MAQattan/My-Graduation-Project/GP_Obsidian/Thesis/4/الفصل الرابع -  الخلايا والألواح الكهروضوئية.md

## [[فكرة الخلية الشمسية (Idea of solar cell)]] 

## [[وصل الخلاية]] 

## [[الدائرة المكافئة للخلية الشمسية]] 

## [[أنواع الألواح الشمسية (Modules)]] 
## [[خصائص الخلية الشمسية]] 

## [[تأثير الإشعاع الشمسي على الطاقة الكهروضوئية الناتجة]] 

## [[تأثير درجة الحرارة على الطاقة الكهروضوئية الناتجة]] 

## [[الفرق بين STC & NOCT]] 

## [[معنى مصطلح كتلة الهواء (Air Mass - AM)]] 

## [[ربط الألواح الشمسية]] 

## [[وصلات MC4]]

## [[دايودات التجاوز (Bypass diode)]] 

## [[دايود الحجب (Blocking Diode)]] 

## [[تنظيف الألواح وأنظمة تثبيتها]] 

## [[ورقة البيانات (Datasheet) للألواح الشمسية]]
