MAQattan/My-Graduation-Project/GP_Obsidian/Thesis/4/خصائص الخلية الشمسية.md

تُعد دراسة خصائص الأداء للألواح الشمسية (Module Characteristics) المدخل الأساسي لفهم كيفية استخلاص أقصى طاقة ممكنة من الضوء الساقط، ويتم ذلك من خلال تحليل العلاقة البيانية بين التيار والجهد فيما يُعرف بمنحنى ($I-V$). يتم رسم هذا المنحنى عبر تعريض اللوح لظروف تشغيلية متغيرة تبدأ من حالة القصر وتصل إلى حالة الدائرة المفتوحة، مما يسمح بتحديد النقاط الحرجة التي تحكم كفاءة المنظومة.

![[PV-04-08.png]]

تبدأ أولى هذه النقاط بما يُعرف بـ **تيار القصر ($I_{sc} - Short\ Circuit\ Current$)**، وهي النقطة التي يمر فيها أقصى تيار ممكن عبر اللوح عندما يكون فرق الجهد بين طرفيه صفراً ($V=0$). ويتم قياس هذه القيمة عملياً بوضع جهاز "أميتر" ذو مقاومة منخفضة جداً بين طرفي اللوح، مما يحاكي حدوث قصر في الدائرة ويسمح بتدفق كامل الإلكترونات المحررة ضوئياً، وتمثل هذه النقطة بداية المنحنى على المحور الرأسي. وفي الطرف المقابل للمنحنى على المحور الأفقي، نجد **جهد الدائرة المفتوحة ($V_{oc} - Open\ Circuit\ Voltage$)**، وهو أقصى جهد يمكن أن يفرضه اللوح عندما تكون الدائرة مفتوحة والتيار المار صفراً ($I=0$). وتُقاس هذه القيمة بواسطة "فولتميتر" عالي المقاومة، حيث يكون الجهد في ذروته لعدم وجود مفقودات ناتجة عن تدفق التيار (Voltage Drop)، وتعد هذه القيمة هي المرجع الأساسي لتحديد سعة الجهد في التصميم.

![[PV-04-09.png]]

أما **منحنى الاستطاعة أو القدرة (Power Curve)**، فهو منحنى اشتقاقي ينتج من حاصل ضرب قيم الجهد والتيار ($P = V \times I$) عند كل لحظة تشغيلية. يتميز هذا المنحنى ببدئه من الصفر (عند نقطة $I_{sc}$ لأن الجهد صفر) وانتهائه بالصفر (عند نقطة $V_{oc}$ لأن التيار صفر)، وما بينهما تبدأ القدرة في التصاعد تدريجياً مع زيادة الجهد وثبات التيار نسبياً في المرحلة الأولى، حتى تصل إلى قمتها عند نقطة فريدة تُسمى **نقطة القدرة القصوى (Maximum Power Point - MPP)**. وبعد تجاوز هذه النقطة، يبدأ التيار في الانهيار بشكل حاد، مما يؤدي إلى انخفاض القدرة الكلية مرة أخرى بالرغم من استمرار زيادة الجهد.

![[PV-04-10.png]]

تُمثل **نقطة القدرة القصوى ($P_{max}$)** الهدف التشغيلي الأسمى للمصمم، حيث يتم استخراج أقصى استطاعة كهربائية من اللوح عند هذه النقطة تحديداً، وترتبط بقيمتين أساسيتين هما: **جهد أقصى قدرة ($V_{mp}$)** و **تيار أقصى قدرة ($I_{mp}$)**. ومن الناحية الرياضية، تُحسب القدرة القصوى للوح وفق العلاقة:

$$
P_{max} = V_{mp} \times I_{mp}
$$

علماً بأن قيمة ($V_{mp}$) تكون دائماً أقل من ($V_{oc}$)، كما أن ($I_{mp}$) أقل من ($I_{sc}$). ولضمان استمرار عمل اللوح عند هذه النقطة المثالية رغم تغير شدة الإضاءة أو درجة الحرارة، تُزود أجهزة التحكم (كالشواحن أو الانفرترات) بخاصية **تتبع نقطة القدرة القصوى (MPPT)**، وهي تقنية إلكترونية تقوم بموازنة الحمل باستمرار لإجبار اللوح على البقاء عند ذروة منحنى القدرة لضمان عدم ضياع الطاقة المتاحة.
