MAQattan/My-Graduation-Project/GP_Obsidian/Thesis/9/9 - 4 الحماية من الجهد الزائد والصواعق (Surge & Overvoltage Protection).md

تُعد الأنظمة الكهروضوئية، بطبيعتها الإنشائية، من أكثر الأنظمة الكهربائية عرضة لمخاطر الجهود الزائدة (Overvoltages) الناتجة عن الصواعق أو عمليات الفصل والوصل في الشبكة العامة (Switching Surges). يعود ذلك إلى تركيب الألواح في أماكن مفتوحة ومرتفعة (فوق أسطح المباني أو في مساحات أرضية واسعة)، مما يجعلها "هوائيات" مثالية لالتقاط الحقول الكهرومغناطيسية العابرة. لحماية الاستثمار المالي للمنظومة ومنع تدمير المكونات الحساسة كالعاكس، يُقسم نظام الحماية إلى شقين متكاملين: **الحماية من الجهد الزائد عبر مانعات الصواعق (SPDs)**، و**تفريغ تيارات الأعطال عبر منظومة التأريض**.

### 9-4-1 مانعات الصواعق (SPD): أنواعها وآلية عملها

تعمل أجهزة الحماية من الجهد الزائد (Surge Protective Devices - SPD) كصمامات أمان كهربائية؛ حيث تكمن وظيفتها الأساسية في حد (Clamping) الجهود العابرة الخطيرة وتوجيه تيار الصاعقة النبضي بأمان نحو الأرض، مانعةً إياه من اختراق الدوائر الداخلية للعاكس أو تدمير عازلية الخلايا الشمسية.

![[PV-09-12.webp]] 

#### أولاً: تصنيف أنواع مانعات الصواعق (Type 1 & Type 2)

يتم التمييز بين نوعين رئيسيين من الـ SPD بناءً على طبيعة الخطر المتوقع ومكان التركيب في المنظومة:

| **وجه المقارنة** | **مانع الصواعق من النوع الأول (Type 1 SPD)** | **مانع الصواعق من النوع الثاني (Type 2 SPD)** |
| --- | --- | --- |
| **طبيعة الحماية** | يحمي من **الضربات المباشرة** للصواعق (Direct Lightning Strikes). | يحمي من **الضربات غير المباشرة** وعمليات الفصل والوصل (Induced Surges). |
| **شكل الموجة الاختبارية** | يُختبر بموجة تيار نبضية قاسية شدتها $10/350\ \mu\text{s}$. | يُختبر بموجة تيار نبضية أسرع وأقل طاقة شدتها $8/20\ \mu\text{s}$. |
| **مكان التركيب الهندسي**  | يُركب عند المدخل الرئيسي للمبنى إذا كان المبنى مزوداً بنظام حماية خارجي (مانعة صواعق شاقولية/قضيب فرامكلين). | يُركب بشكل أساسي في لوحات الـ DC (قبل العاكس) وفي لوحات الـ AC (بعد مخرج العاكس). |
| **القدرة على التحمل** | يتحمل تيارات تفريغ هائلة تصل إلى عشرات الكيلو أمبير دون أن يتلف. | يمتلك زمن استجابة أسرع ولكن لقيم تيارات نبضية أقل مقارنة بالنوع الأول. |

![[PV-09-13.jpg]]

#### ثانياً: آلية العمل الفيزيائية لتفريغ التيارات النبضية

تعتمد هندسة التصميم الداخلي لـ SPD الحديث على مكونات إلكترونية لا خطية، أشهرها **المقاومات المتغيرة بأكسيد المعدن (Metal Oxide Varistors - MOVs)** و**أنابيب التفريغ الغازي (Gas Discharge Tubes - GDTs)**. تتلخص آلية التشغيل في حالتين:

1. **الحالة الطبيعية (تشغيل اعتيادي):** عندما يكون جهد المنظومة ضمن الحدود الطبيعية وأقل من جهد التشغيل المستمر للمانع ($U_c$)، تكون المقاومة الكهربائية للـ MOV عتيقة وجداً وضخمة (تبلغ ميجا أوم)، مما يجعل المانع يسلك سلوك **دارة مفتوحة (Open Circuit)**، فلا يمر عبره أي تيار تسريب يذكر.

![[PV-09-14.png]]
    
2. **الحالة الحرجة (لحظة حدوث الصاعقة):** عند نمو جهد نبضي مفاجئ يتجاوز عتبة المقاومة (أعلى من $U_c$)، تنهار مقاومة الـ MOV داخلياً في غضون نانو ثانية لتتحول إلى ما يشبه **قصر دارة (Short Circuit)** ذي مقاومة قريبة من الصفر. هذا الانهيار اللحظي يفتح مساراً بديلاً فائق السهولة أمام التيار النبضي الهائل ليتدفق مباشرة نحو شبكة التأريض، بدلاً من الدخول إلى المكونات الحساسة للعاكس.

![[PV-09-15.png]]

>[!info] ملاحظة تصميمية
أثناء عملية التفريغ، يضمن المانع ألا يتجاوز الجهد المتبقي بين أقطابه قيمة تُعرف بـ **جهد الحماية ($U_p$)**. ويجب هندسياً أن يكون هذا الجهد ($U_p$) أقل بكثير من جهد تحمل العزل (Impulse Withstand Voltage) للعاكس والألواح لضمان سلامتها المطلقة.

### 9-4-2 منظومة التأريض (Earthing System)

لا قيمة هندسية لأرقى مانعات الصواعق وقواطع الحماية إن لم تكن متصلة بمنظومة تأريض ذات مقاومة منخفضة؛ فالتأريض هو "المصب الفعلي" الذي تؤول إليه كل تيارات الأعطال والتسريب والصواعق. تتجلى الأهمية الأكاديمية والتطبيقية لتأريض المكونات المعدنية في جانبين جوهريين:

#### أولاً: تأريض الهياكل المعدنية للألواح (Structure Grounding)

تُصنع إطارات الألواح الكهروضوئية وهياكل التثبيت (Mounting Racks) من الألومنيوم أو الحديد المغلون. وتأريض هذه الأجزاء إلزامياً للأسباب التالية:

- **تفريغ الشحنات الساكنة (Static Charges):** يؤدي مرور الهواء والرياح المستمر فوق سطح الزجاج والألواح إلى تراكم شحنات كهربائية ساكنة قد تؤدي مع الوقت إلى ظاهرة التحلل المتسارع للعزل الناشئ عن الجهد المستحث (PID - Potential Induced Degradation)، والتأريض يضمن تصريفها أولاً بأول.
    
- **الحماية من مخاطر عيوب العزل:** في حال تضرر غلاف كبل الـ DC واحتكاكه بالهيكل المعدني نتيجة العوامل الجوية، سيتحول الهيكل بالكامل إلى جزء حي صعق مميت لأي فني صيانة. يوفر التأريض مساراً منخفض المقاومة يجبر وسائل الحماية على استشعار العطل وفصل الدائرة فوراً.

#### ثانياً: تأريض جسم العاكس (Inverter Chassis Grounding)

يحتوي العاكس على دوائر تقطيع إلكترونية عالية التردد (High-Frequency Switching - PWM) ومحولات أو فلاتر داخلية. ينتج عن هذه البيئة التشغيلية ما يُعرف بـ **تيارات التسريب السعوية (Capacitive Leakage Currents)** عبر المكثفات الطفيلية بين أشباه الموصلات وجسم العاكس المعدني.

- **وظيفة التأريض هنا:** سحب هذه التيارات المستمرة والمترددة الصغيرة إلى الأرض لمنع ظهور جهود تلامس خطرة على الهيكل الخارجي.
    
- **تفعيل حمايات العاكس:** يعتمد العاكس الذكي على خط التأريض كمرجع تشغيلي أساسي لمراقبة مقاومة العزل للحقل الشمسي (Isolation Resistance Monitoring قبل الإقلاع). فإذا كانت مقاومة الأرض سيئة أو غير متصلة، سيرفض العاكس ربط المنظومة بالشبكة ويطلق إنذار عطل (Ground Fault).

#### ثالثاً: الربط متساوي الكهروجهد (Equipotential Bonding)

لضمان أعلى معايير الأمان، تخضع المنظومة لقاعدة هندسية صارمة: **"يجب ربط كافة الأجزاء المعدنية غير الحاملة للتيار ببعضها البعض بحلقة ربط متكاملة، ثم وصلها بنقطة التأريض الرئيسية (MET)"**.

الهدف من هذا الربط هو إلغاء أي فرق جهد (Potential Difference) قد ينشأ بين نقطتين مختلفتين على السطح أثناء حدوث صاعقة؛ فوجود فرق جهد -ولو لكسر من الثانية- يعني مرور تيار مدمر وقاتل، بينما بقاء المنظومة كاملة عند نفس الجهد (حتى وإن كان مرتفعاً لحظياً) يحمي المعدات والأرواح البشرية تماماً.
