MAQattan/My-Graduation-Project/GP_Obsidian/Thesis/2/أنظمة الربط والتوزيع الكهربائي.md

يمثل فهم طبيعة أنظمة التوزيع الكهربائي منطلقاً أساسياً لتحديد آلية ربط محطات التوليد الكهروضوئية بالشبكات الكهربائية القائمة؛ حيث يتوقف اختيار نظام الربط وهندسته على طبيعة المنشأة، وحجم الأحمال المرتبطة بها، ومتطلبات استقرار الشبكة العامة. وتنقسم شبكات التوزيع منخفض الجهد عموماً إلى أنظمة أحادية الطور (Single-Phase) وأنظمة ثلاثية الأطوار (Three-Phase).

### 2.3.1 أنظمة الطور الواحد (Single-Phase Systems)

يتكون نظام الطور الواحد في بنيته الفيزيائية من ناقلين أساسيين لتشكيل المسار المغلق للتيار:

- **خط الطور أو الحامي (Phase / Line):** وهو الناقل الحي المسؤول عن حمل الجهد المتناوب من المصدر إلى الحمل.
    
- **خط المحايد أو البارد (Neutral):** وهو الخط المرجعي المتمم للدائرة الكهربائية، والذي يُفترض أن يكون جهده مسافراً قريباً من الصفر فولت نتيجة تأريضه عند محولات التوزيع الرئيسية.
    
بناءً على ذلك، يكون فرق الجهد الفعلي المطبق على الأحمال هو الجهد بين الطور والمحايد ($V_{L-N}$)، والذي يبلغ قيمته الاسمية المستقرة في الشبكات التقليدية **220V** أو **230V** تبعاً للكود الكهربائي المحلي.

**محدودية الاستخدام:**

يقتصر تطبيق هذا النظام هندسياً على **الأحمال الصغيرة والمنزلية** نظراً لمحدودية القدرة التي يمكن نقلها عبر طور واحد؛ إذ إن رفع القدرة يتطلب زيادة شدة التيار بشكل طردي، مما يستلزم نواقل ذات مقاطع ضخمة جداً لمواجهة الفقد الحراري وهبوط الجهد، فضلاً عن أن المحركات أحادية الطور تعاني من تموجات في العزم اللحظي وتشكل عبئاً تشغيلياً غير اقتصادي في المنشآت الكبيرة.

### 2.3.2 أنظمة الثلاثة أوجه (Three-Phase Systems)

يُعد نظام التيار المتردد ثلاثي الأطوار النظام القياسي العالمي المعتمد لتوليد، نقل، وتوزيع الطاقة الكهربائية. يتكون هذا النظام في صيغته العامة من ثلاثة خطوط طورية نشطة ($L_1, L_2, L_3$) يفصل بينها خط محايد مشترك ($N$).

**التحليل الطوري المتجهي (Phasor Analysis):**

تتميز الموجات الجيبية الثلاث للأطوار بأنها متساوية تماماً في القيمة العظمى والتردد، ولكنها مشفرة ومزاحة زمنياً بفارق زاوية ثابت يُقدر بـ **120° كهربائية** (أو $\frac{2\pi}{3}$ راديان) بين كل طور والآخر. يضمن هذا التناظر الطوري تدفقاً ثابتاً ومستقراً للقدرة الكلية دون أي نبضات. ورياضياً، يُعبر عن الجهود اللحظية للأطوار الثلاثة كما يلي:

$$v_A(t) = V_m \sin(\omega t)$$

$$v_B(t) = V_m \sin(\omega t - 120^\circ)$$

$$v_C(t) = V_m \sin(\omega t - 240^\circ)$$

**العلاقات الرياضية للجهد:**

في هذا النظام، يتم التمييز هندسياً بين نوعين من الجهد:

1. **جهد الطور (Phase Voltage - $V_{L-N}$):** وهو الجهد المقيس بين أي طور مفرد وخط المحايد، وقيمته الاسمية **220V**.
    
2. **جهد الخط (Line-to-Line Voltage - $V_{L-L}$):** وهو فرق الجهد المقيس بين أي طورين مختلفين (مثل $V_{L1-L2}$).
    
ترتبط قيم الجهدين بعلاقة اتجاهية وثيقة ناتجة عن الطرح المتجهي للموجات المزاحة بـ **120°**، ويُعبر عنها رياضياً بالمعادلة التالية:

$$V_{L-L} = V_{L-N} \times \sqrt{3}$$

وعند التعويض بالقيمة الاسمية لجهد الطور (**220V**)، نجد أن جهد الخط يبلغ:

$$V_{L-L} = 220 \times \sqrt{3} \approx 381.05$$

وهو ما يُعرف اصطلاحاً في التطبيقات العملية بـ **380V** (أو **400V** في الأنظمة التي تعتمد **230V** كجهد طور).

### 2.3.3 اعتبارات الربط مع المنشآت التجارية والشبكة

تعتمد المنشآت التجارية الحيوية (مثل البنوك والمقرات الإدارية) بشكل كلي على نظام التغذية ثلاثي الأطوار؛ ويرجع ذلك لحاجتها التشغيلية المستمرة لأحمال ميكانيكية وضخمة مثل منظومات التكييف المركزي (HVAC)، والمصاعد، ومضخات المياه التي تعتمد على محركات حثية ثلاثية الأطوار تتميز بكفاءة تشغيلية مرتفعة وعزم دوران ثابت ومستقر مقارنة بالمحركات أحادية الطور.

**أهمية الربط المتزن للمنظومة الكهروضوئية:**

عند تصميم محطة طاقة شمسية متصلة بالشبكة لتغذية منشأة تجارية (كبنك تجاري) بقدرة تبلغ **25kW**، يُصبح الاعتماد على **عاكس ثلاثي الأطوار (3-Phase Inverter)** محددًا فنيّاً وإلزامياً بناءً على الاعتبارات الهندسية التالية:

1. **منع عدم الاتزان الفولتية (Phase Unbalance):** إن ضخ قدرة إنتاجية عالية تصل إلى **25kW** على طور واحد مفرد سيؤدي إلى رفع جهد هذا الطور بشكل حاد ومتنافر مقارنة بالأطوار الأخرى، مما يسبب ظاهرة عدم الاتزان الفولتية التي تلحق أضراراً بالغة بالأجهزة والمعدات الحساسة داخل المنشأة.
    
2. **الامتثال لأكواد الشبكة الكهربائية (Grid Codes):** تضع شركات توزيع الكهرباء قيوداً صارمة تمنع حقن قدرات تتجاوز حدوداً معينة (تتراوح غالباً بين 3kW إلى 5kW) على فازة واحدة لتجنب تشويه إشارة الشبكة. لذا، يقوم العاكس الذكي ثلاثي الأطوار بتوزيع استطاعة الألواح المحقونة بالتساوي على الأطوار الثلاثة.
    
3. **اقتصادية النواقل وتقليل الضياعات:** يتيح العمل على جهد الخط المرتفع (**380V/400V**) خفض قيمة التيار المار في الكابلات لنفس القدرة المنقولة. هذا الانخفاض في شدة التيار يسمح للمهندس بتقليص مقاطع كابلات التيار المتردد (AC Cables) بشكل كبير، مما يقلل من التكلفة المادية للمشروع ويحد من ضياعات القدرة الناتجة عن الهبوط الحراري في النواقل.
