MAQattan/My-Graduation-Project/GP_Obsidian/Thesis/7/حل معضلة شكل الموجة (تقنية PWM).md

تُمثل معضلة تشوه شكل الموجة (Waveform) التحدي التقني الأكثر حرجاً في هندسة العواكس؛ حيث تفتقر الموجة المربعة (Square Wave) الناتجة عن عمليات التبديل البسيطة في قنطرة H إلى الخصائص الجيبية الضرورية لتشغيل الأحمال الحثية والإلكترونية الحساسة. ولتجاوز هذا القصور الفيزيائي، يتم اعتماد تقنية **تعديل عرض النبضة (Pulse Width Modulation - PWM)**، وهي المنهجية الهندسية التي تسمح بتحويل الخرج المربع الثابت إلى موجة جيبية نقية (Pure Sine Wave) تماثل تماماً جودة الطاقة المتوفرة في الشبكات الكهربائية العامة.

تستند الفلسفة التشغيلية لتقنية **PWM** إلى مبدأ تجزئة فترة التوصيل الكهربائي إلى سلسلة من النبضات السريعة جداً بدلاً من إبقاء المفاتيح الإلكترونية (IGBT) في حالة إغلاق مستمر طوال نصف الدورة. ففي حين أن العاكس البسيط يُبقي المفتاح مغلقاً لمدة 10 ميلي ثانية كاملة (في نظام 50 هيرتز)، يقوم نظام التحكم في تقنية **PWM** بفتح وإغلاق المفتاح لعدد هائل من المرات خلال نفس الفترة الزمنية وبأزمنة متغيرة. وتكمن الأهمية الفيزيائية لهذا الإجراء في أن الأحمال الكهربائية لا تستجيب لشكل النبضات اللحظية، بل تتأثر بـ **"متوسط الجهد" (Average Voltage)** الناتج عنها.

![[PV-07-06.jpg]]

ومن الناحية الرياضية، تخضع هذه العملية لمعادلة تكامل الجهد اللحظي عبر الزمن الدوري، حيث يتم حساب متوسط الجهد ($V_{avg}$) وفق العلاقة التالية:

$$
V_{avg} = \frac{1}{T} \int V(t) , dt
$$

وبما أن التردد ($1/T$) ثابت لضمان استقرار المنظومة عند 50 هيرتز، فإن التحكم في قيمة الجهد الخارج يعتمد كلياً على تغيير "حدود التكامل" التي تُمثلها أزمنة عرض النبضة (On-time). فعندما تكون النبضة ذات عرض ضيق جداً في بداية نصف الدورة، يكون متوسط الجهد قريباً من الصفر، ومع زيادة عرض النبضة تدريجياً، يرتفع المتوسط ليصل إلى ذروته (Peak) عند منتصف الفترة، ثم يبدأ في التناقص مع تضاؤل عرض النبضات مجدداً.

![[PV-07-07.png]]

يؤدي هذا النمط المتغير في عرض النبضات إلى تشكيل موجة تظهر في التحليل الهيكلي على هيئة "درجات سلم" (Stepped Wave)، وكلما زاد عدد النبضات (Switching Frequency) التي يوفرها ترانزستور الـ **IGBT**، أصبحت هذه الدرجات أصغر وأكثر انسيابية، مما يجعل الموجة النهائية مطابقة كلياً للموجة الجيبية النقية. وبذلك، تضمن تقنية **PWM** تقليل التوافقيات (Harmonics) إلى أدنى مستوياتها، مما يحمي المحركات من الحرارة الزائدة ويمنع تلف الأجهزة الإلكترونية الحساسة، محققةً بذلك التوافق التام بين مصادر الطاقة الشمسية ومتطلبات الأحمال الحديثة.
