MAQattan/My-Graduation-Project/GP_Obsidian/Thesis/Appendices/الملحق ت.md

![[Screenshot 2026-05-26 162740.png]]

![[0.6-1 (1.2) KV Single Core Unarmoured Cables.png]]

![[Screenshot 2026-05-27 171126.png]]

![[Screenshot 2026-05-26 153328.png]]
