MAQattan/My-Graduation-Project/GP_Obsidian/Thesis/10/10 - 13 اختيار العاكس.md

يُمثل اختيار العاكس الكهروضوئي (Inverter) ومواءمته الهندسية مع مصفوفة الألواح الخطوة الأكثر حرجاً في تصميم المنظومات المرتبطة بالشبكة (On-Grid)؛ حيث يُعد العاكس المكون الذكي المسؤول عن تحويل التيار المستمر ($DC$) المتغير الناتج عن الألواح إلى تيار متردد ($AC$) مستقر ومتوافق تماماً مع معايير الجودة والتردد للشبكة الكهربائية العامة. وتستند الممارسة الهندسية الأكاديمية الصارمة في هذا الصدد إلى تحقيق توازن دقيق بين **مواءمة القدرة (Power Matching)** و**تحليل الكفاءة التشغيلية والاقتصادية** لضمان أعلى عائد طاقة ممكن بأقل تكلفة تأسيسية.

### أولاً: مواصفات العاكس المعتمد ونسبة التحميل (DC/AC Ratio)

بناءً على الحسابات الدقيقة المنجزة في الفقرة السابقة، والتي حددت الاستطاعة الإجمالية للمصفوفة الكهروضوئية بقيمة **$23.4 \text{ kWp}$**، %%تم استبعاد الخيار السابق (عاكس بقدرة $50 \text{ kW}$) نظراً للانخفاض الحاد في نسبة تحميله وما يترتب عليه من هدر مالي وتشغيلي. وبدلاً من ذلك، %% تم اعتماد العاكس الذكي ثلاثي الطور من طراز **Huawei SUN2000-25KTL-M5** بقدرة اسمية تبلغ **$25 \text{ kW}$**.

لتأكيد المواءمة الفنية، يتم حساب نسبة التحميل (DC/AC Loading Ratio) والمعروفة هندسياً بمعامل التصميم ($R$) وفق العلاقة التالية:

$$R = \frac{P_{DC \text{ (Nominal)}}}{P_{AC \text{ (Nominal)}}}$$
$$R = \frac{23.4 \text{ kW}}{25 \text{ kW}} = 0.936$$
#### التبرير التشغيلي للنسبة المعتمدة:

تشير الممارسات الهندسية القياسية إلى أن تصميم نسبة التحميل حول القيمة ($0.90$ - $1.15$) في المناطق ذات الإشعاع الشمسي المرتفع يُعد تصميماً مثالياً؛ حيث تضمن النسبة المحسوبة ($0.936$) تشغيل العاكس في النطاق المحصور بين **$40\%$ إلى $80\%$** من حمل التشغيل الاسمي (Load %) لأطول فترة زمنية ممكنة خلال ساعات النهار.

وفقاً لمنحنيات الكفاءة الخاصة بهذا الطراز، فإن هذه المنطقة تمثل ذروة الأداء التشغيلي؛ حيث يبلغ العاكس كفاءته الأوروبية الموزونة (European Weighted Efficiency) البالغة **$98.2\%$** وكفاءته القصوى البالغة **$98.4\%$**، مما يقلل من الضياعات الحرارية الذاتية داخل دوائر العاكس الإلكترونية ويرفع من إنتاجية الطاقة السنوية النوعية (Energy Yield) للمحطة.

### ثانياً: التبرير التكنولوجي وحماية المنظومة (Technical & Safety Justification)

تم اختيار هذا الطراز تحديداً تلبيةً للمحددات الجغرافية والكهربائية الخاصة بموقع المشروع، وذلك بناءً على الميزات التكنولوجية التالية:

- **مرونة تتبع النقطة الأعظمية (Multi-MPPT):** يحتوي العاكس على **متعقِبين مستقلين للاستطاعة العظمى (2 MPP Trackers)** مع إجمالي 4 مداخل تيار مستمر (مدخلان لكل متعقب). تمنح هذه البنية القدرة على فصل المصفوفات كهربائياً؛ مما يتيح معالجة مشكلة الظلال الجانبية الناتجة عن العوائق الإنشائية (مثل غرفة الدرج ووحدات التكييف) عبر حصر الألواح المتأثرة في متعقب مستقل، لحماية كفاءة باقي الألواح المستقرة من مفاقيد عدم التطابق (Mismatch Losses).
    
- **التوافق مع التيارات العالية:** يدعم العاكس تيار دخل أقصى يصل إلى **$30 \text{ A}$** عند ربط سلسلتين على متعقب واحد، و$20 \text{ A}$ للسلسلة المنفردة، وهو ما يتوافق تماماً مع التيارات المرتفعة الناتجة عن ألواح الـ $600 \text{ W}$ الحديثة، مما يضمن تلافي ظاهرة "قص التيار" (Current Clipping) وضمان امتصاص كامل القدرة المولّدة.
    
- **معايير الأمان والسلامة النشطة:** بما أن المنظومة مُثبتة على سطح منشأة مصرفية حيوية، فإن العاكس يوفر حماية متقدمة جداً قائمة على الذكاء الاصطناعي ضد حدوث القوس الكهربائي المستمر (AI-Powered Arc Fault Circuit Interrupter - AFCI)، حيث يقوم بفصل النظام تلقائياً في زمن قياسي عند استشعار أي شرارة كهربائية لمنع نشوب الحرائق، بالإضافة إلى احتوائه على حمايات مدمجة من الصواعق وارتفاع الجهد من النوع الثاني (Type II SPD) لجهتي التيار المستمر والمتردد.

### **ملخص المواصفات الفنية للعاكس المعتمد**

يوضح الجدول التالي أبرز الخصائص الكهربائية والفنية للعاكس المستخلص من وثيقة البيانات (Datasheet) الخاصة بشركة Huawei لتوثيق مطابقتها للتصميم:

|**الميزة الفنية (Technical Feature)**|**التوصيف والقيمة (Value & Description)**|
|---|---|
|**الطراز القياسي (Model)**|Huawei SUN2000-25KTL-M5|
|**الاستطاعة الاسمية المترددة (Rated AC Power)**|25,000 W|
|**أقصى كفاءة تحويل (Max. Efficiency)**|98.4%|
|**الكفاءة الأوروبية الموزونة (Euro. Efficiency)**|98.2%|
|**أقصى جهد دخل مستمر (Max. Input Voltage)**|1,100 V|
|**الجهد الاسمي لدخل التيار المستمر (Rated Input Voltage)**|600 V|
|**نطاق جهد تشغيل الـ MPPT**|200 V - 1000 V|
|**عدد متتبعات الاستطاعة العظمى (No. of MPPTs)**|2|
|**أقصى عدد لمداخل التيار المستمر (Max. Inputs)**|4 (مدخلان لكل MPPT)|
|**أقصى تيار دخل لكل MPPT**|30 A (لمدخلين متوازيين) / 20 A (لمدخل منفرد)|
|**أقصى تيار قصر للمتتبع (Max. Short-Circuit Current)**|40 A|
|**حماية القوس الكهربائي (Arc Fault Protection)**|متوفرة ومدمجة (Yes / AI-Powered)|
|**حماية الارتفاع المفاجئ للجهد (Surge Arrester)**|Type II لجهتي AC و DC|
|**نوع التبريد ودرجة الحماية البيئية**|تبريد هوائي ذكي (Smart Air Cooling) / IP66|
