MAQattan/My-Graduation-Project/GP_Obsidian/Thesis/2/أنواع القدرة وحساباتها في أنظمة التيار المتردد.md

في التيار المتردد، لا تستهلك الأحمال القدرة بشكل بسيط كما في التيار المستمر ($P = V \times I$)، بل تنقسم القدرة إلى ثلاثة أنواع مرتبطة بما يسمى "مثلث القدرة":

1. **القدرة الفعالة (Active Power - P):** هي القدرة الحقيقية التي تنجز شغلاً فعلياً (مثل تدوير المحرك أو الإضاءة). تُقاس بالوات (W) أو الكيلوات (kW).
2. **القدرة غير الفعالة (Reactive Power - Q):** هي قدرة لا تنجز شغلاً مباشراً ولكنها ضرورية لخلق المجالات المغناطيسية اللازمة لعمل المحركات. تُقاس بالفار (VAR) أو الكيلوفار (kVAR).
3. **القدرة الكلية أو الظاهرية (Apparent Power - S):** هي المجموع الاتجاهي للقدرتين السابقتين، وتمثل إجمالي القدرة المسحوبة من المصدر. تُقاس بالفولت أمبير (VA) أو (kVA).
4. **معامل القدرة (Power Factor):** هو النسبة بين القدرة الفعالة والقدرة الكلية ($P/S$)، ويُعبر عنه بـ $\cos(\phi)$.

**العلاقات الرياضية لحساب القدرة الفعالة (P):**

- في نظام **الوجه الواحد**: $P = V \times I \times \cos(\phi)$.
- في نظام **الثلاثة أوجه**: $P = 3 \times V_{ph} \times I_{ph} \times \cos(\phi)$.
- العلاقة بين أنواع القدرة: $S = \sqrt{P^2 + Q^2}$.
