MAQattan/My-Graduation-Project/GP_Obsidian/Thesis/2/العلاقات الرياضية والقيم العملية.md

في التطبيقات العملية، وخاصة في الموجات الجيبية (Sinusoidal Waves)، توجد علاقات ثابتة بين أنواع القيم المختلفة للجهد:

1. **العلاقة بين القيمة العظمى والفعالة:** القيمة التي نقيسها في المقابس المنزلية (مثل 220 فولت) هي قيمة **RMS**، بينما تكون القيمة العظمى (Peak) أعلى من ذلك.

$$
V_{max} = V_{rms} \times \sqrt{2}
$$

*مثال:* عند جهد $V_{rms} = 220V$، تكون $V_{max} \approx 318V$.

2. **جهد القمة للقمة (Peak-to-Peak Voltage):** وهي المسافة من أقصى قمة موجبة إلى أقصى قاع سالب.

$$
V_{p-p} = 2 \times V_{max}
$$

**خلاصة:** الفرق الجوهري يكمن في أن أجهزة قياس التيار المستمر مصممة لقراءة **القيمة المتوسطة**، بينما صُممت أجهزة قياس التيار المتردد لتقرأ **القيمة الفعالة (RMS)**، مما يجعل لكل نظام أدوات قياس وتطبيقات خاصة به.
