MAQattan/My-Graduation-Project/GP_Obsidian/Thesis/2/الفرق بين القدرة (Power) والطاقة (Energy).md

يتم الخلط غالباً بين هذين المصطلحين، والفرق الجوهري بينهما هو **عامل الزمن**:

- **القدرة (Power):** هي سعة أو إمكانية المعدة على بذل شغل، وهي قيمة ثابتة للمعدة سواء تم تشغيلها أم لا. مثال: لمبة قدرتها 100 وات، تظل قدرتها 100 وات حتى وهي مطفأة.
- **الطاقة (Energy):** هي الاستهلاك الفعلي المرتبط بالزمن؛ أي حاصل ضرب القدرة في مدة التشغيل. هي ما يتم محاسبتك عليه في فاتورة الكهرباء.
- **العلاقة الرياضية:**

$$
\text{Energy (E)} = \text{Power (P)} \times \text{Time (t)}
$$

تُقاس الطاقة بوحدة **وات-ساعة (Wh)** أو **كيلوات-ساعة (kWh)**.

**مثال توضيحي:** لمبة قدرتها 100 وات تعمل لمدة 3 ساعات تستهلك طاقة مقدارها 300 وات-ساعة ($100 \times 3 = 300Wh$). بينما لمبة أخرى بقدرة 25 وات تعمل لنفس المدة تستهلك طاقة أقل (75 وات-ساعة) بسبب اختلاف "قدرتها" أو سعتها الأصلية.
