MAQattan/My-Graduation-Project/GP_Obsidian/Thesis/4/الدائرة المكافئة للخلية الشمسية.md

تُعد الدائرة المكافئة للخلية الشمسية (Equivalent Circuit) الأداة الهندسية الأساسية لتوصيف السلوك الكهربائي للخلية وتحليل أدائها تحت مختلف الظروف التشغيلية؛ حيث يتم تمثيل الخلية كمجموعة من العناصر الكهربائية القياسية التي تحاكي الظواهر الفيزيائية المعقدة التي تحدث داخل بنية أشباه الموصلات.

![[PV-04-03.png]]

وتبدأ هذه الدائرة بتمثيل مصدر التيار (Current Source) الذي يعبر عن تيار الفوتونات الناتج عن سقوط الإشعاع الشمسي على وصلة الـ (P-N Junction)، حيث يتناسب هذا التيار طردياً مع شدة الإشعاع الساقط.

ويتم توصيل دايود (Diode) على التوازي مع مصدر التيار ليمثل الخصائص الفيزيائية للوصلة الثنائية نفسها؛ حيث يمتلك هذا الدايود جهداً حاجزاً يُقدر بـ **0.7 فولت** في حالة خلايا السيليكون، وهو الجهد الذي يحدد شكل منحنى الخواص للخلية. ولتضمين المفقودات غير المثالية في النموذج الرياضي، تُضاف مقاومتان أساسيتان للدوائر العملية: الأولى هي **مقاومة التوازي ($R_{sh} - Shunt Resistance$)**، والتي تُستخدم للتعبير عن الفقد في التيار الناتج عن مسارات التسريب الداخلي؛ والثانية هي **مقاومة التوالي ($R_s - Series Resistance$)**، والتي تمثل المفقودات في الجهد (Voltage Drop) الناتجة عن المقاومة الداخلية للمادة ومقاييس التوصيل المعدنية.

وتتمثل العلاقة الرياضية التي تحكم مخرجات الخلية النهائية في حساب التيار المار عبر الحمل الخارجي، حيث يكون التيار الصافي ($I$) مساوياً للتيار الكلي الناتج من المصدر مطروحاً منه التيارات المفقودة عبر الدايود ومقاومة التوازي، وهو ما يمكن صياغته في أبسط صوره كالتالي:

$$
I = I_{G} - I_{d} - I_{sh}
$$

حيث أن ($I_{G}$) هو تيار الضوء، و ($I_{d}$) هو تيار الدايود، و ($I_{sh}$) هو التيار المار عبر مقاومة التوازي. وتعكس هذه الدائرة التكامل بين المكونات المثالية والمفقودات الواقعية، مما يسمح للمصممين بتوقع استجابة الخلية عند ربطها بمختلف أنواع الأحمال (Loads) في المنظومات الكهروضوئية.
