MAQattan/My-Graduation-Project/GP_Obsidian/Thesis/5/الفصل الخامس - المنهجية المتقدمة لتعزيز كفاءة الألواح.md

>[!warning]
>تسمي الفصل : صناعة وتقنية الخلايا الكهروضوئية | المنهجية المتقدمة لتعزيز كفاءة الألواح

## [[الاستراتيجيات الهندسية الحديثة لرفع كفاءة الألواح الكهروضوئية]] 

## [[البنية الكهربائية للألواح المصنعة بتقنية أنصاف الخلايا (Half-Cut Cell)]] 
## [[تصنيفات ألواح أنصاف الخلايا (Half-Cut Cells)]] 

## [[الميزات التنافسية في (Datasheet) مقارنة بالألواح التقليدية]]
