MAQattan/My-Graduation-Project/GP_Obsidian/Thesis/5/الميزات التنافسية في (Datasheet) مقارنة بالألواح التقليدية.md

تبرز ورقة البيانات الخاصة بتقنية الـ Half-cut عدة مؤشرات تقنية تجعلها الخيار الأفضل للمهندسين عند المقارنة مع الألواح الكاملة (Full Cells):

1. **قفزة الكفاءة التشغيلية ($\eta$):** تظهر "الداتا شيت" ارتفاعاً ملحوظاً في الكفاءة؛ فبينما تسجل الألواح التقليدية حوالي 18%، تصل ألواح أنصاف الخلايا (خاصة من النوع N-type) إلى قيم تتراوح بين **21% و22.5%**. ويعود ذلك لتقليل المفاقيد الداخلية ودمج تقنيات الـ Multi-busbar التي قد تصل لـ 12 باسبار في اللوح الواحد.
2. **تحسن المعاملات الحرارية (Temperature Coefficients):** عند مقارنة النسب المئوية لانخفاض القدرة والجهد في "الداتا شيت"، نجد أن ألواح الـ Half-cut تمتلك معاملات حرارية **أفضل (أقل سالباً)**؛ مما يعني أن فقدانها للطاقة عند ارتفاع درجات الحرارة يكون أقل حدة مقارنة بالألواح التقليدية، مما يجعلها أكثر استقراراً في المناخات الحارة.
3. **زيادة الاستطاعة الاسمية ($P_{max}$):** توفر هذه التقنية قدرات عالية جداً بنفس المساحة الفيزيائية تقريباً؛ حيث سجلت العينات في المصادر قدرات تصل إلى **470 - 490 واط** لألواح الـ 60 خلية المطورة، وهي قيم يصعب الوصول إليها في تقنيات الخلايا الكاملة القديمة.
4. **التكوين الداخلي للسلاسل (6 Strings):** تتميز هذه الألواح بوجود **6 سلاسل داخلية** (3 فوق و3 تحت) مرتبطة بـ 3 دايودات تجاوز (Bypass Diodes) مشتركة، مما يمنحها مرونة عالية في التعامل مع الظل الجزئي دون فقدان كامل إنتاجية اللوح.
5. **نوع الويفر (N-type vs. P-type):** تذكر المواصفات الحديثة اعتماد تقنية **N-type**، وهي تقنية فيزيائية تتعلق بترتيب طبقات السليكون تجعل اللوح أكثر كفاءة وأطول عمراً مقارنة بتقنيات الـ P-type التقليدية.
