MAQattan/My-Graduation-Project/GP_Obsidian/Thesis/10/Deleted/اختيار العاكس (Inverter Selection).md

يُمثل اختيار العاكس ومواءمته مع المصفوفة الشمسية الخطوة الأكثر حرجاً في التصميم الهندسي للمنظومات المرتبطة بالشبكة (On-Grid)؛ حيث يُعد العاكس العقل المدبر الذي يحول التيار المستمر ($DC$) الناتج عن الألواح إلى تيار متردد ($AC$) متوافق مع الشبكة العامة. وتستند الممارسة الهندسية الصحيحة في هذا الصدد إلى قاعدتين ذهبيتين: **مواءمة القدرة (Power Matching)** و**تحليل نطاقات الجهد (Voltage Range Analysis)** لضمان التشغيل الآمن والأداء الأعلى للمنظومة.

### **المواءمة الفنية وتحليل نطاقات التشغيل**

بناءً على الحسابات الدقيقة لاستطاعة المنظومة الإجمالية البالغة 23.4 kWp (المكونة من 39 لوحاً باستطاعة 600 W لللوح الواحد)، تم اختيار العاكس الذكي ثلاثي الطور من طراز **Huawei SUN2000-25KTL-M5** لإدارة وتحويل الطاقة في هذا المشروع.

تمت مواءمة العاكس ليعمل بنسبة تحميل (DC/AC Ratio) تبلغ **0.936**، ويتم حساب هذه النسبة وفق العلاقة التالية:

$$R = \frac{P_{DC \text{ (Nominal)}}}{P_{AC \text{ (Nominal)}}} = \frac{23.4 \text{ kW}}{25 \text{ kW}} = 0.936$$

حيث تبلغ الاستطاعة الاسمية للخرج المتردد للعاكس 25,000 W. تُعد هذه النسبة مثالية جداً لتشغيل العاكس في نطاق حمل يتراوح بين 40% و80% لمعظم ساعات النهار، وهي المنطقة الممتدة التي يحقق فيها العاكس أعلى كفاءة أوروبية موزونة تصل إلى 98.2% وكفاءة قصوى تبلغ 98.4%، مما يضمن تقليل المفاقيد الحرارية الذاتية للعاكس ورفع إنتاجية الطاقة السنوية الإجمالية (Energy Yield).

### **التصميم الكهربائي وتوزيع السلاسل (String Configuration)**

يمتلك هذا الطراز **متعقِبين للاستطاعة العظمى (2 MPP Trackers)** مع إمكانية ربط **4 مداخل كحد أقصى (2 Inputs per MPPT)**. تم استغلال هذه البنية المرنة لتوزيع الألواح الـ 39 كهربائياً بطريقة ذكية تضمن معالجة تأثير الظلال الجانبية المرصودة في القسم الشرقي من السطح:

1. **تقسيم المصفوفة:** يتم تقسيم الألواح إلى 3 سلاسل (Strings) متساوية تماماً، بحيث تحتوي كل سلسلة على 13 لوحاً موصولاً على التوالي.
    
2. **توزيع المتتبعات (MPPT Allocation):**
    
    - **المتعقب الأول (MPPT 1):** يتم توصيل سلسلتين على التوازي (بإجمالي 26 لوحاً)، ويُخصص هذا المتعقب للألواح الواقعة في المناطق الآمنة والمشمسة تماماً طوال اليوم (القسمين الغربي والأوسط من السطح).
        
    - **المتعقب الثاني (MPPT 2):** يتم توصيل السلسلة الثالثة المتبقية (13 لوحاً) بشكل مستقل، ويُخصص هذا المتعقب حصرياً للألواح الواقعة في الجهة الشرقية القريبة من العوائق الإنشائية (غرفة الدرج ووحدة التكييف).

#### **التحقق من القيود الحالية والجهدية:**

- **التيار المستمر (DC Current):** يسمح العاكس بمرور تيار دخل أقصى يصل إلى 30 A عند ربط مدخلين على نفس الـ MPPT، و20 A عند ربط مدخل واحد. هذا يتوافق تماماً مع تيار الألواح المستخدمة (600 W)، مما يمنع حدوث ظاهرة قص التيار (Current Clipping).
    
- **نطاق الجهد (Voltage Window):** يمتلك العاكس نطاق جهد تشغيلي واسع جداً لمتتبعات الـ MPPT يمتد من 200 V إلى 1000 V، بجهد اسمي يبلغ 600 V. عند ربط 13 لوحاً على التوالي، فإن جهد التشغيل الاسمي للسلسلة يقع في مركز النطاق الفعال للعاكس، مما يضمن استقرار عمل المنظومة حتى في ظروف درجات الحرارة المرتفعة صيفاً، مع بقائه بعيداً عن الجهد الأقصى المطلق للعاكس والبالغ 1100 V.

ويتميز هذا الطراز بدمج تقنيات الأمان النشط القائمة على الذكاء الاصطناعي لحماية المنشأة المصرفية من مخاطر القوس الكهربائي (AFCI)، بالإضافة إلى احتوائه على حمايات مدمجة من النوع الثاني (Type II) لجهتي التيار المستمر والمتردد ضد الصواعق وارتفاع الجهد المفاجئ.

### **ملخص المواصفات الفنية للعاكس المعتمد**

يوضح الجدول التالي أبرز الخصائص الكهربائية والفنية للعاكس المستخلص من وثيقة البيانات (Datasheet) الخاصة بشركة Huawei لتوثيق مطابقتها للتصميم:

|**الميزة الفنية (Technical Feature)**|**التوصيف والقيمة (Value & Description)**|
|---|---|
|**الطراز القياسي (Model)**|Huawei SUN2000-25KTL-M5|
|**الاستطاعة الاسمية المترددة (Rated AC Power)**|25,000 W|
|**أقصى كفاءة تحويل (Max. Efficiency)**|98.4%|
|**الكفاءة الأوروبية الموزونة (Euro. Efficiency)**|98.2%|
|**أقصى جهد دخل مستمر (Max. Input Voltage)**|1,100 V|
|**الجهد الاسمي لدخل التيار المستمر (Rated Input Voltage)**|600 V|
|**نطاق جهد تشغيل الـ MPPT**|200 V - 1000 V|
|**عدد متتبعات الاستطاعة العظمى (No. of MPPTs)**|2|
|**أقصى عدد لمداخل التيار المستمر (Max. Inputs)**|4 (مدخلان لكل MPPT)|
|**أقصى تيار دخل لكل MPPT**|30 A (لمدخلين متوازيين) / 20 A (لمدخل منفرد)|
|**أقصى تيار قصر للمتتبع (Max. Short-Circuit Current)**|40 A|
|**حماية القوس الكهربائي (Arc Fault Protection)**|متوفرة ومدمجة (Yes / AI-Powered)|
|**حماية الارتفاع المفاجئ للجهد (Surge Arrester)**|Type II لجهتي AC و DC|
|**نوع التبريد ودرجة الحماية البيئية**|تبريد هوائي ذكي (Smart Air Cooling) / IP66|
