MAQattan/My-Graduation-Project/GP_Obsidian/Thesis/10/Deleted/حساب الحالات الحرجة للجهد.md

تكمن الخطورة التقنية في أن الجهد والقدرة يتأثران بـ **علاقة عكسية مع درجة الحرارة**؛ فعند ارتفاع الحرارة ينخفض الجهد والقدرة، وعند انخفاض الحرارة يرتفع الجهد بشكل حاد. ويُعبر عن ذلك بـ **المعامل الحراري للجهد ( $\text{Temperature Coefficient of }V_{oc}$)**، والذي يكون سالباً، ومن ورقة بيانات اللوح الذي أخترناه نجده $-0.29\%$. ولضمان استقرار النظام في ظل تقلبات الطقس، يجب إجراء "حسابات الحالات الحرجة" للجهد باستخدام المعادلة الرياضية التالية:

$$
V_{new} = V_{STC} + [V_{STC} \times \text{Temp Coeff} \times (T_{actual} - 25)] 
$$

1. **حالة الصيف (أقصى درجة حرارة 60°م):** يتم حساب **أقل جهد متوقع للوح ($V_{oc-min}$)** لضمان بقاء جهد السلسلة الإجمالي فوق حد التشغيل الأدنى للعاكس (Start-up Voltage)، لمنع توقف النظام عن العمل في الأيام الحارة.
    
    $$
    V_{oc-min} = 52.81 + [52.81 \times \frac{-0.29}{100} \times (60 - 25)]= 47.45V
    $$
    
1. **حالة الشتاء (أقل درجة حرارة 0°م):** يتم حساب **أعلى جهد متوقع للوح ($V_{oc-max}$)** لضمان عدم تجاوز جهد السلسلة للحد الأقصى الذي يحتمله العاكس (Max DC Input)، حيث إن زيادة الجهد في الشتاء بسبب البرودة قد تؤدي إلى **تدمير الدوائر الإلكترونية للعاكس** فوراً.
    
    $$
    V_{oc-max} = 52.81 + [52.81 \times \frac{-0.29}{100} \times (0 - 25)] = 56.64V
    $$

إن الاهتمام بتفاصيل ورقة البيانات، خاصة معاملات الجهد الحرارية، هو ما يفرق بين التصميم الهندسي الآمن وبين التركيبات العشوائية التي قد تتعرض للفشل الميكانيكي أو الكهربائي في الفصول المتطرفة.

---
###  حساب القيم الحرارية المصححة للوح ($V_{mp}$)

لضمان بقاء المنظومة ضمن **مجال تتبع نقطة القدرة القصوى (MPPT Range)** الخاص بالعاكس طوال العام، يجب موازنة عدد الألواح بحيث لا يخرج جهد السلسلة التشغيلي ($V_{mp}$) عن الحدود الدنيا والقصوى للعاكس تحت أقصى الظروف الحرارية المتوقعة.

يتم حساب أقل جهد تتبع متوقع للوح ($V_{mpp-min}$) لضمان بقاء جهد السلسلة الاجمالي فوق الحد الأدنى للتشغيل ضمن مجال نقطة القدرة القصوى للعاكس (Minimum MPPT Range) في ذروة الحرارة (عند $60^{\circ}$م):
$$V_{mpp-min}=44.66 + [44.66 \times \frac{-0.29}{100} \times (60 - 25)]= 40.127 V$$
يتم حساب أقصى جهد تتبع متوقع للوح ($V_{mpp-max}$) لضمان عدم تجاوز جهد السلسلة الاجمالي للحد الأقصى لمجال التشغيل عند نقطة التتبع القصوى (Maximum MPPT Range) في شدة البرودة (عند $0^{\circ}$م):
$$V_{mpp-max}=44.66 + [44.66 \times \frac{-0.29}{100} \times (0 - 25)]= 47.897 V$$

#ToRefactor
