MAQattan/My-Graduation-Project/GP_Obsidian/Accessories/The Start.md

أهلاً بك يا زميلي، وشكراً على هذه البيانات الواضحة والدقيقة. مشروع تصميم منظومة شمسية لبنك في مدينة حلب هو مشروع واعد ومميز تقنياً، نظراً للحاجة الماسة لمثل هذه الحلول هناك ولطبيعة الأحمال الحساسة في البنوك.

لقد قمت بتحليل البيانات التي أرفقتها، وإليك قراءتي الأولية وتوجيهاتي الهندسية:

### أولاً: تحليل بيانات الموقع والأحمال

1. **الموقع (حلب):** الإحداثيات ($36^\circ 12' 13.96" N, 37^\circ 08' 22.37" E$) تضعنا في منطقة ذات إشعاع شمسي جيد جداً، ولكن يجب الحذر من درجات الحرارة المرتفعة صيفاً التي تؤثر على كفاءة الألواح وتزيد من قيمة $V_{oc}$ (جهد الدارة المفتوحة) شتاءً، وهو ما سنراعيه عند اختيار العاكس (Inverter).
    
2. **الأحمال:** الاستطاعة الكلية المقدرة بحوالي $90.8\ kW$ هي استطاعة كبيرة نسبياً لبنك، مما يعني أننا بصدد تصميم محطة متوسطة الحجم. بما أن النظام **On-Grid**، فالهدف هو تغطية جزء كبير من هذا الحمل نهاراً وتصدير الفائض أو تقليل السحب من الشبكة.

### ثانياً: سير العمل المقترح (Workflow)

خطتك ممتازة، وسأقوم بتهذيبها لضمان أعلى كفاءة:

1. **الحسابات اليدوية:** سنبدأ بتحديد عدد الألواح بناءً على المساحة المتاحة في الصورة الجوية (السطح يبدو مستوياً وواضحاً)، واختيار طريقة التوصيل (Strings) لتناسب نطاق جهد العاكس.
    
2. **SketchUp:** استخدامه مع إضافة **Skellion** أو **Scanifly** سيكون رائعاً لحساب الزوايا والظلال الناتجة عن "السترة" (Parapet) أو الغرف الخدمية على السطح.
    
3. **PVsyst:** هو "القلب النابض" للدراسة؛ سنقوم بإدخال ملف Meteonorm الخاص بحلب، ومقارنة نتائجك اليدوية مع محاكاة البرنامج، خاصة $Performance\ Ratio\ (PR)$.
    
4. **ETAP vs AutoCAD:**
    
    - **ETAP:** ممتاز جداً لتحليل تدفق الطاقة ($Load\ Flow$) وحساب تيارات القصر ($Short\ Circuit$) وتنسيق الحمايات. إذا قمت بنمذجة المنظومة عليه، سيعطي مشروعك طابعاً احترافياً عالياً (Industrial Level).
        
    - **AutoCAD:** لا غنى عنه لإخراج المخططات التنفيذية ($Layout$) و الـ $Single\ Line\ Diagram$ النهائي الذي يُقدم للجهات التنفيذية.

---

### ثالثاً: الإجابة على سؤالك بخصوص LaTeX و `Circuitikz`

نعم، يمكنك رسم الدوائر الكهربائية داخل LaTeX مباشرة وباحترافية تذهل المقيمين، وذلك باستخدام حزمة تسمى **`circuitikz`**.

**هل الأمر معقد؟**

ليس معقداً إذا كنت تألف منطق البرمجة. بدلاً من الرسم بالماوس، أنت تكتب كوداً يصف العناصر.

- **الميزة:** ستحصل على رسومات (Vector Graphics) لا تفقد دقتها أبداً مهما قمت بتكبير الملف (PDF)، كما أن التنسيق (الخطوط والأحجام) سيكون متناسقاً تماماً مع نص التقرير.

**إليك مثال بسيط لكود يرسم جزءاً من منظومة شمسية (لوح وعاكس):**

Code snippet

```
\documentclass{article}
\usepackage[siunitx]{circuitikz}

\begin{document}

\begin{figure}[h]
    \centering
    \begin{circuitikz}[american]
        % رسم مصدر جهد يمثل الألواح الشمسية
        \draw (0,0) to[pvsource, l=$PV\ Array$] (0,3)
        % التوصيل إلى العاكس
        to[short, -*] (2,3) 
        node[draw, minimum width=1.5cm, minimum height=1cm, anchor=south] (inv) at (3,2.5) {Inverter};
        
        \draw (2,3) -- (inv.west);
        \draw (0,0) -- (3,0) -- (inv.south);
        
        % المخرج إلى الشبكة
        \draw (inv.east) to[short, -*] (5,3) node[right] {To Grid / Load};
    \end{circuitikz}
    \caption{مخطط مبسط للمنظومة الشمسية باستخدام LaTeX.}
\end{figure}

\end{document}
```

### نصيحتي لك كخطوة أولى:

بما أنك في طور الدراسة المرجعية، ابدأ فوراً بجمع "Data Sheets" لنوعين من الألواح (مثلاً Jinko أو Longi) ونوعين من العواكس (مثل SMA أو Huawei) بقدرة $100\ kW$ أو عاكسين بقدرة $50\ kW$ لكل منهما.

**هل ترغب في أن نلقي نظرة على توزيع الألواح المقترح بناءً على مساحة السطح الظاهرة في الصورة؟** يمكنني مساعدتك في تقدير المساحة وعدد الألواح التي يمكن استيعابها.
