MAQattan/My-Graduation-Project/GP_Obsidian/Accessories/ضبط الهوامش للتجليد في LaTeX (Binding Offset).md

ما تبحث عنه يسمى تقنياً **Twoside Printing**. في الكتب والأطاريح، نحتاج لهامش إضافي (gutter) من جهة التجليد؛ ففي الصفحات الفردية يكون الهامش على اليمين، وفي الزوجية على اليسار.

لتحقيق ذلك، استخدم حزمة `geometry` مع خيار `twoside` و `bindingoffset`:

Code snippet

```tex
\usepackage[
  inner=3cm,      % الهامش الداخلي (جهة التجليد)
  outer=2cm,      % الهامش الخارجي
  bindingoffset=1cm % القيمة الإضافية للتجليد
]{geometry}

% تأكد من تعريف نوع المستند كصفحتين
\documentclass[twoside]{report}
```

**ملاحظة:** إذا كنت تطبع على وجه واحد فقط (Single-sided) وتريد الهامش دائماً على اليمين لجميع الصفحات، قم بإلغاء خيار `twoside` واكتفِ بضبط `right` و `left` يدوياً.
