MAQattan/My-Graduation-Project/GP_Obsidian/Thesis/Thesis MOC.md

>[!warning]
>ربما في النهاية أرفع الاطروحة لـ Gemini و ChatGPT وأطلب منهم أن يقترحوا لي أسماء للفصول تكون موجزة وعلمية وشاملة.
#### [[الفصل أول - المقدمة]]  
#### [[الفصل الثاني - الأسس الكهربائية للمنظومة]]
#### [[الفصل الثالث -  توليد الطاقة الكهربائية]]
#### [[الفصل الرابع -  الخلايا والألواح الكهروضوئية]]
#### [[الفصل الخامس - المنهجية المتقدمة لتعزيز كفاءة الألواح]]
#### [[الفصل السادس - أنظمة الطاقة الشمسية]]
#### [[الفصل السابع - الانفرتر]]
#### [[الفصل الثامن - زوايا ميل الألواح الشمسية وتوجيهها]]

#### [[الفصل التاسع - كابلات وحمايات المنظومات الكهروضوئية]]  
#### [[10 - 00 الفصل العاشر - تصميم منظومة شمسية متصلة بالشبكة]] 

#### [[الفصل الحادي عشر - محاكاة وتحليل أداء المنظومة عبر برنامج PVsyst]] 
#### [[الفصل الثاني عشر]]
#### [[الفصل الثالث عشر]]
#### [[الفصل الرابع عشر]] 

### [[الملحقات MOC]] 

>[!Idea] تذكر
> عليك أن تكتب [[ملخيص باللغة الانكليزية (Abstract)]] للمشروع في نهاية الاطروحة 

---
[[الفصل التاسع - كابلات وحمايات المنظومات الكهروضوئية]] 

---
