MAQattan/My-Graduation-Project/GP_Obsidian/Thesis/أهداف المشروع (Project Objectives).md

بناءً على محددات مشكلة البحث المتمثلة في قيود المساحة المعمارية للسطح، يهدف هذا المشروع بشكل أساسي إلى **تصميم واستمثال منظومة طاقة شمسية كهروضوئية مرتبطة بالشبكة الكهربائية للمنشأة المصرفية، لتحقيق أقصى وفر طاقي ممكن ضمن المحددات المساحية المتاحة**.

ولتحقيق هذا الهدف العام، تتبلور الأهداف التفصيلية والتشغيلية للمشروع في النقاط الآتية:

1. **الاستمثال المساحي والمكاني (Spatial Optimization):** إجراء دراسة مساحية وهندسية دقيقة لسطح مبنى المنشأة، واستغلال المساحة المحدودة بفعالية قصوى عبر اختيار تقانات ألواح كهروضوئية ذات كفاءة وكثافة استطاعة عاليتين (Power Density)، مع تحديد زوايا الميل المثلى ومسافات التباعد الهندسي لمنع التظليل المتبادل بين المصفوفات (Inter-row Shading).
    
2. **التصميم الهندسي والكهربائي للمنظومة:** حساب وتصميم كافة المكونات الكهربائية للمنظومة الكهروضوئية المرتبطة بالشبكة، بما يشمل تحديد التوصيل التسلسلي والتفرعي للألواح (String Design)، واختيار العواكس الذكية (Inverters) المتوافقة مع استطاعة المصفوفة الكلية، وضمان مواءمة الجهد والتيار للربط مع الشبكة.
    
3. **المحاكاة البرمجية وتحليل الأداء (Software Simulation & Performance Analysis):** استخدام البرمجيات الهندسية التخصصية (مثل برنامج **PVsyst**) لنمذجة المنظومة الكهروضوئية بدقة، والتنبؤ بحجم الطاقة الكهربائية السنوية المتوقعة وحقنها في الشبكة، وحساب عامل الأداء (Performance Ratio - PR)، وتحليل مخطط الضياعات الشامل (Loss Diagram) لتقييم كفاءة التصميم في ظروف التشغيل الحقيقية.
