MAQattan/My-Graduation-Project/GP_Obsidian/Thesis/أهمية المشروع (Project Importance).md

تتجلى أهمية هذا البحث في كونه يقدّم نموذجاً هندسياً تطبيقياً لتطوير أنظمة الطاقة الكهروضوئية المرتبطة بالشبكة (On-Grid) داخل البيئات الحضرية المقيدة مساحياً، وتحديداً في المنشآت المصرفية الحيوية التي تتطلب موثوقية تشغيلية عالية. وتنبثق القيمة الجوهرية للمشروع من المحاور التالية:

1. **اِبتكار حلول للمحدودية المكانية:** تبرز الأهمية التقنية في معالجة القيود المعمارية والعوائق الإنشائية للأسطح عبر تطبيق منهجية "التثبيت المتدرج" (Terraced Mounting)، والتي سمحت برفع "عامل استغلال المساحة" (LUF) وتحقيق كثافة استطاعة مرتفعة بلغت $119.59 W/m^2$ مع تحييد كامل لأثر الظلال المتبادلة.
2. **تعزيز الجدارة الطاقية:** يساهم المشروع في وضع أسس دقيقة لـ "المواءمة الكهربائية" بين التقنيات المتقدمة للألواح (N-Type HPBC) والعواكس الذكية متعددة المتعقبات (Multi-MPPT)، مما يضمن تقليص فواقد "عدم التطابق" والمفاقيد الحرارية والأومية إلى حدودها الدنيا.
3. **دقة التحقق عبر التوأم الرقمي:** تكمن الأهمية الأكاديمية في الانتقال من التقديرات النظرية إلى بناء "توأم رقمي" (Digital Twin) للمنظومة عبر برنامج PVsyst، مما أتاح التنبؤ الدقيق بمؤشرات الأداء الحاكمة مثل "معامل الأداء" (PR) الذي تجاوز $89\%$، و"الإنتاجية النوعية" السنوية التي بلغت $1881 kWh/kWp$.
4. **الاستدامة والجدوى الاقتصادية:** يدعم المشروع خفض "تكلفة الوحدة الطاقية" (LCOE) للمنشأة المصرفية، مما يثبت نجاعة الاستثمار في الطاقة المتجددة كبديل استراتيجي لتقليل الانبعاثات الكربونية وتحقيق الاستقلال الطاقي المستدام.
5. **مرجع تصميمي وبحثي:** يمثل هذا البحث، دليلاً هندسياً مرجعياً لتصميم المنظومات الكهروضوئية المربوطة على الشبكة للمباني الإدارية والتجارية المشابهة في المنطقة.
