MAQattan/My-Graduation-Project/GP_Obsidian/Thesis/الفصل أول - المقدمة.md

## [[مقدمة عامة (General Introduction]] 
## [[أهمية المشروع (Project Importance)]] 
## [[مشكلة البحث (Research Problem)]] 
## [[أهداف المشروع (Project Objectives)]] 
## [[منهجية العمل (Project Methodology)]] 
## [[حدود الدراسة (Scope and Limitations)]] 
## [[هيكلية فصول المشروع (Project Structure)]]
