MAQattan/My-Graduation-Project/GP_Obsidian/Thesis/حدود الدراسة (Scope and Limitations).md

يتحدد نطاق هذا البحث ومخرجاته بمجموعة من المحددات الجغرافية، والتقنية، والمساحية التي جرى العمل في إطارها، وتتمثل حدود الدراسة في النقاط الآتية:

1. **الحدود الجغرافية والمكانية (Spatial & Geographical Limitations):** تقتصر هذه الدراسة على التصميم الهندسي والتحليل الطاقي للموقع الجغرافي المحدد الخاص بمبنى المنشأة المصرفية المعنية بالدراسة. وبناءً على ذلك، فإن قراءات الإشعاع الشمسي، وزوايا الميل المثلى، وتأثيرات الظلال، هي نتائج تخصصية مفرَدة ترتبط بالإحداثيات الجغرافية للموقع، ولا يمكن تعميمها بشكل تطابقي على مناطق أخرى تختلف مناخياً أو جغرافياً.
    
2. **الحدود الفنية والتقنية (Technical Limitations):** يقتصر النطاق الفني للمشروع على دراسة وتصميم الأنظمة الكهروضوئية المرتبطة بالشبكة الكهربائية العامة (**Grid-Connected Systems**) التي تحقن الطاقة مباشرة في شبكة المبنى أو الشبكة العامة نهاراً، دون التطرق إلى أنظمة التخزين الكيميائي (البطاريات) أو الأنظمة المستقلة عن الشبكة (Off-Grid).
    
3. **الحدود المساحية والإنشائية (Structural Limitations):** تقيدت الدراسة بالحدود المعمارية والمساحة الصافية المتاحة فعلياً على سطح مبنى المصرف، والالتزام الكامل بالعوائق الإنشائية والميكانيكية القائمة (مثل غرف الخدمات ووحدات التكييف الخارجية الحالية) دون إجراء أي تعديلات جوهرية على التصميم المعماري للمبنى.
    
4. **حدود البيانات المناخية والبيئية (Meteorological Data Limitations):** تعتمد المحاكاة البرمجية وتحليل الأداء الديناميكي للمنظومة عبر برنامج **PVsyst** على السلاسل الزمنية والبيانات المناخية التاريخية القياسية المستمدة من قواعد البيانات المعتمدة (مثل Meteonorm)، والتي تمثل معدلات السنوات السابقة، وبالتالي قد تظهر بعض الفروقات الطفيفة مقارنةً بالظروف الجوية الحقيقية المتغيرة من سنة إلى أخرى.
