MAQattan/My-Graduation-Project/GP_Obsidian/Thesis/مقدمة عامة (General Introduction.md

شهد قطاع الطاقة العالمي في العقود الأخيرة تحولاً جذرياً نحو مصادر الطاقة المتجددة والمستدامة، مدفوعاً بالتحديات البيئية المتزايدة والارتفاع المستمر في تكاليف الوقود الأحفوري، فضلاً عن السعي نحو تحقيق أمن الطاقة. وتتصدر التقانات الكهروضوئية (Photovoltaic Technologies) هذا التحول كواحدة من أكثر الحلول كفاءةً ونمواً، نظراً لوفرة الإشعاع الشمسي وتطور كفاءة الألواح وانخفاض تكاليفها الاستثمارية.

تعد المنظومات الكهروضوئية المرتبطة بالشبكة الكهربائية (Grid-Connected PV Systems) الخيار الأمثل للتطبيقات الحضرية والتجارية؛ حيث تتيح هذه الأنظمة حقن الطاقة المولدة مباشرة في الشبكة العامة دون الحاجة إلى أنظمة تخزين كيميائي (بطاريات) مكلفة وذات عمر زمني محدود، مما يرفع من الكفاءة الإجمالية للمنظومة ويقلل من فترة استرداد رأس المال (Payback Period). وتعتمد موثوقية هذه المنظومات على دقة التصميم الهندسي وحساب زوايا الميل المثلى، بالإضافة إلى التحليل الدقيق للأداء في ظروف التشغيل الحقيقية للتنبؤ بالإنتاجية السنوية ومعامل الأداء (Performance Ratio).
