MAQattan/My-Graduation-Project/GP_Obsidian/Thesis/منهجية العمل (Project Methodology).md

اعتمد البحث منهجية هندسية تحليلية وتطبيقية متكاملة، تنتظم في خمس مراحل أساسية مترابطة، تضمن الانتقال السلس من المفاهيم الفيزيائية إلى الحلول التصميمية القابلة للتنفيذ:

**المرحلة الأولى: بناء الإطار المعرفي والتأصيل التقني (Theoretical Framework)** تبدأ المنهجية ببناء قاعدة صلبة تشمل تحليل طبيعة الإشارات الكهربائية وتحولات الطاقة بين الجانبين المستمر والمتردد. تلا ذلك دراسة فيزيائية معمقة للخلايا الكهروضوئية، مع التركيز على تقنيات (N-Type HPBC) المتقدمة لرفع الكفاءة، وتحليل طوبولوجيا العواكس الذكية المرتبطة بالشبكة لضمان جودة الطاقة (Power Quality).

**المرحلة الثانية: التقييم الجيومناخي وتحليل المورد الشمسي (Climatic & Resource Assessment)** في هذه المرحلة سيتم استخلاص البيانات المناخية لموقع الدراسة في مدينة حلب عبر منصة (Global Solar Atlas). شملت المنهجية حساب "ساعات الذروة الشمسية" (PSH) وتحديد زوايا الميل (Tilt Angle) والسمت (Azimuth) المثالية عبر نماذج رياضية دقيقة (Optimal Tilt Models) لتعظيم استلام الإشعاع المائل الكلي (GTI).

**المرحلة الثالثة: التصميم الإنشائي والهندسة المكانية (Structural & Shadow Engineering)** استجابةً للقيود المساحية للمنشأة المصرفية، اتبعت المنهجية نمط "التصميم القائم على المساحة" (Area-based Design). تم ابتكار حل هندسي يعتمد على "التثبيت المتدرج" (Terraced Mounting) لرفع "عامل استغلال المساحة" (LUF) إلى حده الأقصى. كما أُجري تحليل دقيق للظلال الموضعية (الجانبية والأفقية) للعوائق الإنشائية باستخدام العالقات المثلثية وبرنامج (AutoCAD) لضمان خلو الخلايا الفعالة من التظليل في ساعات الذروة.

**المرحلة الرابعة: المواءمة الكهربائية وتصميم الحمايات (Electrical Sizing & Protection)** تضمنت هذه المرحلة إجراء "حسابات الحالات الحرجة للجهد" (Critical Voltage Analysis) لتحديد عدد الألواح الأمثل في السلسلة (String Sizing) لضمان استقرار العمل ضمن نافذة (MPPT) للعاكس صيفاً وشتاءً. كما تم تصميم شبكة الموصلات ونظام الحماية وفق مبدأ "الانتقائية الصارمة" (Selectivity)، بما يشمل حمايات التيار الزائد، والجهود العابرة (SPD)، ومنظومة التأريض الوقائي.

**المرحلة الخامسة: النمذجة الرقمية والتحقق من الأداء (Digital Twin & Performance Verification)** تُختتم المنهجية ببناء "توأم رقمي" (Digital Twin) للمنظومة عبر برنامج (PVsyst). تهدف هذه المرحلة إلى المحاكاة الديناميكية للأداء السنوي، واستخلاص مؤشرات الجدارة الطاقية مثل "معامل الأداء" (PR) و"الإنتاجية النوعية" (Specific Yield)، مع تحليل تفصيلي لمخطط تدفق المفاقيد (Loss Diagram) للتأكد من مطابقة النتائج الرقمية للأهداف التصميمية.
