MAQattan/My-Graduation-Project/GP_Obsidian/Thesis/هيكلية فصول المشروع (Project Structure).md

تنتظم هذه الدراسة في أحد عشر فصلاً متكاملاً، تتبع منهجية هندسية رصينة تتدرج من التأصيل النظري والمفاهيمي وصولاً إلى التصميم التطبيقي والتحقق الرقمي، وذلك وفق الهيكلية التالية:

يستعرض **الفصل الأول** مقدمة عامة حول البحث، بينما يخصص **الفصل الثاني** لبناء "الأُسس الكهربائية للمنظومة" عبر تحليل طبيعة الإشارات الكهربائية وتحولات الطاقة، وتحليل تدفق القدرة في شبكات التيار المتردد. ويتناول **الفصل الثالث** "توليد الطاقة الكهربائية" من منظور فيزيائي يشمل المصادر التقليدية والمتجددة والمركزات الشمسية (CSP).

ينتقل العمل في **الفصل الرابع** إلى "الخلايا والألواح الكهروضوئية" لتوصيف الدائرة المكافئة للخلية وأنواع الألواح وخصائص أدائها. يتبعه **الفصل الخامس** الذي يستعرض "المنهجية المتقدمة لتعزيز كفاءة الألواح" بالتركيز على تقنيات "أنصاف الخلايا" (Half-Cut Cells) لخفض المفاقيد المقاومية والحد من أثر البقع الساخنة. وفي **الفصل السادس**، يتم تصنيف "أُنظمة الطاقة الشمسية" (المستقلة، المرتبطة، والهجينة)، وصولاً إلى **الفصل السابع** الذي يحلل فيزياء "العاكس" (Inverter) وطوبولوجيا الربط مع الشبكة.

يركز **الفصل الثامن** على الهندسة الميكانيكية من خلال "زوايا ميل الألواح الشمسية وتوجيهها" باستخدام النمذجة الرياضية الدقيقة وتتبع الشمس. بينما يغطي **الفصل التاسع** "كابلات وحمايات المنظومات الكهروضوئية" لضمان الانتقائية الصارمة في جانب التيار المستمر (DC) والمرتدد (AC) وحماية المنظومة من الجهود العابرة والصواعق.

ويُمثّل **الفصل العاشر** العصب التنفيذي للدراسة عبر "تصميم منظومة شمسية متصلة بالشبكة" لمنشأة مصرفية، حيث ينساب التصميم عبر أربعة أطوار تبدأ بالأساس المناخي، ثم التصميم الهيكلي وتحليل الظلال، فالمواءمة الكهربائية للعاكس، وختاماً بتصميم الحمايات والترابط الكهربائي. وأخيراً، يأتي **الفصل الحادي عشر** ليقدم "تحليل أداء المنظومة عبر برنامج PVsyst" كأداة للتحقق الرقمي وبناء التوأم الرقمي واستخلاص مؤشرات الجدارة الطاقية للمشروع.
