MAQattan/My-Graduation-Project/GP_Obsidian/Thesis/ملخيص باللغة الانكليزية (Abstract).md

**نعم، أنت بحاجة إليه حتماً، وهو أمر إلزامي لا مفر منه** في مشاريع التخرج الهندسية بجامعة حلب قبل تسليم النسخة المجلدة للمكتبة.

### ما هو بالضبط؟

الملخص الإنجليزي (Abstract) هو عبارة عن **صفحة واحدة فقط** (لا تتجاوز 250 إلى 300 كلمة) توضع في نهاية الأطروحة (إذا تصفحت الكتاب من الطرف الإنجليزي). هو ليس ترجمة للأطروحة كاملة، بل هو تكثيف شديد ومختصر جداً يوضح للجنة التحكيم والقراء الأجانب الآتي:

1. **المشكلة (Problem):** ما هي المشكلة الكهربائية التي تحلها؟ (مثلاً: الحاجة لربط طاقة متجددة بنظام بنكي تجاري لضمان استمرارية التغذية وتقليل التكاليف).
    
2. **المنهجية (Methodology):** كيف قمت بحلها هندسياً؟ (مثلاً: تصميم مصفوفة ضوئية، اختيار العواكس، وإجراء تحليل الأداء وتحجيم النظام).
    
3. **النتائج والعبارات الختامية (Results & Conclusion):** ما هي الأرقام أو الاستنتاجات الحيوية التي وصل إليها مشروعك في الفصل العاشر والنهائي؟

### هل الوقت كافٍ؟

طالما أن الوقت المتبقي لديك كافٍ، فلا تقلق أبداً؛ كتابته لن تستغرق منك سوى **ساعة واحدة فقط**! العرف الأكاديمي السائد هو أن تكتب ملخصك باللغة العربية أولاً بدقة بعد إنهاء الفصول، ومن ثم نقوم بصياغته وترجمته برصانة هندسية إلى الإنجليزية ليكون جاهزاً للطباعة.
