MAQattan/My-Graduation-Project/GP_Obsidian/Thesis/مسودة دراسة الجدوى.md

عند تطبيق حسابات المسافات البينية القياسية لتجنب التظليل ($D_{min} = 3\text{ m}$)، تبين أن المنظومة ستفقد ما يقارب **50-60%** من المساحة الصافية للسطح، ونظراً لمحدودية المساحة والتعارض الجوهري مع هدف التصميم الأساسي وهو **(الاستغلال الأقصى للمساحة - Maximum Space Utilization)** لسطح البنك، سنتجه لطريقة الهياكل المتدرجة (Terraced / Stepped Mounting Structures) بدلاً من اعتماد طريقة التثبيت التقليدي بمسافات بينية (Standard Fixed Mounting with Inter-row Spacing)، وسنعلل القرار بحساب جدوى الإضافة أو ما يسمى أكاديميا بالمقارنة الحدية (Marginal Analysis).
%% قد أعلل القرار بدراسة جدوى اقتصادية %%

لتبسيط الحسابات سندرس جدوى لزوج من الالواح سيكون  ليتم تعميمها على كامل المنظومة، وذلك من أجل التموضع الطولي (Portrait) للألواح كما تم أعتماده آنفاً. إذا سيتم دراسة الجدوى من أجل صفين ومن أجل ثلاث صفوف 
##### من أجل صفين من الألواح :

في هذه الحالة سيحتاج الصف الثاني ارتفاع اضافي من الهياكل المعدنية يساوي الارتفاع الرأسي للصف الأول $1.173 \text{ m}$ لتتلاقة الحافة الخلفية للوح الأمامي مع الحافة الأمامية للوح الخلفي، ومن أجل تحقيق هذه الأرتفاع 

ومن أجل الصف الثالث سنحتاج إلى ارتفاع إضافي يساوي ضعف الاتفاع السابق $2.346 \text{ m}$، وبحساب التكلفة الاجمالية :

وبناءً عليه، تمت المفاضلة بين خيارين:

1. **الخيار الأول (التقليدي):** استيعاب عدد أقل من الألواح (مثلاً 15 لوحاً) لضمان عدم التظليل، مما يقلل القدرة الكلية للمنظومة.
    
2. **الخيار الثاني (المتدرج):** رفع المصفوفات الخلفية ميكانيكياً لإلغاء المسافات البينية، مما يسمح بمضاعفة عدد الألواح (إلى 30 لوحاً مثلاً).

**من منظور الجدوى:** بالرغم من زيادة تكلفة الهيكل المعدني بنسبة تقديرية [أضف نسبة، عادة تكون 20-30% زيادة في وزن الحديد]، إلا أن هذه التكلفة تُسترد في أقل من [عام أو عامين] نتيجة زيادة الإنتاجية بمقدار الضعف، خاصة عند مقارنتها بتعرفة الكهرباء التجارية للبنك وتكلفة الفرصة البديلة للطاقة غير المنتجة."

---
---
لحساب تكلفة الهيكل المعدني بدقة لنظام مكون من **لوحين مصفوفين بجانب بعضهما بشكل طولي (Portrait)** وبزاوية ميلان **31 درجة**، يجب أولاً تحليل الأبعاد الهندسية لحساب كمية الحديد والمواد المطلوبة بدقة:

## **1. الأبعاد الهندسية للهيكل**

- **العرض الإجمالي للمصفوفة:** 2.268 متر (1.134 متر × 2 ألواح) + حوالي 10 سم هوامش وفواصل = **2.40 متر**.
- **الطول المائل (الوتر):** طول اللوح هو 2.278 متر، وبالتالي يحتاج إلى جسر مائل بطول **2.30 متر**.
- **ارتفاع القائم الخلفي (بزاوية 31°):** حسب قانون الجيب ($2.30 \times \sin(31^\circ)$) = **1.18 متر**.
- **القاعدة الأرضية الأفقية (المسقط):** حسب قانون جيب التمام ($2.30 \times \cos(31^\circ)$) = **1.97 متر**.

---

## **2. جدول كميات الحديد المطلوبة (حديد ميكانو مجلفن)**

لإنشاء مثلثين داعمين (A-Frames) مع جسرين عرضيين لتثبيت الألواح، تحتاج إلى الأطوال التالية:

|الجزء [1]|العدد|الطول المطلوب للقطعة الواحدة|إجمالي الطول|
|---|---|---|---|
|**الجسور العرضية (حوامل الألواح)**|2|2.40 متر|4.80 متر|
|**الجسور المائلة (الوتر)**|2|2.30 متر|4.60 متر|
|**القوائم الخلفية (العمودية)**|2|1.18 متر|2.36 متر|
|**القواعد الأرضية الأفقية**|2|1.97 متر|3.94 متر|
|**إجمالي أمتار الحديد المطلوبة**|-|-|**15.70 متر طولي**|

- **عدد الرواط (القطع) المطلوبة:** بما أن طول الروطة القياسي هو 6 أمتار، فإن $15.70 \div 6 = 2.61$. وبالتالي تحتاج إلى **3 رواط حديد ميكانو مجلفن**.

---

## **3. جدول الملحقات والقواعد المطلوبة**

- **مشابك الألواح (Clamps):**
    - **مشابك جانبية (End Clamps):** عدد **4** (لتثبيت الأطراف الخارجية للألواح).
    - **مشابك وسطية (Mid Clamps):** عدد **2** (لتثبيت اللوحين معاً من المنتصف).
- **قواعد كونكريتية (صبات):** تحتاج إلى **4 صبات** (وزن 50 أو 65 كغ) لتثبيت زوايا المثلثين الأرضية.
- **زوايا وصل ميكانو (Joints):** تحتاج إلى **6 زوايا** لتجميع المثلثات وربط الجسور العرضية.
- **براغي وصواميل:** حوالي **30 برغي** ميكانو مع العزقات والواشرات. [2]

---

## **4. الحساب المالي التقديري للتكلفة (بالليرة السورية)**

بناءً على الأسعار الرائجة لعام 2026:

|المادة|الكمية|سعر الوحدة التقديري|إجمالي السعر|
|---|---|---|---|
|**حديد ميكانو مجلفن (روطة 6م)**|3 قطع|20,000 ل.س|60,000 ل.س|
|**صبات كونكريتية (وزن 50 كغ)**|4 صبات|8,000 ل.س|32,000 ل.س|
|**مشابك ألمنيوم للألواح (جانبي ووسطي)**|6 قطع|2,500 ل.س|15,000 ل.س|
|**زوايا ميكانو وبراغي للتثبيت**|مجموعة كاملة|15,000 ل.س|15,000 ل.س|
|**التكلفة الإجمالية التقريبية للمواد**|-|-|**122,000 ليرة سورية**|

_ملاحظة: التكلفة أعلاه لا تشمل أجور التركيب والشحن إلى موقع العمل، وقد تختلف أسعار قطع الحديد والمشابك بشكل طفيف حسب الوكيل المصنّع وسماكة الحديد (1.5 ملم أو 1.85 ملم)._

إذا كنت ترغب في ذلك، يمكنني تعديل الحسابات بناءً على **طبيعة السطح** (مستوٍ، مائل، أو قرميد) أو إفادتك بـ **أفضل طريقة لتوزيع الصبات** لضمان مقاومة الرياح.

---

---

تختلف أسعار الهياكل المعدنية (الحديد المجلون) للطاقة الشمسية في سوريا بناءً على الوزن، السماكة، ونوع الحديد (ميكانو، حديد لحام).

بناءً على تحديثات عام 2026، إليك تفاصيل الأسعار لهياكل الحديد المجلفن:

- **حديد ميكانو مجلفن (منغنيس) عالي الجودة:** يتراوح سعر الروطة/القطعة (جملة/مفرد) ما بين **19,500 إلى 20,000 ليرة سورية**.
- **حديد لحام (قياس 40x40):** يتراوح سعر القطعة ما بين **19,500 إلى 20,000 ليرة سورية**.
- **صبات كونكريتية (وزن 65):** سعر الجملة 9,500، والمفرد 10,000 ليرة سورية.
- **صبات كونكريتية (وزن 50):** سعر الجملة 7,500، والمفرد 8,000 ليرة سورية.
- **ملحقات الهيكل (براغي/جوين ميكانو):** سعر القطعة يتراوح بين 1,000 إلى 3,000 ليرة سورية حسب النوع.

**مواصفات الهياكل المتاحة:**

- **السماكة:** 1.5 ملم و 1.85 ملم.
- **المميزات:** مجلفن بالكامل لمقاومة الصدأ والعوامل الجوية، مناسب للأسطح والمنازل.

_ملاحظة: الأسعار المذكورة قد تتغير بناءً على تقلبات أسعار الصرف والمواد الأولية في السوق السورية._

**1. الروطة أو القطعة (The Section/Piece)**

- **تعريف الروطة:** هي التسمية المحلية الشائعة في الأسواق لـ **"البروفيل"** أو **"البوري"** أو **"الجسر الحديدي"**.
- **الطول القياسي:** تأتي القطعة أو الروطة بطول موحد يبلغ **6 أمتار** تقريباً.
- **حساب السعر:** السعر المذكور سابقاً هو للقطعة الكاملة (الـ 6 أمتار) وليس للمتر الواحد.

**2. حديد الميكانو المجلفن (Galvanized Meccano Iron)**

- **طريقة التركيب:** حديد مسبق الصنع والتقطيب يتم تركيبه بواسطة **البراغي والصواميل** فقط دون الحاجة للحام.
- **التصميم:** يحتوي البروفيل على ثقوب متوازية ومدروسة هندسياً لتسهيل التجميع وتعديل الزوايا والميلان.
- **الجلفنة:** مغطى بطبقة من الزنك لحمايته من الرطوبة، العوامل الجوية، ومنع تشكل الصدأ.
- **الميزة الأساسية:** مرن للغاية، يسهل فكه ونقله، ويتحمل الرياح بفضل مرونة واصلاته.

**3. حساب الملحقات لكل قطعة (Accessories per Piece/Meter)**

لا تحسب الملحقات بالمتر الطولي للحديد، بل تُحسب **حسب عدد الألواح الشمسية** وتصميم الهيكل (حامل أرضي، مائل، أو سطحي).

لتركيب منظومة نموذجية (مثال: هيكل يتسع لـ 4 ألواح فوق بعضها أو بجانب بعضها)، تحتاج كل **قطعة حديد (6 أمتار)** تقريباً إلى:

- **براغي التثبيت (البراغي والزوايا):** من **4 إلى 6 براغي** لتثبيت القطعة مع القواعد أو الجسور الأخرى.
- **رابط ميكانو (Join):** **قطعة واحدة** عند الحاجة لوصل روطة مع روطة أخرى لتمديد الطول.
- **مشابك الألواح (Clamps):** تحتاج المنظومة إلى نوعين لتثبيت الألواح فوق الحديد:
    - **مشابك جانبية (End Clamps):** عدد **4** لأطراف الصف الواحد.
    - **مشابك وسطية (Mid Clamps):** عدد **2** بين كل لوحين متجاورين.

---

إذا أردت حساب التكلفة الدقيقة، يرجى تزويدي بـ **عدد الألواح الشمسية** لديك و**حجمها (الوات)**، لنقوم بحساب كمية الحديد والملحقات بدقة.

### **حساب التكاليف الإضافية ($\Delta Investment$)**

لحساب الجدوى، لا تحتاج لحساب تكلفة المشروع كاملاً، بل احسب فقط **الفرق**:

1. **تكلفة الحديد الإضافي:** (وزن الهيكل المتدرج - وزن الهيكل التقليدي) × سعر كيلو الحديد واصل ومُركب.
    
2. **أجور العمالة الزائدة:** الفرق في أجور التركيب نتيجة تعقيد الهيكل الميكانيكي.
    
3. **الكتل الإسمنتية:** زيادة حجم القواعد نتيجة زيادة ارتفاع الهيكل (تأثير الرياح).

### **3. حساب العائد المادي الإضافي ($\Delta Revenue$)**

هنا تستخدم القيم التي استخرجناها سابقاً:

1. **كمية الطاقة الإضافية سنوياً:**
    
    $$\Delta E = (N_{proposed} - N_{baseline}) \times P_{panel} \times SY$$
    
    - $N$: عدد الألواح.
        
    - $P_{panel}$: استطاعة اللوح الواحد (kWp).
        
    - $SY$: الإنتاجية النوعية لمدينة حلب (1730 kWh/kWp).
        
2. **الوفر السنوي بالفاتورة:**
    
    $$\text{Annual Savings} = \Delta E \times \text{Tariff (1,700 SYP)}$$

### **4. مؤشرات الجدوى الاقتصادية**

- **فترة استرداد التكاليف الإضافية (Simple Payback Period - SPP):**
    
    تحسب فقط للمبلغ الإضافي الذي دفعته في الهياكل:
    
    $$SPP = \frac{\Delta \text{Investment}}{\text{Annual Savings}}$$
    
    _(إذا كانت النتيجة أقل من 3-4 سنوات، يعتبر القرار الهندسي ممتازاً جداً)._
    
- **الربح السنوي بعد الاسترداد:**
    
    هو نفسه "الوفر السنوي" الذي سيبقى في ميزانية البنك طوال عمر المنظومة (25 سنة) بعد أن تكون المنظومة قد "سددت ثمن حديدها الإضافي".

---

### **مثال تطبيقي سريع (للتوضيح):**

نفترض أن الطريقة التقليدية تستوعب 30 لوحاً، والطريقة المتدرجة تستوعب 50 لوحاً:

- **الزيادة في الإنتاج:** 20 لوحاً × 0.55 kWp × 1730 = **19,030 kWh/year**.
    
- **الوفر المادي:** 19,030 × 1,700 = **32,351,000 ليرة سورية سنوياً**.
    
- **المقارنة:** إذا كانت تكلفة الحديد الإضافي لرفع الألواح هي 60 مليون ليرة مثلاً، فإن فترة استرداد ثمن هذا الحديد هي أقل من سنتين (**60 / 32.3 = 1.8 سنة**).

### **نصيحة إضافية لتدعيم التعليل الهندسي:**

في حال طُلب منك تعليل "هندسي" إضافي بجانب الجدوى، اذكر أن **"تكلفة المساحة"** في المنشآت التجارية (البنوك) مرتفعة جداً، وأن زيادة كثافة الطاقة في المتر المربع الواحد ($W/m^2$) هي استراتيجية عالمية في الأماكن ذات المساحات المحدودة، حتى لو زادت تكلفة الهياكل، لأن البديل هو "طاقة مفقودة" لا يمكن تعويضها بسبب ضيق السطح.
