MAQattan/My-Graduation-Project/GP_Obsidian/Thesis/10/10 - 00 الفصل العاشر - تصميم منظومة شمسية متصلة بالشبكة.md

### [[10 - 1 مقدمة]] 

## الطور الأول: الأساس المعياري والمناخي للموقع

يمثل هذا الطور الخطوة التأسيسية الأولى في المسار التصميمي للمنظومة؛ حيث يتم فيه الانتقال من التوصيف العام للموقع إلى استخلاص وتدقيق البيانات الإشعاعية والحرارية الفعلية المتاحة. تكمن الغاية هنا في بناء قاعدة بيانات مناخية دقيقة وموثوقة، تشكل حجر الزاوية الذي يستند إليه حساب زوايا الميل واختيار التجهيزات في المراحل اللاحقة.
### [[10 - 2 المورد الشمسي والبيانات المناخية للموقع (Solar Resource Data)]] 

### [[10 - 3 مفهوم الساعات الشمسية الذروية (Peak Sun Hours - PSH)]]  

### [[10 - 4 الإنتاجية النوعية (Specific Production - Specific Yield)]] 

### [[10 - 5 المعايير الاقتصادية والتشغيلية]] 

## الطور الثاني: اختيار المكون الأساسي والتصميم الهيكلي (الميكانيكي)

بناءً على المعطيات الجغرافية والمناخية المستخلصة في الطور السابق، ينتقل العمل في هذا الطور نحو الهندسة الميكانيكية والإنشائية للمنظومة. يرتكز هذا الجزء على معالجة القيود المكانية والعوائق المعمارية للسطح، من خلال تحديد زوايا الميل المثلى وحساب فواصل الظلال بالعلاقات المثلثية، وصولاً إلى تطبيق الفلسفة المبتكرة للهياكل المتدرجة لتعظيم القدرة المثبتة للمصفوفة.
### [[10 - 6 أنماط التصميم والمنهجية المتبعة]] 

### [[10 - 7 اختيار اللوح الشمسي]] 

### [[10 - 8 التوجيه الجغرافي وزاوية الميل المثالية (Orientation and Optimal Tilt Angle)]] 
### [[10 - 9 تحليل الظلال]] 

### [[10 - 10 منهجية تركيب وتوزيع الألواح]] 

### [[10 - 11 دراسة إمكانية استغلال المساحات المظللة جزئياً]] 

### [[10 - 12 حساب الاستطاعة الإجمالية للمنظومة وتقييم الكثافة المساحية]]

## الطور الثالث: المواءمة والتحجيم الكهربائي للعاكس

بعد ضبط التوزيع الميكانيكي والمكاني للألواح، يتناول هذا الطور الربط الكهربائي والمواءمة بين المصفوفة الكهروضوئية والعاكس الذكي. يركز هذا التحجيم على دراسة السلوك الحراري للجهود والتيارات عند الحالات المناخية المتطرفة لموقع الدراسة، لضمان استقرار جهود التشغيل طوال العام وضمان بقائها ضمن نوافذ عمل خوارزميات تتبع نقطة القدرة القصوى ($\text{MPPT}$) بأعلى كفاءة.
### [[10 - 13 اختيار العاكس]]

### [[10 - 14 التحليل الحراري الحرج لجهود الألواح الكهروضوئية]]

### [[10 - 15 تحجيم السلاسل وضوابط نافذة الجهد (String Sizing)]]

### [[10 - 16 التوزيع الكهربائي الفعال للسلاسل على متعقبات القدرة (MPPT Configuration)]]

## الطور الرابع: الحمايات والترابط الكهربائي

تتويجاً لكافة الحسابات الميكانيكية والكهربائية السابقة، يُعنى هذا الطور بصياغة الفلسفة الحمائية وشرايين الربط الكهربائي للمنظومة في جبهتي التيار المستمر والمتردد ($\text{AC/DC}$). يهدف هذا الجزء إلى تحجيم الموصلات وتقليص فواقد هبوط الجهد، وتوصيف منظومة الحماية من القصر والجهود العابرة بناءً على مبدأ الانتقائية الصارمة، بما يضمن أمان المعدات والتوافق التام مع شبكة التوزيع العامة.
### [[10 - 17 جانب التيار المستمر (DC Side)]]

### [[10 - 18 جانب التيار المتردد (AC Side)]]

### [[10 - 19 منظومة القياس ومستشعرات القدرة الذكية]] 
### [[10 - 20 الحماية من الصواعق والتأريض]] 
### [[10 - 21 المخطط أحادي الخط (Single Line Diagram)]]

### [[10 - 22 جدول الكميات (BOQ)]] 

---

#### [[مسودة 01 - حمايات وكابلات]]
#### [[مسودة 02 - حمايات وكابلات]] 

---
#### [[Deleted 10-3]]
