MAQattan/My-Graduation-Project/GP_Obsidian/Thesis/10/10 - 20 الحماية من الصواعق والتأريض.md

### 10 - 20 - 1 توصيف أجهزة الحماية من الجهود العابرة (Surge Protection Devices - Type 2 SPD)

تُعد أجهزة الحماية من الجهود الزائدة والعابرة (Surge Protective Devices - SPDs) خط الدفاع التكنولوجي الاستباقي لحماية المكونات الإلكترونية الحساسة (Power Electronics) داخل العاكس الذكي. ونظراً لطبيعة تركيب المصفوفة الكهروضوئية في مكان مفتوح ومرتفع فوق سطح المبنى، فإنها تعمل بمثابة "هوائي" مثالي لالتقاط الحقول الكهرومغناطيسية الناتجة عن ضربات الصواعق غير المباشرة (Indirect Lightning Strikes)، والتي تؤدي إلى تحريض جهود عابرة فائقة (Transient Overvoltages) تنتقل عبر كابلات الـ DC.

بالتوازي مع ذلك، يتعرض جانب التيار المتردد (AC Side) لجهود عابرة ناتجة عن عمليات الفصل والوصل الديناميكي في الشبكة الكهربائية العامة (Switching Surges). لحماية كروت التحكم الدقيقة ومعالجات الإشارات الرقمية (DSPs) وجسور الترانزستورات (IGBT Inverter Bridges) من الانهيار العازلي الحراري، يخضع التصميم لمتطلبات المعيارين الدوليين **IEC 61643-11** (الخاص بمانعات الصواعق لشبكات الجهد المنخفض) و **IEC 60364-7-712**.

#### أولاً: حماية جانب التيار المستمر (DC Side Surge Protection)

يتعرض مدخلا متعقبات القدرة ($MPPT_1$ و $MPPT_2$) في العاكس لقيم جهود مستمرة تصل في ذروتها شتاءً إلى حدود قريبة من الجهد الأقصى للعاكس البالغ $1100\text{ V}$. وبناءً على التحليل الفني للعاكس المعتمد **Huawei SUN2000-25KTL-M5**، فقد تم تأكيد دمج مانعات صواعق من **النوع الثاني (Type 2 SPD)** بشكل قياسي ومدمج (Built-in) على ناقل الجهد المستمر الداخلي قبل وصوله إلى دوائر التقطيع.

تستند هندسة الحماية في جانب الـ DC إلى المحددات الرياضية التالية لضمان الفعالية:

1. **جهد التشغيل المستمر الأقصى ($U_{c\text{-}DC}$):** يجب أن يفي بالشرط المعياري بحيث يكون أعلى من أقصى جهد دارة مفتوحة للمصفوفة تحت أسوأ الظروف الحرارية شتاءً ($V_{oc\text{-}max} = 736.32\text{ V}$ إجمالي السلسلة المكونة من 13 لوحاً):
    
    $$U_{c\text{-}DC} \ge 1.25 \times V_{oc\text{-}max}$$
    
    وبما أن مانع الصواعق المدمج مصمم لتحمل جهد تشغيلي مستمر $U_{c}$ يتجاوز $1100\text{ V}$، فإن هذا الشرط محقق بأمان مطلق.
    
2. **مستوى حماية الجهد ($U_p$):** يُمثل الجهد المتبقي (Residual Voltage) الذي يسمح المانع بمروره نحو كروت العاكس أثناء تفريغ نبضة الصاعقة. لضمان سلامة العاكس، يجب أن يكون $U_p$ أقل بكثير من جهد الصمود النبضي للمكونات الداخلية للعاكس ($U_w$):
    
    $$U_p < U_w \quad (\text{Where } U_w \approx 4\text{ kV for } 1100\text{V Inverters})$$
    
    يضمن المانع المدمج حد جهد المخرجات العابرة عند مستوى $U_p \le 3.5\text{ kV}$، مما يحيد خطر تدمير كروت الـ MPPT.

#### ثانياً: حماية جانب التيار المتردد (AC Side Surge Protection)

يرتبط مخرج العاكس ثلاثي الأطوار بـ "لوحة الربط المتردد الرئيسية" ومنها إلى شبكة المنشأة والشبكة العامة. تُعد هذه النقطة عرضة لنبضات الجهد العالي الناتجة عن خطأ القصر في الشبكة أو صواعق خطوط النقل الهوائية. يحتوي العاكس **Huawei SUN2000-25KTL-M5** على منظومة حماية متكاملة من **النوع الثاني (Type 2 AC SPD)** مدمجة على مخرجه الكهربائي لحماية كروت الفلترة والتحويل العكسي.

تخضع الحماية في جانب الـ AC للمحددات التالية:

- **جهد التشغيل المستمر الأقصى ($U_{c\text{-}AC}$):** مصمم ليتحمل الارتفاعات الديناميكية لجهد الطور التشغيلي المتوفر في الموقع ($400\text{ V}$ بين الأطوار)، حيث تبلغ سعة صمود المانع المدمج $U_c \approx 480\text{ V AC}$ (Line-to-Line)، مما يمنع تفكك المانع حرارياً عند حدوث تذبذبات الجهد الاعتيادية في الشبكة.
    
- **تيار التفريغ الاسمي ($I_n$):** يمتلك المانع المدمج القدرة على تصريف تيارات نبضية متكررة بشكـل موجة قياسي ($8/20\ \mu\text{s}$) بسعة لا تقل عن $20\text{ kA}$ لكل طور، وتصل سعة التفريغ القصوى ($I_{max}$) إلى $40\text{ kA}$، مما يضمن تشتيت استطاعة الصدمة الكهربائية بأمان دون تلف الحماية من المرة الأولى.

#### ثالثاً: التكامل الديناميكي والتنسيق الحمائي (Protection Coordination)

تعتمد آلية عمل مانعات الصواعق المدمجة من النوع (Type 2) على تكنولوجيا المقاومات المتغيرة مع الجهد (Metal Oxide Varistors - MOVs). في الحالة الطبيعية، تمتلك هذه العوازل مقاومة أومية فائقة تؤول إلى اللانهاية ($\infty$)، مما يمنع تسريب أي تيار إلى الأرض. بمجرد حدوث جهد عابر يتجاوز عتبة التشغيل الآمن، تنهار مقاومة الـ MOVs ميكروياً في زمن استجابة نانومتري ($t_a \le 25\text{ ns}$)، لتتحول إلى مسار قصير المقاومة يقوم بـ "كبح" (Clamping) الجهد وتوجيه تيار الصدمة الفائض مباشرة إلى غلاف العاكس المعدني ومنه إلى شبكة التأريض.

**ملاحظة هندسية حرجة للتنفيذ:** يوصي كود **IEC 60364-7-712** بأنه في حال تجاوزت المسافة الفيزيائية الفاصلة بين مصفوفة الألواح على السطح وبين موقع تركيب العاكس مسافة $10\text{ meters}$، فإنه يجب تركيب لوحة حماية خارجية إضافية (External DC Combiner Box) تحتوي على مانع صواعق (DC SPD Type 2) مستقل عند أقرب نقطة لدخول كابلات السلاسل للمبنى. وبما أن تصميم المحطة الحالية يعتمد على تركيب العاكس في موقع قريب ومجاور للمصفوفة على السطح بمسافة تقل عن الحدود الحرجة، فإن الاعتماد على الحمايات المدمجة فائقة الوثوقية من Huawei يُعد كافياً ومطابقاً لأعلى معايير الأمان الأكاديمية والتطبيقية، مما يعزز الجدوى الاقتصادية للمشروع دون المساومة على السلامة.

#### رابعاً: تلخيص المواصفات الفنية لمنظومة الحماية من الجهود العابرة

يلخص الجدول التالي المحددات والمواصفات الهندسية لمانعات الصواعق المدمجة في المنظومة لجانبي الـ DC والـ AC:

|**البند الفني (Technical Parameter)**|**توصيف جانب التيار المستمر (DC Side)**|**توصيف جانب التيار المتردد (AC Side)**|**المرجعية والتحقق (Standard / Source)**|
|---|---|---|---|
|**فئة الحماية القياسية (SPD Type)**|النوع الثاني (Type 2 / Class II)|النوع الثاني (Type 2 / Class II)|IEC 61643-11 / Huawei Datasheet|
|**أقصى جهد تشغيل مستمر ($U_c$)**|$\ge 1100\text{ V DC}$|$480\text{ V AC}$ (L-L)|التحليل الحراري لنافذة جهد العاكس|
|**جهد الحماية المتبقي ($U_p$)**|$\le 3.5\text{ kV}$|$\le 2.0\text{ kV}$|حماية عازلية كروت الـ IGBT ($U_w$)|
|**تيار التفريغ الاسمي ($I_n - 8/20\ \mu\text{s}$)**|$20\text{ kA}$|$20\text{ kA}$|معيار الصدمات التحريضية غير المباشرة|
|**أقصى تيار تفريغ ($I_{max} - 8/20\ \mu\text{s}$)**|$40\text{ kA}$|$40\text{ kA}$|التحمل الديناميكي للمقاومات الكيميائية|
|**زمن الاستجابة الحركي ($t_a$)**|$\le 25\text{ ns}$|$\le 25\text{ ns}$|حماية الدوائر المتكاملة الحساسة لسرعة النبضة|
|**حالة الربط والتركيب (Status)**|مدمج قياسياً (Built-in)|مدمج قياسياً (Built-in)|مطابقة معمارية العاكس الذكي المعتمد|

_ارتباط تشغيلي حرج:_ إن تفعيل عمل مانعات الصواعق المدمجة مشروط بشكل قطعي بربط نقطة تأريض هيكل العاكس الخارجية (Chassis Grounding) بشبكة تأريض منخفضة المقاومة ($\le 5\ \Omega$)، وهو ما سيتم تفصيله وحسابه هندسياً في الفقرة اللاحقة الخاصة بتصميم شبكة التأريض والربط متساوي الكهروجهد.

### 10 - 20 - 2 تصميم شبكة التأريض والربط متساوي الكهروجهد (Earthing System & Equipotential Bonding)

تُمثل منظومة التأريض والربط متساوي الكهروجهد الركيزة الأمنية والتشغيلية الجوهرية في الجانبين المستمر والمتردد للمنظومة الكهروضوئية. ولا تقتصر فلسفتها على تصريف تيارات الأعطال المفاجئة فحسب، بل تمتد لتشمل حماية المعدات الرأسمالية الثمينة من الانهيار المبكر، وتوفير بيئة تلامس آمنة للأفراد الصيانة وفقاً للمواصفات العالمية الصارمة **IEC 60364-7-712** (الخاصة بمتطلبات التمديدات الكهروضوئية) والمعيار **IEC 62305** لإدارة مخاطر الصواعق، والكود **IEEE 80** لتصميم الأرضي العملي.

#### أولاً: التأريض الإلزامي لهياكل التثبيت المعدنية والتحليل الهندسي لمكافحة ظاهرة الـ PID

تتعرض هياكل التثبيت المعدنية للألواح (المصنوعة من الألومنيوم المؤكسد Anodized Aluminum أو الحديد المغلون على الساخن Hot-Dip Galvanized Steel) لتراكم مستمر للشحنات الساكنة (Static Charges) الناتجة عن حركة الرياح والاحتكاك بالجسيمات الجوية. يؤدي غياب المسار الأرضي لتفريغ هذه الشحنات إلى نشوء فرق جهد مستمر (DC High Potential) مرتفع جداً بين الخلايا السيليكونية الداخلية النشطة والإطار المعدني الخارجي المحيط باللوح.

1. **آلية نشوء ظاهرة التحلل المتسارع للعزل (Potential Induced Degradation - PID):**
    
    تحت تأثير هذا الحقل الكهربائي الحرج المستمر، تنشأ تيارات تسريب ميكروية تدفع أيونات الصوديوم الموجبة ($Na^+$) الموجودة في الزجاج الأمامي للوح نحو سطح الخلايا السيليكونية. تتسبب هذه الأيونات المهاجرة في تدمير البنية البلورية للوصلات الثنائية (P-N Junctions) وخفض عازلية الخلايا، مما يؤدي إلى هبوط حاد في كفاءة الألواح وتدني استطاعتها بمعدلات قد تتجاوز 30% خلال فترات تشغيلية قصيرة.
    
    لحماية ألواح المنظومة من طراز **LR5-72HTH-600M** من هذا الانهيار، يفرض التصميم ربطاً فيزيائياً ميكانيكياً متيناً ومستمراً لجميع الإطارات المعدنية للألواح وسكك التثبيت بشبكة التأريض الكلية. يضمن هذا الإجراء جعل جهد كافة الأجزاء المعدنية المحيطة مساوياً لجهد الأرض (صفر فولت مطلق)، مما يحيد الحقل الكهربائي المسبب لهجرة الأيونات.
    
    ويتكامل هذا التصميم الوقائي مع ميزة التعافي النشط المدمجة في العاكس المعتمد **Huawei SUN2000-25KTL-M5** (**Integrated PID Recovery**)، والتي تعتمد على خط التأريض كمرجع تشغيلي أساسي لتسليط جهد عكسي ليلاً لإعادة الأيونات المهاجرة وتجديد كفاءة العزل تلقائياً.
    
2. **التوصيف الفني ونواقل ربط الهياكل:**
    
    - **نوع الموصل:** يتم استخدام موصلات نحاسية مجدولة معزولة بـ PVC مقاوم للأشعة فوق البنفسجية طراز **Cu/PVC (أخضر/أصفر)** أو موصلات نحاسية عارية (**Bare Copper Conductors**).
        
    - **تحجيم المقطع العرضي ($A_{bonding}$):** استناداً للمعيار **IEC 60364-7-712**، وبما أن المحطة تحتوي على حماية خارجية من الصواعق، يجب ألا يقل المقطع العرضي لناقل الربط الرئيسي متساوي الجهد عن **$16\text{ mm}^2$** من النحاس لضمان تحمل الإجهادات الحرارية والميكانيكية الناتجة عن التيارات النبضية العالية. أما بالنسبة للروابط البينية الموضعية بين السكك المتجاورة (Jumper Cables)، فيتم اعتماد مقطع **$6\text{ mm}^2$** أو **$10\text{ mm}^2$**.
        
    - **معالجة عازلية الألومنيوم:** نظراً لأن طبقة الأكسدة السطحية للألومنيوم المؤكسد تُعد عازلاً كهربائياً، يلزم التصميم استخدام كليبات تأريض وغسالات مسننة خاصة (**Serrated Grounding Washers / Clips**) مصنوعة من الفولاذ المقاوم للصدأ عند نقاط التثبيت، بحيث تخترق أسنانها الحادة طبقة الأكسدة ميكانيكياً عند إحكام الربط، لضمان استمرارية كهربائية كاملة (Electrical Continuity) بمقاومة تلامس تؤول إلى الصفر ($\le 0.1\ \Omega$).

#### ثانياً: توصيف مسارات شبكة التأريض لإطار العاكس ولوحات التوزيع

لضمان سحب تيارات الأعطال وحماية الأفراد من مخاطر جهود التلامس الخطرة (Contact Voltages)، تم تصميم مسارات شبكة التأريض للمكونات الحيوية وفق نظام تأريض محمي هندسياً يعتمد على مبدأ التكرارية الأمنية (Redundant Earthing Path):

1. **تأريض جسم العاكس (Inverter Chassis Grounding):**
    
    تنتج الدوائر الإلكترونية عالية التردد وأشباه الموصلات (IGBT Bridges) العاملة بتقنية تعديل عرض النبضة (**PWM**) داخل عاكس هواوي تيارات تسريب سعوية طفيلية (**Capacitive Leakage Currents**) تتدفق نحو جسمه المعدني الخارجي. لتأمين تصريف هذه التيارات، يخضع العاكس لمساري تأريض مستقلين:
    
    - **المسار الأول (الأرضي التشغيلي المدمج):** يتم توصيل طرف PE الخاص بكابل مخرج الـ AC الرئيسي (بمقطع **$16\text{ mm}^2$** نحاس) مباشرة بالمنفذ المخصص له داخل علبة التوصيل المحمية للعاكس.
        
    - **المسار الثاني (الأرضي الوقائي للهيكل):** امتثالاً للمعيار الدولي **IEC 62109-1**، يتم تأريض البرغي الخارجي المثبت على الهيكل المعدني للعاكس (Chassis Earthing Terminal) بواسطة ناقل نحاسي مستقل معزول بمقطع **$16\text{ mm}^2$**، ويتوجه مباشرة إلى **لوحة التأريض الرئيسية (Main Earthing Busbar - MEB)**. يعتمد العاكس الذكي على هذا الخط كمرجع حاسم لإجراء فحص مقاومة العزل للحقل الشمسي (**Isolation Resistance Monitoring**) قبل الإقلاع اليومي؛ وفي حال رصد أي خلل أو ضعف في اتصال هذا المسار، يرفض العاكس ربط المنظومة بالشبكة ويطلق إنذار عطل أرضي (**Ground Fault**)، منعاً لظهور جهود تلامس قاتلة على غلافه.
        
2. **تأريض لوحات التوزيع (Distribution Boards Earthing):**
    
    يتم ربط الهياكل المعدنية وأبواب لوحة تجميع التيار المستمر (DC Combiner Box) ولوحة التوزيع المترددة الرئيسية (ACDB) بجسر تأريض داخلي نحاسي مستقل باستخدام كابلات نحاسية معزولة **Cu/PVC** بمقطع **$16\text{ mm}^2$**. تُجمع خطوط التأريض القادمة من أجهزة الحماية ضد الجهود العابرة (SPDs) وقواطع الدورة وتربط جميعها عبر نواقل رئيسية متوجهة إلى منظومة أقطاب الأرضي الكلية.

#### ثالثاً: التحليل الرياضي والهندسي لتصميم شبكة أقطاب التأريض (Earth Electrode System Layout)

لتحقيق الهدف الأكاديمي والتنظيمي الصارم الذي يفرض ألا تتجاوز المقاومة الكلية لشبكة التأريض **5 أوم ($R_e < 5\ \Omega$)** لضمان سرعة استجابة وسائط الفصل الآلي، تم اعتماد تصميم هندسي يتكون من قضبان فولاذية ملبسة بالنحاس (Copper-Bonded Steel Rods) مدفونة عمودياً في التربة المحيطة بالموقع الإنشائي.

1. **النمذجة الرياضية لمقاومة قضيب التأريض المفرد (Dwight's Formula):**
    
    تُحسب المقاومة الأومية لقضيب تأريض عمودي مفرد مغروس في تربة متجانسة بالاعتماد على معادلة "دوايت" الفيزيائية القياسية:
    
    $$R_1 = \frac{\rho}{2\pi L} \left[ \ln\left(\frac{4L}{d}\right) - 1 \right]$$
    
    حيث المحددات الهندسية المختارة للمشروع هي:
    
    - $\rho$: المقاومية النوعية للتربة بالموقع، وبفرض قيمة نموذجية لتربة طينية/مزيجية متوسطة الرطوبة قدرها $\rho = 100\ \Omega\cdot\text{m}$.
        
    - $L$: الطول الفيزيائي الفعال لقضيب التأريض، وتم اعتماد قضبان قياسية بطول $L = 2.5\text{ m}$.
        
    - $d$: القطر الخارجي لقضيب التأريض، وتم اعتماد قطر هندسي قياسي $d = 16\text{ mm} = 0.016\text{ m}$.

    _تطبيق الحساب العددي للقطب المفرد:_
    
    نحسب أولاً النسبة الهندسية للأبعاد داخل اللوغاريتم:
    
    $$\frac{4L}{d} = \frac{4 \times 2.5}{0.016} = 625$$
    
    بإيجاد اللوغاريتم الطبيعي للناتج:
    
    $$\ln(625) \approx 6.4378$$
    
    بالتعويض المباشر في صيغة دوايت:
    
    $$R_1 = \frac{100}{2 \times \pi \times 2.5} \times [6.4378 - 1]$$
    
    $$R_1 = \frac{100}{15.708} \times 5.4378 \approx 6.366 \times 5.4378 \approx 34.61\ \Omega$$
    
2. **حساب عدد القضبان المطلوبة للتوصيل على التوازي ومقاومة الحقل الإجمالية:**
    
    نظراً لأن مقاومة القطب الواحد ($34.61\ \Omega$) تتجاوز الحد المسموح، يتم ربط عدة قضبان على التوازي بمسافات بينية متباعدة تساوي ضعف طول القضيب على الأقل ($S = 2L = 5\text{ m}$) لتفادي تداخل مخاريط الجهد (Voltage Cones) في التربة. تُحسب مقاومة الحقل الإجمالية ($R_{total}$) بالعلاقة:
    
    $$R_{total} = \frac{R_1}{N} \times \eta$$
    
    حيث:
    
    - $N$: عدد القضبان المربوطة توازياً.
        
    - $\eta$: معامل التداخل الرياضي بين الأقطاب (Combining Factor)، ويؤخذ للتوزيع الخطي المتباعد بقيمة هندسية $\eta = 1.15$.

    لتأمين هامش أمان تشغيلي مريح، يستهدف التصميم الوصول إلى مقاومة كلية $R_{total} \le 4\ \Omega$ (أقل من الحد الأكاديمي الأعلى 5 أوم):
    
    $$4 = \frac{34.61}{N} \times 1.15 \implies N = \frac{34.61 \times 1.15}{4} \approx 9.95$$
    
    _القرار التصميمي المعتمد:_
    
    يتم تقريب الناتج إلى الرقم الصحيح الأعلى؛ وبناءً عليه، تتكون شبكة التأريض من **$10$ قضبان تأريض عمودية**، تُغرس على مسافات بينية لا تقل عن $5\text{ m}$، ويتم تجميعها وربطها تحت مستوى الأرض (على عمق $0.8\text{ m}$ من السطح لمنع التأثر بالجفاف الحراري) بواسطة ناقل نحاسي عارٍ (**Bare Copper Cable**) بمقطع عرضي قدره **$50\text{ mm}^2$**، مما يضمن خفض المقاومة الفعالة الكلية الكهروضوئية للحقل إلى **$3.98\ \Omega$**، وهو ما يحقق امتثالاً مطلقاً للمعايير الهندسية.

#### رابعاً: الجدول التلخيصي والمواصفات الفنية لمنظومة التأريض والربط متساوي الجهد

يلخص الجدول التالي كافة العناصر والمكونات التي تم حسابها وتوصيفها لشبكة تأريض المحطة:

|**البند الفني وعنصر الشبكة**|**التوصيف والمقطع العرضي المعتمد**|**المرجعية والمعيار الدولي**|**الوظيفة الحمائية والتشغيلية المستهدفة**|
|---|---|---|---|
|**ناقل ربط إطارات الألواح والسكتين**|سلك نحاسي عارٍ أو Cu/PVC بمقطع $16\text{ mm}^2$|IEC 60364-7-712|تفريغ الشحنات الساكنة وتحييد الحقل الكهربائي لمكافحة الـ PID|
|**وسائط تلامس الألومنيوم المؤكسد**|غسالات مسننة وكليبسات واختراق الفولاذ (Serrated Clips)|معايير الاستمرارية الكهربائية|اختراق طبقة الأكسدة السطحية وضمان مقاومة تلامس $\le 0.1\ \Omega$|
|**ناقل تأريض غلاف العاكس الخارجي**|كابل نحاسي معزول Cu/PVC بمقطع $16\text{ mm}^2$|IEC 62109-1 / Huawei Datasheet|تصريف تيارات التسريب السعوية PWM وتفعيل نظام الـ Isolation Monitor|
|**نواقل تأريض لوحات الـ AC والـ DC**|كابلات نحاسية معزولة Cu/PVC بمقطع $16\text{ mm}^2$|كود التصميم للوحات الكهربائية|تأمين مسار منخفض المقاومة لإجبار أجهزة الحماية على الفصل الفوري|
|**قضبان حقل التأريض الرئيسي**|10 قضبان فولاذية ملبسة بالنحاس (طول $2.5\text{ m}$ / قطر $16\text{ mm}$)|Dwight's Formula|التصريف النهائي والآمن لتيارات القصر العالية وصدمات الصواعق للتربة|
|**ناقل الربط الأفقي بين الأقطاب**|كابل نحاسي عارٍ بمقطع $50\text{ mm}^2$ مدفون عمق $0.8\text{ m}$|IEEE 80|تجميع الأقطاب المتوازية وضمان توزيع متساوي للكهروجهد (Equipotential)|
