MAQattan/My-Graduation-Project/GP_Obsidian/Thesis/10/10 - 21 المخطط أحادي الخط (Single Line Diagram).md

يُعد المخطط أحادي الخط (Single Line Diagram) الوثيقة المرجعية الأولى لمهندسي التنفيذ والصيانة، حيث يلخص البنية الكهربائية وترابط المكونات للمنظومة؛ من نقطة التوليد الكهروضوئي وصولاً إلى نقطة الربط بشركة توزيع الكهرباء. ويتتبع التصميم التخطيطي المسارات الكهروضوئية كالآتي:

1. **جانب التيار المستمر (DC Side Configuration):**
    
    - **مصفوفة الألواح:** يتضح من المخطط توزيع الـ 39 لوحاً شمسياً (من طراز $LR5-72HTH-600M$) على 3 سلاسل كهربائية مستقلة (Strings)، بحيث تحتوي كل سلسلة على 13 لوحاً موصولة على التوالي.
        
    - **صندوق الحماية والتجميع (DC String Protection):** يتم تمديد الطاقة عبر كابلات طاقة شمسية نحاسية مرنة مقاومة للأشعة فوق البنفسجية بمقطع $1 \times 4 \text{ mm}^2$ باللونين الأحمر والموجب. تمر كل سلسلة عبر مصاهر حماية تيار مستمر (DC Fuses) من الفئة التشغيلية $gPV$ بسعة اسمية تبلغ $25 \text{ A}$ وجهد اسمي $1000 \text{ V DC}$ لحماية الخلايا من تيارات القصر الراجعة.
        
    - **التوزيع على متعقبات القدرة (MPPT Mapping):** يُظهر المخطط ربط السلسلتين (String 1 & String 2) على التوازي قبل الدخول إلى المتعقب الأول ($MPPT\ 1$) للعاكس، في حين تدخل السلسلة الثالثة ($String\ 3$) بشكل منفصل ومستقل تماماً إلى المتعقب الثاني ($MPPT\ 2$) لحصر تأثير ظلال العوائق الإنشائية الشرقية.
        
    - **العزل والحماية من الصواعق:** يتضمن المخطط قواطع الفصل الميكانيكي المستمر ($DC\ Isolators$) المدمجة في العاكس لكل متعقب، تليها منظومة حماية مدمجة ضد خطوط الجهد العابر ناتجة الصواعق غير المباشرة عبر مانعات جهد من الصنف الثاني ($Type\ 2\ DC\ SPD$).
        
2. **العاكس الشمسي الذكي (Smart Inverter Stage):**
    
    - يُمثّل العاكس ($Huawei\ SUN2000-25KTL-M5$) قلب المنظومة، حيث يستقبل قدرة التيار المستمر المتغيرة ويقوم بتحويلها ومعالجتها بذكاء إلى طاقة مترددة متزنة ($Balanced\ 3\text{-Phase\ AC}$) عند جهد شبكة اسمي $400 \text{ V}$ وتردد $50 \text{ Hz}$.
        
3. **جانب التيار المتردد والربط بالشبكة (AC Side Configuration):**
    
    - **كابل الطاقة الرئيسي:** يخرج التيار المتردد الأقصى للعاكس والبالغ تشغيلياً $38 \text{ A}$ عبر كابل نحاسي متعدد النوى معزول بمادة الـ XLPE ومغلف بـ PVC من إنتاج شركة السويدي للكابلات بمقطع مقنن يبلغ $4 \times 10 \text{ mm}^2$.
        
    - **لوحة الحماية المترددة (ACDB):** يتجه الكابل مباشرة إلى لوحة توزيع الحماية المترددة، حيث يربط بقاطع حماية رئيسي حراري مغناطيسي ($MCB/MCCB$) رباعي الأقطاب ($4\text{-Pole}$) بسعة مقننة تبلغ $50 \text{ A}$ وسعة قطع صمود ضد التيارات اللحظية. كما تشتمل اللوحة على مانع الصواعق المتردد المدمج بالعاكس ($Type\ 2\ AC\ SPD$) لتأمين الكروت الإلكترونية من تشوهات الشبكة والجهود العابرة.
        
4. **شبكة التأريض والربط متساوي الكهروجهد (Earthing Systems):**
    
    - يوضح المخطط خطوط التأريض الوقائي والتشغيلي، حيث ترتبط هياكل الألواح المعدنية (الألومنيوم) وإطار العاكس وجسم لوحة التوزيع عبر نواقل نحاسية مجدولة إلى بئر تأريض مشترك لضمان تفريغ الشحنات الساكنة وتحقيق مقاومة أرضية كلية منخفضة للغاية ($\le 5\ \Omega$).

![[SLD.pdf]]
