MAQattan/My-Graduation-Project/GP_Obsidian/Thesis/11/الخلاصة والاستنتاجات.md

اختتمت هذه الدراسة مرحلة التحقق الرقمي لمنظومة "بنك حلب" الكهروضوئية بقدرة **23.40 kWp**، حيث أثبتت المحاكاة عبر برنامج **PVsyst** أن المنهجية التصميمية المتبعة في "الفصل العاشر" قد حققت توازناً استثنائياً بين كفاءة المكونات وهندسة الموقع. وتتلخص أهم الاستنتاجات الفنية التي تربط قوة التصميم بنتائج الأداء فيما يلي:

1. **عبقرية التوجيه ودقة المورد الإشعاعي:** أثبتت نتائج المحاكاة أن اعتماد **زاوية ميل 31°** (المستنتجة من المعادلات الرياضية الدقيقة في الفصل الثامن والعاشر) قد نجح في رفع الإشعاع المائل الكلي (GTI) إلى **2184.8 kWh/m²**، مما أدى مباشرة لتحقيق إنتاجية نوعية مرتفعة جداً بلغت **1881 kWh/kWp/year**، متجاوزة بذلك متوسط الإنتاجية التقليدية في المنطقة.
2. **كفاءة التحجيم الكهربائي وتقليص المفاقيد:** يعود الفضل في تحقيق **معامل أداء (PR) قياسي بنسبة 89.3%** إلى الدقة في اختيار مقاطع الكابلات ($16mm^2$ للجانب المتردد و$4mm^2$ للجانب المستمر)؛ حيث نجح هذا التصميم في حصر المفاقيد الأومية عند **$-0.73\%$** فقط، وهو ما يطابق حسابات "هبوط الجهد" التي أجريت يدوياً والتي لم تتجاوز عتبة الـ $1\%$.
3. **نجاح تقنية "التثبيت المتدرج" (Tiered Structure):** أكدت المحاكاة نجاح الابتكار الميكانيكي المقترح في الفصل العاشر؛ فبالرغم من ضيق مساحة سطح البنك، أتاح "التثبيت المتدرج" بلوغ **كثافة استطاعة $119.59 W/m²$** مع تحييد كامل للمفاقيد البصرية الناتجة عن التظليل المتبادل بين الصفوف (Row-to-Row Shading)، مما جعل المسافة البينية (Pitch) فعلياً تساوي صفراً دون التأثير على الأداء.
4. **المواءمة الذكية مع العاكس (Multi-MPPT Strategy):** أظهر مخطط الفواقد أن توزيع السالسل على متعقبات القدرة المستقلة قد حد من مفاقيد "عدم التطابق" (Mismatch Loss) عند $**-2.10\%**$ فقط؛ مما يثبت صحة قرار "التوزيع الفعال" الذي اعتزل السلسلة المتأثرة بظل غرفة الدرج والوحدة التكييفية وحيد تأثيرها عن باقي المصفوفة.
5. **الصمود الحراري وجودة الخلايا:** يثبت انخفاض المفاقيد الحرارية عند **$-4.64\%$** جدارة اختيار ألواح **LONGi Hi-MO 6** ذات المعامل الحراري المنخفض، وقدرتها على استدامة الإنتاج في مناخ حلب الحار صيفاً دون انهيار الجهد التشغيلي.

>بناءً على هذا الربط التحليلي، نؤكد أن منظومة "بنك حلب" المصممة تمثل نموذجاً هندسياً فائق الجودة، يجمع بين الاستغلال الأمثل للمساحة والحد الأدنى من الضياعات التقنية، مما يضمن للمنشأة المصرفية استقلالاً طاقياً وموثوقية تشغيلية كاملة طوال العمر الافتراضي للمشروع.
