MAQattan/My-Graduation-Project/GP_Obsidian/Thesis/11/الفصل الحادي عشر - محاكاة وتحليل أداء المنظومة عبر برنامج PVsyst.md

## [[هيكلية فقرات فصل محاكاة وتحليل أداء المنظومة عبر برنامج PVsyst]] 
---
## [[المقدمة]] 

## [[مدخلات المنظومة وإعدادات المحاكاة]]  
## [[تحليل النتائج الرئيسية للمحاكاة]] 
## [[مخطط فواقد الطاقة للمنظومة]] 
## [[الخلاصة والاستنتاجات]]
