MAQattan/My-Graduation-Project/GP_Obsidian/Thesis/11/المقدمة.md

تمثل المحاكاة الحاسوبية المرحلة الجوهرية للتحقق من دقة التصميم الهندسي والجدوى التشغيلية للمنظومة الكهروضوئية المخطط تركيبها. فبعد استكمال الحسابات اليدوية لاختيار مكونات الجانب المستمر (DC) والمتردد (AC)، يبرز دور برنامج **PVsyst** كأداة هندسية معيارية تتيح نمذجة السلوك الفيزيائي للمنظومة تحت وطأة الظروف المناخية المتغيرة والمحدودية المكانية للموقع.

تستند فلسفة هذا الفصل إلى بناء توأم رقمي (Digital Twin) للمنظومة بقدرة **25kW**، مع مواءمة المواصفات الفنية للألواح المختارة (**Longi 600W**) والعاكس الذكي (**Huawei SUN2000**) مع قاعدة بيانات البرنامج المعتمدة من الشركات المصنعة. تهدف هذه الدراسة التحليلية إلى تجاوز التقديرات الثابتة للوصول إلى تنبؤات ديناميكية دقيقة لإجمالي الطاقة السنوية المنتجة ($E_{sys}$)، مع تحليل معمق لكافة مفاقيد النظام الحرارية والكهربائية والبصرية.

سيركز هذا الفصل على استعراض مدخلات المحاكاة الجغرافية والهندسية، وتحليل مؤشرات الأداء الحاكمة مثل **معامل الأداء (Performance Ratio - PR)** و**الإنتاجية النوعية (Specific Yield)**، وصولاً إلى فك شفرة **مخطط تدفق المفاقيد (Loss Diagram)** الذي يوضح ميزان الطاقة المفقودة منذ لحظة سقوط الإشعاع الشمسي وحتى ضخ القدرة في لوحة التوزيع الرئيسية للمصرف. إن هذا التحقق الرقمي هو الضمانة التقنية لضمان استقرار تغذية الأحمال المصرفية الحيوية وتحقيق أعلى عائد على الاستثمار طوال العمر الافتراضي للمنظومة.
