MAQattan/My-Graduation-Project/GP_Obsidian/Thesis/11/تحليل النتائج الرئيسية للمحاكاة.md

### الإنتاجية الطاقية السنوية (Annual Energy Production)

تُعد الطاقة السنوية المحقونة في الشبكة ($E_{Grid}$) المتغير الكمي المحوري الذي يترجم نجاح التصميم الهندسي لمنظومة البنك البالغة استطاعتها الذروية $23.40 \text{ kWp}$. وبناءً على نتائج المحاكاة الرقمية المحدثة، تبين أن المنظومة قادرة على توريد إجمالي طاقة كهربائية صافية للشبكة والمبنى المصرفي تقدر بـ **$44.02 \text{ MWh/year}$**.

وعند تحليل المنحنى الإنتاجي الشهري، يظهر التقرير تبايناً طردياً متوافقاً مع تغير المورد الإشعاعي في مدينة حلب؛ حيث سجلت المنظومة ذروة ضخ القدرة في شهر يوليو (تموز) بقيمة **$4.604 \text{ MWh}$**، تلاه شهر أغسطس بقيمة **$4.542 \text{ MWh}$**. وفي المقابل، تنحدر الإنتاجية إلى مستوياتها الدنيا خلال فصل الشتاء لتسجل أقل قيمة في شهر فبراير (شباط) بواقع **$2.521 \text{ MWh}$**.

يعزى هذا السلوك الإنتاجي فيزيائياً إلى وصول الإشعاع الساقط على مستوى المصفوفة ($GlobInc$) إلى ذروته السنوية في شهر يوليو بمعدل $229.4 \text{ kWh/m²}$، مما سمح للعاكس الذكي بتوليد أقصى تيار متردد متاح، بالرغم من الارتفاع النسبي في فواقد حرارة الخلايا ($Thermal Loss$) التي يتميز اللوح المختار (**Longi 600W**) بمقاومتها بفعالية عبر معامل حراري منخفض.

![[PV-11-04.png]]
>وصف الصورة (caption): جدول البيانات الشهرية يوضح ميزان الطاقة التفصيلي، ويبرز قيمة الطاقة السنوية الكلية المحقونة في الشبكة $E_Grid$ المقدرة بـ 44.02 ميجاواط ساعي).

### عامل الأداء للمنظومة (Performance Ratio - PR)

يُعتبر معامل الأداء ($PR$) المعيار العالمي لتقييم "جودة جدارة" المنظومة الكهروضوئية، حيث يعبر عن النسبة المئوية للطاقة التي تم استخلاصها فعلياً وحقنها في الشبكة ($E_{Grid}$) مقارنة بالطاقة المثالية التي كان يمكن إنتاجها لو عملت الألواح بكفاءتها القصوى تحت الإشعاع المتاح دون أي فواقد تقنية. ووفقاً لتقرير المحاكاة المحدث، حققت المنظومة معامل أداء سنوي مرتفع جداً قدره **$89.30\%$**، وهي قيمة تتجاوز النطاق التقليدي للمشاريع النمطية (الذي يتراوح عادة بين 75% و85%)، مما يوثق الجودة العالية للمكونات المختارة ودقة التحجيم الكهربائي.

ويمكن تفكيلك هذا المؤشر وتحليله هندسياً من خلال محورين أساسيين:

#### أولاً: التحليل الديناميكي الموسمي للـ PR

تُظهر نتائج المحاكاة تبايناً فيزيائياً منطقياً في قيم $PR$ على مدار العام؛ حيث سجلت المنظومة أعلى كفاءة أداء في شهر يناير (كانون الثاني) بنسبة **$94.8\%$**، بينما انخفضت تدريجياً لتصل إلى أدنى مستوياتها في شهر يوليو (تموز) بنسبة **$85.8\%$**. ويعزى هذا السلوك الميداني إلى التأثير العكسي لدرجة الحرارة على جهد الخلايا؛ فبالرغم من وصول الإشعاع لذروته صيفاً، إلا أن ارتفاع درجة الحرارة المحيطة في مدينة حلب (المقدرة بـ $30.62^{\circ}\text{C}$ في يوليو) يؤدي إلى زيادة المفاقيد الحرارية للألواح، في حين تساهم برودة الطقس شتاءً في رفع جهد الدارة، مما يقرب المنظومة من كفاءتها المثالية.

#### ثانياً: المكونات الفنية المساهمة في استقرار PR

إن الحفاظ على متوسط PR يقترب من $90\%$ يعكس نجاحاً في إدارة أربعة أنواع رئيسية من الفواقد التي تم توصيفها في التصميم:

1. **كفاءة التحويل (Inverter Efficiency):** ساهم العاكس الذكي (**Huawei 25kW**) في الحفاظ على هذا المعامل المرتفع بفضل فواقد تحويل ضئيلة جداً بلغت **$-1.72\%$** فقط، نظراً لتوافقه مع استطاعة المصفوفة.
2. **الفواقد الأومية (Ohmic Wiring Losses):** نجح التصميم في تقليص مفاقيد الكابلات إلى **$-0.73\%$** فقط، وهو ما يثبت صحة اختيار مقاطع الكابلات ($16 mm^2$ للجانب المتردد و$4mm^2$ للجانب المستمر) التي حالت دون ضياع القدرة في صورة حرارة.
3. **فواقد عدم التطابق (Mismatch Losses):** بفضل استخدام عاكس متعدد المداخل (Multi-MPPT)، تم حصر مفاقيد عدم تطابق السلاسل عند نسبة **$-2.10\%$**، مما حمى PR الإجمالي من الانهيار في حال حدوث ظلال جزئية.

![[PV-11-05.png]]

> وصف الصورة (caption): مخطط بياني يوضح التوزيع الشهري لمعامل الأداء، ويظهر بوضوح ثبات المنظومة فوق حاجز الـ 85% طوال العام بفضل التصميم الهندسي الرصين).

### الإنتاجية النوعية للمنظومة (Specific Production)

تُعد **الإنتاجية النوعية ($Specific Yield$)** المعيار الهندسي الموحد لتقييم جدارة النظام الكهروضوئي بمعزل عن حجمه، حيث تُمثل حاصل قسمة إجمالي الطاقة السنوية الصافية المحقونة في الشبكة ($E_{Grid}$) على الاستطاعة الذروية المركبة للمصفوفة ($P_{nom}$). وتعكس هذه القيمة "الساعات التشغيلية المكافئة" التي عملت فيها المنظومة بكامل طاقتها القصوى تحت المورد الشمسي المتاح في موقع بنك حلب.

![[PV-11-06.png]]
> وصف الصورة (caption): ملخص نتائج المحاكاة يبرز قيمة الإنتاجية النوعية للمنظومة كمعيار للأداء الطاقي السنوي ومطابقتها لمعدل ساعات الذروة ومعامل الأداء.

ووفقاً لنتائج المحاكاة المحدثة في تقرير **PVsyst**، سجلت المنظومة إنتاجية نوعية استثنائية بلغت **$1881 \text{ kWh/kWp/year}$**. ويمكن استقراء هذا الرقم وتحليله هندسياً من خلال المحاور التقنية التالية:

#### أولاً: الارتباط بالموارد الإشعاعية ومعامل الأداء

ترتبط الإنتاجية النوعية مباشرة بعدد ساعات الذروة الشمسية ($PSH$) المتوفرة في الموقع؛ فبالرجوع للبيانات المناخية في التقرير، نجد أن الإشعاع الساقط على مستوى المصفوفة ($GTI$) بلغ $2106.4 \text{ kWh/m²}$ سنوياً، وهو ما يعادل $2106.4$ ساعة ذروة شمسية. إن وصول الإنتاجية النوعية إلى $1881$ هو نتيجة فيزيائية مباشرة للحفاظ على معامل أداء ($PR$) مرتفع بنسبة $89.3\%$، حيث تتحقق العلاقة الرياضية بدقة: 
$$Specific Yield = PSH_{tilted} \times PR$$
$$1881 \approx 2106.4 \times 0.893$$
وهذا يوثق نجاح التصميم في تقليص المفاقيد التقنية إلى أدنى مستوياتها الممكنة.

#### ثانياً: أثر التوجيه الهندسي والمكاني

يكشف التحليل أن اختيار زاوية الميل المثالية ($31^{\circ}$) وتوجيه المصفوفة نحو الجنوب تماماً ($0^{\circ}$) ساهما في رفع الإنتاجية النوعية بنسبة تقارب $13\%$ مقارنة بالوضع الأفقي. فبينما يبلغ متوسط ساعات الذروة الأفقية في حلب $4.74 \text{ h/day}$، نجح التصميم في رفعها إلى متوسط سنوي قدره **$5.98 \text{ h/day}$**، مما أدى إلى تعظيم كثافة الفوتونات المستخلصة لكل كيلوواط مركب.

#### ثالثاً: الجدوى الطاقية والاستثمارية للمصرف

من منظور اقتصادي، تُعد قيمة $1881 \text{ kWh/kWp}$ مؤشراً قوياً على قصر فترة استرداد رأس المال (Payback Period)؛ إذ إن كل كيلوواط ذروة يتم تركيبه فوق السطح سينتج فعلياً قرابة الـ $1.9 \text{ MWh}$ سنوياً. هذا المردود المرتفع يؤكد أن اختيار الألواح عالية الكفاءة (**Longi 600W**) وتوافقها مع العاكس الذكي، بالإضافة إلى التوزيع الاحترافي للألواح قد حقق "الاستغلال الأعظمي للمساحة" (LUF)، موفراً أعلى كثافة طاقية ممكنة ($119.59 \text{ W/m²}$) في ظل القيود المساحية لسطح البنك.

### الإنتاجية المعايرة والمفاقيد اليومية (Normalized Productions Analysis)

تتجلى القيمة التحليلية لبرنامج **PVsyst** في قدرته على تبسيط ميزان الطاقة عبر "معايرة" النتائج (Normalization)؛ أي نسب كافة قيم التوليد والضياعات إلى الكيلوواط الذروي الواحد من الاستطاعة المركبة ($23.40 \text{ kWp}$)، مما يسهل رصد الكفاءة التشغيلية اليومية للنظام.

![[PV-11-07.png]]
> وصف الصورة (caption): مخطط الإنتاجية المعايرة اليومية يوضح توزيع الطاقة المفيدة $Y_f$ مقابل مفاقيد المصفوفة $L_c$ ومفاقيد النظام $L_s$ لكل كيلوواط ذروة مركب).

واستناداً إلى المخطط البياني للإنتاجية المعايرة في تقرير المحاكاة، يمكن تفكيك أداء المنظومة إلى ثلاثة مكونات رئيسية:

1. **الإنتاجية المفيدة ($Y_f$):** تمثل صافي الطاقة التي نجح العاكس في حقنها بالشبكة وتغذية أحمال البنك، حيث سجلت المنظومة متوسطاً سنوياً متميزاً قدره **$5.15 \text{ kWh/kWp/day}$**. هندسياً، يعني هذا الرقم أن كل كيلوواط مركب فوق سطح البنك ساهم بإنتاج ما يزيد عن خمس ساعات تشغيل كاملة من الطاقة الصافية يومياً.
2. **مفاقيد المصفوفة ($L_c$):** تمثل الضياعات في الجانب المستمر ($DC$) قبل وصول الطاقة للعاكس (بسبب الحرارة، واتساخ الألواح، ومقاومة الكابلات)، وقد بلغت قيمتها **$0.52 \text{ kWh/kWp/day}$**. ويُعد هذا الرقم منخفضاً، مما يثبت نجاح منهجية "التثبيت المتدرج" التي اعتمدناها في التصميم لتقليل التظليل وزيادة التهوية.
3. **مفاقيد النظام ($L_s$):** وهي الضياعات الناتجة أثناء عملية التحويل داخل العاكس وفي كابلات الجانب المتردد ($AC$)، وقد سجلت قيمة ضئيلة جداً بلغت **$0.09 \text{ kWh/kWp/day}$**. وتؤكد هذه القيمة المحدودة جودة اختيار عاكس **Huawei** وتوافقه المثالي مع استطاعة المصفوفة.
