MAQattan/My-Graduation-Project/GP_Obsidian/Thesis/11/مخطط فواقد الطاقة للمنظومة.md

يُمثل مخطط المفاقيد (Sankey Diagram) الأداة الهندسية الأكثر دقة في تقييم جودة التصميم؛ حيث يتتبع التسلسل الهرمي لتحولات الطاقة ويحدد بدقة مكامن الضياع الفيزيائي والكهربائي. واستناداً إلى نتائج المحاكاة، نجحت المنظومة في الحفاظ على **89.3%** من طاقتها الإجمالية، بينما توزعت المفاقيد المتبقية وفق التحليل الفني التالي:

#### المفاقيد البصرية (IAM Losses)

سجلت المحاكاة فقدانًا بنسبة **$-1.70\%$** ناتجاً عن عامل تعديل الزاوية (IAM factor). فيزيائياً، يعود هذا الفقد إلى انعكاس جزء من الإشعاع الشمسي عن سطح الزجاج عندما تكون الشمس في زوايا سقوط مائلة (خاصة عند الشروق والغروب)، مما يمنع الفوتونات من النفاذ إلى خلايا السيليكون. وتُعد هذه النسبة منخفضة جداً بفضل اعتماد زاوية الميل المثالية ($31^{\circ}$) التي قللت من مفقودات الانعكاس السطحي.

![[PV-11-08.png]]
> وصف الصورة: مخطط تدفق المفاقيد السنوي يوضح الميزان الطاقي من الإشعاع الشمسي الخام وصولاً إلى الطاقة الصافية المحقونة في الشبكة وقدرها 44.02 MWh).

#### مفاقيد المصفوفة الداخلية (PV Array Internal Losses)

تُعد هذه المجموعة هي الأكثر تأثيراً على الجانب المستمر (DC)، وتتكون من ثلاثة عناصر رئيسية:

1. **المفاقيد الحرارية للألواح ($-4.64\%$):** وهي الفقد المهيمن تقنياً؛ حيث يؤدي ارتفاع حرارة الخلايا فوق $25^{\circ}\text{C}$ إلى خفض جهد الدارة المفتوحة ($V_{oc}$). وبالرغم من ذلك، تظل هذه النسبة ممتازة لمناخ مدينة حلب، مما يوثق كفاءة الألواح المختارة (**Longi 600W**) ذات المعامل الحراري المنخفض.
2. **مفاقيد عدم التطابق (Mismatch Loss -2.10%):** ناتجة عن التفاوت الطبيعي البسيط في منحنيات ($I-V$) بين الـ 39 لوحاً المكونة للمصفوفة. وقد ساهم استخدام عاكس بمتعقبات متعددة (Multi-MPPT) في تقليص هذا الفقد عبر عزل السلاسل المظللة جزئياً عن السلاسل المشمسة.
3. **المفاقيد الأومية في الكابلات (-0.73%):** تعبر عن الطاقة المبددة كحرارة ($I^2R$) في موصلات الجانب المستمر. وتثبت هذه القيمة الضئيلة نجاح التحجيم الهندسي للموصلات.

#### مفاقيد التحويل والنظام (System & Inverter Losses)

تحدث هذه المفاقيد عند انتقال الطاقة من الحالة المستمرة إلى المترددة (DC to AC):

- **كفاءة العاكس التشغيلية (-1.72%):** سجل عاكس **Huawei** أداءً استثنائياً؛ حيث لم تتجاوز مفقودات التحويل الحراري داخل جسور الترانزستورات ($IGBTs$) حاجز الـ 2%.
- **مفاقيد الاستهلاك الليلي (-0.06%):** وهي الطاقة الضئيلة التي يسحبها العاكس من الشبكة ليلاً لبقاء دوائر التحكم في وضع الاستعداد.
