MAQattan/My-Graduation-Project/GP_Obsidian/Thesis/11/مدخلات المنظومة وإعدادات المحاكاة.md

### تحديد الموقع الجغرافي وبيانات الأرصاد الجوية (Geographical Site & Meteorological Data):

تُمثل تهيئة الموقع الجغرافي الخطوة التأسيسية والمحورية في برنامج **PVsyst**؛ حيث ترتبط بها ديناميكياً كافة الحسابات اللاحقة المتعلقة بكثافة الإشعاع الشمسي وزوايا السقوط الفلكية. ونظراً لأن المنظومة الكهروضوئية المصممة تقع في **مدينة حلب - سوريا**، فقد تم إدخال الإحداثيات الجغرافية الدقيقة للموقع (خط العرض $37.2^{\circ}$ شمالاً، وخط الطول $37.1^{\circ}$ شرقاً) في واجهة إعدادات البرنامج.

وللحصول على قراءات مناخية موثوقة ومطابقة للواقع الفيزيائي للموقع، تم الاعتماد على قاعدة البيانات العالمية المدمجة **(Meteonorm 8.0)** لاستيراد وتوليد جداول الإشعاع الشمسي الكلي والانتشاري (Global & Diffuse Irradiance) بالإضافة إلى مخططات درجات الحرارة الساعية والشهرية على مدار العام، كما هو موثق في **الشكل ([X])** أدناه. تضمن هذه الخطوة دقة عالية في حساب معاملات الفواقد الحرارية للألواح والتنبؤ الدقيق بإنتاجية الطاقة الكلية المحقونة في الشبكة الكهربائية المصرفية.

![[PV-11-01.png]]
> وصف الصورة (caption): واجهة ضبط الإحداثيات الجغرافية لمدينة حلب واستيراد بيانات الطقس عبر Meteonorm 8.0 في برنامج PVsyst.

### توجيه وميل المصفوفة الكهروضوئية (PV Array Orientation):

لضمان تحقيق أعلى عائد طاقي سنوي ممكن ($Maximum\text{ }Yearly\text{ }Yield$) وتوافقاً مع المخطط الهندسي العام لسطح المبنى المصرفي في مدينة حلب، تم ضبط إعدادات توجيه المصفوفة الكهروضوئية في برنامج $PVsyst$ بناءً على المحددات التصميمية المعتمدة مسبقاً في دراسة المشروع. تَم اعتماد هندسة التثبيت من النمط الثابت ذو الميل المفرد ($Fixed\text{ }Tilted\text{ }Plane$) بزاوية ميل ثابتة ومثالية مقدارها ($\beta = 31^{\circ}$)، مع توجيه الألواح نحو الجنوب الجغرافي تماماً لتكون زاوية السمت صفرية ($Azimuth = 0^{\circ}$).

وقد أظهرت أداة التحسين السريع للإنتاجية السنوية ($Quick\text{ }Optimization$) ضمن البرنامج أن هذه الزاوية تعطي الاستغلال الأمثل الممكن للإشعاع الشمسي الساقط على مدار العام في الموقع الجغرافي المختار، حيث تؤول نسبة المفقودات الناتجة عن الانحراف عن الزاوية النظرية المطلقة إلى الصفر ($0.0\%$)، مما يؤكد الرصانة العلمية للقيم التصميمية الميكانيكية للمنظومة. ويُبين الشكل ($X-X$) التوصيف الرقمي والمنحنى البياني لهذه الإعدادات بعد تحديثها في واجهة البرنامج.

![[PV-11-02.png]]

> وصف الصورة (caption): واجهة ضبط وتأكيد معطيات توجيه وزاوية ميل المصفوفة الكهروضوئية ($\beta = 31^{\circ}$) في برنامج $PVsyst$.

### التوصيف الفني المنظومة الكهروضوئية:

بناءً على الحسابات الهندسية والمعايير الفنية المعتمدة في دراسة المشروع النظريّة، تم إسقاط وتوصيف المكونات الكهربائية الأساسية للمحطة داخل بيئة برنامج $PVsyst$ لضمان محاكاة فيزيائية دقيقة ومطابقة للواقع العلمي. يشتمل هذا الجزء على تحديد النماذج الرياضية للألواح والعواكس وتوزيع السلاسل الكهربائية كما يلي:

**أ) المصفوفة الكهروضوئية (PV Array):**

تم اختيار الألواح الشمسية أحادية البلورة عالية الكفاءة بتكنولوجيا الـ $TOPCon$ من إنتاج شركة **LONGi Solar** طراز **$LR5-72HTH-600M$** (من فئة _Hi-MO 6 Scientist_)، بقوة اسمية تبلغ $600\text{ Wp}$ للوح الواحد عند الشروط القياسية ($STC$). تتكون المنظومة الإجمالية من **39 لوحاً شمسياً**، مما يرفع الاستطاعة الذروية الإجمالية المستمرة للمحطة إلى ($P_{dc} = 23.4\text{ kWp}$).

**ب) العاكس الكهروضوئي (Grid-Tied Inverter):**

لتحويل الطاقة المستمرة وتأمين ربط متزامن وآمن مع شبكة التوزيع الكهربائية الداخلية للمبنى المصرفي في مدينة حلب، تم اعتماد عاكس ذكي ثلاثي الطور من إنتاج شركة **Huawei** طراز **$SUN2000-25KTL-M5$** باستطاعة اسمية متناوبة تبلغ ($P_{ac} = 25\text{ kW}$). تبلغ نسبة تحميل العاكس المعتمدة في هذا التصميم ($P_{dc}/P_{ac} = 0.936$)، وهي نسبة مثالية جداً تحمي العاكس من ظواهر كبح القدرة المستمرة ($Power\text{ }Clipping$) خلال فترات الذروة الإشعاعية الصيفية، فضلاً عن إتاحة هامش مرن لأي توسعة مستقبلية في مصفوفة الألواح دون الحاجة لتغيير البنية التحتية للعواكس.

**ج) طوبولوجيا الربط وتوزيع السلاسل الكهربائية (String Topology):**

نظراً لطبيعة التوزيع غير المتناظر للألواح على السطح ولتعظيم كفاءة تتبع نقطة الاستطاعة العظمى ($MPPT$)، تم تقسيم المنظومة كهربائياً داخل البرنامج إلى مصفوفتين فرعيتين ($Sub-arrays$) موزعتين على متعقبي العاكس المستقلين كالتالي:

- **المصفوفة الفرعية الأولى ($Sub-array\text{ }1$):** وتتصل بالمتعقب الأول ($\text{MPPT 1}$)، وتضم سلسلتين متوازيتين ($2\text{ Strings}$)، تحتوي كل سلسلة على 13 لوحاً متصلاً على التوالي (بمجموع 26 لوحاً واستطاعة قدرها $15.6\text{ kWp}$).
    
- **المصفوفة الفرعية الثانية ($Sub-array\text{ }2$):** وتتصل بالمتعقب الثاني ($\text{MPPT 2}$)، وتضم سلسلة واحدة منفردة ($1\text{ String}$) مكونة من 13 لوحاً متصلاً على التوالي (بمجموع 13 لوحاً واستطاعة قدرها $7.8\text{ kWp}$).

تضمن هذه الهندسة تشغيل السلاسل عند جهد تشغيلي اسمي يقارب ($V_{mp} \approx 580.6\text{ V}$) عند الشروط القياسية، وهو جهد يقع في النطاق السليم تماماً ويقترب من الجهد الاسمي المقنن للعاكس البالغ ($600\text{ V}$)، مما يتيح لوحدات التحكم الإلكترونية داخل العاكس بالعمل عند ذروة كفاءتها الموزونة وتقليص الضياعات الحرارية لأدنى حد. ويُبين الشكل ($X-X$) واجهة إدخال المكونات الفنية الكلية بعد ضبطها وتأكيد مطابقتها وتجاوزها لجميع شروط الفحص البرمجي بنجاح.

![[PV-11-03.png]]

> وصف الصورة (caption): واجهة تعريف المكونات الفنية الكهربائية وتوزيع السلاسل الكهربائية على متعقبات العاكس المستقلة في برنامج $PVsyst$.
