MAQattan/My-Graduation-Project/GP_Obsidian/Thesis/11/هيكلية فقرات فصل محاكاة وتحليل أداء المنظومة عبر برنامج PVsyst.md

### الهيكلية المقترحة | الفصل [X]: محاكاة وتحليل أداء المنظومة عبر برنامج PVsyst

#### **1. مقدمة الفصل**

- نبذة موجزة (سطرين إلى ثلاثة) تبين أهمية استخدام برمجيات المحاكاة الكهروضوئية للحصول على قراءات تنبؤية قريبة من الواقع الفيزيائي وتوثيق جدوى التصميم الهندسي للمصرف.
    
#### **2. مدخلات المنظومة وإعدادات المحاكاة (Simulation Inputs & Parameters)**

_تجميع البيانات التصميمية التي قمت بحسابها في الفصول السابقة وإدخالها للبرنامج:_

- **الموقع الجغرافي وبيانات الطقس (Geographical & Meteorological Data):** تحديد إحداثيات الموقع (خطوط الطول، دوائر العرض، والارتفاع) والاعتماد على قاعدة بيانات الطقس (مثل Meteonorm).
    
- **توجيه المصفوفة (Orientation):** زاوية السمت (Azimuth = $0^{\circ}$ نحو الجنوب) وزاوية الميل المثالية ($\beta$) المعتمدة للمشروع.
    
- **المكونات الفنية المتطابقة (System Configuration):** * مواصفات وعدد الألواح الشمسية المختارة وقدرتها الإجمالية ($P_{p}$).
    
    - مواصفات وقدرة العاكس المرتبط بالشبكة وطوبولوجيا الربط المعتمدة (Multi-string أو غيرها).
        
#### **3. تحليل النتائج الرئيسية للمحاكاة (Key Simulation Results)**

_هنا نضع الجداول والمخططات المستخرجة من التقرير النهائي للبرنامج والتعليق الهندسي عليها:_

- **الإنتاجية الطاقية السنوية (Annual Energy Production):** إجمالي الطاقة الكهربائية المحقونة في الشبكة ($E_{Grid}$) مقدرة بـ (MWh/year).
    
- **عامل الأداء للمنظومة (Performance Ratio - PR):** استعراض قيمة الـ $PR$ السنوية للمنظومة والتعليق عليها أكاديمياً (وهي المؤشر الأساسي لكفاءة جودة التصميم، وعادة ما تتراوح بين $75\%$ إلى $85\%$).
    
- **الإنتاجية النوعية للمنظومة (Specific Production):** كمية الطاقة المولدة لكل كيلوواط ذروة مركّب ($\text{kWh/kWp/year}$).
    
#### **4. مخطط فواقد الطاقة للمنظومة (Sankey Loss Diagram)**

_أهم جزء يلتفت إليه دكاترة لجنة التحكيم في مناقشة مشاريع التخرج:_

- إدراج مخطط التدفق الفيزيائي للفواقد (Loss Diagram) من البرنامج.
    
- تحليل ومناقشة أهم الفواقد الواردة فيه بشكل موجز وسريع (مثل: المفاقيد الحرارية للألواح $Thermal Loss$، مفاقيد التوصيل والكابلات $Wiring Losses$، مفاقيد كفاءة العاكس $Inverter Efficiency$، ومفاقيد عدم التطابق $Mismatch$).
    
#### **5. الخلاصة والاستنتاجات**

- تقييم فني نهائي يؤكد ملاءمة نظام الطاقة الشمسية المصمم لتلبية أحمال البنك وحقن الفائض في الشبكة بأعلى كفاءة وأقل ضياعات ممكنة.
