MAQattan/My-Graduation-Project/GP_Obsidian/Thesis/3/1- طاقة الرياح (Wind Energy).md

تُعد **طاقة الرياح (Wind Energy)** من أهم تطبيقات الطاقة المتجددة التي تتبنى المبدأ الفيزيائي الموحد لعمليات توليد الكهرباء، حيث يتمثل الفارق الجوهري بينها وبين المصادر التقليدية في طبيعة **مصدر الحركة** المستخدم لتدوير المولد الكهربائي. فبينما تعتمد المحطات التقليدية على ضغط البخار الناتج عن احتراق الوقود، تعتمد طاقة الرياح على القوة الحركية للهواء لتدوير ريش التوربينات مباشرة؛ وبمجرد دوران هذه الريش، ينتقل العزم الميكانيكي إلى المولد (Generator) ليبدأ الموصل في قطع خطوط الفيض المغناطيسي، وهو ما يؤدي استناداً إلى **قانون فاراداي** إلى نشوء قوة دافعة كهربائية مستحثة وتوليد تيار كهربائي مستحث. وبذلك، فإن المنظومة تحقق شرط "الحركة والمجال" لإنتاج "التيار" باستخدام مورد طبيعي مجاني ومستدام.

![[PV-03-03.gif]]

وتواجه مشاريع طاقة الرياح مجموعة من التحديات التقنية والجغرافية التي تحكم جدواها الاقتصادية، حيث تبرز ضرورة اختيار مواقع جغرافية محددة تتسم بـ **نشاط رياح عالٍ** ومستقر لضمان استمرارية دوران المولد بالسرعات المطلوبة، إذ أن غياب الرياح أو ضعف سرعتها يحول دون إنتاج الطاقة بشكل فعال مقارنة بالمصادر غير المتجددة التي تتسم بالاستمرارية طالما توفر الوقود. كما تتطلب هذه المنظومات توفير **مساحات واسعة وشاسعة جداً** حول التوربينات لضمان كفاءة الامتصاص الحركي للهواء وتجنب الاضطرابات الهوائية، مما يفرض تشييدها في مناطق نائية ومفتوحة بعيداً عن المناطق السكنية المكتظة.
