MAQattan/My-Graduation-Project/GP_Obsidian/Thesis/3/3- أنظمة الطاقة الشمسية المركزة (CSP).md

تُعد أنظمة الطاقة الشمسية المركزة (Concentrated Solar Power - CSP) من الحلول الهندسية المتقدمة التي تهدف إلى توظيف حرارة الشمس لتوليد الطاقة الكهربائية باتباع نفس المسار التشغيلي للمحطات الحرارية التقليدية، ولكن باستخدام مورد طبيعي نظيف بدلاً من الوقود الأحفوري. ويقوم المفهوم التقني لهذه الأنظمة على **تركيز الإشعاع الشمسي** الساقط على مساحات شاسعة وتجميعه في بؤرة مركزية واحدة باستخدام عواكس مرآتية، وذلك للتغلب على التشتت الطبيعي للطاقة الشمسية الذي لا يكفي وحده لوصول الموائع إلى درجات غليان مرتفعة تتناسب مع متطلبات التوربينات. ويمكن تشبيه هذه العملية بآلية عمل العدسات المجمعة التي تركز الأشعة في نقطة واحدة لرفع طاقتها الحرارية إلى مستويات قياسية قادرة على تسخين وسائط نقل الحرارة وصهر الأملاح، مما يسمح في النهاية بإنتاج بخار الماء تحت ضغوط عالية لتدوير التوربينات والمولدات وإنتاج تيار مستحث وفق قانون فاراداي.

ولمعالجة التحدي المحوري المرتبط بانقطاع الإشعاع الشمسي خلال فترة الليل، تتبنى هذه المحطات تقنية **تخزين الطاقة الحرارية باستخدام الملح المصهور (Molten Salt)** كبديل لوسائط التبريد التقليدية كالماء؛ حيث يتميز الملح المصهور بخصائص فيزيائية فريدة تمكنه من الاحتفاظ بالحرارة العالية لفترات زمنية طويلة قد تصل إلى ثماني أو تسع ساعات. وتعتمد الدورة التشغيلية في هذه الحالة على تسخين الملح داخل المستقبل الشمسي (Receiver) الموجود في بؤرة التركيز، ثم يتم نقله وتخزينه في خزانات ضخمة معزولة حرارياً بشكل محكم جداً لمنع أي تبادل حراري مع الوسط الخارجي والحفاظ على استقراره الحراري.

وعند غياب الشمس أو الحاجة لتوليد الكهرباء خلال ساعات الليل، يتم سحب الملح الساخن من هذه الخزانات المخصصة ليمر عبر مبادل حراري (Heat Exchanger)؛ حيث يقوم الملح بنقل طاقته الحرارية المختزنة إلى الماء لتحويله إلى بخار ماء مضغوط يدير التوربينات، ثم يعود الملح بعد تبريده وفقدانه للحرارة إلى خزان الملح البارد بانتظار إعادة رفعه للمستقبل الشمسي في اليوم التالي لبدء دورة تسخين جديدة. وبذلك، تضمن تقنية الملح المصهور استمرارية تدفق الطاقة الكهربائية للمستهلكين على مدار الساعة، مما يمنح أنظمة الـ CSP ميزة الموثوقية والثبات التشغيلي التي تفتقر إليها بعض المصادر المتجددة الأخرى، مع الحفاظ على بيئة نظيفة خالية من الانبعاثات الضارة الناتجة عن احتراق الفحم أو الغاز.

![[PV-03-05.png]]

#### 3-1 أنواع نظم المركزات الشمسية من حيث الشكل

تتعدد الأنماط الهندسة لأنظمة الطاقة الشمسية المركزة (**CSP**) بناءً على شكل العاكس وكيفية تركيز الإشعاع، إلا أنها تشترك جميعاً في الوظيفة الأساسية وهي تجميع أشعة الشمس في بؤرة مركزية لرفع درجة حرارة وسيط نقل الحرارة. وفيما يلي شرح مفصل لهذه الأنواع الثلاثة وفقاً لتصنيفاتها المورفولوجية:

##### **أولاً: نظام القطع المكافئ (Parabolic Trough)**

يُعد هذا النظام أحد أكثر التقنيات شيوعاً، ويستمد اسمه من الشكل الهندسي للعاكس الذي يتخذ هيئة **"القطع المكافئ" (Parabola)**. يتكون النظام من مرايا طولية منحنية على شكل حرف (U) تعمل على عكس أشعة الشمس وتركيزها في خط بؤري مستقيم يمر عبره أنبوب (مستقبل) يحتوي على المائع المراد تسخينه. ويتميز هذا التصميم بقدرته على تتبع الشمس في محور واحد، مما يجعله فعالاً في تجميع كميات كبيرة من الطاقة الحرارية الموزعة على مسارات طولية، وهو ما يسهل عمليات الصيانة والتشغيل في المحطات الكبيرة.

![[PV-03-06.png]]

##### **ثانياً: نظام الدش (Dish System)**

يأخذ هذا العاكس شكلاً هندسياً يشبه إلى حد كبير **"دش التليفزيون"** المنزلي، حيث يتكون من مرآة مقعرة دائرية أو مجموعة من المرايا المرتبة بشكل دائري. وتعتمد آلية العمل فيه على استقبال الأشعة الشمسية الساقطة على كامل مساحة الدش وعكسها لتتركز جميعاً في **نقطة بؤرية واحدة (Focal Point)** تقع في مقدمة الدش. ويتم وضع المستقبل الحراري عند هذه النقطة لامتصاص الحرارة المركزة جداً، والتي تُستخدم غالباً لتشغيل محركات صغيرة (مثل محرك ستيرلينغ) أو تسخين الملح المصهور، مما يجعله نظاماً مستقلاً وعالي الكفاءة في توليد الاستطاعات المتوسطة.

![[PV-03-07.jpg]]

##### **ثالثاً: نظام البرج الشمسي (Solar Tower)**

يُمثل نظام البرج الشمسي التقنية الأكثر ضخامة وقدرة على توليد درجات حرارة فائقة، ويعتمد على فلسفة **"التركيز البؤري المركزي"**. يتكون النظام من حقل واسع يضم مئات أو آلاف المرايا المتحركة التي تسمى "الهليوستات" (Heliostats)، والتي يتم التحكم بها برمجياً لتتبع مسار الشمس بدقة وتوجيه كافة الأشعة المنعكسة نحو هدف واحد وهو **الرسيفر (Receiver)** الموجود في قمة برج مركزي شاهق. وتتحول قمة البرج في هذا النظام إلى بؤرة حرارية هائلة تستقبل الإشعاع من كافة الجهات، مما يسمح بصهر كميات ضخمة من الأملاح ونقلها عبر أنابيب داخل البرج لبدء دورة توليد البخار والكهرباء. وتكمن ميزة هذا النظام في قدرته العالية على تخزين كميات هائلة من الطاقة الحرارية للعمل خلال فترات غياب الشمس.

![[PV-03-08.png]]

وبالرغم من اختلاف الأشكال الهندسية بين القطع المكافئ والدش والبرج، إلا أن **الدورة الحرارية والفيزيائية** تظل ثابتة؛ حيث تهدف جميعها لتحقيق أقصى تركيز ممكن للحرارة لتشغيل التوربينات والمولدات لإنتاج التيار المستحث.

#### **3-2 مميزات أنظمة الـ CSP** كطاقة نظيفة مقارنة بالمصادر التقليدية.

تتفوق أنظمة **الطاقة الشمسية المركزة (CSP)** على مصادر الطاقة التقليدية (مثل الفحم والغاز) من خلال تقديم نموذج إنتاجي يجمع بين الكفاءة الحرارية العالية والمحافظة التامة على البيئة. فبينما تعتمد المصادر التقليدية على احتراق الوقود الأحفوري الذي يخلف **انبعاثات غازية ضارة** تسهم بشكل مباشر في تلوث البيئة وظاهرة الاحتباس الحراري، تبرز أنظمة الـ CSP كبديل **نظيف تماماً** لا ينتج عنه أي ملوثات أو انبعاثات كربونية أثناء عملية التوليد. ويعود ذلك إلى الاعتماد على مورد طبيعي مجاني ومستدام وهو الشمس لتسخين الموائع وتوليد البخار اللازم لتحريك التوربينات، بدلاً من الاعتماد على حرق الفحم أو الغاز.

ومن الناحية التشغيلية والموثوقية، تعالج أنظمة الـ CSP العيب الجوهري المرتبط بمعظم المصادر المتجددة، وهو الارتباط الوثيق بالظروف الجوية والوقت؛ فإذا كانت المصادر التقليدية تمتاز بـ **الاستمرارية** طالما توفر الوقود اللازم للحرق، فإن أنظمة الـ CSP تحقق موثوقية مشابهة بفضل تقنية **تخزين الملح المصهور (Molten Salt)**. وتسمح هذه التقنية المتقدمة للمحطة بالاحتفاظ بالحرارة العالية لمدة تتراوح بين **8 إلى 9 ساعات**، مما يضمن استمرار عملية توليد الكهرباء بكفاءة خلال فترات الليل أو عند غياب الشمس، متجاوزة بذلك عقبة "التقطع" التي قد تواجه طاقة الرياح أو الأنظمة الشمسية التي لا تمتلك خاصية التخزين الحراري.

وبناءً على ذلك، تكمن الميزة التنافسية لأنظمة الـ CSP في أنها توفر "نظافة" المصدر المتجدد مع الحفاظ على "استقرار" وموثوقية المصدر التقليدي؛ فهي تتبع نفس الدورة الميكانيكية والفيزيائية للمحطات التقليدية (دوران التوربينات لإنتاج تيار مستحث وفق قانون فاراداي) ولكن باستخدام طاقة شمسية مركزة، مما يجعلها خياراً هندسياً مثالياً للتحول نحو الطاقة الخضراء دون المساس باستقرار الأحمال على الشبكة الكهربائية].
