MAQattan/My-Graduation-Project/GP_Obsidian/Thesis/3/المبدأ الفيزيائي العام لتوليد الكهرباء (قانون فاراداي).md

تُعد عملية توليد الطاقة الكهربائية، سواء من المصادر المتجددة أو غير المتجددة، تطبيقاً فيزيائياً لمبدأ عام واحد يقوم على التفاعل بين ثلاثة عناصر أساسية هي: الحركة، والمجال المغناطيسي، والتيار الكهربائي. وتنص القاعدة الفيزيائية على أنه في حال توافر عنصرين من هذه الثلاثة، يمكن استنتاج العنصر الثالث؛ وفي حالة المولد الكهربائي (Generator)، يتم استغلال **الحركة والمجال** لإنتاج **التيار**. ويستند هذا المبدأ بشكل أساسي إلى **قانون فاراداي (Faraday's Law)**، الذي يقرر أنه عندما يقطع موصل كهربائي خطوط فيض مجال مغناطيسي، تتولد في هذا الموصل قوة دافعة كهربائية مستحثة (Induced EMF)، وتؤدي هذه القوة بدورها إلى سريان تيار كهربائي مستحث في الدائرة.

![[PV-03-01.png]]

وتعتبر هذه الظاهرة الفيزيائية هي القاسم المشترك بين جميع محطات القوى؛ فالاختلاف بين طرق التوليد لا يكمن في المبدأ الفيزيائي ذاته، بل في **مصدر الحركة** وكيفية الحصول عليها. ففي المصادر غير المتجددة، يتم الحصول على الحركة عن طريق حرق الوقود (مثل الفحم أو الغاز) لتسخين المياه وتحويلها إلى بخار مضغوط يدير ريش التوربينات، والتي تقوم بدورها بتحريك المولد داخل المجال المغناطيسي لتوليد الكهرباء. أما في المصادر المتجددة، فيتم الحصول على هذه الحركة مباشرة من طاقة الرياح التي تدير التوربينات، أو من خلال دفع المياه في المحطات الهيدروليكية، أو حتى عبر تركيز الإشعاع الشمسي (CSP) لتسخين الموائع وتوليد البخار اللازم لتحريك التوربين.

ومن الناحية الرياضية والمنطقية، يمكن التعبير عن هذا التفاعل بالعلاقة التبادلية بين المتغيرات الثلاثة، حيث يمثل إنتاج التيار ($I_{induced}$) المحصلة النهائية للتفاعل بين المتجه الحركي ($v$) وكثافة الفيض المغناطيسي ($B$)، وهو ما يضمن استمرارية تحويل الطاقة الميكانيكية إلى طاقة كهربائية طالما استمر قطع الموصل لخطوط المجال.
