MAQattan/My-Graduation-Project/GP_Obsidian/Thesis/3/مصادر الطاقة غير المتجددة.md

تُعتبر المصادر غير المتجددة، والمتمثلة بشكل أساسي في الفحم والغاز الطبيعي، الركيزة التقليدية التي قامت عليها نظم توليد الطاقة الكهربائية لعقود طويلة، حيث تعتمد في جوهرها على تحويل الطاقة الكيميائية الكامنة في الوقود إلى طاقة حركية ثم إلى طاقة كهربائية. وتتبع هذه المصادر آلية عمل فيزيائية موحدة تبدأ بعملية احتراق الوقود لتوليد طاقة حرارية هائلة تُستغل في تسخين المياه داخل غلايات ضخمة لتحويلها إلى بخار ماء. ويتم رفع ضغط هذا البخار وتوجيهه بسرعات تدفق عالية جداً ليصطدم بريش التوربينات، مما يؤدي إلى دورانها بسرعة كبيرة؛ وبما أن التوربينة متصلة ميكانيكياً بالمولد الكهربائي (Generator)، فإن حركتها تؤدي إلى دوران الموصلات داخل مجال مغناطيسي، وهو ما يحقق شرط "الحركة والمجال" اللازمين لتوليد القوة الدافعة الكهربائية المستحثة والتيار الكهربائي بناءً على قانون فاراداي.

![[PV-03-02.jpg]]

وتتميز المصادر غير المتجددة بمجموعة من الخصائص التي جعلتها الخيار السائد عالمياً، وعلى رأسها عامل الاستمرارية والموثوقية العالية في التزويد بالطاقة. فخلافاً للمصادر المتجددة كالرياح التي ترتبط بنشاط حركة الهواء أو الطاقة الشمسية التي تتقيد بوجود الشمس نهاراً، فإن محطات الفحم والغاز لا تتأثر بالظروف المناخية أو التقلبات الجوية؛ إذ يمكن توليد الكهرباء منها في أي وقت طالما توافر مخزون الوقود الكافي، مما يضمن استقرار الشبكة الكهربائية وتلبية الأحمال المطلوبة على مدار الساعة دون انقطاع. وهذا الاستقرار هو السبب الرئيسي وراء الاعتماد الواسع على هذه المصادر في تشغيل المدن والمصانع التي تتطلب طاقة مستمرة وثابتة.

ومع ذلك، تبرز العيوب البيئية كأكبر تحدٍ يواجه استمرار الاعتماد على هذه المصادر، حيث تطلق عملية احتراق الفحم والغاز كميات هائلة من الانبعاثات الغازية والملوثات الضارة بالبيئة، والتي تُسهم بشكل مباشر في ظاهرة الاحتباس الحراري وتلوث الهواء. وتُعد هذه الانبعاثات الكربونية الدافع الرئيسي الذي يوجه العالم حالياً نحو البحث عن بدائل نظيفة ومستدامة، مثل أنظمة المركزات الشمسية (CSP) التي تحاكي نفس الدورة الحرارية وتوليد البخار ولكن باستخدام حرارة الشمس بدلاً من حرق الوقود الملوث، وذلك لتفادي الأضرار البيئية الجسيمة المرتبطة بالمصادر التقليدية.
