MAQattan/My-Graduation-Project/GP_Obsidian/Thesis/4/الفرق بين STC & NOCT.md

تُمثل ظروف الاختبار القياسية (**STC**) وظروف التشغيل الطبيعية للخلية (**NOCT**) المعايير المرجعية التي يتم على أساسها تقييم الأداء الكهربائي للألواح الشمسية وتحديد قيم الجهد والتيار (مثل تيار القصر وجهد الدائرة المفتوحة) قبل خروج اللوح من المصنع. وتعتمد **ظروف الاختبار القياسية (Standard Test Conditions - STC)** على بيئة مخبرية مثالية تهدف إلى استخراج أقصى قدرة ممكنة من اللوح، حيث يتم الاختبار عند شدة إشعاع شمسي تبلغ **1000 واط/متر مربع** (وهو الإشعاع المماثل لوقت الظهيرة في يوم مشمس)، ودرجة حرارة خلية منخفضة ومثالية تبلغ **25 درجة مئوية**، مع معامل كتلة هواء (Air Mass) يبلغ 1.5. وتؤدي هذه الظروف المثالية إلى تسجيل أعلى قيم للقدرة الاسمية ($P_{max}$) نظراً لدمجها بين ذروة الإشعاع وأقل مستوى من المفقودات الحرارية.

وعلى النقيض من ذلك، تهدف **ظروف التشغيل الطبيعية (Nominal Operating Cell Temperature - NOCT)** إلى تقديم محاكاة أكثر دقة لما سيواجهه اللوح فعلياً عند التركيب في الميدان؛ حيث يتم القياس عند شدة إشعاع متوسطة تبلغ **800 واط/متر مربع**، ودرجة حرارة خلية واقعية تصل إلى **45 درجة مئوية** (وهي قيمة قريبة للظروف التشغيلية في المنطقة العربية)، مع الأخذ في الاعتبار تأثير سرعة الرياح لزيادة دقة النتائج. وبناءً على هذه المعطيات، تكون القدرة الإنتاجية المسجلة تحت ظروف (NOCT) دائماً **أقل** من تلك المسجلة تحت ظروف (STC) بسبب انخفاض شدة الإضاءة وارتفاع درجة الحرارة التي تؤثر سلباً على جهد اللوح.

ومن الناحية الهندسة والتصميمية، يبرز تساؤل حول سبب اعتماد المصممين والشركات المصنعة على قيم (STC) بشكل أساسي في "الداتا شيت" (Data Sheets) بالرغم من كونها ظروفاً غير واقعية تماماً. ويعود السبب في ذلك إلى رغبة الصناعة في **توحيد معايير القياس عالمياً**؛ حيث إن ظروف (NOCT) تختلف باختلاف الموقع الجغرافي والمناخ (فحرارة 45 مئوية قد لا تكون طبيعية في أوروبا مثلاً)، مما يجعل (STC) مرجعاً ثابتاً وحيداً للمقارنة العادلة بين كفاءة الألواح من مختلف المصنعين. وبشكل عام، تُستخدم قيم (STC) في مرحلة **التصميم والديزاين** الأساسي للمنظومة، بينما تُستخدم قيم (NOCT) كأداة هندسية لحساب **المفقودات الفعلية (Actual Losses)** التي ستتعرض لها القدرة الإنتاجية في بيئة العمل الحقيقية.
