MAQattan/My-Graduation-Project/GP_Obsidian/Thesis/4/تنظيف الألواح وأنظمة تثبيتها.md

تُعد صيانة المنظومات الكهروضوئية من خلال **تنظيف الألواح** واختيار **أنظمة التثبيت** (Supports) المناسبة ركيزتين أساسيتين لضمان استدامة الإنتاجية وتحقيق أقصى استفادة من الإشعاع الشمسي المتاح؛ حيث لا يقتصر دور التنظيف على إزالة العوائق الفيزيائية كالشوائب والأتربة فحسب، بل يمتد ليشمل الإدارة الحرارية للوح. فمن الناحية التقنية، يُعد رش الألواح بالماء وسيلة فعالة للتنظيف تماثل تأثير الأمطار الطبيعية، وهي تحقق فائدة مزدوجة؛ تتمثل الأولى في استعادة قدرة الخلايا على امتصاص الفوتونات بكفاءة عالية، وتتمثل الثانية في **تبريد الألواح** وخفض درجة حرارتها التشغيلية. وبما أن العلاقة بين درجة الحرارة والقدرة الكهربائية هي **علاقة عكسية**، فإن خفض حرارة اللوح يؤدي بالضرورة إلى رفع قيمة الجهد الناتج وبالتالي زيادة الاستطاعة الكلية للمنظومة.

أما فيما يخص **هياكل التثبيت والقواعد**، فإن اختيار نوع الشاسيه يعتمد بشكل مباشر على طبيعة السطح والظروف المحيطة بالموقع؛ ففي حال كان التركيب على أسطح خرسانية مستوية، يُفضل استخدام القواعد الأرضية المباشرة لجدواها الاقتصادية العالية. أما في حال التركيب في المزارع أو الأراضي المفتوحة، فيتحتم **رفع الألواح عن مستوى الأرض** بمسافة كافية؛ وذلك لحماية الأجزاء السفلية من الألواح من تراكم الأتربة أو التظليل الناتج عن نمو الأعشاب وأوراق الشجر، مما يضمن بقاء كامل مساحة اللوح معرضة للإشعاع دون عوائق.

وتنقسم أنظمة التثبيت من حيث الحركية إلى أنظمة ثابتة (Fixed) وأنظمة تتبع (Trackers). وتعتمد **أنظمة التتبع** على ملاحقة مسار الشمس لتصحيح زاوية السقوط وضمان بقاء الأشعة عمودية قدر الإمكان على سطح الخلية؛ حيث توجد أنظمة تتبع في **اتجاه واحد** (Single-axis) تتيح تعديل ميل اللوح بين فصلي الصيف والشتاء لمواجهة تغير ارتفاع الشمس في الأفق، حيث تتطلب الشتاء زاوية ميل كبيرة بينما تتطلب الصيف زاوية ميل صغيرة. كما توجد أنظمة تتبع في **اتجاهين** (Dual-axis) تلاحق الشمس من الشرق إلى الغرب يومياً بالإضافة لتعديل زاوية الميل الرأسية، مما يحقق أعلى إنتاجية ممكنة للقدرة.

![[PV-04-24.jpg]]

ورغم المزايا الإنتاجية لأنظمة التتبع، إلا أن **الأنظمة الثابتة** (Fixed Systems) تظل هي الخيار الأكثر شيوعاً وهيمنة في التطبيقات العملية؛ ويعود ذلك إلى اعتبارات اقتصادية وهندسية، حيث إن تكلفة المحركات والحساسات ونظم التحكم والصيانة المرتبطة بالمقتفيات الشمسية تفوق غالباً قيمة الزيادة المحققة في الطاقة المنتجة. لذا، يتم ترجيح كفة النظام الثابت في معظم المشاريع لضمان توازن أفضل بين التكلفة الرأسمالية والعائد الطاقي، مع التركيز على ضبط زاوية الميل الثابتة لتناسب متوسط الإشعاع السنوي للموقع.

![[PV-04-25.jpg]]
