MAQattan/My-Graduation-Project/GP_Obsidian/Thesis/4/دايود الحجب (Blocking Diode).md

يُعد هذا **الدايود** عنصراً أساسياً لحماية المصفوفات الكهروضوئية (Arrays) التي تتكون من عدة سلاسل (Strings) مربوطة على التوازي. وبخلاف دايود التجاوز (Bypass Diode) الذي يُوصل على التوازي مع مجموعات الخلايا، يتم توصيل دايود الحجب على **التوالي** مع كل سلسلة بشكل منفصل قبل نقطة التجميع. وتكمن الوظيفة الجوهرية لهذا الدايود في منع تدفق التيار العكسي (Reverse Current) من السلاسل السليمة ذات الجهد المرتفع إلى السلاسل التي قد تتعرض لظلال جزئية أو أعطال تقنية تؤدي لانخفاض جهدها.

ومن الناحية الفيزيائية، عندما تتعرض سلسلة معينة للظل، ينخفض جهدها الكلي بشكل ملحوظ مقارنة بالسلاسل المجاورة لها في نفس المصفوفة، مما ينشئ فرق جهد يدفع التيار القادم من السلاسل السليمة للتدفق عكسياً داخل السلسلة المظللة بدلاً من التوجه نحو الحمل. لا يتسبب هذا السلوك في فقدان كبير للقدرة الإنتاجية فحسب، بل يؤدي أيضاً إلى ارتفاع حرارة الألواح في السلسلة المتضررة مما قد يسبب احتراقها أو نشوب حرائق في المنظومة. وهنا يعمل دايود الحجب كصمام أحادي الاتجاه؛ حيث يسمح بمرور التيار في الاتجاه الطبيعي من الألواح نحو نقطة التجميع، بينما يمنع تماماً أي تيار يحاول المرور في الاتجاه المعاكس.

![[PV-04-22.png]]

ويمكن توضيح الأهمية الرياضية لدايود الحجب من خلال معادلة التيار الكلي للمصفوفة ($I_{total}$)؛ ففي حالة حدوث خلل في إحدى السلاسل (السلسلة رقم 1 مثلاً) وغياب دايود الحجب، تضيع الطاقة في صورة تيار عكسي، وتُصبح العلاقة:

$$
I_{total} = I_2 + I_3 - I_{reverse(1)}
$$

أما عند استخدام دايود الحجب، فإنه يمنع قيمة ($I_{reverse}$) تماماً، مما يضمن خروج صافي تيار السلاسل السليمة فقط إلى الحمل:

$$
I_{total} = I_2 + I_3
$$

وعلى صعيد التركيب الميكانيكي، لا يتم وضع دايود الحجب في "صندوق التوصيل" (Junction Box) خلف اللوح كما هو الحال مع دايود التجاوز، بل يُثبت عادةً داخل **"صندوق التجميع" (Combiner Box)**، وهو صندوق يشبه لوحة التوزيع الكهربائية يتم فيه تجميع كافة السلاسل في المنظومات الكبيرة. وكما هو معلوم بالغالب يكون وصل جميع الخلاية الداخلية للوح الواحد تسلسلي، وبالتالي غالب استخدام هذه الطريقة عند توصل سلاسل الألواح مع بعضها البعض على التوازي، ويجدر بالذكر أن استخدام دايودات الحجب يقتصر غالباً على المنظومات الضخمة التي تحتوي على مصفوفات متوازية متعددة، بينما قد لا تُستخدم في المنظومات الصغيرة جداً لعدم وجود خطر حقيقي من التيارات العكسية.
