MAQattan/My-Graduation-Project/GP_Obsidian/Thesis/4/دايودات التجاوز (Bypass diode).md

تعتبر هذه الدايودات من أهم عناصر الحماية في الوحدات الكهروضوئية، حيث تهدف بشكل أساسي إلى معالجة الآثار السلبية الناتجة عن حدوث الظلال الجزئية (Shading) على خلايا اللوح. فعند تعرض خلية شمسية واحدة أو مجموعة من الخلايا للظل — بسبب سقوط أوراق الأشجار أو تراكم الأتربة مثلاً — فإن إنتاجيتها من التيار تنخفض بشكل حاد، مما يجعل بقية الخلايا السليمة في السلسلة "ترى" هذه الخلية المظللة كحمْل كهربائي (Load) بدلاً من كونها مصدراً للطاقة. ويؤدي تدفق التيار عبر الخلية المظللة في هذه الحالة إلى ارتفاع شديد في درجة حرارتها، وهو ما قد يتسبب في حدوث ما يُعرف بـ "النقاط الساخنة" (Hotspots) التي قد تؤدي إلى احتراق الخلية وتلف اللوح بالكامل.

ولمواجهة هذه الظاهرة، يتم توصيل دايود التجاوز على التوازي مع مجموعة من الخلايا بقطبية معكوسة، بحيث يُربط مصعد الدايود (Anode) بالطرف السالب للمجموعة، ومهبطه (Cathode) بالطرف الموجب. وفي ظروف التشغيل العادية (بدون ظل)، في هذه الحالة تعمل الخلية عمل بطارية صغيرة تولد طاقة، وبالتالي يكون الجهد على خرجها يساوي جهدها بالإضافة إلى جهد الخلاية المربوطة على دخلها، وبما أن الديود مربوط معها على التوازي فسيكون جهد المصعد (Anode) أخفض من جهد المهبط (Cathode)، مما يجعل الدايود في حالة انحياز عكسي، وبالتالي لا يمر عبره أي تيار وتعمل كافة الخلايا بشكل طبيعي. أما عند حدوث التظليل، فإن الجهد على الخلية المظللة ينخفض أو ينعكس نتيجة تحولها لحمْل، مما يؤدي إلى انعكاس القطبية عند أطراف الدايود ليصبح جهد المصعد أعلى من جهد المهبط، مما يدفع الدايود للانتقال إلى حالة التوصيل (Forward Bias). في هذه اللحظة، يسلك التيار مساراً بديلاً عبر الدايود متجاوزاً مجموعة الخلايا المظللة، وهو ما يحميها من الاحتراق بالرغم من أن ذلك يؤدي إلى فقدان جزئي في قدرة اللوح الكلية تعادل قدرة الخلايا التي تم تجاوزها.

![[PV-04-19.png]]

ومن الناحية العملية والاقتصادية، لا يتم تخصيص دايود تجاوز لكل خلية على حدة لارتفاع التكلفة، بل يتم تقسيم اللوح إلى مجموعات؛ ففي الألواح القياسية المكونة من 60 خلية، يُستخدم عادةً ثلاث دايودات تجاوز، بحيث يكون كل دايود مسؤولاً عن حماية 20 خلية متصلة توالياً. وتوضع هذه الدايودات هندسياً داخل "صندوق التوصيل" (Junction Box) الموجود في الجانب الخلفي من اللوح الشمسي لسهولة الصيانة والوصول إليها. وتتمثل المعادلة الفيزيائية الحاكمة لبدء عمل الدايود في وصول فرق الجهد بين المصعد والمهبط إلى حالة تسمح بمرور التيار ($V_{anode} > V_{cathode}$)، وهو ما يحدث فقط عند تعثر أداء الخلايا المظللة.

![[PV-04-21.png]]

![[PV-04-20.png]]
