MAQattan/My-Graduation-Project/GP_Obsidian/Thesis/4/ربط الألواح الشمسية.md

تنتقل المنظومة الشمسية من مجرد ألواح فردية إلى نظام طاقة متكامل من خلال طرق ربط محددة تهدف إلى مواءمة المخرجات الكهربائية مع متطلبات أجهزة التحكم والأحمال، حيث يُعد اللوح الشمسي أصغر وحدة مستقلة في المنظومة، بينما يمثل الربط بين هذه الألواح الوسيلة للتحكم في قيمتي الجهد والتيار. وتنقسم طرق الربط الأساسية إلى ثلاثة أنماط رئيسية هي التوصيل على التوالي، والتوصيل على التوازي، والتوصيل المشترك.

### **أولاً: التوصيل على التوالي (Series Connection)**

يتم التوصيل على التوالي من خلال ربط القطب الموجب للوح الأول بالقطب السالب للوح الذي يليه، وهكذا حتى الوصول إلى نهاية المجموعة التي يُطلق عليها هندسياً اسم **"سلسلة" (String)**. ويُعد الهدف الأساسي من هذا النمط هو الرفع التراكمي لجهد المنظومة مع الحفاظ على قيمة تيار ثابتة تعادل تيار اللوح الواحد؛ حيث يمر تيار واحد فقط في كامل السلسلة.

![[PV-04-14.png]]

وتصاغ العلاقات الرياضية لهذا النوع من الربط كالتالي:

- **الجهد الكلي:** $V_{total} = V_1 + V_2 + V_3 + \dots + V_n$.
- **التيار الكلي:** $I_{total} = I_{panel}$.

فعلى سبيل المثال، إذا تم ربط أربعة ألواح توالياً، وكان جهد اللوح الواحد 19 فولت وتياره 8 أمبير، فإن الجهد الكلي للمنظومة سيرتفع ليصل إلى 76 فولت ($19 \times 4$)، بينما سيظل التيار الكلي ثابتاً عند قيمة 8 أمبير.

### **ثانياً: التوصيل على التوازي (Parallel Connection)**

يعتمد التوصيل على التوازي على تجميع كافة الأطراف ذات القطبية المتشابهة معاً؛ حيث تُربط جميع الأقطاب الموجبة في نقطة تجميع واحدة، وكذلك الأقطاب السالبة، لتخرج المنظومة في النهاية بطرفين رئيسيين (موجب وسالب). ويُستخدم هذا النمط لزيادة التيار الكلي للمنظومة مع الحفاظ على استقرار الجهد عند قيمة مساوية لجهد اللوح الواحد.

![[PV-04-15.png]]

وتتمثل العلاقات الرياضية للربط التوازي في:

- **التيار الكلي:** $I_{total} = I_1 + I_2 + I_3 + \dots + I_n$.
- **الجهد الكلي:** $V_{total} = V_{panel}$.

وفي حال تطبيق هذا النمط على أربعة ألواح (بقدرة 8 أمبير و19 فولت للوح)، فإن التيار الكلي سيتضاعف ليصل إلى 32 أمبير ($8 \times 4$)، بينما سيظل جهد المنظومة ثابتاً عند 19 فولت.

### **ثالثاً: التوصيل المشترك (Series-Parallel Connection)**

في المشاريع المتوسطة والكبيرة، نادراً ما يتم الاعتماد على نمط واحد فقط، بل يتم اللجوء للتوصيل المشترك للوصول إلى الاستطاعة التصميمية المطلوبة، وهو ما يُعرف بـ **"المصفوفة" (Array)**. وتتكون المصفوفة من عدة سلاسل (Strings) متصلة توازياً مع بعضها البعض، مما يسمح للمصمم بالتحكم في رفع الجهد (من خلال عدد الألواح في السلسلة الواحدة) ورفع التيار (من خلال عدد السلاسل المربوطة توازياً) في آن واحد.

![[PV-04-16.jpg]]

ولحساب مخرجات التوصيل المشترك، يتم أولاً حساب جهد السلسلة الواحدة، ثم يُعتبر هذا الجهد هو الجهد الكلي للمصفوفة لأن جهد التوازي ثابت. أما التيار الكلي، فيكون مجموع تيارات كافة السلاسل المربوطة توازياً. فإذا كان لدينا مصفوفة مكونة من أربع سلاسل، وكل سلسلة تحتوي على لوحين توالي (بفرض أن اللوح 19 فولت و8 أمبير)، فإن الجهد الكلي سيكون 38 فولت ($19 \times 2$)، والتيار الكلي سيكون 32 أمبير ($8 \times 4$)، مما ينتج قدرة إجمالية تساوي حاصل ضرب الجهد الكلي في التيار الكلي للمصفوفة.
