MAQattan/My-Graduation-Project/GP_Obsidian/Thesis/4/وصل الخلاية.md

تعتمد الكفاءة التشغيلية للوح الشمسي على كيفية تنظيم وترابط الوحدات البنائية الصغرى، وهي الخلايا الشمسية، داخلياً للوصول إلى قيم جهد وتيار تتناسب مع المتطلبات الكهربائية للمنظومات. فمن الناحية التقنية، تُنتج الخلية الشمسية المنفردة تياراً كهربائياً مرتفعاً يتراوح عادةً بين 8 إلى 10 أمبير، إلا أنها تعاني من انخفاض حاد في قيمة الجهد الكهربائي، حيث لا يتجاوز جهد الخلية الواحدة حاجز 0.5 إلى 0.6 فولت في أحسن الأحوال. وبناءً على هذه المعطيات الفيزيائية، يصبح من غير المجدي استخدام الخلايا بشكل منفرد أو ربطها توازياً، لأن ذلك سيحافظ على الجهد منخفضاً جداً؛ وهو ما استدعى هندسياً اعتماد **التوصيل على التوالي (Series Connection)** كخيار أساسي وحيد للربط الداخلي داخل اللوح الواحد لرفع الجهد إلى مستويات تشغيلية مقبولة.

ويتم تنفيذ هذا الربط من خلال مكون معدني متخصص يُعرف بـ **"الباسبار" (Busbar)**، وهو عبارة عن أشرطة رقيقة مصنعة من مادة القصدير تقوم بمهمة مزدوجة؛ فهي تعمل كمجمعات للإلكترونات من سطح الخلية لتقليل الفقد، وفي الوقت نفسه تقوم بدور الجسر الموصل الذي يربط القطب الموجب لكل خلية بالقطب السالب للخلية التي تليها مباشرة. هذا التسلسل في الربط يؤدي إلى تراكم الجهد الكهربائي بشكل طردي مع عدد الخلايا؛ ففي الألواح القياسية التي تحتوي مثلاً على 36 خلية متصلة توالياً، يرتفع الجهد الكلي للوح ليصل إلى حوالي 18 فولت (وهو حاصل ضرب جهد الخلية الواحدة في عدد الخلايا)، بينما يظل التيار الكلي للوح ثابتاً ومساوياً لتيار الخلية الواحدة (حوالي 8 أو 9 أمبير) لأن تيار التوالي يمر في مسار واحد فقط.

تسمح هذه الآلية في الربط الداخلي بتحويل مجموعة كبيرة من الخلايا الصغيرة إلى "موديول" أو لوح شمسي متكامل، تكون قدرته الإجمالية هي حاصل مجموع قدرات كافة الخلايا المكونة له. ويُعد اللوح في هذه الحالة هو **أصغر وحدة مستقلة** يمكن للمهندس التعامل معها وتوصيلها في المنظومة، حيث يضمن الربط التوالي الداخلي وصول الجهد إلى مستويات كافية لبدء تشغيل أجهزة تحويل الطاقة (Inverters) أو منظمات الشحن، مع الحفاظ على شدة تيار مستقرة ناتجة عن الخلية الواحدة.

![[PV-04-02.png]]
