MAQattan/My-Graduation-Project/GP_Obsidian/Thesis/4/وصلات MC4.md

تُمثل وصلات **MC4** (اختصار لـ Multi-Contact 4mm) المعيار الهندسي العالمي لربط الألواح الشمسية ببعضها البعض أو ربطها بالمنظومة الكهربائية، وهي مصممة خصيصاً لتجاوز التحديات البيئية والكهربائية التي تواجهها محطات الطاقة الشمسية. وتكمن الضرورة القصوى لاستخدام هذه الوصلات في طبيعة تشغيل الألواح التي توضع دائماً في أماكن معرضة بشكل مباشر للعوامل الجوية القاسية من أمطار، وأتربة، ودرجات حرارة مرتفعة جداً؛ لذا يتم تزويد هذه الوصلات بمعامل حماية (**IP - Ingress Protection**) مرتفع يضمن عزل نقاط الاتصال الكهربائي عن الرطوبة والمياه والشوائب التي قد تسبب تآكلاً في الموصلات أو حدوث تماس كهربائي.

![[PV-04-17.jpg]]

ومن الناحية التقنية، يُحظر في التصميمات الاحترافية اللجوء إلى الطرق التقليدية في ربط الأسلاك، مثل لف الأطراف يدوياً وتغطيتها بالشريط اللاصق (الشكرتون)؛ فمثل هذه الربطات اليدوية تخلق مقاومة كهربائية عالية عند نقطة الاتصال، مما يؤدي إلى حدوث فقد كبير في الجهد (**Voltage Drop**) وتوليد حرارة عالية عند مرور تيارات المنظومة. وتُعد نقاط الربط اليدوي هذه أضعف حلقة في السلسلة الكهربائية، حيث تكون أولى النقاط عرضة للصهر أو الاحتراق (Melting) بمجرد ارتفاع شدة التيار، وهو ما تتلاشاه وصلات **MC4** تماماً من خلال توفير اتصال ميكانيكي وكهربائي منخفض المقاومة ومحكم الإغلاق.

تتكون هذه الوصلات ميكانيكياً من طرفين: طرف ذكري (**Male**) وطرف أنثوي (**Female**)، حيث يتم تعشيقهما ببعضهما البعض لضمان اتصال ثابت لا ينفك بفعل الرياح أو الاهتزازات. وتتوفر هذه الوصلات بأنماط مختلفة تناسب نوع التوصيل المطلوب؛ ففي التوصيل على التوالي، تُستخدم الوصلات البسيطة لربط الألواح تباعاً، أما في التوصيل على التوازي، فتُستخدم **وصلات تشعبية (Y-branch)** قادرة على استقبال طرفين من الألواح وإخراجهما في طرف واحد، مما يسهل عملية تجميع التيارات في نقطة واحدة مع الحفاظ على درجة حماية المنظومة. وبذلك، تضمن وصلات **MC4** استمرارية تدفق الطاقة بكفاءة عالية مع توفير الأمان اللازم للمعدات والعنصر البشري طوال العمر الافتراضي للمنظومة.

![[PV-04-18.png]]
