MAQattan/My-Graduation-Project/GP_Obsidian/Thesis/6/الفصل السادس - أنظمة الطاقة الشمسية.md

## [[المنظومات الكهروضوئية المستقلة عن الشبكة (Off-Grid Systems)]]

## [[المنظومات الكهروضوئية المرتبطة بالشبكة (On-Grid Systems)]] 

## [[المنظومات الكهروضوئية الهجينة (Hybrid PV Systems)]]
