MAQattan/My-Graduation-Project/GP_Obsidian/Thesis/6/المنظومات الكهروضوئية المرتبطة بالشبكة (On-Grid Systems).md

تُمثل **المنظومات الكهروضوئية المرتبطة بالشبكة (On-Grid Systems)** أو (Grid-tied) أو (Grid-Connected) النمط الهندسي الأكثر انتشاراً في البيئات الحضرية والمناطق المجهزة بالبنية التحتية الكهربائية، وهي التركيز الأساسي للتطبيقات التجارية والسكنية الحديثة. وتستند الفلسفة التشغيلية لهذه المنظومات إلى مبدأ التكامل مع الشبكة القومية، حيث تعمل الشبكة كـ **"مستودع تخزيني افتراضي"** يستقبل فائض الطاقة نهاراً ويمد المستخدم بالطاقة اللازمة ليلاً، مما يلغي الحاجة التقنية لأنظمة البطاريات المكلفة والمعقدة في الظروف العادية.

### آلية العمل والدورة الطاقية (Operational Dynamics)

![[PV-06-02.jpg]]

تعتمد الدورة التقنية للمنظومة المرتبطة بالشبكة على مسار تحويلي يبدأ من الألواح الكهروضوئية التي تولد تياراً مستمراً (**DC**) عند سقوط الإشعاع الشمسي. يتم توجيه هذا التيار مباشرة إلى **المحول المرتبط بالشبكة (Grid-interactive Inverter)**، والذي يقوم بمهمة حيوية تتمثل في تحويل التيار إلى متردد (**AC**) مع مواءمة جهده وتردده بدقة مع معايير الشبكة القومية.

- **خلال ساعات النهار:** تقوم المنظومة بتغذية الأحمال الكهربائية داخل المبنى أولاً؛ وفي حال زاد الإنتاج عن حاجة الاستهلاك، يتم تصدير الفائض تلقائياً إلى الشبكة الكهربائية.
- **خلال ساعات الليل:** يتوقف الإنتاج الشمسي كلياً، وتتحول الشبكة إلى المصدر الأساسي لتزويد المبنى بالكهرباء، مما يضمن استمرارية الخدمة دون الحاجة لوسيط تخزين كيميائي.

### المكونات الأساسية للمنظومة (System Components)

تتميز هذه المنظومة ببساطة مكوناتها مقارنة بالأنظمة المعزولة، مما يقلل من تكاليف الصيانة والتركيب:

- **المصفوفة الكهروضوئية (PV Array):** لتوليد الطاقة من ضوء الشمس.
- **المحول (Inverter):** وهو المكون الأهم، حيث يتضمن تقنيات تتبع نقطة الاستطاعة القصوى (**MPPT**) لضمان استخلاص أقصى قدرة ممكنة من الألواح تحت الظروف المختلفة.
- **نظام القياس (Metering System):** ويتمثل في عداد تبادلي (**Net Meter**) يقوم بحساب كمية الطاقة المُصدرة للشبكة مقابل الطاقة المستوردة منها، ويتم محاسبة المستخدم على الفرق بينهما (المحصلة).

### المزايا الاقتصادية والتقنية

تتمتع المنظومات المرتبطة بالشبكة بعدة ميزات تجعلها الخيار الأول للمستثمرين:

- **انخفاض التكلفة الرأسمالية:** نظراً للاستغناء عن البطاريات ومنظمات الشحن التي تمثل جزءاً كبيراً من ميزانية الأنظمة المعزولة.
- **المرونة في التصميم:** لا يشترط في هذه المنظومة أن تغطي كامل أحمال المبنى، بل يمكن تصميمها بأي حجم يرغبه المالك لتقليل قيمة الفاتورة الشهرية فقط.
- **تحقيق الأرباح:** في العديد من الدول، تتيح القوانين (مثل تعرفه التغذية **Feed-in Tariffs**) للمستخدمين بيع الطاقة الفائضة للشبكة وتحقيق عائد مادي.

### الأمان الكهربائي وظاهرة "الجزيرة" (Islanding)

من الناحية الأمنية، تُصمم المحولات الحديثة في هذه المنظومات لتتوقف عن العمل تلقائياً في حال انقطاع التيار عن الشبكة القومية؛ وتُعرف هذه الميزة بـ **منع التجزير (Anti-Islanding)**. وتكمن أهميتها في حماية فنيي الصيانة الذين قد يعملون على خطوط الشبكة، حيث يمنع المحول تدفق الكهرباء من الألواح الشمسية إلى الشبكة "الميتة"، مما يضمن سلامة الأرواح والمعدات.
