MAQattan/My-Graduation-Project/GP_Obsidian/Thesis/6/المنظومات الكهروضوئية المستقلة عن الشبكة (Off-Grid Systems).md

تُعد المنظومات المستقلة عن الشبكة، والمعروفة تقنياً بـ **(Off-Grid)** أو **(Stand-alone Systems)**، الحل الهندسي الأمثل لتوفير الطاقة الكهربائية في المناطق النائية والمعزولة جغرافياً التي تفتقر لوجود البنية التحتية للشبكة القومية. وتستند الفلسفة التشغيلية لهذه المنظومات إلى مبدأ "الاستقلالية الطاقية التامة"، حيث يتم توليد واستهلاك الطاقة بمعزل عن أي مصدر خارجي، مما يجعلها الخيار الأكثر جدوى اقتصادياً في الحالات التي تتجاوز فيها تكاليف مد خطوط الشبكة التقليدية الميزانيات المتاحة. وتتميز هذه الأنظمة بمرونة عالية في الحجم، حيث تبدأ من تطبيقات بسيطة تعتمد على لوح واحد لتشغيل أحمال محدودة، وصولاً إلى محطات ضخمة مجهزة بأنظمة تحكم متطورة ومولدات احتياطية لتلبية احتياجات تجمعات سكنية أو صناعية كاملة.

### آلية العمل ودورة الطاقة (Operational Mechanism)

تعتمد المنظومات المعزولة في جوهرها على الموائمة بين فترات التوليد وفترات الاستهلاك عبر وسيط تخزيني. فخلال ساعات النهار، تقوم الألواح الكهروضوئية بتحويل الإشعاع الشمسي إلى تيار مستمر (**DC**) يُستخدم لتغذية الأحمال مباشرة وشحن نظام البطاريات. وبما أن إنتاجية الألواح تنقطع كلياً خلال فترة الليل، تصبح **البطاريات** هي المصدر البديل والوحيد لتزويد الأحمال بالكهرباء المخزنة، مما يضمن استمرارية الخدمة على مدار الساعة.

### المكونات الأساسية للنظام (System Components)

تتألف المنظومة المعزولة المتكاملة من أربعة عناصر تقنية رئيسية تعمل في تناغم هندسي:

- **المصفوفة الكهروضوئية (PV Array):** المسؤولة عن تحويل الطاقة الضوئية إلى كهربائية.

![[PV-06-01.png]]

- **منظم الشحن (Charge Controller):** وهو العقل المدبر لعملية الشحن، حيث يقوم بتنظيم الجهد والتيار القادم من الألواح لضمان شحن البطاريات بكفاءة وحمايتها من الشحن الزائد أو التلف.
- **بنك البطاريات (Battery Bank):** وهو المستودع الكيميائي لتخزين الطاقة، ويعد المكون الأكثر تكلفة والأكثر حرجاً في هذه المنظومات.
- **المحول (Inverter):** ويقوم بتحويل التيار المستمر (**DC**) المخزن في البطاريات إلى تيار متردد (**AC**) بجهد وتردد يطابق متطلبات الأجهزة المنزلية أو الصناعية القياسية.

### أنماط وتطبيقات خاصة (System Variations)

تتنوع أشكال المنظومات المعزولة بناءً على طبيعة الحمل التشغيلي:

- **منظومات التيار المستمر البسيطة (Simple DC Systems):** وهي حالات خاصة يتم فيها الاستغناء عن المحول (Inverter) والبطاريات، حيث يتم ربط الألواح مباشرة بأحمال تعمل بالتيار المستمر خلال نهاراً فقط، مثل بعض أنواع مراوح التهوية أو المضخات، مما يقلل من التكلفة الرأسمالية للنظام بشكل كبير.
- **منظومات ضخ المياه (Solar Pumping):** تُعد تطبيقاً حيوياً للمنظومات المعزولة في المناطق الصحراوية لاستصلاح الأراضي، حيث تُستغل الطاقة الشمسية لتشغيل مضخات تسحب المياه الجوفية. وغالباً ما يتم تصميمها لتعمل نهاراً مع استبدال البطاريات بخزانات مياه لتوفير التكلفة.

### التحديات التقنية والاقتصادية

بالرغم من ميزة الاستقلالية، تواجه المنظومات المعزولة تحدي **التكلفة المرتفعة** مقارنة بالمنظومات المتصلة بالشبكة (On-Grid)؛ ويعود ذلك بشكل رئيسي إلى ارتفاع أسعار البطاريات والحاجة لاستبدالها بشكل دوري. كما تتطلب عملية التصميم دقة فائقة في حساب "أيام الغيوم" (Autonomy Days) لضمان عدم انقطاع التيار عن الأحمال الحرجة في الظروف الجوية السيئة.
