MAQattan/My-Graduation-Project/GP_Obsidian/Thesis/6/المنظومات الكهروضوئية الهجينة (Hybrid PV Systems).md

تُمثل **المنظومات الهجينة (Hybrid Systems)** الجيل الأكثر تطوراً ومرونة في هندسة الطاقة الشمسية؛ حيث صُممت لتتجاوز الحدود التشغيلية لكل من الأنظمة المعزولة والمرتبطة بالشبكة على حد سواء. وتستند الفلسفة الجوهرية لهذا النظام إلى دمج ميزات "الربط التبادلي" مع الشبكة القومية، وميزات "التخزين الطاقي" المستقل، مما يخلق بيئة تشغيلية تضمن استمرارية تدفق الكهرباء حتى في أصعب الظروف التقنية. وبالرغم من نضوج تقنيات الألواح والمحولات في الأسواق العالمية، إلا أن الأنظمة الهجينة تظل الخيار الهندسي الأول للتطبيقات التي لا تحتمل أي هامش لانقطاع التيار، موفرةً بذلك حلاً مثالياً يوازن بين الجدوى الاقتصادية والأمان التشغيلي.

### المفهوم التقني والآلية التشغيلية (System Concept)

تُعرف المنظومة الهجينة تقنياً بأنها النظام الذي يجمع بين ميزتين أساسيتين: الربط مع الشبكة الكهربائية (On-Grid) لتبادل الفائض، ووجود بنك للبطاريات (Off-Grid) لتأمين الطاقة الاحتياطية. وتعتمد هذه المنظومة على "المصدر المتعدد"، حيث يشترط هندسياً توفر **مصدرين إضافيين** على الأقل بجانب الألواح الشمسية لضمان استقرار الأحمال، وهما غالباً الشبكة العامة والبطاريات، أو الشبكة العامة ومولد الديزل (Diesel Generator).

### المكونات الأساسية للنظام (Core Components)

تتألف المنظومة الهجينة من عناصر تقنية معقدة تتيح لها إدارة تدفقات الطاقة في اتجاهات متعددة:

- **المصفوفة الكهروضوئية (PV Array):** المصدر الأساسي لتوليد التيار المستمر نهاراً.
- **المحول الهجين (Hybrid Inverter):** ويُعرف أحياناً بـ (Inverter-Charger)، وهو جهاز متعدد الوظائف يقوم بتحويل التيار، وشحن البطاريات، وتنظيم العلاقة التبادلية مع الشبكة؛ حيث يمكنه تغذية الأحمال من الألواح أو البطاريات أو الشبكة حسب الأولوية المبرمجة.
- **وسيط التخزين أو النسخ الاحتياطي (Storage/Back-up):** ويتمثل في بنك بطاريات لتخزين الطاقة لاستخدامها عند انقطاع الشبكة، أو مولدات احتراق داخلي (ديزل/تربينات) لتعزيز الموثوقية في المواقع الاستراتيجية.

### تطبيقات الأحمال الحرجة (Critical Loads Applications)

تُعد المنظومات الهجينة الحل المعياري لما يُسمى بـ **"الأحمال الكريتيكال" (Critical Loads)**، وهي الأجهزة والمنشآت التي يؤدي انقطاع الكهرباء عنها إلى خسائر فادحة أو مخاطر حيوية. ومن أبرز هذه التطبيقات:

- **غرف العناية المركزة (ICU):** حيث يجب ضمان عمل الأجهزة الطبية دون انقطاع لثانية واحدة.
- **مراكز البيانات (Data Centers):** لحماية المعلومات الحساسة من الفقد الناتج عن التوقف الفجائي.
- **أنظمة المراقبة والأمن:** لضمان عمل الكاميرات وأجهزة الإنذار على مدار الساعة.

### تحليل الأداء والمميزات

تتفوق المنظومة الهجينة في قدرتها على إدارة سيناريوهات العمل المختلفة؛ ففي أوقات النهار والجو الغائم، يمكنها سحب العجز من الشبكة أو البطاريات. وفي حال انقطاع تيار الشبكة القومية (Blackout)، تتحول المنظومة تلقائياً للعمل بنمط "الأوف جريد" بالاعتماد على البطاريات، مما يحمي المستخدم من الانقطاعات التي تعجز الأنظمة المرتبطة بالشبكة (On-Grid) عن معالجتها بسبب ميزة "منع التجزير". وبذلك، تحقق المنظومة الهجينة أقصى استفادة من "مجانية" الإشعاع الشمسي، و"استقرار" الشبكة العامة، و"أمان" التخزين الكيميائي.
