MAQattan/My-Graduation-Project/GP_Obsidian/Thesis/7/التحديات التقنية في العواكس البسيطة.md

يواجه التصميم الأولي للعواكس البسيطة، والمعتمد هندسياً على بساطة قنطرة H الميكانيكية، عوائق تقنية جوهرية تحول دون قدرتها على تلبية المتطلبات القياسية للأحمال الكهربائية الحديثة، وتتمحور هذه التحديات حول ثلاثة محاور فيزيائية رئيسية هي التردد، وقيمة الجهد، وشكل الموجة.

يتمثل **التحدي الأول في ضبط التردد (Frequency)**؛ كما ذكرنا سابقًا تتطلب الأنظمة الكهربائية القياسية تردداً قدره 50 هيرتز، وهو ما يفرض إتمام دورة كاملة (نصف موجب ونصف سالب) كل 20 ميلي ثانية. وتعجز المفاتيح الميكانيكية البدائية عن الصمود أمام هذه السرعة الفائقة في التبديل، حيث يتطلب الأمر تغيير حالة المفاتيح كل 10 ميلي ثانية بدقة متناهية، وهو ما يمثل عائقاً زمنياً وحركياً لا يمكن تجاوزه بالوسائل التقليدية. أما **التحدي الثاني فيتعلق بقيمة الجهد أو "السعة" (Amplitude)**؛ فالمصدر الأساسي للتغذية في المنظومات المعزولة هو البطاريات التي تعمل بجهود منخفضة غالباً ما تكون 12 أو 24 أو 48 فولت تيار مستمر. وعند تحويل هذا التيار عبر القنطرة البسيطة، يظل الجهد المتردد الناتج عند مستوياته المنخفضة (حوالي 46 فولت مثلاً بعد احتساب المفاقيد الداخلية)، وهي قيمة لا تتناسب إطلاقاً مع جهد التشغيل المنزلي القياسي البالغ 220 فولت، مما يجعل العاكس البسيط غير قادر على تزويد الأحمال بالقدرة الكافية.

ويبرز **التحدي الثالث في تشوه شكل الموجة (Waveform)**؛ حيث إن عملية التبديل المباشر بين أقطاب البطارية تنتج ما يُسمى بالـ "الموجة المربعة" (Square Wave)، وهي موجة تتميز بثبات القيمة اللحظية للجهد في كل نصف دورة. وبالرغم من أنها تيار متردد فيزيائياً لكونها تعكس اتجاهها، إلا أنها تفتقر إلى الخصائص الجيبية (Sinusoidal) للموجة النقية المتوفرة في الشبكة العامة. ويؤدي الاعتماد على هذه الموجة المربعة إلى مشاكل تقنية حادة عند تشغيل الأحمال الحثية مثل المحركات أو الأجهزة الإلكترونية الحساسة، نظراً لارتفاع نسبة التوافقيات (Harmonics) التي تسبب حرارة زائدة وقد تؤدي إلى احتراق المكونات الداخلية للأجهزة. وبناءً على ذلك، تمثل هذه التحديات الثلاثة الفجوة التقنية التي استدعت تطوير تقنيات التبديل الإلكتروني السريع وتعديل عرض النبضة واستخدام المحولات الرافعة للوصول إلى جودة الطاقة المطلوبة.
