MAQattan/My-Graduation-Project/GP_Obsidian/Thesis/7/الطوبولوجيا الهندسية لعواكس الشبكة (On-Grid Topologies).md

تُحدد الطوبولوجيا الهندسية لعواكس الشبكة (On-Grid Topologies) الكيفية التي يتم بها تنظيم الربط الكهربائي بين المصفوفات الشمسية ووحدات التحويل. وهي تلعب دوراً حاسماً في تحديد التكلفة الكلية للمشروع ومقدار الإنتاجية الطاقية، خاصة في الظروف الجوية غير المثالية. وتصنف هذه الأنظمة تقنياً إلى أربعة أنماط رئيسية تتفاوت في قدرتها على معالجة مفاقيد التظليل الجزئي وتحقيق الجدوى الاقتصادية:

### 1. العواكس الدقيقة (Micro-inverters)

تعتمد هذه الطوبولوجيا على تخصيص عاكس مستقل لكل لوح شمسي يقوم بعملية تحويل التيار وتتبع نقطة الاستطاعة القصوى (MPPT) بشكل منفصل، مما يجعل كل لوح يعمل بمعزل عن أداء الألواح المجاورة له. وتتميز هذه التقنية بكونها الأكثر كفاءة في مواجهة ظروف التظليل الجزئي؛ فإذا تعرض لوح واحد للظل، يظل باقي النظام يعمل بكامل طاقته دون أي تأثر، كما أنها تلغي الحاجة لكابلات التيار المستمر (DC) الطويلة وتسهل عملية التوسعة المستقبلية.

ولكن في المقابل، تُمثل هذه البنية التكنولوجية الأعلى من حيث التكلفة الرأسمالية نظراً للحاجة إلى عدد كبير من الوحدات، كما تظهر التحليلات الهندسية ارتفاع المفاقيد والضياعات الداخلية فيها، وتزايد صعوبة إجراءات الصيانة الدورية نظراً لتموضع العواكس على الأسطح خلف الألواح مباشرة.

![[PV-07-12.png]]

### 2. عواكس السلسلة (String Inverters)

يُعد هذا النمط الخيار الأكثر شيوعاً وتوافراً في الأسواق التجارية للمنظومات متوسطة الحجم، حيث يتم ربط مجموعة من الألواح على التوالي لتشكل "سلسلة" كهربائية موحدة تتصل بعاكس مركزى يمتلك مدخلاً واحداً لتقنية MPPT.

وعلى الرغم من الميزة الاقتصادية والتوافرية لهذه العواكس، إلا أنها تعاني من حساسية مرتفعة وحرجة تجاه ظروف التظليل؛ إذ يتسبب تظليل لوح واحد فقط داخل السلسلة في خفض إنتاجية السلسلة بأكملها وهبوط أدائها بشكل حاد، نتيجة ارتباط الألواح كافة بمسار تيار كهربائي واحد يجبر النظام على اتخاذ قيمة التيار الأقل.

![[PV-07-16.png]]

### 3. العواكس المركزية (Central Inverters)

تبرز العواكس المركزية كحل هندسي مثالي واقتصادي للمشاريع الكبرى ومحطات التوليد التي تتجاوز قدرتها 10 كيلوواط؛ حيث يتم ربط المصفوفة الشمسية بالكامل بعاكس ضخم واحد، مما يحقق أقل تكلفة رأس مالية ممكنة للمشروع ويسهل عمليات التشغيل والصيانة لتركيز المعدات في نقطة مركزية واحدة.

ومع ذلك، يعيب هذه الطوبولوجيا ضعف المرونة التشغيلية وافتقارها لمبدأ الاعتمادية التبادلية (Redundancy) في حال تعطل وحدة العكس الرئيسية. فعند حدوث تظليل على لوح واحد، قد تخرج أجزاء واسعة من المنظومة عن الخدمة؛ حيث يُستخدم في هذا النوع ديودات حجب (Blocking Diodes) تربط كل سلسلة بديود مستقل داخل صندوق التجميع (Combiner Box)، وعند وقوع التظليل ينحاز الديود برابط عكسي ليخرج السلسلة المتأثرة بالكامل من حيز الإنتاج حمايةً للنظام.

![[PV-07-17.png]]

### 4. العواكس متعددة السلاسل (Multi-string Inverters)

تأتي هذه الطوبولوجيا الحديثة لتقدم حلاً هجيناً يجمع بكفاءة بين المزايا الاقتصادية للأنظمة المركزية والمرونة التشغيلية لأنظمة السلاسل؛ حيث تتكون من وحدة عاكس مدمجة واحدة لكنها تحتوي داخلياً على عدة مداخل مستقلة ومتوازية لتقنية MPPT.

تمنح هذه البنية المهندسين مرونة عالية في تقسيم الألواح إلى مجموعات مستقلة تماماً، مما يتيح معالجة مشاكل التظليل الجزئي بذكاء، والتغلب على عوائق اختلاف زوايا ميل وتوجيه الألواح على الأسطح المعقدة، دون الاضطرار لتحمل التكاليف الباهظة للعواكس الدقيقة.

![[PV-07-18.png]]

> **خلاصة هندسية:** بناءً على هذه المقارنات، يظل استقرار القرار على طوبولوجيا هندسية محددة محكوماً بمعادلة موازنة دقيقة بين متطلبات الاعتمادية واستمرارية التشغيل، وبين الميزانية الاستثمارية المرصودة للمشروع وطبيعة الطبوغرافية الجغرافية للموقع.
