MAQattan/My-Graduation-Project/GP_Obsidian/Thesis/7/العواكس المرتبطة بالشبكة (On-Grid Inverters).md

تُمثل العواكس المرتبطة بالشبكة الركيزة التقنية للأنظمة الكهروضوئية التفاعلية؛ حيث يرتكز مبدأ عملها الأساسي على استقبال التيار المستمر (DC) الناتج من مصفوفة الألواح وتحويله إلى تيار متردد (AC) يُحقن مباشرة في الشبكة العامة أو يُستهلك محلياً في أحمال المنشأة. وعلى خلاف الأنظمة المعزولة، تتصل هذه العواكس بالألواح الشمسية كأول وسيط تقني في المسار، مما يفرض دمج خاصية تتبع نقطة الاستطاعة القصوى (MPPT) داخل بنيتها الإلكترونية لرفع كفاءة التوليد وضمان استخلاص أقصى قدرة ممكنة تحت ظروف الإشعاع المتغيرة.

### حماية منع التجزير (Anti-Islanding)

خضع عمل هذه العواكس لرقابة إلكترونية صارمة تضمن التوقف الفوري والآلي عن العمل في حال انقطاع تيار الشبكة العامة. تهدف هذه الآلية إلى منع تدفق الطاقة نحو شبكة كهربائية ميتة وخارجة عن الخدمة، وهي الميزة الأمنية المعروفة هندسياً بمنع التجزير (Anti-Islanding)، والتي تُعد إلزامية لحماية فنيي الصيانة من مخاطر الصعق وتأمين المعدات الشبكية من التلف.

### اشتراطات التزامن مع الشبكة (Synchronization)

تُعد عملية التزامن المعيار الهندسي الحاسم لتشغيل العواكس، إذ يُحظر تقنياً ربط مخرجات العاكس بالشبكة إلا بعد تحقق أربعة اشتراطات فيزيائية دقيقة تضمن تماثل الخصائص الموجية تماماً:

**تطابق قيمة الجهد (Voltage Magnitude):** يجب أن يوفر العاكس جهداً كهربائياً يماثل جهد الشبكة بدقة، مثل 220 فولت للأنظمة أحادية الطور أو 380 فولت للأنظمة ثلاثية الأطوار لضمان استقرار الربط.

**تماثل التردد (Frequency):** يلتزم العاكس بالعمل التام وفق تردد الشبكة القياسي (50 هيرتز)؛ وذلك لتجنب حدوث تداخلات موجية أو اضطرابات طاقية في المنظومة.

**تطابق زاوية الوجه (Phase Shift):** تفرض هذه الخاصية تزامناً زمنياً كاملاً، بحيث تتطابق لحظة بداية الموجة الجيبية للعاكس مع لحظة بداية موجة الشبكة الكهربائية.

**تطابق تسلسل الأطوار (Phase Sequence):** يُشترط في الأنظمة ثلاثية الأطوار تطابق ترتيب وتتابع الأطوار (مثل A-B-C) بين العاكس والشبكة، وهو أمر جوهري لضمان سلامة وتشغيل الأحمال الحثية والمحركات.

### جودة الطاقة والموجة الجيبية النقية (Pure Sine Wave)

بناءً على محددات التزامن الصارمة، يُحظر هندسياً استخدام العواكس ذات الموجات المربعة أو المعدلة في الأنظمة المرتبطة بالشبكة. ويُشترط إلزامياً إنتاج موجة جيبية نقية (Pure Sine Wave) ذات محتوى تشوه توافقي (Harmonics) ضئيل جداً يقل عن 3% غالباً، وذلك للحفاظ على جودة الطاقة الموردة، وحماية الأجهزة الحساسة، وضمان استقرار الشبكة الكهربائية القومية.
