MAQattan/My-Graduation-Project/GP_Obsidian/Thesis/7/العواكس المعزولة عن الشبكة (Off-Grid Inverters).md

تُمثل العواكس المعزولة عن الشبكة الركيزة التشغيلية للمنظومات الكهروضوئية المستقلة، وهي الأنظمة المصممة هندسياً لتوفير الطاقة في المناطق النائية التي تفتقر للربط مع البنية التحتية للشبكة الكهربائية العامة نتيجة عوائق جغرافية أو اقتصادية.

### التسلسل التقني وديناميكية التغذية

تعتمد البنية الهيكلية لهذه المنظومات على تسلسل تقني متكامل؛ يبدأ من مصفوفة الألواح الشمسية التي تولد التيار المستمر، مروراً بمنظم الشحن (Charge Controller) الذي يدير تدفق الطاقة نحو بنك البطاريات، وصولاً إلى العاكس الذي يتولى المهمة النهائية بتحويل هذه الطاقة إلى تيار متردد متوافق مع الأحمال المنزلية أو الصناعية.

وتتسم آلية تغذية العاكس في هذا النمط بمرونة زمنية تضمن استقرار التغذية الكهربائية للأحمال على مدار الساعة. فخلال ساعات النهار، يستمد العاكس طاقته التشغيلية من الإنتاج المباشر للألواح الشمسية عبر الوسيط التنظيمي، بينما يتحول الاعتماد كلياً إلى الطاقة الكيميائية المخزنة في البطاريات خلال فترات الليل أو في الظروف الجوية التي يغيب فيها الإشعاع الشمسي.

### غياب تقنية الـ MPPT والتمايز الهندسي

من الناحية التصميمية، يبرز تمايز جوهري في هندسة العواكس المعزولة يتمثل في عدم اشتراط دمج خاصية تتبع نقطة الاستطاعة القصوى (MPPT) داخل جهاز العاكس نفسه، وهو ما يفسر انخفاض تكلفتها الرأسمالية نسبياً مقارنة بالأنواع الأخرى.

ويعود السبب العلمي لهذا الاستبعاد الوظيفي إلى ترتيب المكونات داخل الدائرة الكهربائية؛ حيث إن منظم الشحن هو المكون الأقرب كهربائياً للمصفوفة الشمسية، وبالتالي تقع على عاتقه هندسياً مسؤولية القيام بعملية الـ MPPT لضمان استخلاص أقصى قدرة ممكنة من الألواح وتوجيهها بكفاءة لشحن البطاريات.

وبما أن دخل العاكس المعزول يرتبط مباشرة ببنك البطاريات الذي يوفر جهداً مستمراً مستقراً ومحكوماً، فإنه لا يحتاج وظيفياً لتتبع مخرجات الألواح المتغيرة. ويختلف هذا السلوك جذرياً عن العواكس المرتبطة بالشبكة (On-Grid) التي تتصل مباشرة بالمصفوفة الشمسية وتستلزم وجود تقنية الـ MPPT بداخلها كشرط أساسي لرفع كفاءة التوليد.

> **خلاصة هندسية:** يمثل العاكس المعزول حلقة الوصل الأخيرة في دورة الطاقة المستقلة، حيث يركز جهده التقني على جودة تحويل التيار واستقراره التشغيلي، بمعزل عن تعقيدات تتبع القدرة الشمسية التي يتولاها منظم الشحن.
