MAQattan/My-Graduation-Project/GP_Obsidian/Thesis/7/الفصل السابع - الانفرتر.md

تعد العواكس (Inverters) المكون التقني الجوهري في منظومات الطاقة الشمسية، حيث تضطلع بمهمة محورية تتمثل في تحويل التيار الكهربائي من النوع المستمر (DC) إلى التيار المتردد (AC) ليتوافق بشكل دقيق مع متطلبات تشغيل الأحمال الكهربائية القياسية. ويعزى خروج الطاقة الكهربائية من الألواح الكهروضوئية بصيغة تيار مستمر إلى الطبيعة الفيزيائية لحركة الإلكترونات داخل الخلية الشمسية، حيث تتحرك الإلكترونات في اتجاه ثابت وموحد من الطبقة (N-type) إلى الطبقة (P-type)، مما ينتج عنه تياراً ثابتاً في القطبية والاتجاه لا يمكن استخدامه مباشرة لتشغيل معظم الأجهزة والمعدات التي تعمل بنظام التيار المتردد. وتتجلى الوظيفة الحيوية للعواكس في دورها كوسيط تقني لا غنى عنه لربط مصادر التوليد بنقاط الاستهلاك؛ ففي المنظومات المستقلة، يقوم العاكس بسحب التغذية الكهربائية المستمرة من المصفوفة الشمسية خلال ساعات النهار أو من بنك البطاريات خلال فترات الليل، ثم يجري عليها عمليات التحويل اللازمة لتوفير طاقة مترددة مستقرة. وبناءً على ذلك، يمثل العاكس الركيزة الأساسية التي تضمن تكامل المنظومة الشمسية مع الأحمال الكهربائية، وبدونه تظل الطاقة المولدة من الإشعاع الشمسي محصورة في نطاق تطبيقات التيار المستمر المحدودة وغير متوافقة مع الأنظمة الكهربائية الحديثة.

## [[المبدأ الفيزيائي لعملية الانعكاس (قنطرة H)]] 

## [[التحديات التقنية في العواكس البسيطة]] 

## [[حل معضلة التردد (تقنية الترانزستور IGBT)]]

## [[حل معضلة شكل الموجة (تقنية PWM)]] 

## [[حل معضلة قيمة الجهد والتحكم بالتردد]] 

## [[العواكس المعزولة عن الشبكة (Off-Grid Inverters)]] 

## [[تصنيف موجات العواكس وتوافقها مع الأحمال]] 

## [[تحليل الخصائص الكهربائية في (Datasheet) العاكس المعزول]] 

## [[العواكس المرتبطة بالشبكة (On-Grid Inverters)]] 

## [[الطوبولوجيا الهندسية لعواكس الشبكة (On-Grid Topologies)]] 

## [[تحليل الخصائص الكهربائية (Datasheet) لعاكس متصل (On-grid)]] 

## [[عواكس أنظمة الضخ الشمسي (Solar Pumping Inverters)]]
