MAQattan/My-Graduation-Project/GP_Obsidian/Thesis/7/المبدأ الفيزيائي لعملية الانعكاس (قنطرة H).md

يستند المبدأ الفيزيائي لعملية الانعكاس في منظومات الطاقة الشمسية إلى مفهوم "التبديل الدوري للقطبية" (Commutation) لتحويل تيار مستمر ثابت الاتجاه إلى تيار متردد يعكس اتجاهه دورياً. ويتم تنفيذ هذه العملية هندسياً عبر دائرة إلكترونية تُعرف بـ **"قنطرة H" (H-Bridge)**، والتي تتكون من أربعة مفاتيح إلكترونية مرتبة في فرعين متوازيين مع وجود الحمل في المنتصف، مما يمنح الدائرة شكل حرف (H) في المخططات الهندسية. وتعتمد آلية العمل على فتح وإغلاق هذه المفاتيح في أزواج متقابلة؛ فعند إغلاق الزوج الأول من المفاتيح (S1 و S4) مع بقاء الزوج الآخر مفتوحاً، يتدفق التيار من القطب الموجب للمصدر المستمر (كالبطارية أو الألواح) ليمر عبر الحمل في اتجاه محدد، مطبقاً قطبية موجبة على طرفي الحمل. ولإتمام عملية الانعكاس وتحقيق شرط التيار المتردد، يتم فتح الزوج الأول وإغلاق الزوج الثاني (S2 و S3)، مما يؤدي إلى عكس مسار تدفق الإلكترونات داخل الحمل نفسه، فتنعكس القطبية ويصبح اتجاه التيار معاكساً تماماً للحالة الأولى رغم ثبات قطبية المصدر الأصلي.

![[PV-07-01.png]]

![[PV-07-02.webp]]

ومن الناحية الزمنية، تخضع هذه العملية التبادلية لمعادلة التردد الأساسية حيث إن الزمن الدوري ($T$) اللازم لإتمام دورة كاملة (دورة موجبة وسالبة) يرتبط بالتردد ($f$) بالعلاقة ($T = 1/f$)؛ فمن أجل الحصول على تردد قياسي قدره 50 هيرتز، يجب أن تتم العمليتان معاً كل 20 ميلي ثانية، مما يعني ضرورة تبديل حالة المفاتيح كل 10 ميلي ثانية. ويؤدي هذا النمط البدائي من التبديل إلى إنتاج ما يُعرف بـ **"الموجة المربعة" (Square Wave)**، وهي موجة تتميز بثبات القيمة اللحظية للجهد في النصفين الموجب والسالب، مما يجعلها تختلف في خصائصها الفيزيائية عن الموجة الجيبية النقية (Pure Sine Wave) المتوفرة في الشبكات الكهربائية العامة. وبالتحليل البصري لهذه العملية، يظهر أن الجهد الناتج يتبدل لحظياً بين قيمتين قصويتين متساويتين في المقدار ومتعاكستين في الاتجاه، وهو ما يمثل التحدي التقني الأول في تصميم العواكس لضمان توافق هذا الخرج مع الأحمال الحثية والإلكترونية الحساسة. وخلاصة القول، إن قنطرة H تمثل المنهجية الفيزيائية لتحويل التدفق الأحادي للإلكترونات إلى تدفق ترددي عبر التلاعب بمسارات الدائرة الكهربائية، وهي الركيزة التي تُبنى عليها كافة تقنيات تحويل الطاقة الحديثة.

![[PV-07-03.png]]
