MAQattan/My-Graduation-Project/GP_Obsidian/Thesis/7/تحليل الخصائص الكهربائية (Datasheet) لعاكس متصل (On-grid).md

يُمثل التحليل الفني لورقة البيانات (Datasheet) الخاصة بالعواكس المرتبطة بالشبكة (On-grid Inverters) الخطوة الجوهرية في تصميم المنظومات الكهروضوئية التفاعلية، حيث تُحدد هذه البيانات الحدود التشغيلية والملاءمة الهندسية لربط المصفوفة الشمسية بالشبكة الكهربائية القومية. وتُظهر المواصفات الفنية لجيل العواكس الحديثة (مثل طرازات شركة ABB) تمايزاً دقيقاً في معاملات الدخل والخرج يضمن استخلاص أقصى طاقة ممكنة مع الحفاظ على استقرار الشبكة.

![[PV-07-13.png]]

تبدأ العملية التحليلية بتقييم **خصائص الدخل المستمر (DC Input)**، حيث يبرز مصطلح **"مدى جهد تتبع نقطة الاستطاعة القصوى" (MPPT Voltage Range)** كأهم معيار للتصميم؛ ففي العينة قيد الدراسة، يتراوح هذا المدى بين 335 فولت و800 فولت. وتكمن الأهمية الفيزيائية لهذا المدى في اشتراط بقاء جهد المصفوفة الشمسية ضمن هذه الحدود لضمان عمل خوارزمية الـ MPPT بكفاءة كاملة؛ ففي حال انخفاض الجهد عن 335 فولت أو ارتفاعه عن 800 فولت، يفقد العاكس قدرته على استخلاص الاستطاعة العظمى من الألواح. كما تشير البيانات إلى **"الجهد المستمر الأقصى" (Max DC Voltage)** الذي يصل إلى 900 فولت، وهو حد الأمان الذي لا يجوز تجاوزه لتجنب تلف الدوائر الإلكترونية، مع ملاحظة أن العمل في المنطقة بين 800 و900 فولت يسمح بالتشغيل دون تتبع نقطة الاستطاعة القصوى. ومن الناحية الهيكلية، يُصنف العاكس كـ **"متعدد السلاسل" (Multi-string)** نظراً لوجود أربعة مداخل مستقلة للتيار المستمر، حيث تبلغ سعة التيار لكل دخل 10.5 أمبير، مما يتوافق هندسياً مع تيار السلسلة الواحدة (String) الذي يتراوح عادة حول 9 أمبير.

أما في جانب **خصائص الخرج المتردد (AC Output)**، فتُركز ورقة البيانات على جودة الطاقة والتزامن؛ حيث تبلغ الاستطاعة الاسمية للخرج 3.3 كيلوواط بجهد قياسي 230 فولت وتيار 14.3 أمبير. ويخضع الخرج لرقابة صارمة على **"التوافقيات" (Total Harmonic Distortion - THD)**، والتي يجب أن تكون أقل من 3% لضمان عدم إدخال تشوهات موجية للشبكة العامة، وهو ما يعد أفضل من المعايير القياسية التي تسمح بحدود تصل إلى 5%. كما يظهر **"معامل القدرة" (Power Factor)** بقيمة مساوية للواحد الصحيح (cos φ = 1)، وهو ما يفسر تطابق قيم الاستطاعة الفعالة (Watt) مع الاستطاعة الكلية (VA) في هذه العواكس. وتتضمن البيانات أيضاً مؤشرات الكفاءة التشغيلية مثل **"استهلاك وضع الاستعداد" (Standby Consumption)** الذي يبلغ 12 واط نهاراً، و"الاستهلاك الليلي" (Night Consumption) الذي ينخفض إلى أقل من 1 واط عند غياب الإشعاع الشمسي، مما يضمن تقليل الهدر الطاقي للحد الأدنى. وبناءً على هذا التحليل، يُعد التوافق بين جهد المصفوفة ومدى الـ MPPT للعاكس هو الركيزة الأساسية لضمان نجاح التوليد الشمسي المرتبط بالشبكة.
