MAQattan/My-Graduation-Project/GP_Obsidian/Thesis/7/عواكس أنظمة الضخ الشمسي (Solar Pumping Inverters).md

تُمثل عواكس أنظمة الضخ الشمسي (**Solar Pumping Inverters**) فئة متخصصة من أجهزة تحويل الطاقة صُممت هندسياً لتلائم الطبيعة الديناميكية للأحمال الميكانيكية، وتحديداً المحركات الحثية ثلاثية الأطوار المستخدمة في طلمبات المياه. وبخلاف العواكس التقليدية، تشتمل هذه العواكس على بنية تحكم ذكية تتصل مباشرة بالمصفوفة الكهروضوئية، مما يفرض دمج تقنية تتبع نقطة الاستطاعة القصوى (**MPPT**) بداخلها كشرط أساسي لضمان استخلاص أقصى قدرة ممكنة من الألواح وتوجيهها لتشغيل الموتور تحت ظروف الإشعاع المتغيرة.

![[PV-07-19.png]]

وتبرز أهمية هذه العواكس في قدرتها على معالجة معضلة "تيار البدء" (**Starting Current**)؛ فالمحركات الحثية تعاني في لحظة الإقلاع من ظاهرة القصور الذاتي، مما يضطرها لسحب تيار كهربائي ضخم يتراوح بين **6 إلى 8 أضعاف** تيار التشغيل الطبيعي. ولتجنب الإجهاد الحراري للمكونات أو الحاجة لتضخيم حجم النظام الشمسي بشكل غير اقتصادي، يتم دمج تقنية **"البدء الناعم" (Soft Starter)** ضمن البرمجيات التشغيلية للعاكس، حيث تستغل المفاتيح الإلكترونية الداخلية لتطبيق الجهد على المحرك بشكل تدريجي وتصاعدي يبدأ من الصفر. وتؤدي هذه المنهجية الهندسية إلى زيادة التيار والجهد ببطء حتى يتم تجاوز مرحلة القصور الذاتي والوصول إلى السرعة المقررة (**Rated Speed**) دون حدوث قفزات تيارية مفاجئة، مما يطيل العمر الافتراضي للمضخة ويحمي الدوائر الإلكترونية للعاكس من التلف.

علاوة على ذلك، تتميز عواكس الضخ بقدرتها الفريدة على تأمين **"القدرة غير الفعالة" (Reactive Power)** الضرورية لعمل المحركات الحثية، وهو ما يميزها عن العواكس المرتبطة بالشبكة التي قد تعمل بمعامل قدرة مساوٍ للواحد الصحيح. فمن الناحية الفيزيائية، يحتاج الموتور لامتصاص قدرة فعالة لتحويلها إلى شغل ميكانيكي، بجانب امتصاص قدرة غير فعالة لإنتاج المجال المغناطيسي (**Magnetic Field**) اللازم لعملية الدوران. لذا، يتم تزويد هذه العواكس بمكونات داخلية (مثل المكثفات والدوائر التوافقية) تتيح لها توفير هذه القدرة التخيلية محلياً، مما يضمن استقرار عزم الدوران واستمرارية عمل المضخة بكفاءة عالية حتى في ظروف التشغيل القاسية. وخلاصة القول، إن عاكس الضخ الشمسي ليس مجرد محول للطاقة، بل هو منظومة إدارة طاقية متكاملة تجمع بين كفاءة التحويل وحماية الأحمال الحثية وتأمين متطلباتها الفيزيائية الخاصة.
