MAQattan/My-Graduation-Project/GP_Obsidian/Thesis/8/أثر دوران الأرض وميل محورها على استلام الإشعاع.md

تستند هندسة استلام الإشعاع الشمسي إلى فهم الحركتين الأساسيتين لكوكب الأرض؛ حيث ينتج عن دوران الأرض حول محورها تعاقب الليل والنهار، بينما يؤدي دورانها المداري حول الشمس إلى ظاهرة تعاقب فصول السنة الأربعة. ويُعد ميل محور الأرض (Axial Tilt) بمقدار ثابت في الفضاء هو المحرك الفيزيائي لهذه التغيرات، إذ يتسبب هذا الميل أثناء الدوران المداري في اختلاف الزاوية التي يواجه بها كل نصف من نصفي الكرة الأرضية الإشعاع الشمسي، مما يغير من زاوية سقوط الأشعة وكثافتها الطاقية بشكل مستمر.

![[PV-08-03.png]]

### النمذجة الرياضية عبر زاوية الانحراف الشمسي (Declination Angle)

يتم التعبير عن المحصلة الهندسية والزمنية لهذه الحركات الفلكية رياضياً عبر **"زاوية الانحراف الشمسي"** والتي يُرمز لها بالرمز ($\delta$). تُمثل هذه الزاوية علمياً الزاوية المحصورة بين الخط الواصل بين مركزي الأرض والشمس ومستوى خط الاستواء، وتتغير قيمتها ديناميكياً كل يوم من أيام السنة في مدى محصور بدقة بين $+23.45^{\circ}$ (عند الانقلاب الصيفي في النصف الشمالي) و $-23.45^{\circ}$ (عند الانقلاب الشتوي).

![[PV-08-05.jpg]]

وتُعد هذه الزاوية المتغير الزمني الحرِج والحجر الأساس في المعادلات التحليلية لحساب زوايا الإشعاع، حيث تحدد قيمتها اليومية كفاءة الامتصاص الضوئي ومقدار الطاقة المتاحة للمنظومة الكهروضوئية على مدار العام.

### الديناميكية الموسمية لمسار الشمس وزوايا الألواح

يظهر الأثر المباشر لتغير زاوية الانحراف الشمسي ($\delta$) على مسار الشمس الظاهري في السماء، وهو ما يحدد قيم زوايا الميل المطلوبة للألواح الكهروضوئية حسب الفصول. فخلال فصل الصيف، عندما تقترب زاوية الانحراف من حدها الأقصى الموجب، تتواجد الشمس في أعلى ارتفاع لها في السماء (High Altitude)، مما يفرض فيزيائياً وضع الألواح بزاوية ميل صغيرة تقترب من الوضع الأفقي لضمان تعامد الأشعة (حيث تصل زاوية الميل المثالية صيفاً في مدينة حلب إلى حوالي $13^{\circ}$ فقط).

أما في فصل الشتاء، عندما تتحول زاوية الانحراف إلى القيم السالبة، تنخفض الشمس ظاهرياً نحو الأفق وتصبح أشعتها مائلة، مما يتطلب استجابة هندسية مغايرة تتمثل في إمالة الألواح بزوايا كبيرة لمواجهة هذا الانخفاض واستخلاص أقصى طاقة ممكنة من الإشعاع الشتوي.

### تباين طول النهار وساعات الشحن الكهروضوئي

لا يقتصر أثر ميل المحور وزاوية الانحراف على هندسة زوايا السقوط فحسب، بل يمتد ليتسبب في تباين زمني حرج متمثل في تغير طول النهار على مدار العام. وتنعكس هذه الظاهرة مباشرة على ساعات الشحن الفعالة للمنظومة الكهروضوئية؛ حيث تتسع ساعات سطوع الشمس وتتدفق الطاقة بغزارة وبمعدلات زمنية أطول في فصل الصيف، في حين تتقلص نافذة الشحن اليومية بشكل ملحوظ خلال فصل الشتاء نتيجة قصر السطوع الشمسي، وتصل هذه الظاهرة الفيزيائية إلى حدها الأقصى في النطاقات القطبية بناءً على اتجاه ميل الأقطاب.

![[PV-08-04.jpg]]
