MAQattan/My-Graduation-Project/GP_Obsidian/Thesis/8/أنظمة التتبع الشمسي (Tracking Systems).md

تُمثّل المفاضلة الهندسيّة بين أنظمة التتبع الشمسي (Tracking Systems) والأنظمة ذات الزاوية الثابتة (Fixed Systems) أحد القرارات التصميمية الحرجة في هندسة الطاقة المتجددة، حيث ترتكز على موازنة دقيقة بين تحقيق الكفاءة الفيزيائية القصوى وتأمين الجدوى الاقتصادية الاستثمارية للمشروع.

ومن المنظور النظري، يتطلب تعظيم الإنتاجية الطاقية للألواح الكهروضوئية تعديلاً ديناميكياً مستمراً لزاوية الميل لمواكبة التغير اليومي في زاوية الانحراف الشمسي ($\delta$)، وهو ما تحققه أنظمة التتبع عبر تدوير المصفوفة لضمان التعامد المباشر مع الأشعة الساقطة طوال ساعات السطوع الشمسي. وتُصنّف هذه الأنظمة تقنياً إلى نمطين رئيسيين:

1. **الأنظمة أحادية المحور (Single-axis):** وتعمل على تتبع مسار الشمس الظاهري في حركتها اليومية من الشرق إلى الغرب.
    
2. **الأنظمة ثنائية المحور (Dual-axis):** وتتميز بقدرتها على ضبط زاوية التوجيه وزاوية الميل (Tilt Angle) معاً، مما يتيح لها مواءمة التغير في الارتفاع المداري والموسمي للشمس على مدار فصول السنة.

![[PV-04-24.jpg]]

### التعقيدات الهندسية والتحديات التشغيلية (O&M)

على الرغم من التفوق التقني والفيزيائي الواضح لأنظمة التتبع، إلا أن التحليل الهيكلي يشير إلى وجود تعقيدات تشغيلية ومادية كبرى تؤثر على موثوقية النظام؛ حيث يستلزم دمج هذه التقنية تزويد المنظومة بمحركات كهربائية (Motors)، وحساسات ضوئية متطورة (Sensors)، بالإضافة إلى وحدات تحكم رقمية (Digital Controllers) لضبط التتبع الميكانيكي بدقة.

وتنعكس هذه المكونات سلباً على مؤشرين أساسيين:

- **التكلفة الرأسمالية (CAPEX):** حيث تتسبب هذه الملحقات في زيادة حادة وفورية في التكلفة الأولية للمشروع.
    
- **الكفاءة الصافية للقدرة:** حيث تستهلك المحركات وأجهزة التحكم جزءاً طفيلياً (Parasitic Consumption) من الطاقة التي تنتجها الألواح لتأمين حركتها الميكانيكية.

علاوة على ذلك، يبرز تحدي الصيانة الدورية (Maintenance) كعامل حرِج، نظراً لأن وجود الأجزاء الميكانيكية المتحركة يجعل النظام عرضة للتآكل والأعطال المستمرة، مما يرفع من مخاطر الفشل الميكانيكي مقارنة بالهياكل الثابتة التي تفتقر للأجزاء المتحركة وتتسم بالمتانة العالية والتشغيل الخامل.

### التحليل الإنتاجي والمحدودية الاقتصادية

من المنظور الإنتاجي والعملي، توفر أنظمة التتبع زيادة في إجمالي الطاقة السنوية المستخلصة تتراوح بين $10\%$ إلى $15\%$ كحد أقصى مقارنة بالأنظمة الثابتة. وبتحليل هذه النسبة من وجهة نظر اقتصادية (Financial Analysis)، يُلاحظ في معظم التطبيقات القياسية أن التكاليف الإضافية المرتبطة بالتركيب، والتشغيل، والصيانة المستمرة تفوق العائد المادي المتوقع من هذه الزيادة الطاقية، مما يجعل الهياكل الثابتة الخيار الأكثر استدامة وجدوى مالية للمشاريع النمطية.

وخلاصة القول، يقتصر الاعتماد على أنظمة التتبع غالباً على محطات التوليد الكبرى (Utility-Scale Plants) أو ضمن تطبيقات هندسية خاصة؛ ومثال ذلك الاستفادة من ميزة الإمالة الميكانيكية لتفادي أحمال الرياح الشديدة، حيث تقوم وحدات التحكم بإمالة الألواح إلى الوضع الأفقي تماماً (Stow Position) عند استشعار سرعات رياح حرجة لحماية الهياكل من الانهيار الإنشائي، بينما تظل الأنظمة الثابتة هي المعيار الهندسي السائد لبساطتها الهيكلية وجدواها الاستثمارية المتفوقة.

![[PV-08-06.png]]
