MAQattan/My-Graduation-Project/GP_Obsidian/Thesis/8/استراتيجيات تحديد زاوية الميل.md

يخضع القرار الهندسي المتعلق باختيار زاوية تثبيت الألواح الشمسية لمجموعة من المتغيرات التقنية والاقتصادية المعقدة، والتي تتفاوت تفاوتًا جوهريًا باختلاف الطوبولوجيا التشغيلية ونوع المنظومة المستخدمة ونمط ربطها الكهربائي.

### أولاً: الأنظمة المرتبطة بالشبكة الكهربائية والأنظمة الهجينة (On-Grid & Hybrid Systems)

- **المعيار الأساسي للتشغيل:** يتم في هذه الأنظمة اعتماد **زاوية فصلي الربيع والخريف (الاعتدالين)** كمعيار أساسي ومحوري للتشغيل، وهي الزاوية التي تقترب هندسياً من قيمة زاوية دائرة عرض الموقع الجغرافي المستهدف ($\phi$).
    
- **التبرير التقني والاقتصادي:** يرتكز التفضيل الهندسي لزاوية الاعتدالين على البعد الاستثماري للمشروع؛ حيث إن الغرض الرئيسي من بناء الأنظمة المرتبطة بالشبكة هو غرض استثماري بحت يهدف إلى تحقيق أقصى عائد مادي (Financial Return) أو تأمين أعلى قيمة توفير طاقي تراكمي على مدار العام بالكامل. وتضمن هذه الزاوية للمصمم الحصول على ذروة الإنتاجية الطاقية خلال ستة أشهر كاملة من السنة.
    
- **منهجية التعامل مع العجز الشتوي:** بالرغم من أن اعتماد زاوية الاعتدالين قد يتسبب في حدوث عجز طاقي وفصلّي نسبي في معدلات التوليد خلال أشهر الشتاء (نتيجة الانخفاض الطبيعي في شدة الإشعاع الشمسي)، إلا أن هذا النقص لا يُشكل عائقاً تشغيلياً أو خطراً هندسياً على المنظومة. ويعود السبب في ذلك إلى وجود الشبكة الكهربائية العامة أو المولدات الاحتياطية التي تعمل بمثابة **"مأمن طاقي"** ديناميكي يعوض النقص فورياً، مما يمنح مهندس التصميم مرونة كاملة للتركيز على تعظيم الاستفادة الاستثمارية السنوية الإجمالية بدلاً من إجهاد المنظومة وتكبير حجمها لتغطية أحمال الشتاء الحرجة.

### ثانياً: الأنظمة المعزولة عن الشبكة الكهربائية (Off-Grid Systems)

على النقيض من الأنظمة التفاعلية، تتبع الأنظمة المستقلة (المعزولة) استراتيجية تصميمية مغايرة تماماً، حيث ترتكز فلسفتها التشغيلية بالكامل على **"نمط الاستهلاك" (Consumption Profile)** وطبيعة الأحمال المتصلة بالمنظومة لضمان استمرارية التغذية الكهربائية ومنع انقطاع التيار؛ إذ يُمثل أي عجز طاقي في هذه البنية التحتية المستقلة تهديداً مباشراً يؤدي إلى توقف المنظومة بالكامل نتيجة غياب المصدر البديل أو الشبكة الداعمة.

وبناءً على طبيعة الأحمال، يُصنف توجيه زاوية الميل في الأنظمة المستقلة إلى استراتيجيتين رئيسيتين:

#### 1. التوجيه نحو زاوية فصل الصيف (Summer Tilt)

- **النطاق التطبيقي:** يتم اختيار زاوية الميل الصيفية (وهي زاوية ميل صغيرة مقتربة من الوضع الأفقي) حصرياً في المشاريع ذات الأحمال التي تتصف بكونها "صيفية بامتياز".
    
- **الأمثلة الهندسية:** المنازل الصيفية والمجمعات والمنتجعات السياحية التي يرتفع فيها الطلب على الطاقة الكهربائية بشكل مكثف وحاد لتشغيل **أجهزة التكييف (Air Conditioning)**، حيث تتزامن ذروة الحاجة للطاقة مع ذروة وفرة المورد الإشعاعي الصيفي المتاح.

#### 2. التوجيه نحو زاوية فصل الشتاء (Winter Tilt)

- **النطاق التطبيقي:** يتم تفضيل اعتماد زاوية فصل الشتاء—وهي زاوية ميل كبيرة تضمن رفع الألواح وتصل قيمتها هندسياً إلى **45-46 درجة**—في أغلب التطبيقات والمنظومات المستقلة الأخرى لضمان أمن الطاقة واستقرار التغذية.
    
- **التطبيقات الحيوية المستهدفة:**
    
    - **أنظمة إنارة الشوارع:** حيث تواجه المنظومة تحدياً تشغيلياً مزدوجاً يتجلى في قصر ساعات النهار المتاحة لعملية شحن البطاريات، مقابل طول ساعات الليل التي تتطلب تفريغاً مستمراً ومطولاً للطاقة، بالتزامن مع الضعف العام لشدة الإشعاع الشمسي الشتوي.
        
    - **أنظمة التدفئة ومضخات المياه:** وهي تطبيقات حيوية تتطلب تدفقاً طاقياً وتشغيلياً مستقراً وثابتاً على مدار أيام العام بالكامل دون انقطاع.
        
    - **البيوت التقليدية (الخالية من أجهزة التكييف):** تُعمد فيها زاوية الشتاء كخيار تصميمي حاسم لمنع حدوث أي عجز في شحن بنك البطاريات خلال أسوأ الظروف الجوية والمناخية؛ حيث يمتلك فيض الإشعاع الصيفي الكثيف القدرة الفيزيائية الكاملة على تعويض أي نقص في إنتاجية الألواح ناتج عن عدم مثالية زاوية الميل خلال أشهر الصيف، في حين يظل الهدف الأسمى والأولوية القصوى لهندسة النظام هي الحفاظ على استدامة الطاقة وأمن التغذية خلال أشهر الشتاء الحرجة.
