MAQattan/My-Graduation-Project/GP_Obsidian/Thesis/8/التوجيه الجغرافي للألواح (Azimuth - Orientation).md

يُعد **التوجيه الجغرافي** (Orientation)، والمشار إليه زاوياً في الأدبيات الهندسية بـ **"زاوية السمت الشمسي"** (Azimuth Angle)، المتمم الهيدروليكي والفيزيائي لزاوية الميل ($\beta$) في تحديد الكفاءة الإجمالية لاستخلاص الإشعاع الشمسي. وتكمن الوظيفة التصميمية لهذه الزاوية في تحديد الاتجاه البوصلي الدقيق الذي يجب أن تواجهه المصفوفة الكهروضوئية لتتبع مسار الشمس الظاهري في القبة السماوية، مما يضمن استلام أقصى دفق طاقي ممكن على مدار ساعات النهار.

![[PV-08-07.jpg]]

### القواعد الهندسية للتوجيه بناءً على الموقع من خط الاستواء

تستند القاعدة الهندسية الحاكمة لتحديد زاوية السمت إلى الإحداثيات الجغرافية للموقع، وتحديداً موقع المنظومة بالنسبة لخط الاستواء، حيث ينقسم التوجيه إلى استراتيجيتين متناظرتين:

- **نصف الكرة الشمالي (Northern Hemisphere):** ويشمل جغرافياً سوريا، وكافة الدول العربية، ومعظم الكتلة البرية لليابسة؛ حيث تحتم المعايير الهندسية توجيه الألواح نحو **الجنوب الجغرافي تماماً (True South)**.
    
    - _التبرير الفيزيائي:_ يعود السبب في ذلك إلى أن الشمس في النصف الشمالي تميل دائماً بزاوية ظاهرة نحو الجنوب أثناء حركتها الدورية اليومية من الشرق إلى الغرب، مما يجعل الواجهة الجنوبية هي المسار الفيزيائي الوحيد الكفيل بضمان تعامد الألواح مع الحزمة الإشعاعية المباشرة (Direct Beam Radiation) لأطول فترة زمنية ممكنة.
        
- **نصف الكرة الجنوبي (Southern Hemisphere):** ويشمل مناطق مثل جنوب أفريقيا وأجزاء واسعة من أستراليا وأمريكا الجنوبية، حيث تفرض الحسابات الفلكية توجيه الألواح نحو **الشمال الجغرافي تماماً (True North)**.
    
    - _التبرير الفيزيائي:_ يرجع ذلك إلى كون مسار الشمس الظاهري يقع في الجزء الشمالي من القبة السماوية بالنسبة للمراقب الواقع في تلك النطاقات الجغرافية.

### التحليل الفيزيائي والتباين الفصلي

يُظهر التحليل الهندسي لمسار وموقع الشمس أن الالتزام الدقيق ببوصلة التوجيه (جنوباً في النصف الشمالي، وشمالاً في النصف الجنوبي) يكتسب **أهمية مضاعفة وحرجة خلال فصل الشتاء**؛ ففي هذا الفصل، تبلغ الشمس أدنى ارتفاع مداري لها في السماء (Low Altitude) وتميل بزاوية حادة وقريبة من الأفق.

وبناءً عليه، فإن توجيه الألواح لمقابلة مسارها المائل مباشرة يُعد العامل الحاسم لتعويض الضعف الطبيعي الشديد في شدة الإشعاع الشمسي الشتوي، ومنع حدوث انخفاض حاد في إنتاجية القدرة الكهربائية للمنظومة.

### الخصوصية التشغيلية للمناطق المحصورة بين المدارين

تنتقل الحسابات التصميمية إلى مرحلة أعلى من التعقيد عند التعامل مع المنظومات الواقعة في **المناطق المدارية**—وهي النطاقات الجغرافية المحصورة بدقة بين مدار السرطان (شمالاً) ومدار الجدي (جنوباً)؛ حيث يتسم مسار الشمس الظاهري في هذه المناطق بالديناميكية العالية والتأرجح الموسمي، إذ تمر الشمس مباشرة فوق الرأس (السمت الراسي) وتتغير زاوية ميلها بين الشمال والجنوب على مدار العام بناءً على زاوية الانحراف الشمسي ($\delta$).

وفي هذه الحالات الخاصة، يختلف التوجيه الجغرافي الأمثل للألواح ولا يقتصر على اتجاه ثابت واحد، بل يتطلب دراسة محاكاة حاسوبية متقدمة (عبر برمجيات مثل **PVsyst**) لتحسين زاوية السمت، أو الاعتماد على أنظمة التتبع أحادية أو ثنائية المحور لمواكبة التغير المحوري المستمر لمسار الشمس.
