MAQattan/My-Graduation-Project/GP_Obsidian/Thesis/8/العلاقة الرياضية النظرية لزاوية ميل اللوح.md

تُمثل العلاقة الرياضية النمذجة التحليلية والقاعدة الهندسية الأساسية لتحديد زاوية ميل الألواح الكهروضوئية الكفيلة بضمان استخلاص أقصى قدرة إشعاعية ممكنة من المورد الشمسي المتاح. وتكمن الأهمية التصميمية لهذه المعادلة في قدرتها على الربط الديناميكي الدقيق بين المتغيرات الجغرافية الثابتة للموقع والمحددات الفلكية المتغيرة التي تحكم مسار وموقع الشمس بالنسبة للمنظومة.

$$\beta = \phi - \delta$$

#### مكونات النموذج الرياضي

يخضع تطبيق هذه العلاقة الرياضية لترجمة دلالات ثلاثة رموز أساسية تتكامل فيما بينها لتحديد التوجيه الأمثل للمصفوفة الشمسية:

- **$\beta$ (بيتا):** تُعبر عن زاوية ميل اللوح المطلوبة والمقاسة ميكانيكياً بالنسبة للمستوى الأفقي لسطح الأرض.
    
- **$\phi$ (فاي):** تُمثل زاوية دائرة العرض (Latitude) الخاصة بالموقع الجغرافي المستهدف، وهي قيمة ثابتة إحداثياً لا تتغير للمشروع الواحد؛ ومثال ذلك القيمة القياسية لمدينة حلب ($37^{\circ}$) أو مدينة دمشق ($33^{\circ}$).
    
- **$\delta$ (دلتا):** وهي زاوية الانحراف الشمسي (Declination Angle) الفلكية التي تعبر كمياً عن ميل محور الأرض، وتتغير قيمتها ديناميكياً على مدار أيام السنة.

### التحليل الفيزيائي والمواءمة الزمنية للمنظومة

يكشف التحليل الفيزيائي المعمق لهذه العلاقة عن حتمية وجود مواءمة زمنية مستمرة في التصميم التشغيلي؛ فبما أن زاوية دائرة العرض ($\phi$) تمثل ثابتاً جغرافياً للموقع، بينما تتأرجح زاوية الانحراف الشمسي ($\delta$) يومياً وبشكل دوري في المدى المحصور بين $-23.45^{\circ}$ و $+23.45^{\circ}$، فإن المحصلة الرياضية تفرض بالضرورة أن تكون زاوية ميل اللوح المثالية ($\beta$) متغيرة بشكل يومي أيضاً لتحقيق شرط التعامد الفيزيائي مع الشعاع الساقط.

ومن الناحية النظرية، يُعد التغيير اليومي لزاوية الميل الميكانيكية المنهجية الأدق والأعلى كفاءة لتعظيم إنتاجية الألواح. حيث تتقلص قيمة زاوية الميل ($\beta$) في فصل الصيف لتصل إلى أدنى مستوياتها نظراً لارتفاع مسار الشمس في السماء وصولاً إلى ذروتها الفلكية (نتيجة زيادة قيمة $\delta$ الموجبة). وفي المقابل، تزداد قيمة زاوية الميل ($\beta$) تدريجياً خلال فصل الشتاء لمواجهة الانخفاض الظاهري لمسار الشمس نحو الأفق، مما يضمن تعامد الأشعة واستمرار استقرار الكفاءة الطاقية الممتصة.
