MAQattan/My-Graduation-Project/GP_Obsidian/Thesis/8/الفصل الثامن - زوايا ميل الألواح الشمسية وتوجيهها.md

## [[زاوية الميل (Tilt Angle)]] 

## [[محددات الموقع الجغرافي]] 

## [[أثر دوران الأرض وميل محورها على استلام الإشعاع]] 

## [[زاوية الانحراف الشمسي (Declination Angle - $delta$)]] 

## [[العلاقة الرياضية النظرية لزاوية ميل اللوح]] 

## [[أنظمة التتبع الشمسي (Tracking Systems)]] 

## [[حساب الزوايا الموسمية التقريبية]] 

## [[النماذج الرياضية الدقيقة للزاوية المثالية (Optimal Tilt)]] 

## [[استراتيجيات تحديد زاوية الميل]]

## [[التوجيه الجغرافي للألواح (Azimuth - Orientation)]]
