MAQattan/My-Graduation-Project/GP_Obsidian/Thesis/8/النماذج الرياضية الدقيقة للزاوية المثالية (Optimal Tilt).md

تنتقل الممارسة الهندسية في المشاريع الكهروضوئية الاحترافية من الاعتماد على القواعد التقديرية البسيطة والتقريبية إلى استخدام **النماذج الرياضية الدقيقة**، وهي النماذج الأساسية التي تعتمد عليها البرمجيات المتخصصة في محاكاة الأنظمة الشمسية (مثل برنامج **PVsyst**)، وذلك بهدف تقليص المفاقيد الطاقية الناتجة عن زاوية الميل غير المثالية إلى حدها الأدنى وبلوغ نسبة الصفر في الضياعات (**Zero Losses**).

ويُظهر التحليل الحاسوبي المعمق أن الالتزام بزاوية دائرة العرض كزاوية ميل ثابتة ودائمة للمشروع يؤدي غالباً إلى حدوث فاقد طاقي طفيف؛ حيث أثبتت الدراسات التحليلية أن تطبيق زاوية ميل تعادل $37^{\circ}$ لمدينة حلب نتج عنه فاقد فيزيائي قدره $0.1\%$، في حين أدى الاعتماد على الزاوية المثالية المستخرجة من الحسابات الدقيقة والنماذج الرياضية إلى انعدام الفواقد تماماً وتحقيق استغلال كامل للمورد الإشعاعي.

### التصنيف المنهجي لنطاقات دوائر العرض والمعادلات الرياضية

تُصنّف هذه القوانين الرياضية الدقيقة بناءً على الإحداثيات الجغرافية وموقع المنظومة بالنسبة لخط الاستواء، حيث يتم تقسيمها هندسياً إلى ثلاثة نطاقات رئيسية لدوائر العرض ($\phi$) تضمن مواءمة التغير الديناميكي لمسار الشمس:

- **النطاق الأول:** يشمل المناطق الجغرافية الواقعة بين النطاق المداري والقريب من خط الاستواء من $0^{\circ}$ إلى $25^{\circ}$.
    
- **النطاق الثاني:** يغطي المناطق المعتدلة والوسطى الواقعة بين دوائر عرض **$25^{\circ}$ و$50^{\circ}$**.
    
- **النطاق الثالث:** يختص بالمناطق ذات العروض المرتفعة والقريبة من النطاقات القطبية التي تتجاوز **$50^{\circ}$**.

ويوضح الجدول التالي العلاقات الرياضية الدقيقة لحساب زاوية الميل المثالية ($\beta$) حسب الفصول والتوقيتات التشغيلية لكل نطاق جغرافي:

|**نطاق دائرة العرض (ϕ)**|**على مدار العام (Year-round)**|**فصل الشتاء (Winter)**|**فصل الصيف (Summer)**|
|---|---|---|---|
|**$0^{\circ} \rightarrow 25^{\circ}$**|$\beta = (\phi \times 0.84) + 1^{\circ}$|$\beta = \phi + 16^{\circ}$|$\beta = (\phi \times 0.05) + 1^{\circ}$|
|**$25^{\circ} \rightarrow 50^{\circ}$**|$\beta = (\phi \times 0.76) + 3^{\circ}$|$\beta = (\phi \times 0.88) + 19^{\circ}$|$\beta = (\phi \times 0.93) - 21^{\circ}$|
|**$> 50^{\circ}$**|$\beta = (\phi \times 0.66) + 30^{\circ}$|$\beta = \phi \times 0.82$|$\beta = \phi - 24.5^{\circ}$|

### تطبيق عملي

يتضح الفارق الجوهري والدقة التصميمية لهذه النماذج عند تطبيقها عملياً لحساب زاوية الميل المثالية لمدينة درعا خلال التوقيت الصيفي؛ حيث تقع مدينة درعا عند دائرة عرض تعادل **$32.6^{\circ}$ شمالاً**، مما يفرض هندسياً استخدام العلاقة الرياضية المحددة في (السطر الثاني، العمود الثالث) والمخصصة للنطاق الثاني صيفاً.

وبالتعويض المباشر في المعادلة:

$$\beta = (32.6^{\circ} \times 0.93) - 21^{\circ} \simeq 9.3^{\circ}$$

وعند إجراء تحليل مقارن بين هذه النتيجة الدقيقة والقيمة المستخرجة من القواعد التقريبية السابقة (التي حددت زاوية الصيف لمدينة درعا بـ $17.6^{\circ}$)، يبرز فارق زاويّ حاد يصل إلى حوالي **$8^{\circ}$ درجات كاملة** بين الطريقتين، وهو ما يؤكد عدم دقة الحسابات التقريبية في المشاريع الاحترافية.

### الأثر الاستثماري والجدوى الاقتصادية للمنظومة

تكمن الأهمية الاستثمارية والمادية الكبرى لهذه النماذج التحليلية في كونها المرجع البرمجي والهندسي الحاسم لاختيار زاوية التثبيت النهائية للهياكل المعدنية؛ حيث تشير البيانات الفنية والمصادر المعتمدة إلى أن كل **انحراف بمقدار $10^{\circ}$ درجات** عن هذه القيم المثالية المحسوبة حاسوبياً يترتب عليه فاقد فيزيائي مباشر وتراجع في الإنتاجية يقدر بـ **$2.5\%$** من إجمالي طاقة المنظومة المتاحة.

وبناءً على ذلك، فإن الانتقال من بيئة "الزوايا التقديرية" إلى بيئة "النماذج الرياضية الدقيقة" يُمثل الفارق الهندسي الجوهري بين التصميم الهاوي والتصميم الاحترافي، وهو العامل الحاسم لرفع كفاءة الجدوى الاقتصادية وضمان استعادة رأس المال الاستثماري للمشروع (ROI) في أقصر فترة زمنية ممكنة.
