MAQattan/My-Graduation-Project/GP_Obsidian/Thesis/8/حساب الزوايا الموسمية التقريبية.md

تستند بعض الممارسات الهندسية في تصميم المنظومات الكهروضوئية إلى تبسيط الحسابات الرياضية المعقدة لزوايا الميل عبر استخدام قواعد تقديرية (Rules of Thumb) تضمن الحصول على متوسط أداء مقبول خلال فصول السنة المختلفة دون الحاجة لتغيير الزاوية يومياً. وتعتمد هذه القواعد الهندسية السريعة على **زاوية دائرة العرض ($\phi$)** كمرجع أساسي، حيث يتم تعديل ميل اللوح بالزيادة أو النقصان بمقدار ثابت قدره $15^{\circ}$ لمواجهة التغير الموسمي في مسار الشمس الظاهري.

### التحليل الفيزيائي والنمذجة الرياضية للزوايا الموسمية

من الناحية الفيزيائية، تبلغ الشمس أقصى ارتفاع لها في السماء خلال فصل الصيف (High Altitude)، مما يتطلب تقليل زاوية ميل الألواح لتقترب من الوضع الأفقي وتحقق شرط التعامد مع الأشعة الساقطة، ولذلك تُحسب زاوية الميل الصيفية التقريبية وفق العلاقة:

$$\beta = \phi - 15^{\circ}$$

وفي المقابل، تنخفض الشمس نحو الأفق في فصل الشتاء وتصبح أشعتها مائلة، مما يفرض هندسياً زيادة زاوية ميل اللوح لاستقبال الأشعة المائلة بفعالية أكبر، وتُحدد الزاوية الشتوية بالمعادلة:

$$\beta = \phi + 15^{\circ}$$

أما في فصلي الربيع والخريف (الاعتدالين)، فإن مسار الشمس يتوسط الارتفاعين الصيفي والشتوي، وتكون زاوية الميل المثالية مساوية تماماً لزاوية دائرة العرض للموقع الجغرافي المستهدف:

$$\beta = \phi$$

### تطبيق العملي

يظهر التطبيق العملي لهذه القواعد التقديرية بوضوح عند تحليل المواقع الجغرافية المتباينة، وهو ما يمكن إبرازه عبر المقارنة بين النموذجيين التاليين:

- **مدينة حلب:** تقع عند دائرة عرض **$37.2^{\circ}$ شمالاً**، وتبعاً لذلك تبلغ زاوية الميل المتوسطة في فصل الصيف حوالي **$22.2^{\circ}$**، وترتفع لتصل إلى **$52.2^{\circ}$** في فصل الشتاء، بينما تستقر تماماً عند **$37.2^{\circ}$** خلال فترات الاعتدالين.
    
- **مدينة درعا:** بالانتقال إلى منطقة أكثر قرباً من خط الاستواء كمدينة درعا التي تقع عند دائرة عرض **$32.6^{\circ}$ شمالاً**، نجد أن الحسابات الهندسية تفرض زاوية ميل صيفية منخفضة تبلغ **$17.6^{\circ}$** فقط، وتزداد شتاءً لتصل إلى **$47.6^{\circ}$**، في حين تمثل زاوية **$32.6^{\circ}$** الوضع الأمثل خلال فصلي الربيع والخريف.

### الأهمية الاستراتيجية والمفاضلة بناءً على نمط الاستهلاك

تكمن الأهمية الاستراتيجية لهذه الزوايا الموسمية في منح مهندس التصميم مرونة عالية لاختيار الزاوية الثابتة الدائمة للمشروع بناءً على **"نمط الاستهلاك" (Consumption Profile)** وطبيعة الأحمال المرتبطة بالمنظومة؛ فإذا كان المشروع سياحياً أو موسمياً يعمل بكثافة في فصل الصيف فقط، يتم اعتماد زاوية الصيف لتوليد أقصى طاقة ممكنة خلال هذا الفصل.

أما في مشاريع إنارة الشوارع أو المنشآت الحيوية ذات الأحمال الشتوية الدائمة، فيتم تفضيل اعتماد زاوية الشتاء لضمان استقرار التغذية الكهربائية وتحقيق أمن الطاقة تحت أقل ظروف إشعاعية ممكنة على مدار العام.

وخلاصة القول، إن هذه النماذج الرياضية التقريبية تمثل الحل الهندسي والاقتصادي الأمثل للموازنة بين كفاءة استلام الإشعاع الشمسي واستخلاصه من جهة، وبساطة الهياكل الإنشائية الثابتة وانخفاض تكاليفها التشغيلية والرأسمالية من جهة أخرى.
