MAQattan/My-Graduation-Project/GP_Obsidian/Thesis/8/زاوية الانحراف الشمسي (Declination Angle - $delta$).md

تُعرف زاوية الانحراف الشمسي، والتي يُرمز لها هندسياً بالرمز ($\delta$)، بأنها الزاوية الفيزيائية المحصورة بين الخط المستقيم الواصل بين مركزي الأرض والشمس من جهة، ومستوى خط الاستواء الأرضي من جهة أخرى.

وتنشأ هذه الزاوية فيزيائياً نتيجة الحقيقة الهندسية المتمثلة في ثبات ميل محور دوران الأرض حول نفسها في الفضاء أثناء دورانها المداري السنوي حول الشمس؛ فبينما تبدو الشمس وكأنها تتحرك صعوداً وهبوطاً في السماء، فإن التغير الفعلي اليومي في قيمة الزاوية ($\delta$) يعود إلى هذا الميل المحوري الكوكبي الذي يجعل اتجاه سقوط الأشعة يختلف دورياً على مدار العام.

### المدى الرياضي والتغير الموسمي للزاوية

يتراوح المدى الرياضي لزاوية الانحراف الشمسي بدقة بين قيمتين حديتين هما القيمة الصغرى ($-23.45^{\circ}$) والقيمة العظمى ($+23.45^{\circ}$). وتتأرجح قيمة الزاوية ديناميكياً لتصل إلى ذروتها الموجبة ($+23.45^{\circ}$) عند حلول الانقلاب الصيفي في النصف الشمالي، في حين تنخفض تدريجياً لتبلغ الصفر تماماً خلال الاعتدالين الربيعي والخريفي، وتواصل هبوطها حتى تصل إلى أدنى مستوياتها بالسالب ($-23.45^{\circ}$) عند حلول الانقلاب الشتوي.

### النمذجة الرياضية لزاوية الانحراف

تكتسب زاوية الانحراف الشمسي أهمية حاسمة في الحسابات الهندسيّة للطاقة الشمسية؛ لكونها المتغير الزمني الوحيد المسؤول عن تحديد موقع الشمس بدقة. ويتم حساب قيمتها اليومية بالاعتماد على نموذج رياضي يربط الحركة المدارية بالزمن المقاس وفق الترتيب التسلسلي لأيام السنة:

$$\delta = 23.45 \cdot \sin \left[ \frac{360}{365} (d + 284) \right]$$

وتتوزع محددات هذه العلاقة الرياضية على الثوابت والمتغيرات التالية:

- **$\delta$ (دلتا):** القيمة المستهدفة لزاوية الانحراف الشمسي مقدرة بالدرجات القوسية.
    
- **$d$ (ترتيب اليوم):** المتغير المستقل الوحيد في المعادلة، ويمثل الرقم التسلسلي لليوم في السنة البسيطة؛ حيث يبدأ من $d=1$ (في الأول من يناير/كانون الثاني) وينتهي عند $d=365$ (في الحادي والثلاثين من ديسمبر/كانون الأول).
    
- **الرقم 23.45:** ثابت فيزيائي يمثل أقصى ميل لمحور الأرض عن القطب السماوي، وهو الذي يحدد المدى الحدي القياسي لتأرجح الزاوية بين الموجب والسالب.
    
- **الدالة المثلثية ($\sin$):** تُستخدم لتمثيل الطبيعة الدورية والموجية المنتظمة لحركة الأرض حول الشمس، مما يفسر رياضياً انعدام الزاوية عند الاعتدالين ووصولها للذروة عند الانقلابين.

### التحليل التطبيقي والأثر الهندسي في التتبع الشمسي

تتضح الديناميكية الفصلية لهذا النموذج عند تطبيق قيم زمنية متباينة؛ فعند تعويض ترتيب يوم 17 يناير ($d=17$) في العلاقة الرياضية، تنتج قيمة سالبة تعادل حوالي $-20.9^{\circ}$ مشيرةً تقنياً إلى موسم الشتاء. وفي المقابل، ينتج عن تعويض يوم 11 يونيو ($d=162$) قيمة موجبة تقترب من الحد الأقصى لتصل إلى حوالي $+23^{\circ}$ دلالةً على موسم الصيف.

بناءً على هذه المعطيات، تُمثل الزاوية ($\delta$) المكون الديناميكي المتغير في المعادلة التصميمية الأساسية لحساب زاوية ميل اللوح الفضلى:

$$\beta = \phi - \delta$$

وتثبت هذه العلاقة التحليلية أن تعظيم استخلاص الطاقة الكهروضوئية يتطلب—من الناحية النظرية—تعديلاً مستمراً لزاوية ميل الألواح ($\beta$) بشكل يومي لمواكبة التغير المستمر في زاوية الانحراف الشمسي، وهو المبدأ الهندسي الذي قامت على أساسه تقنية أنظمة التتبع الشمسي (Solar Tracking Systems).
