MAQattan/My-Graduation-Project/GP_Obsidian/Thesis/8/زاوية الميل (Tilt Angle).md

تُعرف زاوية الميل (Tilt Angle)، والتي يُرمز لها هندسياً بالرمز ($\beta$)، بأنها الزاوية الميكانيكية المحصورة بين مسطح اللوح الشمسي والمستوى الأفقي للأرض. ويعد تحديد هذه الزاوية بدقة ركيزة أساسية لتعظيم كفاءة الامتصاص والتبادل الطاقي في الخلايا الكهروضوئية.

### التحليل الفيزيائي لمركبات الإشعاع

تستند الجدوى الفيزيائية لضبط زاوية الإمالة إلى مبدأ تعظيم الاستفادة من كثافة الإشعاع الشمسي الساقط؛ فعندما يسقط الإشعاع على سطح اللوح بزاوية مائلة، فإنه يتحلل رياضياً إلى مركبتين رئيسيتين. المركبة الأولى هي العمودية (Vertical Component) التي يتم امتصاصها بفعالية وتتولى إنتاج القدرة الكهربائية، في حين تُمثل المركبة الثانية الموازية (Parallel Component) لسطح اللوح ضياعاً طاقياً مماسياً لا يتم استغلاله في توليد التيار.

### معضلة التثبيت الأفقي والتحليل الرياضي

من هذا المنطلق، تبرز معضلة هندسية عند وضع الألواح بشكل أفقي تماماً على الأسطح، إذ يتسبب ذلك في تشتيت جزء كبير من الطاقة الإشعاعية المتاحة فيزيائياً. على سبيل المثال، إذا سقط شعاع إشعاعي بقيمة $E$ بزاوية قدرها $30^{\circ}$ على لوح موضوع بشكل أفقي، فإن الخلايا لن تستخلص سوى المركبة العمودية للإشعاع الساقط، والتي تعادل نصف القدرة الإشعاعية المتاحة فقط وفقاً للعلاقة الرياضية:

$$E_{\text{vertical}} = E \cdot \sin(30^{\circ}) = \frac{1}{2} \cdot E$$

بينما تتبدد بقية الطاقة الكامنة في الحزمة الإشعاعية كمركبة موازية غير مستغلة تعتمد على جيب التمام ($E \cdot \cos(30^{\circ})$).

### الهدف الهندسي والجدوى الاقتصادية للمشروع

بناءً على هذه المحددات، يتلخص الهدف الهندسي في إمالة اللوح بزاوية ($\beta$) محددة ودقيقة تضمن تعامد الإشعاع الشمسي على مسطح الخلايا قدر الإمكان طوال فترات السطوع. يتيح هذا التوجيه الميكانيكي التقاط كامل الحزمة الإشعاعية المتاحة وتحويلها إلى تيار كهربائي نافع، وهو ما يبرر تقنياً واقتصادياً الاستثمار في تصميم ودراسة هياكل التثبيت الميكانيكية (الشاسيهات) بدلاً من التثبيت الأفقي التقليدي، وصولاً إلى تحقيق أعلى مردود طاقي ممكن من المنظومة الكهروضوئية.

![[PV-08-01.png]]
