MAQattan/My-Graduation-Project/GP_Obsidian/Thesis/8/محددات الموقع الجغرافي.md

يمثل الموقع الجغرافي المتغير الأول والحاسم في هندسة المنظومات الكهروضوئية، إذ لا يمكن تعميم زاوية ميل موحدة لمشاريع تقع في نطاقات جغرافية متباينة نظراً لاختلاف زوايا سقوط الإشعاع الشمسي باختلاف الإحداثيات. ويتم رصد ملامح الموقع بدقة عبر تقاطع نظامين شبكيين هما خطوط الطول ودوائر العرض، واللذان يتمايزان وظيفياً بشكل جذري في الحسابات الهندسيّة والتصميمية.

![[PV-08-02.jpg]]

### خطوط الطول والتوقيت الزمني (Longitude)

تمتد خطوط الطول تقنياً بين القطبين الشمالي والجنوبي بواقع 360 خطاً وهمياً يتوسطها خط غرينيتش (Prime Meridian) كمستوى مرجعي صفري. ويقتصر الدور الوظيفي لهذه الخطوط على تنظيم النطاقات الزمنية وتحديد التوقيت المحلي للمنطقة الجغرافية المدروسة، حيث تتطابق الساعات الزمنية في الدول الواقعة على خط الطول ذاته، دون أن يكون لها تأثير فيزيائي مباشر على قيم كثافة الإشعاع أو حسابات زاوية الميل الميكانيكية للألواح.

### دوائر العرض والركيزة الفيزيائية للميل (Latitude)

في المقابل، تُعد دوائر العرض—التي يُرمز لزاويتها هندسياً بالرمز ($\phi$)—هي الحجر الأساس والركيزة الفيزيائية التي تُبنى عليها كافة حسابات زاوية الميل ($\beta$). ويتخذ هذا النظام من خط الاستواء مستوى صفرياً مرجعياً يقسم الكرة الأرضية إلى نصفين، تتراوح فيه قيم الزوايا بين $0^{\circ}$ و $90^{\circ}$ في النصف الشمالي، وبين $0^{\circ}$ و $-90^{\circ}$ في النصف الجنوبي.

تكتسب دوائر العرض أهميتها الحرجة في التصميم الكهروضوئي لكونها عنصراً جوهرياً وثابتاً في العلاقات الرياضية التحليلية المستخدمة لتحديد التوجيه الأمثل للمصفوفة؛ إذ ترتبط زاوية ميل اللوح ارتباطاً مباشراً بموقع المنشأة بالنسبة لخط الاستواء، مما يجعل تحديد دائرة عرض الموقع بدقة خطوة إلزامية لضمان محاذاة الألواح بزاوية تضمن التقاط الحد الأقصى من المورد الشمسي المتاح على مدار فصول السنة.
