MAQattan/My-Graduation-Project/GP_Obsidian/Thesis/9/9 - 1 كابلات الطاقة في المنظومات الكهروضوئية (PV Cabling).md

تُمثل كابلات الطاقة المسارات المادية المسؤولة عن نقل الطاقة الكهربائية عبر المراحل المختلفة للمنظومة الكهروضوئية. يُقسم هذا الفصل الكابلات هندسياً إلى شقّين رئيسيين بناءً على طبيعة التيار المار فيهما والموقع من العاكس الكهربائي: الجانب المستمر (**DC Side**) والجانب المتردد (**AC Side**)، حيث يخضع كل جانب لمعايير تصميمية وظروف تشغيلية مختلفة تماماً.

### التباين الفيزيائي بين كابلات التيار المستمر والمتردد

#### ظاهرة التأثير القشري (Skin Effect)

تُعد ظاهرة التأثير القشري تمايزاً فيزيائياً جوهرياً بين سلوك التيارين المتردد والمستمر داخل الموصلات. عند مرور التيار المتردد (AC)، تولّد التغيرات الزمنية للمجال المغناطيسي تيارات دوامية داخلية تعاكس تدفق التيار الرئيسي عند مركز الموصل، مما يدفع الشحنات الكهربائية للهجرة نحو السطح الخارجي. ينتج عن ذلك توزيع غير متجانس لكثافة التيار، ويُعبر عن عمق اختراق التيار في القشرة السطحية ($\delta$) بالمعادلة التالية:

$$\LARGE \delta = \sqrt{\frac{\rho}{\pi f \mu}}$$

حيث تمثل $\rho$ المقاومية النوعية للمادة، و $\mu$ النفاذية المغناطيسية، و $f$ التردد.
![[PV-09-01.png]]
##### نستنتج من العلاقة
بسبب هذه الظاهرة، تقل مساحة المقطع الفعالة للموصل في دوائر الـ AC، مما يرفع المقاومة الفعالة ($R_{ac} > R_{dc}$) ويتسبب في زيادة المفاقيد الحرارية. في المقابل، تنعدم هذه الظاهرة تماماً في دوائر التيار المستمر (DC) نظراً لثبات الاتجاه والقيمة صفريّة التردد ($f = 0$)؛ حيث تتوزع كثافة التيار بشكل متجانس كامل المساحة المقطعية للموصل، مما يتيح استغلالاً هندسياً كلياً لمعدن الناقل وبمفاقيد أومية أقل لنفس مساحة المقطع.

#### الإجهاد الحراري المستمر (Continuous Thermal Stress)

يخضع عزل كابلات الجانب المستمر (DC) لإجهاد حراري تراكمي يختلف ديناميكياً عن كابلات الجانب المتردد (AC)، وخصوصاً عند مقارنة الأداء عند القيمة العظمى للتيار ($I_{max}$). في دوائر الـ AC، يتغير التيار جيبياً ويمر بنقطة الصفر مرتين في كل دورة موجية، مما يمنح المادة العازلة فترات استرخاء حراري (Thermal Relaxation) متناهية الصغر تسمح بتشتت جزئي للحرارة المتولدة نبضياً.

أما في دوائر الـ DC، يتدفق التيار بقيمته العظمى خطياً وبشكل مستمر دون أي انقطاع أو تذبذب، مما يعني غياب نقاط الصفر تماماً. هذا التدفق المستمر يمنع العازل من الحصول على أي فترات تبريد لحظية، مما يرفع من معدل الاحترار التراكمي في قلب الموصل وفقاً للعلاقة الحرارية الثابتة ($P = I^2 R$). هذا الإجهاد الحراري المتواصل والمكثف يُسرّع من عملية التقادم الفيزيائي للعوازل (Insulation Degradation) ويُقلل من عمرها الافتراضي، مما يفرض هندسياً اختيار مواد عزل ذات متانة حرارية وكيميائية فائقة لكابلات الـ DC (مثل العوازل المخصصة للطاقة الشمسية المتوافقة مع معيار EN 50618) لتتحمل هذه البيئة التشغيلية القاسية مقارنة بكابلات الـ AC.

### كابلات الجانب المستمر (DC Cables)

تغطي هذه الكابلات المسافة الممتدة من الخلايا الكهروضوئية عبر وصلات السلاسل (**Strings**)، وصولاً إلى صناديق التجميع (**Combiner Boxes**) أو المداخل المباشرة لمنظمات الشحن والعواكس.

بسبب طبيعة تركيبها في البيئات المفتوحة، تفرض المواصفات العالمية (مثل المعيار الأوروبي **EN 50618** والمعيار الدولي **IEC 62930**) متطلبات تصنيعية صارمة لكابلات الـ **DC** الشمسية (المعروفة بـ **H1Z2Z2-K**)، وتتمثل في:

- **مادة الموصل (Conductor):** تُصنع من النحاس المرن متعدد الشعيرات، ويُشترط أن يكون **نحاساً مطلياً بالقصدير (Tinned Copper)**. تكمن الأهمية الهندسية للطلاء بالقصدير في مقاومة الأكسدة والتآكل الكيميائي الناتج عن الرطوبة العالية والعوامل الجوية.
    
- **العزل والغلاف الخارجي (Insulation & Sheath):** تُعزل الكابلات باستخدام مادتين من البوليمر المتشابك خالي الهالوجين (**Cross-linked Polyolefin - XLPO**)، ويتم معالجتها بشعاع إلكتروني (**Electron-beam cross-linked**). يوفر هذا العزل المزدوج حماية ميكانيكية فائقة ومقاومة حرارية عالية.

![[PV-09-02.png]]

- **مقاومة الظروف البيئية:** يجب أن تكون الكابلات مقاومة بالكامل للأشعة فوق البنفسجية (**UV Resistant**)، ومقاومة لانتشار اللهب (**Flame Retardant**)، وخالية من الغازات السامة عند الاحتراق (**LSZH - Low Smoke Zero Halogen**).
    
- **الجهد الاسمي:** صُممت هذه الكابلات لتحمل جهود تشغيلية مرتفعة تصل عادة إلى **1.5 kV** تيار مستمر.

### كابلات الجانب المتردد (AC Cables)

تبدأ كابلات الجانب المتردد من مخرج العاكس الكهربائي وتتجه نحو لوحات التوزيع الرئيسية الأقرب، ومنها إلى الأحمال أو نقطة الربط مع الشبكة الكهربائية العامة (**Grid Connection Point**).

تخضع كابلات الـ **AC** لمعايير التمديدات الكهربائية التقليدية داخل وخارج المباني (مثل معايير **IEC 60502-1**)، وتتميز بالخصائص التالية:

- **نوع العزل المتداول:** يُستخدم النحاس أو الألمنيوم كموصلات، وتُعزل غالباً بمادة البولي إيثيلين المتشابك (**XLPE**) كعازل داخلي، ومادة كلوريد البوليفينيل (**PVC**) كغلاف خارجي (مثل كابلات **NYY**).
    
- **ظروف التشغيل الحرارية:** تعمل ضمن درجات حرارة تشغيلية اعتيادية مقارنة بالجانب المستمر، نظراً لأن الجزء الأكبر من مساراتها يكون ممدداً داخل قنوات مخصصة أو مدفوناً أو داخل المباني المحمية من الإشعاع الشمسي المباشر.
    
- **الجهد الاسمي:** تعمل عادة عند الجهود المنخفضة القياسية، مثل **0.6/1 kV**، لتتوافق مع جهود الشبكة ثلاثية الطور (**230/400 V**).

### مقارنة هندسية بين كابلات الـ DC والـ AC

لتلخيص الفروقات الجوهرية والضوابط التصمیمیة التي تمنع الخلط بين هذين النوعين في التطبيق العملي، يُدرج الجدول التالي مقارنة شاملة:

|**وجه المقارنة**|**كابلات التيار المستمر الشمسية (DC Cables)**|**كابلات التيار المتردد (AC Cables)**|
|---|---|---|
|**المعيار القياسي الدولي**|EN 50618 / IEC 62930|IEC 60502-1|
|**مادة الموصل ونوعه**|نحاس مرن مطلي بالقصدير (Tinned Copper)|نحاس أحادي/مجدول أو ألمنيوم|
|**طبيعة العزل الهيكلي**|عزل مزدوج بمادة بوليمر متشابك (XLPO)|عزل أحادي أو مزدوج (XLPE/PVC) أو (PVC/PVC)|
|**مقاومة الأشعة الفوق بنفسجية (UV)**|مدعومة ومضمونة لسنوات طويلة في الهواء الطلق|غير مدعومة إلا في أنواع خاصة ومحدودة جداً|
|**نطاق درجات الحرارة**|واسع جداً (من **40°C-** وحتى **90°C**، وتتحمل **120°C** لفترات قصيرة)|اعتيادي (يصل إلى **70°C** للـ PVC أو **90°C** للـ XLPE)|
|**مقاومة الحريق والغازات**|خالية من الهالوجين منخفضة الانبعاث الدخاني (LSZH)|تعتمد على التطبيق (تطلق غازات حامضية عند احتراق PVC)|

> **تنبيه هندسي حرج:** يمنع منعاً باتاً استخدام كابلات التيار المتردد (AC) التقليدية في تمديدات الجانب المستمر (DC) للمصفوفات الشمسية. إن تعرض كابلات الـ AC للإشعاع الشمسي المباشر يؤدي إلى تفكك غلاف الـ PVC السريع وانهيار العازلية، مما يسبب قصر في الدائرة الكهربائية (**Short Circuit**)، وينشأ عنه قوس كهربائي مستمر (**DC Arc**) يصعب إطفاؤه تلقائياً، وهو المسبب الأول لحرائق المحطات الكهروضوئية.

### المعايير الهندسية الحاكمة في حساب مقاطع الكابلات

لاختيار المقطع العرضي المناسب (**Cross-Sectional Area**) لأي كابل في المنظومة، يجب مراجعة ثلاثة محددات رياضية وفنية أساسية:

1. **السعة الأمبيرية (Ampacity):** قدرة الكابل على تمرير التيار التصميمي الأقصى دون أن تتجاوز حرارة الموصل حده الآمن. يتم الحساب بالاعتماد على جداول الشركات المصنعة مع تطبيق **عوامل التصحيح الحراري والتجميع (Derating Factors)** بناءً على طريقة التمديد (في الهواء، في قنوات، مدفون) ودرجة الحرارة المحيطة بالموقع.
    
2. **هبوط الجهد المسموح (Permissible Voltage Drop):** يُعد هبوط الجهد من مسببات الفقد الطاقي المستمر. تشترط الأكواد الهندسية ألا يتجاوز الفقد في جهد الـ **DC** نسبة **1%** (وفي أسوأ الحالات **2%**)، بينما في جانب الـ **AC** يُفضل ألا يتجاوز **1%** إلى **3%** للحفاظ على استقرار الجهد المنقول إلى الشبكة أو الأحمال.
    
3. **تحمل تيار القصر (Short-Circuit Capacity):** يجب أن يمتلك المقطع العرضي للكابل الكتلة المعدنية الكافية لتحمل التيارات الحرارية الناتجة عن أعطال القصر المفاجئة لفترة زمنية محددة حتى تبدأ أجهزة الحماية بالفصل، وذلك دون أن يذوب العازل.
