MAQattan/My-Graduation-Project/GP_Obsidian/Thesis/9/9 - 2 أجهزة الحماية من التيار الزائد وقواطع الفصل (Overcurrent & Isolation Devices).md

تُمثّل أجهزة الحماية والفصل عصب الأمان في المنظومات الكهروضوئية؛ حيث تعمل على موازنة التشغيل المستمر مع تأمين النظام ضد الأعطال الكارثية. ونظراً للاختلاف الجوهري بين طبيعة التيار المستمر (DC) والتيار المتردد (AC)، فإن لكل جانب اشتراطات هندسية دقيقة تحكم اختيار أجهزة الحماية.

### 9-2-1 مصاهر حماية السلاسل (gPV Fuses)

تُعد المصهرات المصممة وفق الفئة المعيارية **gPV** (طبقاً للمعيار العالمي IEC 60269-6) خط الدفاع الأول عن الألواح الشمسية في الجانب المستمر (DC)، وتتميز بخصائص زمنية وميكانيكية تجعلها قادرة على قطع تيارات القصر المستمرة بفعالية.

![[PV-09-03.jpg]]
![[PV-09-04.jpg]]

#### وظيفتها في الجانب المستمر (DC):
تُثبّت هذه المصاهر على خطوط السلاسل (Strings) في لوحات التجميع (DC Combiner Boxes). وظيفتها حماية السلاسل الشمسية من تيارات الخطأ العكسية (Reverse Fault Currents) التي تتدفق من السلاسل السليمة المربوطة على التوازي نحو سلسلة أصابها عطل قصر، مما يحمي الخلايا من التلف الحراري وخطر نشوب الحرائق.
    
#### خصائص العمل عند التيارات العكسية (Reverse Currents)
في الحقول الشمسية التي تحتوي على ثلاث سلاسل متوازية أو أكثر، إذا تعرضت إحدى السلاسل لعطل (تظليل شديد، أو تلف عزل، أو قصر)، فإن السلاسل السليمة الأخرى تقوم بضخ تيارها بالكامل بشكل عكسي داخل السلسلة المعطوبة. تُصمم مصاهر gPV بحيث تستشعر هذا التيار العكسي الخاطئ، والذي يُرمز له بـ $I_{\text{reverse}}$، وتقوم بفتح الدائرة بسرعة فائقة قبل أن يتجاوز التيار قيمة تحمل التيار العكسي الأقصى للوح الشمسي والمحددة في ورقة البيانات بـ $I_{\text{mrt}}$ (Maximum Reverse Current).

#### البنية الفيزيائية ومبدأ العمل
نظراً لأن تيارات الأعطال في الجانب المستمر للمنشآت الشمسية تكون مقيدة فيزيائياً وقريبة من قيم التشغيل الطبيعية، فإن مصهرات gPV تُصنع بعناصر انصهار فلزية دقيقة (من الفضة أو النحاس) تحتوي على تضييقات هندسية معيرة (Notches). عند سريان تيار عكسي يتجاوز عتبة الفصل الحرجة (تتراوح عادة بين $1.35 \times I_n$ و $1.45 \times I_n$)، ترتفع كثافة التيار بشكل حاد عند هذه النطاقات الضيقة، مما يولد حرارة جولية مركزة ($I^2Rt$) تؤدي إلى صهر المادة وعزل السلسلة المعطوبة بدقة وقبل تضرر الخلايا الكهروضوئية.

>[!info] ملاحظة تصميمية حرجـة:
>  لا تُستخدم المصهرات التقليدية (مثل فئة gG أو aM الخاصة بالشبكات المترددة) في الأنظمة الشمسية مطلقاً؛ لأن تيارات القصر في الألواح الشمسية تكون قريبة من تيارات التشغيل الاعتيادية، ومصاهر gPV هي الوحيدة القادرة على الإحساس بالفروقات الصغيرة جداً والأنحناءات الحرجة لتيار المستمر.
#### تكنولوجيا إخماد القوس الكهربائي المستمر (DC Arc)
يُمثل إخماد القوس الكهربائي المستمر (DC Arc) تحدياً هندسياً كبيراً مقارنة بالقوس المتردد (AC Arc)؛ إذ يمر التيار المتردد جيبياً بنقطة الصفر مرتين في كل دورة، مما يمنح وسط الفصل فرصة طبيعية للتبريد وإخماد الشرارة تلقائياً. بالمقابل، يتميز التيار المستمر بثبات قيمته وغياب نقاط الصفر، مما يجعل القوس المتولد لحظة انصهار الفتيل مستقراً، شديد الحرارة، ومستمر التأين في الفراغ ما لم يتم إخماده قسرياً.

للتعامل مع هذه الظاهرة، تُملأ خرطوشة المصهر بإحكام بـ **رمال الكوارتز (Quartz Sand)** عالية النقاء. ولحظة نشوء القوس الكهربائي، تمتص رمال الكوارتز المحيطة الطاقة الحرارية العالية للقوس وتنصهر، مما يؤدي إلى تبريد بلازما القوس بسرعة فائقة. ينتج عن هذا التفاعل الفيزيائي تشكّل غلاف زجاجي عازل غير متبلور يُعرف بالـ (Fulgurite) يطوق مسار الشرارة، مما يضيق مسار القوس فيزيائياً ويرفع مقاومته الكهربائية إلى حد يمنع تدفق الشحنات، فيجبر القوس المستمر على الانطفاء السريع والآمن داخل جسم المصهر.

![[PV-09-05.png]]

### 9-2-2 قواطع الدورة المصغرة (MCB - Miniature Circuit Breakers)

تُعتبر قواطع الدورة المصغرة من أكثر عناصر الحماية شيوعاً واستخداماً في الدوائر الكهربائية، وتُصنف كمعيار هندسي أساسي في التطبيقات المنخفضة والمتوسطة القدرة.

![[PV-09-06.jpg]]

#### نطاق العمل التشغيلي
تعمل هذه القواطع ضمن نطاق تيار اسمي يتراوح عموماً بين **10 أمبير وحتى 125 أمبير**، وبسعات قطع (Breaking Capacity) تقع غالباً بين 6 كيلو أمبير و 15 كيلو أمبير.
    
#### الاستخدام في الأنظمة الكهروضوئية
تُستخدم قواطع MCB كمعيار هندسي في الجانب المتردد (AC) للمنظومات الصغيرة والمتوسطة (مثل المنظومات السكنية والتجارية الصغيرة). يتم تركيبها مباشرة بعد مخرج العاكس (Inverter AC Output) لتأمين خط الربط الواصل إلى لوحة التوزيع الرئيسية أو الأحمال.
    
#### آلية الحماية
توفر هذه القواطع حماية ثنائية: **حرارية** (عبر مغناطيس ثنائي المعدن بيميتال) للحماية من الأحمال الزائدة المستمرة لفترات طويلة، و**مغناطيسية** لفصل تيار القصر اللحظي بشكل فوري. وفي الغالب يُنصح باختيار منحنى الفصل من النوع (Type C) أو (Type D) لتتحمل التيارات الاندفاعية اللحظية عند بدء تشغيل العاكس.
	
##### الحماية من الحمل الزائد (Overload Protection)
ينشأ الحمل الزائد عن ارتفاع طفيف ومستمر في التيار فوق القيمة الاسمية، مسبباً إجهاداً حرارياً تراكمياً ($I^2 Rt$). تعتمد آلية الفصل على **شريحة ثنائية المعدن (Bimetallic Strip)** مكونة من معدنين بمعاملي تمدد مختلفين؛ تنحني تدريجياً بفعل التدفئة غير المتساوية حتى تحفز ميكانيكية الفصل الميكانيكي.

![[PV-09-07.png]]

تخضع هذه الاستجابة لـ **خاصية الزمن العكسي (Inverse-Time Characteristic)**، حيث يتناسب زمن الفصل عكسياً مع شدة التيار. هذا التأخير الحراري متعمد؛ إذ يسمح للقاطع بتجاوز تيارات البدء العابرة (Inrush Currents)—كشحن مكثفات ترشيح العاكس—دون حدوث فصل زائف، مع ضمان عزل الأحمال الزائدة المستمرة بأمان.
##### تكنولوجيا إخماد الشرارة الكهربائية (Arc Chutes)

لحظة تباعد الملامسات الميكانيكية تحت تأثير تيار القصر، يتأين الهواء في الفجوة الفاصلة نتيجة شدة المجال الكهربائي، مما ينتج عنه قوس كهربائي (Electric Arc) ذو حرارة هائلة قادرة على صهر الملامسات. وللتعامل مع هذه الظاهرة، يتم تصميم مسار الشرارة (Arc runners) بحيث تُجبر الشرارة على التمدد والابتعاد عن نقاط التلامس (Arc Contacts)، وبما أن المقاومة تزداد بزيادة الطول، تضعف شدة الشرارة تدريجياً. يُوجَّه القوس فيزيائياً عبر المسار إلى غرف إخماد الشرارة (Arc Chutes)، والتي تحتوي على صفائح معدنية متوازية ومعزولة تُعرف بمجزئات القوس (Arc Splitters). تعمل هذه الصفائح على سحب القوس وتجزئته إلى أقواس صغيرة متتالية، مما يرفع من مقاومته الفيزيائية ويخفض جهده، ليتم تبريده وإخماده بسرعة فائقة.

![[PV-09-08.png]]

#### منحنيات الخصائص وسعات التيار المعيارية (Characteristics Curves and Standard Ratings)

يُمثل منحنى الخصائص الزمني-التياري (Time-Current Curve) الأداة الهندسية الأساسية لتقييم أداء قاطع الحماية (MCB) وتحديد مواءمته الفنية للمنظومة الكهروضوئية. يُرسم هذا المنحنى على مخطط بياني ذي مقياس لوغاريتمي مزدوج، حيث يُمثل المحور الرأسي زمن الفصل بالثواني، بينما يُمثل المحور الأفقي مضاعفات التيار الاسمي للقاطع ($I/I_n$).

![[PV-09-09.svg]]

1. **منطقة الفصل الحراري (Thermal Trip Zone):** تمثل الجزء العلوي من المنحنى وتتعامل مع **الحمل الزائد (Overload)**؛ وتتميز بعلاقة عكسية حيث يستغرق القاطع زمناً طويلاً (قد يصل لعدة دقائق) لفصل التيارات التي تزيد بنسبة بسيطة عن التيار المقنن ($I_{rated}$)، ويقل هذا الزمن تدريجياً كلما ارتفعت شدة التيار الزائد. وتتبع هذه المنطقة خصائص زمنية عكسية (IDMT) لتمكين المنظومة من تحمل تيارات بدء التشغيل المؤقتة دون فصل مفاجئ.
2. **منطقة الفصل المغناطيسي (Magnetic Trip Zone):** تبدأ عند وصول التيار إلى قيمة حرجة تُعرف بـ **($I_{magnetic}$)**، وتتعامل مع **تيار القصر (Short Circuit)**. في هذه المنطقة، ينحدر المنحنى بشكل رأسي حاد، مما يعني أن القاطع سيفصل الدارة بشكل لحظي (Instantaneous) في زمن فائق الصغر بمجرد وصول التيار إلى **5 إلى 10 أضعاف** التيار المقنن (في قواطع الفئة C الشائعة)، وذلك لحماية العاكس والكابلات من الدمار.

ويؤكد التحليل الفني على ضرورة عدم تجاوز **أقصى تيار يتحمله القاطع** الموضح في نهاية المنحنى؛ لأن مرور تيار يفوق هذه السعة (Breaking Capacity) سيؤدي إلى احتراق القاطع وتلفه فيزيائياً قبل أن يتمكن من أداء وظيفة الفصل.

### 9-2-3 قواطع الحالة المدمجة (MCCB - Molded Case Circuit Breakers)

عندما تتجاوز استطاعة المنظومة الحدود التي تغطيها القواطع المصغرة، يتم الانتقال مباشرة إلى قواطع الحالة المدمجة (MCCB) كحل هندسي متقدم وأكثر متانة.

![[PV-09-10.png]]

#### نطاق الحماية
تبدأ السعات الاسمية لقواطع MCCB عادةً من **100 أمبير وتصل إلى 1600 أمبير**، مما يجعلها الخيار المثالي للمنظومات الكهروضوئية التجارية الكبيرة والمحطات الشمسية الضخمة (Utility-Scale).
    
#### سعات القصر
تمتاز هذه القواطع بقدرة ميكانيكية وكهربائية عالية على تحمل وقطع تيارات قصر هائلة (تتراوح من 25 كيلو أمبير وتتجاوز 100 كيلو أمبير) دون أن تتعرض للتلف الميكانيكي.
    
#### مرونة الضبط
على عكس قواطع MCB الثابتة، تتيح قواطع MCCB للمصمم إمكانية ضبط وتعديل تيار الفصل الحراري $I_t$ وتيار الفصل المغناطيسي $I_m$ (أو عتبة الفصل الإلكترونية في الطرازات الحديثة)، وهو ما يُعرف هندسياً بـ **التنسيق الانتقائي للحمايات (Selectivity / Coordination)**، لضمان أن القاطع الأقرب للعطل هو فقط من يفصل، منعا لانقطاع الطاقة عن كامل المنشأة.

### 9-2-4 قواطع الفصل الميكانيكي (DC Isolators)

تختلف قواطع الفصل الميكانيكي (أو ما يُعرف بمفاتيح العزل) جوهرياً عن قواطع الدورة الآلية؛ فهي لا تحتوي على عناصر استشعار حرارية أو مغناطيسية للفصل الذاتي عند حدوث عطل، بل تُدار يدوياً بالكامل.

![[PV-09-11.jpg]]

#### الفصل اليدوي تحت الحمل (Load-Breaking Capacity)
إن إطفاء التيار المستمر (DC) يمثل تحدياً هندسياً كبيراً بسبب عدم وجود نقطة "العبور الصفرية" (Zero-Crossing) المتاحة في التيار المتردد، مما يؤدي إلى نشوء قوس كهربائي (Electric Arc) عنيف ومستمر عند محاولة فصل الأقطاب. لذا، تُصمم قواطع الفصل الميكانيكي للجانب المستمر وفق فئات استخدام صارمة (مثل DC-PV2) لضمان إخماد القوس الكهربائي الداخلي بأمان وسرعة أثناء الفصل يدوياً وتحت الحمل الكامل.
    
#### الأهمية التشغيلية
تُعد الأداة الأساسية والموثوقة لفنيي التشغيل والصيانة؛ حيث تتيح عزل حقل الألواح الشمسية ذو الجهد العالي عن العاكس بشكل مرئي وميكانيكي كامل قبل البدء بأي أعمال صيانة. كما تمثل أهمية كبيرة لحماية العاكس؛ ففي حال حدوث عطل داخلي بالعاكس أو الحاجة لإجراء فحص طارئ، يتم قطع خطوط الـ DC القادمة من السطح عبر هذا المفتاح لمنع استمرار تدفق الطاقة وتحجيم الأضرار الكهربائية.
