MAQattan/My-Graduation-Project/GP_Obsidian/Thesis/2/الفصل الثاني - الأسس الكهربائية للمنظومة.md

تعد التفرقة بين التيار المستمر (DC) والتيار المتردد (AC) حجر الزاوية في فهم المنظومات الكهربائية، حيث يعتمد نوع التيار بشكل أساسي على سلوك الجهد الكهربائي الذي يدفعه؛ فإذا كان الجهد مستمراً كان التيار مستمراً، وإذا كان الجهد متردداً كان التيار متردداً.

### [[التيار المستمر (Direct Current - DC)]]

### [[التيار المتردد (Alternating Current - AC)]]

### [[العلاقات الرياضية والقيم العملية]]

### [[أنظمة الوجه الواحد (Single Phase) والثلاثة أوجه (Three Phase)]]

### [[أنواع القدرة وحساباتها في أنظمة التيار المتردد]]

### [[الفرق بين القدرة (Power) والطاقة (Energy)]]

## الهيكلية الأحدث
---
### 2.1 مقدمة الفصل (Introduction)

يستعرض هذا الفصل الأسس النظرية والمبادئ الكهربائية الجوهرية التي تشكل البنية التحتية لفهم وتصميم المنظومات الكهروضوئية المتصلة بالشبكة. فالهندسة الكهروضوئية لا تعمل بمعزل عن قوانين القوى الكهربائية التقليدية، بل تمثل تطبيقاً ديناميكياً يربط بين فيزياء التيار المستمر (DC) المتولد عن الألواح الشمسية، وآليات تحويله وعكسه الكهرومغناطيسي ليتوافق مع أنظمة التيار المتردد (AC) ثلاثي الأطوار السائدة في المنشآت الحيوية والشبكة العامة. يهدف هذا التمهيد الرياضي والفيزيائي إلى بناء قاعدة علمية رصينة تتيح للمهندس تحليل تدفقات القدرة (الفعالة وغير الفعالة) وضمان جودة واستقرار الطاقة، تمهيداً للانتقال إلى الحسابات التصميمية والميكانيكية للمشروع.

### 2.2 [[طبيعة الإشارات الكهربائية وتحولاتها في الأنظمة الشمسية (DC & AC Concept)]] 
### 2.3 [[أنظمة الربط والتوزيع الكهربائي]] 
### 2.4 [[تدفق القدرة وتحليل الطاقة]] 

### 2.5 خلاصة الفصل (Summary)

تأسيساً على ما تقدم، يُشكل هذا الفصل الجسر المعرفي الذي يربط بين المفاهيم النظرية البحتة والواقع التنفيذي للمنظومة الشجرية الكهروضوئية. فمن خلال استيعاب الفوارق التشغيلية بين سلوك إشارات التيار المستمر والمتردد، وفهم العلاقات الطورية للجهود والقدرة المعقدة في الأنظمة ثلاثية الأطوار، تم وضع المحددات الصارمة التي تُبنى عليها الاختيارات الهندسية الواقعية.
