MAQattan/My-Graduation-Project/GP_Obsidian/Thesis/2/تدفق القدرة وتحليل الطاقة.md

تتميز ديناميكية تدفق القدرة في شبكات التيار المتردد (AC) ببيئة أكثر تعقيداً مقارنة بأنظمة التيار المستمر (DC)؛ نظراً لوجود فارق زاوية طوري (Phase Shift) بين موجتي الجهد والتيار ناتج عن طبيعة الأحمال المرتبطة بالشبكة. في المنظومات الكهروضوئية المتصلة بالشبكة، يُعد فهم آليات تدفق وتوزيع هذه القدرة ركيزة أساسية لتصميم واختيار العواكس الذكية وتحليل جودة الطاقة (Power Quality) المغذاة للمنشأة.

### 2.4.1 مثلث القدرة الكهربائية (The Power Triangle)

تُقسم القدرة الكهربائية في أنظمة التيار المتناوب إلى ثلاثة مكونات رئيسية ترتبط مع بعضها هندسياً بعلاقة اتجاهية في الفراغ الطوري، ويُعبر عنها بنموذج **مثلت القدرة (Power Triangle)** في المستوي المركب ($S = P + jQ$):

- **القدرة الفعالة أو الحقيقية (Active / Real Power - $P$):**
    
    هي القدرة الفعلية التي تتحول بالكامل داخل أحمال المنشأة إلى شغل ميكانيكي مفيد (مثل دوران المحركات) أو طاقة حرارية (مثل الإضاءة والسخانات). تُقاس بالوات (**W**) ومضاعفاتها الكيلووات (**kW**). في الأنظمة ثلاثية الأطوار، تُحسب رياضياً بالمعادلة:
    
    $$P = \sqrt{3} \times V_{L-L} \times I_L \times \cos(\phi)$$
    
- **القدرة غير الفعالة أو الردية (Reactive Power - $Q$):**
    
    هي قدرة تذبذبية لا تنجز شغلاً ميكانيكياً أو حرارياً مباشراً، ولكنها ضرورية فيزيائياً لبناء وإخماد المجالات المغناطيسية اللازمة لعمل المعدات الحثية (مثل المحركات، والمحولات، وملفات كوابح الإضاءة) أو المجالات الكهربائية في الأحمال السعوية. تُقاس بالفولت أمبير المرتد (**VAR**) ومضاعفاتها الكيلوفار (**kVAR**). وتُحسب رياضياً بالمعادلة:
    
    $$Q = \sqrt{3} \times V_{L-L} \times I_L \times \sin(\phi)$$
    
- **القدرة الظاهرية أو الكلية (Apparent Power - $S$):**
    
    هي المحصلة الاتجاهية الإجمالية الناتجة عن دمج القدرتين الفعالة وغير الفعالة، وتمثل السعة الكلية المنقولة عبر النواقل والمحولات والتي يجب على مصدر التوليد (سواء الشبكة أو العاكس الشمسي) تأمينها للنظام. تُقاس بالفولت أمبير (**VA**) ومضاعفاتها الكيلوفولت أمبير (**kVA**)، وتُحسب رياضياً بالجذر التربيعي لمجموع المربعين:
    
    $$S = \sqrt{P^2 + Q^2} = \sqrt{3} \times V_{L-L} \times I_L$$

### 2.4.2 معامل القدرة ($\cos \phi$) وجدارته الفنية

يُعرف معامل القدرة (**Power Factor - PF**) هندسياً بأنه النسبة بين القدرة الفعالة والمستفاد منها فعلياً إلى القدرة الكلية المسحوبة من المصدر، وهو يمثل رياضيّاً جيب تمام زاوية الإزاحة الطورية ($\phi$) بين الجهد والتيار:

$$\text{PF} = \frac{P}{S} = \cos(\phi)$$

**تبعات انخفاض معامل القدرة على الشبكة:**

عندما تحتوي المنشأة التجارية على أحمال حثية كعامل رئيسي (مثل محركات التكييف المركزي)، تزداد زاوية الطور ($\phi$) مما يؤدي إلى انخفاض معامل القدرة ($\cos\phi$). هذا الانخفاض يترتب عليه تبعات فنية واقتصادية سلبية:

1. **زيادة شدة التيار المار:** لنقل نفس القدرة الفعالية ($P$) عند معامل قدرة منخفض، يضطر النظام لسحب تيار خط ($I_L$) أعلى بكثير.
    
2. **ارتفاع الضياعات الحرارية ($I^2 R$):** زيادة التيار تؤدي إلى ارتفاع الفقد الحراري في الكابلات والمحولات، مما يقلل الكفاءة الكلية لشبكة التوزيع.
    
3. **هبوط الجهد (Voltage Drop):** يتسبب التيار المرتفع في زيادة هبوط الجهد على طول خطوط النقل، مما يهدد استقرار الفولتية عند أطراف الأحمال الحساسة ويفرض غرامات مالية من شركات الكهرباء.

**متطلبات أكواد الشبكة (Grid Codes) ودور العواكس الذكية:**

تفرض أكواد الشبكة الحديثة على محطات التوليد الكهروضوئية ألا تقتصر وظيفتها على حقن القدرة الفعالة ($P$) فقط، بل يجب أن تساهم ديناميكياً في دعم استقرار الشبكة.

تتميز العواكس الذكية الحديثة (Smart Inverters) بقدرتها على التحكم الكامل في إلكترونيات القدرة عبر قواطع الـ **IGBTs**، مما يتيح لها توليد تيار بموجة منزاحة طورياً (متقدمة أو متأخرة) بالنسبة لجهد الشبكة. بناءً على أوامر نظام التحكم أو استجابةً للمتغيرات اللحظية للجهد عبر منحنيات دعم الجهد الديناميكي ($Q(U)$) أو منحنيات ($ \cos\phi(P) $):

- **حقن القدرة غير الفعالة (Injecting Q):** تعمل المحطة كـ (Capacitor Bank) لرفع جهد الشبكة المحلي في أوقات الهبوط.
    
- **امتصاص القدرة غير الفعالة (Absorbing Q):** تعمل المحطة كـ (Inductive Load) لخفض وكبح الارتفاع المفرط في الجهد الذي قد يحدث نتيجة الحقن الكثيف للطاقة الشمسية في أوقات الذروة وظهيرة أيام الصيف.

### 2.4.3 التمييز الهندسي بين القدرة اللحظية والطاقة التراكمية

يُعد التمييز الصارم بين مفهومي القدرة والطاقة ركيزة حسابية أساسية في تقييم الجدارة الفنية والاستثمارية للمشاريع الكهروضوئية؛ حيث يكمن الفارق الجوهري بينهما في إدراج **عامل الزمن**:

- **القدرة (Power):** هي معدل تدفق أو توليد الطاقة في لحظة زمنية معينة (معدل بذل الشغل)، وهي قيمة ديناميكية متغيرة تتأثر لحظياً في الأنظمة الشمسية بشدة الإشعاع الساقط ودرجة حرارة الألواح.
    
- **الطاقة (Energy):** هي المقدار التراكمي الإجمالي للشغل المبذول أو المنتَج على مدار فترة زمنية ممتدة. رياضياً، تُمثل الطاقة بالتكامل المحدود لدالة القدرة اللحظية بالنسبة للزمن:
    
    $$\text{Energy (E)} = \int_{t_1}^{t_2} P(t) \, dt$$
    
    وفي حال ثبات القدرة على مدى فترة زمنية محددة ($t$)، تؤول المعادلة إلى الضرب المباشر: $E = P \times t$.

**مفهوم سعة المنظومة ($kWp$) مقابل إنتاجيتها السنوية ($kWh$):**

بناءً على التمييز السابق، يتم التعبير عن المنظومات الشمسية بمصطلحين مختلفين بنيوياً ووظيفياً:

1. **كيلووات ذروة (Kilowatt-peak - $kWp$):**
    
    هو وحدة قياس السعة أو الاستطاعة الاسمية التصميمية القصوى لمصفوفة الألواح الشمسية (DC Capacity). يتم تحديد هذه القيمة من قبل الشركة المصنعة تحت **شروط الاختبار القياسية (STC)** والتي تفرض شدة إشعاع بمقدار $1000\text{ W/m}^2$، ودرجة حرارة خلايا تبلغ $25^\circ\text{C}$، ومعامل كتلة هوائية $AM = 1.5$. وهي قيمة ثابتة تعبر عن حجم المحطة (مثلاً سعة مصفوفة ألواح مشروعنا البالغة $23.4\text{ kWp}$).
    
2. **كيلووات ساعي (Kilowatt-hour - $kWh$):**
    
    هو وحدة قياس الطاقة الكهربائية الفعلية المحقونة في الشبكة أو المستهلكة من قبل الأحمال على مدار الزمن (AC Generation). وهي القيمة المتغيرة التراكمية التي يتم رصدها عبر العدادات وتُبنى عليها دراسات الجدوى الاقتصادية وحساب فترات استرداد رأس المال للمشروع.

على سبيل المثال، محطة شمسية بسعة اسمية ثابتة قدرها **$23.4\text{ kWp}$** قد تعمل تحت إشعاع شمس حلب ظهراً لتنتج قدرة لحظية حقيقية تبلغ **$20\text{ kW}$** (نتيجة الفقد الحراري والبيئي)، وإذا استقرت هذه القدرة لمدة ساعة واحدة، فإنها تضخ طاقة تراكمية في شبكة البنك مقدارها **$20\text{ kWh}$**، ويتم تجميع هذه القيم على مدار أيام السنة للحصول على الإنتاجية السنوية الكلية للمحطة.
