MAQattan/My-Graduation-Project/GP_Obsidian/Thesis/2/طبيعة الإشارات الكهربائية وتحولاتها في الأنظمة الشمسية (DC & AC Concept).md

تُعد التفرقة بين التيار المستمر (DC) والتيار المتردد (AC) حجر الزاوية في فهم المنظومات الكهربائية وتحليل أداء مخرجاتها؛ حيث يعتمد نوع التيار بشكل أساسي على سلوك واستقطاب الجهد الكهربائي الذي يدفعه في الدائرة. فإذا كان الجهد مستمراً في اتجاه قطبية ثابتة كان التيار مستمراً، وإذا كان الجهد متناوباً تتغير قطبيته دورياً كان التيار متردداً.

تكتسي هذه المفاهيم في منظمات الطاقة الشمسية الكهروضوئية المتصلة بالشبكة أهمية فنية مضاعفة؛ كون المنظومة تُمثل بيئة هجينة ديناميكية تجمع بين توليد طاقة التيار المستمر عند مصفوفات الألواح، وضخ طاقة التيار المتردد لتغذية أحمال المنشأة التجارية أو حقن الفائض في الشبكة العامة.

### 2.2.1 نظام التيار المستمر (Direct Current - DC)

يُعرف التيار المستمر علمياً بأنه التيار الذي يحافظ على **ثبات اتجاه تدفق الشحنات الكهربائية** بمرور الزمن. ومن منظور هندسي، لا يشترط في هذا النظام ثبات الشدة أو القيمة المطلقة دائماً؛ إذ يُصنف السلوك الموجي للتيار المستمر إلى نمطين أساسيين:

- **تيار مستمر نقي (Pure DC):** يتميز بثبات الشدة والاتجاه معاً بمرور الزمن، وهو السلوك النمطي لخرج البطاريات الكيميائية، أو الخلايا الكهروضوئية عند خضوعها لإشعاع شمسي مستقر وثابت تماماً.
    
- **تيار مستمر متموج (Pulsating DC):** يحافظ على اتجاهه الثابت فوق محور الصفر (موجب دائماً)، لكن قيمته اللحظية تتغير بشكل نبضي أو تموجي بمرور الزمن، مثل الخرج المباشر لدوائر التقويم غير المرشحة (Rectifiers)، أو مخرجات الألواح الشمسية عند تعرضها لتغيرات سريعة في شدة الإشعاع أو تأثيرات الظلال المتحركة.

**القياس والقيمة المتوسطة (Average Value):**

في أنظمة التيار المستمر، لا يُعول فنيّاً على القيم اللحظية العظمى أو الصغرى للجهد، بل يتم الاعتماد على **القيمة المتوسطة (Average Value)** كمعيار أساسي لتقييم الأداء ونقل القدرة. رياضياً، نظراً لأن الإشارة الكهربائية تمثل دالة متصلة تحتوي على عدد لا نهائي من النقاط الزمنية، يتم استبدال المجموع الجبري بالتكامل المحدود لحساب المتوسط الدقيق خلال فترة زمنية دورية ($T$):

$$V_{avg} = \frac{1}{T} \int_{0}^{T} v(t) \, dt$$

### 2.2.2 نظام التيار المتردد (Alternating Current - AC)

يتميز التيار المتردد بأنه **متغير الشدة والاتجاه** بشكل دوري ومتناظر بمرور الزمن؛ حيث تبدأ الموجة الجيبية النموذجية من نقطة الصفر لتصعد تدريجياً حتى تصل إلى ذروتها الموجبة ($V_{max}$)، ثم تتناقص عائدة إلى الصفر، لتعكس اتجاهها بعد ذلك متجهة نحو ذروتها السالبة ($-V_{max}$) قبل أن تختتم دورتها الكاملة عند الصفر مجدداً.

**إشكالية القياس والقيمة الفعالة (RMS Value):**

عند تحليل أنظمة التيار المتردد، يبرز عائق فني عند محاولة تطبيق مفهوم "القيمة المتوسطة"؛ إذ إن مجموع النصف الموجب للموجة مع النصف السالب خلال دورة كاملة واحدة سيساوي صفراً ($V_{avg} = 0$). وهذا يفسر فيزيائياً لماذا يقرأ جهاز الفولتميتر المخبري قيمة (صفر) إذا تم ضبطه على وضعية قياس التيار المستمر (DC) ووُضع على مصدر تيار متردد.

للتغلب على هذه المعضلة وتحديد الأثر الفيزيائي الحقيقي للموجة (القدرة على بذل شغل ميكانيكي أو حراري)، يُعتمد هندسياً على مفهوم **جذر متوسط المربعات (Root Mean Square - RMS)** والمعروف بـ **القيمة الفعالة** للتيار والجهد. تعبر هذه القيمة عن المقدار المكافئ للتيار المستمر الذي يولد نفس الأثر الحراري عند مروره في المقاومة ذاتها. تترجم هذه العملية رياضياً عبر ثلاث خطوات متسلسلة: تربيع دالة الموجة اللحظية (لتحويل الأجزاء السالبة إلى موجبة)، ثم أخذ المتوسط الحسابي عبر التكامل، يليه أخذ الجذر التربيعي للقيم المتربعة:

$$V_{rms} = \sqrt{\frac{1}{T} \int_{0}^{T} v^2(t) \, dt}$$

**العلاقات الرياضية والقيم العملية:**

في التطبيقات الهندسية المتعلقة بالموجات الجيبية النقية (Pure Sinusoidal Waves)، توجد علاقات قطعية ثابتة ترسم أبعاد الإشارة الكهربائية:

1. **العلاقة بين القيمة العظمى والفعالة:** إن الجهد الاسمي المعتمد في المقابس وشبكات التوزيع منخفضة الجهد (مثل 220V) هو قيمة **RMS** فعالة، في حين أن الجهد الذروي اللحظي ($V_{max}$) يكون أعلى من ذلك ويرتبط بها عبر المعامل $\sqrt{2}$:
    $$V_{max} = V_{rms} \times \sqrt{2}$$
    
1. **جهد القمة للقمة (Peak-to-Peak Voltage):** ويمثل الفارق المطلق الممتد من أقصى ذروة موجبة إلى أقصى قاع سالب للموجة:
    $$V_{p-p} = 2 \times V_{max}$$
    
### 2.2.3 آلية التحويل الديناميكي (DC/AC Conversion Basics)

بما أن المصفوفات الكهروضوئية تنتج تياراً مستمراً (DC) ذو جهد يتأثر صعوداً وهبوطاً بالظروف المناخية، في حين أن شبكة المنشأة التجارية تعمل بنظام التيار المتردد (AC) الجيبي الثابت؛ تبرز هنا الحاجة الفنية إلى العاكس الذكي كجسر ربط تحويلي وديناميكي. تتم عملية العكس الكهربائي داخل النظام الإلكتروني للعاكس عبر مرحلتين رئيسيتين:

1. **مرحلة الرفع والتثبيت (DC/DC Boost Stage):** تتضمن دوائر إلكترونية متطورة (Choppers) تعمل بالتوازي مع خوارزميات تتبع نقطة الاستطاعة القصوى (MPPT)؛ حيث تقوم برفع وتنظيم جهد التيار المستمر القادم من السلاسل الشمسية المتغيرة وتثبيته عند مستوى مرتفع ومستقر يُعرف بـ (DC-Bus Link).
    
2. **مرحلة العكس والموجة الجيبية (Inversion Stage):** يتم فيها استخدام قواطع إلكترونية صلبة فائقة السرعة من نوع الترانزستورات ثنائية القطب ذات البوابة المعزولة (**IGBTs**). يتم التحكم في هذه القواطع عبر تقنية تعديل عرض النبضة (**Pulse Width Modulation - PWM**)، والتي تقوم بتقطيع الجهد المستمر الثابت إلى قطار من النبضات عالي التردد. تمرر هذه النبضات لاحقاً عبر مرشحات ترددية منخفضة (Low-Pass Filters) لتنعيم الإشارة وإخراج موجة جيبية نقية متوافقة تماماً مع تردد الشبكة (50Hz) وجهدها المقنن بأعلى كفاءة تشغيلية ممكنة.
