MAQattan/My-Graduation-Project/GP_Obsidian/Thesis/5/تصنيفات ألواح أنصاف الخلايا (Half-Cut Cells).md

تتنوع تصنيفات ألواح **أنصاف الخلايا (Half-Cut Cells)** في السوق التجاري بناءً على عدد الخلايا المكونة لها وطبيعة التقنيات المدمجة فيها، حيث يتم تمييزها في المواصفات الفنية (Datasheet) بمجموعة من الخصائص الكهربائية والميكانيكية التي تمنحها تفوقاً نوعياً على الألواح التقليدية. وفيما يلي استعراض مفصل لهذه الأنواع وأبرز ميزاتها التنافسية وفقاً للمصادر العلمية المتاحة:

### **تصنيف الألواح من حيث التكوين الهندسي وعدد الخلايا**

تعتمد الشركات المصنعة معايير محددة لعدد أنصاف الخلايا داخل اللوح الواحد، ويتم الإشارة إليها في برامج التصميم الهندسية بصيغة (العدد الكلي × 2) للدلالة على التقسيم العلوي والسفلي. وأهم هذه الأنواع:

1. **لوح 120 نصف خلية:** وهو المشتق من اللوح القياسي ذو الـ 60 خلية كاملة، ويُكتب في المواصفات كـ ($60 \times 2$)؛ حيث يحتوي على 60 نصف خلية في الجزء العلوي و60 في السفلي.
2. **لوح 144 نصف خلية:** وهو المشتق من اللوح ذو الـ 72 خلية كاملة، ويُشار إليه بـ ($72 \times 2$)، ويُستخدم غالباً في المشاريع الكبيرة لزيادة الاستطاعة الخارجة من الموديول الواحد.

### **التصنيف حسب تقنية الامتصاص (Monofacial vs. Bifacial)**

تُظهر بيانات "الداتا شيت" تمايزاً بين جيلين من ألواح أنصاف الخلايا من حيث القدرة على استغلال الإشعاع:

- **الألواح أحادية الوجه (Monofacial):** وهي الألواح التي تستفيد من الإشعاع الشمسي المباشر الساقط على الطبقة العلوية فقط، وتُصنف غالباً كألواح "مونو كريستالين" سوداء اللون لرفع الكفاءة.
- **الألواح ثنائية الوجه (Bifacial):** وهي تقنية متطورة (تكون شفافة غالباً) تسمح للوح بإنتاج الكهرباء من الوجهين؛ حيث يستقبل الإشعاع المباشر من الأعلى، ويمتص الإشعاع المرتد من الأرض (Albedo) من خلال الوجه الخلفي، مما يرفع الكفاءة الكلية لتتجاوز حاجز الـ 22%.

![[PV-05-08.png]]
