MAQattan/My-Graduation-Project/GP_Obsidian/Thesis/7/تحليل الخصائص الكهربائية في (Datasheet) العاكس المعزول.md

يُمثل التحليل الدقيق للبيانات الفنية (Datasheet) الخاصة بالعواكس المعزولة عن الشبكة الركيزة الأساسية لضمان التوافقية بين المكونات وحماية المنظومة من الانهيار المبكر. وتتضمن هذه الوثائق مجموعة من المصطلحات والخصائص الكهربائية التي تُحدد الحدود التشغيلية للجهاز، وكيفية استجابته للأحمال المختلفة في الظروف الواقعية.

وتتصدر **"الاستطاعة الاسمية المستمرة" (Continuous Rated Power)** هذه الخصائص، وهي القيمة التي تُحدد أقصى قدرة يمكن للعاكس تزويدها للأحمال بشكل دائم ومستمر (تصل إلى 12 ساعة في بعض الطرازات) دون أن يلحق به ضرر حراري. أما **"جهد الدخل المستمر" (DC Input Voltage)**، فيرتبط ارتباطاً وثيقاً بجهد بنك البطاريات؛ فالعاكس المصمم ليعمل بجهد اسمي قدره 24 فولت، يمتلك "نافذة تشغيل" تتراوح غالباً بين 19 فولت إلى 33 فولت. وتكمن الأهمية الهندسية لهذا المدى في مراعاة التغير الطبيعي لجهد البطارية؛ حيث ينخفض الجهد عند التفريغ ليصل إلى مستويات دنيا (حوالي 19 فولت) ويرتفع عند اكتمال الشحن، مما يفرض على المصمم عدم ربط العاكس ببطاريات ذات جهد اسمي مختلف (مثل 48 فولت) لتجنب تلف الدوائر الداخلية.

![[PV-07-15.png]]

ويبرز مصطلح **"تيار اللاحمل" (No-load Current)** كمعيار للكفاءة الداخلية للعاكس؛ وهو التيار الذي يسحبه الجهاز من البطاريات لتشغيل دوائره الإلكترونية الذاتية وبقاءه في حالة الاستعداد حتى في حال عدم وجود أحمال متصلة به. وتُعد هذه القيمة (التي تبلغ حوالي 1.5 أمبير في عينات الدراسة) فاقداً طاقياً يجب أخذه في الحسبان عند حساب سعة التخزين الكلية، وهي تشبه في منطقها الفيزيائي استهلاك شاحن الهاتف للطاقة عند بقائه في المقبس دون توصيله بالهاتف.

ومن أكثر المفاهيم حرجاً في التصميم الهندسي هو **"قدرة الذروة" (Peak Power Rating)**، وهي القدرة اللحظية التي يمكن للعاكس توفيرها لفترة زمنية وجيزة جداً (عادة 200 ميلي ثانية أو 0.2 ثانية)، وتكون غالباً **ضعف** الاستطاعة الاسمية (مثلاً 4000 واط لعاكس استطاعته 2000 واط). وتتجلى الضرورة التقنية لهذه الميزة عند تشغيل الأحمال الحثية مثل "المحركات" و"المضخات"، التي تسحب تيار بدء (Starting Current) يتراوح بين 6 إلى 8 أضعاف تيارها الطبيعي نتيجة ظاهرة القصور الذاتي. ويتم تحديد زمن هذه الذروة بدقة لأن الطاقة الحرارية المتولدة داخل العاكس تتبع العلاقة ($E = P \times t$)؛ فبقاء العاكس تحت هذه الاستطاعة العالية لزمن أطول سيؤدي إلى تراكم حراري يُتلف المكونات، بينما يسمح الزمن القصير (0.2 ثانية) بمرور تيار البدء العالي دون رفع حرارة الجهاز إلى مستويات خطرة. وبناءً على ذلك، يُعد فهم هذه المتغيرات أمراً حتمياً للمصمم لضمان عدم احتراق العاكس عند لحظة تشغيل المحركات أو الهدر غير المحسوب للطاقة خلال فترات الخمول.
