MAQattan/My-Graduation-Project/GP_Obsidian/Thesis/7/تصنيف موجات العواكس وتوافقها مع الأحمال.md

يُصنف الخرج الموجي للعواكس الكهربائية في المنظومات المستقلة إلى ثلاثة أنماط رئيسية تتباين فيما بينها من حيث الجودة الطاقية، والمحتوى التوافقي (Harmonics)، والتوافق التشغيلي مع الأحمال الكهربائية، حيث يُعد شكل الموجة المحدّد الأساسي لكفاءة الأداء وسلامة الأجهزة المتصلة.

![[PV-07-09.jpg]]

يتمثل النمط الأول في **"الموجة المربعة" (Square Wave)**، وهي الشكل البدائي الناتج عن عمليات التبديل البسيطة دون استخدام تقنيات تعديل عرض النبضة؛ وتتميز هذه الموجة بتساوي قيمة الجهد اللحظي مع القيمة الفعالة (RMS) وقيمة الذروة (Peak)، حيث تكون جميعها متساوية في المقدار. ومن الناحية الهندسية، تفتقر هذه الموجة إلى التدرج الجيبي، مما يجعلها غنية جداً بالتوافقيات التي تسبب مشاكل حرارية حادة، ولذلك يقتصر استخدام العواكس ذات الموجة المربعة على **"الأحمال المقاومية" (Resistive Loads)** فقط، مثل السخانات الكهربائية وأجهزة التدفئة وبعض أنواع الإنارة البسيطة، حيث تُعد الخيار الأرخص ثمناً والأقل تعقيداً.

![[PV-07-10.webp]]

أما النمط الثاني فهو **"الموجة الجيبية المعدلة" (Modified Sine Wave)**، وهي تطوير تقني للموجة المربعة يتم عبر إنتاج موجة على هيئة "درجات سلم" (Staircase) لتكون أكثر قرباً من الشكل الجيبي القياسي. وبالرغم من تحسن أدائها مقارنة بالموجة المربعة، إلا أنها لا تزال تحتوي على نسبة توافقيات تؤدي لارتفاع درجة حرارة المكونات الداخلية للأجهزة. وتُعد هذه العواكس مناسبة لتشغيل **"المحركات البسيطة"** ذات القدرات المنخفضة مثل المراوح، بالإضافة إلى أحمال الإنارة، لكنها تظهر صعوبة بالغة وقد تؤدي لتلف الأجهزة الأكثر تعقيداً مثل الطابعات الليزرية، ومصابيح الفلورسنت، وأجهزة التلفاز.

ويبرز النمط الثالث والأكثر كفاءة وهو **"الموجة الجيبية النقية" (Pure Sine Wave)**، والتي يتم توليدها باستخدام تقنيات تعديل عرض النبضة (PWM) لإنتاج موجة مطابقة تماماً لموجة الشبكة الكهربائية العامة، حيث ترتبط فيها قيمة الذروة بالقيمة الفعالة وفق العلاقة الرياضية ($V_{peak} = V_{rms} \times \sqrt{2}$). تمنح هذه الموجة استقراراً تاماً للأحمال وتكاد تنعدم فيها التوافقيات الضارة، مما يجعلها الخيار الحتمي والوحيد لتشغيل **"الأجهزة الإلكترونية الحساسة"** مثل الحاسوب المحمول (Laptop)، والثلاجات الحديثة، والمعدات الطبية، وكافة أحمال المنازل المتكاملة. وبالرغم من ارتفاع تكلفتها الرأسمالية، إلا أنها تضمن استدامة المعدات وحمايتها من الاحتراق الناتج عن الإجهاد الحراري الذي تسببه الموجات المشوهة. وبناءً على ذلك، تظل عملية اختيار العاكس مرهونة بطبيعة الحمل الكهربائي والموازنة بين التكلفة الاقتصادية وجودة الطاقة المطلوبة لضمان سلامة المنظومة.

![[PV-07-11.png]]
