MAQattan/My-Graduation-Project/GP_Obsidian/Thesis/7/حل معضلة التردد (تقنية الترانزستور IGBT).md

تُمثل معضلة التردد (Frequency) العائق التقني الأول في العواكس البدائية؛ حيث تفرض المعايير الكهربائية العالمية تردداً ثابتاً يبلغ 50 هيرتز (أو 60 هيرتز في بعض الدول)، وهو ما يتطلب فيزيائياً إتمام دورة كاملة تتكون من نصف موجة موجبة ونصف موجة سالبة في زمن دوري ($T$) قدره 20 ميلي ثانية فقط، وفق العلاقة ($T = 1/f$). وتكمن الإشكالية في أن المفاتيح الميكانيكية التقليدية لا تمتلك القدرة الحركية على الاستجابة لهذه السرعة الفائقة، حيث يلزم تبديل حالة المفاتيح كل 10 ميلي ثانية بدقة متناهية لضمان استقرار التردد، وهو أمر يتجاوز قدرات الأنظمة الميكانيكية. ولتجاوز هذا القصور الهندي، تم الانتقال إلى استخدام أنظمة التبديل الإلكتروني الصلبة، وتحديداً تقنية **ترانزستور الـ IGBT (Insulated Gate Bipolar Transistor)**، والتي أحدثت ثورة في كفاءة العواكس الحديثة.

![[PV-07-04.png]]

وتعتمد الفلسفة التشغيلية للترانزستور في أنظمة القدرة على استخدامه "كمفتاح إلكتروني" (Switch) بدلاً من استخدامه كمضخم (Amplifier)؛ حيث يتم التحكم في مروره للتيار عبر ثلاثة أطراف، منها طرف التحكم المعروف بـ "القاعدة" أو البوابة (Gate)، والذي يسمح بمرور التيار عند استقبال إشارة كهربائية صغيرة جداً (بالملي أمبير) ويقطعه عند غيابها. وقد وقع الاختيار على نوع **IGBT** تحديداً في تصميم العواكس لجمعه بين ميزتين حاسمتين: القدرة العالية على تحمل تيارات وجهود مرتفعة (High Power Rating)، وسرعة التبديل الفائقة (High Switching Frequency) التي تسمح بإجراء مئات بل آلاف عمليات الفتح والإغلاق في الثانية الواحدة دون مجهود ميكانيكي. فمن الناحية الحسابية، لإنتاج تردد قدره 50 هيرتز، يقوم نظام التحكم بإرسال إشارات للترانزستورات لإجراء 100 عملية تبديل في الثانية الواحدة، بينما يرتفع هذا الرقم إلى 120 عملية تبديل للوصول إلى تردد 60 هيرتز.

ويظهر التحليل الهندسي لهذه التقنية أن استخدام الـ **IGBT** لم يحل مشكلة التردد فحسب، بل منح المصممين سيطرة تامة على الزمن الدوري للموجة عبر وحدة التحكم (Controller)؛ فمن خلال تقليل زمن الدورة الواحدة يمكن رفع التردد، ومن خلال زيادته يمكن خفضه بدقة عالية، مما يضمن توافق مخرجات المنظومة الشمسية مع تردد الشبكة الكهربائية العامة أو الأحمال الخاصة. وبناءً على ذلك، يُعد ترانزستور الـ **IGBT** المكون المسؤول عن تحويل التيار المستمر إلى نبضات سريعة ومحكومة زمنياً، مما يشكل الخطوة الأولى والأساسية نحو بناء موجة مترددة تتسم بالجودة والاستقرار المطلوبين في هندسة القوى الكهربائية.

![[PV-07-05.png]]
