MAQattan/My-Graduation-Project/GP_Obsidian/Thesis/7/حل معضلة قيمة الجهد والتحكم بالتردد.md

تُعد مواءمة قيمة الجهد وضبط التردد الركيزتين الأساسيتين لضمان توافق الطاقة الخارجة من العاكس مع المعايير الفنية للأجهزة الكهربائية، حيث يواجه التصميم الأولي للعواكس معضلة انخفاض الجهد المستمد من المصادر الكيميائية (البطاريات) مقارنة بالجهد التشغيلي المطلوب للأحمال.

يتمثل الحل الهندسي لمعضلة قيمة الجهد (Amplitude) في استخدام "المحولات الرافعة للجهد" (**Step-up Transformers**)؛ فبينما تعمل معظم أنظمة البطاريات بجهود منخفضة تبلغ 12 أو 24 أو 48 فولت تيار مستمر، ينتج عن تحويلها المباشر جهد متردد بنفس القيمة المنخفضة (حوالي 46 فولت تيار متردد بعد احتساب المفاقيد)، وهي قيمة لا تكفي لتشغيل الأحمال المنزلية القياسية التي تتطلب 220 فولت. وتكمن الأهمية التقنية للمحول في قدرته على رفع سعة الموجة المترددة للوصول إلى المستوى المطلوب (220 فولت أو 380 فولت للأنظمة ثلاثية الأطوار). ومن الناحية التصميمية، تجب الإشارة إلى أن تقنيات التحكم الإلكتروني (مثل PWM) تمنح القدرة على التحكم في قيمة الجهد بالخفض فقط عبر تقليل نسبة زمن التشغيل (On-time) مقارنة بالزمن الكلي للدورة، ولكنها لا تستطيع فيزيائياً رفع الجهد عن قيمة المصدر الأصلي، مما يجعل وجود المحول الرافعة حتمياً في هذه المرحلة.

![[PV-07-14.png]]

وفيما يتعلق بالتحكم في التردد (**Frequency Control**)، تستند العملية إلى المبدأ الرياضي الذي يربط التردد ($f$) بالزمن الدوري ($T$) للموجة وفق العلاقة ($f = 1/T$). ويتم تنفيذ هذا التحكم عبر "وحدة التحكم" (Controller) التي تدير توقيتات فتح وإغلاق ترانزستورات الـ **IGBT** بدقة متناهية؛ فمن خلال تقليل الزمن المستغرق لإتمام دورة كاملة (نصف موجب ونصف سالب)، يتم رفع التردد ليطابق معيار 60 هيرتز، بينما يؤدي زيادة هذا الزمن إلى خفض التردد ليصل إلى 50 هيرتز أو أقل. تمنح هذه السيطرة الزمنية مرونة عالية للعاكس للعمل ضمن نطاق واسع من الترددات، مما يضمن استقرار أداء المحركات الحثية والأجهزة الإلكترونية الحساسة وتوافقها التام مع مخرجات المنظومة الشمسية. وبذلك، فإن التكامل بين المحول الرافعة ووحدة التحكم الزمنية يمثل المنهجية العلمية لتحويل تيار البطاريات المنخفض والثابت إلى موجة سينوسيدال قياسية بتردد وجهد مستقرين.

![[PV-07-08.png]]
