MAQattan/My-Graduation-Project/GP_Obsidian/Thesis/10/Draft 1.md

لدي بنك استطاعته 90.84 kW ، عامل استطاعته PF = 0.85

نذهب لموقع Global Solar Atlas ومن الخريطة نحدد مدينة حلب فنحصل على القدرة الكهربائية النوعية الناتجة عن الألواح خلال اليوم والسنة 

Specific photovoltaic power output :

PVOUT specific = **4.740** kWh/kWp per day

PVOUT specific = **1730.0** kWh/kWp

كما نجد قيمة للاشعاع الشمسي السنوي لحلب (وهو كمية الشعاع الشمسي الساقط على واحد متر مكعب خلال اليوم أو السنة **على سطح افقي**):

Global horizontal irradiation : 

GHI = **5.289** kWh/m2 per day

GHI = **1930.4** kWh/m2

$$
\text{Specific Yield (PVOUT)} = \text{Irradiation (GTI)} \times \text{Performance Ratio}
$$

Optimum tilt of PV modules : OPTA = **31 / 180**°

ونلاحظ أن زاوية الانحراف لمحافظة حلب مساوية تماما للزاوية التي حسبناها بالطريقة الدقيقة (في الفصل الثامن)، كما أن زاوية توجيه الألواح هنا 180 بالنسبة للشمال (حيث الموقع يعتبر أن الشمال هو الزاوية 0) وكما ذكر أنفا المناطق التي تقع شمال خط الاستواء توجه فيها الألواح بالتجاه الجنوب والعكس بالعكس.

ونجد أيضا ارتفاع تضاريس محافظة حلب عن سطح الماء : 

Terrain elevation : ELE = **377** m

---

تمثل قيمة GHI الإشعاع الشمسي السنوي الساقط على سطح أفقي، وهي تعكس الخصائص المناخية للموقع بدقة، إلا أنها لا تعبر بشكل مباشر عن الطاقة المستقبلة من قبل الألواح الشمسية، نظراً لاختلاف زاوية ميلها واتجاهها، لذلك يتم استخدام الإشعاع على مستوى سطح الألواح (Plane of Array Irradiation (POA) أو GTI (Global Tilted Irradiation)) في حساب إنتاج الطاقة، حيث هذه القيمة التي يعتمد عليها في حساب الانتاج النوعي للنظام PVOUT.

>[!info]
> 
> ## ChatGPT
> 
> ---
> 
> ![[PV-10-02.png]] 
> 
> فيما يلي صياغة أكاديمية متكاملة يمكنك وضعها مباشرة في مشروعك، وتشمل تفسير القيم والعلاقات بينها بشكل واضح ودقيق:
> 
> ---
> 
> ## **تحليل بيانات الإشعاع الشمسي باستخدام Global Solar Atlas**
> 
> تم الحصول على بيانات المورد الشمسي لموقع المشروع (مدينة حلب) بالاعتماد على منصة Global Solar Atlas، والتي توفر معلومات مناخية دقيقة مبنية على قواعد بيانات عالمية. وتشمل هذه البيانات القيم الأساسية التالية:
> 
> - **GHI (Global Horizontal Irradiation)**: الإشعاع الشمسي الكلي الساقط على سطح أفقي، ويُعبّر عن الخصائص المناخية العامة للموقع.
> - **GTI (Global Tilted Irradiation)**: الإشعاع الشمسي الساقط على سطح مائل بزاوية محددة.
> - **PVOUT**: الإنتاج السنوي المتوقع من النظام الكهروضوئي لكل وحدة استطاعة مركبة.
> - **زاوية الميل المثلى (Optimum Tilt Angle)**: الزاوية التي تحقق أعلى استقبال للإشعاع الشمسي على مدار السنة.
> 
> ---
> 
> ## **الإشعاع الشمسي على السطح الأفقي والمائل**
> 
> تُظهر البيانات أن قيمة الإشعاع الشمسي على السطح المائل عند الزاوية المثلى (GTI opta) تبلغ:
> 
> $$
> GTI = 2184.8 \text{ kWh/m}^2/\text{year}
> $$
> 
> تمثل هذه القيمة كمية الطاقة الشمسية السنوية التي تستقبلها الألواح الشمسية عند تركيبها بزاوية الميل المثلى (حوالي 31° واتجاه جنوبي 180°)، وهي بذلك تعكس **الإشعاع الفعلي المتاح لتحويله إلى طاقة كهربائية**. في المقابل، فإن قيمة **GHI** تمثل الإشعاع على سطح أفقي، وهي أقل من GTI بسبب عدم توجيه السطح نحو الشمس بشكل مثالي. والجدير بالذكر أن الإشعاع الشمسي على مستوى الألواح (Global Tilted Irradiation – GTI) يتضمن مجموع مكونات الإشعاع الشمسي، بما في ذلك الإشعاع المباشر (Direct Beam)، والإشعاع المنتشر(Diffuse)، بالإضافة إلى الإشعاع المنعكس من سطح الأرض(Albedo)، مما يجعله المؤشر الأكثر دقة لتقدير الطاقة المستقبلة من قبل الألواح الشمسية.
> 
> ---
> 
> ## **العلاقة بين الإشعاع والإنتاج الكهربائي**
> 
> لتحويل الإشعاع الشمسي إلى طاقة كهربائية، يجب أخذ كفاءة النظام بعين الاعتبار، والتي يتم التعبير عنها بمعامل الأداء (Performance Ratio – PR).
> 
> تعطى العلاقة الأساسية كما يلي:
> 
> $$
> \text{Specific Yield} = GTI \times PR
> $$
> 
> حيث:
> 
> - **GTI**: الإشعاع الشمسي على مستوى الألواح
> - **PR**: معامل الأداء، ويأخذ بعين الاعتبار جميع خسائر النظام
> 
> ---
> 
> ## **العلاقة بين PVOUT و GTI و PR**
> 
> تعرف قيمة **PVOUT** بأنها الإنتاجية النوعية للنظام، أي كمية الطاقة المنتجة لكل 1 kWp من الاستطاعة المركبة، ويمكن التعبير عنها بالعلاقة التالية:
> 
> $$
> PVOUT = GTI \times PR
> $$
> 
> وبالتالي:
> 
> - **GTI** يمثل الطاقة الشمسية المتاحة
> - **PR** يمثل كفاءة تحويل هذه الطاقة إلى كهرباء، وتعتمد قمته على كفاءة المكونات، درجة الحرارة، الظلال، دقة التصميم.
> - **PVOUT** يمثل الناتج النهائي (الطاقة الكهربائية)
> 
> ---
> 
>>[!quote]
> >
> >## **تفسير القيم عملياً**
> >
> >إذا كانت:
> >
> >$$
> >GTI = 2184.8 \text{ kWh/m}^2/\text{year}
> >$$
> >
> >وبفرض:
> >
> >$$
> >PR ≈ 0.75
> >$$
> >
> >فإن:
> >
> >$$
> >PVOUT ≈ 2184.8 \times 0.75 ≈ 1638 \text{ kWh/kWp/year}
> >$$
> >
> >وهي قيمة منطقية وتعكس أداء نظام شمسي مصمم بشكل جيد في منطقة حلب.
> >
> 
> 
> ---
> 
> ## **ملاحظات مهمة**
> 
> 1. **قيمة GTI لا تتضمن أي خسائر**، بل تمثل الإشعاع الخام على الألواح.
> 2. **قيمة PVOUT تتضمن الخسائر**، حيث يفترض الموقع معامل أداء قياسي يقارب 0.75.
> 3. تختلف القيمة الفعلية لـ PVOUT في الواقع حسب:
>     - جودة المكونات
>     - درجة الحرارة
>     - الظلال
>     - دقة التصميم
> 
> ---
> 
> ## **دور برامج المحاكاة**
> 
> على الرغم من دقة البيانات المقدمة من Global Solar Atlas، إلا أنها تعتمد على افتراضات عامة، لذلك يتم استخدام برامج متخصصة مثل PVsyst للحصول على نتائج أكثر دقة، حيث تأخذ بعين الاعتبار جميع تفاصيل النظام الفعلي، بما في ذلك الخسائر الحرارية، وخسائر التوصيل، وتأثير الظلال.
> 
> ---
> 
> يتم حساب عدد ساعات الذروة الشمسية (PSH) اعتماداً على الإشعاع الشمسي الساقط على سطح الألواح (GTI) بتقسيم قيمتها السنوية على عدد أيام السنة، أول بتبديل لخيار (Per day) من داخل الموقع (حيث أن الموقع يوفر زر بالجانب للتبديل من السنة لليوم والعكس) وإن هذا المؤشر يمثل عدد ساعات الإشعاع المكافئة عند شدة 1000 واط/م². وحينها لحساب القدرة اليومية للمنظومة نعتمد على القانون :
> 
> $$
> \text{PV Power (System Size)} = \frac{\text{Total Required Energy per Day (Daily Load)}}{PSH \times \eta}
> $$
> 
> كما يمكن الاعتماد على الإنتاجية النوعية (PVOUT) في حساب عدد ساعات الإنتاج الفعلي للنظام (PSH) وذلك بتقسيم قيمة PVOUT على عدد أيام السنة، إلا أن هذه القيمة تأخذ بعين الاعتبار خسائر النظام، وبالتالي فهي تمثل ساعات التشغيل المكافئة للنظام وليس الإشعاع الشمسي الحقيقي. وبالتالي لست بحاجة لاضافة الكفاءة في القانون السابق لأنك اعتمددت على الكفاءة التي اعتمدها موقع Global Solar Atlas داخل PVOUT، أي يصبح القانون السابق كالتالي: 
> 
> $$
> \text{PV Power} = \frac{\text{Total Required Energy per Day (Daily Load)}}{PSH_{eff}}
> $$
> 
> أو بستطاعتنها حساب قدرة النظام المطلوب بالعتماد على قيمة الطاقة النوعية المكافئة للعام من العلاقة التالية:
> 
> $$
> \text{PV Power} = \frac{\text{Total Require Energy per Year}}{\text{Specific Yield (PVOUT)}}
> $$
> 
> >[!quote]
>> 
>> في حال أردت معرفة قيمة الكفاءة التي يعتمدها موقع Global Solar Atlas من العلاقة التالي :
>> 
>> $$
>> \eta = \frac{PVOUT}{GTI} =\frac{1730.0}{2184.8}=0.791
>> $$
> 
> 
> ---
> 
> ## **خلاصة**
> 
> يمكن تلخيص العلاقة بين القيم المدروسة كما يلي:
> 
> - **GHI** → الإشعاع الشمسي العام للموقع
> - **GTI** → الإشعاع الفعلي على الألواح بعد تحديد الزاوية
> - **PR** → كفاءة النظام
> - **PVOUT (Specific Yield)** → الإنتاج الكهربائي النهائي
> 
> $$
> GHI \rightarrow GTI \rightarrow PVOUT
> $$
> 
> حيث تمثل هذه السلسلة المراحل المتتالية لتحويل الطاقة الشمسية من إشعاع ساقط إلى طاقة كهربائية منتجة.
