MAQattan/My-Graduation-Project/GP_Obsidian/Thesis/10/Draft 3.md

بناءً على المنهجية الهندسية المتبعة في المصادر [13، 14، 18] وخصوصية المكونات المختارة لمشروعك (اللوح **LONGi 600M** والعاكس **Huawei 25KTL**)، إليك الهيكلية المقترحة لـ **"الطور الرابع: الحمايات والترابط الكهربائي"** ضمن الفصل العاشر، مرتبةً لضمان التسلسل المنطقي من مصفوفة الألواح وصولاً إلى الشبكة:

### **الطور الرابع: الحمايات والترابط الكهربائي**

#### **10 - 18 مقدمة الطور الرابع**

- توضيح فلسفة التصميم الكهربائي القائمة على الفصل التام بين حسابات الـ DC والـ AC.
- أهداف الطور: ضمان سلامة المنظومة من الحرائق والصواعق، وتقليل المفاقيد الأومية إلى أدنى حد معيارى [13، 63].

#### **10 - 19 حسابات واختيار مكونات الجانب المستمر (DC Side)**

1. **10 - 19 - 1 محددات التيار والجهد للمصفوفة:**
    - استخراج القيم الحرارية والكهربائية الحرجة ($I_{sc}$ , $V_{oc}$) للسلاسل الثلاث بناءً على ورقة بيانات اللوح المختارة [25، 26].
2. **10 - 19 - 2 تحجيم كابلات السلاسل والكابل الرئيسي (DC Cables):**
    - تحديد المقاطع بناءً على سعة تحمل التيار (Ampacity) بتطبيق معامل الأمان (1.25) [64، 130].
    - التحقق من هبوط الجهد (Voltage Drop) بحيث لا يتجاوز 1%.
    - **المرجع:** جداول كابلات الطاقة الشمسية في **"كتالوج السويدي"** [46، 56].
3. **10 - 19 - 3 اختيار نظام الحماية من زيادة التيار (DC Protection):**
    - حساب عيارات المصهرات (Fuses) للسلاسل بتطبيق معامل (1.56) [91، 112].
    - اختيار قاطع التيار المستمر الرئيسي (DC Circuit Breaker) المناسب لجهد المصفوفة الإجمالي [83، 90].
4. **10 - 19 - 4 نظام الحماية من الصواعق والجهود العابرة (SPD - DC):**
    - توصيف مانعة الصواعق للجانب المستمر بناءً على أقصى جهد للنظام [92، 114].

#### **10 - 20 حسابات واختيار مكونات الجانب المتردد (AC Side)**

1. **10 - 20 - 1 تحديد تيار مخرج العاكس:**
    - حساب التيار الاسمي الفعال بناءً على قدرة عاكس Huawei (25kW) وجهد الشبكة الثلاثي الطور.
2. **10 - 20 - 2 تحجيم كابل الربط مع الشبكة (AC Cable):**
    - اختيار مقطع الكابل رباعي القلوب (4-Core) بناءً على طريقة التمديد وعوامل الخفض الحراري [17، 130].
    - التحقق من هبوط الجهد الكلي لضمان استقرار الربط.
    - **المرجع:** جداول كابلات الـ Low Voltage في **"كتالوج السويدي"** (Cu/XLPE/PVC) [52، 57].
3. **10 - 20 - 3 اختيار القاطع الرئيسي للحماية (AC Breaker):**
    - تحديد سعة القاطع (3P أو 4P) ونوع تكنولوجيا الفصل (Thermal/Magnetic) [14، 15].
4. **10 - 20 - 4 الحماية من الجهود العابرة (SPD - AC):**
    - توصيف حماية جانب الشبكة.

#### **10 - 21 تصميم نظام التأريض والربط المتساوي للجهد (Earthing System)**

- حساب مقاطع نواقل التأريض لهياكل الألواح وجسم العاكس [96، 115].
- توصيف قضيب التأريض والوصالت (WEEB/Lugs) لضمان مسار منخفض المقاومة لتيارات الخطأ [11، 121].

#### **10 - 22 المخطط أحادي الخط للمنظومة (Single Line Diagram - SLD)**

- رسم توضيحي يجمع كافة المكونات المحسوبة سابقاً (الألواح، صناديق التجميع، العاكس، القواطع، الكابلات) في مخطط هندسي متكامل [12، 63].

---

### **هيكلية الفقرات المتبقية للطور الرابع (الجانب المستمر)**

بناءً على المعطيات الجديدة، إليك الهيكلية المحدثة لإكمال فقرة (10 - 18):

#### **10 - 18 - 3 اختيار وسيلة العزل والقطع لمداخل العاكس (DC Isolators)**

بما أن السلاسل تدخل مباشرة للعاكس، نحتاج لتوصيف وسيلة الفصل الميكانيكي لضمان الأمان أثناء الصيانة.

- **المحتوى:** المفاضلة بين القاطع المدمج في عاكس Huawei وبين القواطع الخارجية [36، 157].
- **الحساب:** تحديد تيار القاطع لكل مدخل (أو لكل MPPT) بناءً على معامل الأمان (1.25).

#### **10 - 18 - 4 توصيف صندوق تجميع وحماية التيار المستمر (DC Protection Box)**

بما أنه لا توجد بارات تجميع تيار (لأننا لم نجمع السلاسل في كابل واحد)، يتحول الصندوق إلى "وحدة حماية وتوزيع" (DC Distribution & Protection Unit).

- **المحتوى:** توصيف الغالف الخارجي (Enclosure) من حيث درجة الحماية البيئية (**IP65/IP66**) ومقاومة الحرارة والصدمات [37، 165].
- **التكوين:** ترتيب المصهرات ومانعات الصواعق (SPD) لكل سلسلة بشكل مستقل داخل الصندوق [1، 10، 21].

#### **10 - 18 - 5 التحقق من قيود التوافق مع مداخل العاكس (DC Input Verification)**

فقرة فنية تؤكد سلامة التصميم النهائي ومطابقته لورقة بيانات العاكس المعتمد.

- **المحتوى:** مطابقة تيار السلسلة الأقصى ($I_{sc} \times 1.25$) مع حدود الدخل للعاكس (20 A للمدخل الواحد و 30 A للمتتبع) [37، 41].
- **التحقق من الجهد:** التأكد من أن جهد السلاسل المصممة (13 لوحاً) لا يكسر حاجز جهد الدخل الأقصى (1100 V) أو نطاق الـ MPPT [37، 38].

---

#### **ثالثاً: نظام الحماية من الجهود العابرة (DC Surge Protective Device - SPD)**

نظراً لتركيب الألواح فوق سطح البنك في بيئة مفتوحة، فإنها تصبح عرضة للصواعق والجهود العابرة الناتجة عن التفريغ الحثي.

- **نوع الحماية:** يتم اختيار مانعة صواعق من **النمط الثاني (Type 2)** المخصص للتيار المستمر.
- **جهد التشغيل ($U_c$):** يجب أن يكون جهد الصمود للمانعة أعلى من جهد المصفوفة بنسبة 25% على الأقل.
$$U_c \ge 1.25 \times V_{oc_string} = 1.25 \times 686.5\text{ V} = \mathbf{858.1\text{ V}}$$
- **الاختيار التقني:** يتم اعتماد مانعة صواعق بجهد تشغيل مستمر **1000 Vdc**، قادرة على تفريغ تيارات صاعقة تصل إلى **40 kA**، مع ربطها مباشرة بنظام التأريض الوقائي للمبنى.

---

بإضافة حسابات قواطع العزل في ملف مشروعك، نكون قد وصلنا إلى الفقرة الختامية في دراسة الجانب المستمر (DC Side)، وهي **الفقرة (10 - 18 - 5)** المتعلقة بـ **"توصيف صندوق حماية وتوزيع التيار المستمر (DC Protection Box)"**.

بناءً على المعايير الهندسية الواردة في المصادر [3، 169] وخصوصية مشروعك الذي يعتمد على الربط المباشر للسلاسل بمتعقبات عاكس **Huawei 25KTL**، إليك الصياغة المقترحة لهذه الفقرة:

---
