MAQattan/My-Graduation-Project/GP_Obsidian/Thesis/9/9 - 3 فلسفة التنسيق والتراتب الرياضي للحمايات (Coordination & Discrimination Logic).md

تُمثّل الانتقائية الكهربائية (Selectivity/Discrimination) الركيزة الأساسية في تصميم حمايات الجانب المستمر (DC Side) للمنظومات الكهروضوئية. ولا تقتصر وظيفة أجهزة الحماية على فصل الأعطال فحسب، بل تمتد لتشمل إدارة "التراتب التشغيلي" للفصل؛ بحيث يتم عزل الجزء المعيب فقط دون التأثير على استمرارية تشغيل الأجزاء السليمة، مما يضمن الحفاظ على معدل الأداء ($Performance\ Ratio - PR$) للمنظومة وحمايتها من الهدر المالي والتشغيلي.

### القواعد الحاكمة لمنع الفصل العشوائي للحمايات (Nuisance Tripping)

عند حدوث عطل كهربائي (كتيار قصر عكسي الناتج عن تظليل شديد أو تضرر أحد الألواح) في سلسلة واحدة ($String$) من المصفوفة، فإن الهدف الهندسي هو حصر العطل داخل هذه السلسلة عبر صهر المصهر ($Fuse$) الخاص بها.

لتحقيق هذا التراتب ومنع القاطع الرئيسي للمصفوفة ($Main\ DC\ Breaker$) من الفصل العشوائي وإطفاء المنظومة بالكامل، يتم اتباع القواعد التصميمية التالية:

- **عزل خطأ السلسلة المنفردة:** يجب أن تكون الخصائص الزمنية-الأمبيرية ($Time-Current\ Curves$) للمصهرات أسرع بكثير من استجابة القاطع الرئيسي عند قيم تيارات الأعطال الموضعية.
    
- **تحمل تيارات العبور الطبيعية:** يجب أن تتحمل مصهرات السلاسل السليمة والقاطع الرئيسي تيارات العبور الطبيعية الناتجة عن التغيرات المفاجئة في الطقس دون أن تفصل كذباً.
    
- **التنسيق التصاعدي:** يُفرض هندسياً أن تخضع سعات الحمايات لعلاقة طردية تصاعدية تبدأ من أدنى نقطة (السلسلة) وتكبر باتجاه النقطة المركزية (العاكس).

### الضوابط الرياضية ومعاملات الأمان وضمان الانتقائية

لترجمة هذه الفلسفة إلى قيم تصميمية عمليّة، يتم الاعتماد على معايير الأكواد العالمية (مثل $NEC\ Art.\ 690$) لضبط المعاملات الرياضية بدقة:
#### 1. سعة فيوز السلسلة المنفردة ($I_{\text{fuse}}$)

يُحسب التيار الاسمي لمصهر السلسلة بناءً على تيار القصر للوح الواحد تحت ظروف الاختبار المعيارية ($I_{\text{sc}}$) وفق العلاقة التالية:

$$I_{\text{fuse}} = I_{\text{sc}} \times 1.56$$

- **تفكيك المعامل الرياضي ($1.56$):** هذا المعامل ليس عشوائياً، بل هو ناتج ضرب عاملي أمان جوهريين:
    
    1. **معامل الحمل المستمر ($1.25$):** لأن النظام الشمسي يعمل لعدة ساعات متواصلة تحت أشعة الشمس، مما يرفع حرارة أجهزة الحماية ويقلل سعتها الفعلية.
        
    2. **معامل تعزيز الإشعاع ($1.25$):** لأخذ ظاهرة انعكاس السحب المتطرفة ($Cloud-edge\ effect$) بعين الاعتبار، حيث يمكن للإشعاع الفعلي أن يتجاوز حاجز $1000 \text{ W/m}^2$ لفترات وجيزة.

    - وبذلك يكون: $1.25 \times 1.25 = 1.5625 \approx 1.56$.

#### 2. سعة القاطع الرئيسي للمصفوفة ($I_{\text{main\_breaker}}$)

يتم تركيب هذا القاطع (أو قاطع الـ $MPPT$) عند مخرج السلاسل المتوازية المجتمعة قبل دخولها إلى العاكس، وتُحسب سعته وفق العلاقة:

$$I_{\text{main\_breaker}} = \left(\sum I_{\text{string}}\right) \times 1.25$$

حيث تُمثّل $\sum I_{\text{string}}$ مجموع تيارات القصر لجميع السلاسل المربوطة على التوازي والمحمية بهذا القاطع (وفي حال الاعتماد على قيم تيار القصر الإجمالي للمصفوفة تصبح الصياغة $I_{\text{sc-total}} \times 1.25$).

>[!info] سبب أخذ معامل أمان واحد 
يُكتفى هنا بمعامل أمان واحد ($1.25$) للحمل المستمر لأن توازي السلاسل يوزع مخاطر الارتفاعات الفجائية، ولضمان وجود فجوة تنسيقية كافية بينه وبين الفيوز.

#### 3. معادلة التيار التصميمي لاختيار الكابلات

لضمان اختيار مساحة مقطع قادرة على تحمل التيارات التشغيلية وأعطال الحمل الزائد دون تخطي الحدود الحرارية للعازل تحت أسوأ الظروف الميدانية، تُستخدم العلاقة الرياضية التالية لتحديد السعة التيارّية الدنيا المعايرة ($I_{cable\_required}$) الواجب مطابقتها مع جداول الشركات المصنعة:

$$I_{cable\_required} = \frac{I_{breaker\_rating}}{f_{derating}}$$

حيث تُعرّف المتغيرات كالتالي:

- **$I_{cable\_required}$**: السعة التيارّية الاسمية الدنيا المطلوبة للكابل تحت الظروف القياسية للكتالوج.
    
- **$I_{breaker\_rating}$**: التيار الاسمي المقنن لقاطع الحماية المختار ($I_n$) والذي يحمي هذا الكابل.
    
- **$f_{derating}$**: معامل التصحيح الإجمالي المتراكم، ويُحسب رياضياً بضرب معاملات التصحيح المنفردة:

$$f_{derating} = k_{temp} \times k_{group} \times k_{install}$$

_(حيث $k_{temp}$ معامل تصحيح درجة الحرارة، و $k_{group}$ معامل التجمع، و $k_{install}$ معامل طريقة التمديد)._

> **الفلسفة الهندسية للتصميم:** تضمن هذه المنهجية العكسية أن تكون السعة الفيزيائية الحقيقية للكابل في موقع التركيب—بعد خفضها بفعل الاحتباس الحراري والبيئة—أعلى من تيار الفصل الحراري للقاطع، مما يضمن تفعيل حماية القاطع وعزله للحمل الزائد قبل وصول الكابل إلى مرحلة الانهيار الحراري.

### تحقيق الانتقائية التشغيلية والتنسيق التراتبي

#### الانتقائية التشغيلية للحمايات

لضمان الانتقائية المطلقة ($Total\ Selectivity$)، يجب دائمًا تحقيق الشرط الحاكم التالي:

$$I_{\text{fuse}} < I_{\text{main\_breaker}}$$

يوضح الجدول التالي المقارنة الهندسية والوظيفية التي تحكم هذا التنسيق:

|**معيار المقارنة**|**مصهر السلسلة (String Fuse)**|**القاطع الرئيسي (Main Breaker / Isolator)**|
|---|---|---|
|**الموقع الهندسي**|على التوالي مع القطب الموجب (والسالب) لكل سلسلة منفردة.|عند المخرج الكلي للسلاسل المجتمعة قبل دخول العاكس.|
|**العلاقة الرياضية**|$I_{\text{fuse}} = I_{\text{sc}} \times 1.56$|$I_{\text{main\_breaker}} = \sum I_{\text{string}} \times 1.25$|
|**طبيعة الحماية**|حماية حرارية (انصهارية) موضعية فائقة السرعة.|حماية مغناطيسية/حرارية مركبة مع إمكانية الفصل الميكانيكي اليدوي.|
|**السلوك عند الخطأ**|ينصهر في السلسلة المعيبة فقط (انتقائية موضعية).|يظل مستقراً ولا يفصل إلا إذا تخطى العطل حدود المصفوفة الإجمالية.|

>[!info] خلاصة
> إن ضبط الحمايات وفق هذه النسب الرياضية يضمن هندسياً أن تيار القصر المتدفق نتيجة عطل في سلسلة معينة سيبادر أولاً بصهر الفيوز الخاص بها (نظراً لخضوعه لمعامل تصحيح حراري أعلى واستجابة زمنية أسرع)، في حين يظل القاطع الرئيسي مستقراً ويمرر طاقة السلاسل السليمة الأخرى إلى العاكس دون انقطاع، وهو الهدف الأسمى لإدارة الأعطال الذكية في المحطات الكهروضوئية الاحترافية.

#### التنسيق التراتبي لأمان الكابلات

تُمثل فلسفة التنسيق التراتبي الخط الدفاعي الأخير لمنع الانهيار الحراري واحتراق الموصلات نتيجة للأعطال الكهربائية الممتدة. تفرض هذه الفلسفة علاقة متراجحة صارمة تُعرف بـ **القاعدة الذهبية للتنسيق**، وتُصاغ رياضياً كالتالي:

$$\text{Cable Ampacity} \ge I_{breaker\_rating} \ge I_{rated}$$

حيث تُعرّف أطراف المتراجحة هندسياً وفق الآتي:

- **$I_{rated}$ (التيار الاسمي للتشغيل):** تيار الحمل الأقصى الفعال الذي تسحبه المنظومة (العاكس) في ظروف التشغيل المستقرة الكاملة.
    
- **$I_{breaker\_rating}$ (تيار القاطع الاسمي):** عتبة الفصل الحراري المقننة لأداة الحماية ($I_n$)، والتي يجب أن تسمح بمرور تيار التشغيل الطبيعي دون عوائق، وتتحسس أي زيادة غير طبيعية فوراً.
    
- **$\text{Cable Ampacity}$ (السعة الأمبيرية المصححة للكابل):** أقصى تيار فيزيائي يمكن للكابل تحمله مستمراً في بيئة تشغيله الواقعية (بعد خفضه بمعاملات التصحيح $f_{derating}$) دون أن تتجاوز حرارة عازله العتبة الحرجة المصممة (مثل 90°C لعوازل XLPE).

>[!info] خلاصة
يضمن التنسيق التراتبي المنضبط جعل أداة الحماية هي "الحلقة الأضعف كهربائياً" لتفادي جعل الكابلات والناقلات هي الحلقة الأضعف فيزيائياً وحرارياً داخل المنظومة.

إليك صياغة أكثر إيجازاً وتركيزاً لفقرة قيود هبوط الجهد، تحافظ على العمق الأكاديمي والمصطلحات الفنية:

### قيود هبوط الجهد (Voltage Drop Constraints):

تخضع حسابات تحجيم الكابلات لقيود صارمة تتعلق بهبوط الجهد ($\Delta V$)؛ لارتباطه المباشر بتقليل مفاقيد الطاقة، وضمان استقرار الربط بالشبكة، والحفاظ على كفاءة خوارزميات تتبع نقطة القدرة القصوى (MPPT).

- **محددات جانب التيار المستمر (DC Side $\le 1\%$):**
    
    - **حماية كفاءة الـ MPPT:** يتسبب هبوط الجهد المرتفع في تشويه وإزاحة قيمة الجهد الواصل إلى دخل العاكس مقارنة بجهد الألواح الفعلي، مما يُضلل خوارزمية الـ MPPT ويمنعها من الاستقرار عند نقطة القدرة المثلى، مسبباً هدراً مستمراً في الطاقة (Energy Yield Losses).
        
    - **الفقد الخطي الكلي:** وفقاً للعلاقة ($P = V \times I$)، فإن أي انخفاض في الجهد نتيجة المقاومة الأومية للكابلات يترجم مباشرة وبشكل خطي إلى خفض في القدرة الكلية المستخلصة.
        
- **محددات جانب التيار المتردد (AC Side: $1\% \text{ to } 3\%$):**
    
    - **ظاهرة ارتفاع جهد العاكس (Voltage Rise):** ليتمكن العاكس من ضخ القدرة نحو الشبكة، يجب أن يحقق العلاقة: $V_{\text{inverter}} = V_{\text{grid}} + \Delta V$. تضخم قيمة $\Delta V$ يجبر العاكس على رفع جهد مخرجه بشكل مفرط؛ مما قد يتخطى عتبة حماية الجهد الزائد (Overvoltage Protection) ويدفعه للفصل الزائف المفاجئ عن الشبكة (Nuisance Tripping).
        
    - **الموازنة الاقتصادية الفنية:** يُقيد الهبوط عند $1\%$ في خطوط الربط الرئيسية للمنشآت الضخمة لتقليل المفاقيد الحرارية، بينما يُسمح بالوصول إلى $3\%$ في الدوائر الفرعية القصيرة لموازنة التكلفة الاستثمارية للكابلات مقابل العائد المالي للطاقة المستردة.
