MAQattan/My-Graduation-Project/GP_Obsidian/Thesis/9/الفصل التاسع - كابلات وحمايات المنظومات الكهروضوئية.md

تُعد كابلات الطاقة الكهربائية وأجهزة الحماية العصب الحيوي ومحور الأمان في أي منظومة طاقة كهروضوئية ($PV System$). فمن ناحية، لا يقتصر دور الكابلات على نقل الطاقة الكهربائية المُنتَجة فحسب، بل يتعدى ذلك إلى ضرورة تأمين هذا النقل بأقل مفقودات ممكنة لرفع الكفاءة الكلية للمحطة. ومن ناحية أخرى، تشكل منظومة الحماية خط الدفاع الأول لضمان استمرارية التشغيل الآمن، وحماية المعدات الرأسمالية الثمينة—مثل العواكس والمصفوفات الشمسية—من التلف، فضلًا عن حماية الأفراد والمنشآت من مخاطر الصعق والحرائق.

تفرض الطبيعة التشغيلية للمحطات الكهروضوئية تحديات هندسية فريدة؛ فالجانب المستمر ($DC Side$) يتميز بأن تيارات القصر فيه قريبة جداً من تيارات التشغيل الاعتيادية، مما يجعل اكتشاف الأعطال وفصلها أمراً معقداً يتطلب هندسة دقيقة وحسابات انتقائية ($Selectivity$) متقدمة. بالإضافة إلى ذلك، تخضع المعدات والكابلات في الجانب المستمر لظروف بيئية قاسية تشمل الإشعاع الشمسي المباشر، والأشعة فوق البنفسجية ($UV$)، والتقلبات الحرارية الكبيرة، مما يستدعي الالتزام بمعايير تصميمية وتصنيعية صارمة تتماشى مع الأكواد العالمية مثل معايير اللجنة الكهرتقنية الدولية ($IEC$) والكود الكهربائي الوطني ($NEC$).

تأسيساً على ما سبق، يهدف هذا الفصل إلى تقديم دراسة مرجعية شاملة للأسس النظرية والمعايير الهندسية المعتمدة في توصيف واختيار كابلات الطاقة (بشقّيها المستمر والمتردد)، واستعراض فلسفة الحماية الحديثة ضد التيارات الزائدة، وجهود القصر، والجهود العابرة الناتجة عن الصواعق، مما يشكل المرجعية العلمية التي ستُبنى عليها الحسابات التطبيقية والعملية للمشروع في الفصول اللاحقة.

### [[9 - 1 كابلات الطاقة في المنظومات الكهروضوئية (PV Cabling)]] 

### [[9 - 2 أجهزة الحماية من التيار الزائد وقواطع الفصل (Overcurrent & Isolation Devices)]] 

### [[9 - 3 فلسفة التنسيق والتراتب الرياضي للحمايات (Coordination & Discrimination Logic)]]

### [[9 - 4 الحماية من الجهد الزائد والصواعق (Surge & Overvoltage Protection)]]
