MAQattan/My-Graduation-Project/GP_Obsidian/Thesis/Appendices/الملحقات MOC.md

[[الملحق (أ)]] | [[الملحق (ب)]] | [[الملحق ت]]
