MAQattan/My-Graduation-Project/GP_Obsidian/Thesis/10/Prompts.md

أفكر في اضافة فصل للحمايات والكابلات للدراسة المرجعية بعد الفصل الثامن (أي كما ترى من فهرس المشروع أن فصل التصميم هو الفصل التاسع، الفصل الذي أريد أن أعمل عليه للحمايات والكابلات سيكون الفصل التاسع وفصل التصميم سيصبح العاشر)، حيث قمت بجمع مسودة للفصل النظري ولفقرة العملي في فصل التصميم (للطور الرابع في فصل التصميم الذي عن حساب واختيار الحمايات والكابلات) والتي هي بالمصادر بإسم "مسودة 01 - حمايات وكابلات".
  ما رأيك بالفكرة ؟
في حال توفقني الرأي حتى نبدأ بالعمل على هيكلية الفصل بالاعتماد على هذه المسودة وخبرتك الشخصية، حيث ستقوم باعادة هيكلة وتنسيق وتدقيق هذه المسودة وتخرج بهيكليتين؛ هيكلية لفصل الكابلات والحمايات في الدراسة المرجعية، وهيكلية لطور الكابلات والحمايات في الطور الرابع في فصل التصميم (أنا قمت بهيكلة الطور الرابع في فصل التصميم كما هو واضح من ملف محتوات الفصل العاشر (فصل التصميم) يمكن تقييمها في حال وجدتها جيده يمكننا اعتمادها. سيكون لديك صلاحية إعادة الصياغة والإضافة، وأيضا الحذف في حال وجد تكرار أو لغط لا حاجة له (وهذا موجود بكثرة بالمسودة) بحيث نحصل على محتوى مركّز ومهيكل ومنسق بشكل أكاديمي عصري.
في حال توافقني تجد قراري جيد ، بماذا نبدأ بفصل النظري للحمايات والكابلات (الفصل التاسع في الدراسة المرجعية) أم الطور الرابع العملي للحمايات والكابلات (في فصل التصميم) ؟
وفي حال لا توافقني الرأي في إضافة فصل نظري مخصص للحمايات والكابلات في الدراسة المرجعية علل لي سبب ذلك

ملاحظة : رفعت لك كاتلوج للكابلات فما رأيك به ؟ وإذا لديك خيار أفضل اخبرني به
