MAQattan/My-Graduation-Project/GP_Obsidian/Thesis/10/Draft 2.md

يُعد **حساب مسافة الظلال** من أهم الخطوات في تصميم المنظومات الكهروضوئية، حيث أن وقوع الظل على جزء بسيط من المصفوفة قد يؤدي إلى فقدان كبير في الطاقة أو توقف الإنتاج تماماً [3، 211]. وفيما يلي تفصيل أكاديمي لطرق حساب هذه المسافة بناءً على المعايير الهندسية الواردة في المصادر:

### **1. المبدأ الأساسي والحالة الأسوأ (Worst-Case Scenario)**

يتم حساب مسافة الظلال دائماً بناءً على **أسوأ ظروف السنة**، وهي اللحظة التي يكون فيها الظل في أطول حالاته. وتحدث هذه الحالة في يوم **االنقالب الشتوي (21 ديسمبر)**، حيث تكون زاوية ارتفاع الشمس ($\alpha$) في أدنى قيمة لها [154، 212]. ويُنصح هندسياً بضمان خلو المنظومة من الظلال لمدة **6 ساعات** يومياً على الأقل (من الساعة 9 صباحاً حتى 3 عصراً بالتوقيت الشمسي) [211، 213].

### **2. المعلمات الأساسية المطلوبة للحساب [212، 215]**

- **زاوية ارتفاع الشمس ($\alpha$):** الزاوية بين أشعة الشمس والمستوي الأفقي.
- **زاوية السمت الشمسي ($\psi$):** انحراف الشمس عن الجنوب الجغرافي الحقيقي.
- **زاوية ميل الألواح ($\beta$):** زاوية ميل المصفوفة عن الأفق.
- **عرض اللوح أو ارتفاع الجسم المظلل ($x$ أو $H$):** الأبعاد المادية للجسم.

### **3. خطوات الحساب الرياضي للمسافة بين الصفوف**

لحساب المسافة المثلى بين صفين من الألواح لتجنب **التظليل الذاتي (Self-Shading)**، يتم اتباع الخطوات التالية [54، 55، 56]:

1. **حساب الارتفاع الرأسي ($H$):** إذا كان اللوح بطول ($X$) ومائل بزاوية ($\beta$): $$H = X \times \sin(\beta)$$
2. **حساب المسقط الأفقي للوح ($L_1$):** $$L_1 = X \times \cos(\beta)$$
3. **حساب طول الظل ($L_2$):** يعتمد على زاوية ارتفاع الشمس ($\alpha$) في أسوأ وقت (مثلاً الساعة 9 صباحاً يوم 21 ديسمبر): $$L_2 = \frac{H}{\tan(\alpha)}$$
4. **المسافة الإجمالية بين بداية الصفين ($L_3$):** $$L_3 = L_1 + L_2$$ أو بالصيغة المباشرة: **$L_3 = X \times (\cos\beta + \frac{\sin\beta}{\tan\alpha})$**.

### **4. حساب التباعد بين المباني أو الأجسام المحيطة**

عند وجود أجسام ثابتة (مبانٍ، جدران) أمام المنظومة، تُحسب **زاوية الظل ($\theta$)** لضمان عدم حجبها للشمس، وتكون المسافة المطلوبة ($L$) كالتالي [146، 148]: $$L > H \times \tan(\theta)$$ حيث تُحسب زاوية الظل ($\theta$) بناءً على خط العرض ($\phi$) وزاوية انحراف الشمس ($\delta$) والزاوية الساعية ($\omega$) بالعلاقة: $$\theta = \phi - \arctan(\tan\delta \times \cos\omega)$$.

- **مثال:** في مدينة على خط عرض 35 درجة، يحتاج مبنى بارتفاع 10 أمتار إلى مسافة تباعد تزيد عن **22 متراً** لضمان وصول الشمس في الشتاء.

### **5. قواعد تقريبية (Rule of Thumb)**

في حال غياب البيانات الدقيقة، توفر المصادر قواعد تقريبية سريعة:

- يجب أن تكون المسافة بين الصفوف **ضعف ارتفاع الخلية** أو الحامل تقريباً ($2 \times H$).
- يمكن استخدام **عامل استغلال المساحة ($f$)**، حيث يتراوح عادة بين 0.5 إلى 1.0 لضمان توازن جيد بين استغالل السطح وتجنب الظلال.

### **6. الأدوات والبرمجيات المساعدة**

للحصول على الزوايا الشمسية بدقة حسب الموقع الجغرافي، توصي المصادر باستخدام:

- موقع **NOAA Solar Calculator** لإيجاد زوايا ($\alpha$) و ($\psi$) بدقة.
- أدوات مثل **Solar Pathfinder** أو برمجيات المحاكاة مثل **PVSYST** و **Shadow Analyzer** لبناء نماذج ثلاثية الأبعاد وتحليل الظلال طوال العام [1، 9].

اعتمدت في الرد السابق الخاص بـ **"حساب مسافة الظلال"** بشكل أساسي على المعلومات الواردة في المراجع التالية من المصادر المتوفرة لديك:

1. **كتاب الطاقة الكهروشمسية.pdf**:
    
    - هو المصدر الرئيسي لخطوات **الحساب الرياضي للمسافة بين الصفوف** وتفاصيل الارتفاع الرأسي ($H$) والمسقط الأفقي ($L1$) وطول الظل ($L2$).
    - منه تم استقاء **القواعد التقريبية (Rule of Thumb)** التي تنص على أن المسافة يجب أن تكون ضعف ارتفاع الخلية تقريباً.
    - شرح من خلاله مبدأ **الحالة الأسوأ** المرتبطة بيوم الانقالب الشتوي (21 ديسمبر) وزاوية ميل الشمس الدنيا.
    - فصّل في مفهوم **عامل استغلال المساحة ($f$)** وكيفية استخدامه لتجنب الظل المشترك.
2. **فيزياء الطاقة الشمسية.pdf**:
    
    - اعتمدت عليه في تفصيل **حساب التباعد بين المباني أو الأجسام المحيطة** (وليس فقط بين صفوف الألواح)، بما في ذلك معادلة زاوية الظل ($\theta$) المستنتجة من خط العرض وانحراف الشمس والزاوية الساعية [148، 149].
    - قدّم المثال التطبيقي للمبنى الذي يبلغ ارتفاعه 10 أمتار ويحتاج لمسافة تباعد تزيد عن 22 متراً لضمان وصول الشمس في الشتاء.
3. **مشروع.pdf**:
    
    - ساهم في توضيح **العالقة الرياضية للتخفيض في قيمة الإشعاع** الناتجة عن التظليل وكيفية تخفيض هذه الضياعات إلى حد مقبول.
4. **Grid_connected_Solar_Electric_Systems_The_Earthscan_Expert_Handbook.pdf**:
    
    - استُخدم كمرجع إضافي للتأكيد على أهمية خلو المنظومة من الظلال خلال الساعات المركزية من اليوم (من 9 صباحاً حتى 3 عصراً).

هذه المراجع تكاملت لتعطيك الشرح المفصل من الناحيتين الهندسية (المسافة بين الصفوف) والمعمارية (المسافة بين المباني والأجسام المحيطة).

---

لتوضيح اللبس حول **"زاوية الظل" ($\theta$)** وعلاقتها بزوايا الشمس والمخططات المتوفرة، إليك تفصيلاً أكاديمياً بناءً على المصادر:

### **1. هل زاوية انحراف الشمس ($\delta$) هي نفسها زاوية الظل؟**

**الإجابة هي لا.** هناك فرق جوهري بين الزاويتين [162، 164]:

- **زاوية انحراف الشمس ($\delta$):** هي زاوية موقع الشمس بالنسبة لخط الاستواء السماوي، وتتراوح قيمتها بين **$+23.45^\circ$** (في الصيف) و **$-23.45^\circ$** (في الشتاء) [80، 194، 197]. هي قيمة ثابتة لكل يوم في السنة بغض النظر عن موقعك على الأرض.
- **زاوية الظل ($\theta$):** هي زاوية هندسية مركبة تُستخدم خصيصاً لحساب **المسافة الأفقية ($L$)** المطلوبة بين المباني أو الأجسام لمنع التظليل [162، 164]. هي تعتمد على ثلاثة عوامل مجتمعة: **خط عرض موقعك ($\phi$)**، و**يوم السنة (عبر $\delta$)**، و**الوقت من اليوم (عبر الزاوية الساعية $\omega$)** [164، 165].

### **2. لماذا نحتاج العلاقة الرياضية بدلاً من المخططات الجاهزة؟**

بينما توفر مخططات مسار الشمس (**Sunpath Diagrams**) موقع الشمس اللحظي (الارتفاع والسمت)، تبرز الحاجة للعلاقة الرياضية ($\theta = \phi - \arctan(\tan\delta \times \cos\omega)$) للأسباب التالية [163، 166]:

- **تحديد "المسافة الدنيا" بدقة:** المخططات تخبرك أين الشمس، لكن العلاقة الرياضية تخبرك **كم متراً** بالضبط يجب أن تبتعد عن المبنى المجاور ($L > H \tan\theta$) لضمان وصول الشمس لمنظومتك في "أسوأ ظروف السنة" [164، 166].
- **تصميم النوافذ الزمنية:** المصادر تشترط هندسياً ضمان خلو الموقع من الظلال لمدة **6 ساعات** (مثلاً من 9 صباحاً لـ 3 عصراً) في يوم الانقلاب الشتوي. العلاقة الرياضية تسمح لك بتعويض الوقت ($\omega$) في المعادلة لاستخراج زاوية الظل الدقيقة لتلك الساعة تحديداً، وهو ما يصعب استنتاجه بدقة رقمية من المخططات البصرية العامة [163، 164].
- **التعميم الجغرافي:** المخططات غالباً ما تكون مصممة لخطوط عرض محددة (مثلاً كل 5 درجات)، بينما تتيح لك المعادلة الحساب الدقيق لأي إحداثيات جغرافية ($\phi$) بدقة متناهية [75، 166].

### **3. كيف تعمل هذه العلاقة هندسياً؟**

توضح المصادر أن زاوية الظل ($\theta$) تُستنتج من دمج زاوية **ارتفاع الشمس ($h$)** وزاوية **السمت ($A$)** معاً في مثلث كروي [75، 163]:

1. العلاقة تبدأ من: $\tan\theta = \frac{\cos A}{\tan h}$.
2. باستخدام تحويل الإحداثيات من النظام الأفقي إلى الاستوائي (الذي يربط الزمن بالمكان)، يتم اختزالها لتصبح معتمدة فقط على خط العرض والميل والزاوية الساعية [75، 164].
3. **النتيجة العملية:** إذا كنت في مدينة على خط عرض $35^\circ$ وأردت تأمين الشمس الساعة 9 صباحاً في الشتاء، فإن المعادلة ستعطيك زاوية ظل قدرها **$66^\circ$**. وبناءً عليه، إذا كان ارتفاع المبنى المجاور ($H$) هو 10 أمتار، يجب أن تبتعد عنه مسافة تزيد عن **22 متراً** ($10 \times \tan 66^\circ$).

**الخلاصة:** مخططات مسار الشمس هي أداة **للمعاينة البصرية** وتحديد فترات التظليل [7، 12]، بينما العلاقة الرياضية المذكورة هي أداة **للتصميم الهندسي** وحساب المساحات والمسافات البينية بدقة لضمان كفاءة المنظومة طوال العام [164، 166].

---

**المصادر المعتمدة:**

- **فيزياء الطاقة الشمسية.pdf:** الفقرات (4) و(13) المتعلقة بتتبع ضوء الشمس واستخدام الأراضي [75، 162-167].
- **كتاب الطاقة الكهروشمسية.pdf:** الباب الثاني والثالث حول الزوايا الشمسية وحساب الإشعاع.
- **Grid_connected_Solar_Electric_Systems...:** الفصل الثاني والسابع حول هندسة الشمس وأدوات تقييم الموقع [7، 12].

---
