MAQattan/My-Graduation-Project/GP_Obsidian/Thesis/10/Note 01.md

ملاحظتك دقيقة وفي مكانها تماماً! هندسياً، تفكيرك سليم 100%، ولو التزم كل المصممين بوضع أبعاد لظلال الأجسام المحيطة من الساعة 9:00 حتى 16:00 في يوم 21 كانون الأول (الانقلاب الشتوي) لما وجدنا مكاناً لتركيب لوح شمس واحد في أي منشأة حضرية.

السبب الفيزيائي لما لاحظته هو أن غرب مدينة حلب في ديسمبر يشهد غروب الشمس في تمام الساعة 16:15 تقريباً. هذا يعني أنه عند الساعة 16:00 تكون زاوية ارتفاع الشمس (Solar Elevation Angle) قريبة جداً من الصفر (حوالي 2 إلى 3 درجات فقط). رياضياً، بما أن طول الظل يحسب من العلاقة:

$$Length = \frac{H}{\tan(\alpha)}$$

فعندما تقترب زاوية الارتفاع ($\alpha$) من الصفر، يؤول طول الظل إلى اللانهاية، ويرمي مجسم صغير مثل "غرفة الدرج" ظلاً يغطي نصف السطح بالفعل.

### فكيف تدرس الظلال للأجسام المحيطة في المشاريع الهندسيّة الواقعية؟

في المشاريع الحقيقية وأكاديمياً في مشاريع التخرج، يتم التعامل مع ظلال الأجسام المرتفعة (كغرفة الدرج أو المداخن أو الأبنية المجاورة) وفق ثلاثة أسس هندسية:

#### 1. اعتماد "النافذة الزمنية القياسية" (Standard Solar Window)

لا يتم تصميم المنظومة لتجنب الظل طوال ساعات النهار في الشتاء، بل يتم حصر الدراسة في الفترات التي يكون فيها الإشعاع الشمسي ذو قيمة إنتاجية حقيقية.

- **المعيار العالمي:** يتم دراسة الظلال ليوم 21 كانون الأول بين الساعة **10:00 صباحاً وحتى الساعة 14:00 (2 ظهراً)**، أو في أقصى الحالات من **9:00 صباحاً حتى 15:00 (3 عصراً)**.
    
- **التعليل الهندسي:** الطاقة الإشعاعية المتاحة (GTI) قبل الساعة 9 صباحاً وبعد الساعة 3 ظهراً في شهر كانون الأول تكون ضئيلة جداً ولا تشكل سوى نسبة لا تذكر من الإنتاج السنوي. تضحية المصمم بنصف مساحة السطح من أجل حماية المنظومة من ظل يتشكل في ساعة تكون فيها شدة الإشعاع شبه معدومة هو "تصميم مفرط وخاطئ" (Over-design).

#### 2. التحليل المبني على "نسبة الفقد السنوية" (Annual Shading Loss) وليس اللحظية

البرامج الاحترافية مثل (PVSyst) أو (Helioscope) لا تلغي الألواح لمجرد أن الظل يسقط عليها في شهر كانون الأول. بدلاً من ذلك، تحسب البرنامج الخسارة على مدار **365 يوماً**.

- إذا كان هذا الجزء الشرقي من المبنى يتلقى ظلاً من غرفة الدرج عند الساعة 9:00 صباحاً في شهر ديسمبر فقط، ولكنه يكون مشمساً تماماً طوال أشهر (نيسان، أياير، حزيران، تموز، آب، وأيلول)، فإن خسارته السنوية الإجمالية لن تتجاوز 1% إلى 2%.
    
- **القاعدة الهندسية:** إذا كانت نسبة الفقد السنوي في بقعة معينة بسبب الظل **أقل من 3% إلى 5%**، يتم تركيب الألواح فيها دون تردد، لأن العائد المادي من إنتاجها طوال الصيف والخريف يعوض وزيادة خسارتها الطفيفة في الشتاء.

#### 3. الحلول الكهربائية الذكية (Electrical Mitigation)

بدلاً من ترك السطح فارغاً، يلجأ المهندس الكهربائي لحلول الربط لتقليل تأثير هذا الظل الجانبي:

- **توزيع السلاسل (String Configuration):** يتم تجميع الألواح التي يُحتمل أن يمسها ظل غرفة الدرج صباحاً في "سلسلة مستقلة" (Isolated String) وربطها على مُتعقب استطاعة عظمى مستقل (MPPT Tracker) في العاكس.
    
- بهذه الطريقة، عندما يسقط الظل صباحاً على هذا الجزء، تنخفض إنتاجية هذه السلسلة فقط، بينما تستمر بقية ألواح السطح (في النصف الغربي مثلاً) بالعمل بأعلى كفاءة دون أن تتأثر.

---

### كيف تسقط هذا الكلام في مشروع تخرجك بطريقة رصينة؟

لكي تحمي نفسك أمام لجنة المناقشة وتبرر توزيع الألواح في المخطط، اكتب في فصل التصميم ما يلي:

> **"نظراً لمحدودية المساحة السطحية للمبنى المصرفي، ولتعظيم الاستطاعة المركبة الإجمالية، تم دراسة الظلال الجانبية الناتجة عن الملحقات الإنشائية (غرفة الدرج) اعتماداً على النافذة الزمنية المعيارية ليوم الانقلاب الشتوي (21 كانون الأول) من الساعة 10:00 AM وحتى الساعة 14:00 PM، حيث تتركز في هذه الفترة القيمة الفعالة للإشعاع الشمسي. تم استبعاد المساحات المظللة ضمن هذه النافذة فقط، مع مراعاة فصل الألواح القريبة من العوائق في سلاسل كهربائية (Strings) مستقلة على مستوى العاكس للحد من تأثير المفاقيد اللحظية."**

بهذه المنهجية، يمكنك العودة إلى مخطط الأوتوكاد، وتحديد زاوية السمت (Azimuth) وزاوية الارتفاع لشمس حلب في يوم 21 كانون الأول **عند الساعة 10:00 صباحاً وعند الساعة 2:00 ظهراً فقط**، ورسم خطوط الظل بناءً عليهما. سترى أن مساحة الظل تجمعت في رقعة صغيرة جداً بجوار غرفة الدرج، مما يتيح لك استغلال بقية الجزء الشرقي بملء الفراغات بالألواح بأمان وثقة هندسية كاملة.
