MAQattan/My-Graduation-Project/GP_Obsidian/Thesis/10/Note 02.md

سؤالك في منتصف الجبهة هندسياً! ملحوظتك ذكية جداً وتكشف الفجوة الشهيرة بين "المراجع الأكاديمية النظرية" و"الهندسة التطبيقية في أرض الواقع".

السبب في أن جميع المراجع التي بين يديك تركّز على التظليل الأفقي (بين الصفوف) وتهمل التظليل الجانبي (من الأجسام المحيطة كغرفة الدرج) يعود إلى أربعة أسباب جوهرية:

### 1. كونية التظليل الأفقي ومحلية التظليل الجانبي (Universal vs. Site-Specific)

- **التظليل الأفقي:** هو مشكلة حتمية موجودة في **أي** محطة طاقة شمسية في العالم تتكون من أكثر من صف، سواء كانت فوق سطح بنك في حلب أو في صحراء دبي. لذلك، تفرد لها المراجع معادلات ثابتة لأنها تتبع فقط لخط عرض المنطقة وزاوية ميل الألواح.
    
- **التظليل الجانبي:** هو حالة خاصة جداً (Site-Specific) تختلف من مبنى إلى آخر. مبنى يحتوي غرفة درج في الشرق، ومبنى آخر بجواره مدخنة في الغرب، ومبنى ثالث تحيط به أشجار. لا يمكن للمراجع وضع "معادلة عامة" تصلح لجميع أشكال المباني والعوائق العشوائية في العالم.

### 2. التعقيد الرياضي وحركة زاوية السمت (Azimuth Angle)

- حساب المسافة بين الصفوف (الأفقي) يعتمد بشكل أساسي على زاوية ارتفاع الشمس (Solar Altitude Angle) في وقت ذروة الشتاء (لحظة الظهر مثلاً)، وهي حركة ثنائية الأبعاد (2D) سهلة التنبؤ والحل بمعادلة مثلثية بسيطة.
    
- أما التظليل الجانبي، فهو حركة ثلاثية الأبعاد (3D) معقدة جداً؛ فالظل يرسم قوساً متحركاً (Shading Arc) يتغير طوله واتجاهه كل دقيقة بناءً على تغير زاوية الارتفاع وزاوية السمت (Azimuth) معاً طوال اليوم وطوال فصول السنة. حساب هذا القوس يدوياً يتطلب مصفوفات رياضية معقدة، لذلك تكتفي المراجع بذكر المبدأ وتترك الحساب كاملاً لبرامج المحاكاة الهندسية التي تعتمد على تتبع الأشعة (Ray-Tracing).

### 3. اختلاف الفلسفة الحلّية (Different Engineering Solutions)

- التظليل بين الصفوف يحكمه قرار تصميمي ميكانيكي بحت وهو **"المسافة البينية $D$"**، وإذا لم تحسبها بدقة ستفشل المنظومة بأكملها لأن كل صف سيخنق الصف الذي خلفه.
    
- أما التظليل الجانبي فلا يُحل بزيادة مسافة أو بتغيير الهيكل، بل يُحل بـ **"الاستبعاد الذكي" (Keep-out zones)** في الـ Layout، أو بـ **"التصميم الكهربائي الحذر"** (فصل الألواح المعرضة للظل في سلاسل مستقلة). المراجع تفترض أن المهندس بمجرد نظره للمخطط سيعرف أن هذه المنطقة تتعرض لظل عائق وسيستثنيها تلقائياً، أو سيترك البرامج تحددها له.

### 4. حجم الأثر الطاقي (Scale of Impact)

خطأ واحد في حساب التظليل الأفقي يعني أن المحطة بالكامل انخفضت كفاءتها طوال الشتاء (كارثة هندسية). أما التظليل الجانبي الناتجة عن جسم مثل غرفة الدرج، فهو في النهاية يؤثر على بقعة محددة جداً (لوحين أو ثلاثة) من أصل مصفوفة كاملة، لذا ثقله الأكاديمي في تشكيل "النظرية العامة" للطاقة الشمسية يُعتبر ثانوياً مقارنة بالتظليل بين الصفوف.

---

### كيف تستغل هذا في كتابة مشروعك؟

هذه النقطة بالذات هي **"نقطة قوة"** لمشروع تخرجك وليست ضعفاً. يمكنك إضافتها في مقدمة فصل التصميم تحت عنوان (محددات التصميم الحَضري):

> _"تكتفي المراجع القياسية بحساب التظليل البيني الأفقي نظراً لعموميته، بينما تم في هذا المشروع إدخال دراسة التظليل الجانبي (المحلي) الناتج عن الملحقات الإنشائية للمبنى المصرفي (غرفة الدرج)، نظراً للأثر البالغ للعوائق المحيطة في البيئات الحضرية المحدودة المساحة، وتمت معالجتها عبر تحديد النافذة الزمنية الفعالة للإشعاع وتوزيع السلاسل الكهربائية بشكل مستقل."_

هذا التبرير سيجعل لجنة المناقشة تدرك أنك لا تنقل عميأً من الكتب، بل تفهم تماماً جغرافية ومحددات الموقع الذي تصمم له.
