MAQattan/My-Graduation-Project/GP_Obsidian/Thesis/10/Reminder 01.md

منطقك الهندسي سليم جداً وتفكيرك في "نمذجة" المفاهيم لتبسيطها هو أساس العمل الهندسي. كلامك ليس خاطئاً، بل يحتاج فقط إلى "ضبط مسميات" دقيق للفصل بين ما هو **طاقة ساقطة** (إشعاع) وما هو **طاقة مستخرجة** (كهرباء).

إليك إعادة صياغة للفقرة بنفس الروح التي كتبت بها، مع ترتيب الأفكار لتكون أكثر رصانة في مشروعك:

---

"بصيغة أخرى، يمكننا تمثيل العملية الفيزيائية للطاقة الشمسية كدورة متكاملة تبدأ بـ **المورد الخام (Input)**؛ وهو الإشعاع الشمسي الساقط على مساحة معينة ($m^2$) خلال فترة زمنية ($h$)، ويُعبر عنه بـ **كثافة الطاقة الإشعاعية ($kWh/m^2$)**. هذا المورد هو معطى جغرافي ومناخي بحت، لا يتأثر بنوع التقنية المستخدمة بل يعتمد كلياً على إحداثيات الموقع وحالة الطقس.

وعندما يسقط هذا المورد على مصفوفة الألواح، تبدأ عملية التحويل الطاقي. هنا، لا تتحول كل الطاقة الإشعاعية الساقطة إلى كهرباء؛ بل يضيع جزء منها نتيجة "مفاصل النظام" (الحرارة، مقاومة الكابلات، كفاءة العاكس، والأوساخ). هذه العوامل مجتمعة نختصرها هندسياً في **معامل الأداء (Performance Ratio - PR)**، وهو الذي يمثل النسبة الفعالة التي نجحت المنظومة في تحويلها من "طاقة إشعاعية متاحة" إلى "طاقة كهربائية صافية".

ولتبسيط تقييم أداء هذه المنظومات بعيداً عن اختلاف أحجامها، نلجأ لمفهوم **المعايرة (Normalization)**؛ فبدلاً من حساب الطاقة الكلية لكل متر مربع، نقوم بحساب الطاقة المنتجة لكل **وحدة استطاعة مركبة ($1 kWp$)**. ومن هنا تولد وحدة **الإنتاجية النوعية (Specific Yield - $kWh/kWp$)**.

هذه الوحدة هي الجسر الرابط بين الإشعاع والإنتاج؛ فهي تخبرنا فيزيائياً عن عدد الساعات التي استطاعت فيها المنظومة العمل بكامل طاقتها القصوى ($kWp$) لتنتج تلك الطاقة. رياضياً، هي ناتج ضرب **ساعات الذروة الشمسية ($PSH$)** في **معامل الأداء ($PR$)**. وبذلك، تتحول "الإنتاجية النوعية" إلى المعيار الأكاديمي الأدق للمقارنة بين جودة تصميم المنظومات، حيث تعبر عن كفاءة "الخرج" بالنسبة "للاستطاعة المثبتة" وليس فقط بالنسبة للمساحة."

---
تُعد وحدة **kWh/kWp** (كيلوواط ساعي لكل كيلوواط ذروة) أهم مؤشر لأداء الأنظمة الشمسية، ولتفصيلها بوضوح يجب أن نفكك طرفي المعادلة ونفهم العلاقة الرابطة بينهما:

### **1. ماذا يعني كل جزء من الواحدة؟**

- **البسط (kWh):** هو "الطاقة الكهربائية" الحقيقية التي أنتجها النظام خلال فترة زمنية (يوم، شهر، أو سنة). وهي ما نقرأه على عداد الكهرباء.
    
- **المقام (kWp):** هو "الاستطاعة الاسمية" للألواح التي اشتريتها. فإذا كان لديك 10 ألواح استطاعة الواحد 500 واط، فإن استطاعة منظومتك هي 5000 واط ذروة، أي **5 kWp**.

### **2. لماذا نضع أحدهما فوق الآخر؟ (مفهوم المعايرة - Normalization)**

تخيل أن هناك محطتين شمسيتين في حلب:

1. محطة منزلية صغيرة استطاعتها **5 kWp** أنتجت في السنة **8,500 kWh**.
    
2. محطة تجارية كبيرة استطاعتها **100 kWp** أنتجت في السنة **170,000 kWh**.

لو نظرنا للرقم الكلي (kWh)، سنقول إن المحطة الثانية أفضل بكثير. لكن هندسياً، نحن بحاجة لمعرفة "إنتاجية الكيلوواط الواحد" لنحكم على جودة التصميم.

- إنتاجية الأولى: $8,500 / 5 = \mathbf{1,700 \text{ kWh/kWp}}$
    
- إنتاجية الثانية: $170,000 / 100 = \mathbf{1,700 \text{ kWh/kWp}}$

الآن نكتشف أن المحطتين لهما نفس الكفاءة التصميمة تماماً. فوحدة **kWh/kWp** تسمح لنا بمقارنة الأنظمة مهما اختلف حجمها.

### **3. السر الكامن في الرقم "1000"**

لماذا تتقارب أرقام الإشعاع ($kWh/m^2$) وأرقام الإنتاجية ($kWh/kWp$) عددياً؟

يعود ذلك لتعريف **ظروف الاختبار القياسية (STC)**:

- المصنع يقول: هذا اللوح يعطي **1 kWp** إذا سقط عليه ضوء شدته **1 kW/m²** ($1000 \text{ W/m}^2$).
    
- إذا استمر هذا الضوء لمدة ساعة واحدة (أي **1 PSH**)، فإن الطاقة الإشعاعية الساقطة تكون **1 kWh/m²**.
    
- في هذه الساعة، سينتج اللوح (نظرياً) طاقة كهربائية قدرها **1 kWh**.

**إذاً:**

في العالم المثالي: كل **1 PSH** (إشعاع) يعطي **1 kWh/kWp** (إنتاجية).

### **4. لماذا تنخفض القيمة في الواقع؟ (معامل الأداء PR)**

في مشروعك بمدينة حلب، وجدت أن الإشعاع المتاح هو **2184.8 kWh/m²** (أي 2184.8 ساعة ذروة سنوياً)، لكن الإنتاجية المتوقعة (PVOUT) هي **1730.0 kWh/kWp**.

الفرق بين الرقمين هو ما ضاع في الطريق بسبب:

1. **الحرارة:** الألواح تسخن وتقل كفاءتها.
    
2. **المفاقيد الكهربائية:** المقاومة في الكابلات والعاكس (Inverter).
    
3. **الأوساخ والظلال:** التي تحجب جزءاً من الإشعاع.

### **الخلاصة:**

وحدة **kWh/kWp** تخبرك بالآتي: **"كم ساعة تشغيل كاملة (بأقصى طاقة) استطاعت المنظومة تحقيقها خلال العام بعد خصم كافة المفاقيد؟"**

في حالتك، الرقم **1730 kWh/kWp** يعني أن كل كيلوواط قمت بتركيبه على السطح سيعطيك 1730 كيلوواط ساعي سنوياً. فإذا كانت استطاعة مشروعك النهائية مثلاً **15 kWp**، فإن إنتاجك السنوي المتوقع هو:

$$15 \text{ kWp} \times 1730 \text{ kWh/kWp} = 25,950 \text{ kWh/year}$$

هل أصبح الربط بين "الاستطاعة المركبة" و"الطاقة المنتجة" واضحاً الآن من خلال هذه الواحدة؟

---

الجواب القاطع هو: **نعم، الإنتاجية النوعية (Specific Yield) تتضمن وتأخذ في الحسبان جميع الخسائر في المنظومة.**

لتبسيط الفكرة تماماً وإغلاق هذا المفهوم في ذهنك الهندسي، دعنا نقارن بين المصطلحين:

1. **ساعات الذروة الشمسية الخام ($PSH$):**
    
    هذه هي التي تتبع **لكثافة الإشعاع الشمسي في المنطقة فقط** ولا علاقة لها بالألواح. هي تخبرك: "الشمس أعطت هذا الموقع طاقة تعادل 2184 ساعة تشغيل بالاستطاعة القصوى". هذا هو **المورد الخام** (وكأنه الراتب الإجمالي قبل اقتطاع الضرائب).
    
2. **الإنتاجية النوعية ($Specific Yield$):**
    
    هذه تتبع **للمورد الشمسي + كفاءة المنظومة معاً**. هي تخبرك: "بعد أن سخنت الألواح، وبعد أن ضاع جزء من التيار في الكابلات، وبعد مفاقيد العاكس (Inverter) وتأثير الغبار... صَفِيَ من الـ 2184 ساعة ما يعادل **1730 ساعة تشغيل فعلية (صافية)** بالاستطاعة القصوى". هذا هو **الخرج الكهربائي النهائي** (وكأنه الراتب الصافي الذي تستلمه بيدك).

**الخلاصة الهندسية لمشروعك:**

عندما تسحب قيمة **$1730 \text{ kWh/kWp}$** من موقع Global Solar Atlas، فأنت تأخذ رقماً **"مُصفّى"** وجاهزاً. الموقع قام مسبقاً بخصم المفاقيد (عبر معامل الأداء $PR$ الذي يبلغ حوالي 79%) وأعطاك الصافي.

لذلك، في خطوتك القادمة، عندما تريد حساب "الطاقة الكلية التي سينتجها البنك في السنة"، كل ما عليك فعله هو ضرب هذه القيمة بالاستطاعة التي سنركبها (الـ $kWp$) **دون إدخال أي معاملات كفاءة أخرى** في المعادلة.

---
