MAQattan/My-Graduation-Project/GP_Obsidian/Thesis/9/الفصل التاسع - تصميم منظومة طاقة شمسية متصلة بالشبكة.md

## [[أقسام التلخيص على NotebookLM]] 

---
### [[مفهوم الساعات الشمسية الذروية (Peak Sun Hours - PSH)]] 

>[!info]
>[[PSH vs PVOUT vs GTI (This subsection needs Organizing)]] 

### [[الإنتاجية النوعية (Specific Production - Specific Yield)]] 

>[!warning]
>
>ربما اضيف [[PSH vs PVOUT vs GTI (This subsection needs Organizing)|الحبشكلات]] التي في الأعلى والتي سينظمها NotebookLM لي هنا

### [[المعايير الاقتصادية والتشغيلية]]

### [[أنماط التصميم]] 
### [[منهجية التصميم]]

### [[اختيار اللوح الشمسي]] 
### [[اختيار العاكس (Inverter)]] 

### [[حساب الحالات الحرجة للجهد]]

### [[تحجيم سلسلة الألواح (String Sizing)]]

### [[التوجيه الجغرافي وزاوية الميل المثالية (Orientation and Optimal Tilt Angle)]]

### [[تحليل الظلال]] 

### [[الجدوى والقرار الإنشائي (أو التحليل التقني - الاقتصادي المختصر)]] 

>[!info] مسميات الطرق
>- الطريقة التي كنت تتبعها تسمى: **"التثبيت التقليدي بمسافات بينية" (Standard Fixed Mounting with Inter-row Spacing).**
>- الطريقة التي اقترحتها أنت تسمى: **"الهياكل المتدرجة" (Terraced / Stepped Mounting Structures).**

>[!warning] تذكر
>بعد النتهاء من تحديد هيكلية تصميم الهياكل المعدينة وترتيب الأواح عدود لفقرة [[التوجيه الجغرافي وزاوية الميل المثالية (Orientation and Optimal Tilt Angle)]] لحسم أمر مسافة الأمان وممرات الصيانة

>[!warning] تعديل
> ### [[حساب وتوزيع السلاسل الكهروضوئية (String Sizing and Distribution)]]
> (سأعود للعمل على هذه الفقرة بعد حساب عدد الألواح بناءا على المساحة)
