MAQattan/My-Graduation-Project/GP_Obsidian/Thesis/2/أنظمة الوجه الواحد (Single Phase) والثلاثة أوجه (Three Phase).md

يعد فهم الفرق بين هذين النظامين أساسياً لتحديد كيفية تغذية الأحمال الكهربائية:

1. **نظام الوجه الواحد (Single Phase):** يتكون من سلكين؛ سلك الجهد (Phase) بجهد 220 فولت، وسلك المحايد أو الراجع (Neutral) بجهد صفر فولت. بالتالي، يكون فرق الجهد الفعلي هو 220 فولت ($220 - 0 = 220V$). يُستخدم هذا النظام عادةً مع **الأحمال الصغيرة** مثل معظم الأجهزة المنزلية.
2. **نظام الثلاثة أوجه (Three Phase):** يتكون من ثلاثة أطراف (Phase 1, Phase 2, Phase 3). فرق الجهد بين أي طور والمحايد هو 220 فولت، بينما فرق الجهد **بين أي طورين** (Phase-to-Phase) هو **380 فولت**.
    - **الزاوية الكهربائية:** يوجد فارق زمني (إزاحة) بين الموجات الثلاث بمقدار **120 درجة كهربائية**.
    - **الاستخدام:** يُستخدم مع **الأحمال الكبيرة** (مثل المحركات الضخمة) لأن قدرته أعلى، حيث يُعامل كأنه ثلاثة مصادر وجه واحد مدمجة.
    - **العلاقة الرياضية للجهد:** $V_{L-L} = V_{L-N} \times \sqrt{3}$.
