MAQattan/My-Graduation-Project/GP_Obsidian/Thesis/2/التيار المتردد (Alternating Current - AC).md

يتميز التيار المتردد بأنه **متغير الشدة والاتجاه** بشكل دوري؛ حيث تبدأ الموجة من الصفر لتصل إلى القمة الموجبة (Positive Max)، ثم تعود للصفر، ثم تعكس اتجاهها لتصل للقمة السالبة (Negative Max) قبل العودة للصفر مرة أخرى.

- **إشكالية القياس:** لا يمكن استخدام "القيمة المتوسطة" لقياس التيار المتردد لأن مجموع النصف الموجب مع النصف السالب خلال دورة كاملة سيساوي صفراً ($V_{avg} = 0$)، وهو ما يفسر لماذا يقرأ الفولتميتر المصمم للتيار المستمر قيمة (صفر) عند وضعه على مصدر تيار متردد.
- **القيمة الفعالة (RMS Value):** للتغلب على مشكلة الإشارة السالبة، يتم استخدام مفهوم **جذر متوسط المربعات (Root Mean Square)**، وهي القيمة التي تعبر عن الأثر الفعلي للتيار. تترجم هذه العملية رياضياً عبر ثلاث خطوات: تربيع الموجة (لتحويل الجزء السالب لموجب)، ثم أخذ المتوسط، ثم أخذ الجذر التربيعي.
- **العلاقة الرياضية:**

$$
V_{rms} = \sqrt{\frac{1}{T} \int_{0}^{T} v^2(t) dt}
$$
