MAQattan/My-Graduation-Project/GP_Obsidian/Thesis/2/التيار المستمر (Direct Current - DC).md

يُعرف التيار المستمر بأنه التيار الذي يحافظ على **ثبات الاتجاه** بمرور الزمن. ولا يشترط فيه ثبات الشدة دائماً؛ فقد يكون ثابت الشدة والاتجاه كما في البطاريات، أو متغير الشدة وثابت الاتجاه كما في المخرجات الناتجة عن دوائر التقويم (Rectifiers).

- **القياس والقيمة المتوسطة:** في أنظمة التيار المستمر، لا يتم الاعتماد على القيم العظمى أو الصغرى للجهد، بل يتم قياس **القيمة المتوسطة (Average Value)**.
- **العلاقة الرياضية:** نظراً لأن الموجة قد تكون متصلة وتحتوي على عدد لا نهائي من النقط، يتم استبدال المجموع الجبري بالتكامل الرياضي لحساب المتوسط خلال فترة زمنية (T):

$$
V_{avg} = \frac{1}{T} \int_{0}^{T} v(t) dt
$$
