MAQattan/My-Graduation-Project/GP_Obsidian/Thesis/3/2- الطاقة المائية (Hydro Energy).md

تُمثل **الطاقة المائية** النوع الثاني من مصادر الطاقة المتجددة التي تعتمد في جوهرها على المبدأ الفيزيائي الموحد لتوليد الكهرباء، حيث يكمن وجه الاختلاف الوحيد في استخدام **قوة اندفاع المياه** كمصدر أساسي للحركة المطلوبة لتدوير المولد. وتتطلب هذه التقنية هندسياً وجود ما يُعرف بـ **"هد الميه" (Water Head)**، وهو فرق الارتفاع في منسوب المياه الذي يمكن تأمينه من خلال بناء السدود على الأنهار، أو استغلال البحيرات والمجاري المائية الطبيعية.

وتعتمد آلية العمل في المحطات المائية على حجز كميات ضخمة من المياه خلف السد لإنشاء **منسوب مرتفع** يختزن طاقة وضع عالية، وعند الحاجة لتوليد الطاقة، يتم فتح بوابات السد لتندفع المياه من المنسوب العالي إلى المنسوب المنخفض بسرعة كبيرة جداً تحت تأثير الجاذبية. ويؤدي هذا التدفق المائي السريع للاصطدام بـ **ريش التربينة** مما يجبرها على الدوران بسرعة ميكانيكية عالية، وبما أن هذه التربينة متصلة بشكل مباشر بالمولد الكهربائي، فإن دورانها يؤدي إلى تحريك الموصلات داخل المجال المغناطيسي، مما ينتج عنه توليد قوة دافعة كهربائية وتيار مستحث وفقاً لقانون فاراداي.

![[PV-03-04.jpg]]

وبالرغم من كون الطاقة المائية مصدراً نظيفاً ومستداماً، إلا أنها تواجه تحديات ومعوقات جوهرية تحد من انتشارها في كل مكان؛ حيث يرتبط وجودها بـ **عوامل جغرافية صارمة** تتمثل في ضرورة القرب من مصادر المياه الدائمة كالأنهار والبحيرات. ويبرز التحدي الأكبر في **بعد أماكن التوليد عن مراكز الأحمال** واستهلاك الطاقة؛ فعلى سبيل المثال، تقع محطة السد العالي في أسوان بينما تتركز الكتلة الاستهلاكية الكبرى في القاهرة، مما يفرض الحاجة لإنشاء خطوط نقل ضخمة (Transmission Lines) تمتد لمسافات طويلة جداً. ويؤدي هذا البعد الجغرافي إلى حدوث **فقد كبير جداً في الطاقة** أثناء عملية النقل، وهو ما يُعد من أبرز العيوب التقنية والاقتصادية لمنظومات الطاقة المائية مقارنة بغيرها.
