MAQattan/My-Graduation-Project/GP_Obsidian/Thesis/3/الفصل الثالث -  توليد الطاقة الكهربائية.md

>[!warning]
>لست مقتنع باسم هذا الفصل
> **قدم الفصل لـ NotebookLM حتى يقترح لك اسم لهذا الفصل**
## [[المبدأ الفيزيائي العام لتوليد الكهرباء (قانون فاراداي)]] 

## [[مصادر الطاقة غير المتجددة]] 

## [[مصادر الطاقة المتجددة]] 

---
