MAQattan/My-Graduation-Project/GP_Obsidian/Thesis/3/مصادر الطاقة المتجددة.md

### [[1- طاقة الرياح (Wind Energy)]] 

### [[2- الطاقة المائية (Hydro Energy)]] 

### [[3- أنظمة الطاقة الشمسية المركزة (CSP)]]
