MAQattan/My-Graduation-Project/GP_Obsidian/Thesis/4/أنواع الألواح الشمسية (Modules).md

تتنوع أنواع الألواح الشمسية (Modules) المتوفرة في السوق التجاري بناءً على تكنولوجيا التصنيع ودرجة نقاء السيليكون المستخدم، وهو ما ينعكس بشكل مباشر على كفاءة اللوح وتكلفته الاقتصادية. ويتم تصنيف هذه الألواح إلى ثلاثة أنواع رئيسية هي: الخلايا أحادية البلورة، والخلايا متعددة البلورات، والخلايا الرقيقة.

### **1. الخلايا أحادية البلورة (Monocrystalline)**

تُعد الألواح أحادية البلورة الأكفأ والأعلى جودة في سوق الطاقة الشمسية، حيث تُصنع من سبائك سيليكون ذات درجة نقاء عالية جداً. وتتميز هذه الخلايا بمظهرها المتجانس ولونها الداكن (الأسود غالباً)، ومن الناحية الهندسية، يمكن تمييزها من خلال حوافها "المقصقصة" أو المستديرة، حيث لا تأخذ الخلية شكل مستطيل كامل.

وعلى الرغم من ارتفاع تكلفتها المادية، إلا أنها توفر أعلى معدلات إنتاجية للطاقة مقارنة بالمساحة، مما يجعلها الخيار الأمثل في المشاريع التي تكون فيها **المساحة المتاحة محدودة**؛ فعندما يفرض العميل مساحة ضيقة لا تكفي لتركيب عدد كبير من الألواح العادية، يتم اللجوء للمونو كريستالين لتعويض نقص المساحة بكفاءة الخلايا العالية.

![[PV-04-04.png]]

### **2. الخلايا متعددة البلورات (Polycrystalline)**

تمثل الألواح متعددة البلورات الخيار الأكثر انتشاراً في المشاريع المتوسطة والكبيرة نظراً للتوازن الذي تحققه بين الكفاءة والسعر. وتصنع هذه الخلايا من صهر عدة بلورات سيليكون معاً، مما يعطيها لوناً مائلاً للزرقة وشكلاً مستطيلاً كاملاً ومستوياً دون قص في الحواف.

وعلى الرغم من أن كفاءتها أقل من النوع أحادي البلورة، إلا أن انخفاض تكلفتها يجعلها المفضلة في معظم الاستخدامات العامة حيث تكون المساحة متوفرة بشكل كافٍ، مما يقلل من التكلفة الرأسمالية الكلية للمنظومة.

![[PV-04-05.png]]

### **3. الخلايا الرقيقة (Thin Film)**

يختلف هذا النوع جوهرياً عن الألواح البلورية التقليدية، حيث يتميز بمرونته وانسيابيته التي تسمح له باتخاذ شكل السطح الذي يوضع عليه. وتُعد هذه التكنولوجيا الأقل كفاءة بين الأنواع الثلاثة، حيث تتراوح كفاءتها ما بين **3% إلى 6%** فقط.

ولا يجد هذا النوع انتشاراً واسعاً في المنطقة العربية، بل يكثر استخدامه في تطبيقات محدودة مثل الآلات الحاسبة، أو في الدول الأوروبية حيث تُصمم الأسطح بزوايا ميل حادة لمنع تراكم الثلوج، فيتم تغطيتها بهذه الطبقات الرقيقة لتتبع انحناءات السطح.

![[PV-04-06.png]]

![[PV-04-07.png]]

**ترتيب الكفاءة والقدرة:**
ترتبط كفاءة اللوح ($\eta$) بعلاقة طردية مع جودة المادة، ويمكن ترتيب الأنواع حسب الكفاءة والقدرة الإنتاجية كالتالي:

$$
\eta_{Mono} > \eta_{Poly} > \eta_{Thin-Film}
$$
