MAQattan/My-Graduation-Project/GP_Obsidian/Thesis/4/تأثير الإشعاع الشمسي على الطاقة الكهروضوئية الناتجة.md

يُعتبر الإشعاع الشمسي (Irradiance) العامل الحاسم والمؤثر الأول في كمية الطاقة الكهربائية المنتجة من الألواح الشمسية، حيث ترتبط إنتاجية اللوح بعلاقة طردية مباشرة مع شدة الضوء الساقط عليه. ويظهر هذا التأثير بوضوح عند تحليل منحنيات الخواص (I-V) ومنحنيات القدرة (P-V) تحت مستويات إشعاع مختلفة، مثل القيمة القياسية ($1000 W/m^2$) والقيم الأقل منها.

**1. التأثير على منحنى التيار والجهد (I-V Curve):**
يؤثر الإشعاع الشمسي بشكل رئيسي ومباشر على **قيمة التيار**؛ فكلما زادت شدة الإشعاع، زاد عدد الفوتونات الساقطة، مما يؤدي إلى تحرر عدد أكبر من الإلكترونات، وبالتالي يرتفع تيار القصر ($I_{sc}$) وتيار أقصى قدرة ($I_{mp}$) بنسبة كبيرة وواضحة. أما بالنسبة لـ **الجهد الكهربائي**، فإن تأثير الإشعاع عليه يُعد طفيفاً جداً مقارنة بالتيار؛ حيث تلاحظ الدراسات أن زيادة الإشعاع تؤدي إلى زيادة بسيطة في جهد الدائرة المفتوحة ($V_{oc}$)، ولكنها تظل فروقات غير جوهرية (مثل التغير من 21.7 فولت إلى 22 فولت عند مضاعفة الإشعاع)، مما يجعل الجهد يتصف بالثبات النسبي أمام تغيرات الإضاءة.

**2. التأثير على منحنى القدرة (Power Curve):**
بما أن القدرة الكهربائية ($P$) هي حاصل ضرب الجهد في التيار ($P = V \times I$)، فإن المحصلة النهائية لزيادة الإشعاع هي زيادة كبيرة في القدرة الكلية. وعند رسم منحنيات القدرة لمستويات إشعاع مختلفة (مثلاً 1000، 800، 600 واط/متر مربع)، يظهر كل مستوى إشعاع كقوس منفصل، حيث تنخفض قمة المنحنى التي تمثل **نقطة القدرة القصوى ($P_{max}$)** كلما قل الإشعاع.

![[PV-04-11.png]]

**3. السلوك الزمني للقدرة خلال اليوم:**
تنعكس هذه العلاقة الطردية على الأداء الفعلي للمنظومة خلال ساعات النهار؛ ففي الصباح الباكر يكون الإشعاع ضعيفاً مما ينتج قدرة منخفضة، وتتصاعد هذه القدرة تدريجياً مع زيادة شدة الإشعاع لتصل إلى ذروتها عند وقت الظهيرة (حيث يقترب الإشعاع من $1000 W/m^2$)، ثم تبدأ في التراجع مرة أخرى مع اقتراب وقت الغروب ونقص شدة الضوء. وبناءً على ذلك، يتم تصميم المنظومات وتحديد عدد الألواح بناءً على "ساعات الذروة" لضمان كفاية الطاقة المنتجة.

**العلاقة الرياضية:**
تتحدد القدرة عند أي مستوى إشعاع من خلال العلاقة:

$$
P(\text{Irradiance}) \approx V (\text{Slight change}) \times I (\text{Proportional to Irradiance})
$$

حيث يمثل التيار المتغير التابع الأساسي لشدة الإشعاع الشمسي.
