MAQattan/My-Graduation-Project/GP_Obsidian/Thesis/4/تأثير درجة الحرارة على الطاقة الكهروضوئية الناتجة.md

يُعد تأثير درجة الحرارة (Temperature Effect) من العوامل الحاسمة في أداء المنظومات الكهروضوئية، حيث يتسم هذا التأثير بكونه **علاقة عكسية** مع كفاءة وقدرة اللوح الشمسي، وهو ما يخالف الاعتقاد الشائع بأن زيادة الحرارة تزيد من إنتاجية الكهرباء. فبينما يعتمد اللوح على ضوء الشمس (الفوتونات) لتحرير الإلكترونات، فإن الحرارة الزائدة تؤدي إلى تراجع الخصائص الكهربائية للخلية.

ويتجلى هذا التأثير من خلال تحليل سلوك الجهد والتيار عند ارتفاع درجة الحرارة؛ حيث يؤدي ارتفاع حرارة الخلية إلى **انخفاض حاد في الجهد**، وتحديداً جهد الدائرة المفتوحة ($V_{oc}$) وجهد أقصى قدرة ($V_{mp}$). ويعزى هذا فيزيائياً إلى زيادة الحركة العشوائية للإلكترونات داخل المادة شبه الموصلة، مما يؤدي إلى زيادة التصادمات الداخلية ونشوء "هبوط في الجهد" (Voltage Drop) كبير داخل الخلية، مما يقلل من الجهد الصافي المتاح للحمل.

وفي المقابل، تشهد قيمة التيار ($I$) **زيادة طفيفة جداً** مع ارتفاع درجة الحرارة، وذلك لأن الحرارة تمثل طاقة إضافية تساعد في تحرير عدد محدود من الإلكترونات الإضافية. ومع ذلك، فإن هذه الزيادة الطفيفة في التيار لا يمكنها تعويض النقص الكبير الحادث في الجهد، وبما أن القدرة الكلية ($P$) هي حاصل ضرب الجهد في التيار ($P = V \times I$)، فإن المحصلة النهائية لارتفاع درجة الحرارة هي **انخفاض القدرة الكلية** المنتجة من اللوح.

![[PV-04-12.png]]

وتظهر هذه الفوارق بوضوح عند مقارنة أداء الألواح تحت الظروف المختلفة؛ ففي "الظروف القياسية" (STC) يتم اختبار اللوح عند درجة حرارة مثالية هي **25 درجة مئوية** لضمان أعلى إنتاجية، بينما في "الظروف الطبيعية" (NOCT) التي تصل فيها حرارة الخلية إلى **45 درجة مئوية** أو أكثر، تنخفض القدرة الاسمية للوح بشكل ملحوظ. ولذلك، تُعد عمليات تبريد الألواح (سواء بالهواء أو رش الماء) وسيلة فعالة لخفض حرارة اللوح واستعادة جزء من القدرة المفقودة، حيث يعمل التبريد على رفع قيمة الجهد وبالتالي زيادة الطاقة الكلية.
