MAQattan/My-Graduation-Project/GP_Obsidian/Thesis/4/فكرة الخلية الشمسية (Idea of solar cell).md

تعتمد تكنولوجيا الألواح الشمسية على تحويل ضوء الشمس مباشرة إلى طاقة كهربائية، وهو ما يمثل المسار الثاني لاستغلال الطاقة الشمسية بخلاف الأنظمة الحرارية (CSP) التي تعتمد على تجميع الحرارة لتوليد البخار. ومن منظور فيزيائي، يبدأ فهم عمل الخلية الشمسية من خلال تصنيف المواد بناءً على مستويات الطاقة، حيث يمثل "نطاق التكافؤ" (Valence Band) المستوى الخارجي للذرة الذي يحتوي على الإلكترونات المرتبطة، بينما يمثل "نطاق التوصيل" (Conduction Band) مستوىً وهمياً ينتقل إليه الإلكترون ليصبح حراً وقادراً على نقل التيار. وتفصل بين هذين النطاقين "فجوة الطاقة" (Band Gap)، وهي مقدار الطاقة اللازمة لتحرير الإلكترون؛ فبينما تكون هذه الفجوة كبيرة جداً في العوازل ومنعدمة في الموصلات، فإنها تتخذ قيمًا متوسطة في أشباه الموصلات، مما يجعلها مثالية لامتصاص طاقة فوتونات الضوء وتحويلها إلى طاقة حركية للإلكترونات.

ويُعد السيليكون ($Si$) المادة الأكثر شيوعاً في صناعة الخلايا الشمسية نظراً لتوفرها الهائل في الطبيعة (مثل رمال السيليكون عالية النقاء)، فضلاً عن استقراره العالي وأدائه المتميز في درجات الحرارة المرتفعة مقارنة بمواد أخرى كالجرمانيوم. وفي حالته النقية، يمتلك السيليكون أربعة إلكترونات في مستوى التكافؤ، حيث ترتبط الذرات ببعضها عبر روابط تساهمية قوية لتصل إلى حالة الاستقرار بوجود ثمانية إلكترونات في المستوى الخارجي، مما يجعل السيليكون النقي ضعيف التوصيل. ولتجاوز هذه العقبة، يتم اللجوء إلى عملية "التطعيم" (Doping) بإضافة شوائب محددة؛ فعند إضافة مادة خماسية التكافؤ كالفوسفور، ينشأ النوع السالب (N-type) لوجود إلكترون زائد حر الحركة. أما عند التطعيم بمادة ثلاثية التكافؤ كالبورون، فينشأ النوع الموجب (P-type) نتيجة وجود نقص في الإلكترونات يُعرف بـ "الفجوات" (Holes)، والتي تُعامل فيزيائياً كشحنات موجبة.

وعند دمج الطبقتين (P) و (N) معاً لتكوين ما يُعرف بوصلة (P-N Junction)، تنجذب الإلكترونات من الجانب السالب لتملأ الفجوات القريبة في الجانب الموجب، مما يؤدي إلى تكوين "المنطقة القاحلة" (Depletion Region) الخالية من الشحنات الحرة. وينشأ نتيجة لذلك جهد داخلي يُعرف بـ "الجهد الحاجز"، وتصل قيمته في خلايا السيليكون إلى حوالي **0.7 فولت**، وهو الجهد الذي يمنع استمرار تدفق الإلكترونات تلقائياً. وعند سقوط فوتونات الضوء على الخلية، يمتص الإلكترون طاقة كافية لتجاوز فجوة الطاقة والانتقال لنطاق التوصيل، وهنا يعمل الجهد الحاجز الداخلي كقوة دافعة كهربائية (EMF) توجه هذه الإلكترونات المحررة للمرور عبر مسار خارجي (الحمل) والعودة للطرف الآخر، مما يولد تياراً كهربياً مستمراً (DC).

![[PV-04-01.png]]

وتتم صياغة كفاءة الخلية رياضياً من خلال تحليل منحنى الخواص ($I-V$)، حيث يتم التركيز على نقطة القدرة القصوى ($P_{max}$) التي تمثل حاصل ضرب الجهد عند أقصى قدرة في التيار المقابل له:

$$
P_{max} = V_{mp} \times I_{mp}
$$

علماً بأن أقصى جهد يمكن أن تصل إليه الخلية في حالة الدائرة المفتوحة هو ($V_{oc}$)، بينما يمثل تيار القصر ($I_{sc}$) أقصى تيار ناتج عند حدوث تلامس مباشر بين الطرفين، ولكن التشغيل الفعلي والمثالي يتم دائماً عند نقطة القدرة القصوى لضمان أعلى إنتاجية. وبناءً على هذا الهيكل، تُجمع الخلايا لتكوين اللوح (Module)، ثم تُربط الألواح على التوالي لتكوين "سلسلة" (String) لزيادة الجهد، أو على التوازي لتكوين "مصفوفة" (Array) لزيادة التيار، حسب متطلبات التصميم.
