MAQattan/My-Graduation-Project/GP_Obsidian/Thesis/4/معنى مصطلح كتلة الهواء (Air Mass - AM).md

يُشير هذا المصطلح في سياق تقنيات الطاقة الشمسية إلى المقياس الذي يعبر عن طول المسار الذي يقطعه ضوء الشمس عبر الغلاف الجوي للأرض وصولاً إلى سطح الخلية الشمسية. وبمعنى أدق، يمثل هذا المفهوم عدد طبقات الجو ومقدار المقاومة التي يواجهها الإشعاع الشمسي أثناء مروره في الغلاف الجوي؛ فكلما زادت المسافة التي يقطعها الضوء، زاد تآثر الفوتونات مع الجسيمات والغازات الجوية، مما يؤدي إلى تشتت وامتصاص جزء من الطاقة قبل وصولها للوح الشمسي.

![[PV-04-13.jpg]]

تُصنف قيم كتلة الهواء وفقاً لزاوية سقوط أشعة الشمس، وتتحدد رياضياً من خلال العلاقة التالية:

$$
AM = \frac{1}{\cos(\theta)}
$$

حيث تمثل ($\theta$) الزاوية المحصورة بين اتجاه سقوط أشعة الشمس والخط العمودي على سطح الأرض. وبناءً على هذه العلاقة، يتم تقسيم المعايير التشغيلية إلى مستويات أساسية:

1. **المعيار (AM 0):** يمثل حالة الإشعاع الشمسي خارج الغلاف الجوي للأرض، حيث تكون المقاومة الجوية منعدمة (صفر)، ويُستخدم هذا المعيار خصيصاً في تصميم المنظومات الشمسية المخصصة للتطبيقات الفضائية والأقمار الصناعية.
2. **المعيار (AM 1):** يمثل الحالة التي تسقط فيها أشعة الشمس بشكل عمودي تماماً على الأرض، بحيث تكون الزاوية ($\theta$) مساوية لصفر، وبالتالي يكون ناتج العلاقة ($1/\cos(0) = 1$). ويُعد هذا المعيار مناسباً للمناطق الواقعة على خط الاستواء حيث تكون الشمس عمودية أغلب الوقت، مما يعني أقصر مسار ممكن للضوء وأقل فقد في الطاقة.
3. **المعيار (AM 1.5):** وهو المعيار العالمي المعتمد في ظروف الاختبار القياسية (**STC**) لمعظم دول العالم الواقعة خارج المنطقة الاستوائية. وتنتج هذه القيمة عندما تميل الشمس عن العمودي بزاوية تقارب **48.2 درجة**، حيث أن ($1/\cos(48.2^\circ) \approx 1.5$). ويُفترض في هذا المعيار أن الضوء يقطع مساراً أطول في الغلاف الجوي مقارنة بالوضع العمودي، مما يجعله محاكاة واقعية لمتوسط الإشعاع الذي يصل للأرض في معظم بقاع العالم.

تكمن الأهمية الفيزيائية لهذا المعيار في أن زيادة قيمة (Air Mass) تعني بالضرورة انخفاضاً في كفاءة إنتاجية اللوح؛ نظرًا لأن المسار المائل للضوء يجبره على اختراق طبقات جوية أكثر كثافة، مما يقلل من شدة الإشعاع الفعلي الواصل للخلية مقارنة بالسقوط العمودي.
