MAQattan/My-Graduation-Project/GP_Obsidian/Thesis/5/الاستراتيجيات الهندسية الحديثة لرفع كفاءة الألواح الكهروضوئية.md

تُعد محدودية الكفاءة التشغيلية للألواح الكهروضوئية التقليدية من أبرز التحديات التقنية التي تواجه استدامة مشاريع الطاقة الشمسية؛ حيث تقتصر قدرة الأنظمة التجارية الحالية على تحويل الإشعاع الشمسي الساقط إلى طاقة كهربائية في حدود تتراوح بين 20% إلى 22% فقط. ولتجاوز هذه العوائق الفيزيائية وتحسين الأداء الطاقي للمنظومات، برزت **تقنية أنصاف الخلايا (Half-Cut Cell Technology)** كواحدة من أحدث الحلول الهندسية التي أحدثت طفرة في الأسواق العالمية. فمنذ إنتاج أول لوح بهذه التقنية في عام 2014 من قبل شركة "ريك سولار" (REC Solar) النرويجية، شهدت هذه التكنولوجيا نمواً متسارعاً حتى أصبحت تهيمن حالياً على حوالي 50% من حصة السوق العالمي، مع توجه الصناعة نحو اعتمادها كمعيار قياسي في كافة التصاميم الحديثة.

تستند الاستراتيجيات الهندسية الحديثة لرفع كفاءة الألواح الكهروضوئية إلى معالجة المفاقيد الفيزيائية والكهربائية داخل الموديول، حيث تهدف هذه التقنيات إلى تجاوز حاجز الكفاءة التقليدي الذي يتراوح بين 20% إلى 22%. ولتحقيق هذه الزيادة في المردود، يتم اتباع **أربعة منهجيات تطويرية** أساسية تهدف في مجملها إلى تقليل المقاومات الداخلية وتحسين الامتصاص الضوئي:

**1. زيادة عدد الباسبارات وتقليص المسافات البينية (Multi-Busbar - MBB):**
تتمثل الخطوة الأولى في رفع الكفاءة عبر زيادة عدد القضبان الموصلة (Busbars) المسؤولة عن تجميع التيار من سطح الخلية؛ فبينما كانت الخلايا القياسية تعتمد على 4 باسبارات فقط، توجهت التصاميم الحديثة لاعتماد **9 أو 12 باسبار**. تهدف هذه الزيادة إلى **تقليل المسافة** التي يقطعها التيار للوصول إلى الموصل، مما يقلل من المقاومة الكهربائية الإجمالية ويرفع من احتمالية تجميع تيار أكبر مع خفض ملموس في الضياعات (Losses)، وهو ما ينعكس طردياً على زيادة إنتاجية اللوح.

![[PV-05-01.png]]

![[PV-05-02.png]]

**2. تقسيم الخلية ميكانيكياً باستخدام تقنية الليزر (Cell Splitting):**
تعتمد هذه المنهجية على قص الخلية الكاملة (Full Cell) إلى نصفين متساويين باستخدام أشعة الليزر، وهي الخطوة الجوهرية في تقنية الـ Half-Cut. وتكمن الفلسفة الفيزيائية هنا في **تقليص طول المسار ($L$)** الذي تسلكه الإلكترونات؛ وحسب القانون الفيزيائي ($R = \rho \cdot L/A$)، فإن تقليل الطول يؤدي إلى انخفاض المقاومة ($R$)، وبالتالي تنخفض ضياعات القدرة التي تُحسب بالعلاقة ($P_{loss} = I^2 \cdot R$). وتؤكد الدراسات أن هذا الإجراء وحده يساهم في **زيادة القدرة الخارجة بنسبة تصل إلى 3%** نتيجة خفض المفاقيد الحرارية داخل الخلية.

![[PV-05-03.jpg]]

**3. تحسين هندسة الباسبار (Cylindrical Busbar Design):**
تتعلق الطريقة الثالثة بمعالجة "الظلال الذاتية" الناتجة عن الموصلات؛ حيث كان الشكل التقليدي للباسبار يتخذ هيئة متوازي مستطيلات، مما يسبب انعكاساً للإشعاع الساقط عليه ويخلق ظلاً واسعاً على مساحة الخلية النشطة. وقد تم تطوير ذلك عبر اعتماد **التصميم الأسطواني (Cylindrical Shape)** للباسبار، وهو ما يقلص من مساحة الظل الملقى على الخلية ويسمح باستغلال مساحة أكبر لامتصاص الضوء، مما يعزز من كفاءة التحويل الكهروضوئي ويرفع القدرة الإنتاجية.

![[PV-05-04.png]]

**4. استخدام الزجاج عالي النفاذية والمقاوم للانعكاس (Anti-reflective Glass):**
تتمثل الخطوة الرابعة في تحسين الخصائص البصرية للطبقة الخارجية للوح عبر استخدام زجاج متطور يتميز بـ **معامل نفاذية عالٍ جداً** ومقاومة للانعكاس. تضمن هذه التقنية نفاذ معظم الفوتونات الساقطة إلى طبقات السليكون دون انعكاسها عن السطح، مما يسمح للمنظومة بالاستفادة من أقصى قدر ممكن من الإشعاع الشمسي المتاح وتحويله إلى طاقة كهربائية، وهو ما يقلل من ضياعات الانعكاس ويزيد من المردود الكلي للوح.
