MAQattan/My-Graduation-Project/GP_Obsidian/Thesis/5/البنية الكهربائية للألواح المصنعة بتقنية أنصاف الخلايا (Half-Cut Cell).md

تعتمد البنية الكهربائية لهذه الألواح على إعادة هندسة مسارات التيار والجهد داخلياً لتحقيق أقصى كفاءة ممكنة مع تقليل المفاقيد الحرارية. ولتوضيح هذا التحول، يجب مقارنة التوصيل في الألواح التقليدية (Full Cells) بما استُحدث في تقنية أنصاف الخلايا، حيث يتغير الهيكل التنظيمي للخلايا من نظام السلسلة الواحدة إلى **نظام الربط المختلط (التوالي والتوازي معاً)**.

عند قص الخلية الكاملة (Standard Cell) ميكانيكياً إلى نصفين متساويين، يتأثر المتغير الكهربائي الأساسي وهو **التيار**؛ فمن الناحية الفيزيائية، يؤدي تنصيف مساحة الخلية إلى **تنصيف قيمة التيار** الناتج عنها، بينما يظل **الجهد الكهربائي ثابتًا** ومساويًا لجهد الخلية الكاملة (حوالي 0.5 إلى 0.6 فولت). فإذا كانت الخلية الكاملة تنتج تياراً قدره 8 أمبير، فإن نصف الخلية سينتج 4 أمبير فقط، وهو مفتاح تقليل الضياعات الحرارية داخل اللوح.

في الألواح التقليدية التي تحتوي على 60 خلية، يتم ربط كافة الخلايا على **التوالي** في مسار واحد، مما ينتج جهداً كلياً يبلغ حوالي 30 فولت وتياراً مساوياً لتيار الخلية الواحدة (مثلاً 8 أمبير). أما في تقنية الـ Half-Cut، فيتحول اللوح من 60 خلية كاملة إلى **120 نصف خلية**، ويتم تنظيمها كهربائياً كالتالي:

- يُقسم اللوح إلى جزئين منفصلين تماماً؛ **نصف علوي** يحتوي على 60 نصف خلية، و**نصف سفلي** يحتوي على 60 نصف خلية أخرى.
- يتم توصيل الـ 60 نصف خلية في الجزء العلوي على **التوالي**، وكذلك الـ 60 نصف خلية في الجزء السفلي على **التوالي**.
- يتم ربط المجموعتين (العلوية والسفلية) معاً على **التوازي** عند مخرج اللوح.

![[PV-05-05.png]]

يؤدي هذا التصميم الهجين (توالي ثم توازي) إلى الحفاظ على نفس القيم الكهربائية الكلية للوح التقليدي، ولكن بميزات تشغيلية أفضل:

- بما أن الجزء العلوي (60 نصف خلية توالي) ينتج 30 فولت، والجزء السفلي ينتج 30 فولت، فإن ربطهما توازياً يحافظ على **جهد كلي للوح قدره 30 فولت**، وهو نفس جهد اللوح التقليدي.
- بما أن تيار نصف الخلية هو 4 أمبير، فإن الجزء العلوي يخرج 4 أمبير والسفلي 4 أمبير؛ وعند ربطهما توازياً، يُجمع التياران ليصبح **التيار الكلي 8 أمبير**، وهو نفس تيار اللوح التقليدي.

تكمن الفائدة الجوهرية في أن التيار الذي يسري في "الأسلاك الداخلية" وأنصاف الخلايا هو **نصف التيار الأصلي** فقط، مما يقلل المفاقيد الناتجة عن المقاومة ($P_{Full}=I^{2}_{Full} R$) إلى الربع:

$$
 P_{Half}=(\frac{1}{2}I_{Half})^{2} R = P_{Half}=\frac{1}{4}I_{Half}^{2} R \,\,\,\,\,\,\,\,\,\ ;I_{\text{Half}}= I_{Half}=\frac{1}{2}\cdot I_{Half}
$$

 وهو ما يرفع القدرة الخارجة ويقلل حرارة اللوح. ومن الناحية الشكلية، يمكن تمييز هذا الهيكل بوجود **فاصل أفقي واضح** في منتصف اللوح يقسمه إلى نصفين علوي وسفلي، خلافاً للألواح التقليدية التي تظهر ككتلة مصمتة واحدة.

### ميزات تقنية أنصاف الخلايا

تُقدم هذه تقنية ميزات هندسية وتطويرية جوهرية تجعلها تتفوق على الألواح التقليدية من حيث الكفاءة والموثوقية التشغيلية، وتتركز هذه الفوائد في ثلاث نقاط تقنية أساسية تم استنباطها من التحليل الكهربائي والميداني لأداء هذه الألواح:

### **1. خفض المفاقيد المقاومية (Reduction of Resistive Power Losses)**

تُعد الميزة الأبرز لهذه التقنية هي القدرة العالية على تقليل الضياعات في الاستطاعة الناتجة عن المقاومة الداخلية للخلية. فمن الناحية الفيزيائية، تعتمد مفاقيد القدرة على مربع التيار ($P_{loss} = I^2 \cdot R$)؛ وبما أن تقسيم الخلية إلى نصفين يؤدي هندسياً إلى تنصيف قيمة التيار المار في كل جزء، فإن ذلك يقلل الضياعات إلى الربع مقارنة بالخلية الكاملة.
وعلى سبيل المثال، إذا كانت المفاقيد في اللوح التقليدي تصل إلى 12 واط، فإنها تنخفض في لوح أنصاف الخلايا إلى حوالي 3 واط فقط، مما يسمح باستغلال القدرة الضائعة وتحويلها إلى زيادة في الاستطاعة الخارجة (Output Power) بنسبة تتراوح حول 3%.

![[PV-05-06.png]]

### **2. الحد من تأثير البقع الساخنة (Hot Spot Mitigation)**

تنشأ ظاهرة **البقع الساخنة (Hot Spots)** عندما تتعرض خلية معينة للتظليل (بسبب أوراق الشجر أو فضلات الطيور)، مما يحولها من منتج للطاقة إلى "حمل" يستهلك الطاقة ويولد حرارة قد تؤدي لاحتراق الخلية.
وتساهم تقنية الـ Half-cut في تقليل هذا الخطر بشكل كبير؛ فبما أن التيار المار في نصف الخلية هو نصف التيار المعتاد، فإن الطاقة الحرارية المتولدة عند التظليل ($I^2 \cdot R \cdot t$) تكون أقل بكثير، مما يحافظ على برودة أنصاف الخلايا ويحميها من التلف الحراري، ويضمن استدامة اللوح لفترة أطول.

### **3. الكفاءة العالية في ظروف التظليل (Enhanced Shade Tolerance)**

تتميز الألواح التقليدية بحساسية عالية تجاه الظل؛ حيث يتكون اللوح عادة من 3 سلاسل (Strings)، وتظليل جزء بسيط من سلسلة واحدة قد يؤدي لخروج ثلث اللوح عن العمل. أما في تقنية أنصاف الخلايا، فيتم تقسيم اللوح كهربائياً إلى **6 سلاسل مستقلة** (3 في النصف العلوي و3 في السفلي) مرتبة بنظام "التصميم التوأمي" (Twin-design).

![[PV-05-07.png]]

هذا الهيكل يسمح للنصف غير المظلل بالعمل بكامل كفاءته حتى لو تعرض النصف الآخر للتظليل الكامل؛ ففي حين قد يفقد اللوح التقليدي 100% من إنتاجيته عند تظليل عرضه بالكامل، يظل لوح أنصاف الخلايا قادراً على إنتاج **50% من طاقته** في نفس الظروف، مما يجعله الخيار الأمثل للمواقع التي تعاني من ظلال متكررة.
