MAQattan/My-Graduation-Project/GP_Obsidian/Thesis/8/التطبيق على مدينة حلب.md

#### **جدول معادلات حساب زاوية الميل المثالية**

| $\Large \phi$ | **Year-round** | **Winter** | **Summer** |
| --- | --- | --- | --- |
| $0 → 25^{\circ}$ | $\beta = (\phi \times 0.84) + 1^{\circ}$  | $\beta = \phi + 16^{\circ}$ | $\beta = (\phi \times 0.05) + 1^{\circ}$ |
| $25^{\circ} → 50^{\circ}$ | $\beta = (\phi \times 0.76) + 3^{\circ}$  | $\beta = (\phi \times 0.88) + 19^{\circ}$ | $\beta = (\phi \times 0.93)-21^{\circ}$  |
| $> 50^{\circ}$ | $\beta = (\phi \times 0.66) + 30^{\circ}$ | $\beta = \phi \times 0.82$ | $\beta = \phi - 24.5^{\circ}$ |

 وبالتطبيق العملي على **مدينة حلب** التي تقع عند دائرة عرض **37° شمالاً**، نجد أنها تقع ضمن النطاق الثاني، مما يفرض استخدام المعادلات التالية لتحقيق أقصى كفاءة إنتاجية وفقاً للهدف التشغيلي:

1. **الزاوية المثالية للتشغيل السنوي (Year-round):** تُستخدم في المنظومات التي تهدف لتحقيق أقصى عائد استثماري سنوي (مثل الأنظمة المرتبطة بالشبكة)، وتُحسب وفق العلاقة: $(\text{Latitude} \times 0.76) + 3^{\circ}$. وبتطبيقها على حلب نجد أن الزاوية المثالية الدقيقة هي :

$$
\beta = (37^{\circ} \times 0.76) + 3^{\circ} ≃ 31^{\circ} 
$$

ونجد أن هناك فرق 6 درجات عن الطريقة التقليدية الغير دقيقة (التي تكون فيها الزاوية من أجل التشغيل السنوي : $\beta = \phi = 37^{\circ}$) .

2. **الزاوية المثالية لفصل الشتاء:** لتأمين أقصى قدرة خلال أشهر الشتاء وتجاوز عجز الإشعاع، يتم الاعتماد على القانون: $(\text{Latitude}\ (\phi) \times 0.88) + 19^{\circ}$. وبتطبيق ذلك على حلب نجد:

$$
\beta = (37^{\circ} \times 0.88) + 19^{\circ} ≃ 52^{\circ}
$$

3. **الزاوية المثالية لفصل الصيف:** في المقابل، وبسبب الارتفاع الشاهق للشمس في سماء حلب صيفاً، تُستخدم العلاقة: $(\text{Latitude} \times 0.93) - 24.5^{\circ}$. وبالتعويض:

$$
\beta = (37^{\circ} \times 0.93) - 21^{\circ} ≃ 10^{\circ}
$$
