MAQattan/My-Graduation-Project/GP_Obsidian/Thesis/Appendices/الملحق (أ).md

## أوراق البيانات للعناصر المنظومة (Datasheets)

![[L_Gi_LE_PM_T_PMD_059_F133_LR_5_72_HTH_590_600_M_V2_30_30_and_15_Frame_Scientist_V19_EN_pdf_26bcba7569.pdf]]
