MAQattan/My-Graduation-Project/GP_Obsidian/Thesis/9/Draft/الفصل التاسع - الحمايات والكابلات في المنظومات الكهروضوئية.md

تفرض طبيعة العمل الميداني للمنظومات الشمسية الكهروضوئية محددات تشغيلية وبيئية استثنائية على تصميم شبكاتها الكهربائية؛ حيث تواجه هذه المنظومات ظروفاً مناخية قاسية تتراوح بين درجات الحرارة المرتفعة، والإشعاع فوق البنفسجي المستمر، والاهتزازات الميكانيكية الناتجة عن الرياح. هذه العوامل البيئية تؤثر مباشرة على الخصائص الفيزيائية للموصلات وعوازلها، مما يسرّع من معدلات تقادمها الحراري ويزيد من مقاومتها الأومية. بناءً على ذلك، لا تقتصر المتطلبات التشغيلية لشبكات الربط على نقل القدرة بكفاءة فحسب، بل تمتد لتشمل الحفاظ على استقرار الجهد ضمن الحدود المعيارية، وتقليل المفاقيد الحرارية إلى حدها الأدنى لضمان استمرار عمل خوارزميات تتبع نقطة القدرة القصوى (**MPPT**) بكفاءة كاملة، وتفادي ظواهر الفصل الزائف للعاكسات نتيجة اضطرابات جودة القدرة الكهربائية المتولدة عن الأحمال غير الخطية في الشبكة.

من جانب آخر، تتطلب هندسة هذه المنظومات فلسفة أمان بالغة الدقة لعزل الأعطال، نظراً لدمجها بين بيئتين كهربائيتين متمايزتين فيزيائياً: بيئة الجهد المستمر (**DC**) وبيئة الجهد المتردد (**AC**). في جانب التيار المستمر، تكمن خطورة الأعطال في غياب نقطة الصفر الطبيعية للتيار، مما يجعل إطفاء الأقواس الكهربائية الناشئة تحدياً فيزيائياً معقداً يتطلب وسائط عزل خاصة كرمال الكوارتز في المصهرات وقواطع مؤهلة للجهود المستمرة العالية. أما في جانب التيار المتردد، فتتمحور فلسفة الحماية حول التعامل مع تيارات البدء العابرة والأحمال الزائدة التراكمية، والتنسيق التراتبي الصارم بين أدوات القطع وسعات الكابلات لضمان عزل الجزء المعطوب بانتخابية عالية (**Selectivity**) وبسرعة تحول دون نشوب الحرائق أو تضرر الأصول التشغيلية للمنشأة.

تأسساً على هذين الركيزتين—المتطلبات التشغيلية والبيئية وفلسفة عزل الأعطال في البيئتين—يستعرض هذا الفصل تحليلاً هندسياً معمقاً يبدأ بفيزيائية قواطع الحماية المترددة والمستمرة وتكنولوجيا إخماد الشرارة، مروراً بالتصنيفات البنيوية والترميزية للموصلات، وانتهاءً بالمنهجية الرياضية والكودية المتبعة عالمياً لتحجيم الكابلات والتنسيق الحمائي.

### [[بنية التمديد والحماية في الجانب المتردد (AC Side)]] 

### [[كابلات التيار المتردد (AC Cables)]] 

### [[فيزيائية الحماية والربط في الجانب المستمر (DC Side)]] 

### [[المنهجية المعيارية للتنسيق الرياضي وحسابات التحجيم]] 

---
[[مسودة 01 - حمايات وكابلات]]
