MAQattan/My-Graduation-Project/GP_Obsidian/Thesis/9/Draft/المنهجية المعيارية للتنسيق الرياضي وحسابات التحجيم.md

### المنهجية النظرية لتحجيم الحمايات والكابلات (AC/DC)

تستند الصياغة الرياضية الحاكمة لتصميم واختيار عناصر الحماية ومساحات مقاطع الكابلات في المنظومات الكهروضوئية إلى تحديد التيارات التشغيلية القصوى المتوقعة، ثم تطبيق معاملات أمان صارمة تضمن سلامة المكونات تحت الظروف التشغيلية القصوى. وتبدأ الخطوة النظرية لجانب التيار المتردد (AC) باستنتاج التيار الاسمي للعاكس الشمسي بناءً على قدرته المخرجة القصوى، وجهد الشبكة، ومعامل القدرة.

في أنظمة الربط أحادية الطور (Single-Phase)، يُحسب التيار الاسمي الفعال ($I_{rated}$) بالاعتماد على القدرة الاسمية للعاكس ($P_{inverter}$)، وجهد الطور ($V$)، ومعامل القدرة ($PF$) وفقاً للعلاقة الرياضية التالية:

$$I_{rated} = \frac{P_{inverter}}{V \times PF}$$

أما في أنظمة الربط ثلاثية الأطوار (Three-Phase)، فيتم إدراج المعامل الفيزيائي لفرق الجهد بين الأطوار ($\sqrt{3}$) لحساب تيار الخط الاسمي ($I_{rated}$) وفقاً للمعادلة التالية:

$$I_{rated} = \frac{P_{inverter}}{\sqrt{3} \times V \times PF}$$

بمجرد استخراج القيمة الرياضية الدقيقة للتيار الاسمي ($I_{rated}$)، تفرض الأكواد الهندسية المعيارية تطبيق معامل أمان (Safety Factor) ثابت يُقدر بـ **1.25** لتحديد تيار التصميم الأدنى ($I_{design}$):

$$I_{design} = I_{rated} \times 1.25$$

يهدف هذا المعامل إلى تعويض الإجهادات الحرارية المستمرة وتجنب ظاهرة الفصل الزائف لعناصر الحماية نتيجة الارتفاعات الطفيفة العابرة في جهد الشبكة أو مستويات الإشعاع، ويُتخذ تيار التصميم الناتِج كقاعدة أساسية تلتها خطوتان متزامنتان: اختيار العتبة الاسمية المقاربة لقاطع الحماية ($I_n \ge I_{design}$)، وتحديد الحد الأدنى لسعة التيار للكابلات (Current-Carrying Capacity) قبل تطبيق معاملات التصحيح الحراري والبيئي الخاصة بطريقة التمدد.

### محددات التصحيح الحراري والبيئي (Derating Factors)

تنخفض سعة حمل التيار الاسمية للكابلات الكهربائية عند تركيبها في ظروف تشغيلية واقعية مقارنة بقيمها القياسية المدرجة في الجداول (والتي تُقاس غالباً عند درجة حرارة محيطة $30^{\circ}\text{C}$ في الهواء). تفرض الأكواد الهندسية تطبيق معاملات تقليل القدرة (Derating Factors) لمعادلة أثر البيئة المحيطة وطرق التمديد، ضماناً لعدم تجاوز العوازل لدرجات حرارتها الحرجة.

#### أثر التمديد داخل المواسير (Conduits) والمجاري المغلقة

يتسبب تركيب الكابلات داخل مواسير حمائية أو مجاري كابلات مغلقة (Closed Trays) في تقييد حركة الهواء حول الموصلات، مما يخلق مقاومة حرارية إضافية تعوق التبديد الطبيعي للحرارة الناجمة عن المفاقيد الأومية ($I^2R$). يرتفع هذا الإجهاد الحراري التراكمي طردياً عند تجميع عدة كابلات حرارية في مسار مغلق واحد نتيجة التأثير الحراري المتبادل بين الدوائر (Grouping Effect). لتفادي التدهور المتسارع للمادة العازلة، تُطبق معاملات تصحيح صارمة (تستند لمعايير مثل IEC 60364-5-52) تختزل السعة الأمبيرية للكابل بناءً على نوع المجرى، ومادة التصنيع، وعدد الموصلات المتجاورة.

#### معادلة التيار التصميمي لاختيار الكابلات من الكتالوجات

لضمان اختيار مساحة مقطع قادرة على تحمل التيارات التشغيلية وأعطال الحمل الزائد دون تخطي الحدود الحرارية للعازل تحت أسوأ الظروف الميدانية، تُستخدم العلاقة الرياضية التالية لتحديد السعة التيارّية الدنيا المعايرة ($I_{cable\_required}$) الواجب مطابقتها مع جداول الشركات المصنعة:

$$I_{cable\_required} = \frac{I_{breaker\_rating}}{f_{derating}}$$

حيث تُعرّف المتغيرات كالتالي:

- **$I_{cable\_required}$**: السعة التيارّية الاسمية الدنيا المطلوبة للكابل تحت الظروف القياسية للكتالوج.
    
- **$I_{breaker\_rating}$**: التيار الاسمي المقنن لقاطع الحماية المختار ($I_n$) والذي يحمي هذا الكابل.
    
- **$f_{derating}$**: معامل التصحيح الإجمالي المتراكم، ويُحسب رياضياً بضرب معاملات التصحيح المنفردة:

$$f_{derating} = k_{temp} \times k_{group} \times k_{install}$$

_(حيث $k_{temp}$ معامل تصحيح درجة الحرارة، و $k_{group}$ معامل التجمع، و $k_{install}$ معامل طريقة التمديد)._

> **الفلسفة الهندسية للتصميم:** تضمن هذه المنهجية العكسية أن تكون السعة الفيزيائية الحقيقية للكابل في موقع التركيب—بعد خفضها بفعل الاحتباس الحراري والبيئة—أعلى من تيار الفصل الحراري للقاطع، مما يضمن تفعيل حماية القاطع وعزله للحمل الزائد قبل وصول الكابل إلى مرحلة الانهيار الحراري.

### فلسفة التنسيق التراتبي للأمان (Protection-Cable Coordination)

#### أولاً: القاعدة الذهبية للتنسيق الحمائي

تُمثل فلسفة التنسيق التراتبي الخط الدفاعي الأخير لمنع الانهيار الحراري واحتراق الموصلات نتيجة للأعطال الكهربائية الممتدة. تفرض هذه الفلسفة علاقة متراجحة صارمة تُعرف بـ **القاعدة الذهبية للتنسيق**، وتُصاغ رياضياً كالتالي:

$$\text{Cable Ampacity} \ge I_{breaker\_rating} \ge I_{rated}$$

حيث تُعرّف أطراف المتراجحة هندسياً وفق الآتي:

- **$I_{rated}$ (التيار الاسمي للتشغيل):** تيار الحمل الأقصى الفعال الذي تسحبه المنظومة (العاكس) في ظروف التشغيل المستقرة الكاملة.
    
- **$I_{breaker\_rating}$ (تيار القاطع الاسمي):** عتبة الفصل الحراري المقننة لأداة الحماية ($I_n$)، والتي يجب أن تسمح بمرور تيار التشغيل الطبيعي دون عوائق، وتتحسس أي زيادة غير طبيعية فوراً.
    
- **$\text{Cable Ampacity}$ (السعة الأمبيرية المصححة للكابل):** أقصى تيار فيزيائي يمكن للكابل تحمله مستمراً في بيئة تشغيله الواقعية (بعد خفضه بمعاملات التصحيح $f_{derating}$) دون أن تتجاوز حرارة عازله العتبة الحرجة المصممة (مثل 90°C لعوازل XLPE).

#### ثانياً: تحليل سيناريوهات التنسيق وأثرها على المنشآت التجارية

| **السيناريو** | **العلاقة الرياضية** | **الأثر التشغيلي والفيزيائي على المنشأة** |
| --- | --- | --- |
| **التنسيق الصحيح (المثالي)** | $\text{Cable Ampacity} \ge I_{breaker\_rating} \ge I_{rated}$ | • حماية كاملة ومؤكدة للمنشأة؛ حيث يتحسس القاطع عطل الحمل الزائد ويفصل الدائرة حرارياً **قبل** وصول الكابل لدرجة حرارة تدهور العازل.<br><br>  <br><br>• استقرار تيار التغذية وضمان استمرارية التشغيل الآمن للأصول. |
| **التنسيق الخاطئ (قاطع متضخم)** | $I_{breaker\_rating} > \text{Cable Ampacity}$ | • **مخاطر حرارية كارثية:** يمر تيار عطل أعلى من قدرة الكابل الفنيّة، فيستمر الناقل في تفريغ حرارة جولية تراكمية ($I^2Rt$) دون أن يفصل القاطع.<br><br>  <br><br>• يتسبب هذا السيناريو في ذوبان العوازل ونشوب **حرائق كهربائية متسارعة** داخل مجاري الكابلات تهدد سلامة المنشأة بالكامل. |
| **التنسيق الخاطئ (قاطع متقزم)** | $I_{breaker\_rating} < I_{rated}$ | • **الفصل الزائف المستمر (Nuisance Tripping):** يفصل القاطع الدائرة ميكانيكياً وحرارياً أثناء ظروف التشغيل الطبيعية والمستقرة للمحطة الكهروضوئية.<br><br>  <br><br>• يتسبب في انقطاعات عشوائية متكررة للقدرة، مما يرفع من الخسائر التشغيلية للمنشأة التجارية نتيجة توقف الإنتاج. |

> **خلاصة هندسية:** يضمن التنسيق التراتبي المنضبط جعل أداة الحماية هي "الحلقة الأضعف كهربائياً" لتفادي جعل الكابلات والناقلات هي الحلقة الأضعف فيزيائياً وحرارياً داخل المنظومة.

### قيود هبوط الجهد (Voltage Drop Constraints)

لا تقتصر حسابات تحجيم الكابلات في المنظومات الكهروضوئية على استيفاء سعة حمل التيار (Ampacity) لحمايتها من الاحتراق فحسب، بل تخضع لقيود هندسية وتشغيلية صارمة تتعلق بهبوط الجهد ($\Delta V$). يرتبط هبوط الجهد مباشرة بالفقد في الطاقة المنتجة، ويؤثر فيزيائياً على كفاءة عمل خوارزميات تتبع نقطة القدرة القصوى (MPPT) داخل العواكس الشمسية، فضلاً عن تأثيره على استقرار الربط بالشبكة الكهربائية.

#### القيود الصارمة لجانب التيار المستمر (DC Side $\le$ 1%)

تفرض التصاميم الهندسية المتقدمة ألا يتجاوز هبوط الجهد في كابلات الجانب المستمر (من مصفوفات الألواح إلى دخل العاكس) نسبة **1%** تحت ظروف الإشعاع القصوى. وتعود هذه الصرامة إلى محددات فيزيائية وتشغيلية حرجة:

- **حماية كفاءة الـ MPPT:** تعتمد خوارزمية تتبع نقطة القدرة القصوى على مسح دقيق ومنتظم لمنحنى الجهد-التيار الخاص بالسلاسل الكهروضوئية لتحديد النقطة التشغيلية المثلى التي تُستخلص عندها أعلى طاقة ممكنة. حدوث هبوط جهد مرتفع في الكابلات يتسبب في حدوث إزاحة وتشويه في قيمة الجهد الفعلي الواصل إلى أطراف دخل العاكس مقارنة بالجهد الحقيقي المتولد عند الألواح، مما يضلل خوارزمية الـ MPPT ويمنعها من الاستقرار بدقة عند نقطة القدرة القصوى الحقيقية، وينتج عن ذلك هدر مستمر في الطاقة المتولدة (Energy Yield Losses).
    
- **طبيعة الفقد الخطي الكلي:** بما أن القدرة المستمرة تساوي حاصل ضرب الجهد في التيار ($P = V \times I$)، فإن أي انخفاض في قيمة الجهد نتيجة المقاومة الأومية للكابلات يترجم مباشرة وبشكل خطي إلى انخفاض في القدرة الكلية المستخلصة من الحقل الكهروضوئي، وهو فقد دائم لا يمكن تعويضه طوال ساعات ذروة الإشعاع الشمسي.

#### قيود جانب التيار المتردد (AC Side: 1% to 3%)

في جانب التيار المتردد (من مخرج العاكس إلى لوحة التوزيع الرئيسية أو محول الرفع)، يُسمح بهبوط جهد يتراوح بين **1% إلى 3%** كحد أقصى وفقاً لطبيعة المنشأة وتوصيات المعايير الدولية (مثل IEC 60364-7-712)، ويخضع هذا الجانب للمحددات التالية:

- **ظاهرة ارتفاع جهد العاكس (Inverter Voltage Rise):** لكي يتمكن العاكس الشمسي من ضخ القدرة الحركية نحو الشبكة الكهربائية، يجب أن يكون جهد مخرجه أعلى من جهد الشبكة بقيمة تساوي هندسياً مقدار هبوط الجهد في كابل الربط المتردد وفق العلاقة:

$$V_{inverter} = V_{grid} + \Delta V$$

- إذا تضخمت قيمة $\Delta V$ نتيجة صغر مساحة مقطع الكابل المختار، يضطر العاكس لرفع جهد مخرجه بشكل مفرط؛ وفي فترات ذروة الإشعاع بالتزامن مع انخفاض الأحمال الداخلية للمنشأة، قد يتخطى هذا الجهد المرتفع عتبة الحماية من الجهد الزائد (Overvoltage Protection) المبرمجة في العاكس، مما يدفعه للفصل التلقائي الفوري عن الشبكة (Nuisance Tripping)، وهو ما يتسبب في خسائر تشغيلية فادحة للمنشآت نتيجة انقطاع حقن الطاقة.
    
- **الموازنة الاقتصادية الفنية (Techno-Economic Optimization):** يُفضل هندسياً تقييد نسبة الهبوط عند **1%** في خطوط الربط الرئيسية للمنشآت التجارية والصناعية الكبيرة لتقليل المفاقيد الحرارية في الطاقة الكلية المصدرة، بينما يُسمح بالوصول إلى عتبة **3%** في الدوائر الفرعية القصيرة أو الأنظمة الصغيرة لموازنة التكلفة الاستثمارية لشراء كابلات ذات مقاطع ضخمة مقابل العائد المالي من الطاقة المستردة.
