MAQattan/My-Graduation-Project/GP_Obsidian/Thesis/9/Draft/فيزيائية الحماية والربط في الجانب المستمر (DC Side).md

### المقارنة الهندسية والفيزيائية بين كابلات الـ AC والـ DC

#### ظاهرة التأثير القشري (Skin Effect)

تُعد ظاهرة التأثير القشري تمايزاً فيزيائياً جوهرياً بين سلوك التيارين المتردد والمستمر داخل الموصلات. عند مرور التيار المتردد (AC)، تولّد التغيرات الزمنية للمجال المغناطيسي تيارات دوامية داخلية تعاكس تدفق التيار الرئيسي عند مركز الموصل، مما يدفع الشحنات الكهربائية للهجرة نحو السطح الخارجي. ينتج عن ذلك توزيع غير متجانس لكثافة التيار، ويُعبر عن عمق اختراق التيار في القشرة السطحية ($\delta$) بالمعادلة التالية:

$$\LARGE \delta = \sqrt{\frac{\rho}{\pi f \mu}}$$

حيث تمثل $\rho$ المقاومية النوعية للمادة، و $\mu$ النفاذية المغناطيسية، و $f$ التردد. وبسبب هذه الظاهرة، تقل مساحة المقطع الفعالة للموصل في دوائر الـ AC، مما يرفع المقاومة الفعالة ($R_{ac} > R_{dc}$) ويتسبب في زيادة المفاقيد الحرارية. في المقابل، تنعدم هذه الظاهرة تماماً في دوائر التيار المستمر (DC) نظراً لثبات الاتجاه والقيمة صفريّة التردد ($f = 0$)؛ حيث تتوزع كثافة التيار بشكل متجانس كامل المساحة المقطعية للموصل، مما يتيح استغلالاً هندسياً كلياً لمعدن الناقل وبمفاقيد أومية أقل لنفس مساحة المقطع.

> **[موضع صورة توضيحية 5: رسم بياني يوضح توزيع كثافة التيار داخل الموصل في حالتي الـ AC والـ DC لبيان أثر التأثير القشري]**

#### الإجهاد الحراري المستمر (Continuous Thermal Stress)

يخضع عزل كابلات الجانب المستمر (DC) لإجهاد حراري تراكمي يختلف ديناميكياً عن كابلات الجانب المتردد (AC)، وخصوصاً عند مقارنة الأداء عند القيمة العظمى للتيار ($I_{max}$). في دوائر الـ AC، يتغير التيار جيبياً ويمر بنقطة الصفر مرتين في كل دورة موجية، مما يمنح المادة العازلة فترات استرخاء حراري (Thermal Relaxation) متناهية الصغر تسمح بتشتت جزئي للحرارة المتولدة نبضياً.

أما في دوائر الـ DC، يتدفق التيار بقيمته العظمى خطياً وبشكل مستمر دون أي انقطاع أو تذبذب، مما يعني غياب نقاط الصفر تماماً. هذا التدفق المستمر يمنع العازل من الحصول على أي فترات تبريد لحظية، مما يرفع من معدل الاحترار التراكمي في قلب الموصل وفقاً للعلاقة الحرارية الثابتة ($P = I^2 R$). هذا الإجهاد الحراري المتواصل والمكثف يُسرّع من عملية التقادم الفيزيائي للعوازل (Insulation Degradation) ويُقلل من عمرها الافتراضي، مما يفرض هندسياً اختيار مواد عزل ذات متانة حرارية وكيميائية فائقة لكابلات الـ DC (مثل العوازل المخصصة للطاقة الشمسية المتوافقة مع معيار EN 50618) لتتحمل هذه البيئة التشغيلية القاسية مقارنة بكابلات الـ AC.

## فيزيائية الحماية بالمصهرات المستمرة (DC gPV Fuses)

#### آلية الانصهار الحراري تحت تيارات الخطأ العكسية

تُصمم المصهرات المخصصة للأنظمة الكهروضوئية، والمعروفة بفئة **gPV** وفقاً للمعيار المعياري IEC 60269-6، لحماية السلاسل الشمسية من تيارات الخطأ العكسية (Reverse Fault Currents) التي تتدفق من السلاسل السليمة المربوطة على التوازي نحو سلسلة أصابها عطل قصر. ونظراً لأن تيارات الأعطال في الجانب المستمر للمنشآت الشمسية تكون مقيدة فيزيائياً وقريبة من قيم التشغيل الطبيعية، فإن مصهرات gPV تُصنع بعناصر انصهار فلزية دقيقة (من الفضة أو النحاس) تحتوي على تضييقات هندسية معيرة (Notches). عند سريان تيار عكسي يتجاوز عتبة الفصل الحرجة (تتراوح عادة بين $1.35 \times I_n$ و $1.45 \times I_n$)، ترتفع كثافة التيار بشكل حاد عند هذه النطاقات الضيقة، مما يولد حرارة جولية مركزة ($I^2Rt$) تؤدي إلى صهر المادة وعزل السلسلة المعطوبة بدقة وقبل تضرر الخلايا الكهروضوئية.

#### تحديات إخماد القوس المستمر ودور رمال الكوارتز

يُمثل إخماد القوس الكهربائي المستمر (DC Arc) تحدياً هندسياً كبيراً مقارنة بالقوس المتردد (AC Arc)؛ إذ يمر التيار المتردد جيبياً بنقطة الصفر مرتين في كل دورة، مما يمنح وسط الفصل فرصة طبيعية للتبريد وإخماد الشرارة تلقائياً. بالمقابل، يتميز التيار المستمر بثبات قيمته وغياب نقاط الصفر، مما يجعل القوس المتولد لحظة انصهار الفتيل مستقراً، شديد الحرارة، ومستمر التأين في الفراغ ما لم يتم إخماده قسرياً.

للتعامل مع هذه الظاهرة، تُملأ خرطوشة المصهر بإحكام بـ **رمال الكوارتز (Quartz Sand)** عالية النقاء. ولحظة نشوء القوس الكهربائي، تمتص رمال الكوارتز المحيطة الطاقة الحرارية العالية للقوس وتنصهر، مما يؤدي إلى تبريد بلازما القوس بسرعة فائقة. ينتج عن هذا التفاعل الفيزيائي تشكّل غلاف زجاجي عازل غير متبلور يُعرف بالـ (Fulgurite) يطوق مسار الشرارة، مما يضيق مسار القوس فيزيائياً ويرفع مقاومته الكهربائية إلى حد يمنع تدفق الشحنات، فيجبر القوس المستمر على الانطفاء السريع والآمن داخل جسم المصهر.

> **[موضع صورة توضيحية 6: مقطع عرضي لفيوز DC يوضح مادة الكوارتز الداخلية وكيفية إطفاء الشرارة المستمرة]**

### التكوين الهندسي لصندوق تجميع التيار المستمر (PV Combiner Box)

#### تجميع السلاسل وهندسة البارات النحاسية

يقوم صندوق تجميع التيار المستمر بوظيفة هندسية محورية تتمثل في دمج التيارات الكهربائية القادمة من مخرجات السلاسل الكهروضوئية المتوازية (Strings Aggregation)، وتحويلها إلى مسار رئيسي موحد ذي مقطع كبير يتجه نحو دخل العاكس. تعتمد هذه العملية بنيوياً على البارات النحاسية (Busbars) المصنوعة من النحاس الأحمر عالي الناقلية والمطلي بطبقة من القصدير لحمايته من الأكسدة والتآكل الكيميائي. وتُحسب الأبعاد الفيزيائية ومساحة مقطع هذه البارات بدقة لتتحمل التيار الإجمالي المتجمع الناجم عن ضرب عدد السلاسل في تيار القصر لكل منها ($N \times I_{sc}$) مع تطبيق معاملات الأمان المعيارية، مما يضمن خفض المفاقيد الأومية ومنع الارتفاع الحراري، بالإضافة إلى توفير صلابة ميكانيكية كافية لمقاومة قوى التشويه الديناميكية المغناطيسية التي تنشأ بين البارات عند تدفق تيارات الأعطال العنيفة.

#### مكونات الأمان والوقاية

تتكامل داخل صندوق التجميع منظومة حمائية متعددة المستويات لتأمين جانب التيار المستمر قبل إرسال القدرة إلى العاكس، وتتوزع هذه المكونات وظيفياً وفقاً للتالي:

- **مصهرات السلاسل (String Fuses):** تُثبت على حوامل معزولة وتتصل على التوالي مع القطبين الموجب والسالب لكل سلسلة (أو القطب الموجب فقط حسب معايير التصميم)؛ وتكمن وظيفتها في عزل السلسلة المعطوبة فوراً وبشكل مستقل في حال تدفق تيار عكسي إليها، مما يحمي الألواح من الاحتراق الموضعي.
    
- **قاطع الـ DC الرئيسي (Main DC Circuit Breaker / Disconnector):** يُمثل وسيلة الفصل والعزل الميكانيكية الرئيسية للمحطة الكهروضوئية، ويُوضع عند المخرج النهائي لصندوق التجميع. يُصمم هذا القاطع هندسياً ليكون قادراً على قطع وإطفاء تيار الحمل الكامل بأمان تحت ظروف الجهد المستمر المرتفع ($V_{oc}$) للمنظومة، مما يتيح عزل صندوق التجميع كلياً أثناء عمليات الصيانة الدورية أو في حالات الطوارئ.
    
- **مانعات الصواعق والجهود العابرة (Surge Protective Devices - SPD):** تُربط هذه الواقيات على التوازي بين البارات الرئيسية الموجبة والسالبة وخط التأريض الوقائي، وتُختار من النمط المخصص للتيار المستمر (Type 2 أو Type 1+2). تعتمد تكنولوجياً على المقاومات المتغيرة مع الجهد (Metal Oxide Varistors - MOV) التي تنخفض مقاومتها الفيزيائية اللحظية إلى الصفر تقريباً في زمن بالنانو ثانية عند حدوث صاعقة أو قفزة جهد عابرة، ممّا يفتح مساراً منخفض المقاومة يوجه تيار الصاعقة الفائق مباشرة إلى الأرض، وبذلك يتم تفريغ الطاقة الحثية لحماية عوازل الكابلات والدوائر الإلكترونية الحساسة داخل العاكس الشمسي.
