MAQattan/My-Graduation-Project/GP_Obsidian/Thesis/9/Draft/كابلات التيار المتردد (AC Cables).md

### التصنيفات البنيوية للموصلات 

ترتبط التهيئة البنيوية لقلوب الموصلات الكهربائية مباشرة بطبيعة النظام الكهربائي والوظيفة التشغيلية المراد تحقيقها في محطة الطاقة الشمسية؛ حيث تُصنف الكابلات بناءً على عدد القلوب إلى أحادية القلب (Single-Core) ومتعددة القلوب (Multi-Core). تُعد الكابلات أحادية القلب الخيار الهندسي المهيمن في تمديدات الجانب المستمر (DC Side) لربط السلاسل الكهروضوئية بصناديق التجميع (Combiner Boxes) أو العواكس، نظراً لسهولة تمريرها وعزلها، كما تُستخدم في خطوط القدرة الكبيرة لجانب التيار المتردد (AC Side) لكل طور على حدة لتجنب تيارات الدوامة والإجهادات الحرارية المرافقة للكابلات المتعددة ذات الأقطار الضخمة. في المقابل، تُستخدم الكابلات ثنائية القلوب (2-Core) في دوائر التحكم والتغذية المساعدة أحادية الطور، بينما تُخصص الكابلات ثلاثية القلوب (3-Core) لمخرجات العواكس ثلاثية الأطوار المتصلة بأحمال متزنة أو الموجهة نحو محولات الرفع حيث لا حاجة لنقل خط المحايد. أما الكابلات رباعية القلوب (4-Core)، فتشكل العصب التوزيعي للأنظمة التي تغذي أحمالاً غير متزنة أو تتطلب نظام تأريض يشترط مرافقة خط المحايد للأطوار الثلاثة لضمان مسار آمن لتيارات عدم الاتزان والتيارات التوافقية الراجعة.

من جانب آخر، ينقسم التصنيف البنيوي الداخلي للمادة الناقلة إلى موصلات مصمتة (Solid) تتكون من سلك مصمت واحد، وموصلات مجدولة مرنة (Stranded/Flexible) تتألف من مجموعة شعيرات معدنية دقيقة ملتفة حول بعضها هندسياً. تقتصر الموصلات المصمتة على التطبيقات الإنشائية الثابتة تماماً التي لا تتعرض لأي حركات ديناميكية، نظراً لصلابتها وقابليتها العالية للكسر عند الانحناء المتكرر. في المقابل، تفرض بيئة تشغيل المنظومات الكهروضوئية—خاصة تلك المثبتة على هياكل تتبع شمسية متحركة (Solar Trackers) أو المعرضة لاهتزازات مستمرة ناتجة عن الرياح الإستاتيكية والديناميكية على الأسطح—الاعتماد الحصري على الموصلات المجدولة المرنة. تمنح بنية الجدل الشعيرية للكابل مرونة ميكانيكية فائقة تتيح له امتصاص الاهتزازات وتوزيع الإجهادات الميكانيكية على كامل القطر، مما يمنع ظاهرة الكلل أو التعب الميكانيكي للمعدن (Mechanical Fatigue) ويقضي على احتمالية تشقق الناقل أو انفصاله داخل عازله بمرور الزمن.

> **[موضع صورة توضيحية 4: صورة فوتوغرافية عالية الجودة توضح الفرق البنيوي بين الموصل المصمت والمجدول]**

### التسميات الفنية ومواد العزل المعيارية 

#### التحليل المقارن بين عوازل PVC وعوازل XLPE

تُصنف مواد عزل كابلات القدرة في المنظومات الكهروضوئية بناءً على خصائصها الحرارية والفيزيائية، ويبرز هنا الفارق الجوهري بين عوازل بولي فينيل الكلوريد (PVC) وعوازل البولي إيثيلين التشابكي (XLPE). يمتلك عازل الـ PVC بنية لدنة بالحرارة (Thermoplastic) تحد من درجة حرارة تشغيله المستمر عند 70°C، وتصل عتبة تحمله الحراري أثناء أعطال القصر إلى 160°C كحد أقصى. في المقابل، يتميز عازل الـ XLPE ببنية شبكية ثلاثية الأبعاد ناتجة عن معالجة التشابك الجزيئي (Cross-linking)، مما يرفع درجة حرارة تشغيله المستمر إلى 90°C ويمنحه قدرة على تحمل حرارة القصر اللحظية حتى 250°C دون حدوث انصهار أو تشوه فيزيائي للمادة. تتيح هذه المتانة الحرارية لعوازل XLPE تمرير سعات تيار أعلى (Current-Carrying Capacity) لنفس مساحة مقطع الموصل مقارنة بالـ PVC، فضلاً عن انخفاض الفقد العازلي ومقاومتها العالية للتقادم الحراري في البيئات ذات درجات الحرارة المرتفعة التي تميز المحطات الشمسية.

#### الكابلات المسلحة (Armoured Cables) وتطبيقات الدفن المباشر

تُصمم الكابلات المسلحة بطبقة حماية ميكانيكية معدنية لحماية القلوب الداخلية والعوازل من الإجهادات الميكانيكية الخارجية، وتنقسم هندسياً إلى كابلات مسلحة بأسلاك فولاذية (Steel Wire Armoured - SWA) للكابلات متعددة القلوب، وأسلاك ألومنيوم (Aluminium Wire Armoured - AWA) للكابلات أحادية القلب تجنباً لتولد تيارات دوامية (Eddy Currents) وخسائر مغناطيسية في التسليح عند مرور التيار المتردد. تُعد هذه الكابلات الخيار الهندي القياسي لتطبيقات الدفن المباشر (Direct Burial) في خنادق الأرض دون الحاجة لقمصان أو قنوات حماية (Conduits) ممتدة؛ حيث يوفر التسليح المعدني درعاً واقياً ضد قوى السحق الناتجة عن حركة الآليات الثقيلة، واهتزازات التربة، وضغط الصخور الحادة، بالإضافة إلى منع اختراق القوارض والرطوبة الأرضية، مما يضمن سلامة خطوط نقل القدرة الرئيسية للمحطة بمرور الزمن.

### الأكواد الدولية لترميز الألوان في دوائر الـ AC

تخضع عملية ترميز ألوان الموصلات في جانب التيار المتردد (AC) لمعايير دولية صارمة تضمن سلامة فرق الصيانة وتمنع أخطاء التوصيل الكارثية مثل عكس تتابع الأطوار (Phase Sequence) أو حدوث قصر مباشر بين الأطوار. يُعد معيار اللجنة الكهروتقنية الدولية **IEC 60445** النظام الأكثر انتشاراً عالمياً وفي المحطات الكهروضوئية؛ حيث يُحدد لون الموصل وفقاً لوظيفته الكهربائية بدقة. ففي الأنظمة ثلاثية الأطوار، يُرمز للطور الأول (**L1**) باللون البني، وللطور الثاني (**L2**) باللون الأسود، وللطور الثالث (**L3**) باللون الرمادي، بينما يُخصص اللون الأزرق الفاتح لخط المحايد (**N**)، ويُفرَض استخدام المزيج اللوني الأخضر والأصفر معاً حصرياً لموصل التأريض الوقائي (**PE**).

في المقابل، يعتمد كود الكهرباء الوطني الأمريكي **NEC** نظاماً مغايراً يرتبط مباشرة بمستوى الجهد التشغيلي للمنظومة الكهربائية. ففي الأنظمة الصناعية وتوزيع القدرة (مثل 277/480 فولت) الشائعة في خطوط ربط المحطات الشمسية الكبيرة، تُرمز الأطوار الثلاثة بالألوان البني، والبرتقالي، والأصفر بالتتابع، ويُحدد اللون الرمادي لخط المحايد. أما في أنظمة الجهد المنخفض الفرعية (مثل 120/208 فولت)، فتُرمز الأطوار بالأسود، والأحمر، والأزرق، مع تخصيص اللون الأبيض للمحايد، في حين يظل اللون الأخضر الصريح (أو الموشى بالأصفر) رمزاً ثابتاً للأرضي في كلا الجهدين. ويُعد الالتزام الصارم بتوحيد أحد هذين الكودين في وثائق المشروع والمطابقة الميدانية ركيزة أساسية للأمان ومنع الحوادث الكهربائية داخل لوحات التوزيع.
