MAQattan/My-Graduation-Project/GP_Obsidian/Thesis/9/Draft/مسودة 01 - حمايات وكابلات.md

# مفاهيم الحماية واختيار الكابلات والحمايات في الجانب المتردد (AC) من المنظومة الشمسية
## تصنيفات وقواطع الحماية في الأنظمة الكهربائية

تُعد قواطع الحماية الكهربائية (Circuit Breakers) الركيزة الأساسية لضمان سلامة الأفراد والمعدات في المنظومات الكهروضوئية، حيث تعمل كأجهزة فصل وتحكم (Switches) تتيح فتح وإغلاق الدوائر الكهربائية يدوياً، فضلاً عن دورها الآلي في استشعار وفصل الأعطال. ويتم تصنيف هذه القواطع هندسياً إلى ثلاث فئات رئيسية بناءً على **سعة التيار (Current Capacity)** ونطاق الاستخدام التشغيلي، وهي كالآتي:

### **1. قواطع الدورة المصغرة (Miniature Circuit Breaker - MCB)**

يُمثل هذا النوع المعيار الهندسي الأكثر استخداماً في حماية المنظومات الشمسية المنزلية والتجارية المتوسطة، حيث صُممت للتعامل مع تيارات تبدأ من **10 أمبير وتصل حتى 125 أمبير** كحد أقصى. وتبرز أهمية هذه القواطع في أن معظم استخدامات القدرة في المنظومات الشمسية تقع ضمن هذا النطاق، مما يجعلها الخيار الأول للمهندسين عند تصميم لوحات التوزيع الفرعية والربط بين العاكس (Inverter) والأحمال. وتتوفر هذه القواطع في السوق ضمن **سعات قياسية (Standard Ratings)** محددة (مثل 10، 16، 20، 25، 32، 40، 50، 63، 80، 100، 125 أمبير)، ويجب على المصمم اختيار أقرب سعة قياسية أعلى من التيار المحسوب للمنظومة.

### **2. قواطع الدورة المصبوبة (Molded Case Circuit Breaker - MCCB)**

تُستخدم هذه القواطع عند الانتقال إلى مستويات طاقة أعلى، حيث يبدأ نطاق عملها من **25 أمبير ويصل إلى 1600 أمبير**. ونظراً لقدرتها العالية على تحمل التيارات الكبيرة، يتم تركيبها بشكل أساسي في **لوحات التوزيع الرئيسية** للمباني الضخمة أو المنشآت الصناعية التي تتطلب سعة تيار تفوق حدود الـ MCB التقليدية.

### **3. قواطع الدورة الهوائية (Air Circuit Breaker - ACB)**

يُعد هذا النوع الأضخم في عائلة القواطع، ويُستخدم حصراً في **محطات التوزيع الكبرى** والشبكات الكهربائية ذات الأحمال الفائقة؛ إذ يبدأ نطاق تياره من **630 أمبير ويصل إلى 6000 أمبير**. وتعتمد هذه القواطع على آلية تبريد القوس الكهربائي في الهواء، وهي غير مستخدمة عادةً في التمديدات المباشرة للمنظومات الشمسية المتوسطة إلا في حال ربط مزارع شمسية عملاقة بالشبكة القومية.

## التكوين الهندسي للأقطاب (Poles) وتطبيقات الربط

يُمثل **التكوين الهندسي للأقطاب (Poles)** المعيار التصميمي الذي يحدد مدى شمولية الحماية والتحكم في الدوائر الكهربائية، حيث تعتمد فعالية فصل المنظومة الكهروضوئية عن الشبكة أو الأحمال على عدد المسارات التي يقوم القاطع بفتحها وإغلاقها متزامناً. ويتم اختيار عدد الأقطاب بناءً على نوع النظام الكهربائي (أحادي أو ثلاثي الأطوار) ومستوى الأمان التشغيلي المطلوب.

ويمكن تفصيل تصنيفات الأقطاب وتطبيقاتها الهندسية وفق المنهجية الأكاديمية التالية:

### **أولاً: قواطع الأنظمة أحادية الطور (Single Phase)**

تُستخدم هذه القواطع في المنظومات الشمسية الصغيرة والمتوسطة التي ترتبط بشبكة جهد 220 فولت، وتنقسم إلى نوعين أساسيين:

1. **القاطع أحادي القطب (1-Pole / 1P):** صُمم هذا القاطع ليتحكم في مسار واحد فقط وهو خط الطور (Line/Phase). تكمن وظيفته في توفير الحماية الحرارية والمغناطيسية لهذا الخط، بينما يظل خط التعادل (Neutral) متصلاً بالدائرة بشكل دائم عبر "بارة النيوترال" دون وجود وسيلة فصل آلية عليه.
2. **القاطع ثنائي القطب (2-Pole / 2P):** يقوم هذا النوع بفتح وإغلاق مسارين كهربائيين في وقت واحد (الطور والتعادل). هندسياً، يُعد القاطع ثنائي القطب **أكثر أماناً (More Safety)** من أحادي القطب؛ لأنه يضمن العزل التام للمنظومة عن الشبكة أثناء الصيانة، مما يمنع حدوث صدمات كهربائية ناتجة عن تسرب تيار عبر خط التعادل في حال وجود عدم اتزان في الشبكة العامة.

### **ثانياً: قواطع الأنظمة ثلاثية الأطوار (Three Phase)**

تُعتبر المعيار الأساسي في المشاريع التجارية الكبرى (مثل البنوك والمصانع) التي تعمل بجهد 380 فولت، وتصنف كالآتي:

1. **القاطع ثلاثي الأقطاب (3-Pole / 3P):** يضطلع بمهمة حماية وفصل الأطوار الثلاثة (L1, L2, L3) بشكل متزامن. يُستخدم هذا النوع عندما تكون الأحمال متزنة تماماً أو عندما لا تفرض الأكواد المحلية فصل خط التعادل، حيث يُربط النيوترال مباشرة بلوحة التوزيع.
2. **القاطع رباعي الأقطاب (4-Pole / 4P):** يوفر حماية شاملة للأطوار الثلاثة بالإضافة إلى خط التعادل. يُعد الخيار الهندسي المفضل في الأنظمة المرتبطة بالشبكة لضمان **أقصى درجات الأمان (Max Safety)**؛ حيث يمنع أي تدفق للتيارات المتبقية أو "تيارات الخطأ" من الشبكة باتجاه العاكس (Inverter) أو العكس خلال فترات الفصل، مما يحمي المكونات الإلكترونية الدقيقة للعاكس من التلف.

### **ثالثاً: الأهمية الهندسية لفصل خط التعادل (Neutral Isolation)**

يؤكد التحليل الفني أن الاعتماد على القواطع التي تفصل النيوترال (2P و 4P) ليس مجرد خيار تكميلي، بل هو ضرورة في تطبيقات الطاقة الشمسية للأسباب التالية:

- **الحماية أثناء الصيانة:** يضمن الفصل الفيزيائي للنيوترال عدم وجود أي فرق جهد (Potential Difference) بين أجزاء النظام والأرض، مما يحمي الفنيين من مخاطر "النيوترال الحي".
- **توافق كود الألوان والربط:** تسهل هذه القواطع عملية الربط المنظم وفق الأكواد الدولية؛ حيث يتم تمييز خطوط الطور بالألوان (أسود، أحمر، أزرق) وخط التعادل باللون (الأبيض أو الأزرق الفاتح)، ويتم إدخالها جميعاً في القاطع لضمان استمرارية الحماية.
- **تجنب الفصل الخاطئ:** يساعد فصل النيوترال في الأنظمة المزودة بحماية ضد التسريب الأرضي (Earth Leakage) في دقة استشعار العطل ومنع الفصل العشوائي الناتج عن اضطرابات الشبكة الخارجية.

## الوظائف الأساسية للقاطع الكهربائي كعنصر حماية

يُعد القاطع الكهربائي (Circuit Breaker) الجهاز الأكثر حيوية في منظومة الحماية الكهربائية للجانب المتردد (AC)، حيث يجمع بين كونه أداة تحكم يدوية وبين كونه آلية دفاعية ذكية تعمل بشكل تلقائي عند استشعار الخلل. وتستند المنهجية الهندسية في تصميم المنظومات الشمسية المرتبطة بالشبكة إلى تعريف **الأدوار الأربعة الجوهرية** التي يؤديها القاطع لضمان استمرارية التشغيل وسلامة المكونات.

ويمكن تفصيل هذه الوظائف الأساسية وفق التحليل الفني التالي:

### **1. العمل كمفتاح يدوي للوصل والفصل (Manual Switch)**

بالرغم من الطبيعة الحمائية للقاطع، إلا أنه يُستخدم في المقام الأول كـ **جهاز فصل ميكانيكي** يتيح للفنيين التحكم في تدفق الطاقة يدوياً. تكمن الأهمية التطبيقية لهذه الوظيفة في تمكين إجراء أعمال الصيانة الدورية على العاكس (Inverter) أو لوحات التوزيع عبر فصل الدائرة فيزيائياً، مما يوفر بيئة عمل آمنة خالية من الجهد الكهربائي. ويتميز القاطع هنا بقدرته على فتح وإغلاق الدائرة تحت ظروف التشغيل العادية دون التأثير على جودة الملامسات الداخلية.

### **2. الحماية ضد تيار القصر (Short Circuit Protection)**

يُمثل تيار القصر الحالة الكهربائية الأكثر خطورة، وتحدث عند تلامس مباشر بين خط الطور (Phase) وخط التعادل (Neutral) أو بين طورين مختلفين، مما يؤدي إلى انخفاض المقاومة لدرجة تقترب من الصفر.

- **الفيزيائية الهندسية:** يؤدي هذا التصادم إلى ارتفاع لحظي وهائل في شدة التيار يتراوح ما بين **10 إلى 100 ضعف** التيار الطبيعي للمنظومة.
- **آلية العمل:** يعتمد القاطع في هذا الدور على **الميكانزم المغناطيسي (Magnetic Mechanism)**؛ حيث يولد التيار العالي جداً مجالاً مغناطيسياً قوياً داخل ملف داخلي يقوم بجذب "تقل" أو ذراع الفصل فوراً وبزمن استجابة فائق الصغر (أقل من دورة واحدة) لقطع التيار قبل أن تتدمر الدوائر الإلكترونية للعاكس أو تشتعل الأسلاك.

### **3. الحماية ضد الحمل الزائد (Overload Protection)**

تحدث حالة الحمل الزائد عندما تُسحب طاقة من المنظومة تتجاوز القدرة المقننة التي صُممت من أجلها (مثلاً تشغيل أحمال بنك إضافية تفوق قدرة العاكس)، ويكون التيار فيها أعلى من الطبيعي ولكن ليس بمراحل كارثية كتيار القصر.

- **الفيزيائية الهندسية:** يتراوح تيار الحمل الزائد (Overload) عادة بين **1.25 إلى 2.5 ضعف** التيار الاسمي ($I_{rated}$).
- **آلية العمل:** يستخدم القاطع هنا **الميكانزم الحراري (Thermal Mechanism)** المعتمد على "الشريحة ثنائية المعدن" (Bimetallic Strip). تتميز هذه الآلية بوجود **تأخير زمني (Time Delay)** مقصود؛ حيث يسمح القاطع بمرور الزيادة الطفيفة لفترة وجيزة للتمييز بين "تيارات بدء التشغيل" (Starting Currents) وبين الأعطال الفعلية، فإذا استمرت الحرارة في الارتفاع نتيحة استمرار الحمل الزائد، تنحني الشريحة وتؤدي لفصل القاطع.

### **4. حماية الكابلات من الانهيار والاحتراق (Cable Protection)**

تعد هذه الوظيفة هي الغاية النهائية من الربط الهندي بين القاطع والكابل؛ فالمهمة الرئيسية للقاطع ليست حماية العاكس فحسب، بل منع **الاحتراق الحراري للوصلات**.

- **قاعدة التنسيق (Coordination):** تفرض المعايير الهندسية أن تكون سعة القاطع المختارة دائماً **أقل** من قدرة الكابل على تحمل التيار (Ampacity).
- **التطبيق العملي:** إذا تم استخدام كابل يتحمل 20 أمبير مع قاطع 16 أمبير، فإن القاطع سيفصل عند وصول التيار إلى 18 أمبير (حالة أوفرلود)، مما يحافظ على الكابل بارداً وسليماً. أما إذا عكسنا الاختيار، فإن الكابل سيسخن ويحترق تماماً قبل أن "يشعر" القاطع بوجود مشكلة، مما يسبب حرائق في تمديدات البنك.

## فيزيائية تيار القصر وآلية الحماية المغناطيسية

تُمثل ظاهرة **تيار القصر (Short Circuit)** الحالة الكهربائية الأكثر حرجاً وخطورة في الدوائر المترددة (AC)، حيث تنشأ نتيجة تلامس مباشر ومفاجئ بين موصلين ذوي فرق جهد مختلف، مثل تلامس خط الطور (Phase) مع خط التعادل (Neutral) أو تلامس طورين مختلفين في الأنظمة ثلاثية الأطوار. وتتميز هذه الظاهرة فيزيائياً بانخفاض المقاومة الكهربائية عند نقطة التلامس إلى مستويات تقترب من الصفر، مما يؤدي إلى هبوط الجهد وتدفق تيار هائل يتجاوز حدود التصميم الآمن للمنظومة.

ويمكن تفصيل المحددات الفيزيائية وآلية الحماية المغناطيسية وفق الآتي:

### **أولاً: الخصائص الفيزيائية لتيار القصر**

تؤدي ظاهرة القصر إلى تحول مسار التيار من الأحمال الطبيعية إلى مسار ذي مقاومة متدنية جداً، مما يسبب طفرة تيار لحظية تتراوح قيمتها ما بين **10 إلى 100 ضعف** قيمة التيار المقنن للمنظومة ($I_{rated}$). وفي المشاريع الكبرى، قد تصل شدة هذا التيار إلى مستوى **الكيلو أمبير** (مثلاً 1000 أمبير أو أكثر)، وهو ما يولد طاقة حرارية وميكانيكية هائلة قادرة على صهر الأسلاك وتدمير المكونات الإلكترونية للعاكس في أجزاء من الثانية إذا لم يتم التدخل الفوري. **العلاقة الرياضية التقريبية لتيار القصر:** $$I_{sc} \approx (10 \to 100) \times I_{rated}$$
### **ثانياً: آلية الحماية المغناطيسية (Magnetic Trip)**

يعتمد القاطع الكهربائي في مواجهة تيار القصر على **الملف المغناطيسي (Solenoid/Coil)** الداخلي، والذي يعمل كمستشعر فائق السرعة للتدفق المفاجئ للتيار. وتتلخص آلية عمله في النقاط التالية:

1. **في ظروف التشغيل العادية:** يمر التيار الطبيعي عبر الملف مولداً مجالاً مغناطيسياً ضعيفاً لا يكفي لتحريك الأجزاء الميكانيكية للقاطع.
2. **عند حدوث القصر:** يولد التيار العالي جداً مجالاً مغناطيسياً قوياً وآنياً يقوم بجذب "ثقل" أو مكبس (Plunger) مرتبط بزنبرك الفصل.
3. **الفصل اللحظي:** يؤدي تحرك المكبس إلى فتح الملامسات الكهربائية في زمن استجابة فائق الصغر (Instantaneous)، مما يقطع الدائرة ويحمي المنظومة قبل وصول التيار لذروته التدميرية.

### **ثالثاً: تكنولوجيا إخماد الشرارة (Arc Chutes)**

ينتج عن عملية الفصل الميكانيكي للملامسات تحت ضغط التيارات العالية جداً نشوء **شرارة كهربائية (Electric Arc)** ذات درجات حرارة مرتفعة جداً قد تسبب تلف القاطع أو نشوب حريق. وللتغلب على ذلك، يتم تزويد القواطع بـ **غرف إخماد الشرارة (Arc Chutes)** التي تعمل وفق الأسس الفيزيائية التالية:

1. نقاط التلامس القوسية (Arc contacts): تنشأ الشرار من نقاط التلامس الداخلية عند فصل القاطع.
2. زيادة المقاومة: يتم تصميم مسار الشرارة (Arc runners) بحيث تُجبر الشرارة على التمدد والابتعاد عن نقاط التلامس (Arc Contacts)، وبما أن المقاومة تزداد بزيادة الطول، تضعف شدة الشرارة تدريجياً.
3. تجزئة القوس الكهربائي: تقوم ريش المعدن (Arc splitter) داخل غرف الإخماد بتقسيم الشرارة الكبيرة إلى "أجزاء صغيرة" (Small Chunks)، مما يقلل من مساحة مقطعها ويزيد من تبريدها. ومع زيادة المسافة التي تقطعها هذه الأجزاء الشرارية الصغيرة داخل ريش المعدن ستضعف حتى تنظفئ.

بفضل زيادة المقاومة والتبريد الميكانيكي، تنطفئ الشرارة نهائياً (The arc dies away) في زمن قياسي، مما يضمن سلامة القاطع وجاهزيته للعمل مرة أخرى بعد زوال العطل.

![[193.jpg|500]]
![[Air-Break-Circuit-Breaker-Diagram-2.webp]]

## فيزيائية الحمل الزائد وآلية الحماية الحرارية

تُمثل **الحماية الحرارية ضد الحمل الزائد (Overload Protection)** الوظيفة الدفاعية الثانية للقاطع الكهربائي في الجانب المتردد (AC)، وهي عملية فيزيائية تهدف إلى حماية الموصلات (الكابلات) والمكونات من التلف الناتج عن الارتفاع التدريجي والتراكمي في درجة الحرارة. وتعتمد هذه الحماية على التمييز الدقيق بين التجاوزات المؤقتة والمقبولة للتيار وبين الأعطال المستمرة التي قد تؤدي لنشوب حرائق.

ويمكن تفصيل المفاهيم الهندسية لهذه العملية وفق الآتي:

### **أولاً: التعريف الفيزيائي للحمل الزائد (Overload)**

يحدث الحمل الزائد عندما تُسحب طاقة من المنظومة الشمسية تتجاوز القدرة التصميمية المقننة، مما يؤدي لمرور تيار أعلى من **التيار الطبيعي ($I_{rated}$)** ولكن دون الوصول لمستويات تيار القصر الانفجارية.

- **الشدة الكهربائية:** يتراوح تيار الحمل الزائد هندسياً ما بين **1.1 إلى 2.5 ضعف** التيار المقنن للقاطع (بينما يصل القصر إلى 100 ضعف).
- **الأسباب التطبيقية:** ينشأ غالباً من تشغيل أحمال إضافية تفوق سعة العاكس، أو بسبب "تيارات بدء التشغيل" (Starting Currents) للأجهزة التي تحتوي على محركات.

### **ثانياً: آلية العمل عبر الشريحة ثنائية المعدن (Bimetallic Strip)**

يستخدم القاطع الكهربائي (MCB) **الميكانزم الحراري (Thermal Mechanism)** لمواجهة هذا النوع من الأعطال، وهو يعتمد بشكل أساسي على "الشريحة ثنائية المعدن" التي تعمل كجهاز استشعار حراري.

1. **التكوين:** تتكون الشريحة من معدنين مختلفين ملتصقين ببعضهما، لكل منهما **معامل تمدد حراري مختلف**.
2. **الفعل الفيزيائي:** عند مرور تيار الحمل الزائد، ترتفع درجة حرارة الشريحة؛ وبما أن أحد المعدنين يتمدد بسرعة أكبر من الآخر، تبدأ الشريحة بـ **الانحناء (Bending)** تدريجياً.
3. **الفصل الميكانيكي:** بمجرد وصول الانحناء إلى زاوية معينة، يضغط طرف الشريحة على ذراع الفصل (Trip Lever)، مما يؤدي لفتح الملامسات وانقطاع التيار.

![[Bimetal_Strip.gif]]

### **ثالثاً: ضرورة التأخير الزمني (Time Delay)**

على عكس الحماية المغناطيسية التي يجب أن تكون لحظية، تفرض القواعد الهندسية أن يكون للفصل الحراري **تأخير زمني مقصود**؛ وذلك للتمييز بين حالتين:

- **تيار بدء التشغيل (Starting Current):** عند تشغيل محركات أو بدء عمل العاكس، يرتفع التيار للحظات بسيطة (ثانية أو ثانيتين) ثم يعود للطبيعي. في هذه الحالة، تسخن الشريحة قليلاً لكنها **لا تنحني** لدرجة الفصل، ثم تبرد بمجرد انخفاض التيار، مما يمنع "الفصل المزعج" أو العشوائي للمنظومة.
- **العطل الفعلي المستمر:** إذا استمر التيار عالياً لأكثر من بضع ثوانٍ، تستمر الحرارة في التراكم حتى تصل الشريحة لنقطة الانحناء الحرجة وتفصل الدائرة، وهو ما يحمي الكابلات من الانهيار الحراري.

### **رابعاً: العلاقة العكسية ومنحنى الفصل (Time-Current Curve)**

تتبع الحماية الحرارية علاقة عكسية واضحة؛ فكلما كانت قيمة التيار أعلى، كان زمن الفصل أقصر.

- إذا كان التيار أعلى من المقنن بنسبة **20%**، قد يحتاج القاطع لعدة دقائق ليفصل (لأن الحرارة تتراكم ببطء).
- إذا زاد التيار ليصبح **ضعف** المقنن، يتقلص زمن الفصل لثوانٍ معدودة.
- تستمر هذه العلاقة حتى نصل إلى نقطة يطلق عليها **(I-magnetic)**، وهي النقطة التي يتحول فيها القاطع من الفصل الحراري البطيء إلى الفصل المغناطيسي اللحظي (Short circuit) لإنقاذ المنظومة من الدمار المحتم.

## الخصائص الفنية وسعات التيار القياسية (Standard Ratings)

تعتمد الموثوقية الهندسية في اختيار القواطع الكهربائية لمنظومة على فهم عميق للمواصفات الفنية المكتوبة على جسم القاطع، وقدرة المصمم على تحليل **منحنى الخصائص (Characteristic Curve)** الذي يربط بين شدة التيار المار وزمن الفصل. كما يلتزم المهندس المحترف بـ **السعات القياسية** المتوفرة تجارياً لضمان توافق التصميم مع الواقع الميداني.

ويمكن تفصيل المفاهيم الفنية لهذا القسم وفق المنهجية الأكاديمية التالية:

### **أولاً: تحليل منحنى الخصائص الحراري/المغناطيسي (Time-Current Curve)**

يُقسم منحنى أداء القاطع (MCB) إلى منطقتين تشغيليتين أساسيتين تعبران عن الميكانزمات الدفاعية للجهاز:

![[PV-09-09.svg]]

1. **منطقة الفصل الحراري (Thermal Trip Zone):** تمثل الجزء العلوي من المنحنى وتتعامل مع **الحمل الزائد (Overload)**؛ وتتميز بعلاقة عكسية حيث يستغرق القاطع زمناً طويلاً (قد يصل لعدة دقائق) لفصل التيارات التي تزيد بنسبة بسيطة عن التيار المقنن ($I_{rated}$)، ويقل هذا الزمن تدريجياً كلما ارتفعت شدة التيار الزائد. وتتبع هذه المنطقة خصائص زمنية عكسية (IDMT) لتمكين المنظومة من تحمل تيارات بدء التشغيل المؤقتة دون فصل مفاجئ.
2. **منطقة الفصل المغناطيسي (Magnetic Trip Zone):** تبدأ عند وصول التيار إلى قيمة حرجة تُعرف بـ **($I_{magnetic}$)**، وتتعامل مع **تيار القصر (Short Circuit)**. في هذه المنطقة، ينحدر المنحنى بشكل رأسي حاد، مما يعني أن القاطع سيفصل الدارة بشكل لحظي (Instantaneous) في زمن فائق الصغر بمجرد وصول التيار إلى **5 إلى 10 أضعاف** التيار المقنن (في قواطع الفئة C الشائعة)، وذلك لحماية العاكس والكابلات من الدمار.

ويؤكد التحليل الفني على ضرورة عدم تجاوز **أقصى تيار يتحمله القاطع** الموضح في نهاية المنحنى؛ لأن مرور تيار يفوق هذه السعة (Breaking Capacity) سيؤدي إلى احتراق القاطع وتلفه فيزيائياً قبل أن يتمكن من أداء وظيفة الفصل.

### **ثانياً: السعات القياسية المتوفرة في السوق (Standard Ratings)**

لا تُصنع قواطع الدورة بكل القيم الرقمية الممكنة، بل تتوفر ضمن **نطاقات قياسية (Standards)** محددة عالمياً لتسهيل عمليات التصميم والاستبدال. وتتلخص السعات المتاحة لقواطع الـ MCB التي تهم مشروعنا في الآتي:

- **قيم السعات القياسية (بالأمبير):** تبدأ السلسلة المعيارية من 10، وتتدرج كالتالي: **16، 20، 25، 32، 40، 50، 63، 80، 100، وصولاً إلى 125 أمبير**.
- **سعات الأنظمة الكبرى:** في حال تطلب التصميم سعات أعلى، يتم الانتقال لقواطع الـ MCCB التي تبدأ من 16 أمبير وتصل إلى **1600 أمبير**.

### **ثالثاً: المنهجية الهندسية لاختيار القاطع (Selection Rule)**

عند إجراء الحسابات الرياضية بناءً على قدرة العاكس، نادراً ما تتطابق النتيجة مع سعة قياسية موجودة في السوق، وهنا يطبق المصمم قاعدة **"البحث عن أقرب سعة قياسية للأعلى"** لضمان استقرار التشغيل:

- **التطبيق العملي:** إذا أشارت الحسابات (بعد ضرب التيار المقنن في معامل أمان 1.25) إلى حاجة المنظومة لقاطع بسعة **36 أمبير**، فبما أنه لا يوجد قاطع بهذه السعة تجارياً، يتم اختيار القاطع القياسي المتوفر مباشرة فوق هذه القيمة، وهو **40 أمبير**.
- **حالة أخرى:** إذا كانت الحاجة المحسوبة هي **43 أمبير**، يتم الانتقال مباشرة للسعة القياسية الأعلى وهي **50 أمبير**.

## أنواع وتكوينات كابلات التيار المتردد (AC Cables)

تُمثل **كابلات التيار المتردد (AC Cables)** حلقة الوصل الحيوية في الجزء الأخير من المنظومة الكهروضوئية، حيث تضطلع بمهمة نقل الطاقة الكهربائية بعد تحويلها من تيار مستمر إلى تيار متردد بواسطة العاكس (Inverter)، وصولاً إلى لوحات التوزيع الرئيسية أو الأحمال الكهربائية أو الشبكة العامة. وتعتمد المنهجية الهندسية في اختيار هذه الكابلات على نوع النظام الكهربائي (أحادي أو ثلاثي الأطوار) والمتطلبات الميكانيكية لمكان التركيب.

ويمكن تفصيل أنواع وتكوينات الكابلات المستخدمة وفق التصنيفات الأكاديمية التالية:

### **أولاً: التصنيف بناءً على عدد الموصلات (Core Configurations)**

يحدد عدد الأقطاب أو "القلوب" داخل الكابل الواحد طبيعة استخدامه في الدائرة الكهربائية، وهي كالآتي:

1. **الكابل أحادي القلب (Single Core):** هو كابل يحتوي على موصل واحد فقط محاط بعزل. يُستخدم في الأنظمة أحادية الطور عبر تمديد فردتين مستقلتين (واحدة للطور Line وأخرى للمتعادل Neutral)، كما يتوفر بنوع "أحادي القلب ذو عزل مزدوج" (SDI) لزيادة الأمان الكهربائي.
2. **الكابل ثنائي القلب (2-Core):** هو التكوين الذي يطلق عليه هندسيًا لفظ "كابل" بشكل أدق؛ حيث يجمع بداخله موصلين (الطور والمتعادل) تحت غلاف عازل خارجي واحد. يُفضل استخدامه في التمديدات المنزلية والتجارية البسيطة لسهولة التعامل معه وحمايته الميكانيكية الموحدة.
3. **الكابل ثلاثي القلب (3-Core):** يُخصص هذا النوع للربط في **الأنظمة ثلاثية الأطوار (3-Phase)** التي لا تتطلب خط متعادل، أو في بعض تطبيقات الأنظمة أحادية الطور التي تدمج (الطور، المتعادل، وخط التأريض) في كابل واحد لضمان الحماية الشاملة للأحمال.
4. **الكابل رباعي القلب (4-Core):** يُعد المعيار الهندسي الأهم في المشاريع الكبرى (مثل البنوك والمصانع)، حيث يجمع الأطوار الثلاثة مع خط المتعادل (Neutral) تحت غلاف واحد. ويُستخدم بكثافة في الربط بين مخرج العاكس ثلاثي الأطوار ولوحات التوزيع الرئيسية (MDB) لضمان اتزان النظام وتغذية الأحمال المتنوعة.

### **ثانياً: التصنيف بناءً على بنية الموصل (Conductor Structure)**

تختلف خصائص الكابل التشغيلية بناءً على شكل النحاس أو الألمنيوم الداخلي:

- **الموصل المصمت (Solid Conductor):** يتكون من سلك واحد صلب، ويمتاز بانخفاض تكلفته، ولكنه يفتقر للمرونة؛ لذا يُحظر استخدامه في الأماكن المعرضة للاهتزازات أو الحركة (مثل المواقع الصناعية) لأنه قد يتعرض للكسر والانهيار.
- **الموصل المجدول (Stranded/Flexible Cable):** يتكون من حزمة من الأسلاك الرفيعة المجدولة معًا، ويُسمى أحياناً "كابل مرن". هو النوع المفضل في تمديدات الطاقة الشمسية، خاصة عند الانحناءات وفي مسارات المواسير، لسهولة سحبه وقدرته على تحمل الإجهادات الميكانيكية دون تلف.

![[1761010792405.jpg]] 

### **ثالثاً: التسميات الفنية ومواد العزل (Insulation & Sheathing)**

تعتمد التسمية الفنية للكابل على المواد المستخدمة في عزله وحمايته، ومن أشهرها في كتالوجات الشركات المصنعة (مثل كابلات السويدي):

- **عزل PVC/PVC:** كابل معزول بمادة كلوريد متعدد الفاينيل للموصل والغلاف الخارجي، وهو شائع الاستخدام في المباني.
- **عزل XLPE/PVC:** يستخدم البولي إيثيلين التشابكي (XLPE) للموصل، مما يمنحه قدرة أعلى على تحمل درجات الحرارة المرتفعة، وهو الخيار الهندسي المتين لتمديدات القدرة الكبيرة.
- **الكابل المسلح (Armoured Cable):** كابل متعدد القلب يزود بطبقة حماية معدنية إضافية لمقاومة الصدمات العنيفة، ويُستخدم في حال دفن الكابلات مباشرة في الأرض دون مواسير.

### **رابعاً: معايير ترميز الألوان (Standard Color Coding)**

لضمان الربط الصحيح بين العاكس ولوحة التوزيع وتجنب مخاطر القصر الكهربائي، تلتزم الكابلات بكود ألوان قياسي للتيار المتردد:

- **الأطوار (Phases):** تُميز بالألوان الأسود، الأحمر، والأزرق (L1, L2, L3) في الأنظمة ثلاثية الأطوار، أو الأحمر/الأسود في أحادي الطور.
- **المتعادل (Neutral):** يُرمز له عالمياً باللون **الأبيض** أو الأزرق الفاتح (N).
- **الأرضي (Ground):** يُرمز له دائماً باللون **الأخضر أو الأصفر** (PG) لضمان حماية الأفراد من التسريب الكهربائي.

## المنهجية الرياضية لتحجيم القاطع الكهربائي (Breaker Sizing)

تعتمد **المنهجية الرياضية لتحجيم القاطع الكهربائي** في الجانب المتردد (AC) للمنظومات الشمسية على تحويل قدرة مخرج العاكس الاسمية إلى تيار مكافئ بدقة، مع مراعاة ثبات الجهد في الشبكة وتطبيق معاملات الأمان لضمان استقرار التشغيل. ويتبع المهندسون مساراً حسابياً منظماً يتكون من ثلاث مراحل أساسية لضمان اختيار القاطع الأنسب لكل مشروع:

### **المرحلة الأولى: حساب التيار المتردد المقنن ($I_{rated}$)**

بما أن الجهد في الأنظمة المرتبطة بالشبكة يكون ثابتاً (220 فولت للطور الواحد أو 380 فولت للأنظمة ثلاثية الأطوار)، فإن المتغير الأساسي في الحساب هو التيار. ويتم استخراج قيمة التيار بناءً على نوع النظام الكهربائي:

1. **في الأنظمة أحادية الطور (Single Phase):** تُشتق المعادلة من قانون القدرة المترددة ($P = V \times I \times cos(\phi)$)، وتكون العلاقة كالتالي: $$I_{rated} = \frac{\text{Inverter Output Power}}{V \times PF}$$ حيث يتم قسمة قدرة العاكس الاسمية (بالواط) على ناتج ضرب الجهد (220 فولت) في معامل القدرة (Power Factor).
    
2. **في الأنظمة ثلاثية الأطوار (Three Phase):** تراعى طبيعة الأحمال المتوازنة وتوزيع القدرة عبر المعادلة التالية: $$I_{rated} = \frac{\text{Inverter Output Power}}{\sqrt{3} \times V \times PF}$$ حيث يتم إدخال معامل الجذر التربيعي لـ 3 (حوالي 1.732) والقسمة على الجهد (380 فولت) لضمان دقة التيار في كل طور.

### **المرحلة الثانية: تطبيق معامل الأمان (Safety Factor)**

لضمان ألا يؤدي الارتفاع الطفيف في الإنتاج أو تقلبات التيار الطبيعية إلى "فصل مزعج" (Nuisance Tripping) للمنظومة، تفرض المعايير الهندسية زيادة التيار المحسوب بنسبة **25%** كمعامل أمان. **العلاقة الرياضية:** $$I_{breaker-calculated} = I_{rated} \times 1.25$$ يعد هذا المعامل حيوياً للتمييز بين ظروف التشغيل العادية وبين الأعطال الفعلية، مما يحافظ على استمرارية ضخ الطاقة للشبكة دون انقطاع عشوائي.

### **المرحلة الثالثة: الاختيار وفق السعات القياسية (Standard Ratings Selection)**

بعد الحصول على القيمة الحسابية النهائية، يتم الانتقال من الحسابات النظرية إلى الواقع التجاري؛ حيث لا تتوفر القواطع بكل القيم الرقمية، بل تتبع **سلسلة قياسية** محددة عالمياً (مثل 10، 16، 20، 25، 32، 40، 50، 63، 80، 100، 125 أمبير).

- **قاعدة الاختيار الذهبية:** يتم اختيار **أقرب سعة قياسية أعلى (The next standard rating up)** من القيمة التي تم حسابها.
- **أمثلة تطبيقية:**
    - إذا كان التيار الناتج بعد معامل الأمان هو **36 أمبير**، يتم اختيار قاطع بسعة **40 أمبير**.
    - إذا كانت القيمة المحسوبة **43 أمبير**، يتم الانتقال مباشرة إلى القاطع القياسي التالي وهو **50 أمبير**.
    - إذا كانت القيمة **65 أمبير**، يتم اختيار قاطع بسعة **80 أمبير**.

## المنهجية الرياضية لتحجيم الكابلات (Cable Sizing) واستخدام الكتالوجات

تستند **المنهجية الرياضية لتحجيم كابلات التيار المتردد (AC Cable Sizing)** في المنظومات الشمسية المرتبطة بالشبكة إلى ضمان قدرة الموصل على نقل الطاقة القصوى بأمان وكفاءة، دون تجاوز حدود الانهيار الحراري أو التسبب في مفقودات طاقية ناتجة عن هبوط الجهد. وتتجاوز هذه العملية مجرد الحسابات النظرية لتشمل مواءمة الكابل مع الظروف البيئية المحيطة، وهو ما يتم هندسياً عبر استخدام **معاملات التصحيح (Derating Factors)** والرجوع إلى **كتالوجات الشركات المصنعة**.

ويمكن تفصيل المسار الهندسي لتحجيم الكابلات وفق الخطوات الأكاديمية التالية:

### **أولاً: المنهجية الرياضية لحساب تيار الكابل التصميمي ($I_{cable}$)**

لا يتم اختيار الكابل بناءً على التيار الاسمي للمنظومة مباشرة، بل يجب أن تكون سعة الكابل أعلى من سعة القاطع الكهربائي لضمان الحماية التامة. وتتم الحسابات وفق العلاقة التالية:

1. **تحديد مرجع الحساب:** يتم الانطلاق من سعة القاطع الكهربائي ($I_{breaker}$) التي تم اختيارها في المرحلة السابقة (والتي هي بالأساس التيار المقنن مضروباً في 1.25).
2. **تطبيق معامل التصحيح (Derating Factor):** بما أن سعة التيار المذكورة في الكتالوجات تُقاس غالباً عند درجات حرارة اختبارية معينة، فإن وضع الكابل في بيئة العمل الفعلية (درجات حرارة أعلى أو وجود كابلات متجاورة) يقلل من كفاءته في تبديد الحرارة.
3. **المعادلة الأساسية:** يتم حساب التيار الذي يجب أن يبحث عنه المهندس في الكتالوجات بقسمة سعة القاطع على معامل التصحيح، والذي يُؤخذ في الأنظمة الشمسية عادةً بقيمة **0.8** لتعويض الظروف البيئية.
$$I_{cable_required} = \frac{I_{breaker_rating}}{0.8}$$ _هذه الخطوة تضمن هندسياً أن تكون سعة تحميل الكابل ($Ampacity$) دائماً أعلى من تيار فصل القاطع، مما يحمي الكابل من الاحتراق عند حدوث حمل زائد._

### **ثانياً: استخدام كتالوجات الشركات المصنعة (Manufacturer Catalogs)**

بعد الحصول على قيمة ($I_{cable-required}$)، ينتقل المصمم إلى الجداول الفنية الموفرة من شركات الكابلات (مثل السويدي أو Nexans) لتحديد مساحة المقطع المناسبة ($mm^2$). وتعتمد دقة الاختيار على محددين رئيسيين:

1. **طريقة التركيب (Installation Method):** توفر الكتالوجات جداول مختلفة بناءً على كيفية تمديد الكابلات:
    - **التركيب في الهواء الطلق (In Free Air):** حيث يكون تبريد الكابل معتمداً على الهواء المحيط، مما يعطيه سعة تحميل تيار أعلى.
    - **التركيب داخل مواسير أو قنوات (In Conduits/Pipes):** وهو النمط الأكثر شيوعاً في المشاريع التجارية (مثل البنوك) لحماية الكابلات ميكانيكياً ومن الأشعة فوق البنفسجية. وفي هذه الحالة، تكون سعة الكابل أقل نتيجة انحباس الحرارة داخل الماسورة، وهو ما يفرضه الجدول الخاص بالمواسير في الكتالوج.
2. **قاعدة الاختيار (Nearest Standard Rating Up):** يتم البحث في الجدول المختار عن **أقرب سعة تيار قياسية أعلى** من التيار الذي تم حسابه، ثم قراءة مساحة المقطع المقابلة لها.
    - **مثال:** إذا كان التيار المطلوب هو 40 أمبير، نجد في الكتالوج أن أقرب سعة أعلى هي 47 أمبير، والتي تقابل مساحة مقطع **10 ملم²**.

### **ثالثاً: المعايير الفنية الإضافية في الاختيار**

لا تكتفي المنهجية الأكاديمية بمساحة المقطع فقط، بل يتم استخراج بيانات تفصيلية من الكتالوج لضمان جودة التنفيذ:

- **القطر الكلي (Overall Diameter):** يستخدم لتحديد مقاس المواسير (Conduits) المناسبة التي ستمر الكابلات بداخلها لضمان سهولة السحب وعدم ضغط الكابلات.
- **مقاومة التيار (AC/DC Resistance):** تُستخدم هذه القيمة في حسابات **هبوط الجهد (Voltage Drop)**؛ حيث تفرض الأكواد ألا يتجاوز الهبوط نسبة 1% إلى 3% لضمان عدم ضياع القدرة المنتجة.
- **الوزن (Weight):** يتم حسابه لتقدير الأحمال الميكانيكية على حوامل الكابلات (Cable Trays) والهياكل المعدنية.

## التنسيق بين القاطع والكابل لضمان سلامة المنظومة

يُمثل **التنسيق بين القاطع الكهربائي والكابل (Protection-Cable Coordination)** المحور الأخير والأكثر حيوية في ضمان سلامة المنظومة الكهروضوئية؛ حيث تهدف هذه العملية إلى إرساء تسلسل هرمي للأمان يضمن بقاء الموصلات (الكابلات) ضمن حدودها الحرارية الآمنة طوال فترة التشغيل. وتستند هذه الممارسة إلى **القاعدة الذهبية في التصميم** التي تفرض أن تكون سعة تحميل الكابل للتيار أعلى دائماً من سعة فصل القاطع الكهربائي.

ويمكن تفصيل المحددات الهندسية والميكانيكية لهذا التنسيق وفق المنهجية الأكاديمية التالية:

### **أولاً: فلسفة القاعدة الذهبية (التراتب الهرمي للأمان)**

تعتمد سلامة المنشآت الكبرى على أن يعمل القاطع كـ "درع حراري" للكابل؛ فالمهمة الرئيسية للقاطع ليست فقط حماية العاكس، بل منع الكابل من الوصول إلى **نقطة الانهيار الحراري أو الاحتراق** نتيجة الأحمال الزائدة المستمرة.

- **المبدأ الهندسي:** يجب أن "يشعر" القاطع بالخطر ويفصل الدائرة قبل أن ترتفع درجة حرارة النحاس داخل الكابل إلى مستويات تدمر العزل.
- **العلاقة الشرطية:** $$\text{Cable Ampacity (CCC)} > \text{Circuit Breaker Rating} (I_n) > \text{Full Load Current} (I_{rated})$$ حيث تضمن هذه العلاقة أن القاطع سيسمح بمرور التيار الطبيعي، ولكنه سيفصل عند أي زيادة قبل أن يتأثر الكابل فيزيائياً.

### **ثانياً: التحليل الفيزيائي لسلوك التنسيق (حالات المقارنة)**

لإدراك أهمية هذا التنسيق، يجب تحليل الفرق بين الاختيار الصحيح والخاطئ بناءً على النتائج الميدانية:

1. **حالة التنسيق الخاطئ (Breaker > Cable):** إذا تم استخدام كابل يتحمل **12 أمبير** مع قاطع بسعة **16 أمبير**، نجد أنه عند حدوث عطل يسحب **14 أمبير**:
    - **سلوك القاطع:** لن يفصل القاطع لأن التيار (14A) أقل من سعة فصله (16A).
    - **النتيجة:** الكابل سيتعرض لتيار يفوق قدرته، مما يؤدي لسخونة مفرطة واحتراق العازل وربما نشوب حريق في المنشأة، دون أن "يشعر" نظام الحماية بالعطل.
2. **حالة التنسيق الصحيح (Cable > Breaker):** إذا تم استخدام كابل يتحمل **20 أمبير** مع قاطع بسعة **16 أمبير**، نجد أنه عند حدوث نفس العطل (سحب 18 أمبير مثلاً):
    - **سلوك القاطع:** سيفصل القاطع فوراً لأن التيار تجاوز حد الأمان (Overload).
    - **النتيجة:** يظل الكابل بارداً وسليماً تماماً لأن سعته (20A) أعلى من تيار العطل، وتتم حماية المنظومة بتكلفة صفرية (إعادة رفع القاطع فقط بعد معالجة السبب).

### **ثالثاً: الوسائل الهندسية لتحقيق التنسيق (معاملات التصحيح)**

يتحقق هذا التنسيق في مرحلة التصميم الرياضي عبر تطبيق **معامل التصحيح (Derating Factor)** الذي يرفع سعة الكابل المطلوبة آلياً لتكون أعلى من القاطع.

- عند قسمة تيار القاطع على **0.8**، ننتقل بالضرورة إلى مساحة مقطع كابل أكبر، مما يوفر "هامش أمان حراري" (Thermal Margin) يتيح للكابل العمل لسنوات طويلة دون تدهور في خواص الموصل.
- كما تفرض الأكواد الهندسية ضرورة أن يكون الكابل قادراً على تحمل **تيارات القصر (Short Circuit Currents)** لفترات زمنية وجيزة حتى يكمل القاطع عملية الفصل المغناطيسي.

### **رابعاً: مخاطر غياب التنسيق في المشاريع التجارية**

إن إهمال هذه القاعدة في التصميم قد يؤدي إلى كوارث تشغيلية؛ حيث أن الاختيار غير السليم يؤدي إلى **سخونة زائدة تراكمية** في لوحات التوزيع. وبما أن المنظومات الشمسية تعمل لساعات طويلة تحت ذروة الإنتاج، فإن أي ضعف في التنسيق سيحول الكابلات إلى "سخانات كهربائية" داخل المواسير، مما يرفع من احتمالية انهيار العزل وحدوث أعطال أرضية (Earth Faults) تسبب توقفاً كاملاً لأعمال البنك.

# مفاهيم الحماية واختيار الكابلات والحمايات في الجانب المستمر (DC) من المنظومة الشمسية

## المقارنة الهندسية بين كابلات التيار المتردد (AC) والتيار المستمر (DC)

تُعد المفاضلة بين كابلات التيار المتردد (AC) والتيار المستمر (DC) ضرورة هندسية لضمان سلامة وكفاءة المنظومة الشمسية، حيث يختلف سلوك التيارين فيزيائياً وحرارياً داخل الموصلات. وبناءً على التحليل الفني، يُحظر هندسياً استخدام كابلات الـ AC في جانب الـ DC (الممتد من الألواح وحتى العاكس) لعدة أسباب علمية جوهرية:

### **أولاً: ظاهرة التأثير القشري (Skin Effect)**

تؤثر طبيعة التيار المتردد (AC) على كيفية توزيعه داخل الموصل؛ حيث يميل التيار للتدفق على **القشرة الخارجية للموصل** (الجلد) ولا يمر في قلبه، وذلك بسبب ارتفاع الممانعة الحثية في منتصف السلك الناتج عن تغير التدفق المغناطيسي ($d\phi/dt$). أما في حالة التيار المستمر (DC)، فإن التيار يتدفق بانتظام عبر **كامل مساحة المقطع العرضي** للموصل. هذا الاختلاف الفيزيائي يجعل كابلات الـ DC تتطلب تصميماً يضمن استغلال كامل مساحة النحاس لنقل التيار دون نشوء ممانعات داخلية غير محسوبة.

![[el-current-flowing.png|500]]
![[PV-09-01.png|500]]
### **ثانياً: الإجهاد الحراري المستمر (Thermal Stress)**

يختلف التأثير الحراري الناتج عن كل نوع من التيارات بناءً على شكل الموجة وسلوك التدفق:

- **في التيار المتردد (AC):** تتذبذب موجة التيار بين القيم العظمى والصفر والتردد، مما يمنح الموصل فرصة "ليبرد" نسبياً عند مرور التيار بنقاط الصفر، وبذلك يكون التأثير الحراري التراكمي أقل.
- **في التيار المستمر (DC):** يظل التيار ثابتاً دائماً عند **قيمته العظمى (Maximum)**، مما يولد طاقة حرارية مستمرة وأعلى بكثير من التيار المتردد. لذا، يجب أن تكون كابلات الـ DC مصممة بمواد عزل تتحمل درجات حرارة تشغيلية أعلى (تصل غالباً إلى 85 أو 90 درجة مئوية) لضمان عدم انهيار الكابل تحت الضغط الحراري الدائم.

### **ثالثاً: مخاطر الأعطال ومتطلبات العزل**

تتعرض كابلات التيار المستمر لمخاطر فيزيائية وكهربائية تفوق كابلات الـ AC، خاصة عند حدوث **تيار القصر (Short Circuit)**. ويؤدي الاختيار غير السليم لنوع الكابل في جانب الـ DC إلى نشوء "نقاط ساخنة" وسخونة زائدة قد تنتهي بنشوب حرائق، نظراً لارتفاع شدة التيار المستمر في أغلب الأحيان عن نظيره المتردد في المنظومات الشمسية. لذا، تفرض المعايير الهندسية استخدام كابلات DC ذات **عزل مزدوج** ومقاومة عالية للأشعة فوق البنفسجية (UV Resistance) والعوامل الجوية لضمان حماية المنظومة من الأعطال الأرضية والانهيار المفاجئ.

## فيزيائية الحماية بالفيوزات (DC Fuses) في دوائر التيار المستمر

تُمثل **الفيوزات أو المصهرات (DC Fuses)** خط الدفاع الحراري الأول في دوائر التيار المستمر للمنظومات الكهروضوئية، حيث تكمن وظيفتها الجوهرية في حماية الموصلات والمعدات من التلف الناتج عن تدفق تيارات الخطأ المرتفعة، وتقليل مخاطر الحرائق الناجمة عن السخونة المفرطة للأسلاك. وتعتمد الممارسة الهندسية على اختيار مصهرات مخصصة للتيار المستمر (gPV) تختلف جذرياً في تصميمها الفيزيائي عن مصهرات التيار المتردد التقليدية لضمان الموثوقية والأمان.

![[dc-fuse-srd-30-1100v-01.webp]]

ويمكن تفصيل المفاهيم الأكاديمية والفيزيائية لعمل الفيوزات وفق الآتي:

### **أولاً: المبدأ الفيزيائي وآلية العمل (Mechanism of Action)**

يستند عمل المصهر إلى **التأثير الحراري للتيار الكهربائي**؛ حيث يتكون داخلياً من سلك أو شريط معدني ذي خصائص فيزيائية محددة ومقطع عرضي مدروس ليتحمل تياراً معتدلاً.

1. **في ظروف التشغيل الطبيعية:** يمر التيار عبر الموصل الداخلي للمصهر دون أن ترتفع حرارته لدرجة الانصهار.
2. **عند حدوث خطأ (Overcurrent/Short Circuit):** عندما يتجاوز التيار القيمة المقننة للمصهر، ترتفع درجة حرارة الموصل الداخلي بشكل حاد نتيجة الممانعة الكهربائية، مما يؤدي إلى **انصهاره فيزيائياً (Melting)** وقطع المسار الكهربائي فوراً، وبالتالي فصل الدائرة وحماية باقي المكونات.
3. **العزل الميكانيكي:** يُصنف المصهر كأداة حماية "غير قابلة للاسترداد"؛ أي أنه بمجرد انصهاره وفتح الدائرة، يجب استبداله بقطعة جديدة بالكامل بعد معالجة سبب العطل.

### **ثانياً: فيزيائية إخماد القوس الكهربائي في التيار المستمر (Arc Extinguishing)**

تعد هذه النقطة هي الفارق التقني الأهم بين فيوزات الـ AC والـ DC؛ ففي التيار المتردد (AC)، يمر التيار بنقطة الصفر بشكل دوري (50 أو 60 مرة في الثانية)، مما يسهل إطفاء الشرارة الناتجة عن الفصل. أما في **التيار المستمر (DC)**، فإن التيار يظل ثابتاً عند قيمته العظمى دائماً، مما يولد قوساً كهربائياً (Arc) مستمراً وشديد الحرارة عند انصهار الموصل. لذا، يتم تصميم فيوزات الـ DC داخل **خرطوشة (Cartridge)** مملوءة بمواد خامدة (مثل رمال الكوارتز) تعمل على تبريد وتجزئة القوس الكهربائي بسرعة فائقة لمنع استمرار تدفق الطاقة عبر الهواء المتأين.

![[PV-09-05.png]]
### **ثالثاً: الخصائص الفنية والمواصفات التشغيلية**

تُحدد كفاءة المصهر في حماية المصفوفة بناءً على ثلاثة معايير فيزيائية:

- **الجهد المقنن ($V_{rated}$):** يجب أن يتحمل المصهر أقصى جهد مستمر للنظام (مثل 1000V DC أو 1500V DC) لضمان عدم حدوث قصر داخلي عبر جسم المصهر بعد انصهاره.
- **سعة التيار ($I_{rating}$):** هي القيمة القصوى للتيار التي يمكن للمصهر تمريرها بصفة دائمة دون انصهار، وتتوفر ضمن سعات قياسية (Standard) مثل (10، 15، 20، 25، 30 أمبير).
- **درجة الحماية البيئية (IP Rating):** نظراً لتركيب الفيوزات غالباً في صناديق التجميع الخارجية، تُصنع قواعد الفيوزات (Fuse Holders) بمعايير حماية عالية (مثل **IP67**) لضمان مقاومتها للأتربة وتسرب مياه الأمطار صيفاً وشتاءً.

### **رابعاً: التكوين الهندسي لصندوق الحماية**

يتكون نظام الحماية بالفيوزات ميدانياً من جزأين متكاملين:

1. **المصهر (Fuse Link):** وهو الجزء المستهلك الذي يحتوي على عنصر الانصهار.
2. **حامل المصهر (Fuse Holder):** وهو الجزء الثابت الذي يُثبت على سكة (DIN Rail) داخل صندوق التجميع (Combiner Box) أو داخل العاكس، ويؤمن نقاط الاتصال الكهربائي وسهولة الاستبدال.

إن الالتزام باستخدام مصهرات **String Fuses** لكل سلسلة من سلاسل المصفوفة، وتركيبها في المسارات الموجبة والسالبة (للأنظمة غير المؤرضة)، هو ما يضمن حماية الخلايا الشمسية من "التيارات العكسية" التي قد تنشأ نتيجة ظلال كثيفة أو عطل في إحدى السلاسل المتوازية.

## المنهجية الرياضية لحساب أقصى تيار مستمر للمصفوفة ($I_{max-DC}$)

تُمثل **المنهجية الرياضية لحساب أقصى تيار مستمر ($I_{max-DC}$)** الخطوة الجوهرية الأولى في تصميم وتأمين الجانب المستمر من المنظومة الكهروضوئية، حيث تُعد هذه القيمة المرجع الأساسي (Baseline) الذي تُبنى عليه كافة حسابات تحجيم المصهرات (Fuses) وقواطع الدورة والكابلات. وتعتمد هذه الحسابات على الخصائص الفيزيائية لتوصيل الألواح وقوانين الدوائر الكهربائية لضمان استيعاب المنظومة لأعلى تدفق تيار ممكن تحت الظروف التشغيلية القصوى.

ويمكن تفصيل المحددات الهندسية لهذه المنهجية وفق القواعد التالية:

### **أولاً: تيار المصفوفة في حالات التوصيل (الفيزيائية الهندسية)**

1. **التوصيل على التوالي (Series/String):** في حالة ربط الألواح لتكوين "سلسلة"، تظل شدة التيار ثابتة عبر المسار بالكامل؛ وبذلك يكون تيار السلسلة الواحدة مساوياً لتيار اللوح الواحد.
2. **التوصيل على التوازي (Parallel):** عند ربط عدة سلاسل توازياً، فإن الجهد يظل ثابتاً بينما **تُجمع التيارات** بشكل تراكمي؛ وهذا التراكم هو ما يحدد "التيار الكلي" الذي ستتعامل معه أجهزة الحماية الرئيسية والكابلات المجمعة للقدرة.

### **ثانياً: القانون الأساسي لحساب تيار التصميم ($I_{max-DC}$)**

يتم استنتاج أقصى تيار مستمر للمصفوفة عبر العلاقة الرياضية التالية:
$$I_{max-DC} = I_{sc-module} \times N_{strings}$$
_حيث أن:_

- **$I_{sc-module}$:** هو تيار الدارة المغلقة (Short Circuit Current) للوح الشمسي عند ظروف الاختبار القياسية (STC)، وهو المعيار الهندسي الأضمن لأنه يمثل أقصى تيار فيزيائي يمكن أن ينتجه اللوح تحت أي ظرف.
- **$N_{strings}$:** هو عدد السلاسل الموصلة على التوازي والمرتبطة بمدخل واحد للعاكس أو بصندوق تجميع واحد.

### **ثالثاً: مبررات استخدام تيار القصر ($I_{sc}$) كمرجع**

تفرض الأكواد الهندسية الدولية استخدام تيار القصر ($I_{sc}$) بدلاً من تيار التشغيل ($I_{mp}$) للأسباب التالية:

- **خاصية تحديد التيار:** يُعد اللوح الكهروضوئي جهازاً "محدداً للتيار" (Current-limited device)، ولا يمكنه فيزيائياً إنتاج تيار يتجاوز قيمة الـ $I_{sc}$ الخاصة به.
- **الأمان المطلق:** استخدام القيمة القصوى المحتملة يضمن عدم حدوث "فصل خاطئ" نتيجة تقلبات الإشعاع الشمسي، ويوفر حماية تامة للمعدات من التلف الحراري عند حدوث خطأ فعلي في الدائرة.

### **رابعاً: دور $I_{max-DC}$ في تراتب التصميم (Design Hierarchy)**

تُعد النتيجة المستخرجة من هذه المعادلة هي الركيزة التي تنبثق منها باقي مراحل التصميم:

1. **تحجيم الحماية:** يُضرب $I_{max-DC}$ في معامل أمان (مثل 1.25) لتحديد سعة الفيوز أو القاطع المناسب.
2. **تحجيم الكابلات:** تُستخدم سعة الحماية المستنتجة لاحقاً (مع معاملات التصحيح الحراري) لاختيار مساحة مقطع كابلات الـ DC الرئيسية، بما يضمن بقاء الكابل دائماً "أقوى" من تيار الحماية.

## القواعد الهندسية لتحجيم مصهرات السلاسل (String Fusing)

تُمثل **القواعد الهندسية لتحجيم مصهرات السلاسل (String Fusing)** الضابط التقني لمنع حدوث الانهيار الحراري في الألواح الكهروضوئية، حيث تهدف هذه المصهرات بشكل أساسي إلى حماية الموديولات من **التيارات العكسية (Reverse Currents)** التي قد تتدفق من السلاسل السليمة نحو سلسلة تعرضت لعطل أو تظليل حاد. وتستند المنهجية الأكاديمية لاختيار هذه المصهرات إلى مواءمة القدرة الفيزيائية للوح على تحمل التيار مع معاملات الأمان التي تفرضها الأكواد الدولية.

ويمكن تفصيل المحددات التصميمية لتحجيم المصهرات وفق القواعد الهندسية التالية:

### **أولاً: المنهجية الرياضية لحساب تيار المصهر ($I_{fuse}$)**

لا يتم اختيار سعة المصهر بناءً على تيار التشغيل الطبيعي فقط، بل يجب مراعاة تقلبات الإشعاع الشمسي والإجهاد الحراري المستمر عبر تطبيق معاملات الأمان التالية:

1. **معامل الاستمرارية (Continuous Duty):** يُضرب تيار القصر للوح ($I_{sc}$) في **1.25** لضمان قدرة المصهر على تحمل التيار لعدة ساعات متواصلة دون انصهار ناتج عن الحرارة الطبيعية.
2. **معامل الفصل المزعج (Nuisance Tripping):** يُضرب الناتج في **1.25** أخرى لتجنب الفصل العشوائي الناتج عن الطفرات البسيطة في الإشعاع الشمسي؛ وبذلك يصبح المعامل الإجمالي التراكمي هو **1.56**. **المعادلة التصميمية:**
$$I_{fuse-calculated} = I_{sc-module} \times 1.56$$
_ويؤكد التحليل الهندسي أن استخدام تيار القصر ($I_{sc}$) في هذه المعادلة هو المعيار الأضمن لأن اللوح لا يمكنه فيزيائياً إنتاج تيار يتجاوز هذه القيمة._

### **ثانياً: الالتزام بالسعات القياسية (Standard Ratings)**

بعد استخراج القيمة الحسابية، ينتقل المصمم إلى الواقع التجاري باختيار **أقرب سعة قياسية للأعلى (The next standard rating up)** لضمان استقرار التشغيل وعدم انصهار المصهر في الظروف العادية.

- **السعات المعيارية المتاحة:** تتوفر مصهرات الـ DC عادةً بالقيم التالية: (6، 8، 10، 12، 15، 20، 25، 30 أمبير).
- **قاعدة المواءمة:** إذا كانت القيمة المحسوبة (بعد ضرب $I_{sc}$ في 1.56) تساوي 17.5 أمبير مثلاً، يتم اختيار مصهر بسعة **20 أمبير**.

### **ثالثاً: القيد الهندسي للأمان (Module Rating Constraint)**

يعد هذا الشرط هو الأهم لضمان سلامة الألواح؛ حيث يجب ألا تتجاوز سعة المصهر المختارة القيمة المحددة في ورقة بيانات اللوح تحت مسمى **أقصى سعة لمصهر السلسلة (Maximum Series Fuse Rating)**.

- **السبب الفيزيائي:** إذا تم اختيار مصهر ذي سعة أعلى من قدرة اللوح على تحمل التيار العكسي، فإن اللوح سيحترق ويتلف قبل أن يتمكن المصهر من استشعار العطل والانصهار.
- **القاعدة الشرطية:**
$$I_{fuse-selected} \leq \text{Maximum Series Fuse Rating (from Datasheet)}$$

### **رابعاً: شروط التركيب والتموضع الميداني**

تفرض المعايير الهندسية (مثل المعيار البريطاني أو NEC) ضوابط صارمة لتركيب هذه المصهرات لضمان شمولية الحماية:

- **حماية القطبين:** يجب تركيب مصهر على كل من الكابل **الموجب والسالب** لكل سلسلة في الأنظمة غير المؤرضة (Ungrounded Systems)؛ وذلك لضمان عزل السلسلة تماماً في حال حدوث خطأ أرضي في أي من القطبين.
- **ظروف البيئة:** يجب وضع المصهرات داخل حوامل (Fuse Holders) مخصصة للتيار المستمر وبدرجة حماية عالية (مثل IP67) لضمان عدم تأثر آلية الانصهار الحرارية بالرطوبة أو المطر.

## الحسابات الحرارية ومعاملات التصحيح لكابلات الـ DC

تستند المنهجية الهندسية في **الحسابات الحرارية ومعاملات التصحيح لكابلات الـ DC** إلى مبدأ ضمان استدامة الناقلية الكهربائية للموصل تحت أقسى الظروف الحرارية المتوقعة، حيث يهدف تحجيم الكابل إلى منع "الانهيار الحراري" للعزل الناتج عن التدفق المستمر للتيار المستمر عند ذروته العظمى. وتتجاوز هذه المرحلة الحسابات النظرية لتشمل مواءمة الكابل مع بيئة التركيب الفعلية (درجة الحرارة، وطريقة التمديد).

ويمكن تفصيل المنهجية الأكاديمية لهذا القسم وفق القواعد التالية:

### **أولاً: المرجعية الرياضية لحساب تيار الكابل التصميمي ($I_{cable}$)**

لا يتم اختيار مساحة مقطع كابل الـ DC بناءً على تيار المصفوفة فقط، بل يتم ربطه بسعة أداة الحماية (الفيوز أو القاطع) لضمان أن الكابل هو "أقوى حلقة" في الدائرة. **العلاقة الرياضية الأساسية:**
$$I_{cable-required} = \frac{I_{protection-rating}}{f_{derating}}$$ _حيث أن:_

- **$I_{protection-rating}$ :** هي السعة الاسمية للفيوز أو القاطع التي تم اختيارها في المرحلة السابقة (التيار المقنن × 1.25) .
- **$f_{derating}$ (معامل التصحيح) :** يُؤخذ هندسياً بقيمة **0.8** في الأنظمة الشمسية لتعويض الإجهاد الحراري الناتج عن ثبات موجة التيار المستمر عند قيمتها العظمى، وضمان هامش أمان يحمي الكابل من السخونة المفرطة.

### **ثانياً: التحليل الحراري لبيئة التركيب (Ambient & Installation Conditions)**

تتأثر سعة تحميل التيار (CCC) للكابل بشكل مباشر بالوسط المحيط وقدرته على تبديد الحرارة، وهو ما يفرض المفاضلة بين طريقتين للتركيب:

1. **التركيب في الهواء الطلق (In Free Air):** حيث تتيح حركة الهواء تبريد الموصل بفعالية أكبر، مما يمنحه سعة تحميل تيار أعلى مقارنة بالتركيب المغلق.
2. **التركيب داخل مواسير أو قنوات (In Conduits):** وهو النمط المفضل لحماية الكابلات من الأشعة فوق البنفسجية والعوامل الجوية. ولكن فيزيائياً، تؤدي المواسير إلى حبس الحرارة، حيث يشير الكود (NEC) إلى أن المواسير الملاصقة للأسطح تحت الشمس قد تزيد حرارتها بمقدار **33 درجة مئوية** فوق درجة الحرارة المحيطة، مما يقلل من كفاءة الكابل ويفرض اختيار مساحة مقطع أكبر.

### **ثالثاً: آلية اختيار مساحة المقطع من الجداول الفنية**

بعد تحديد قيمة ($I_{cable-required}$)، يتم الرجوع لكتالوجات الكابلات المتخصصة (Solar DC Cables) لاستخراج مساحة المقطع ($mm^2$) المناسبة، مع الالتزام بالقواعد التالية:

- **قاعدة السعة القياسية:** يتم البحث في جداول "التركيب داخل المواسير" عن **أقرب سعة تيار قياسية أعلى** من القيمة المحسوبة.
- **ثبات الجهد (Voltage Drop Constraint):** يُشترط ألا تؤدي مساحة المقطع المختارة إلى هبوط في الجهد يتجاوز **1%** في جانب الـ DC لضمان عدم ضياع القدرة المنتجة وتحقيق أقصى كفاءة لنظام الـ MPPT.

### **رابعاً: الخصائص الفيزيائية لعزل كابلات الـ DC**

بما أن التيار المستمر يولد طاقة حرارية مستمرة (بدون نقاط صفر تبريد كما في الـ AC)، تفرض المعايير الأكاديمية استخدام كابلات ذات **عزل مزدوج** (Double Insulation) ومواد مثل (XLPE) التي تتحمل درجات حرارة تشغيل تصل إلى **85-90 درجة مئوية** لضمان عدم انهيار العزل تحت الإجهاد الحراري الدائم.

## التحليل الفني لكابلات الموديولات (Module Interconnection Cables)

يُركز **التحليل الفني لكابلات الموديولات (Module Interconnection Cables)** على دراسة المواصفات الهندسية للناقل الكهربائي الذي يُشكل الحلقة الأولى في الدائرة المستمرة للمنظومة، حيث تضطلع هذه الكابلات بمهمة الربط التسلسلي بين الألواح لتكوين "السلسلة" (String) ونقل طاقة اللوح الفردية إلى نقاط التجميع. وتخضع هذه الوصلات لمعايير تصنيعية صارمة تضمن استدامتها أمام الظروف البيئية القاسية.

ويمكن تفصيل المحددات الفنية لهذه الكابلات وفق القواعد الأكاديمية التالية:

### **أولاً: المرجعية التصميمية والتحجيم (Sizing Reference)**

تعتمد المنهجية الهندسية في تحديد مساحة مقطع هذه الكابلات على البيانات الفنية الواردة في **ورقة بيانات اللوح (Module Datasheet)**، حيث تأتي معظم الألواح الحديثة مزودة بكابلات ربط مُثبتة مسبقاً في "صندوق التوصيل" (Junction Box) الخاص بها.

- **المعيار القياسي:** يُعد مقطع **4 ملم²** هو المعيار الهندسي الأكثر شيوعاً وعالمية لكابلات ربط الموديولات، وذلك لقدرته العالية على حمل تيار اللوح المنفرد ($I_{mp}$) وتيار القصر ($I_{sc}$) مع الحفاظ على أقل نسبة مفقودات ممكنة في الجهد.
- **خيارات بديلة:** تتوفر مقاطع أخرى مثل 2.5 ملم² أو 6 ملم²، ويتم المفاضلة بينها بناءً على قدرة المخرج الكلية للموديول لضمان عدم تجاوز سعة تيار الكابل (CCC).

### **ثانياً: الخصائص الفيزيائية ومواد العزل**

نظراً لوجود هذه الكابلات في بيئة خارجية مكشوفة، تفرض الأكواد الهندسية مواصفات فيزيائية خاصة يُطلق عليها تقنياً **"كابل الطاقة الشمسية" (Solar Cable)**:

1. **العزل المزدوج (Double Insulation):** لضمان أقصى درجات الأمان الكهربائي ومنع حدوث أعطال أرضية (Earth Faults) أو حرائق نتيجة تآكل العزل الفردي.
2. **المقاومة للأشعة فوق البنفسجية (UV Resistance):** يجب أن يكون الغلاف الخارجي معالجاً كيميائياً ليتحمل الإشعاع الشمسي المباشر لسنوات طويلة دون حدوث تشققات فيزيائية.
3. **المرونة الحرارية:** استخدام موصلات نحاسية مجدولة (Stranded Copper) مغطاة بطبقة من القصدير غالباً، لضمان مرونة الكابل عند الانحناءات وقدرته على تحمل درجات حرارة تشغيلية مرتفعة تصل إلى 90 درجة مئوية.

### **ثالثاً: آلية الربط الميكانيكي والكهربائي**

تستخدم كابلات الموديولات نظام **القوابس والمقابس (Plug and Socket Connectors)** الموحدة عالمياً لضمان دقة القطبية وسهولة التنفيذ.

- **منع الخطأ التصميمي:** تُصمم هذه الوصلات بقطبية موجبة وسالبة محددة لتقليل مخاطر التوصيل الخاطئ للسلاسل على التوالي.
- **آلية القفل (Locking Mechanism):** تُزود بميكانزم تأمين يمنع انفصال الكابلات نتيجة الشد الميكانيكي أو الرياح، مما يحمي الدائرة من نشوء القوس الكهربائي (Arcing) الخطير.

### **رابعاً: القواعد الهندسية للتركيب والتوجيه**

تلتزم الممارسة الأكاديمية بضوابط صارمة عند التعامل مع هذه الوصلات لضمان كفاءة النقل:

- **قاعدة المسار القصير:** يجب إبقاء الكابلات بأقصر طول ممكن لتقليل المقاومة الكهربائية.
- **تجنب الحلقات (Loops):** يُشترط هندسياً تقليل مساحة "الحلقات الموصلة" (Conductive Loops) في التمديدات لخفض مخاطر الجهد الزائد الناتج عن الصواعق (Lightning Induced Over-voltages).
- **الحماية الميكانيكية:** يُوصى بوضع الكابلات بعيداً عن حواف الهياكل المعدنية الحادة واستخدام المواسير (Conduits) في حال مرورها داخل المباني أو في مناطق معرضة للإجهاد.

## هندسة تحجيم كابلات المصفوفة الرئيسية (DC Main Cables)

تُمثل **هندسة تحجيم كابلات المصفوفة الرئيسية (DC Main Cables)** المرحلة الأكثر حيوية في نقل الطاقة الكلية المتولدة من حقل الألواح وصولاً إلى مداخل العاكس، حيث تضطلع هذه الكابلات بمهمة نقل تيار السلاسل المجتمعة (Combined Strings) الذي يتضاعف عند نقاط التجميع أو داخل صناديق التجميع (Combiner Boxes). وتخضع عملية تحجيم هذه الكابلات لمعايير هندسية صارمة تضمن الكفاءة الطاقية وتمنع الفقد الحراري والمادي في الموصلات.

ويمكن تفصيل المحددات الهندسية لتحجيم الكابلات الرئيسية وفق القواعد الأكاديمية التالية:

### **أولاً: المنهجية الرياضية لحساب تيار التصميم ($I_{main-cable}$)**

لا يتم اختيار الكابل الرئيسي بناءً على تيار التشغيل الإسمي، بل يتم ربطه بمنظومة الحماية الكلية للمصفوفة لضمان التنسيق (Coordination) الكهربائي.

1. **حساب التيار الكلي للمصفوفة:** يتم استنتاج التيار الذي سيراه الكابل الرئيسي عبر ضرب تيار القصر للوح ($I_{sc}$) في إجمالي عدد السلاسل الموصلة توازياً والمرتبطة بنفس المسار.
$$I_{total-sc} = I_{sc-module} \times N_{parallel-strings}$$
2. **تحديد سعة الحماية الرئيسية:** يُضرب التيار الكلي في معامل أمان (1.25) لتحديد سعة القاطع الرئيسي أو المصهر الرئيسي الذي يحمي الكابل.
3. **تطبيق معامل التصحيح الحراري:** يتم حساب التيار الذي يجب البحث عنه في الجداول الفنية بقسمة سعة الحماية على معامل التصحيح (**0.8**) لتعويض ظروف التركيب والحرارة المستمرة للتيار المستمر. $$I_{required-capacity} = \frac{I_{main-protection}}{0.8}$$
### **ثانياً: قيد هبوط الجهد (Voltage Drop Constraint)**

يُعد هبوط الجهد المعيار الهندسي الأكثر تأثيراً في الجانب المستمر؛ فبينما يُسمح في بعض الأكواد بهبوط يصل إلى 3% أو 5% في جانب الـ AC، تفرض الممارسات الأكاديمية الفضلى ألا يتجاوز هبوط الجهد في كابلات الـ DC الرئيسية نسبة **1%**.

- **السبب الهندسي:** أي فقد في الجهد في الجانب المستمر يقلل مباشرة من قدرة مخرج المصفوفة ويؤثر على كفاءة تتبع العاكس لنقطة القدرة القصوى (MPPT Sensing)، مما يجعل استخدام كابلات ذات مقطع أكبر استثماراً اقتصادياً أفضل من إضافة ألواح تعويضية.
- **العلاقة الفيزيائية:** تزداد قيمة هبوط الجهد طردياً مع طول المسار وعكسياً مع مساحة المقطع؛ لذا يتوجب اختيار مقطع كابل يضمن بقاء الفقد ضمن الحدود الدنيا.

### **ثالثاً: الخصائص الميكانيكية والبيئية للكابلات الرئيسية**

نظراً لأن الكابلات الرئيسية تنقل كامل قدرة المنظومة، فإنها تتطلب مواصفات تصنيعية خاصة:

- **العزل المقاوم للعوامل الجوية:** يجب أن تكون الكابلات مصنفة كـ **Solar Cables** ذات عزل مزدوج (Double Sheath) ومقاومة عالية للأشعة فوق البنفسجية (UV-resistant) لأنها تمدد غالباً في مسارات مكشوفة فوق الأسطح.
- **تحمل درجة الحرارة:** يجب أن يتحمل العزل درجات حرارة تشغيلية تصل إلى **90 درجة مئوية**، خاصة عند تمديدها داخل مواسير (Conduits) تلامس أسطح المباني تحت الإشعاع المباشر.
- **التكوين المادي:** يُفضل استخدام الموصلات النحاسية المجدولة المطلية بالقصدير لمقاومة التآكل وضمان المرونة الكافية أثناء التمديد في المسارات الطويلة.

### **رابعاً: تراتب الاختيار من الجداول القياسية**

بعد استيفاء شروط التيار وهبوط الجهد، يتم الرجوع إلى الكتالوجات الفنية (مثل Eland أو السويدي) لاختيار مساحة المقطع المقننة ($mm^2$):

- يتم اختيار **أقرب سعة قياسية أعلى** تحقق شرط التيار بعد التصحيح، وشرط هبوط الجهد عند المسافة المحددة.
- يجب التأكد من توافق مقطع الكابل المختار مع فتحات التوصيل في العاكس (Inverter Terminals) وصندوق التجميع لضمان الربط الميكانيكي السليم.

## الأكواد الدولية لترميز الألوان في دوائر الـ DC

يُعد الالتزام بـ **الأكواد الدولية لترميز الألوان (Standard Color Coding)** في دوائر التيار المستمر (DC) أحد الركائز الأساسية لضمان سلامة التركيبات الكهربائية وتسهيل عمليات الصيانة اللاحقة في المنظومات الكهروضوئية. تهدف هذه المعايير إلى التمييز البصري الفوري بين الأقطاب ذات الجهود المختلفة، مما يقلل من مخاطر التوصيل الخاطئ (Reverse Polarity) الذي قد يؤدي لتلف الأجهزة الإلكترونية الدقيقة في العاكس أو نشوب حرائق نتيجة القصر الكهربائي.

ويمكن تفصيل المنهجية الهندسية لترميز ألوان الجانب المستمر وفق الآتي:

### **أولاً: ترميز الأقطاب في الأنظمة الثنائية (Two-Wire Systems)**

تعتمد معظم المنظومات الشمسية على دوائر تتكون من قطبين (موجب وسالب)، ويتم تمييزهما عالمياً وفق الأنماط الأكثر شيوعاً في الأكواد الهندسية:

- **القطب الموجب (Positive - L+):** يُخصص له اللون **الأحمر (Red)** كمعيار عالمي، وفي بعض الأكواد الأوروبية (مثل المعيار البريطاني القديم) قد يُستخدم اللون البني (Brown) كبديل معتمد.
- **القطب السالب (Negative - L-):** يُرمز له غالباً باللون **الأسود (Black)**، وفي بعض تطبيقات الأنظمة التي تتبع كود الألوان الحديث يُستخدم اللون الأزرق (Blue).

### **ثانياً: ترميز الأنظمة ذات الثلاثة أسلاك (Three-Wire Systems)**

في المشاريع التي تتطلب وجود "نقطة تعادل" أو "خط منتصف" (Neutral/Midpoint) في جانب التيار المستمر لتوازن الجهود، يتم اتباع التوزيع اللوني التالي لضمان دقة الربط الميداني:

1. **القطب الموجب (+L):** اللون **الأحمر**.
2. **القطب السالب (-L):** اللون **الأسود**.
3. **خط التعادل أو المنتصف (N):** يُخصص له اللون **الأبيض** لتمييزه عن الأقطاب الفعالة وتسهيل عمليات القياس والاختبار.

### **ثالثاً: معايير تأريض الحماية (Protective Grounding)**

تتفق الأكواد الهندسية الدولية (مثل NEC و IEC) على ضرورة توحيد لون موصل التأريض لتمييزه بشكل قاطع عن موصلات القدرة الحاملة للتيار، حيث يُستخدم اللون **الأخضر أو الأخضر الممزوج بالأصفر (Green/Yellow)** حصراً لخط الأرضي (Ground/Earth). وتكمن الأهمية الفيزيائية لهذا التمييز في منع حدوث أي التباس بين أسلاك الحماية وأسلاك نقل الطاقة، مما يؤمن حماية قصوى للفنيين أثناء التعامل مع الهياكل المعدنية للمصفوفة.

### **رابعاً: القواعد الهندسية للتعريف والربط**

تفرض الممارسة الأكاديمية ضوابط صارمة لضمان استمرارية التعريف اللوني طوال مسار الدائرة:

- **ثبات الترميز:** يجب الحفاظ على نفس كود الألوان المختار من مخارج الألواح وحتى "صندوق التجميع" (Combiner Box) وصولاً إلى مداخل العاكس.
- **استخدام الأكمام التعريفية:** في حال استخدام كابلات ذات لون موحد (مثل الكابلات الشمسية السوداء المزدوجة العزل)، تفرض المعايير وضع **أشرطة تمييز (Identification Tapes)** أو أكمام حرارية (Heat Shrink) عند نهايات الكابلات تحمل اللون المعبر عن القطبية (أحمر للموجب وأسود للسالب) لضمان عدم الخطأ عند الربط.
- **التمييز البصري:** يُراعى هندسياً تحقيق مسافة فاصلة مناسبة بين كابلات القطب الموجب والسالب داخل القنوات أو المواسير لتقليل احتمالية حدوث قوس كهربائي بينهما.

## التكوين الهندسي لصندوق تجميع التيار المستمر (PV Combiner Box)

يُمثل **صندوق تجميع التيار المستمر (PV Combiner Box)**، والذي يُعرف أحياناً بصندوق التوصيل (Array Junction Box)، المحطة المركزية التي تجمع المسارات الكهربائية القادمة من سلاسل الألواح الشمسية المتعددة قبل انتقالها إلى العاكس. تبرز أهمية هذا الصندوق في المشاريع الكبرى لدوره في تنظيم التمديدات، وتقليل كمية الكابلات الطويلة، وتوفير نقاط حماية وفصل قريبة من المصفوفة.

ويمكن تفصيل التكوين الهندسي والوظائف التشغيلية للصندوق وفق المنهجية الأكاديمية التالية:

### **أولاً: الوظيفة الهندسية الأساسية (Strings Aggregation)**

تتمثل المهمة الرئيسية للصندوق في ربط السلاسل الموصلة على التوازي؛ حيث يتم إدخال كابلات القطب الموجب والسالب لكل سلسلة بشكل مستقل، ويتم تجميعها داخلياً عبر "بارات" أو روابط نحاسية (Busbars/Links). ينتج عن هذه العملية مخرج واحد يتكون من كابل رئيسي ذي مقطع عرضي كبير (DC Main Cable) يحمل التيار الكلي للمنظومة باتجاه العاكس.

### **ثانياً: المكونات الحيوية داخل صندوق التجميع**

يحتوي الصندوق على عناصر تقنية تضمن سلامة المنظومة من الأعطال الكهربائية والظروف الجوية:

1. **مصهرات السلاسل (String Fuses):** تُركب لحماية كل سلسلة من التيارات العكسية وزيادة الحمل، وتوضع عادة في حوامل (Holders) مخصصة للتيار المستمر لسهولة الاستبدال.
2. **قاطع الدورة الرئيسي (Main DC Breaker):** يعمل كجهاز فصل وحماية كلي للقدرة المجمعة، ويتم اختياره بناءً على أقرب سعة قياسية للتيار الكلي (مثلاً قاطع 40 أمبير لتيار إجمالي قدره 36 أمبير).
3. **مانعات الصواعق والجهود العابرة (SPD):** تُعد ضرورة هندسية لحماية العاكس والألواح من الارتفاع المفاجئ في الجهد الناتج عن الصواعق البرقية أو عمليات الفصل والوصل الكبرى، وتُربط مباشرة بقضيب التأريض.
4. **أطراف التوصيل والترقيم (Terminals & Labeling):** تُستخدم أطراف مجهزة مسبقاً (Terminal Blocks) لضمان الربط الميكانيكي الجيد وتجنب نشوء قوس كهربائي، مع ضرورة تمييز الأقطاب بالألوان والملصقات التعريفية لتسهيل الصيانة.

### **ثالثاً: المواصفات الفنية الميدانية (Standard Specifications)**

لضمان صمود الصندوق أمام العوامل الجوية، تفرض المعايير الهندسية (مثل IEC) مواصفات صارمة:

- **درجة الحماية البيئية:** يجب ألا تقل عن **IP55** أو **IP65** لضمان مقاومة الغبار وتسرب مياه الأمطار.
- **درجة العزل:** يُفضل أن يكون من الدرجة الثانية (**Class II**) لزيادة الأمان الكهربائي للمشغلين.
- **التصميم الفيزيائي:** يجب أن يكون حجم الصندوق كافياً لاستيعاب انحناءات الكابلات دون ضغطها أو تعريضها للتلف الحراري.

### **رابعاً: تحذيرات السلامة والربط (Operational Safety)**

تعتبر دقة القطبية (Polarity) هي العامل الأكثر حرجاً عند العمل داخل الصندوق؛ حيث أن **عكس قطبية سلسلة واحدة** داخل صندوق التجميع قد يؤدي إلى نشوب حريق فوري نتيجة تدفق التيارات العكسية من باقي السلاسل نحو السلسلة المخطئة. لذا، تلتزم الممارسة الأكاديمية بإجراء اختبارات "الاستمرارية والجهد" قبل إغلاق القواطع الرئيسية للصندوق.

## تراتب الحماية التشغيلي: الربط بين الفيوز والقاطع الرئيسي

يستند **تراتب الحماية التشغيلي (Operational Protection Hierarchy)** في الجانب المستمر (DC) للمنظومات الشمسية إلى فلسفة "الدفاع المتعدد الطبقات"؛ حيث يتم توزيع أدوار الحماية والتحكم بين مصهرات السلاسل (String Fuses) وقواطع الدورة أو مفاتيح الفصل الرئيسية (Main DC Breakers/Isolators) لضمان سلامة الألواح والعاكس على حد سواء. ويهدف هذا التنسيق الهندسي إلى عزل الأعطال الصغرى في مكانها ومنع تطورها إلى كوارث تشغيلية.

ويمكن تفصيل هذه الفلسفة التنسيقية وفق المحاور الأكاديمية التالية:

### **أولاً: حماية مستوى السلسلة (String Level - الدفاع الأول)**

تضطلع المصهرات (Fuses) المركبة لكل سلسلة بمهمة حماية الموديولات من **التيارات العكسية (Reverse Currents)**.

- **الوظيفة الفيزيائية:** في حال حدوث قصر (Short Circuit) في إحدى السلاسل، تتدفق التيارات من السلاسل المتوازية الأخرى نحو السلسلة المعطوبة. إذا تجاوز هذا التيار القيمة المحددة في الداتا شيت ($Max\ Series\ Fuse\ Rating$)، ينصهر الفيوز فوراً لعزل السلسلة وحماية الألواح من الاحتراق.
- **التكوين:** يتم تركيب المصهر عادةً في القطبين الموجب والسالب لضمان العزل التام عند حدوث أعطال أرضية.

### **ثانياً: حماية مستوى المصفوفة (Array Level - الدفاع الرئيسي)**

يتم تركيب **قاطع دورة مستمر (DC Circuit Breaker)** أو مفتاح فصل رئيسي (Main DC Isolator) عند المخرج الكلي للسلاسل المجتمعة قبل دخولها للعاكس.

- **وظيفة الفصل الميكانيكي:** يُعد هذا القاطع الأداة الأساسية للفنيين لإجراء أعمال الصيانة؛ حيث يتيح فصل تيار المصفوفة الكلي يدوياً تحت الحمل (Load-breaking) لضمان بيئة عمل آمنة.
- **حماية العاكس:** يعمل القاطع كحارس لمداخل العاكس (Inverter Inputs)؛ فإذا حدث خلل داخلي في العاكس أدى لسحب تيار زائد من الحقل الشمسي، يقوم القاطع الرئيسي بفتح الدائرة قبل تضرر الدوائر الإلكترونية للعاكس.

### **ثالثاً: فلسفة التنسيق الرياضي (Coordination Logic)**

لتحقيق تراتب تشغيلي صحيح، يجب أن تخضع السعات المختارة لعلاقة منطقية تمنع الفصل العشوائي للمنظومة بالكامل عند حدوث عطل في سلسلة واحدة:

1. **سعة فيوز السلسلة ($I_{fuse}$):** تُحسب بناءً على تيار القصر للوح المنفرد ($I_{sc} \times 1.56$).
2. **سعة القاطع الرئيسي ($I_{main_breaker}$):** تُحسب بناءً على مجموع تيارات السلاسل المتوازية مع تطبيق معامل الأمان (1.25).

- **القاعدة:** يجب أن تكون سعة القاطع الرئيسي دائماً أعلى من سعة فيوز السلسلة الواحدة لتجنب فصل المنظومة بالكامل عند احتراق مصهر واحد.

### **رابعاً: معايير الاستخدام (متى نستخدم أياً منهما؟)**

تختلف الحاجة الهندسية بناءً على حجم المنظومة:

- **في الأنظمة الصغيرة (سلسلة واحدة أو اثنتين):** قد لا تشترط الأكواد وجود فيوزات للسلاسل لأن التيار العكسي لن يتجاوز قدرة تحمل الألواح، ويُكتفى بمفتاح فصل (DC Isolator) بجوار العاكس.
- **في الأنظمة الكبيرة (3 سلاسل فأكثر):** يصبح وجود مصهرات لكل سلسلة (String Fusing) **إلزامياً** لمنع تدمير الألواح، بالإضافة للقاطع الرئيسي في صندوق التجميع (Combiner Box) للتنسيق الكلي.
