MAQattan/My-Graduation-Project/GP_Obsidian/Thesis/10/Deleted/حساب الاستطاعة الإجمالية للمنظومة.md

بناءً على التوزيع الميكانيكي النهائي للمصفوفات الكهروضوئية، وبعد الأخذ بالاعتبار جميع المحددات الإنشائية، والمسافات البينية لتفادي التظليل الأفقي، بالإضافة إلى استغلال المساحات المحيطة بالعوائق شاقولياً (بعد إثبات أمانها رياضياً)، تم التوصل إلى القدرة الاستيعابية القصوى لسطح المبنى المصرفي المتاح والدراسة.

تم تركيب **39 لوحاً شمسياً** باستطاعة ذروية تبلغ $600 \text{ W}$ للوح الواحد، وتُحسب الاستطاعة الإجمالية للمنظومة ($P_{\text{total}}$) وفق العلاقة التالية:

$$P_{\text{total}} = N \times P_{\text{panel}}$$

$$P_{\text{total}} = 39 \times 600 \text{ W} = 23,400 \text{ W} = 23.4 \text{ kWp}$$

حيث أن:

- $N$: العدد الإجمالي للألواح المركبة ($39 \text{ L}$).
    
- $P_{\text{panel}}$: استطاعة اللوح الواحد تحت الشروط المعيارية ($600 \text{ W}$).

وحيث تبلغ المساحة الإجمالية المستغلة في الدراسة على سطح المبنى قرابة $162 \text{ m}^2$ (كما هو موضح في المخطط الشكلي أدناه)، فإنه يمكن تقييم مؤشر **كثافة الاستطاعة المساحية (Power Density)** للمشروع، والذي يعبر عن كفاءة استغلال المساحات الحضرية:

$$\text{Power Density} = \frac{P_{\text{total}}}{\text{Area}} = \frac{23,400 \text{ W}}{195.6709 \text{ m}^2} \approx 119.58 \text{ W/m}^2$$
![[PV-10-21.png]]

يُمثل تحقيق كثافة استطاعة تبلغ $144.44 \text{ W/m}^2$ في بيئة حضرية مقيدة بالعوائق مؤشراً تصميمياً مرتفعاً. يعود الفضل في هذا الارتفاع إلى تبني منهجية "التحليل الفراغي ثلاثي الأبعاد للظلال الجانبية اللحظية"، والتي سمحت بإنقاذ وإدراج 5 ألواح إضافية (باستطاعة $3 \text{ kWp}$) كان التوجه التصميمي التقليدي المحافظ يستبعدها كلياً خوفاً من الظلال الموضعية، مما أدى لتعظيم إنتاجية المحطة السنوية والوصول بالسطح إلى كفاءة الاستغلال القصوى.
