MAQattan/My-Graduation-Project/GP_Obsidian/Thesis/9/Draft/بنية التمديد والحماية في الجانب المتردد (AC Side).md

### 1.1 التصنيف الهندسي لقواطع الحماية الكهربائية (Circuit Breakers Classification)

تُصنف قواطع الحماية على جانب التيار المتردد (AC) للمنظومات الكهروضوئية بناءً على بنيتها الهيكلية، ونطاقات تحملها، وآلية إخماد القوس الكهربائي. وتتوزع هذه القواطع هرمياً لحماية الشبكة من تيار الحمل الزائد (Overload) وتيار القصر (Short Circuit) عبر ثلاث عائلات رئيسية تضمن انتقائية الفصل وأمان المنشأة.

### القواطع المصغرة (Miniature Circuit Breakers - MCB)

تُستخدم القواطع المصغرة في دوائر القدرة المنخفضة والمخرجات الفرعية للعاكسات الصغيرة، حيث لا يتجاوز تيارها الاسمي ($I_n$) قيمة 125 أمبير، وتتراوح سعة قطع القصر لها ($I_{cu}$) بين 4.5 و 25 كيلو أمبير وفقاً للمواصفة IEC 60898. وتعتمد هذه القواطع على وحدات فصل مغناطيسية حرارية ثابتة مسبقة الضبط وفق منحنيات فصل معيارية (B, C, D) تتناسب مع طبيعة الأحمال وتيارات البدء العابرة للأنظمة الملحقة.

### القواطع المصبوبة (Molded Case Circuit Breakers - MCCB)

في مستويات القدرة المتوسطة والعالية، تُعتمد القواطع المصبوبة المصنوعة من غلاف راتنجي مقوى حرارياً لتحمل الإجهادات الميكانيكية والحرارية؛ حيث يمتد نطاق عملها الاسمي ($I_n$) من 16 إلى 1600 أمبير بسعات قطع قصر تتجاوز 100 كيلو أمبير. وتتميز بمرونة ضبط وحدات الفصل ميدانياً—سواء كانت حرارية مغناطيسية أو إلكترونية رقمية—مما يتيح تحقيق التنسيق الحمائي الدقيق داخل لوحات التوزيع الرئيسية (ACDB) لعاكسات السلاسل الكبيرة.

### القواطع الهوائية (Air Circuit Breakers - ACB)

تُخصص القواطع الهوائية للمحطات الكهروضوئية الضخمة عند نقاط الربط المشترك (PCC) وجانب الجهد المنخفض لمحولات الرفع، وتغطي تيارات اسمية من 630 إلى 6300 أمبير وسعات قطع تصل إلى 150 كيلو أمبير. تعتمد هذه القواطع على الهواء الجوي عند الضغط الطبيعي لإخماد القوس الكهربائي، وتُدار بواسطة وحدات حماية رقمية بالكامل توفر تحكماً دقيقاً في زمن وفصل الأعطال، بما فيها الأعطال الأرضية (Ground Faults).

> **ملاحظة هندسية:** يخضع اختيار هذه القواطع تحليلياً لطاقة المرور العابرة ($I^2t$) لضمان الانتقائية الكاملة ومنع ظاهرة لحام الملامسات الداخلية (Contact Welding) عند حدوث أعطال القصر الشديدة على الشبكة.

## التكوين الهندسي للأقطاب (Poles) وتطبيقات الربط

يُحدد عدد أقطاب قاطع الحماية عدد المسارات الناقلة التي يمكن قطعها وفصلها تزامناً في الدائرة الكهربائية، ويرتبط اختيار التكوين الهندسي للأقطاب مباشرة بنوع شبكة الربط (أحادية أو ثلاثية الأطوار) ونظام التأريض المعتمد في المنشأة الكهروضوئية. في الأنظمة أحادية الطور المغذية للأحمال الفرعية، يتأرجح الاختيار بين القواطع أحادية القطب (1P) التي تعزل خط الطور فقط، والقواطع ثنائية القطب (2P) التي تعزل خطي الطور والمحايد (Neutral) معاً. وتفرض مواصفات الربط بالشبكة غالباً استخدام القواطع الثنائية لعزل خط المحايد بشكل كامل، مما يضمن حماية المنظومة من التيارات المرتدة ويحقق العزل الجلفاني الآمن للعاكس أثناء عمليات الصيانة أو عند تفعيل خاصية الفصل التلقائي عند انقطاع الشبكة.

أما في الأنظمة ثلاثية الأطوار المخصصة للمحطات التجارية والصناعية، فيتوزع التصميم الهندسي بين استخدام القواطع ثلاثية الأقطاب (3P) والقواطع رباعية الأقطاب (4P). يقتصر دور القاطع ثلاثي الأقطاب على فصل الأطوار الثلاثة الرئيسية مع إبقاء خط المحايد متصلاً بشكل دائم، وهو تكوين قياسي يُعتمد عندما تكون الأحمال متزنة تماماً. بالمقابل، يُصبح استخدام القواطع رباعية الأقطاب (4P) لزاماً عند الربط مع شبكات التأريض التي تشترط فصلاً كاملاً للمحايد (مثل أنظمة TT و TN-S)؛ حيث يضمن القاطع رباعي الأقطاب قطع خط المحايد تزامناً مع الأطوار الثلاثة.

تكتسب هذه التهيئة رباعية الأقطاب أهمية بالغة عند التعامل مع شبكات تغذي أحمالاً غير خطية، حيث تتسبب هذه الأحمال في توليد توافقيات من الرتبة الثالثة ومضاعفاتها تتراكم بشكل فيزيائي في خط المحايد وتؤدي إلى رفع درجة حرارته واختلال جهد النقطة النجمية. بناءً عليه، فإن فصل المحايد عبر القاطع رباعي الأقطاب يمنع تدفق التيارات التوافقية الشاردة والتيارات الأرضية الراجعة إلى جهة العاكس الشمسي، مما يحمي وحدات القياس والحساسات الإلكترونية داخل العاكس ويضمن استقرار منظومة الحماية الكهربائية وتوافقها مع معايير جودة الطاقة.

## فيزيائية الأعطال وآليات الحماية في القواطع المغناطيسية الحرارية

تدمج القواطع المغناطيسية الحرارية بين آليتين فيزيائيتين مستقلتين لتوفير حماية متكاملة لجانب التيار المتردد في المنظومات الكهروضوئية. يضمن هذا الدمج سرعة الاستجابة المغناطيسية اللحظية للأعطال العنيفة، بالتوازي مع التأخير الزمني التراكمي للإجهاد الحراري للأعطال الممتدة.

#### أولاً: حالة القصر (Short Circuit) وآلية الفصل المغناطيسي الفوري

عند حدوث عطل قصر صريح في الشبكة، يرتفع التيار بشكل فجائي وعنيف متجاوزاً أضعاف القيمة الاسمية المصممة للقاطع، ويُعبر عن هذه العلاقة تقريبياً بالمعادلة التالية:

$$I_{sc} \approx (10 \dots 100) \times I_{rated}$$

يتدفق هذا التيار الفائق عبر ملف مغناطيسي داخلي (Solenoid)، مما يولّد مجالاً مغناطيسياً شديداً يتناسب طردياً مع مربع التيار العابر. يقوم هذا المجال بجذب عاكسة ميكانيكية (Armature) بشكل فوري ولحظي في زمن يقل عن بضع أجزاء من الثانية، مما يؤدي إلى فتح ملامسات القاطع وعزل العطل قبل سريان الإجهادات الديناميكية المدمرة في الكابلات.

#### ثانياً: تكنولوجيا إخماد الشرارة الكهربائية (Arc Chutes)

لحظة تباعد الملامسات الميكانيكية تحت تأثير تيار القصر، يتأين الهواء في الفجوة الفاصلة نتيجة شدة المجال الكهربائي، مما ينتج عنه قوس كهربائي (Electric Arc) ذو حرارة هائلة قادرة على صهر الملامسات. وللتعامل مع هذه الظاهرة، يُوجَّه القوس فيزيائياً نحو غرف إخماد الشرارة (Arc Chutes)، والتي تحتوي على صفائح معدنية متوازية ومعزولة تُعرف بمجزئات القوس (Arc Splitters). تعمل هذه الصفائح على سحب القوس وتجزئته إلى أقواس صغيرة متتالية، مما يرفع من مقاومته الفيزيائية ويخفض جهده، ليتم تبريده وإخماده بسرعة فائقة.

> **[موضع صورة توضيحية 1: مخطط متحرك أو رسم تفصيلي لغرفة إخماد الشرارة وآلية تجزئة القوس عبر الـ Arc Splitters]**

#### ثالثاً: حالة الحمل الزائد (Overload) وآلية الشريحة ثنائية المعدن

يتسم الحمل الزائد بارتفاع طفيف ومستمر في قيمة التيار فوق العتبة الاسمية، مما يتسبب في تولد حرارة تراكمية داخل الناقل وفقاً للفقد الحراري الفيزيائي ($I^2Rt$). تعتمد آلية الفصل هنا على شريحة ثنائية المعدن (Bimetallic Strip) تتكون من معدنين متلاحمين ذوي معاملين مختلفين للتمدد الحراري. مع استمرار تدفق التيار الزائد، تسخن الشريحة بمعدل غير متساوٍ، مما يجبرها على الانحناء التدريجي باتجاه ميكانيكية الفصل حتى تضغط على زنبرك الإعتاق ويفتح القاطع دائرته.

#### رابعاً: فلسفة التأثير العكسي والتأخير الزمني العمدي

تخضع آلية الفصل الحراري لخاصية الزمن العكسي (Inverse-Time Characteristic)، حيث يتناسب زمن استجابة القاطع عكسياً مع مربع قيمة التيار (كلما زادت شدة الحمل الزائد، قلّ زمن انحناء الشريحة). ويُعد هذا التأخير الزمني متعمداً ومحورياً في الهندسة الكهربائية؛ إذ يمنح القاطع القدرة على التمييز بين تيارات بدء التشغيل العابرة (Starting Currents)—مثل تيارات مغنطة المحولات الكبيرة أو شحن مكثفات الترشيح داخل العاكس الشمسي—وبين الأعطال المستمرة، مما يمنع ظاهرة الفصل الزائف ويؤمن عزل الأحمال المزمنة بأمان.

> **[موضع صورة توضيحية 2: صورة متحركة (GIF) أو رسم بياني يوضح انحناء الشريحة ثنائية المعدن عند مرور تيار الحمل الزائد]**

## منحنيات الخصائص وسعات التيار المعيارية (Characteristics Curves and Standard Ratings)

يُمثل منحنى الخصائص الزمني-التياري (Time-Current Curve) الأداة الهندسية الأساسية لتقييم أداء قاطع الحماية وتحديد مواءمته الفنية للمنظومة الكهروضوئية. يُرسم هذا المنحنى على مخطط بياني ذي مقياس لوغاريتمي مزدوج، حيث يُمثل المحور الرأسي زمن الفصل بالثواني، بينما يُمثل المحور الأفقي مضاعفات التيار الاسمي للقاطع ($I/I_n$).

ينقسم المنحنى بنيوياً إلى منطقتين رئيسيتين يفصلهما نطاق سماحية التصنيع (Tolerance Band): المنطقة الحرارية العلوية ذات الميل العكسي التي توضح تأخر زمن الفصل مع انخفاض نسبة الحمل الزائد، والمنطقة المغناطيسية السفلية المتمثلة بهبوط رأسي حاد يُشير إلى الفصل اللحظي الفوري بمجرد تخطي تيار الأعطال للعتبة المغناطيسية الحرجة، وينتهي المنحنى لأسفل عند نقطة أقصى تيار قصر يمكن للقاطع عزله بأمان دون أن يتلف فيزيائياً، وهي سعة القطع الاسمية ($I_{cu}$).

> **[موضع صورة توضيحية 3: الرسم البياني القياسي لمنحنى الخصائص الزمني-التياري لقواطع الـ MCB موضحاً عليه مناطق الفصل الحراري والمغناطيسي وسعة القطع]**

تخضع السلسلة المعيارية للتيارات الاسمية ($I_n$) لقواطع الحماية في السوق التشغيلي لمواصفات اللجنة الكهروتقنية الدولية، وتحديداً المعيارين IEC 60898-1 و IEC 60947-2، لضمان التوافقية الكاملة والتنسيق الحمائي في التصاميم الهندسية. تتدرج هذه السلسلة القياسية في قواطع الـ MCB لتشمل القيم النمطية التالية: 1، 2، 3، 4، 6، 10، 13، 16، 20، 25، 32، 40، 50، 63، 80، 100، و 125 أمبير. وتستمر هذه المعايرة التصاعدية لتغطية التطبيقات الصناعية الأكبر بقواطع الـ MCCB والـ ACB عبر قيم معيارية تشمل 160، 250، 400، 630، 800، 1000، 1250، 1600 أمبير، وتصل إلى 6300 أمبير في القواطع الهوائية للمحطات الكبرى. يُتيح هذا التدرج القياسي للمصمم اختيار العتبة الحمائية بدقة تتوافق مع تيار العاكس المستمر وتحقق حماية مؤكدة لمساحة مقطع الكابلات المرتبطة به.
