MAQattan/My-Graduation-Project/GP_Obsidian/Thesis/10/Deleted/Deleted 10-3.md

#### الترتيب السابق للفقرات :

مقدمة

مفهوم الساعات الشمسية الذروية (Peak Sun Hours - PSH)

الإنتاجية النوعية (Specific Production - Specific Yield)

المورد الشمسي والبيانات المناخية للموقع (Solar Resource Data)

المعايير الاقتصادية والتشغيلية

أنماط التصميم والمنهجية المتبعة

اختيار اللوح الشمسي

التوجيه الجغرافي وزاوية الميل المثالية (Orientation and Optimal Tilt Angle)

تحليل الظلال

منهجية تركيب وتوزيع الألواح

دراسة إمكانية استغلال المساحات المظللة جزئياً

حساب الاستطاعة الإجمالية للمنظومة وتقييم الكثافة المساحية

اختيار العاكس

التحليل الحراري الحرج لجهود الألواح الكهروضوئية

تحجيم السلاسل وضوابط نافذة الجهد (String Sizing)

التوزيع الكهربائي الفعال للسلاسل على متعقبات القدرة (MPPT Configuration)

>[!info] مسميات الطرق
>- الطريقة التي كنت تتبعها تسمى: **"التثبيت التقليدي بمسافات بينية" (Standard Fixed Mounting with Inter-row Spacing).**
>- الطريقة التي اقترحتها أنت تسمى: **"الهياكل المتدرجة" (Terraced / Stepped Mounting Structures).**

### الهيكلية القديمة التي حذفت :

### [[حساب الاستطاعة الإجمالية للمنظومة]]

### [[اختيار العاكس (Inverter Selection)]] 

### [[حساب الحالات الحرجة للجهد]]

### [[تحجيم سلسلة الألواح (String Sizing)]]

### [[حساب وتوزيع السلاسل الكهروضوئية (String Sizing and Distribution)]]
