MAQattan/My-Graduation-Project/GP_Obsidian/Thesis/10/Deleted/تحجيم سلسلة الألواح (String Sizing).md

يتم تحديد عدد ألواح السلسلة لمداخل الانفرتر بناءً على النتائج الحرارية؛ حيث تُستخدم هذه القيم الحرارية الدقيقة لتحديد النطاق المسموح به لعدد الألواح في السلسلة الواحدة (String Sizing) لضمان بقائها ضمن "نافذة الجهد" للعاكس طوال العام:

حساب أقل عدد ألواح مسموح في السلسلة الواحدة ($N_{min}$)؛ إذ يُستخدم لضمان "استيقاظ" العاكس وبدء تشغيله في أشد الأيام حراً، حيث ينخفض جهد الألواح: $$N_{min} = \frac{V_{start-up} \text{ (Inverter)}}{V_{oc-min}\text{ (module at } 60^{\circ}\text{C)} \times (1 - \text{Losses})}= \frac{200}{47.45 \times (1 - 0.05)}= 4.43 ≃ 5$$
	ملاحظة هامشية : حيث يتم **جبر الكسر للأعلى** دائماً، ويدخل معامل المفاقيد (نضع 5% فاقد في كابلات الـ DC) لضمان الأمان التشغيلي.

2. حساب أقصى عدد ألواح مسموح في السلسلة الواحدة ($N_{max}$)؛ إذ يُستخدم لضمان عدم احتراق العاكس في أبرد صباحات الشتاء، حيث يرتفع جهد الألواح بشكل حاد: $$N_{max} = \frac{V_{max-DC} (\text{Inverter})}{V_{oc-max} (\text{at } 0^{\circ}\text{C})} = \frac{1100}{56.64} = 19.42 ≃ 19$$ 
	ملاحظة هامشية : حيث يتم **تقريب الناتج للأدنى** تماماً (Round Down)؛ لأن تجاوز هذا العدد ولو بكسر بسيط يعني تجاوز حدود جهد العاكس وتدمير دوائره.
	ملاحظة هامشية : لم ندخال المفاقيل في هذه المعادلة لأننا نريد ضمان سلامة العاكس عند أعلى مستوى للجهد.

لضمان بقاء المنظومة ضمن **مجال تتبع نقطة القدرة القصوى (MPPT Range)** الخاص بالعاكس طوال العام، يجب موازنة عدد الألواح بحيث لا يخرج جهد السلسلة التشغيلي ($V_{mp}$) عن الحدود الدنيا والقصوى للعاكس تحت أقصى الظروف الحرارية المتوقعة، حيث يتم تحجيم عدد الألواح لمجال الـ MPPT بالاعتماد على المعادلات التالية:

حساب أقل عدد مسموح به من الألواح في السلسلة الواحدة لمجال الـ MPPT ($N_{min-MPPT}$)؛ إذ تُستخدم هذه المعادلة لضمان أن جهد المصفوفة صيفاً لن ينخفض عن الحد الأدنى الذي يبدأ عنده العاكس بتتبع أقصى قدرة: 
$$N_{min-mppt} = \frac{V_{mpp-min} (\text{Inverter})}{V_{mpp-min} (\text{Module at } 60^{\circ}\text{C}) \times (1 - \text{Losses})} = \frac{200}{47.45 \times (1 - 0.05)} = 4.43 ≃ 5 $$
 حساب أقصى عدد مسموح به من الألواح في السلسلة الواحدة لمجال الـ MPPT ($N_{max-mppt}$)؛ إذ تُستخدم لضمان أن جهد المصفوفة شتاءً لن يتجاوز الحد الأعلى لمجال التتبع، مما يسمح للعاكس بالعمل بأعلى كفاءة دون قيود. **المعادلة:**
 $$N_{max-mppt} = \frac{V_{mpp-max} (\text{Inverter})}{V_{mpp-max} (\text{Module at } 0^{\circ}\text{C})} = \frac{1000}{56.64}=17.65 ≃ 17$$

- ملاحظة هامشية: إذ الحد الأعلى لمجال الـ MPPT في ورقة البيانات **$V_{mpp-max} (\text{Inverter})$**  هي 1000 فولت.
- ملاحظة هامشية: هنا نستخدم جهد أقصى قدرة شتاءً ($V_{mpp-max}$) وليس جهد الدارة المفتوحة ($V_{oc}$)، لأننا نحسب حدود "التشغيل" وليس حدود "الأمان المطلق".

بينما يمنحك هذان الرقمان "النطاق التشغيلي"، تشير المصادر أن لتحقيق أعلى كفاءة تحويل للطاقة يجب التمركز حول الجهد المقنن (Rated Voltage) للعاكس؛ وبهذه الطريقة يتم حساب العدد المثالي للألواح ($N_{ideal}$) وذلك بقسمة الجهد المقنن للعاكس على جهد أقصى قدرة للوح ($V_{mpp}$) عند ظروف الاختبار القياسية (دون إدخال تأثير الحرارة المباشر؛ لأنه يمثل نقطة الاستقرار في منتصف النطاق):
$$N_{ideal} = \frac{V_{rated} (\text{Inverter})}{V_{mp} (\text{at STC})}= \frac{600}{44.66}=13.43≃13$$
	ملاحظة هامشية : ويتم تقريب هذا الرقم للأعلى ليكون هو "العدد المعتمد" في السلسلة، مع التأكد من وقوعه بين $N_{min}$ و $N_{max}$.
    
وباعتماد هذا العدد للسلسلة الواحدة نضمن استمرارية الاستثمار دون أعطال تقنية، حيث ستعمل المنظومة بكفاءة في الصيف (عند انخفاض الجهد)؛ لأن الجهد الإجمالي للسلسلة سيكون أعلى من جهد بدء التشغيل، و ستكون محمية تماماً في الشتاء (عند ارتفاع الجهد)؛ لأن الجهد الإجمالي للسلسلة سيكون أقل بكثير من أقصى جهد يتحمله العالكس.
