MAQattan/My-Graduation-Project/GP_Obsidian/Thesis/10/Deleted/حساب وتوزيع السلاسل الكهروضوئية (String Sizing and Distribution).md

#ToRefactor 

تُمثل عملية **حساب وتوزيع السلاسل الكهروضوئية (String Sizing and Distribution)** المرحلة الحاسمة في الموازنة بين القدرة التصميمية للمنظومة وبين القيود التشغيلية لمداخل العاكس (Inverter Inputs)، حيث يهدف التوصيل التوازي للسلاسل إلى تجميع التيارات الكهربائية للوصول إلى القدرة الكلية المستهدفة مع الحفاظ على الجهد ضمن النطاق التشغيلي المسموح به. وتستند هذه المرحلة إلى مواءمة الخصائص التشغيلية للمصفوفة مع مواصفات متعقبات نقطة القدرة القصوى (MPPT Trackers) المتوفرة في العاكس.

ويمكن تلخيص المنهجية الأكاديمية لحساب وتوزيع السلاسل وفق القواعد الهندسية التالية:

### **أولاً: حساب عدد السلاسل الكلي ($N_{strings}$)**

بعد تحديد العدد الإجمالي للألواح ($N_{total}$) والعدد الأمثل للألواح في السلسلة الواحدة الموصلة توالياً ($N_{series}$)، يتم حساب عدد السلاسل المطلوبة لملء مصفوفة المنظومة بالعلاقة التالية [58، 67]: $$N_{strings} = \frac{N_{total-modules}}{N_{series-per-string}}$$ ويُشترط هندسياً **جبر الكسر للأعلى** للحصول على رقم صحيح، مع مراعاة أن أي زيادة في عدد الألواح لضبط هذا الرقم ستؤدي بالضرورة إلى زيادة طفيفة في القدرة الكلية للمنظومة ($P_{final}$)، وهو ما يُعد إجراءً تأمينياً لتعويض المفاقيد المستقبلية [58، 59].

### **ثانياً: التحقق من قيود التيار الكهربائي (Current Constraints)**

يعد التوصيل التوازي مؤثراً مباشراً على شدة التيار، حيث يظل الجهد ثابتاً (مساوياً لجهد السلسلة الواحدة) بينما تُجمع التيارات [79، 129]. لذا، يجب التأكد من أن عدد السلاسل الموصلة على كل مدخل MPPT لا ينتج عنه تيار يتجاوز **أقصى تيار دخل للعاكس ($I_{max_input}$)**؛ وتُستخدم القيمة القصوى لتيار اللوح (تيار القصر $I_{sc}$) كمعيار للأمان المطلق [60، 68، 189]. **العلاقة الشرطية للأمان:** $$N_{strings-per-MPPT} \times I_{sc-module} \leq I_{max-input-inverter}$$ ويؤكد التحليل الهندسي هنا على ضرورة الرجوع لورقة بيانات العاكس لتحديد "أقصى تيار دخل لكل مدخل" و"أقصى تيار قصر يتحمله العاكس"، لضمان عدم احتراق الدوائر الإلكترونية عند حدوث ذروة في الإشعاع الشمسي [45، 60، 68].

### **ثالثاً: آلية التوزيع على مداخل الـ MPPT**

تتميز العواكس الحديثة في الأنظمة المرتبطة بالشبكة بكونها **متعددة المداخل (Multi-MPPT)**، مما يتيح توزيع السلاسل بشكل متوازن يقلل من تأثير الظلال أو تباين زوايا التوجيه [142، 144]. وتتم عملية التوزيع بقسمة إجمالي السلاسل على عدد المداخل المتوفرة [61، 62]: $$N_{strings-per-MPPT} = \frac{N_{strings-total}}{N_{MPPT-trackers}}$$ والقاعدة الهندسية المفضلة هي **التوزيع المتساوي** للسلاسل على المداخل لضمان تحميل متعقبات الـ MPPT بشكل متوازن، مما يرفع من كفاءة تحويل الطاقة الكلية ويقلل الإجهاد الحراري على المكونات الداخلية للعاكس [62، 68، 142].
