MAQattan/My-Graduation-Project/GP_Obsidian/Thesis/10/Deleted/Deleted 10-1.md

وتعتمد الممارسة المثلى في استخراج هذه البيانات على أدوات رقمية متقدمة، يأتي في مقدمتها برنامج **PVsyst**؛ حيث يقوم البرنامج بعد إتمام التصميم الفني للمنظومة بإصدار تقرير مفصل (Report) يتضمن قيمة **Specific Production**. فعلى سبيل المثال، يُظهر التقرير لمنظومة في مدينة حلب مائلة بزاوية 31 درجة أن الإنتاجية النوعية تبلغ **$1730 \text{ kWh/kWp}$** سنوياً، وهي القيمة التي تعكس جودة الإشعاع في ذلك الموقع وفقاً لزاوية الميل المختارة. وبقسمة هذا الرقم على عدد أيام السنة (365)، يمكن للمهندس استنتاج متوسط ساعات الذروة الشمسية اليومية (PSH) للموقع بدقة عالية، والتي تظهر في هذا المثال بقرابة 4.74 ساعة.

بالتوازي مع ذلك، يبرز موقع **Global Solar Atlas** كأداة جغرافية عالمية لا غنى عنها لاستخراج بيانات الإشعاع الأولية؛ حيث يتيح الموقع للمصمم تحديد إحداثيات الموقع الجغرافي والحصول على بيانات فورية للإنتاجية المتوقعة بناءً على زوايا ميل وتوجيه افتراضية أو مخصصة. ويتميز الموقع بقدرته على عرض الإنتاجية اليومية (Daily Output) للمحطة الافتراضية بقوة 1 كيلوواط، وهو ما يمثل مباشرة قيمة PSH للموقع؛ فإذا أظهر الموقع أن إنتاجية 1 كيلوواط هي 5 كيلوواط ساعي يومياً، فإن ذلك يعني أن ساعات الذروة الشمسية هي 5 ساعات. ويعد الربط بين هذه الأدوات الرقمية والإنتاجية النوعية الخطوة التصميمية الحاسمة لحساب **القدرة الكلية للمصفوفة (Total Power)**، حيث يتم تقسيم إجمالي الطاقة المطلوبة سنوياً على الإنتاجية النوعية للموقع للحصول على حجم المحطة الفعلي اللازم لتغطية الأحمال، وفي حال أردنا معرفة إجمالي الطاقة المنتجة سنوياً لمصفوفة ألواح معينة نضرب الإنتاجية النوعية للموقع بحجم المحطة الفعلي.

تُعد خطوة تحديد **القدرة الكلية للمصفوفة (Total Array Power)**، ويُرمز لها بالوحدة (kWp)، الركيزة الأساسية في تصميم المنظومات المرتبطة بالشبكة، حيث تُمثل الجسر الرياضي الذي يربط بين احتياجات المستهلك الطاقية وبين الحجم الفيزيائي للمحطة. وتستند هذه العملية إلى علاقتين رياضيتين جوهريتين تُحولان "الطاقة" المطلوبة (kWh) إلى "قدرة" مثبتة (kWp) بناءً على المورد الشمسي المتاح في الموقع:

1. **العلاقة المبنية على الاستهلاك اليومي:** تُحسب القدرة الكلية بقسمة الطاقة اليومية المستهدفة على عدد ساعات الذروة الشمسية للموقع:

$$
P_{total} = \frac{E_{daily} (kWh)}{PSH (hours)}
$$

ويؤكد التحليل الهندسي هنا على ضرورة القسمة على **ساعات الذروة (PSH)** وليس على عدد ساعات النهار الفلكية (12 ساعة)؛ لأن ساعات الذروة هي الوحيدة التي تعبر عن كدسة الإشعاع القياسي (1000 وات/م²) التي تُنتج عندها الألواح كامل قدرتها الاسمية.

1. **العلاقة المبنية على الاستهلاك السنوي:** في حال توفر بيانات الاستهلاك لعام كامل، تُحسب القدرة بقسمة إجمالي الطاقة السنوية على **الإنتاجية النوعية (Specific Yield)** المستخرجة من البرمجيات:

$$
P_{total} = \frac{E_{annual} (kWh)}{\text{Specific Yield} (kWh/kWp)}
$$

وتتميز هذه العلاقة بدقتها العالية لأنها تأخذ في الاعتبار تذبذب الإشعاع عبر الفصول الأربعة.

ومن الناحية التطبيقية، لا يكتفي المصمم بالقدرة النظرية الناتجة عن هذه المعادلات، بل يجب ضرب الناتج في **معامل أمان (Safety Factor)**، يُقدر عادةً بـ **1.15**، لتعويض المفاقيد الحتمية الناتجة عن كفاءة العاكس، والمقاومة الكهربائية للكابلات، وتراكم الغبار. وبمجرد اختيار نوع اللوح الشمسي بقدرة محددة ($P_{module}$)، يتم تحديد القدرة النهائية الفعلية للمنظومة عبر ضرب عدد الألواح المختار في قدرة اللوح الواحد:

$$
P_{final} = N_{modules} \times P_{module}
$$

وهذه القيمة النهائية هي التي تُعتمد كأساس لمطابقة قدرة العاكس (Inverter Matching) ولحساب العائد الاستثماري للمشروع.
