MAQattan/My-Graduation-Project/GP_Obsidian/Thesis/10/Deleted/Deleted 10-2.md

### منهجية مكافئة ساعات الذروة الشمسية (PSH Methodology)

يتم تحديد عدد ساعات الذروة الشمسية (Peak Sun Hours) بإجراء عملية مكاملة زمنية (Integration) لتابع الاستطاعة الإشعاعية الساقطة على المتر المربع الواحد، وهو ما يمثل فيزيائياً "المساحة المحصورة تحت منحنى الإشعاع" والتي تعبر عن إجمالي الطاقة الإشعاعية المتراكمة يومياً ($kWh/m^2/day$).
وهنا بإمكاننا تمثيل هذه العملية العلاجية بالعلاقة التالية :
$$PSH = \frac{\int_{t_{rise}}^{t_{set}} G(t) \, dt}{G_{STC}}$$
	حيث أن $G(t)$ هو الإشعاع اللحظي، و $G_{STC} = 1000\text{ W/m}^2$.
