MAQattan/My-Graduation-Project/GP_Obsidian/Thesis/9/الظلال والمسافة بين الألواح/تحليل الظلال.md

### تأثير الظلال على كفاءة الألواح الشمسية

تُعد دراسة تأثير الظلال أحد الركائز الأساسية في تصميم وهندسة أنظمة الطاقة الكهروضوئية (PV Systems)، حيث إن كفاءة النظام تعتمد بشكل مباشر على استمرارية تعرض الخلايا للإشعاع الشمسي المباشر. يهدف هذا القسم إلى تحليل ظاهرة التظليل وتأثيراتها التقنية، مع توضيح الأسس الرياضية المتبعة لتلافيها.

إذ إن الظلال تمثل عائقاً حرجاً يؤدي إلى تدهور أداء الألواح الشمسية؛ وبالتالي حدوث **تظليل جزئي**، ولو على مساحة ضئيلة جداً من اللوح، يتسبب في انخفاض حاد وغير متناسب في القدرة الكهربائية المولدة. يعود ذلك إلى طبيعة توصيل الخلايا داخل اللوح، حيث يؤدي تظليل خلية واحدة إلى زيادة مقاومتها الداخلية، مما يحد من تدفق التيار في كامل السلسلة (String)، وقد يؤدي لحدوث "البقع الساخنة" (Hotspots)، وهو ما يستوجب مراعاة المسافات البينية بدقة عند التصميم لضمان أعلى إنتاجية ممكنة.

### تصنيف أنواع الظلال في المواقع الإنشائية

عند إجراء المحاكاة الهندسية لموقع التثبيت، يجب التمييز بين نوعين رئيسيين من الظلال لضمان استقرار النظام:

1. **التظليل المتبادل بين الصفوف (Row-to-Row Shading):** وهو الظل الذي يلقيه الصف الأمامي من الألواح على الصف الذي يليه، ويحدث هذا النوع غالباً في الأنظمة الأرضية أو فوق الأسطح المستوية نتيجة التقارب غير المدروس بين الهياكل.
2. **التظليل الناتج عن العوائق المحيطة (Environmental Shading):** ويشمل الظلال الناتجة عن العناصر المادية في بيئة المشروع، مثل **المباني المجاورة، الأشجار، أو العوائق الإنشائية** كغرف المحولات أو المداخن، والتي قد تحجب الإشعاع في ساعات الذروة.

### التظليل الأفقي (Horizontal Shading)

يُعرف التظليل الأفقي بأنه الامتداد الهندسي الناتج عن إسقاط ظل الأجسام المعتمة على مستوى العمل الأفقي (Horizontal Plane) نتيجة اعتراض مسار الحزمة الإشعاعية المباشرة. في هندسة الأنظمة الكهروضوئية، يمثل هذا النوع من التظليل "البعد الحرج" الذي يحدد المسافة الدنيا الفاصلة بين مصفوفات الألواح المتتالية، وتُدعى هذه المسافة بالمسافة البينية (Pitch Distance) أو المسافة الأفقية الدنيا، ويرمز لها بالرمز ($D$) وتعتبر من أدق مراحل التصميم الهندسي، حيث تهدف إلى إيجاد التوازن المثالي بين تعظيم القدرة المركبة في المساحة المتاحة ومنع خسائر الطاقة الناتجة عن التظليل المتبادل (Row-to-Row Shading). إذ تمثل الإزاحة الأفقية المطلوبة بين نهاية الصف الأمامي وبداية الصف الذي يليه. يتم التعامل مع هذه المسافة برمجياً وهندسياً كقاعدة لمثلث قائم الزاوية، حيث يمثل ارتفاع الصف ($H$) الضلع القائم، بينما تمثل زاوية ميل الشمس ($\theta$) الزاوية التي تحدد طول ظل هذا الارتفاع على الأرض.

### التظليل الجانبي (Lateral Shading)

يُعرف التظليل الجانبي بأنه الإزاحة العرضية للظلال الناتجة عن انحراف زاوية السمت الشمسية (Azimuth Angle) عن خط الجنوب الجغرافي، ويظهر تأثيره بشكل حرج خلال ساعات الصباح الباكر وقبيل الغروب. في هذه الفترات، تكون الشمس في أدنى ارتفاع لها فوق الأفق، مما يؤدي إلى استطالة الظلال بشكل قطري (Lateral Extension) بعيداً عن المحور الطولي للجسم، مما قد يتسبب في تظليل المساحات المجاورة للعوائق المرتفعة.  

تم حصر دراسة التظليل الجانبي في هذا المشروع على العوائق الإنشائية الثابتة (مثل غرفة الدرج ووحدة التكييف المركزي)، نظراً لارتفاعها النسبي الذي يفرض "حرم ظل" عرضي يجب تجنبه عند توزيع المصفوفات.  
أما بالنسبة للألواح الشمسية ضمن السلسلة الواحدة، فقد تم **إهمال حساب التظليل الجانبي المتبادل** بينها؛ وذلك لاعتماد تصميم ميكانيكي يرتكز على رصف الألواح بشكل متلاصق (Side-by-Side Arrangement) دون وجود فواصل عرضية كبيرة تسمح بمرور الضوء أو تكون الظلال بين الألواح المتجاورة في نفس الصف، مما يجعل المصفوفة تعمل ككتلة واحدة مستمرة حيال الزوايا الجانبية للشمس.

### الحسابات المسافية

من ورقة بيانات (Datasheet) اللوح ([[الملحق (أ)]]) نجد أن أبعاد اللوح ($2.278 \times 1.134 \times 0.03\text{ m}$) وزاوية الميل المثالية التي توصلنا لها عبر الحسابات الدقيقة في الفصل السابق هي $\beta = 31^\circ$، وبناءًا عليه:
#### حساب المسقط الأفقي ($L_{proj}$)

 **"المسقط الأفقي" (Horizontal Projection)** أو **"بصمة اللوح" (Module Footprint)** هي الإزاحة الأفقية الناتجة عن إسقاط الطول المائل للوح الشمسي على مستوى سطح العمل (الأرض أو السطح المستوي). وتمثل المسافة الفعلية التي يشغلها اللوح من طول السطح عند النظر إليه من الأعلى (Top View).
 
  يُعتمد في حسابها على (L) الطول الحقيقي للوح في حال وضعية Portrait، أو عرضه في حال وضعية Landscape، على ($\beta$) زاوية ميل اللوح (Tilt Angle)؛ حيث كلما زادت هذه الزاوية قل المسقط الأفقي ($L_{proj}$) وازداد الارتفاع الرأسي (H)، كما نستخدم دالة جيب التمام (Cosine) لزاوية الميل، كما في العلاقة التالية:
$$\mathbf{L_{proj} = L \times \cos(\beta)}$$

**في حال الوضع الطولي (Portrait) للوح :**
$$L_{proj} = 2.278 \times \cos(31^\circ) = 1.952 \text{ m}$$
**في حال الوضع العرضي (Landscape) للوح :**
$$\mathbf{L_{proj} = L \times \cos(\beta)}=1.134 \times \cos(31^\circ)=0.972 \text{ m}$$

#### حساب الارتفاع الرأسي (H):

وهو المسافة العمودية من أعلى نقطة في حافة اللوح الخلفية إلى سطح الأرض. هذا الارتفاع ليس ثابتاً، بل يعتمد على طول اللوح (Panel Length) وزاوية ميله (Tilt Angle) المختارة للمشروع.

%%وكما ذُكر أنفاً هو المسافة العمودية من أعلى نقطة في حافة اللوح الخلفية إلى سطح الأرض.%%

تُحسب بالاعتماد على دالة الجيب (Sine) لزاوية الميل : 
$$\mathbf{H = L \times \sin(\beta)}$$
**في حال الوضع الطولي (Portrait) للوح :**
$$H = 2.278 \times \sin(31^\circ) = 1.173 \text{ m}$$
**في حال الوضع العرضي (Landscape) للوح :** 
$$H = 1.134 \times \sin(31^\circ) = 0.584 \text{ m}$$

### حساب المسافة الأفقية للظلال

#### المسافة الأفقية للظل المتبادل بين الصفوف:

نعتمد في حساب المسافة الأفقية التي يغطيها الظل على الارتفاع الرأسي (H)، وعلى زاوية الظل أو الارتفاع الشمسي ($\theta$) :
$$ D = \frac{H}{\tan(\theta)} $$
حيث زاوية الظل ($\theta$) هي زاوية سقوط أشعة الشمس بالنسبة للأفق، ويتم استخراجها هذه من "مخطط مسار الشمس" (Sun Path Chart) الخاص بإحداثيات الموقع. وبناءا عليه تم الاعتماد على موقع UO Solar Radiation Monitoring Laboratory للحصول على مخطط لمسار الشمس على مر أشهر السنة لمدينة حلب (التي تقع على احداثيات 36.12 درجة شمال خط الاستواء، و 37.08 شرق غرينتش).

![[PV-09-05.png]]

إذ تُحسب مسافة التظليل بناءً على أسوأ أيام السنة ظلاً؛ وهو يوم **21 ديسمبر** (الانقلاب الشتوي)، حيث تكون الشمس في أدنى مستوياتها، مما ينتج عنه أطول ظل ممكن خلال العام، ويسمى هذا اليوم **بيوم التصميم (Design Day)**. وبعبارة أخرى إذا نجح التصميم في تجنب الظل في هذا اليوم، فإنه سيضمن كفاءة النظام طوال أيام السنة. يتم تحديد الساعة **9:00 صباحاً** كبداية لفترة ذروة الإشعاع الشمسي التي يجب حمايتها من التظليل.

![[PV-09-06.png]] 

كما هو موضح في المخطط، زاوية الظل ($\theta$) في هذا التوقيت تساوي $12^{\circ}$ وبالتعويض في العلاقة :

**في حال الوضع الطولي (Portrait) للوح :**
$$ D = \frac{1.173}{\tan(12)} = 5.518 \text{ m} $$
**في حال الوضع العرضي (Landscape) للوح :** 
$$ D = \frac{0.584}{\tan(12)} = 2.747 \text{ m} $$
##### معامل تصحيح السمت (Azimuth Correction)

عند حساب المسافة البينية بين صفوف الألواح، تعتمد المعادلة الأساسية ($D = H / \tan(\theta)$) على زاوية ارتفاع الشمس (Solar Elevation Angle). ومع ذلك، فإن هذه المعادلة تفترض أن الظل يسقط بشكل عمودي تماماً خلف اللوح. في الواقع، خلال ساعات النهار (خاصة في الصباح الباكر عند التاسعة صباحاً أو في المساء عند الثالثة عصراً)، تكون الشمس في موقع جانبي بالنسبة للصفوف، مما يجعل الظل يسقط بزاوية مائلة.

هنا تبرز الحاجة لـ **معامل تصحيح السمت** لتقليص المسافة المحسوبة إلى "أقل مسافة ممكنة" (Minimum Distance) تضمن عدم التظليل دون إهدار في المساحات الأرضية للمشروع. حيث يُعد **معامل تصحيح زاوية السمت (Azimuth Correction)** أحد أدق المتغيرات في الحسابات الهندسية لتصميم مصفوفات الألواح الشمسية، حيث يهدف إلى الانتقال من الحساب النظري للمسافة (الذي يفترض تعامد الشمس مع الصفوف) إلى الحساب الفعلي الذي يراعي الحركة الأفقية للشمس في قبة السماء.

بدايةً يتم استخراج زاوية السمت (Azimuth Angle) من مخطط مسار الشمس (Sun Path Chart) للموقع الجغرافي المحدد، يتم إيجاد نقطة التقاطع بين الساعة 9:00 صباحاً ومنحنى تاريخ 21 ديسمبر. وبالتالي من أجل مشروعنا الحالي، زاوية السمت عند هذه النقطة هي $123^{\circ}$.

![[PV-09-07.png]]

ومن ثم يتم حساب زاوية التصحيح (Correction Angle) عبر حساب الفرق بين زاوية السمت المستخرجة وخط الجنوب الجغرافي (الذي يمثل زاوية $180^{\circ}$):

![[PV-09-08.jpg]]

$$
\text{Correction Angle} = 180^{\circ} - \text{Azimuth Angle at 9:00 AM}
$$
$$
\text{Correction Angle} =180^{\circ} - 123^{\circ} = 57^{\circ}
$$

بعد الحصول على المسافة الأولية ($D$) الناتجة عن نسبة الارتفاع إلى ظل زاوية الارتفاع، يتم تطبيق معامل التصحيح باستخدام دالة جيب التمام ($Cosine$) للزاوية المستخرجة:

$$
\mathbf{D_{\text{min}} = D \times \cos(\text{\small Correction Angle})}
$$
حيث أن:

- ع **$D_{\text{min}}$:** هي المسافة النهائية المصححة التي سيتم اعتمادها في مخططات التنفيذ.
- ع **$D$:** المسافة المحسوبة بناءً على الارتفاع وزاوية الظل ($H / \tan(\theta)$).
- ع **$\cos(\text{Correction Angle})$:** هو معامل التصحيح الذي يقلل المسافة لتتناسب مع الانحراف الأفقي للشمس.

**من أجل الوضع الطولي (Portrait) للوح :** 
$$ D_{\text{min}} = 5.518 \times \cos(57^{\circ}) = 3 \text{ m} $$
**من أجل الوضع العرضي (Landscape) للوح :** 
$$ D_{\text{min}} = 2.747 \times \cos(57^{\circ}) = 1.5 \text{ m} $$

تكمن أهمية إدراج هذا المعامل في المشروع في كونه يعكس دقة التصميم الهندسي؛ فاستخدام المسافة $D$ بدون تصحيح سيؤدي إلى تباعد كبير غير مبرر بين الصفوف، مما يقلل من عدد الألواح التي يمكن تركيبها في المساحة المتاحة. أما باستخدام **Azimuth Correction**، فإنك تحقق "الاستغلال الأمثل للمساحة" (Space Optimization) مع ضمان حماية كاملة للألواح من الظلال المتبادلة خلال ساعات الذروة الإنتاجية.

>[!info] الفهم الهندسي لمعامل تصحيح السمت (Azimuth Correction)
> تخيل معي أنك تنظر لسطح البنك من الأعلى (Top View):
> - في الساعة 12:00 ظهراً: تكون الشمس في الجنوب تماماً. أشعة الشمس تضرب اللوح من الأمام، والظل يسقط خلف اللوح باتجاه الشمال تماماً بشكل عمودي على الصف. في هذه اللحظة، طول الظل الفعلي (D) هو نفسه المسافة التي يجب تركها بين الصفوف.
>  - في الساعة 9:00 صباحاً (أسوأ حالة في الشتاء): الشمس لا تكون في الجنوب، بل تكون في الجنوب الشرقي (بزاوية سمت $123^\circ$). وبالتالي، الظل الذي سيرميه اللوح الأول لن يسقط نحو الشمال بشكل مستقيم، بل سيسقط مائلاً نحو الشمال الغربي.
> هنا تكمن الخدعة الهندسية:
> الظل المائل (القطري) طويل جداً (المسافة D). ولكن بما أننا نرص صفوف الألواح بشكل متوازٍ ومواجه للجنوب، فنحن لا نحتاج لأن نُبعد الصف الثاني بمسافة توازي هذا "الظل القطري" بالكامل. نحن نحتاج فقط للابتعاد بمقدار المركبة الرأسية (المسافة العمودية بين الصفين) التي تضمن أن هذا الظل المائل سيمر "بجانب" أو "أمام" الصف الثاني وليس فوقه.
> لذلك، نضرب طول الظل المائل بـ $\cos(57^\circ)$ لنأخذ المسقط العمودي فقط. إذا لم تستخدم هذا المعامل، ستجد أن المسافة المحسوبة بين الصفوف ضخمة جداً (مثلاً 4 أمتار!) مما سيهدر مساحة سطح البنك بالكامل.
> 
> ![[Illustration of Correction Angle(1).jpg]]
> 

#### المسافة الأفقية لظل وحدة التكييف

إذ أن ارتفاع وحدة التكييف هو $1.3 \text{ m}$، وبالتالي :
$$ D = \frac{H}{\tan(\theta)} = \frac{1.3}{\tan(12)} = 6.11 \text{ m}$$
مع أخذ معامل تصحيح السمت بعين الاعتبار :
$$\mathbf{D_{\text{min}} = D \times \cos(\text{\small Correction Angle})} = 6.11 \times \cos(57) = 3.33 \text{ m}$$
#### المسافة الأفقية لظل لغرفة الدرج

إذ أن ارتفاع غرفة الدرج هو $2.5 \text{ m}$، وبالتالي :
$$ D = \frac{H}{\tan(\theta)} = \frac{2.5}{\tan(12)} = 11.76 \text{ m}$$
مع أخذ معامل تصحيح السمت بعين الاعتبار :
$$\mathbf{D_{\text{min}} = D \times \cos(\text{\small Correction Angle})} = 11.76 \times \cos(57) = 6.4 \text{ m}$$
### حساب المسافات الجانبية للظل

تُمثل المسافة الجانبية الضلع الثالث للمثلث القائم الذي تشكله المسافة الأفقية الأولية (D) و المسافة الأفقية المصححة ($D_{min}$)، ويمكن حسابها من العلاقة :
$$ \mathbf{D_{Lat} = D \times \sin(\text{\small Correction Angle})} $$
![[Illustration of Correction Angle (D_Lat) .png]]

#### المسافة الجانبية لوحدة التكييف

$$ D_{Lat} = 6.11 \times \sin(12) = 1.27 \text{ m} $$
#### المسافة الجانبية لغرفة الدرج
$$ D_{Lat} = 11.76 \times \sin(12) = 2.44 \text{ m} $$
