MAQattan/My-Graduation-Project/GP_Obsidian/Graduation Project MOC.md

## [[Thesis MOC]] | [[Presentation MOC]] | [[Accessories MOC]] 

---

تعديل مساحة سحط البنك مع سطح درج الخروج $129m^2$ ، المبنى بدون حواف -> سنحتاج لممرات عبور 

![[Screenshot 2026-04-25 154814.png]]
