MAQattan/My-Graduation-Project/GP_Obsidian/Presentation/Presentation MOC.md

## [[التمهيد والتعريف بالبحث]] 
## [[الطور التصميمي والهندسة الميكانيكية - الفصل السادس]]  
## [[التكامل الكهربائي والتحقق الرقمي - الفصل السابع]] 
## [[الخاتمة والتوصيات]]
