MAQattan/My-Graduation-Project/GP_Obsidian/Presentation/التكامل الكهربائي والتحقق الرقمي - الفصل السابع.md

# [[سلايد اضافية 1]] 
# [[السلايد 16]] 
# [[السلايد 17]] 
# [[سلايد اضافية 2]] 
# [[سلايد اضافي 3]] 
# [[السلايد 18]] 
# [[السلايد 19]]
