MAQattan/My-Graduation-Project/GP_Obsidian/Presentation/التمهيد والتعريف بالبحث.md

### [[سلايد 2]] 
### [[سلايد 3]]  
### [[سلايد 4]]  
### [[سلايد 5]]
