MAQattan/My-Graduation-Project/GP_Obsidian/Presentation/الخاتمة والتوصيات.md

# [[السلايد 20]] 
# [[السلايد 21]] 
# [[السلايد 22]] 
# [[السلايد 23]] 
# [[السلايد 24]]
