MAQattan/My-Graduation-Project/GP_Obsidian/Presentation/السلايد 10.md

###  تحليل الظلال الهندسية (Geometric Shading Analysis)

**فلسفة الحساب والتحقق:**

- **يوم التصميم (Design Day):** اعتماد يوم "الانقلاب الشتوي" (21 كانون الأول) كمرجعية حسابية لكونه يمثل أطول مسقط ظل خلال العام.
- **النافذة الزمنية:** ضمان انعدام التظليل المتبادل خلال ساعات الذروة الإشعاعية الفعالة (9:00 AM - 3:00 PM).

**النمذجة الرياضية للمسافات البينية:**

1. **الارتفاع الشاقولي الحرِج ($H$):** يتم حسابه بدلالة طول اللوح ($L$) وزاوية الميل ($\beta$):  
    $H = L \times \sin(\beta)$.
2. **المسافة البينية النظرية ($D$):** تُشتق من زاوية ارتفاع الشمس ($\theta$) عند الساعة 9:00 صباحاً:  
    $D = H / \tan(\theta)$.
3. **معامل تصحيح السمت ($\psi_{Correction}$):** الحل الابتكاري لتقليص المساحات المهدورة عبر حساب الفارق بين زاوية سمت الشمس وخط الجنوب الجغرافي.
4. **المسافة الدنيا المصححة ($D_{min}$):** القيمة النهائية المعتمدة في المخطط التنفيذي:  
    $D_{min} = D \times \cos(\psi_{Correction})$.

**الأثر الهندسي:**

- أدى تطبيق معامل التصحيح إلى تحييد "العقوبة المساحية" (Spatial Penalty) ومنع التباعد غير المبرر بين الصفوف، مما رفع كثافة الألواح المركبة.

---

**اقتراح الصورة التوضيحية:**

> **ضع الشكل 5-6 (أو 5-10 حسب الترقيم في متن الفصل 6) في هذا السلايد:** "رسم هندسي يوضح زاوية السمت وزاوية السمت المصححة والعلاقة المثلثية بين الارتفاع $H$ والمسافات $D$ و $D_{min}$".

_هذا الشكل هو "البرهان الرياضي" لعرضك، حيث يوضح للجنة كيف استخدمت الهندسة الوصفية لتقليص المسافات البينية دون الوقوع في فخ التظليل المتبادل._

هل ننتقل إلى **سلايد 10: الحل الابتكاري (2) - دراسة التظليل الموضعي والجانبي**؟
