MAQattan/My-Graduation-Project/GP_Obsidian/Presentation/السلايد 11.md

### تحليل التظليل الموضعي والجانبي

**تجاوز المنهجية التقليدية:**

- **الانتقال النوعي:** تجاوز الممارسات الهندسية الشائعة التي تقتصر على حساب التظليل البيني الأفقي، نحو دراسة "حرم الظل" المعقد للعوائق الإنشائية الثابتة.
- **تشخيص العوائق:** تحليل الأثر الجيومكاني لغرفة الدرج ووحدات التكييف المركزية نظراً لارتفاعها النسبي الذي يفرض تظليلاً عرضياً حرجاً في ساعات معينة.

**المعايير التقنية للتصميم:**

1. **النمذجة الرياضية ($D_{Lat}$):** حساب المسافة الجانبية للظل الجانبي (Lateral Shading) بدقة لضمان ابتعاد المصفوفة عن مسقط الظل القطري:  
    $D_{Lat} = D \times \sin(\psi_{Correction})$
2. **استراتيجية النافذة الزمنية:** تبني نافذة إشعاعية فعالة للعوائق (11:00 AM - 2:00 PM) في يوم التصميم لتجنب "العقوبة المساحية" المفرطة، مع قبول فواقد شتوية طفيفة جداً مقابل تعظيم الإنتاج الصيفي السنوي.
3. **العزل الكهربائي:** توظيف نتائج دراسة الظلال في "التوزيع الفعال" عبر عزل السلاسل المتأثرة في مداخل مستقلة للعاكس.

---

**اقتراح الصورة التوضيحية:**

> **ضع الشكل 6-13 (أو 10-13 حسب الترقيم في متن الفصل 6) في هذا السلايد:** "تمثيل الظلال لوحدة التكييف وغرفة الدرج على المخطط المعماري للبنك في AutoCAD"،.

_هذا الشكل يمثل البرهان البصري على قدرتك كمصمم على محاكاة واقع السطح وتحويل العوائق المعمارية إلى أرقام ومسافات أمان دقيقة._

هل ننتقل الآن إلى **سلايد 11: استغلال المساحات المظللة جزئياً** لشرح كيفية رفع الهياكل فوق مستوى الظل الشتوي؟
