MAQattan/My-Graduation-Project/GP_Obsidian/Presentation/السلايد 12.md

### استغلال المساحات المظللة جزئياً (Utilizing Partially Shaded Areas)

**الفلسفة التصميمية للاستمثال المساحي:**

- **رفض الاستبعاد المطلق:** تجاوز المنهجية التقليدية غير الاقتصادية التي تستبعد المساحات المظللة جزئياً، والتحول نحو "الاستغلال الهندسي المشروط" لتعظيم القدرة المركبة.
- **تحليل المسار الفراغي للظل:** استغلال السلوك الهندسي المتغير للظل؛ حيث ينخفض ارتفاع مسقط الظل شاقولياً كلما ابتعدنا عن العائق الإنشائي المسبب له.

**المعايير التقنية والتحقق:**

1. **تحييد الأثر البرصي:** ضمان مرور المسار الفراغي للظل بالكامل تحت مستوى الخلايا الفعالة للألواح، مما يلغي فواقد التظليل اللحظية تماماً.
2. **المخرجات الرقمية:** أتاحت هذه المناورة الهندسية دمج **5 ألواح إضافية** في المنظومة، مما ساهم في الوصول إلى كثافة الاستطاعة المستهدفة دون التضحية بالموثوقية.

---

**اقتراح الصورة التوضيحية:**

> **ضع الشكل 16-6 (أو 16-10 حسب الترقيم في متن الفصل 6) في هذا السلايد:** "محاكاة ثلاثية الأبعاد تظهر مساقط وتأثير الظلال الحرجة المتشكلة من غرفة الدرج ووحدة التكييف على الألواح المضافة".

_هذا الشكل سيوضح للجنة التحكيم بصرياً كيف تمر "أشباح الظلال" تحت الهياكل المرفوعة، مما يبرز ذكاء التصميم الميكانيكي في التعامل مع قيود السطح._

هل ننتقل الآن إلى **سلايد 12: التحقق الرياضي للظلال** (السلايد 13 في الهيكلية الأصلية) لاستعراض حسابات ارتفاع الظل؟
