MAQattan/My-Graduation-Project/GP_Obsidian/Presentation/السلايد 13.md

### التحقق الرياضي للظلال

**منهجية إثبات الأمان الطاقي:**

- **الهدف:** التحقق الرقمي من أن المسار الفراغي ثلاثي الأبعاد للظل يمر بالكامل تحت مستوى الخلايا الفعالة للألواح الإضافية،.
- **نقطة التقاطع الحرجة:** تحليل أداء المنظومة في "الحالة الأكثر سوءاً" (**Worst-Case Scenario**) بتاريخ 21 كانون الأول،.

**النمذجة الرياضية والنتائج:**

1. **زاوية ميل الأشعة الشاقولية ($\phi$):** تُحسب استناداً إلى أبعاد العائق والمسافة البينية الدنيا:  
    $\phi = \tan^{-1}(H_{Obstacle} / D_{min})$،.
2. **ارتفاع الظل عند خط المقابلة ($Shadow\ Height$):** يتم حسابه عند نقطة التلاقي مع الهيكل الحامل:  
    $Shadow\ Height = l \times \tan(\phi)$،.
3. **شرط الامتثال الهندسي:**
    - **حالة وحدة التكييف:** ارتفاع الظل ($0.574\ m$) < ارتفاع الهيكل ($1.173\ m$) $\rightarrow$ **آمن**،.
    - **حالة غرفة الدرج:** ارتفاع الظل ($0.763\ m$) < ارتفاع الهيكل ($1.173\ m$) $\rightarrow$ **آمن**،.

**الاستنتاج الفني:**

- تؤكد الحسابات المثلثية تحييد مفاقيد التظليل اللحظية تماماً، مما سمح بزيادة القدرة المركبة دون نشوء فواقد "عدم تطابق" (**Mismatch**) أو "بقع ساخنة" (**Hotspots**)،.

---

**اقتراح الصورة التوضيحية:**

> **ضع الشكل 20-6 (أو 20-10 حسب الترقيم بمتن الفصل 6) في هذا السلايد:** "محاكاة فراغية ثلاثية الأبعاد تظهر سلوك ومسقط الظل الحرج لغرفة الدرج مقارنة بالهيكل الحامل للألواح"،. _أو يمكنك وضع **الشكل 18-6** "منظور ثلاثي الأبعاد يوضح محاكاة زاوية سقوط الإشعاع ومسار ظل وحدة التكييف"؛ فكلاهما يمثل البرهان البصري على صحة معادلاتك._

هل ننتقل الآن إلى **سلايد 13: تقييم كثافة الاستطاعة المساحية** (السلايد 14 في الهيكلية الأصلية) لاستعراض الرقم القياسي الذي حققه المشروع؟
