MAQattan/My-Graduation-Project/GP_Obsidian/Presentation/السلايد 14.md

### تقييم كثافة الاستطاعة المساحية

**التحجيم الرقمي للمنظومة:**

- **القدرة المركبة المستهدفة ($P_{total}$):** $39 , Panels \times 600 , W = 23,400 , W = 23.4 , kWp$.
- **إجمالي المساحة التصميمية ($Area$):** بلغت المساحة الصافية المستغلة فوق السطح **$195.67 , m^2$**.

**الحساب الرياضي لكثافة الاستطاعة المساحية:** تُحسب الجدارة المكانية للمنظومة وفق القانون والتعويض التالي: $$Power , Density = \frac{P_{total}}{Area}$$ $$Power , Density = \frac{23,400 , W}{195.67 , m^2} \approx \mathbf{119.59 , W/m^2}$$

**خلاصة الجدارة التصميمية:**

1. **استعادة المساحة المهدورة:** نجاح منهجية "التصميم القائم على المساحة" في استعادة **40%-50%** من رقعة السطح التي كانت ستُفقد عند اتباع أنماط التباعد التقليدية.
2. **تعظيم عامل LUF:** سمح "التثبيت المتدرج" بدمج **5 ألواح إضافية** في المناطق الحرجة، مما رفع كثافة التوليد إلى حدها الأقصى دون تظليل.

---

**اقتراح الصورة التوضيحية:**

> **ضع الشكل 21-6 (أو 21-10 حسب الترقيم بمتن الفصل 6) في هذا السلايد:** "المخطط الهندسي النهائي ثنائي الأبعاد لمصفوفات الألواح الكهروضوئية وتوزيعها على المساحة السطحية الكلية للمبنى المصرفي".

هذا المخطط يمثل "البرهان البصري" للنتائج الحسابية أعلاه، حيث يظهر للجنة كيف تم تحويل السطح المعقد إلى مصفوفة متراصة وعالية الكثافة.

هل ننتقل الآن إلى **سلايد 14: المواءمة والتحجيم الكهربائي للعاكس**؟
