MAQattan/My-Graduation-Project/GP_Obsidian/Presentation/السلايد 15.md

---

### المواءمة والتحجيم الكهربائي (Inverter Sizing & Matching)

**توصيف وحدة التحويل الرقمية:**

- **الطراز المعتمد:** عاكس ذكي ثلاثي الأطوار من طراز **Huawei SUN2000-25KTL-M5**.
- **الاستطاعة الاسمية المترددة ($P_{AC}$):** تبلغ $25 , kW$.
- **الكفاءة التشغيلية:** كفاءة قصوى **98.4%** وكفاءة أوروبية موزونة **98.2%**,.

**النمذجة الرياضية لنسبة التحميل (DC/AC Ratio):** يتم حساب معامل التصميم ($R$) لضمان استقرار العمل ضمن نوافذ الكفاءة المثلى وفق الآتي: $$R = \frac{P_{DC(Nominal)}}{P_{AC(Nominal)}}$$ $$R = \frac{23.4 , kWp}{25 , kW} = \mathbf{0.936}$$

**مبررات الاستمثال الكهربائي:**

1. **نطاق التشغيل المثالي:** تضمن النسبة (0.936) تشغيل العاكس في النطاق المحصور بين **40% و80%** من حمله الاسمي لأطول فترة زمنية، وهي منطقة ذروة الأداء التشغيلي.
2. **تحييد كبح القدرة (Clipping):** تفادي ظاهرة "قص التيار" صيفاً مع السماح بهامش مرن لأي توسعة مستقبلية دون تغيير البنية التحتية,.
3. **الحماية الذكية:** العاكس مزود بحماية **AFCI** القائمة على الذكاء الاصطناعي ضد القوس الكهربائي.

---

**اقتراح الصورة التوضيحية:**

> **ضع الجدول 2-6 (أو 2-10 حسب الترقيم بمتن الفصل 6) في هذا السلايد:** "ملخص الخصائص الفنية والكهربائية للعاكس الكهروضوئي الذكي المعتمد Huawei SUN2000-25KTL-M5",.

_هذا الجدول يمثل المستند الفني الذي يثبت مطابقة اختيارك للمكونات مع الحسابات التصميمية للمنظومة._

هل ننتقل الآن إلى **الجزء الثالث (التكامل الكهربائي - الفصل السابع)** لنبدأ بـ **سلايد 16: طوبولوجيا السلاسل ونافذة الجهد**؟
