MAQattan/My-Graduation-Project/GP_Obsidian/Presentation/السلايد 16.md

### طوبولوجيا السلاسل وضبط نافذة الجهد

**الهدف الهندسي:**

- مواءمة الجهد التشغيلي للمصفوفة مع نقطة الاستقرار المثلى للعاكس (**Rated Input Voltage**) البالغة **600V**، لتحقيق أعلى كفاءة تحويل داخلية،.

**1. حساب العدد المثالي للألواح في السلسلة ($N_{ideal}$):** يُحسب بالتمركز حول الجهد الاسمي للعاكس بدلاً من الحدود الدنيا/العليا: $$N_{ideal} = \frac{V_{rated} , (Inverter)}{V_{mp} , (at , STC)}$$ $$N_{ideal} = \frac{600 , V}{44.66 , V} \approx 13.43 \rightarrow \mathbf{13 , Panels}$$

**2. تحديد عدد السالسل الكلي ($N_{strings}$):** $$N_{strings} = \frac{N_{modules}}{N_{series}}$$ $$N_{strings} = \frac{39}{13} = \mathbf{3 , Strings}$$

**3. التحقق من المواءمة التشغيلية:**

- **جهد السلسلة المصمم ($V_{string_STC}$):** $13 \times 44.66 , V = \mathbf{580.58 , V}$ (انحراف طفيف بنسبة 3% فقط عن الـ 600V المثالية)،.
- **شرط الأمان:** الرقم المعتمد (13) يقع في منتصف النطاق المسموح كهربائياً ($6 \leq 13 \leq 19$)، مما يضمن استقرار خوارزمية **MPPT** صيفاً وشتاءً،.

---

**اقتراح الصورة التوضيحية:**

> **ضع الشكل 3-11 (أو 3-7 حسب الترقيم بمتن الفصل 7) في هذا السلايد:** "واجهة تعريف المكونات الفنية وتوزيع السالسل الكهربائية (13 لوح/سلسلة) وضبط نسبة التحميل (0.936) في برنامج PVsyst"،.

_هذا الشكل يمثل "شهادة المطابقة الرقمية" لتصميمك، حيث يظهر قبول البرنامج للتحجيم وتوزيعه المتناظر بدون أخطاء._

هل ننتقل إلى **سلايد 17: استراتيجية التوزيع الفعال (Multi-MPPT)** لشرح كيفية عزل السلسلة المظللة؟
