MAQattan/My-Graduation-Project/GP_Obsidian/Presentation/السلايد 17.md

### استراتيجية التوزيع الفعال (Multi-MPPT Distribution)

**الهدف الهندسي:**

- عزل "العقوبة الطاقية" الناتجة عن التظليل الموضعي لغرفة الدرج، ومنع انتقال أثر هبوط الجهد إلى السلاسل المستقرة إشعاعياً،.

**آلية التوزيع الكهربائي (String Mapping):**

1. **المتعقب الأول ($MPPT_1$):** يضم السلسلتين (1 & 2) بإجمالي **26 لوحاً**؛ تغطي المناطق "الآمنة والمشمسة تماماً" (وسط وغرب السطح)،.
2. **المتعقب الثاني ($MPPT_2$):** يضم السلسلة الثالثة (3) بمفردها (**13 لوحاً**)؛ وهي السلسلة القريبة من غرفة الدرج والمعرضة للظلال الجانبية اللحظية،.

**المخرجات التقنية للاستراتيجية:**

- **تحييد فواقد عدم التطابق (Mismatch Losses):** حصر تراجع القدرة في مدخل واحد فقط، مما حمى **66%** من إجمالي المصفوفة من الانهيار الطاقي التبعي،.
- **الاستمثال اللحظي:** السماح لخوارزمية العاكس بالبحث عن نقطة الاستطاعة العظمى لكل زمرة بشكل مستقل، مما رفع "معامل الأداء" ($PR$) الإجمالي للمنظومة إلى **89.3%**،.

---

**اقتراح الصورة التوضيحية:**

> **ضع الشكل 3-7 (أو 3-11 حسب الترقيم في متن الفصل 7) في هذا السلايد:** "واجهة تعريف المكونات الفنية وتوزيع السلاسل الكهربائية على متعقبات العاكس المستقلة في برنامج PVsyst"،.

_هذا الشكل يبرز للجنة التحكيم كيف قمت بترجمة حل مشكلة الظلال ميكانيكياً إلى تقسيم كهربائي دقيق داخل برنامج المحاكاة._

هل ننتقل الآن إلى **سلايد 19: هندسة الحماية والترابط** لاستعراض منظومة التأريض ومانعات الصواعق؟
