MAQattan/My-Graduation-Project/GP_Obsidian/Presentation/السلايد 18.md

### هندسة الحماية والارتباط الكهربائي

**1. استراتيجية الحماية من التيار الزائد (Overcurrent Strategy):**

- **جانب المستمر ($DC$):** اعتماد مصاهر $gPV$ بسعة **$25A$** لكل سلسلة لحماية الخلايا من التيارات العكسية، مع مفاتيح عزل ميكانيكي بقدرة **$32A$**.
- **جانب المتردد ($AC$):** حماية مخرج العاكس بقاطع مصغر ($MCB$) سعة **$50A$** وقاطع رئييسي ($MCCB$) سعة **$63A$**، مع ضبط الانتقائية الصارمة لمنع الفصل العشوائي.

**2. منظومة الحماية من الجهود العابرة ($SPD$):**

- **الفئة المعتمدة:** تركيب مانعات صواعق من **النوع الثاني (Type II)** على جبهتي التيار المستمر والمتردد.
- **الوظيفة التقنية:** كبح الجهود العابرة ($Clamping$) وتصريف النبضات حتى **$40kA$** لحماية جسور الـ $IGBT$ الحساسة في العاكس.

**3. هندسة التأريض والربط متساوي الكهروجهد ($Earthing$):**

- **الهدف التصميمي:** خفض مقاومة الانتشار الأرضي لتحقيق شرط الأمان ($R_e < 5\Omega$).
- **التحقق الحسابي:** باستخدام معادلة "دوايت" ($Dwight's$)، تم تصميم حقل مكون من **10 قضبان** فوالذية ملبسة بالنحاس، مما حقق مقاومة كلية فعلية قدرها **$3.98\Omega$**.
- **الربط البنيوي:** تأريض كافة الهياكل المعدنية وإطارات الألواح لترصيف الشحنات الساكنة ومكافحة ظاهرة الـ **$PID$**.

---

**اقتراح الصورة التوضيحية:**

> **ضع الشكل 5-10 (أو 5-6 حسب الترقيم بمتن الفصل 10):** "الجدول التلخيصي والمواصفات الفنية لمنظومة التأريض والربط متساوي الكهروجهد"، [314، 572].

_هذا الجدول يمثل ملخصاً هندسياً شاملاً يربط بين المكونات، المقاطع العرضية للكابلات، والوظيفة الحمائية لكل جزء._

هل ننتقل الآن إلى **سلايد 20: المخطط أحادي الخط (SLD)** لعرض التكامل الكهربائي النهائي للمنظومة؟
