MAQattan/My-Graduation-Project/GP_Obsidian/Presentation/السلايد 19.md

### المخطط أحادي الخط (Single Line Diagram - SLD)

**1. هيكلية جانب التيار المستمر ($DC$):**

- **المصفوفة:** 39 لوحاً موزعة على 3 سلاسل ($Strings$) مستقلة، بواقع 13 لوحاً لكل سلسلة.
- **لوحة التجميع ($DCDB$):** تشتمل على مصاهر $gPV$ سعة **$25A$** وقواطع عزل ثنائية الأقطاب سعة **$32A$** لكل سلسلة.
- **توزيع المتعقبات:** ربط السلسلتين (1 & 2) توازياً على **$MPPT_1$**، وعزل السلسلة (3) على **$MPPT_2$** لضمان استقرار الأداء حيال ظلال غرفة الدرج.

**2. مرحلة التحويل والربط المتردد ($AC$):**

- **وحدة العكس:** عاكس ذكي **Huawei 25KTL** بمخرج ثلاثي الأطوار متزن ($400V/50Hz$).
- **ناقل القدرة:** كابل نحاسي مقطع **$16mm^2$** معزول بـ $XLPE/PVC$ لتقليص فواقد هبوط الجهد تحت عتبة الـ **$1\%$**.
- **نقطة الارتباط:** الربط مع اللوحة الرئيسية ($MDB$) عبر قاطع رباعي الأقطاب سعة **$50A$**، مع دمج عداد القياس التبادلي وحساس القدرة الذكي.

**3. فلسفة الحماية والتأريض الشاملة:**

- **الحماية العابرة:** منظومة $SPD$ من **النوع الثاني (Type II)** مدمجة على جبهتي الدخل والخرج.
- **شبكة التأريض:** مسار نحاسي مستمر يربط هياكل الألواح وإطار العاكس واللوحات بحقل أقطاب يحقق مقاومة انتشار **$3.98\Omega$.

---

**اقتراح الصورة التوضيحية:**

> **ضع الشكل 26-6 (المطابق لـ 26-10 في المتن):** "المخطط أحادي الخط التفصيلي للمنظومة الكهروضوئية المعد عبر برنامج AutoCAD، والذي يوضح الربط الكهربائي وجوانب الحماية المتكاملة"، [272، 343].

_هذا المخطط هو الوثيقة المرجعية الأهم في عرضك، فهو يثبت للجنة التحكيم قدرتك على تحويل الحسابات النظرية إلى تصميم هندسي تنفيذي مطابق للمعايير الدولية._

هل ننتقل الآن إلى **الجزء الرابع (التحقق الرقمي - الفصل الحادي عشر)** لنبدأ بـ **سلايد 21: بناء التوأم الرقمي (Digital Twin)** في برنامج PVsyst؟
