MAQattan/My-Graduation-Project/GP_Obsidian/Presentation/السلايد 20.md

### بناء التوأم الرقمي (Digital Twin) والمورد الجيومناخي

**فلسفة النمذجة الرقمية:**

- **التوأم الرقمي:** بناء نموذج حاسوبي متكامل في بيئة **PVsyst** لمحاكاة السلوك الفيزيائي للمنظومة تحت وطأة الظروف المناخية المتغيرة والمحدودية المكانية للموقع،.
- **الهدف التصميمي:** الانتقال من التقديرات الساكنة إلى التنبؤات الديناميكية الدقيقة للإنتاجية السنوية ($E_{sys}$) وتحليل المفاقيد،.

**المعايير الجيومناخية (Site Parameters):**

1. **الإحداثيات الجغرافية:** تحديد موقع البنك بدقة (36.20° شمالاً، 37.14° شرقاً) بارتفاع 379 متراً فوق سطح البحر.
2. **محرك الأرصاد الجوية:** استيراد البيانات من قاعدة **Meteonorm 8.0** لتوليد جداول الإشعاع الكلي والانتشاري (Global , & , Diffuse , Irradiance) ومخططات درجات الحرارة الساعية،.
3. **الاستمثال الهندسي (Quick Optimization):** تأكيد مطابقة زاوية الميل (**31°**) والسمت (**0°**) مع القيم المثالية النظرية لتحقيق مفقودات توجيه صفرية ($0.0\% , loss$).

---

**اقتراح الصورة التوضيحية:**

> **ضع الشكل 1-7 (المطابق لـ 1-11 في المتن) في هذا السلايد:** "واجهة ضبط الإحداثيات الجغرافية لمدينة حلب واستيراد بيانات الطقس عبر Meteonorm 8.0 في برنامج PVsyst"، [236، 318].

_هذه الصورة تمثل حجر الزاوية للمحاكاة، حيث تظهر للجنة أن كافة النتائج الطاقية اللاحقة مبنية على بيانات مناخية معيارية وموقعية دقيقة._

هل ننتقل الآن إلى **سلايد 21: مؤشرات الجدارة الطاقية (PR & Yield)** لاستعراض الأرقام القياسية التي حققتها المنظومة؟
