MAQattan/My-Graduation-Project/GP_Obsidian/Presentation/السلايد 21.md

### مؤشرات الجدارة الطاقية (Energy Merit Indicators)

**1. حصاد الطاقة السنوي ($E_{Grid}$):**

- تؤكد نتائج المحاكاة قدرة المنظومة على ضخ إجمالي طاقة صافية للشبكة تقدر بـ **$44.02 , MWh/year$**.

**2. الإنتاجية النوعية (Specific Yield - SY):** تُعبر عن "الساعات التشغيلية الفعالة" للمنظومة سنوياً، وتُحسب وفق الآتي: $$SY = \frac{E_{Grid}}{P_{array-STC}} = \frac{44020 , kWh}{23.4 , kWp} = \mathbf{1881 , kWh/kWp/year}$$

- **الدلالة الهندسية:** كل $1 , kWp$ مركب سينتج قرابة $1.9 , MWh$ سنوياً، وهو ما يقلص "فترة استرداد رأس المال" (Payback Period).

**3. معامل الأداء (Performance Ratio - PR):** يُمثل المعيار العالمي لجودة التصميم وتقليص المفاقيد: $$PR = \frac{SY}{PSH_{tilted}} = \frac{1881}{2106.4} = \mathbf{89.3\%}$$

- **التقييم الفني:** هذه القيمة ($89.3\%$) تُعد "رقمًا قياسياً" (Benchmark) يتجاوز النطاق التقليدي ($75\% - 85\%$)، مما يوثق نجاح تقنية "التثبيت المتدرج" في تحييد الظلال المتبادلة.

**التحقق من الاتساق الرياضي:**

- تطابق النتائج يؤكد صحة العلاقة: $Specific , Yield = PSH_{tilted} \times PR$، مما يمنح التصميم موثوقية أكاديمية كاملة،.

---

**اقتراح الصورة التوضيحية:**

> **ضع الشكل 6-7 (المطابق لـ 6-11 في المتن) في هذا السلايد:** "ملخص نتائج المحاكاة في PVsyst الذي يبرز قيم الإنتاجية السنوية، والإنتاجية النوعية، ومعامل الأداء"، [254، 321].

_هذه الصورة هي "بطاقة النتائج" النهائية لعملك، حيث تظهر للجنة الأرقام الثلاثة الذهبية التي تلخص نجاح مشروعك بالكامل._

هل ننتقل الآن إلى **سلايد 22: تحليل الإنتاجية المعايرة** لتوضيح توزيع الطاقة المفيدة والمفاقيد اليومية؟
