MAQattan/My-Graduation-Project/GP_Obsidian/Presentation/السلايد 22.md

### تحليل الإنتاجية المعايرة والمفاقيد اليومية

**فلسفة المعايرة (Normalization):**

- نسب مخرجات المنظومة والضياعات إلى "الكيلوواط الذروي الواحد" ($1 , kWp$) لتبسيط رصد الكفاءة التشغيلية اليومية وتسهيل المقارنة المعيارية،.

**تفكيك مكونات الأداء اليومي (المعدلات السنوية):**

1. **الإنتاجية المفيدة ($Y_f$):** سجلت المنظومة متوسطاً متميزاً قدره **$5.15 , kWh/kWp/day$** محقوناً في الشبكة،.
    - **الدلالة الهندسية:** كل $1 , kWp$ مركب ساهم بإنتاج ما يزيد عن خمس ساعات تشغيل كاملة من الطاقة الصافية يومياً،.
2. **مفاقيد المصفوفة ($L_c$):** ضياعات جانب المستمر ($DC$) الناتجة عن (الحرارة، الاتساخ، ومقاومة الكابلات)، وبلغت **$0.51 , kWh/kWp/day$**،.
3. **مفاقيد النظام ($L_s$):** ضياعات التحويل داخل العاكس ($DC , to , AC$)، بلغت قيمتها الدنيا **$0.11 , kWh/kWp/day$**،.

**الاستنتاج الفني:**

- تؤكد النتائج أن "الطاقة المفيدة" هي المكون المهيمن في ميزان الطاقة اليومي، مما يثبت نجاح التصميم في تحييد المفاقيد واسترداد أقصى قدر ممكن من الفوتونات الساقطة.

---

**اقتراح الصورة التوضيحية:**

> **ضع الشكل 7-7 (المطابق لـ 7-11 في المتن) في هذا السلايد:** "مخطط الإنتاجية المعايرة اليومية يوضح توزيع الطاقة المفيدة $Y_f$ مقابل مفاقيد المصفوفة $L_c$ ومفاقيد النظام $L_s$ لكل كيلوواط ذروة مركب"،.
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
