MAQattan/My-Graduation-Project/264.png

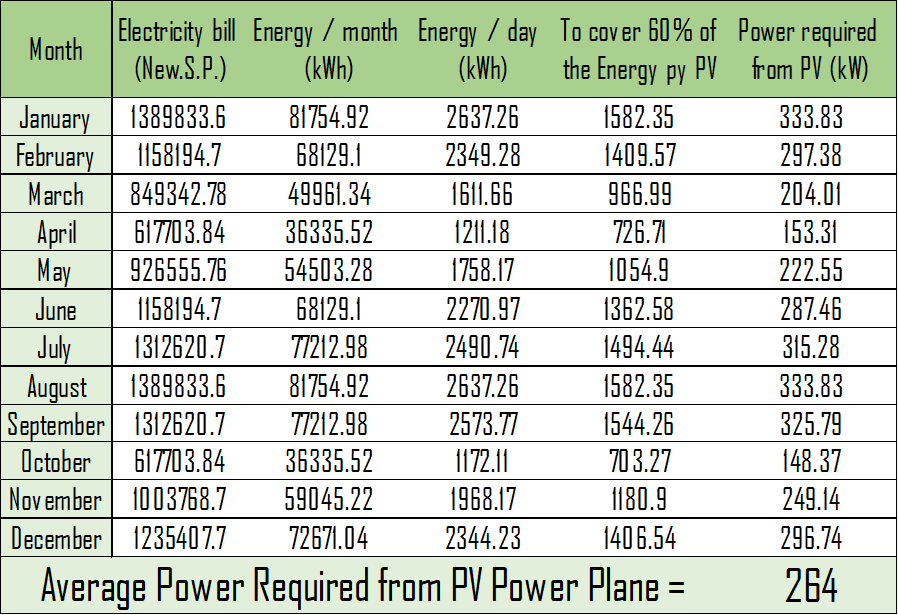
264.png
