MAQattan/My-Graduation-Project/Data about the project site/1771487291.jpg

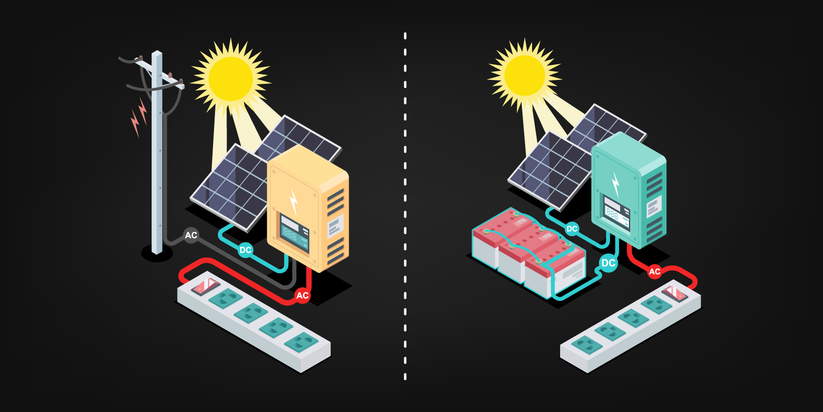
Data about the project site/1771487291.jpg
