MAQattan/My-Graduation-Project/Data about the project site/Aleppo Sun Path Chart_36.12_37.08 (1).png

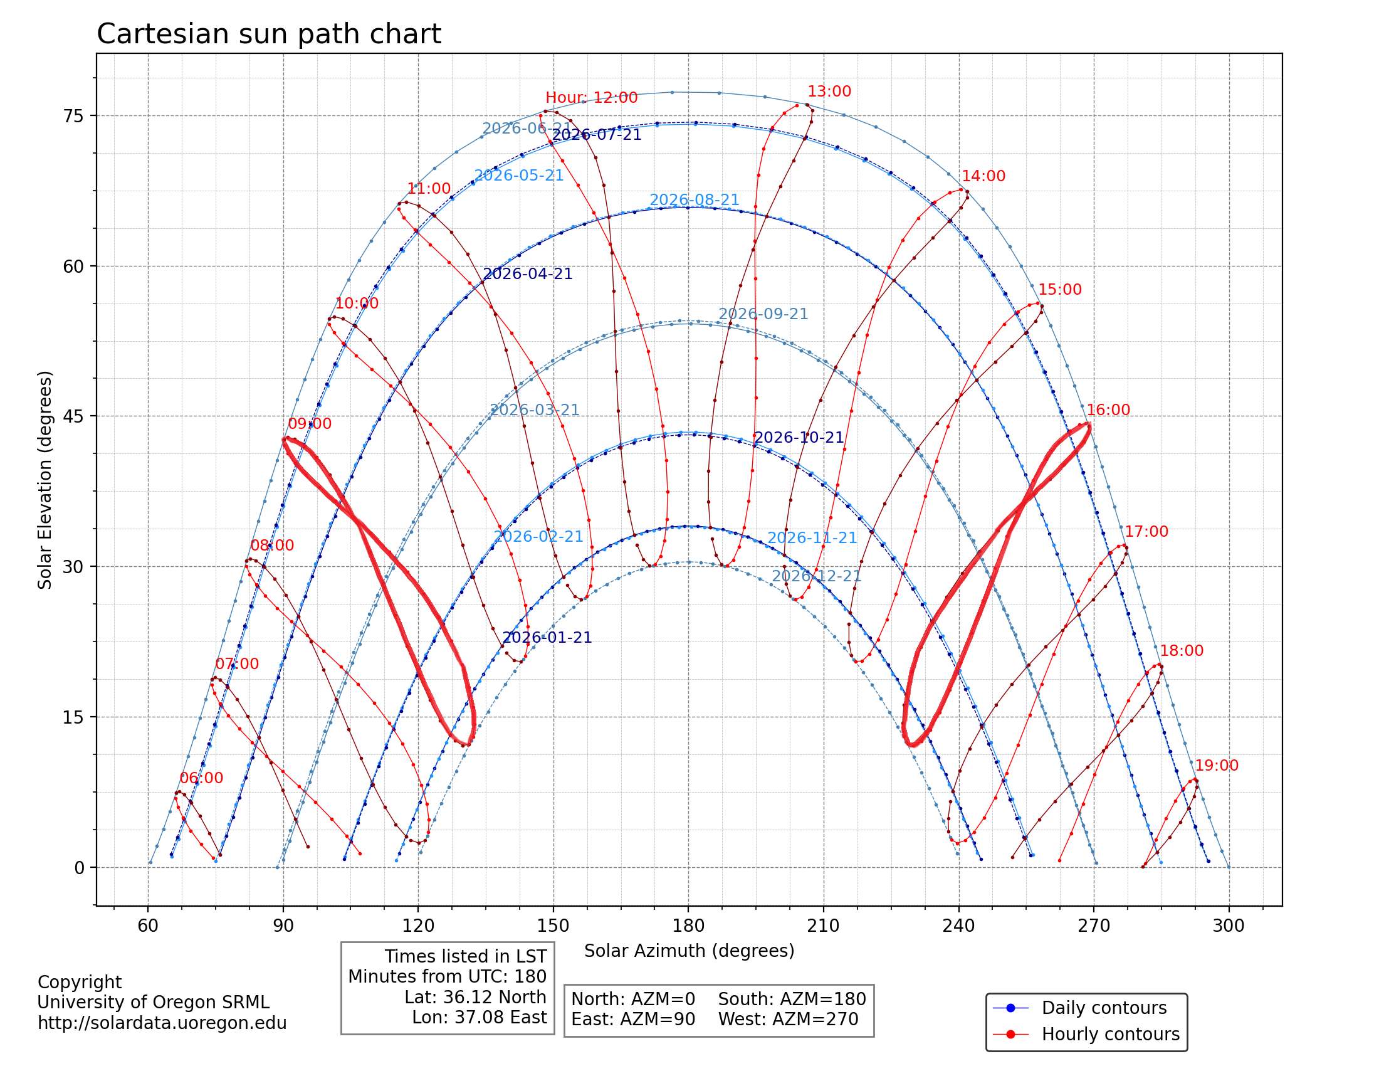
Data about the project site/Aleppo Sun Path Chart_36.12_37.08 (1).png
