MAQattan/My-Graduation-Project/Data about the project site/Aleppo Sun Path Chart_36.12_37.08 (3) - Copy - Copy.png

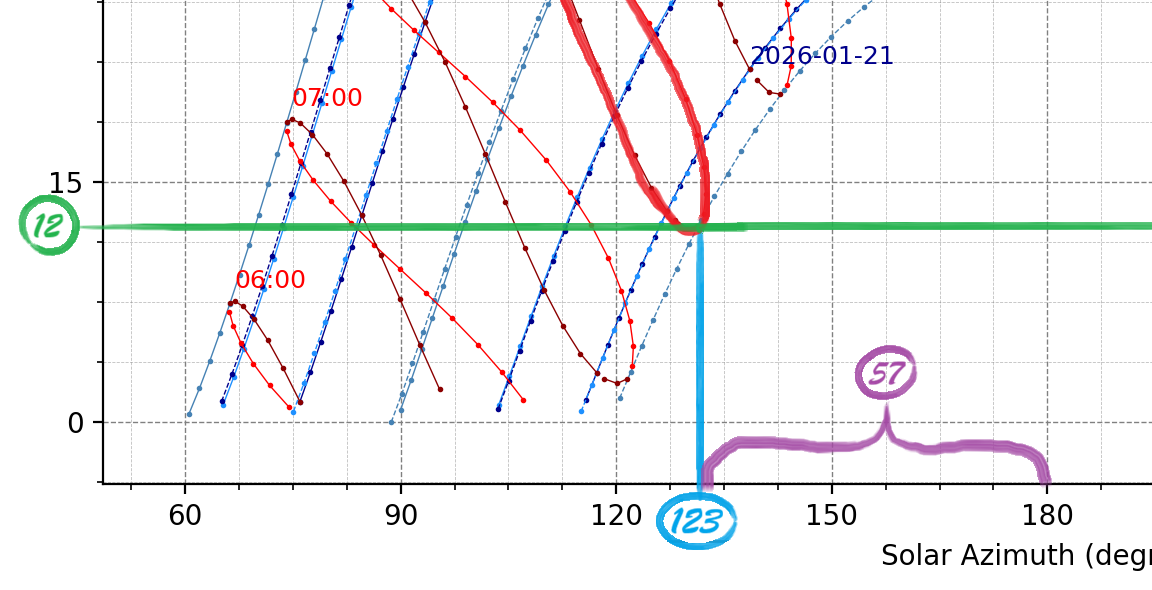
Data about the project site/Aleppo Sun Path Chart_36.12_37.08 (3) - Copy - Copy.png
