MAQattan/My-Graduation-Project/Data about the project site/New folder/Schematic-of-pitch-length-calculation.png

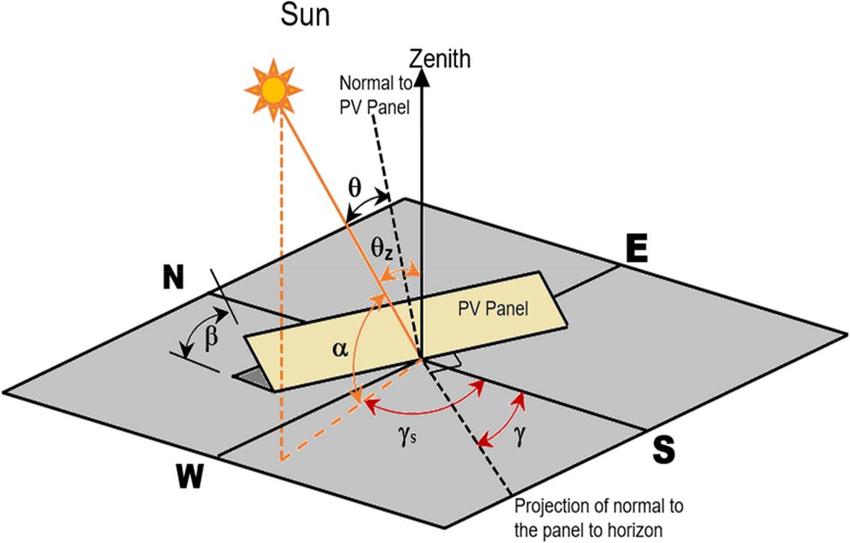
Data about the project site/New folder/Schematic-of-pitch-length-calculation.png
