MAQattan/My-Graduation-Project/Data about the project site/Screenshot 2026-04-04 113735.png

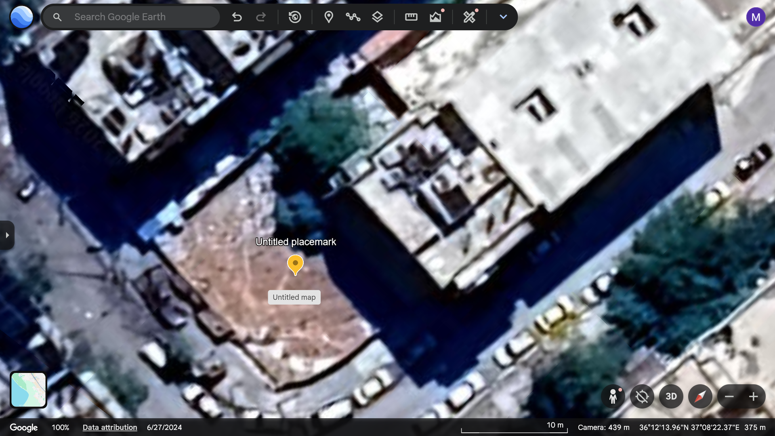
Data about the project site/Screenshot 2026-04-04 113735.png
