MAQattan/My-Graduation-Project/Data about the project site/Screenshot 2026-04-05 110951.png

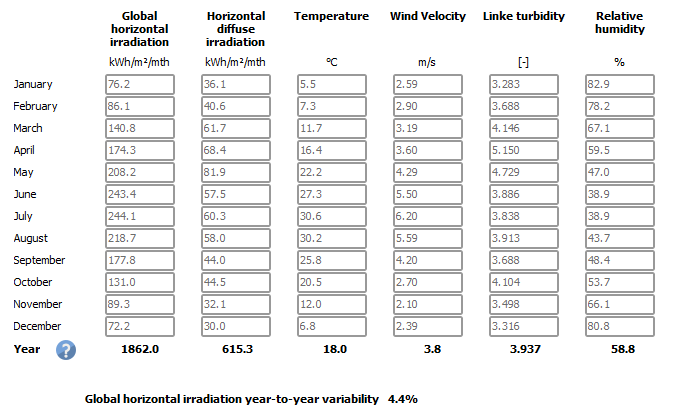
Data about the project site/Screenshot 2026-04-05 110951.png
