MAQattan/My-Graduation-Project/Data about the project site/Screenshot 2026-04-08 160711.png

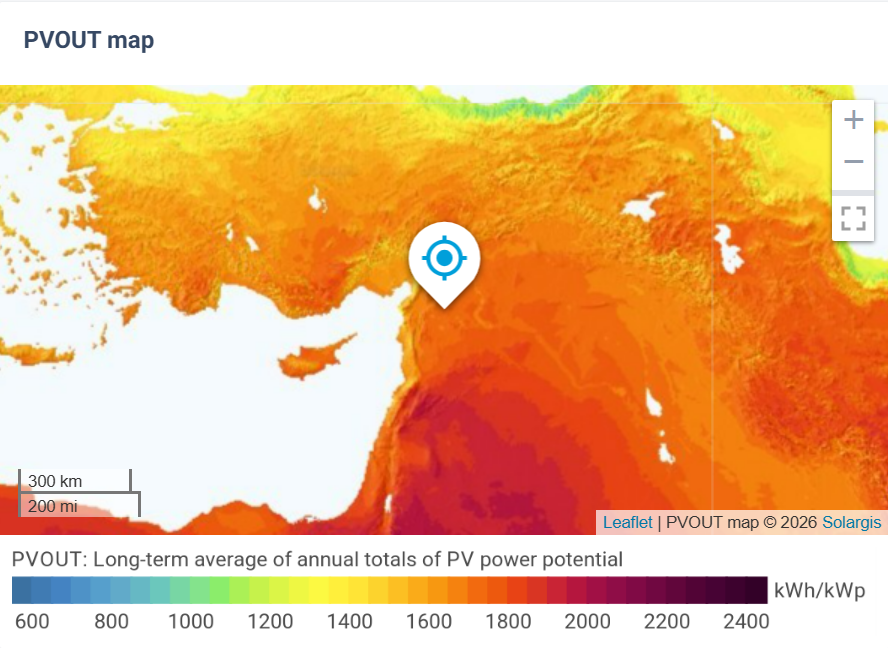
Data about the project site/Screenshot 2026-04-08 160711.png
