MAQattan/My-Graduation-Project/GP_Obsidian/Attachments/Index 01.jpg

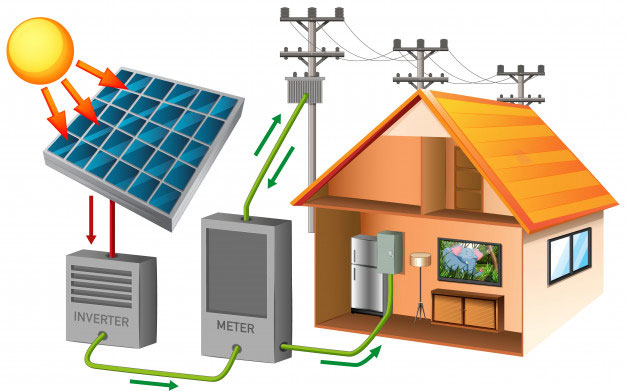
GP_Obsidian/Attachments/Index 01.jpg
