MAQattan/My-Graduation-Project/GP_Obsidian/Attachments/Index 02.png

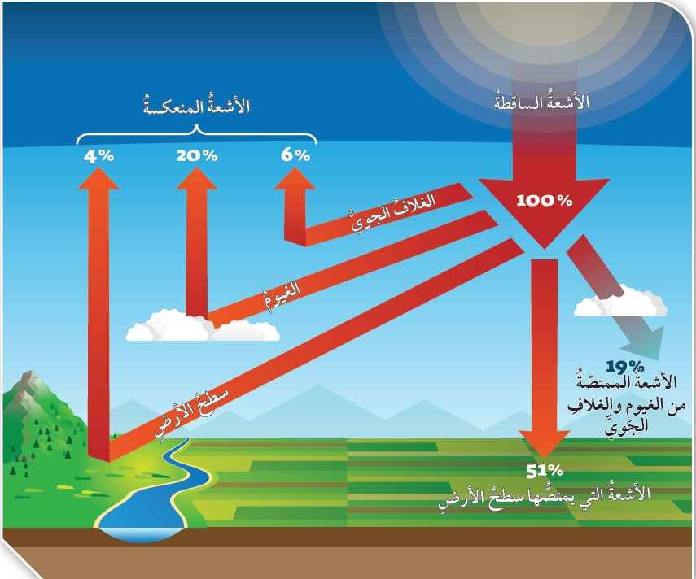
GP_Obsidian/Attachments/Index 02.png
