MAQattan/My-Graduation-Project/GP_Obsidian/Attachments/Index 03.png

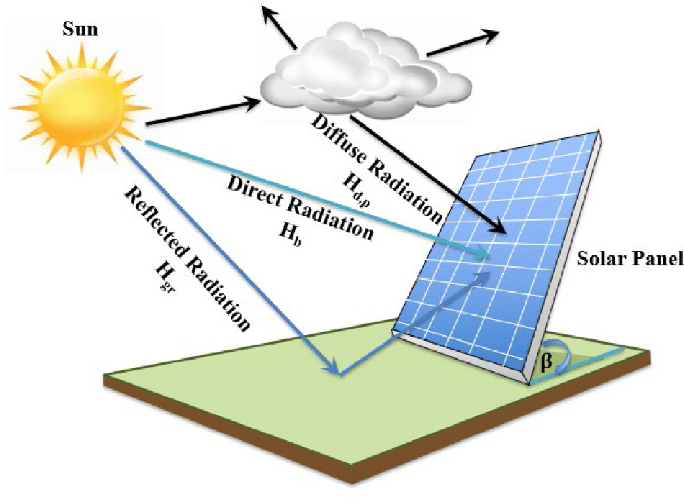
GP_Obsidian/Attachments/Index 03.png
