MAQattan/My-Graduation-Project/GP_Obsidian/Attachments/PEAK-SUN.gif

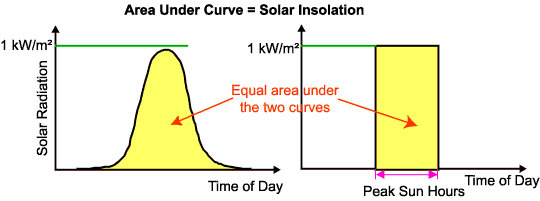
GP_Obsidian/Attachments/PEAK-SUN.gif
