MAQattan/My-Graduation-Project/GP_Obsidian/Attachments/Screenshot 2026-04-25 154814.png

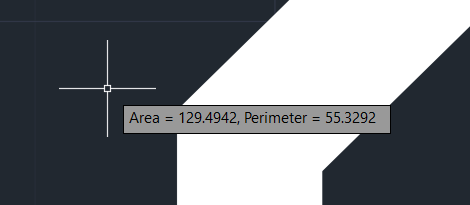
GP_Obsidian/Attachments/Screenshot 2026-04-25 154814.png
