MAQattan/My-Graduation-Project/GP_Obsidian/Attachments/SI 01.png

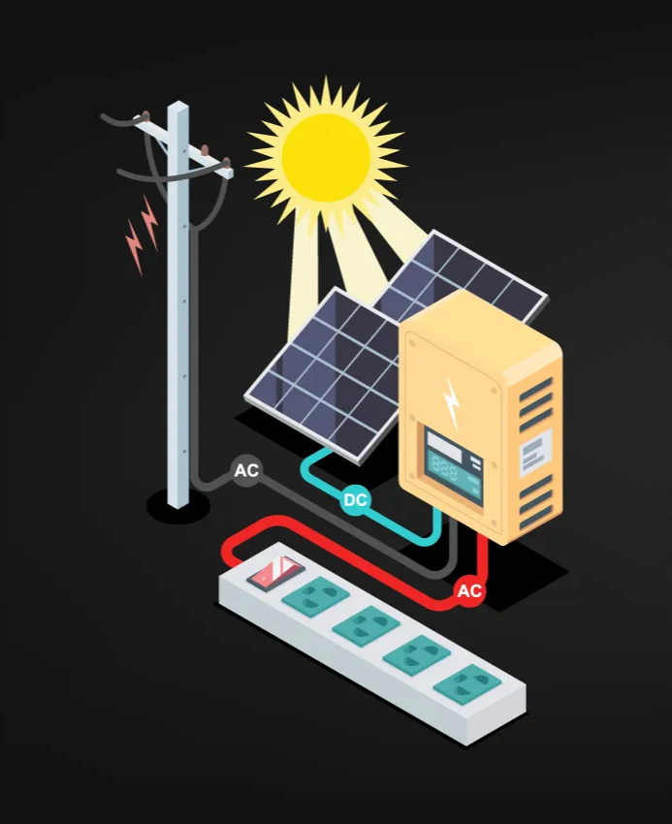
GP_Obsidian/Attachments/SI 01.png
