MAQattan/My-Graduation-Project/GP_Obsidian/Attachments/SI 02.png

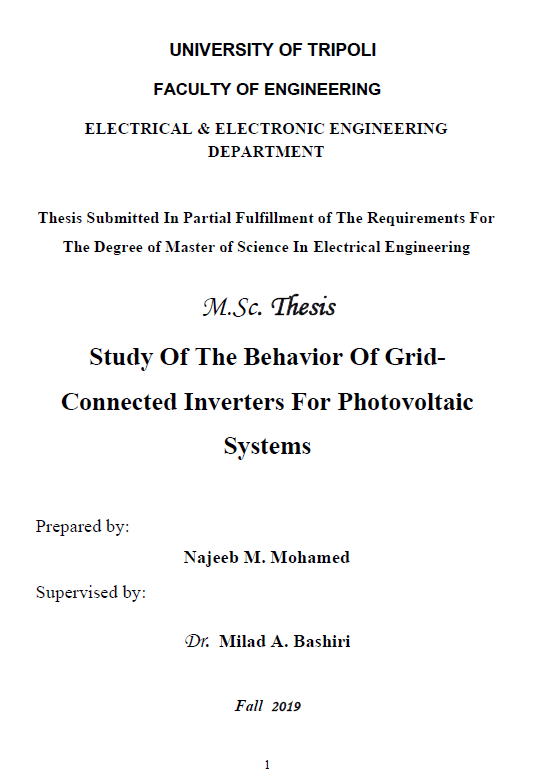
GP_Obsidian/Attachments/SI 02.png
