MAQattan/My-Graduation-Project/GP_Obsidian/Attachments/SI 03.png

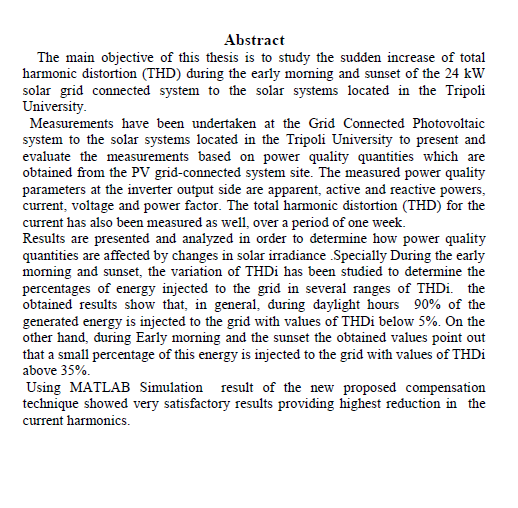
GP_Obsidian/Attachments/SI 03.png
