MAQattan/My-Graduation-Project/GP_Obsidian/Attachments/SI 04.png

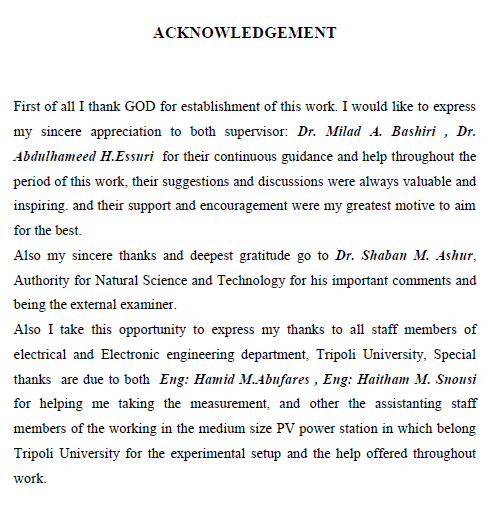
GP_Obsidian/Attachments/SI 04.png
