MAQattan/My-Graduation-Project/GP_Obsidian/Attachments/SI 05.png

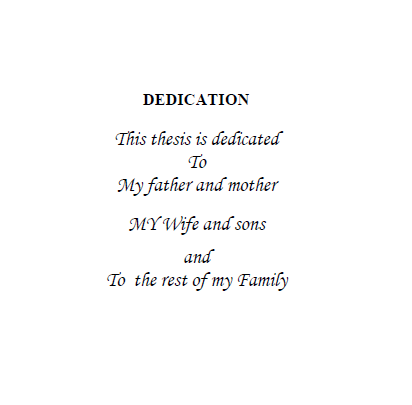
GP_Obsidian/Attachments/SI 05.png
