MAQattan/My-Graduation-Project/GP_Obsidian/Presentation/specific-yield-solar-pv-same-location-comparison.webp

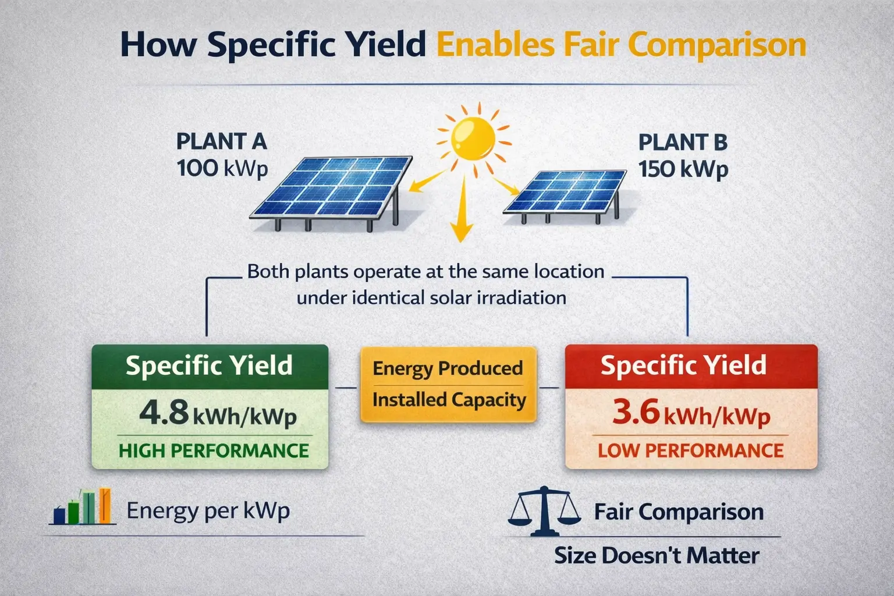
GP_Obsidian/Presentation/specific-yield-solar-pv-same-location-comparison.webp
