MAQattan/My-Graduation-Project/GP_Obsidian/Thesis/6/Figures/PV-06-02.jpg

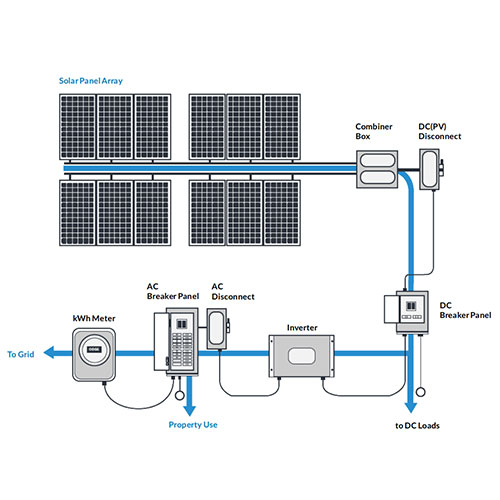
GP_Obsidian/Thesis/6/Figures/PV-06-02.jpg
