MAQattan/My-Graduation-Project/Illustrations/3df2d12a-9647-4f14-b2d9-c0ec93a9c686.png

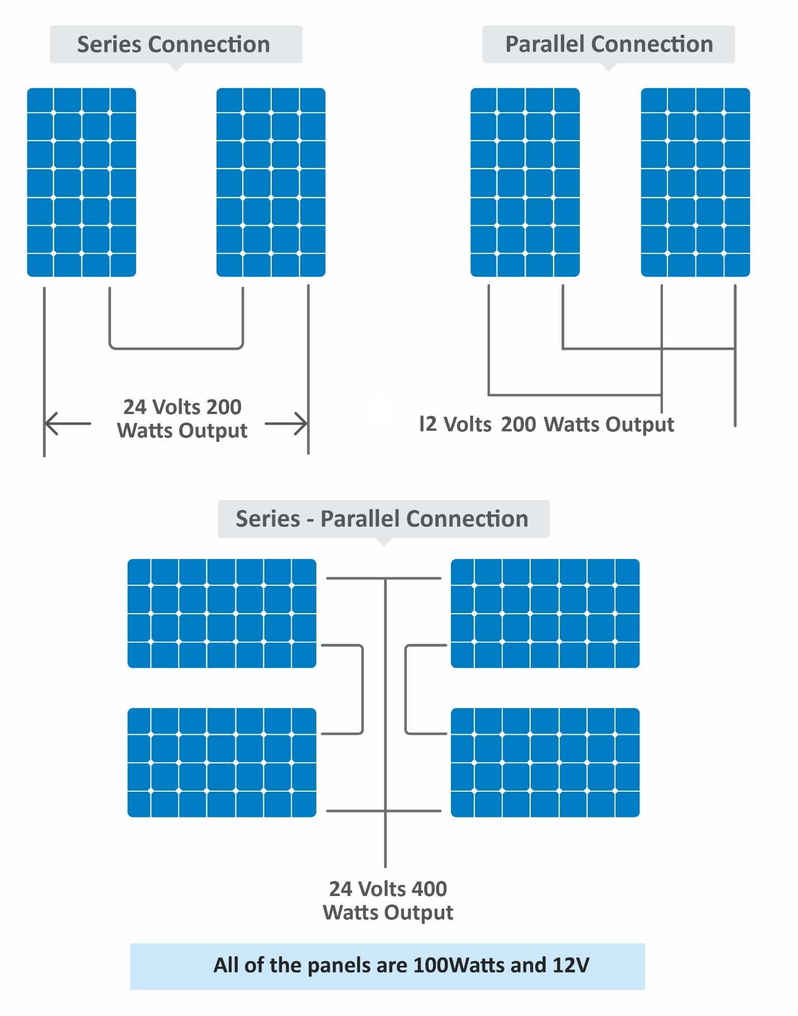
Illustrations/3df2d12a-9647-4f14-b2d9-c0ec93a9c686.png
