MAQattan/My-Graduation-Project/Illustrations/4.jpg

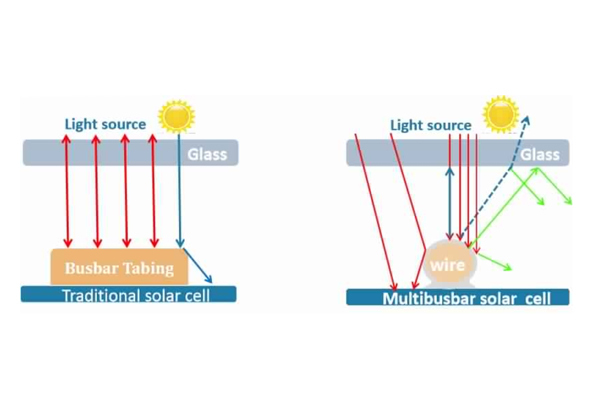
Illustrations/4.jpg
