MAQattan/My-Graduation-Project/Illustrations/7.jpg

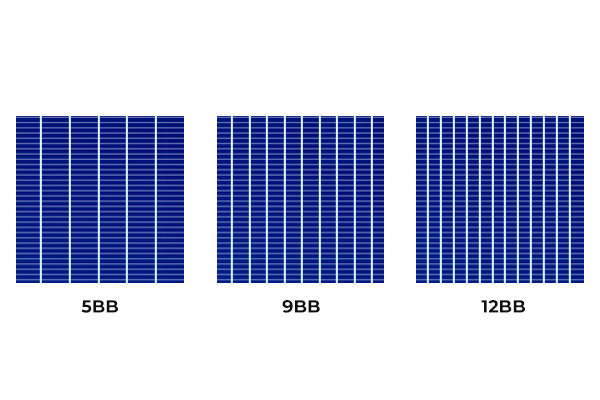
Illustrations/7.jpg
