MAQattan/My-Graduation-Project/Illustrations/359658603_389.jpg

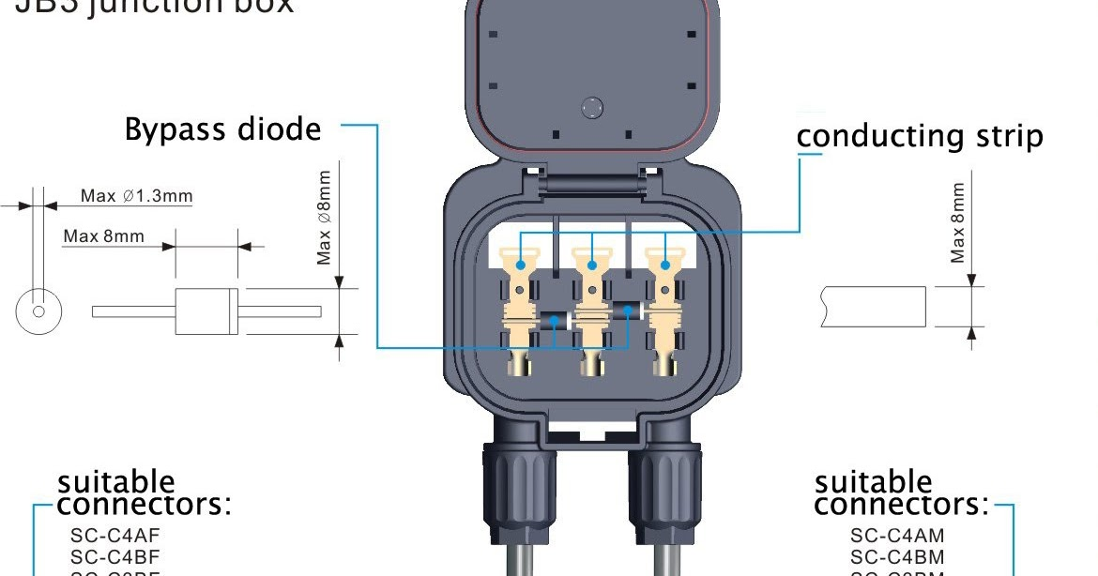
Illustrations/359658603_389.jpg
