MAQattan/My-Graduation-Project/Illustrations/1728963700492.jpg

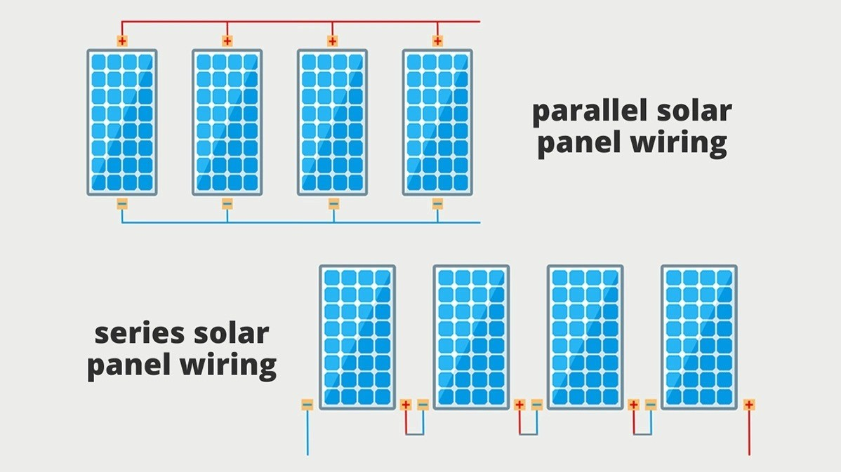
Illustrations/1728963700492.jpg
