MAQattan/My-Graduation-Project/Illustrations/articles-solar3.webp

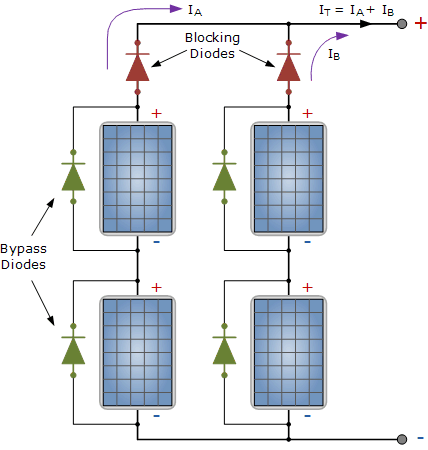
Illustrations/articles-solar3.webp
