MAQattan/My-Graduation-Project/Illustrations/Bifacial-Solar-Panels-1-1-scaled.jpg

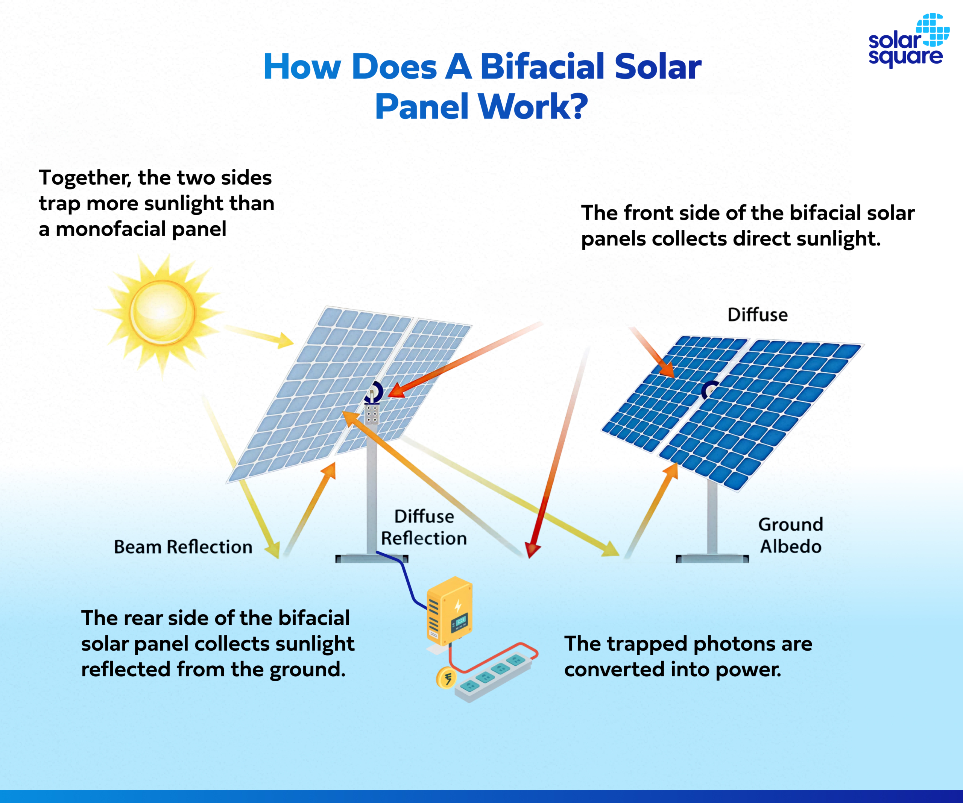
Illustrations/Bifacial-Solar-Panels-1-1-scaled.jpg
