MAQattan/My-Graduation-Project/Illustrations/en-1.png

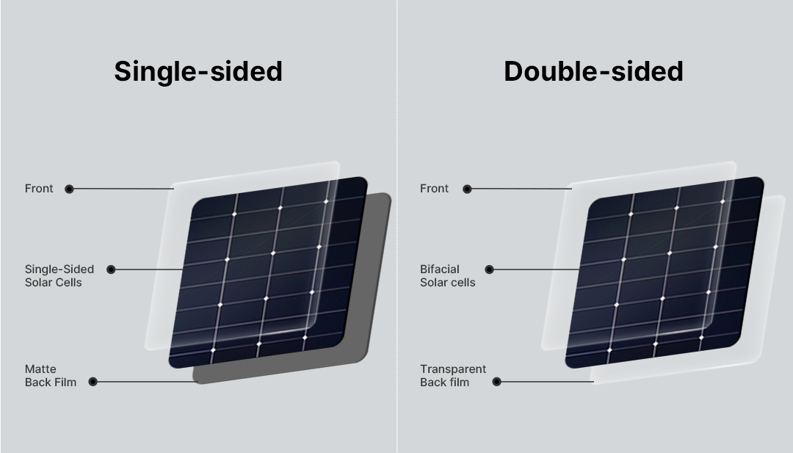
Illustrations/en-1.png
