MAQattan/My-Graduation-Project/Illustrations/From Gird-C. book/Screenshot 2026-03-26 142916.png

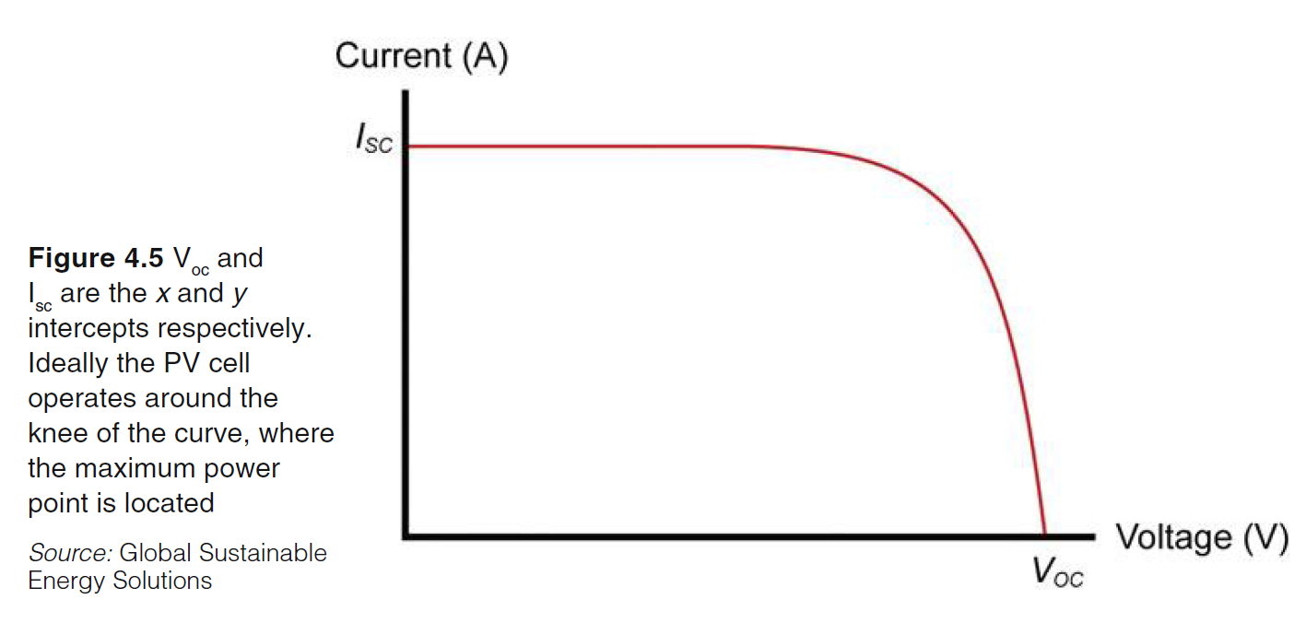
Illustrations/From Gird-C. book/Screenshot 2026-03-26 142916.png
