MAQattan/My-Graduation-Project/Illustrations/half-cut-solar-panels.png

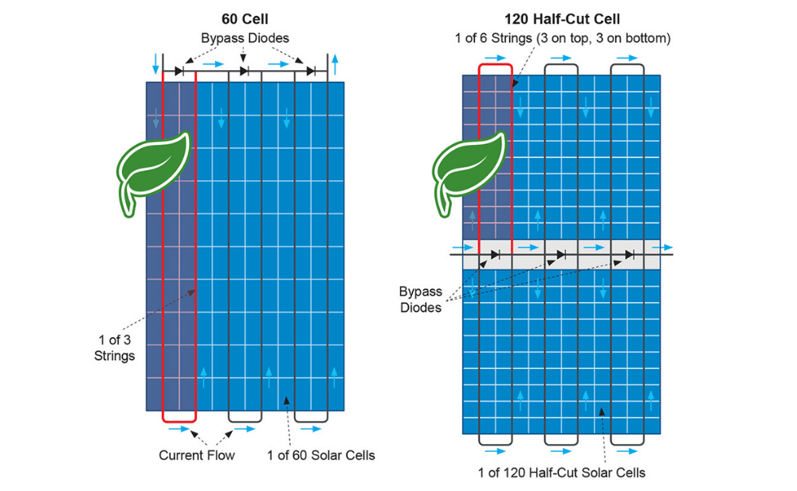
Illustrations/half-cut-solar-panels.png
