MAQattan/My-Graduation-Project/Illustrations/How Electricity Gets to You.png

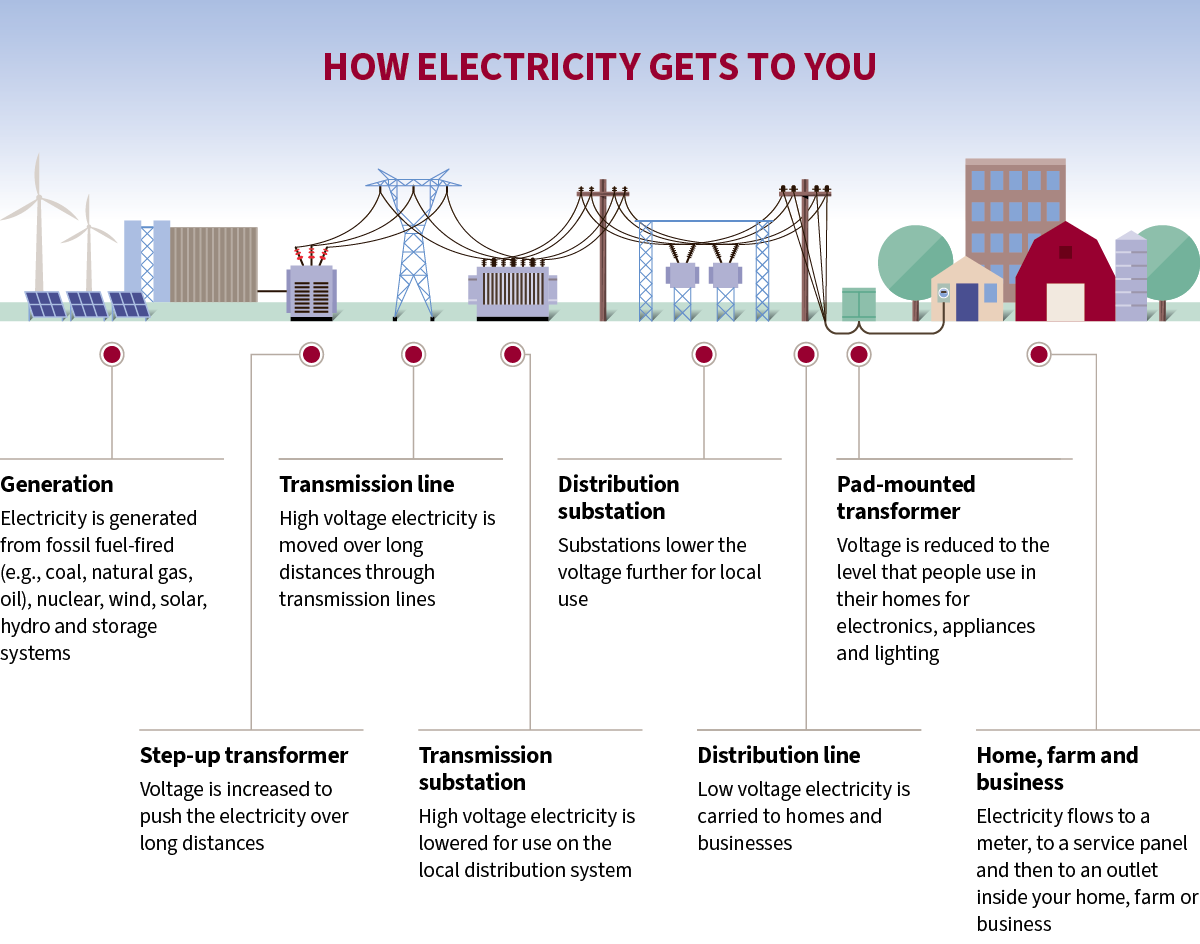
Illustrations/How Electricity Gets to You.png
