MAQattan/My-Graduation-Project/Illustrations/Latitude-and-Longitude.png

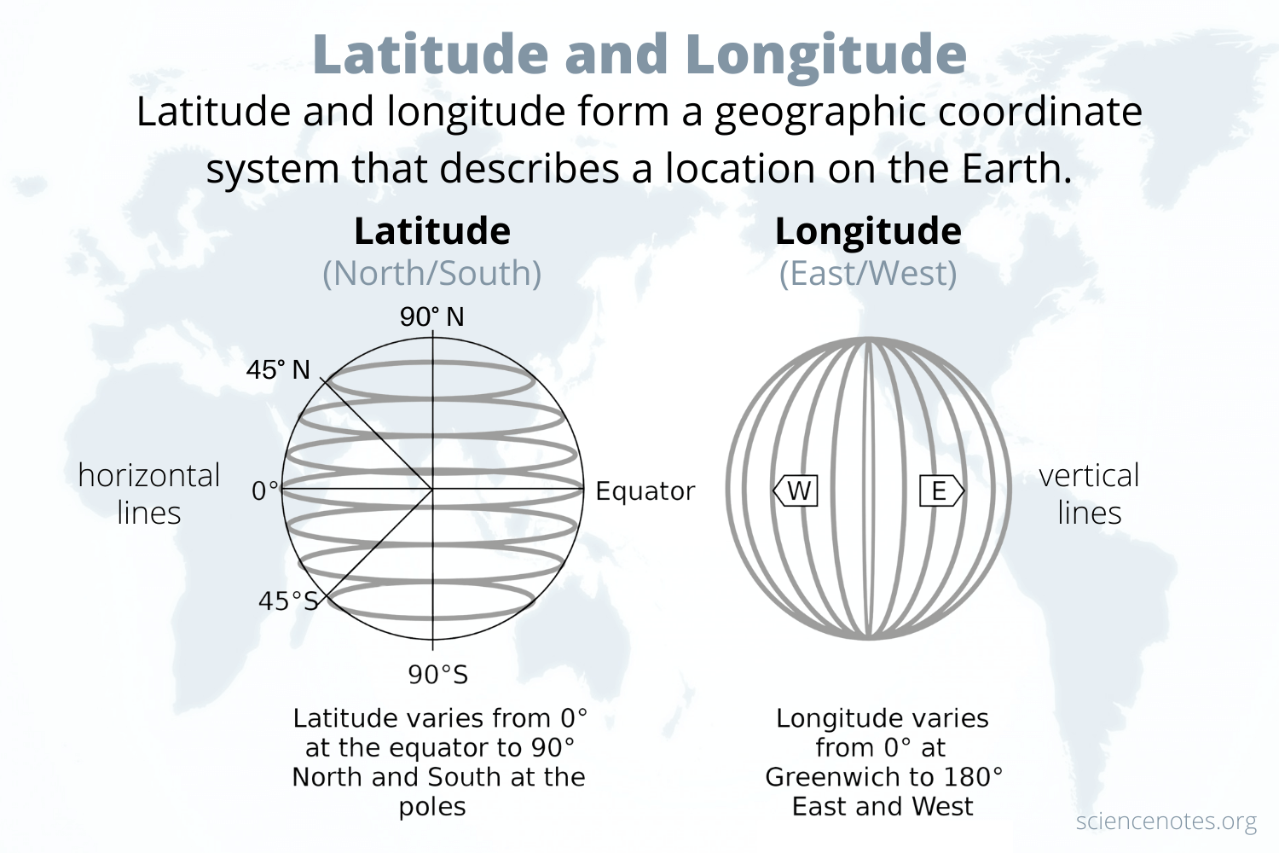
Illustrations/Latitude-and-Longitude.png
