MAQattan/My-Graduation-Project/Illustrations/parallel-series-connections-682e3a7539d08.png

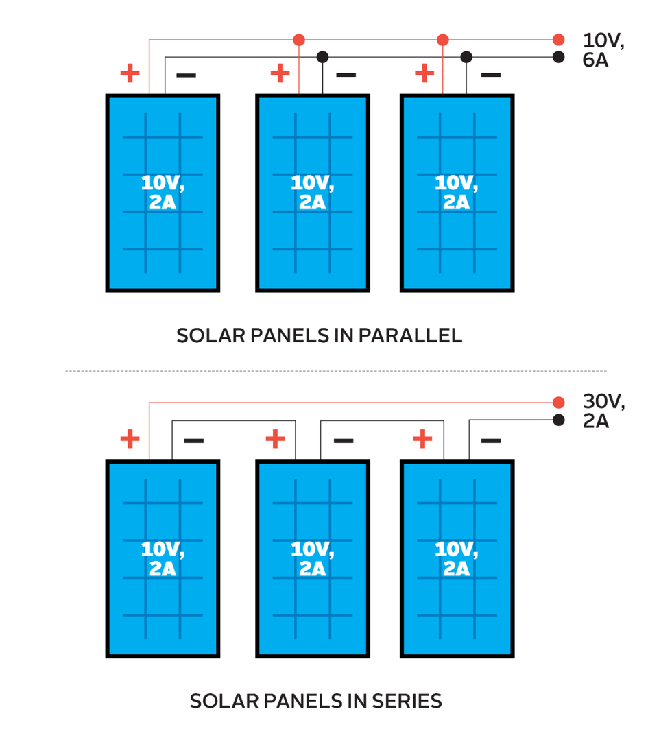
Illustrations/parallel-series-connections-682e3a7539d08.png
