MAQattan/My-Graduation-Project/Illustrations/Photovoltaic-Panels-3.jpg

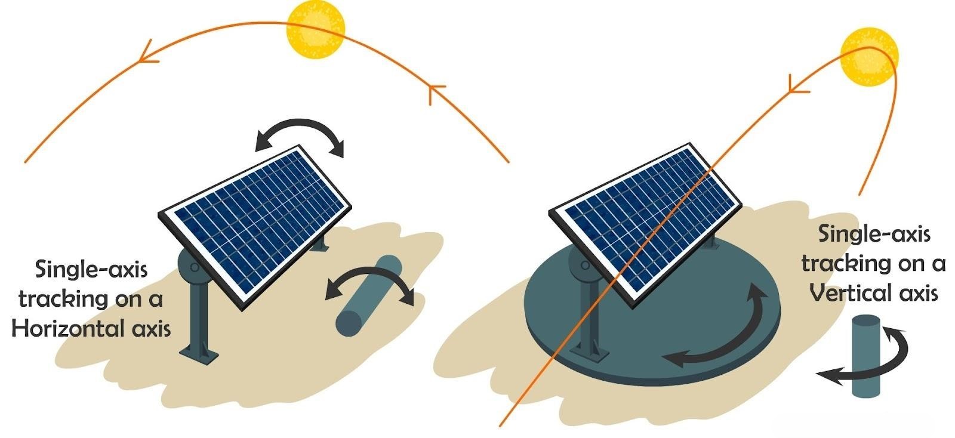
Illustrations/Photovoltaic-Panels-3.jpg
