MAQattan/My-Graduation-Project/Illustrations/Screenshot 2026-03-23 225106.png

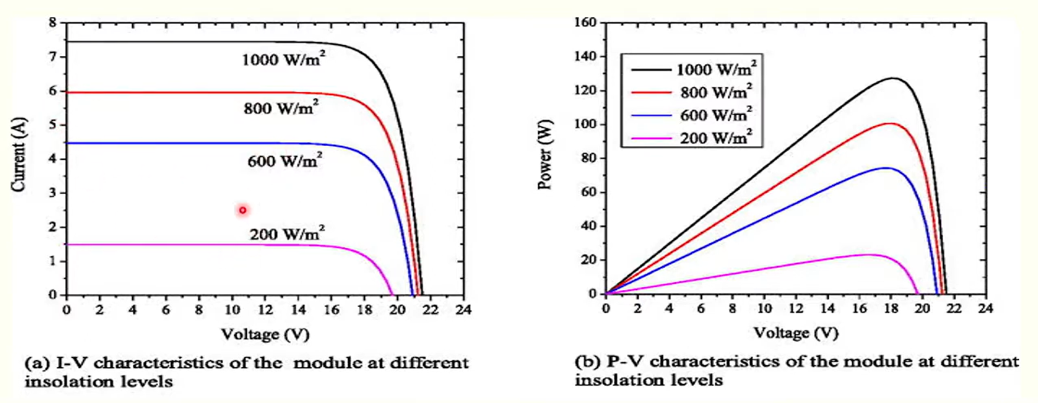
Illustrations/Screenshot 2026-03-23 225106.png
