MAQattan/My-Graduation-Project/Illustrations/Screenshot 2026-03-24 154752.png

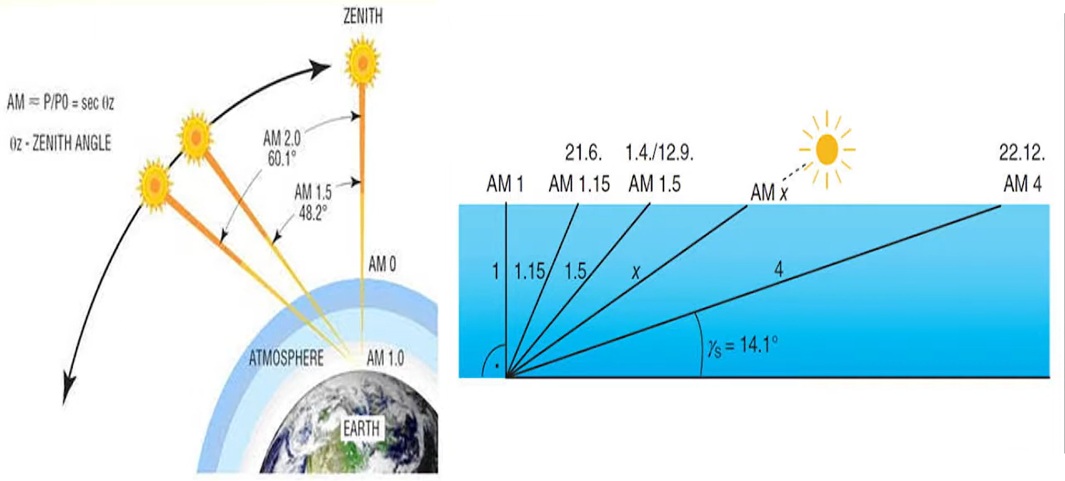
Illustrations/Screenshot 2026-03-24 154752.png
