MAQattan/My-Graduation-Project/Illustrations/Screenshot 2026-03-24 173450.png

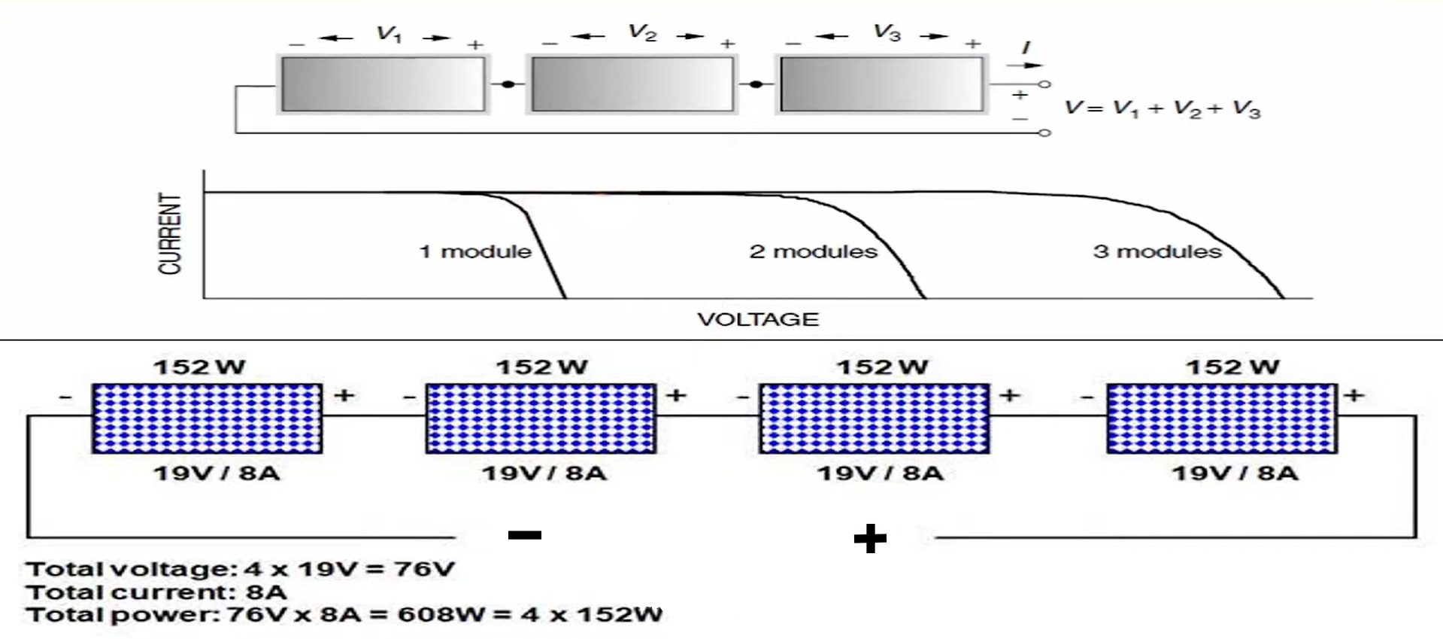
Illustrations/Screenshot 2026-03-24 173450.png
