MAQattan/My-Graduation-Project/Illustrations/Screenshot 2026-03-24 183942-copy .png

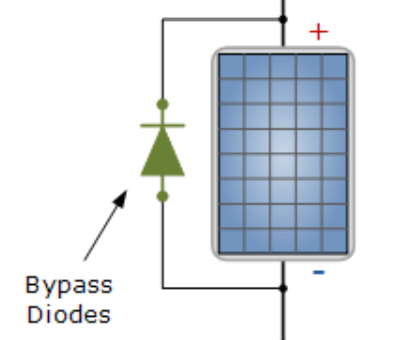
Illustrations/Screenshot 2026-03-24 183942-copy .png
