MAQattan/My-Graduation-Project/Illustrations/Screenshot 2026-03-24 183942.png

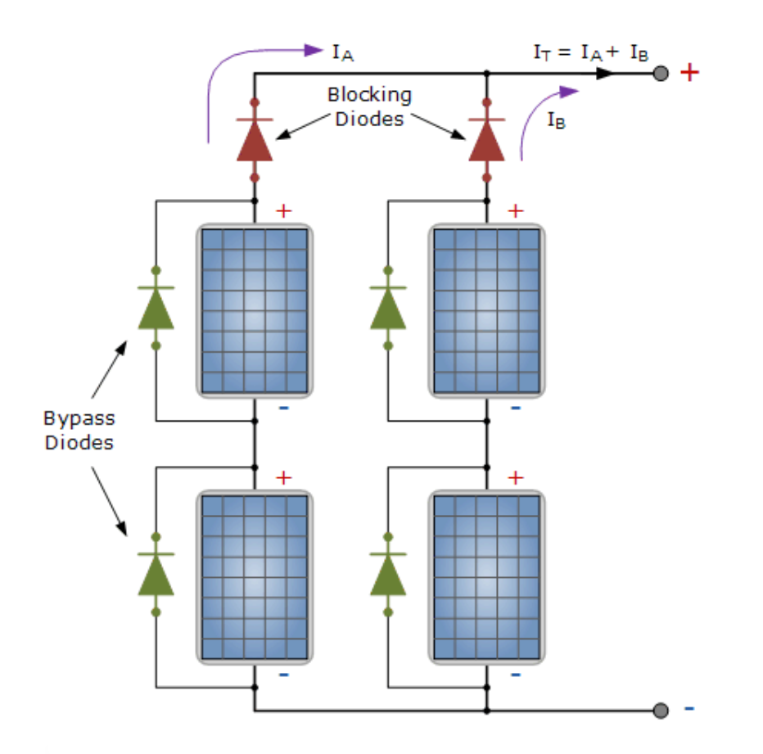
Illustrations/Screenshot 2026-03-24 183942.png
