MAQattan/My-Graduation-Project/Illustrations/Screenshot 2026-03-25 153131.png

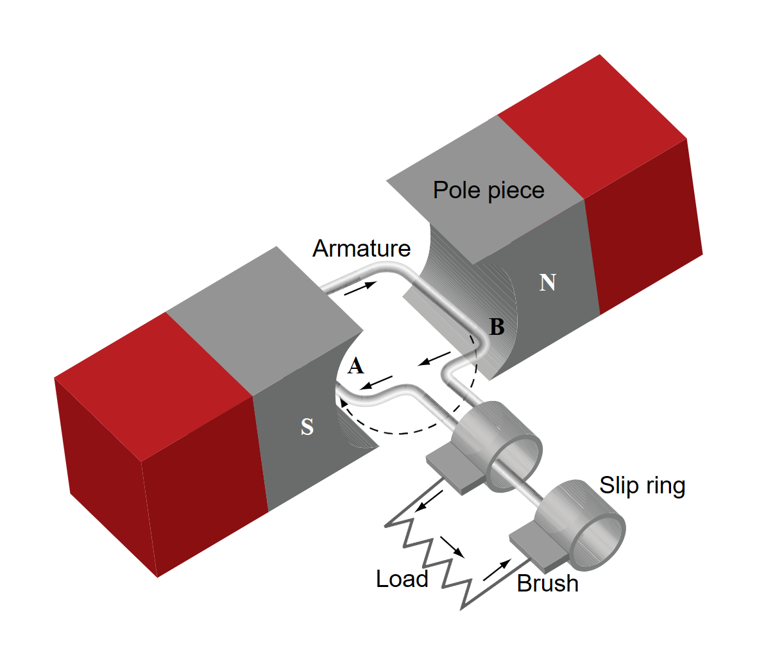
Illustrations/Screenshot 2026-03-25 153131.png
