MAQattan/My-Graduation-Project/Illustrations/Screenshot 2026-03-28 003433.png

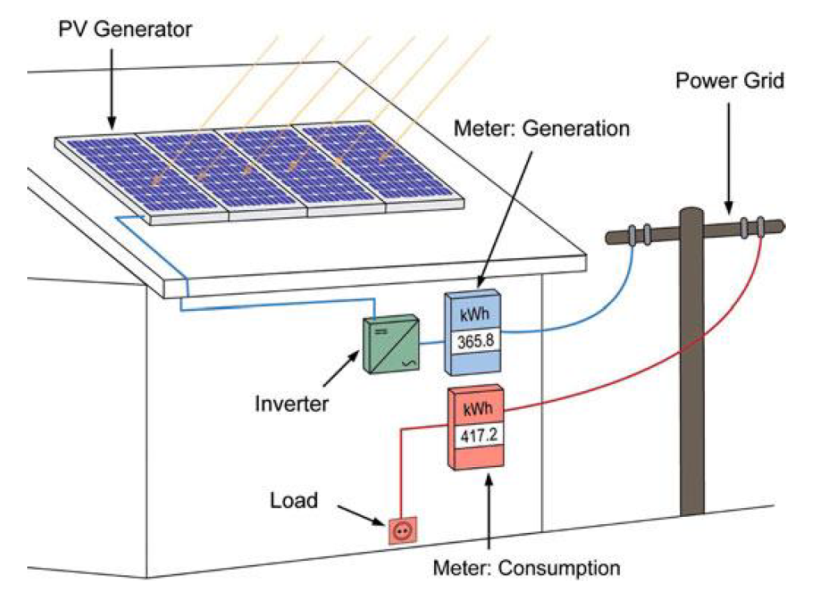
Illustrations/Screenshot 2026-03-28 003433.png
