MAQattan/My-Graduation-Project/Illustrations/seasons.jpg

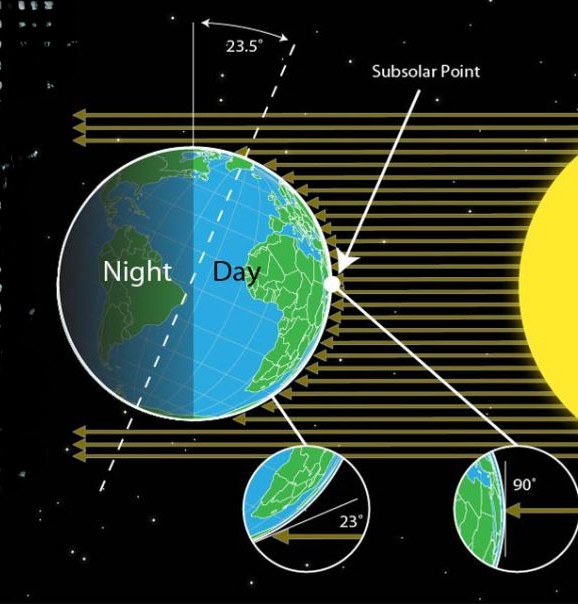
Illustrations/seasons.jpg
