MAQattan/My-Graduation-Project/Illustrations/Solar Panel Datasheet Part 3.jpg

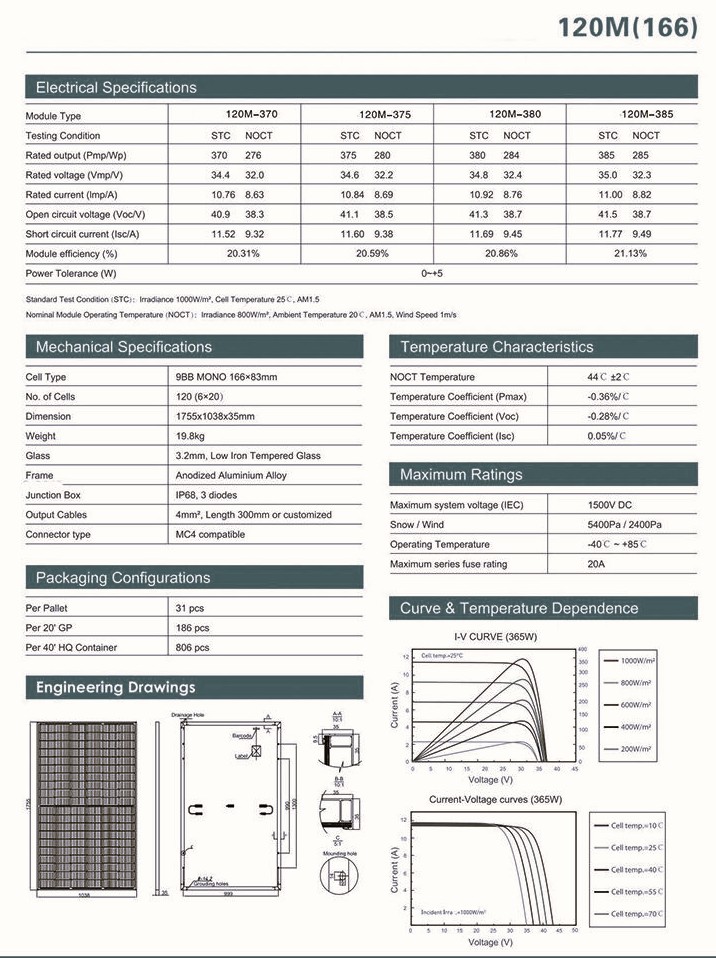
Illustrations/Solar Panel Datasheet Part 3.jpg
