MAQattan/My-Graduation-Project/Illustrations/solar-array.png

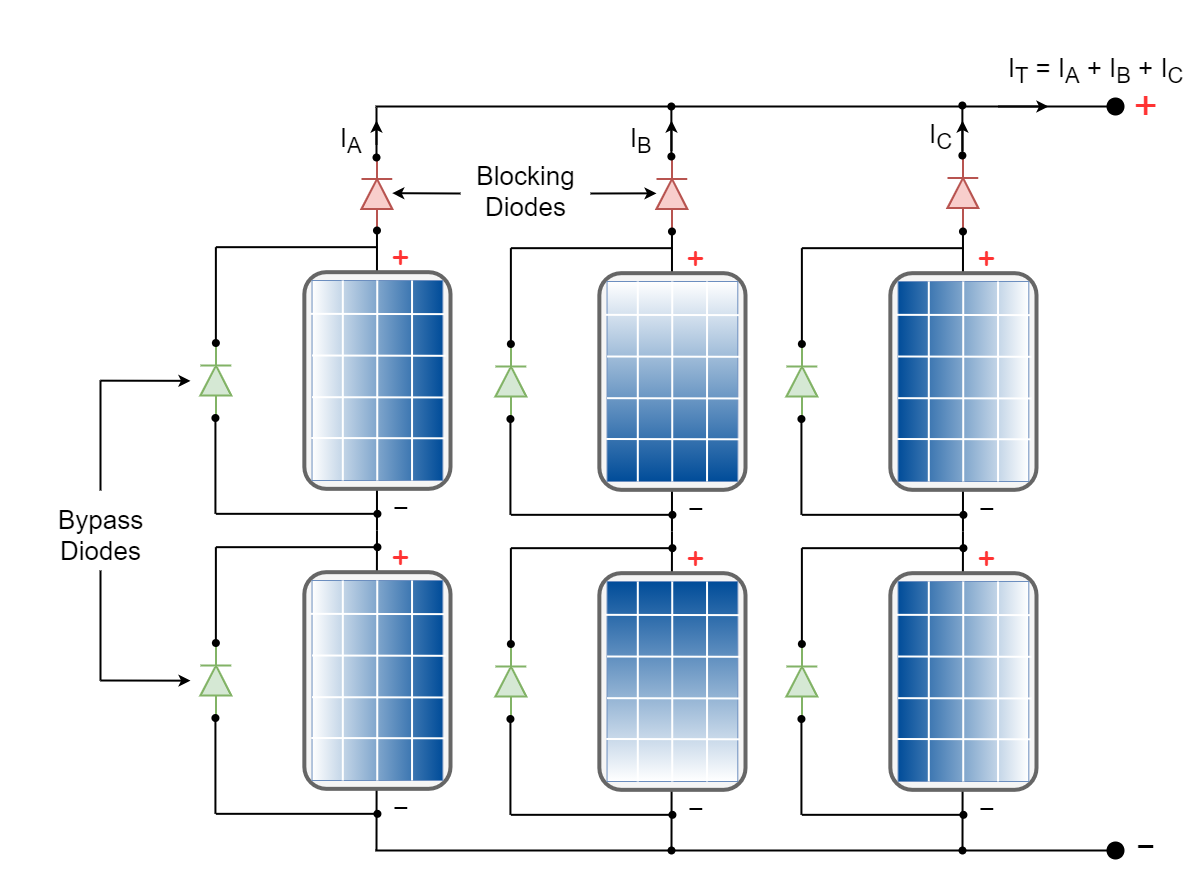
Illustrations/solar-array.png
