MAQattan/My-Graduation-Project/Illustrations/solar-panel-junction-box.jpg

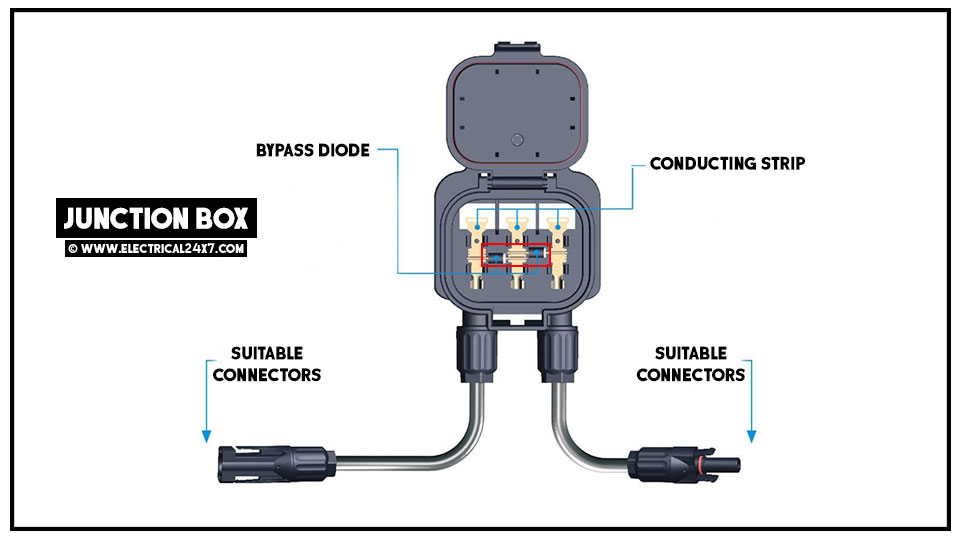
Illustrations/solar-panel-junction-box.jpg
