MAQattan/My-Graduation-Project/Illustrations/solar-panel-types-illustration.jpg

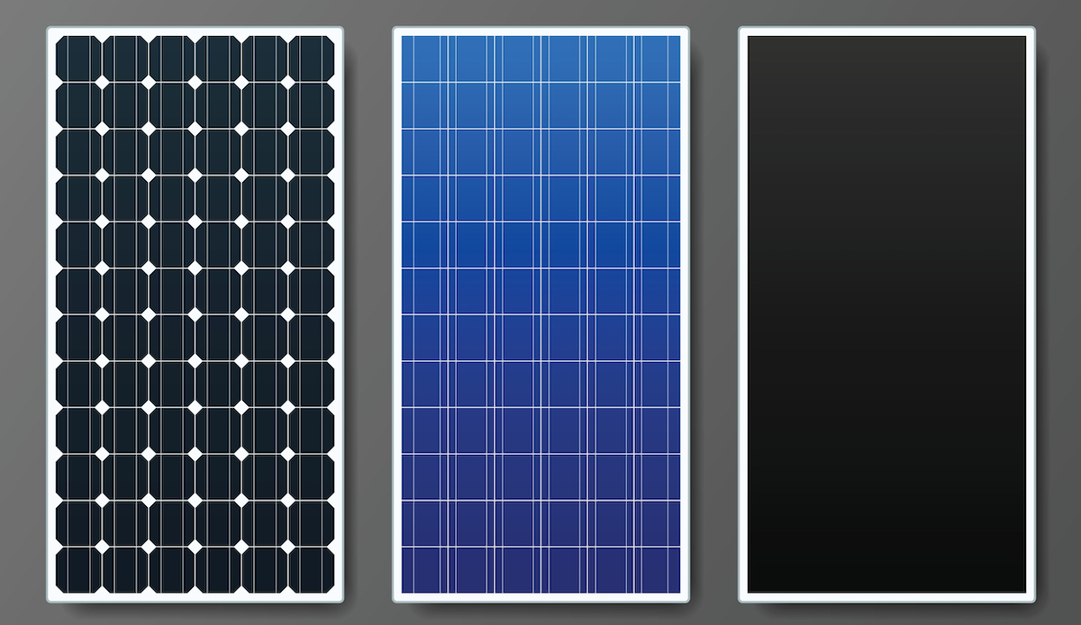
Illustrations/solar-panel-types-illustration.jpg
