MAQattan/My-Graduation-Project/Illustrations/solar-panels.jpg

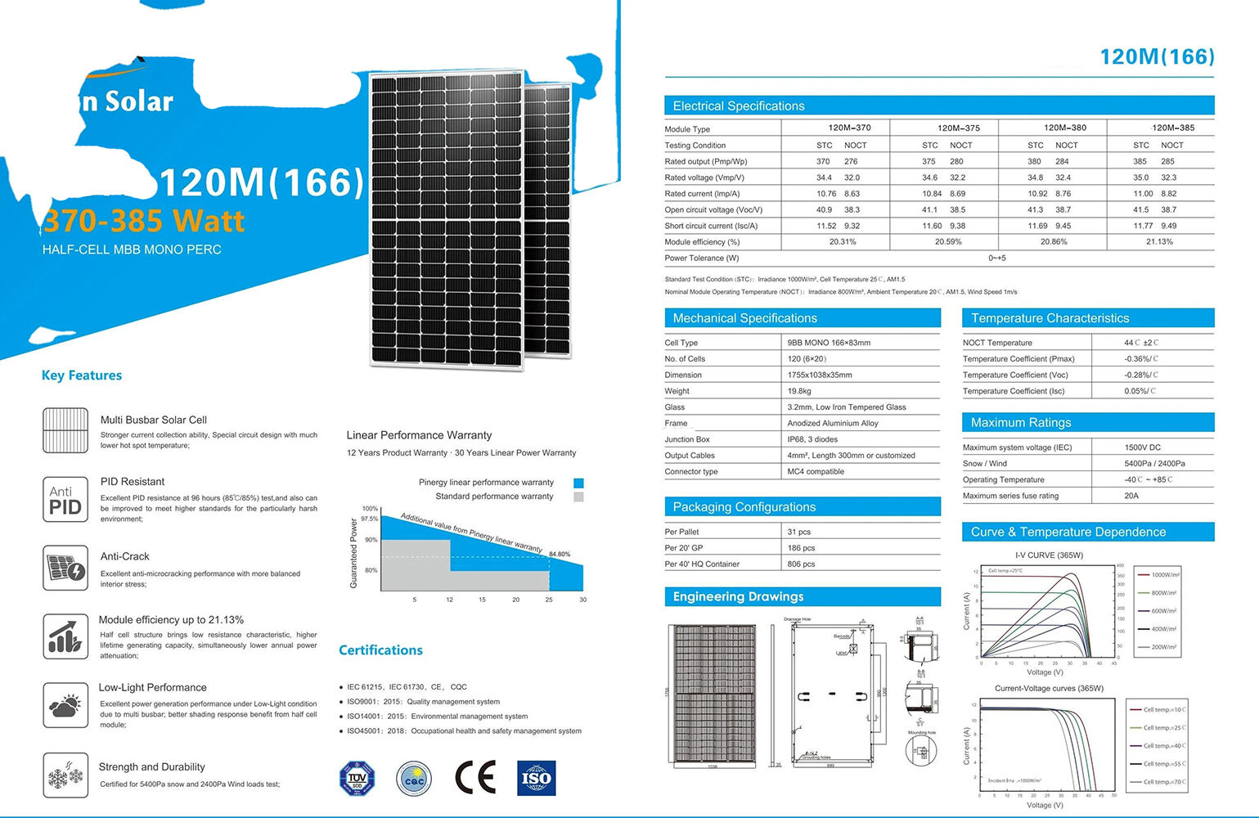
Illustrations/solar-panels.jpg
