MAQattan/My-Graduation-Project/Illustrations/solar_csp_image_combined-656x1024.png

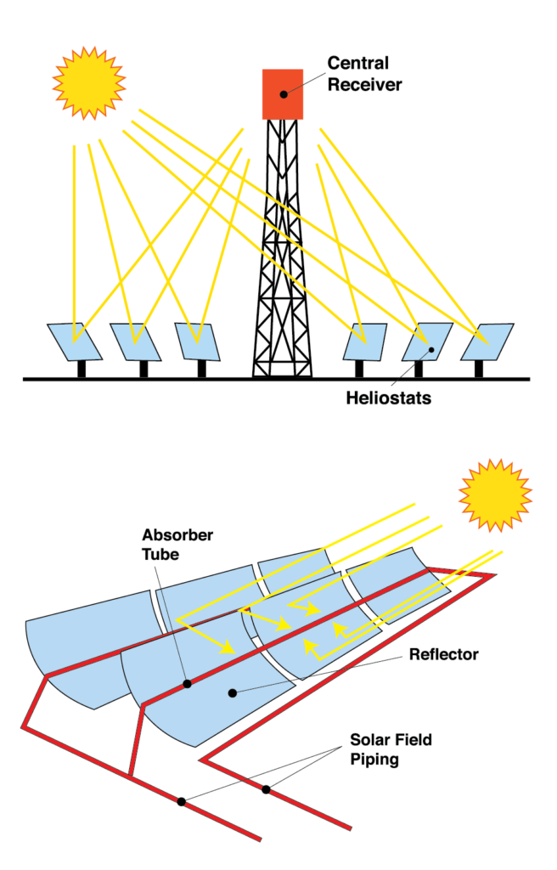
Illustrations/solar_csp_image_combined-656x1024.png
