MAQattan/My-Graduation-Project/Illustrations/split-cell-junction-boxes.jpeg

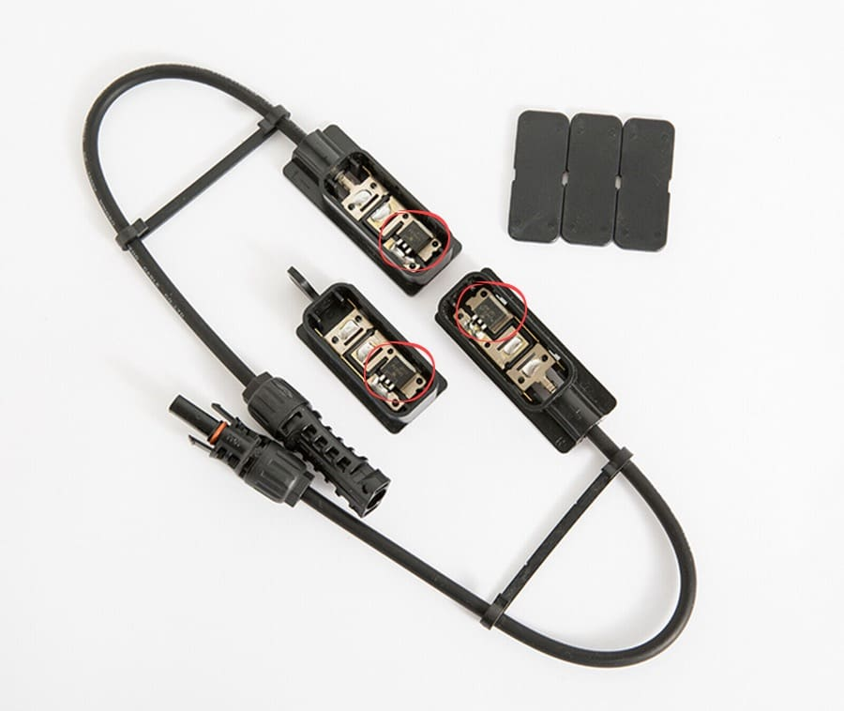
Illustrations/split-cell-junction-boxes.jpeg
