MAQattan/My-Graduation-Project/Illustrations/Square-Sine-and-Modified-sine-wave-Inverter-Output-Waveform_0.png

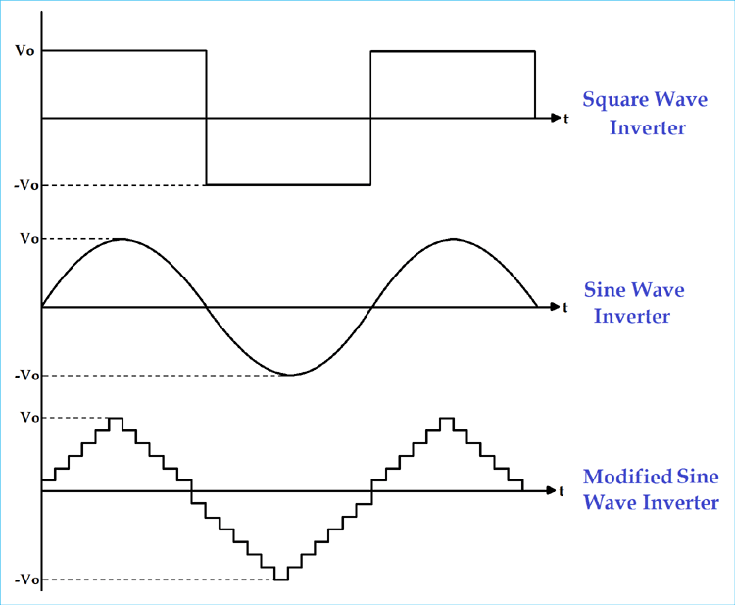
Illustrations/Square-Sine-and-Modified-sine-wave-Inverter-Output-Waveform_0.png
