MAQattan/My-Graduation-Project/Illustrations/SunPathThroughYear_RV_092622 REV (002).jpg

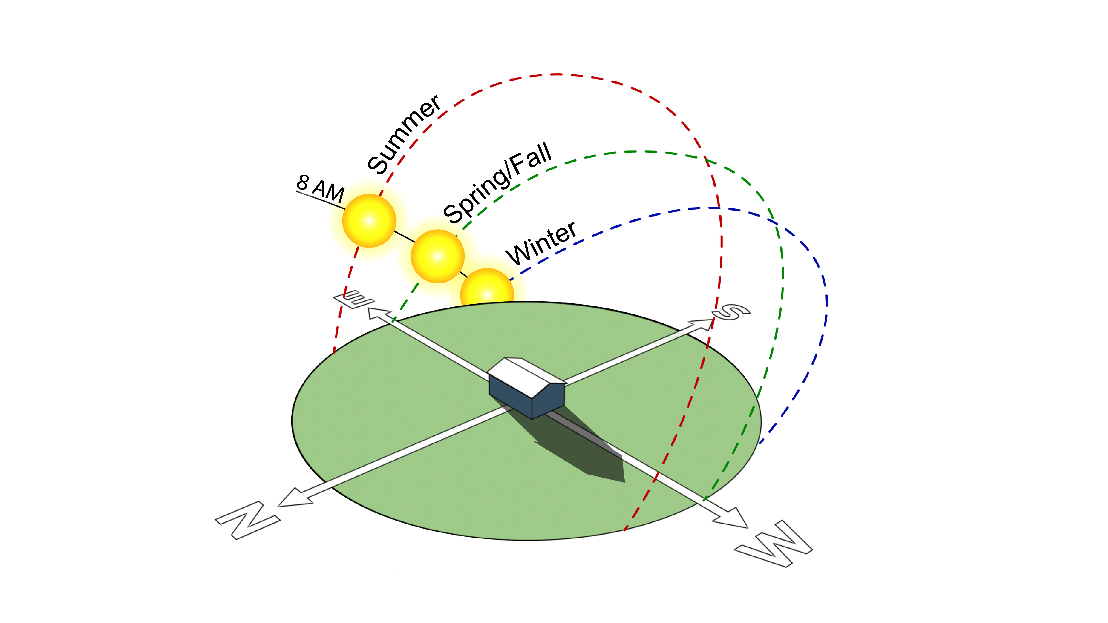
Illustrations/SunPathThroughYear_RV_092622 REV (002).jpg
