MAQattan/My-Graduation-Project/Illustrations/tilt-angle.png

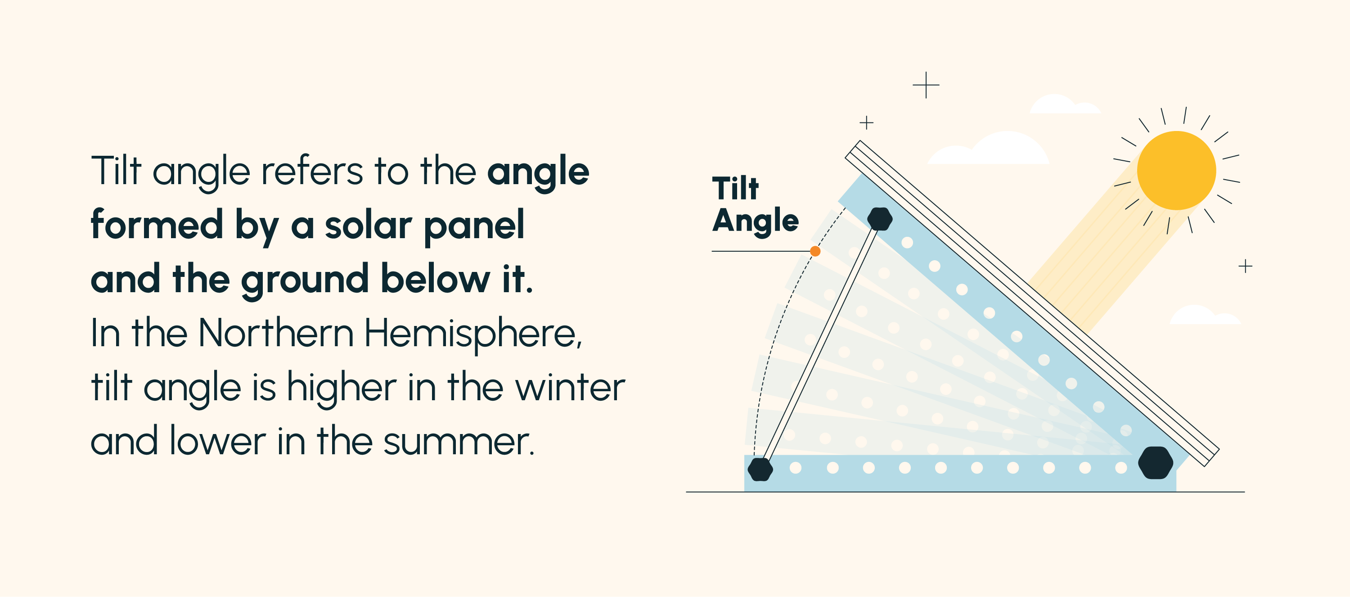
Illustrations/tilt-angle.png
