MAQattan/My-Graduation-Project/Illustrations/لوحة-الطاقة-الشمسية.png

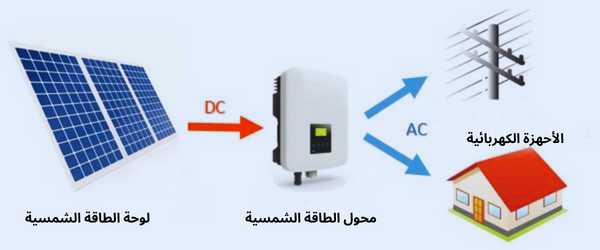
Illustrations/لوحة-الطاقة-الشمسية.png
