MAQattan/My-Graduation-Project/Illustrations/نظام-طاقة-كهروضوئي-متصل-بالشبكة-1024x819.jpg

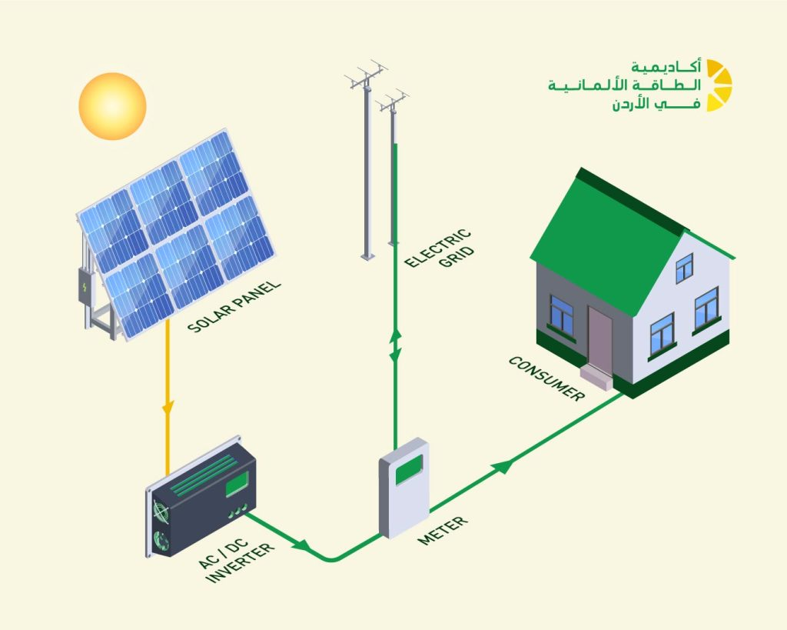
Illustrations/نظام-طاقة-كهروضوئي-متصل-بالشبكة-1024x819.jpg
