MAQattan/My-Graduation-Project/Illustrations/博文配图-8-1-1024x576.jpg

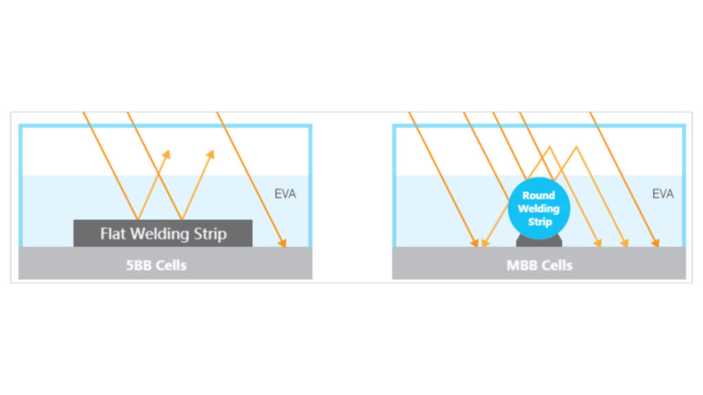
Illustrations/博文配图-8-1-1024x576.jpg
