MAQattan/My-Graduation-Project/Presentation_Typst/Figures/PV-10-00.webp

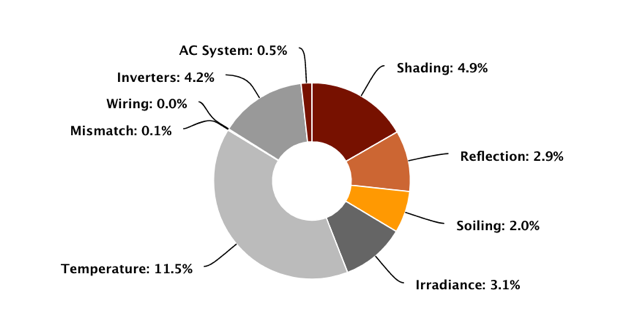
Presentation_Typst/Figures/PV-10-00.webp
