MAQattan/My-Graduation-Project/Presentation_Typst/Figures/PV-10-01.png

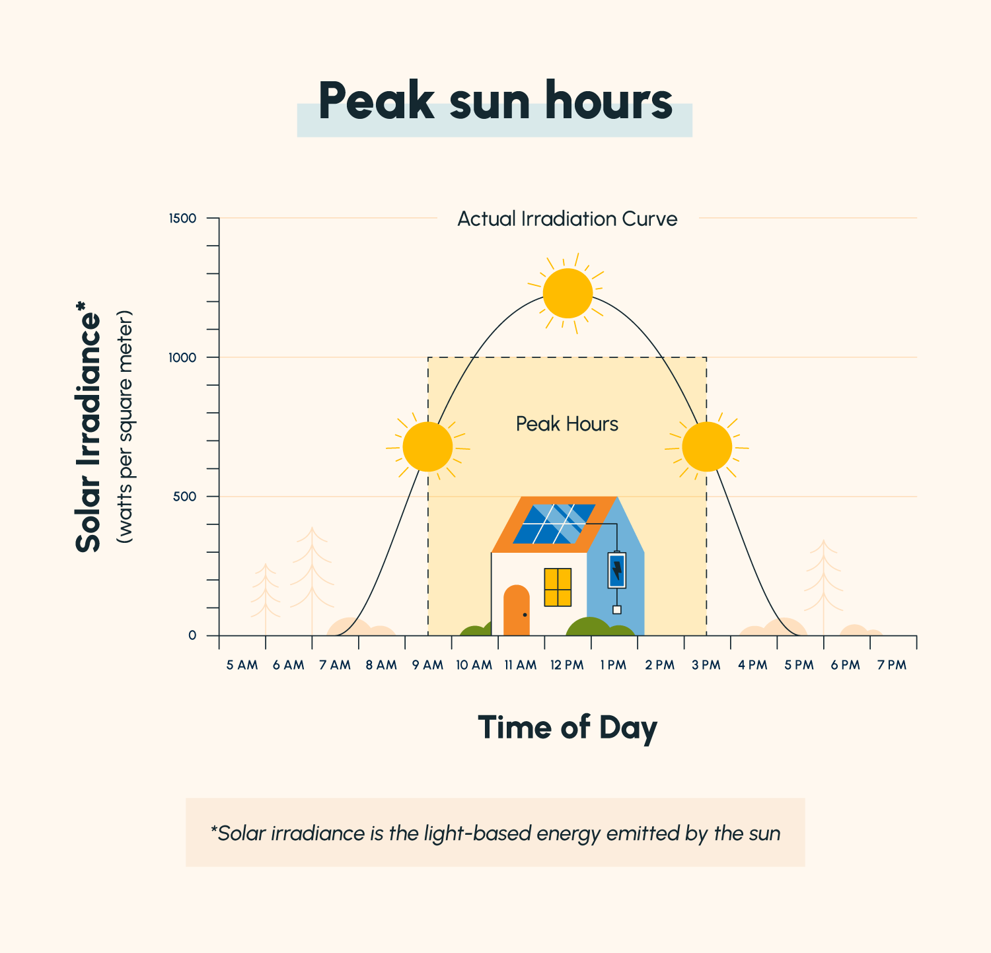
Presentation_Typst/Figures/PV-10-01.png
