MAQattan/My-Graduation-Project/Presentation_Typst/Figures/PV-10-02.png

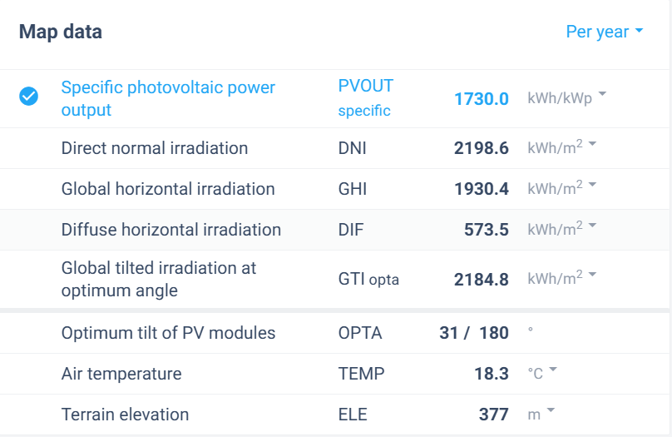
Presentation_Typst/Figures/PV-10-02.png
