MAQattan/My-Graduation-Project/Presentation_Typst/Figures/PV-10-03.jpg

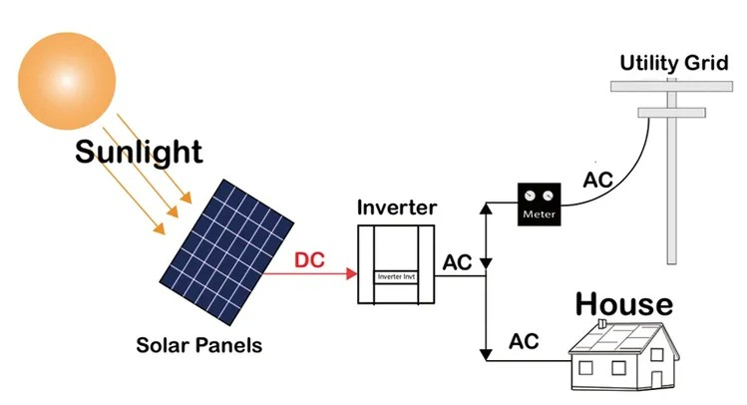
Presentation_Typst/Figures/PV-10-03.jpg
