MAQattan/My-Graduation-Project/Presentation_Typst/Figures/PV-10-06.png

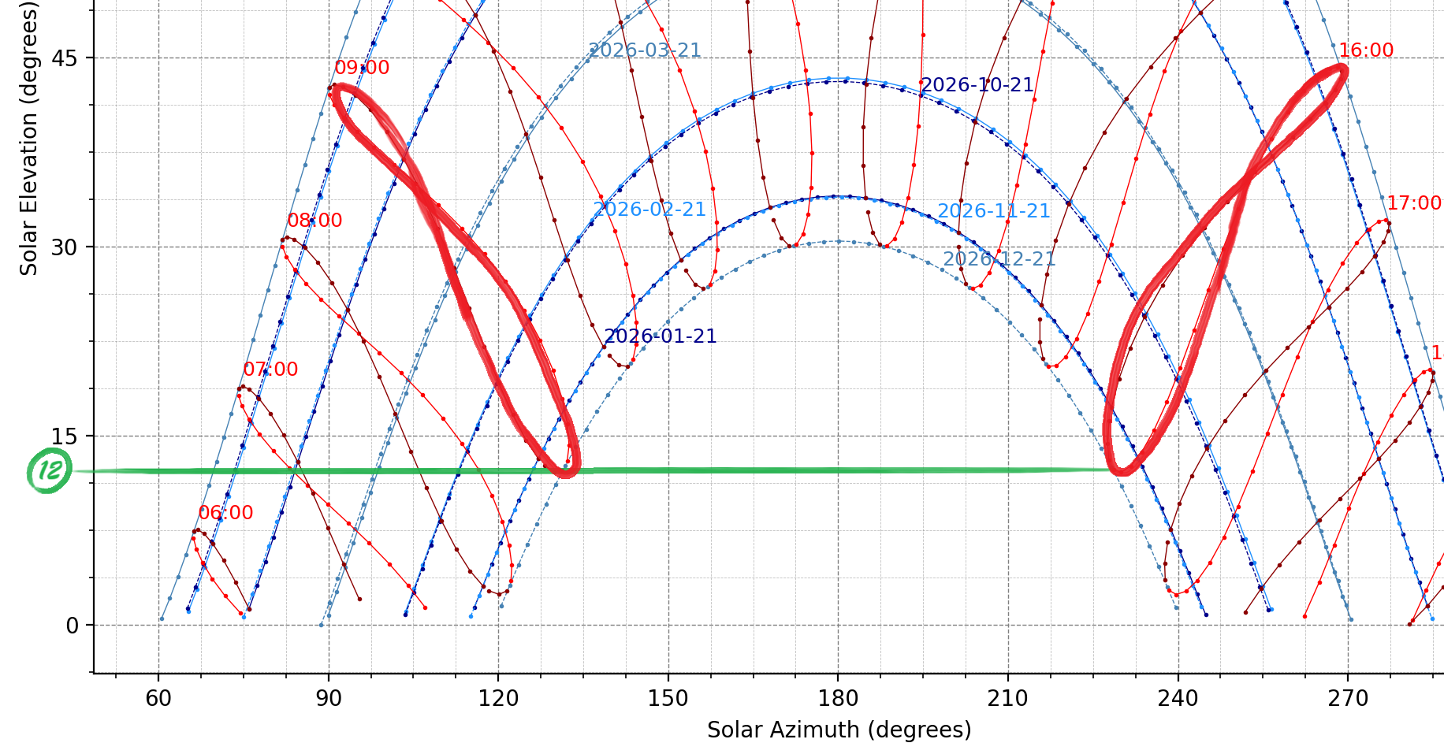
Presentation_Typst/Figures/PV-10-06.png
