MAQattan/My-Graduation-Project/Presentation_Typst/Figures/PV-10-07.png

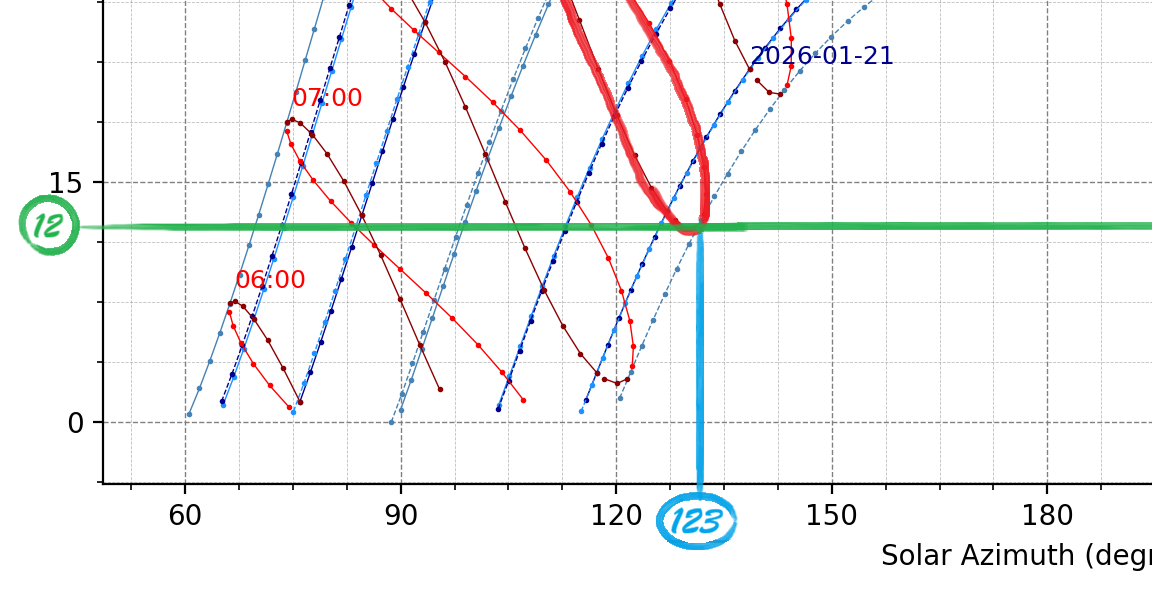
Presentation_Typst/Figures/PV-10-07.png
