MAQattan/My-Graduation-Project/Presentation_Typst/Figures/PV-10-09.png

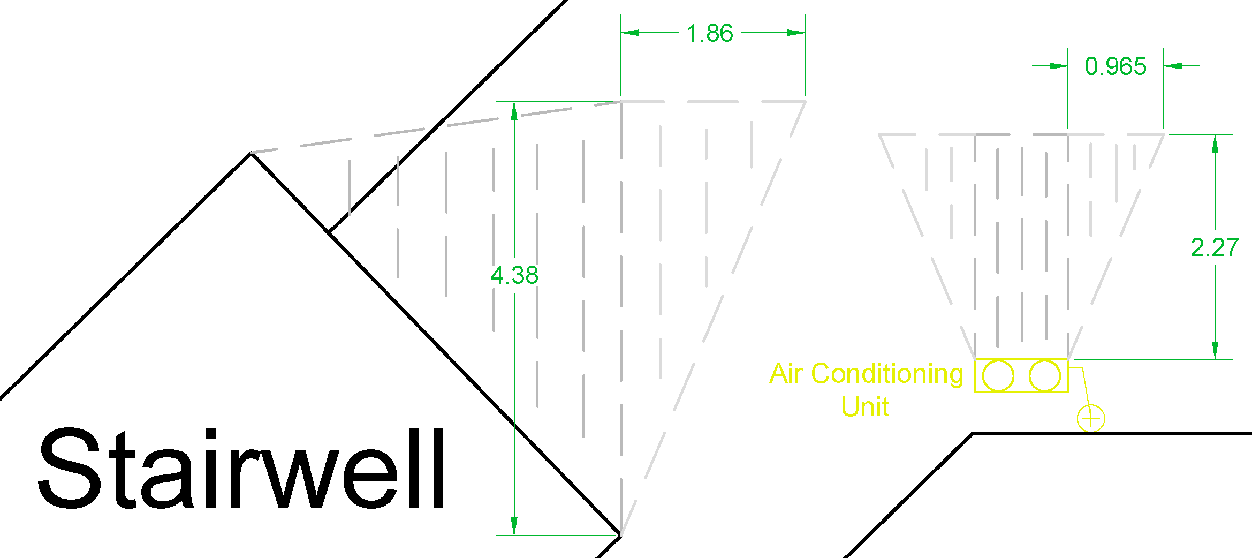
Presentation_Typst/Figures/PV-10-09.png
