MAQattan/My-Graduation-Project/Presentation_Typst/Figures/PV-10-12.png

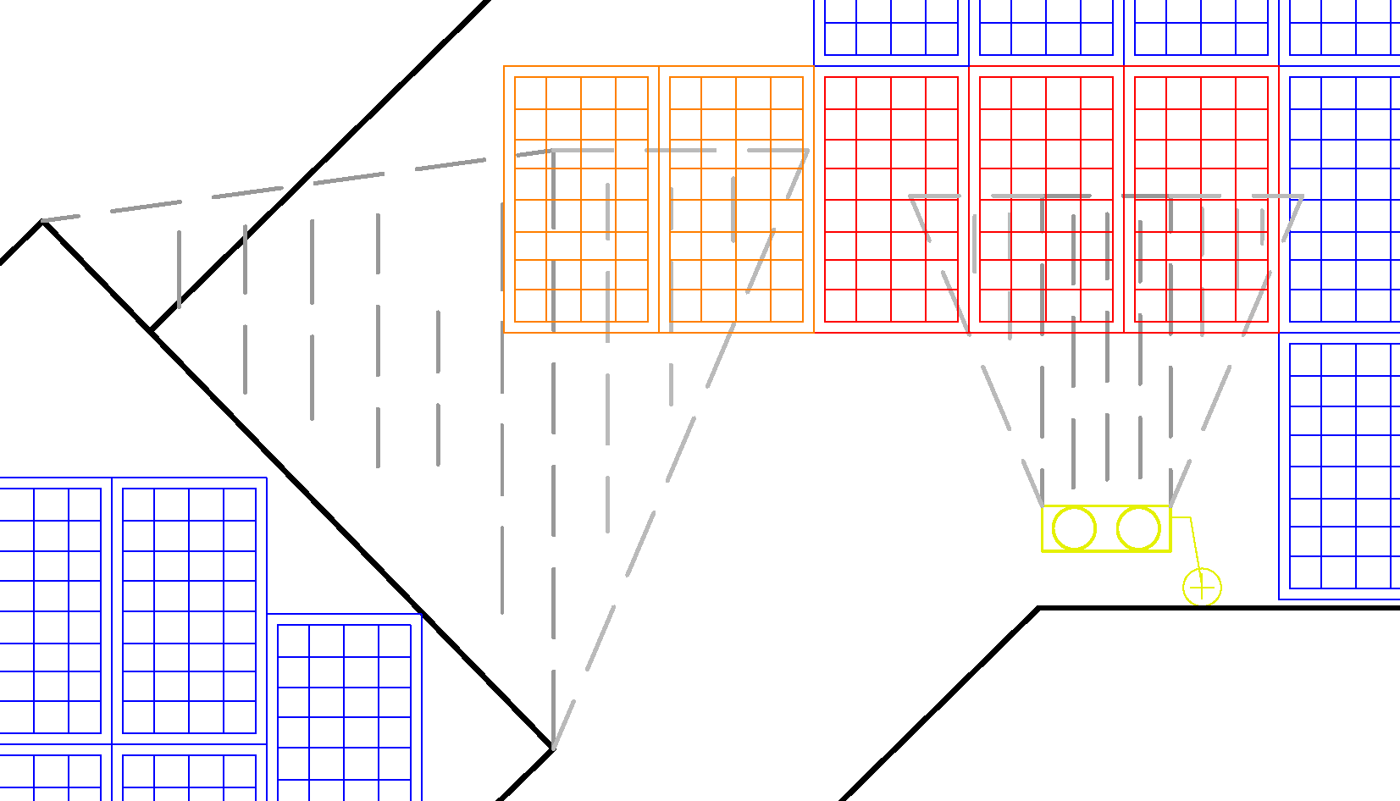
Presentation_Typst/Figures/PV-10-12.png
