MAQattan/My-Graduation-Project/Presentation_Typst/Figures/PV-10-13.png

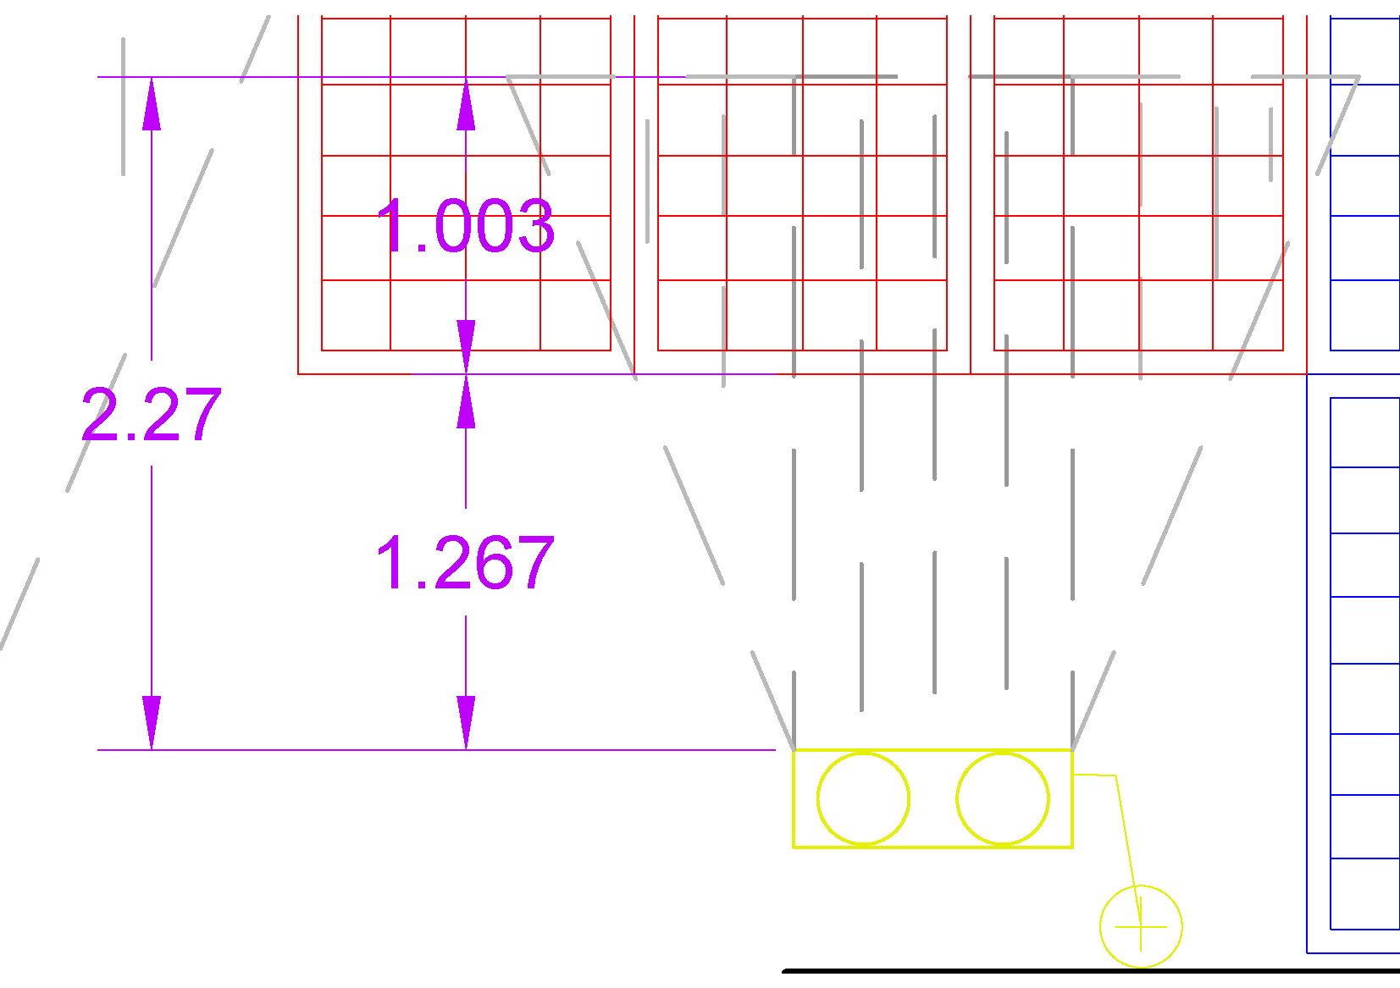
Presentation_Typst/Figures/PV-10-13.png
