MAQattan/My-Graduation-Project/Presentation_Typst/Figures/PV-10-14.png

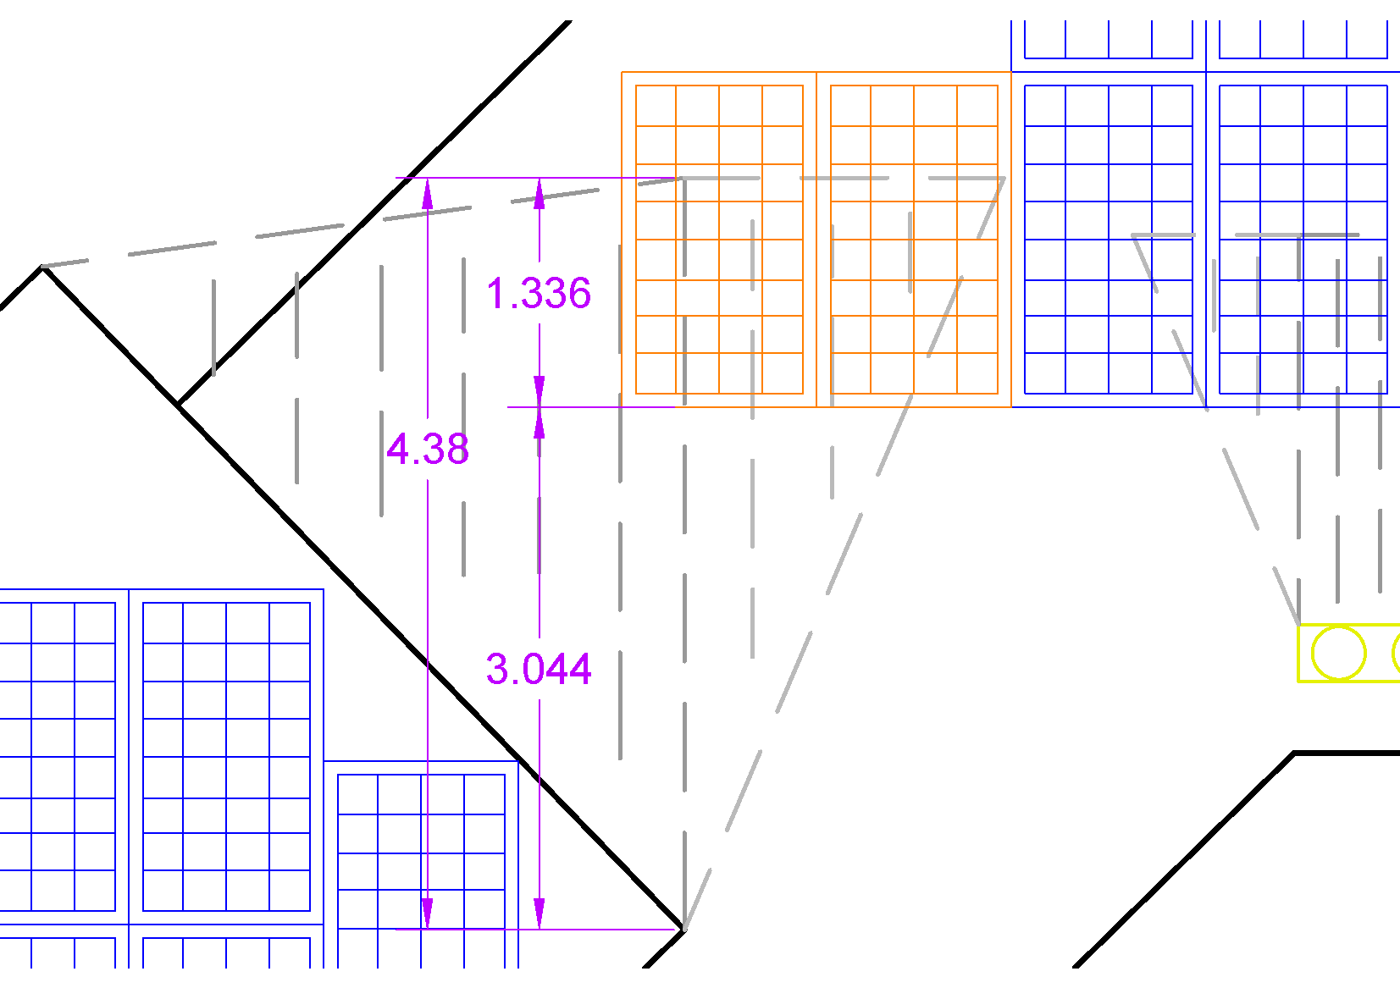
Presentation_Typst/Figures/PV-10-14.png
