MAQattan/My-Graduation-Project/Presentation_Typst/Figures/PV-10-15.png

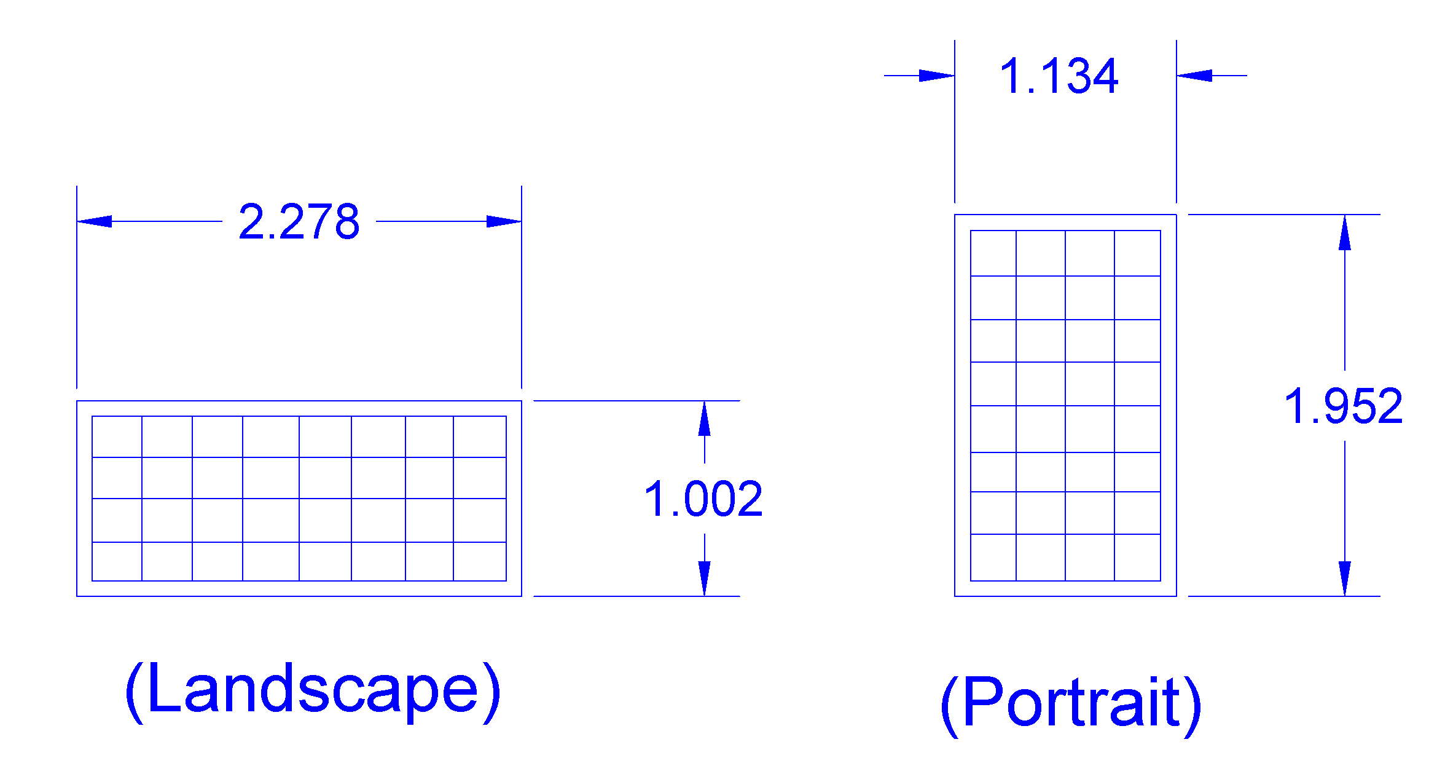
Presentation_Typst/Figures/PV-10-15.png
