MAQattan/My-Graduation-Project/Presentation_Typst/Figures/PV-10-16.png

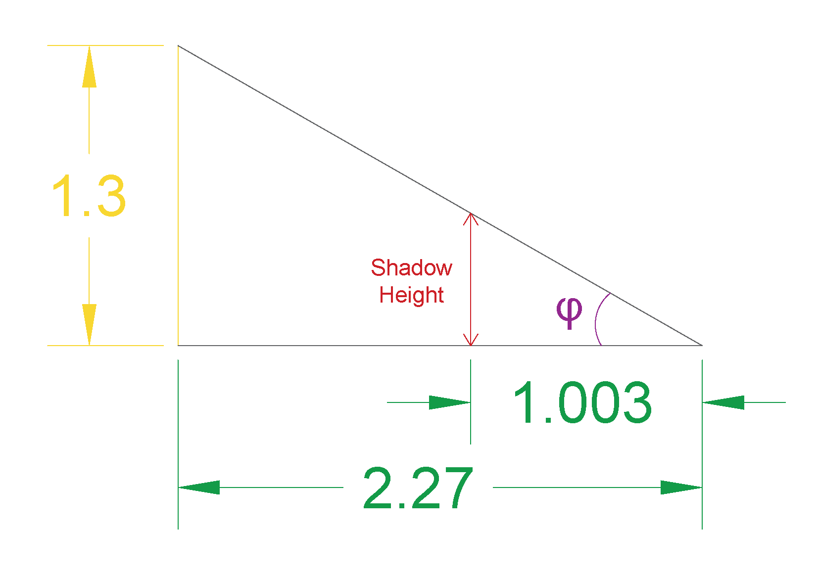
Presentation_Typst/Figures/PV-10-16.png
