MAQattan/My-Graduation-Project/Presentation_Typst/Figures/PV-10-17.png

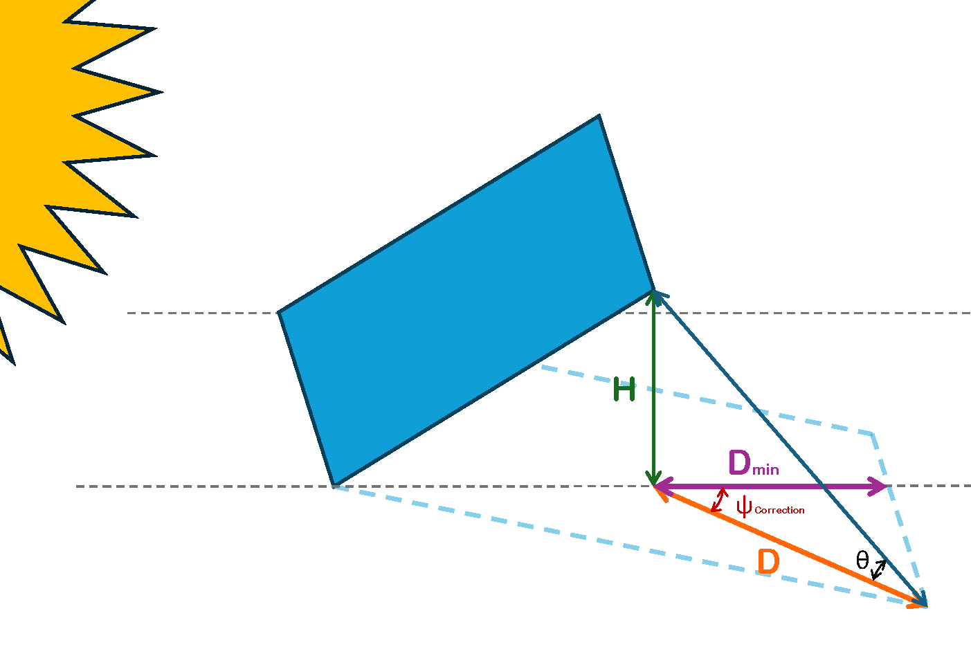
Presentation_Typst/Figures/PV-10-17.png
