MAQattan/My-Graduation-Project/Presentation_Typst/Figures/PV-10-20.png

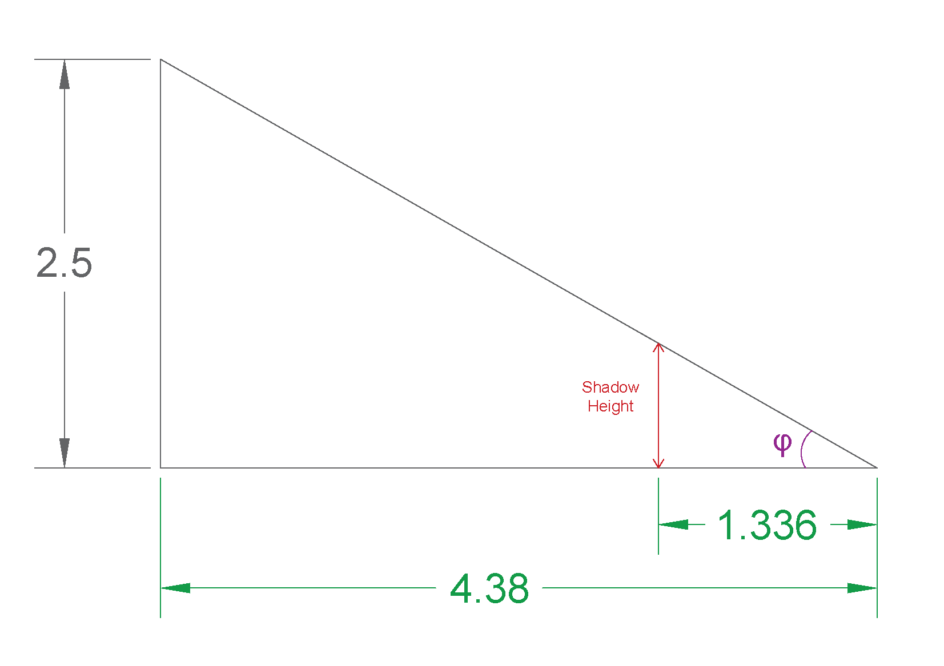
Presentation_Typst/Figures/PV-10-20.png
