MAQattan/My-Graduation-Project/Presentation_Typst/Figures/PV-10-21.png

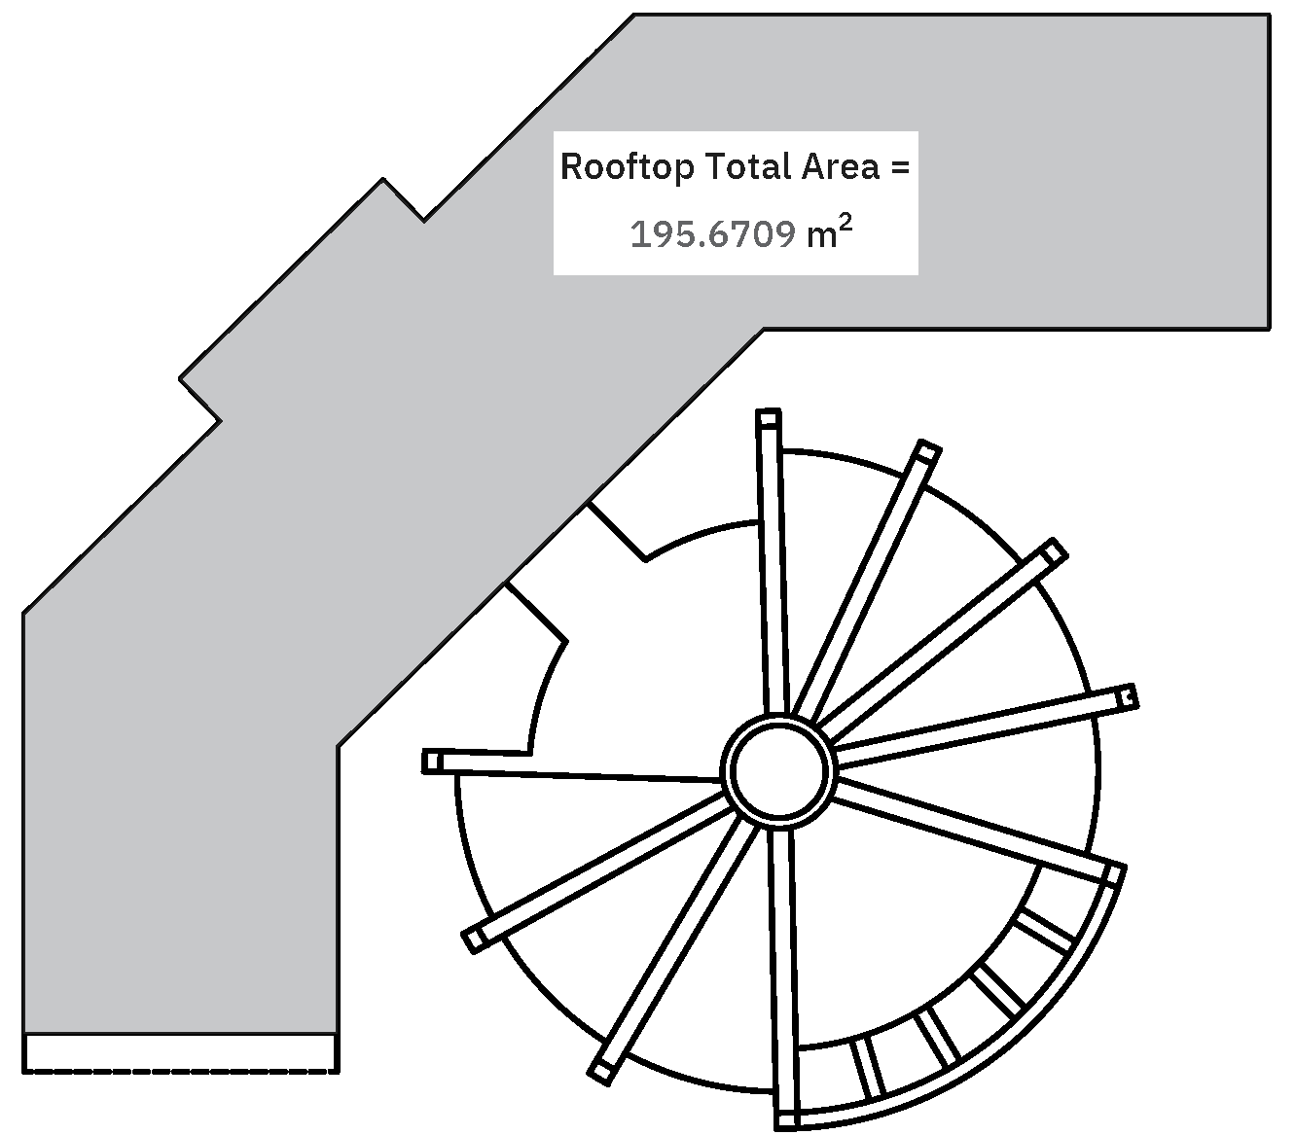
Presentation_Typst/Figures/PV-10-21.png
