MAQattan/My-Graduation-Project/Presentation_Typst/Figures/PV-10-22.jpg

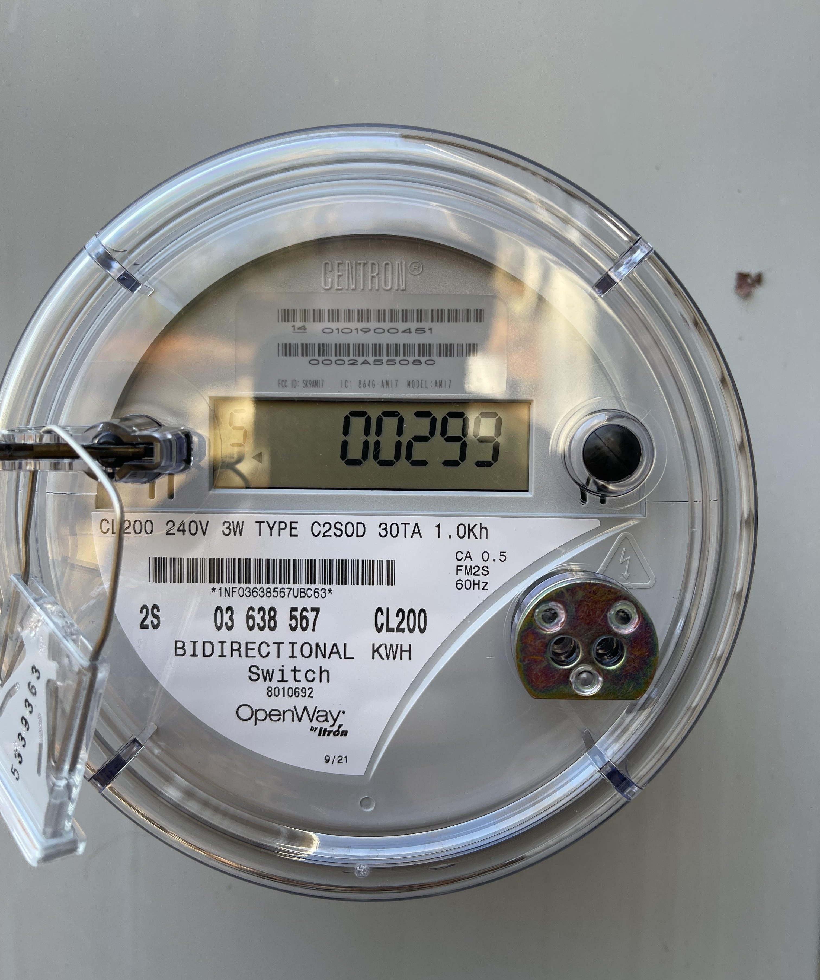
Presentation_Typst/Figures/PV-10-22.jpg
