MAQattan/My-Graduation-Project/Presentation_Typst/Figures/PV-10-23.jpg

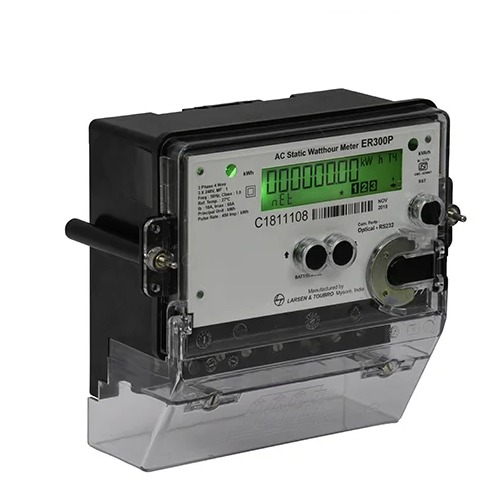
Presentation_Typst/Figures/PV-10-23.jpg
