MAQattan/My-Graduation-Project/Presentation_Typst/Figures/PV-10-24.jpg

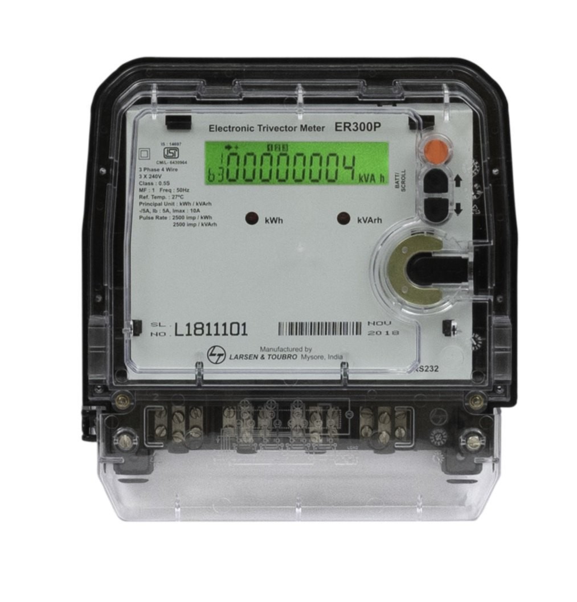
Presentation_Typst/Figures/PV-10-24.jpg
