MAQattan/My-Graduation-Project/Presentation_Typst/Figures/PV-10-25.jpg

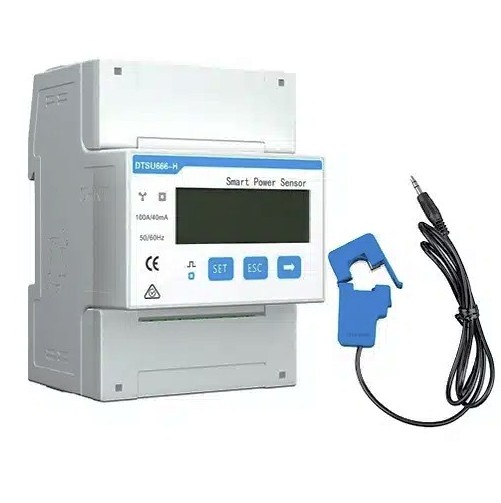
Presentation_Typst/Figures/PV-10-25.jpg
