MAQattan/My-Graduation-Project/Presentation_Typst/Figures/PV-11-01.png

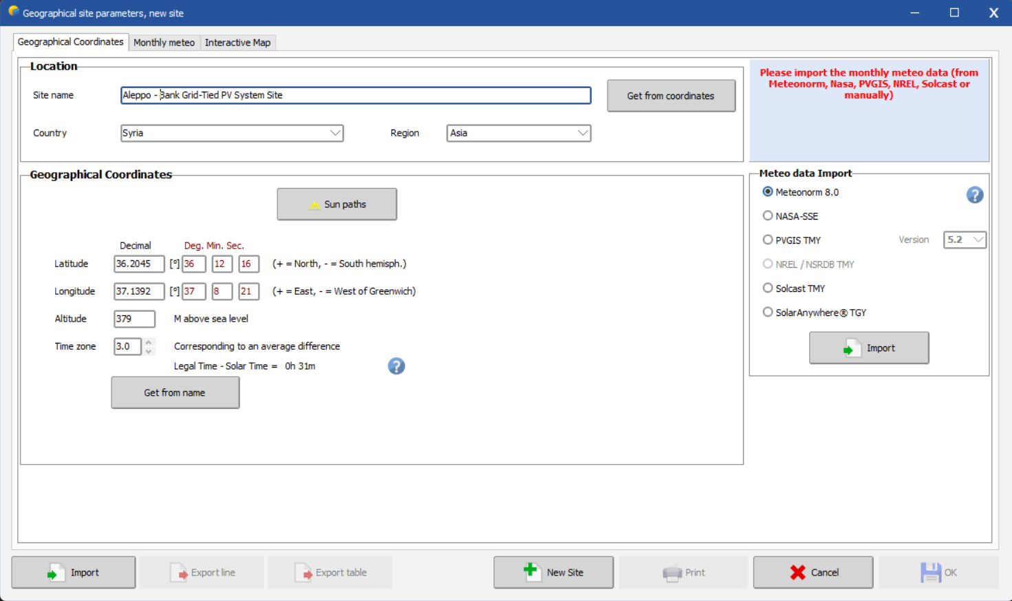
Presentation_Typst/Figures/PV-11-01.png
