MAQattan/My-Graduation-Project/Presentation_Typst/Figures/PV-11-02.png

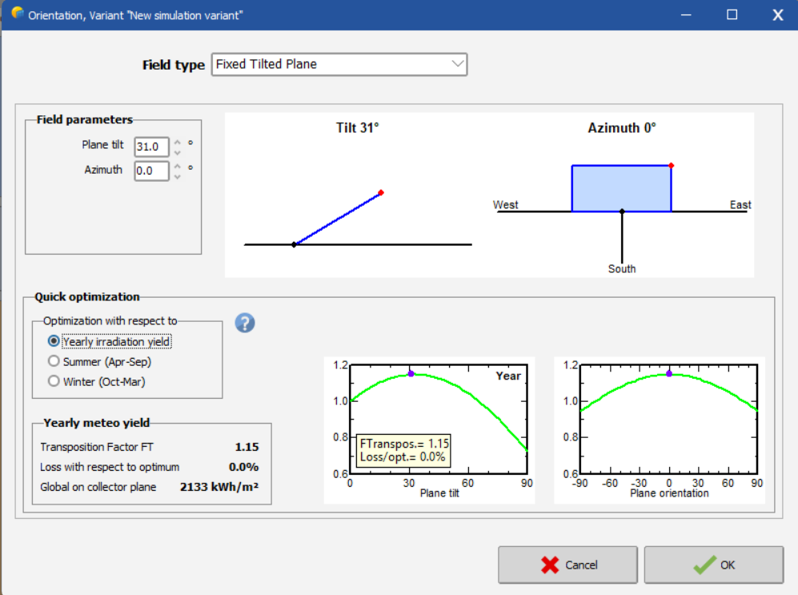
Presentation_Typst/Figures/PV-11-02.png
