MAQattan/My-Graduation-Project/Presentation_Typst/Figures/PV-11-04.png

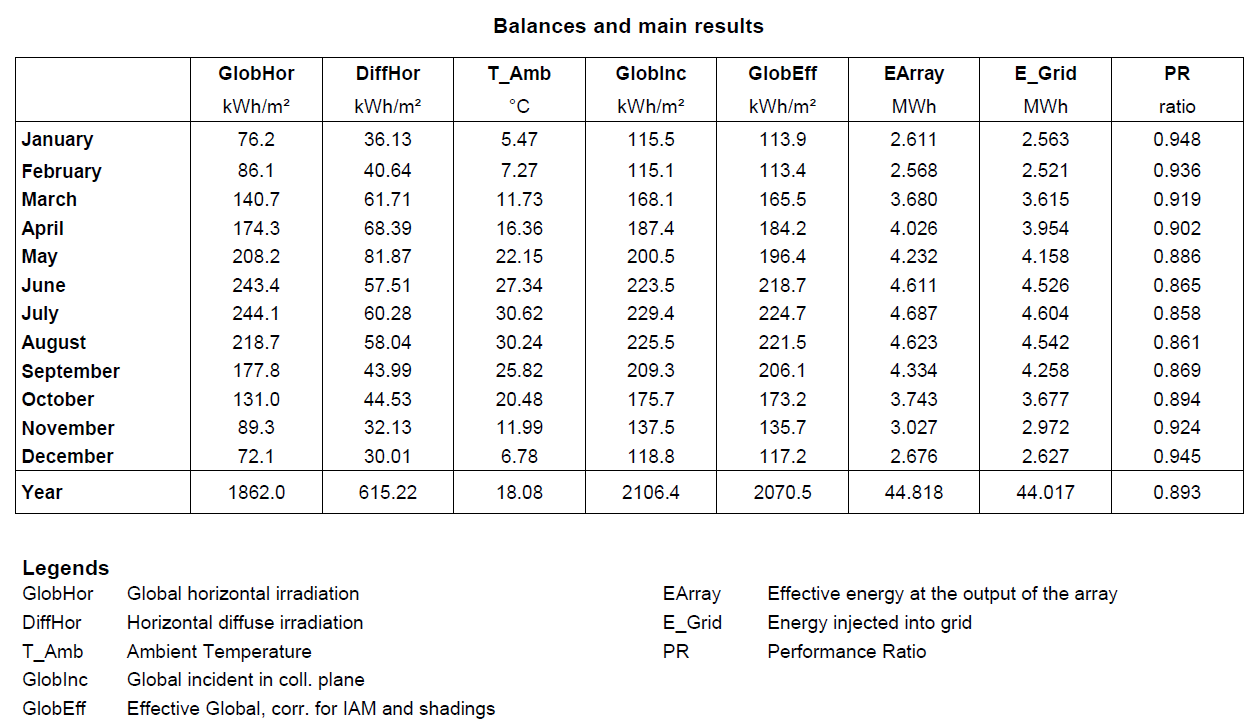
Presentation_Typst/Figures/PV-11-04.png
