MAQattan/My-Graduation-Project/Presentation_Typst/Figures/PV-11-05.png

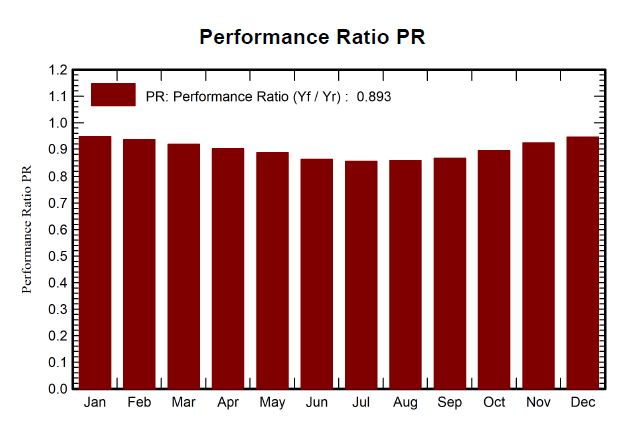
Presentation_Typst/Figures/PV-11-05.png
