MAQattan/My-Graduation-Project/Presentation_Typst/Figures/PV-11-07.png

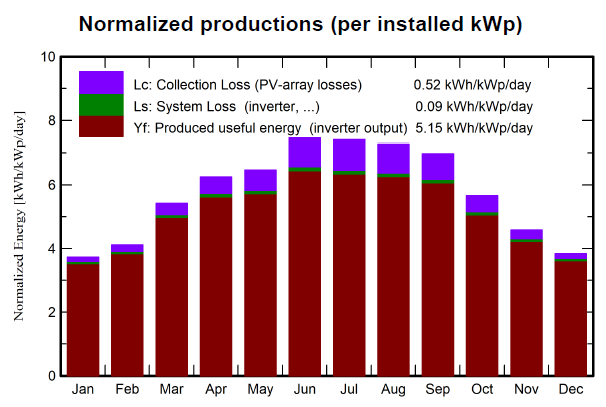
Presentation_Typst/Figures/PV-11-07.png
