MAQattan/My-Graduation-Project/Thesis_Typst/Appendices/A_Page_1.png

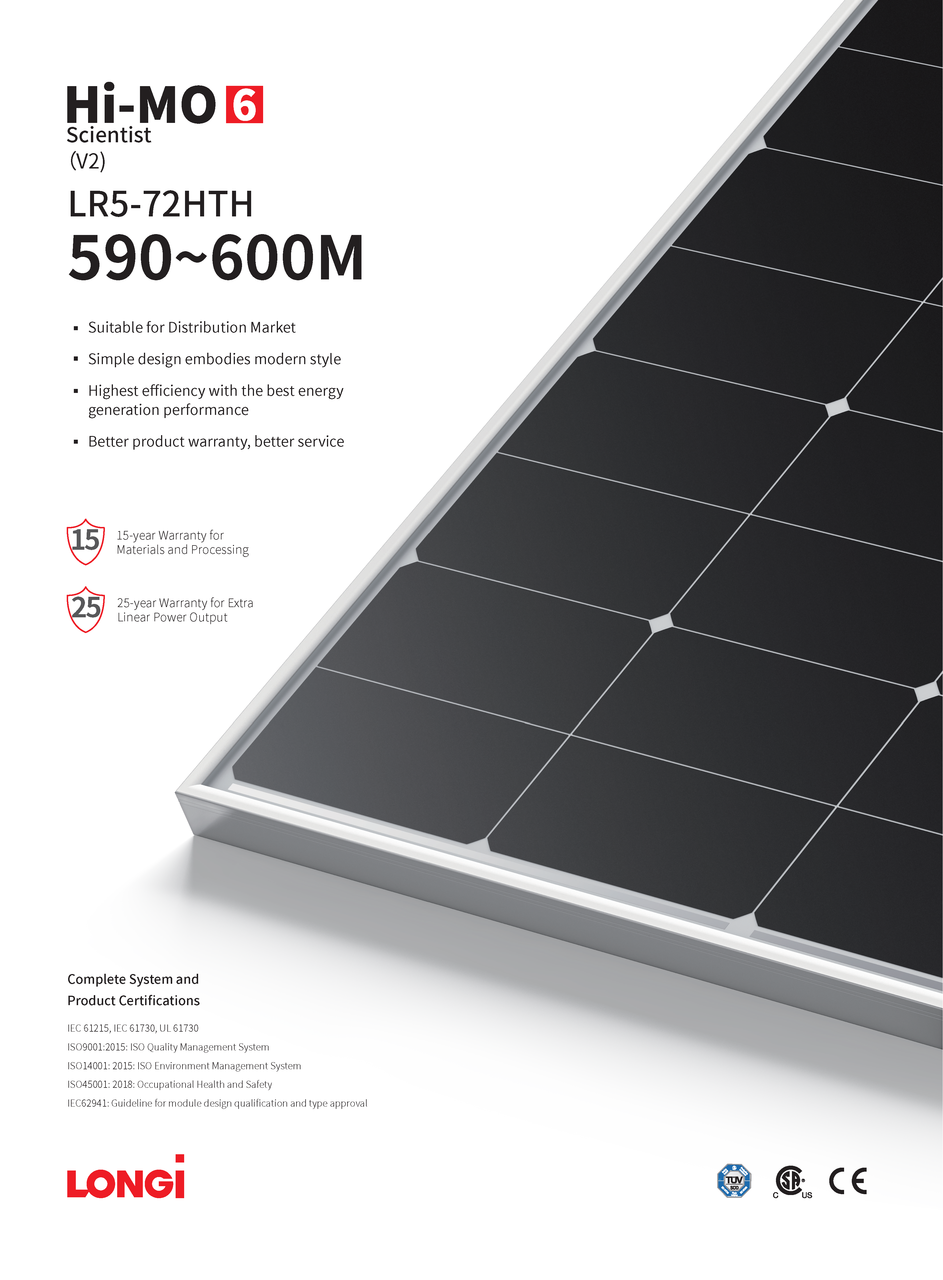
Thesis_Typst/Appendices/A_Page_1.png
