MAQattan/My-Graduation-Project/Thesis_Typst/Appendices/A_Page_2.png

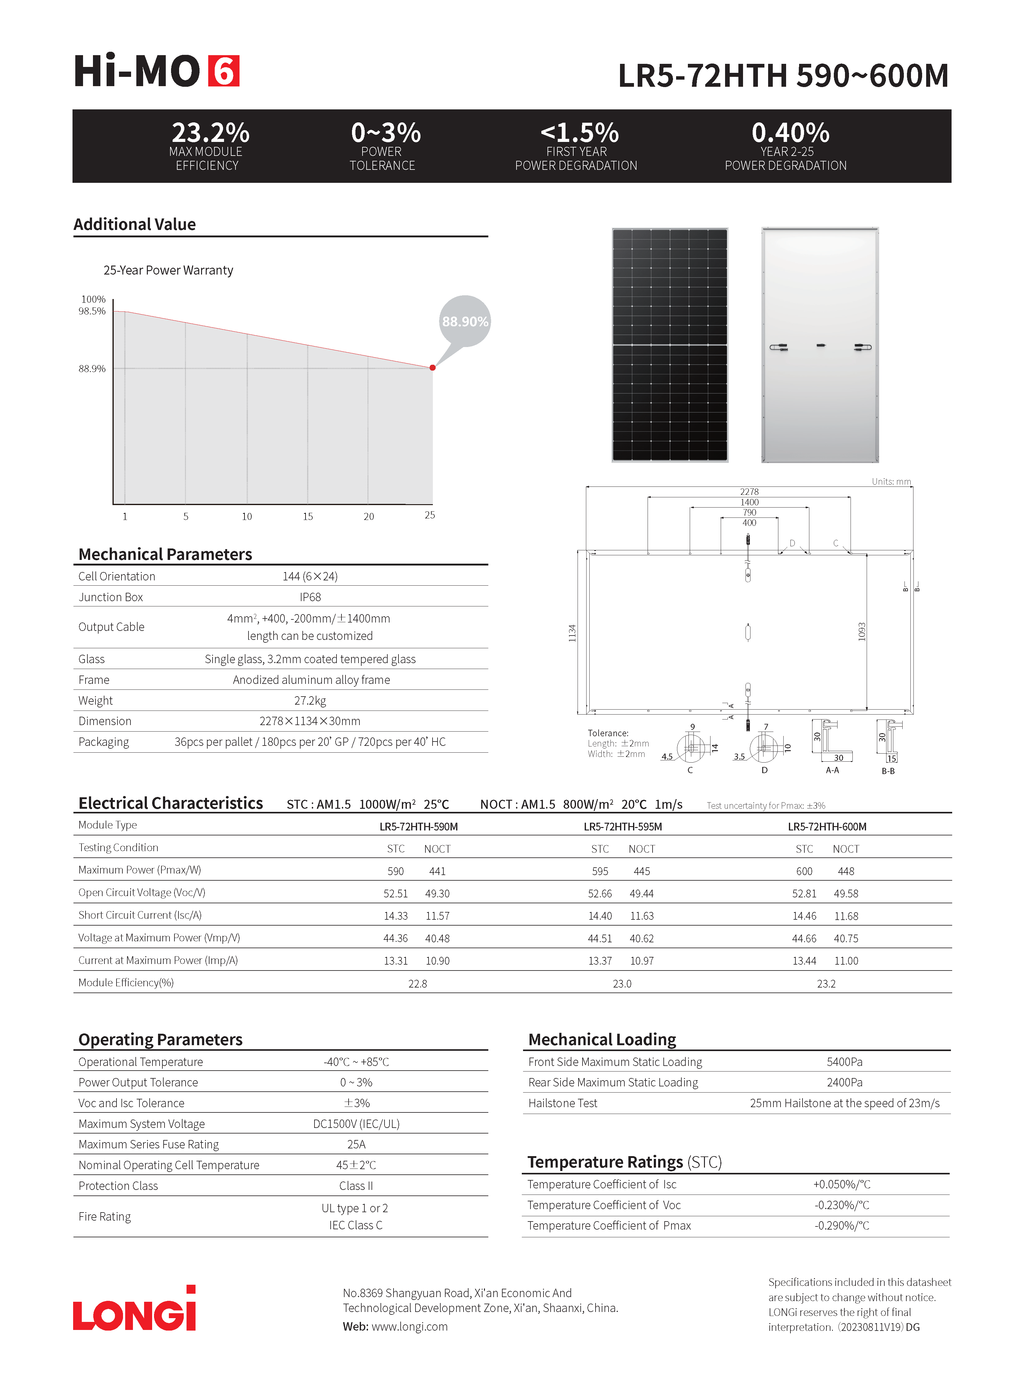
Thesis_Typst/Appendices/A_Page_2.png
