MAQattan/My-Graduation-Project/Thesis_Typst/Appendices/B_Page_1.png

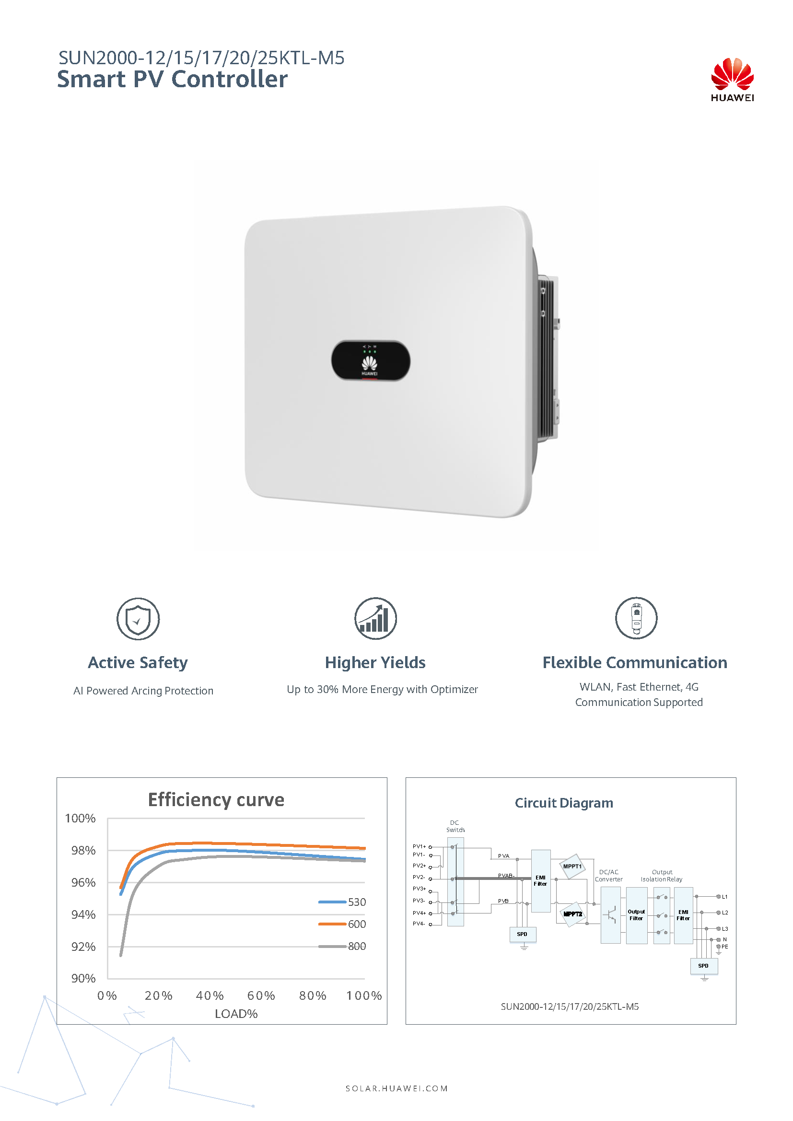
Thesis_Typst/Appendices/B_Page_1.png
