MAQattan/My-Graduation-Project/Thesis_Typst/Appendices/B_Page_2.png

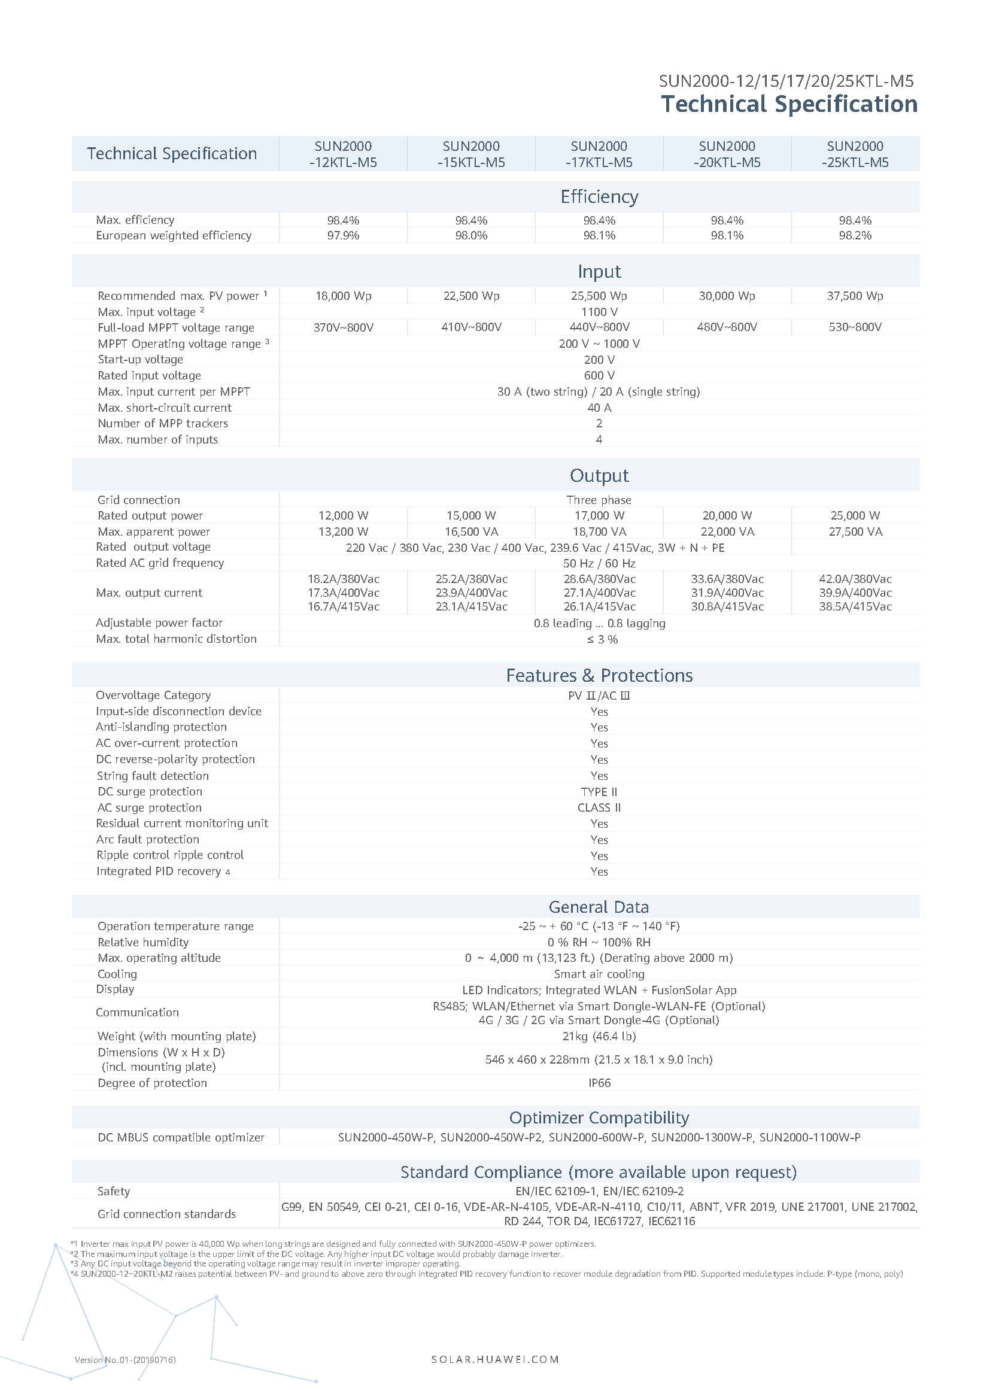
Thesis_Typst/Appendices/B_Page_2.png
