MAQattan/My-Graduation-Project/Thesis_Typst/Appendices/C1.png

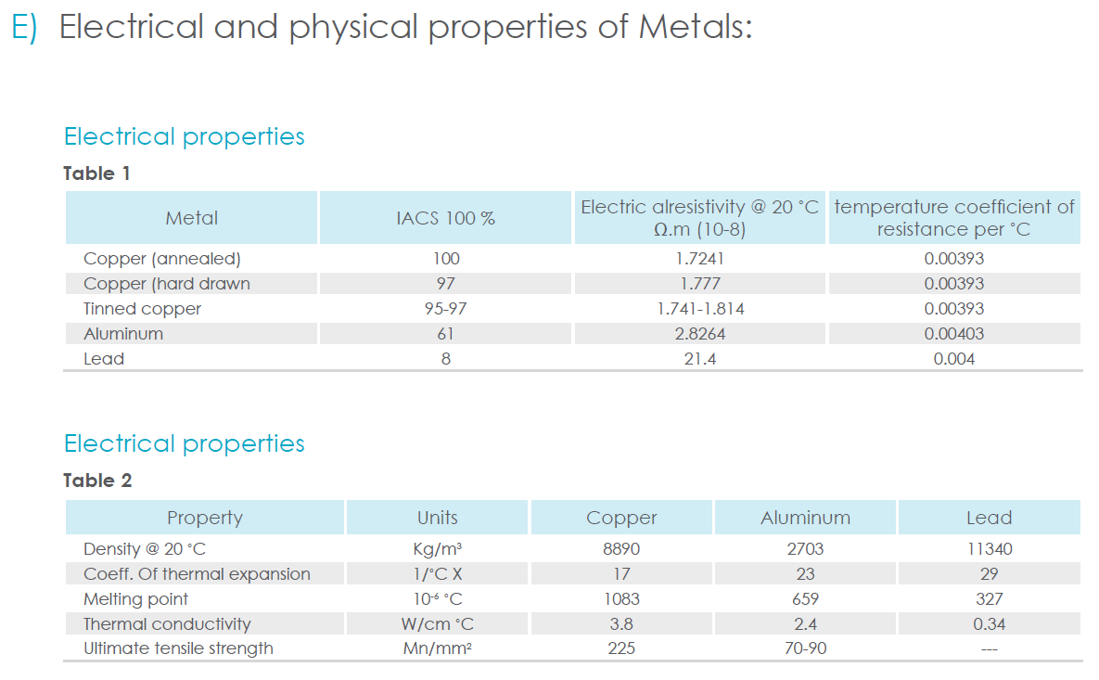
Thesis_Typst/Appendices/C1.png
