MAQattan/My-Graduation-Project/Thesis_Typst/Appendices/C2.png

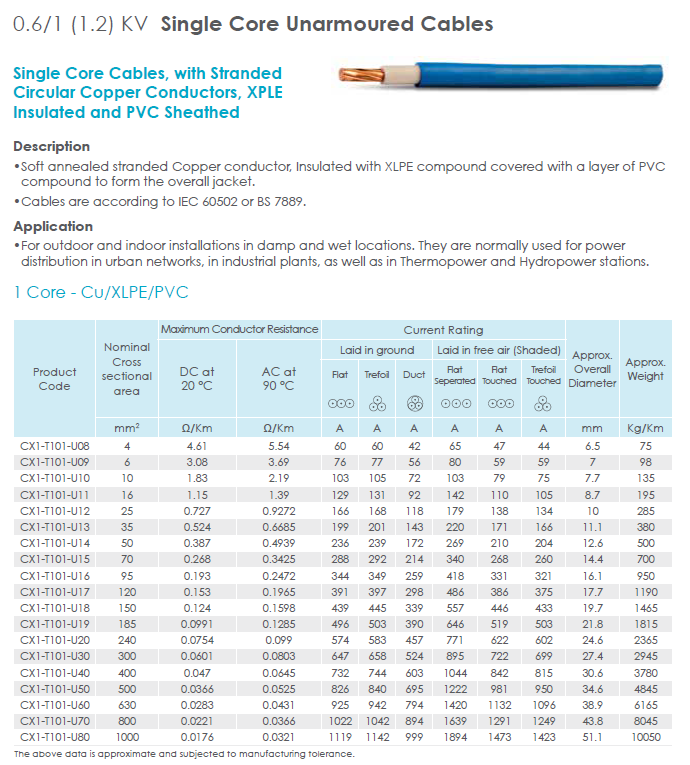
Thesis_Typst/Appendices/C2.png
