MAQattan/My-Graduation-Project/Thesis_Typst/Appendices/C3.png

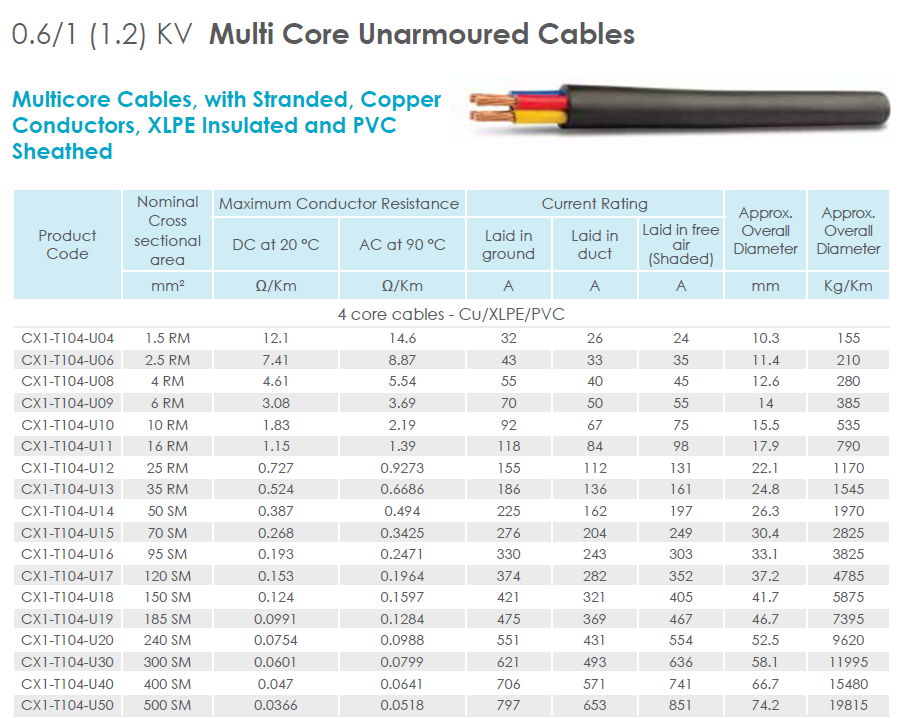
Thesis_Typst/Appendices/C3.png
