MAQattan/My-Graduation-Project/Thesis_Typst/Appendices/C4.png

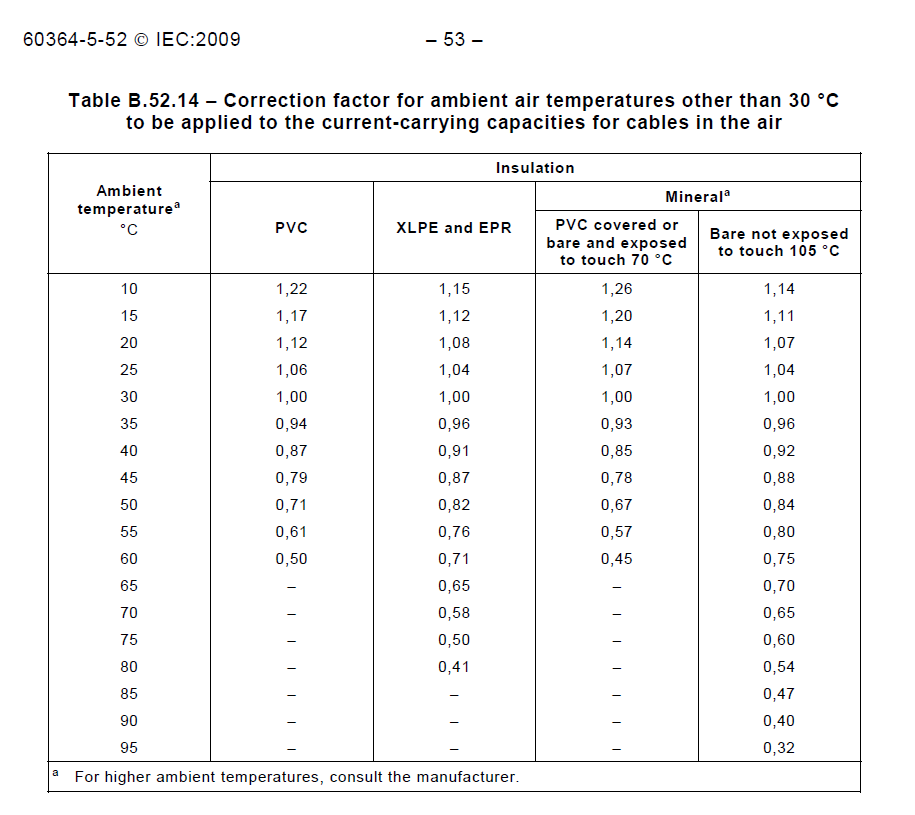
Thesis_Typst/Appendices/C4.png
