MAQattan/My-Graduation-Project/Thesis_Typst/chapters/ch03/Figures/PV-03-01.png

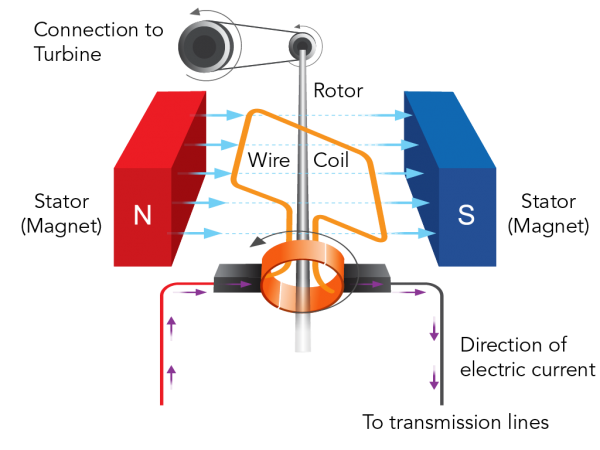
Thesis_Typst/chapters/ch03/Figures/PV-03-01.png
