MAQattan/My-Graduation-Project/Thesis_Typst/chapters/ch03/Figures/PV-03-03.gif

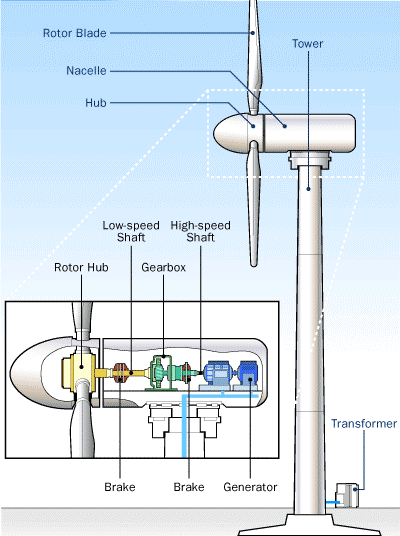
Thesis_Typst/chapters/ch03/Figures/PV-03-03.gif
