MAQattan/My-Graduation-Project/Thesis_Typst/chapters/ch03/Figures/PV-03-04.jpg

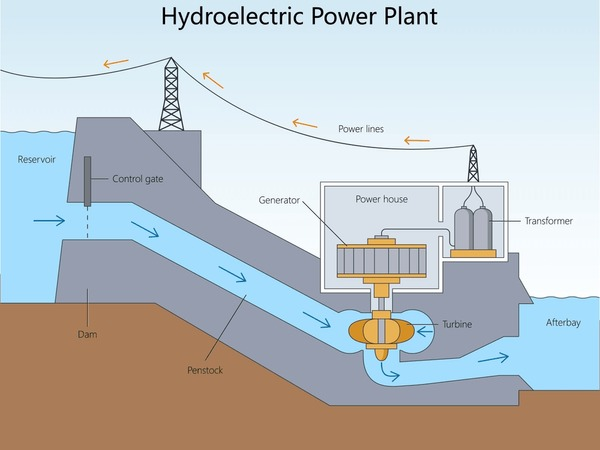
Thesis_Typst/chapters/ch03/Figures/PV-03-04.jpg
