MAQattan/My-Graduation-Project/Thesis_Typst/chapters/ch03/Figures/PV-03-07.jpg

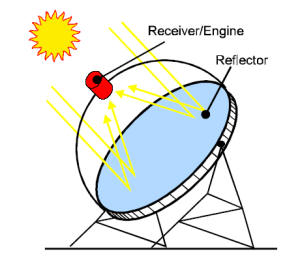
Thesis_Typst/chapters/ch03/Figures/PV-03-07.jpg
