MAQattan/My-Graduation-Project/Thesis_Typst/chapters/ch03/Figures/PV-03-08.png

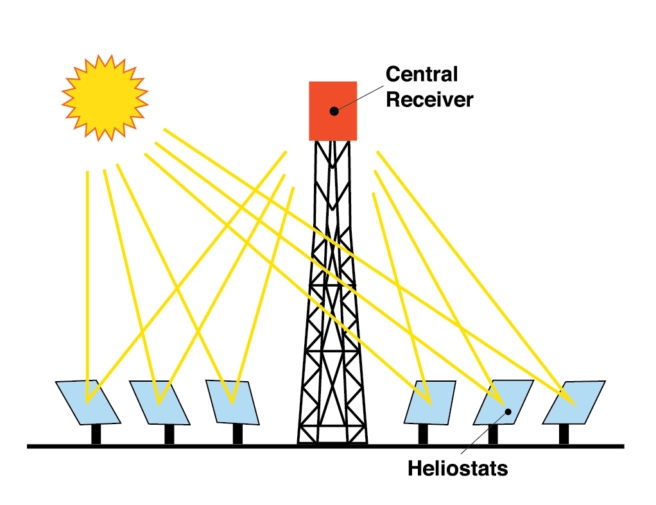
Thesis_Typst/chapters/ch03/Figures/PV-03-08.png
