MAQattan/My-Graduation-Project/Thesis_Typst/chapters/ch04/Figures/PV-04-12.png

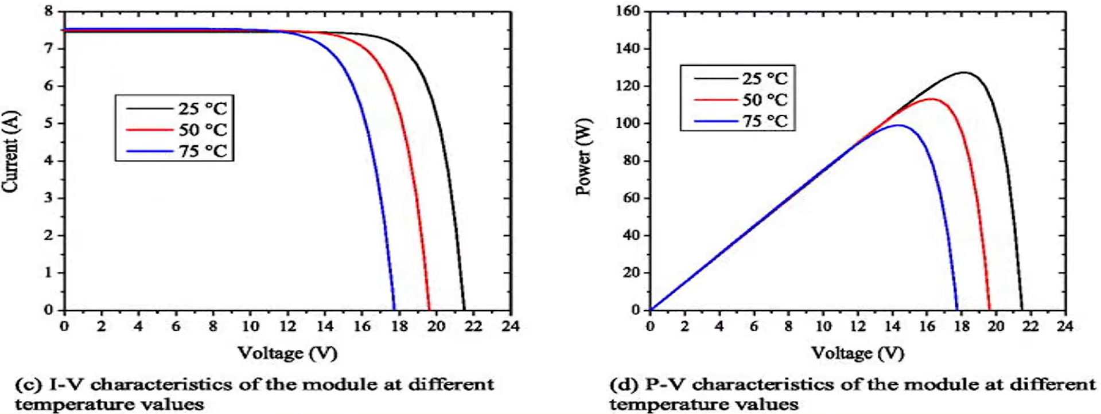
Thesis_Typst/chapters/ch04/Figures/PV-04-12.png
