MAQattan/My-Graduation-Project/Thesis_Typst/chapters/ch04/Figures/PV-04-16.jpg

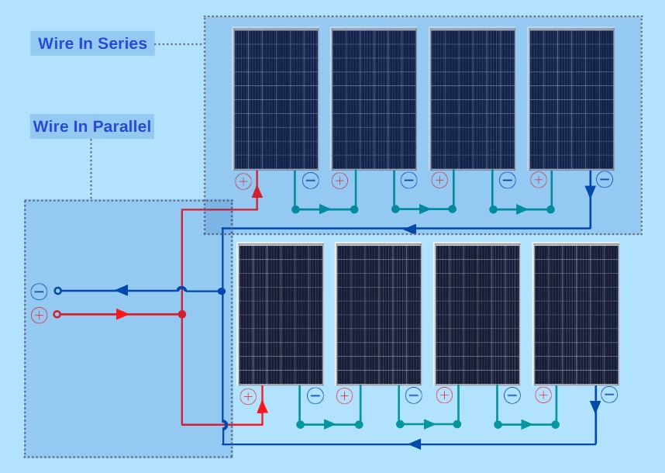
Thesis_Typst/chapters/ch04/Figures/PV-04-16.jpg
