MAQattan/My-Graduation-Project/Thesis_Typst/chapters/ch04/Figures/PV-04-19.png

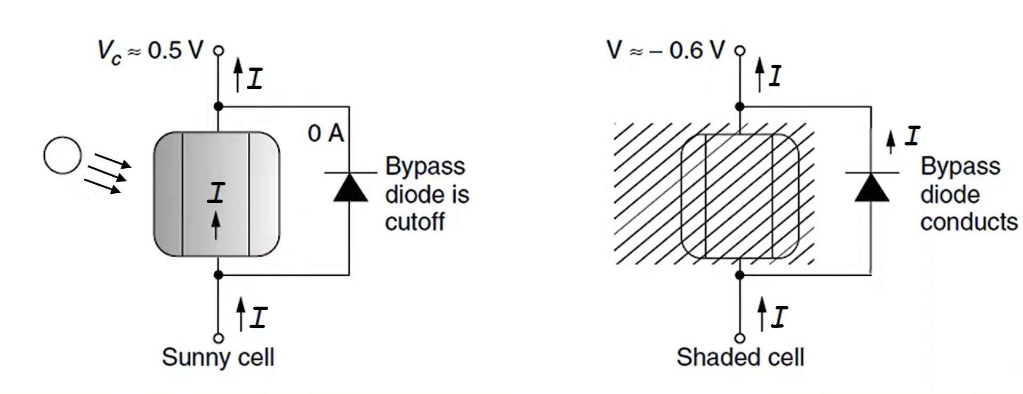
Thesis_Typst/chapters/ch04/Figures/PV-04-19.png
