MAQattan/My-Graduation-Project/Thesis_Typst/chapters/ch04/Figures/PV-04-23.jpg

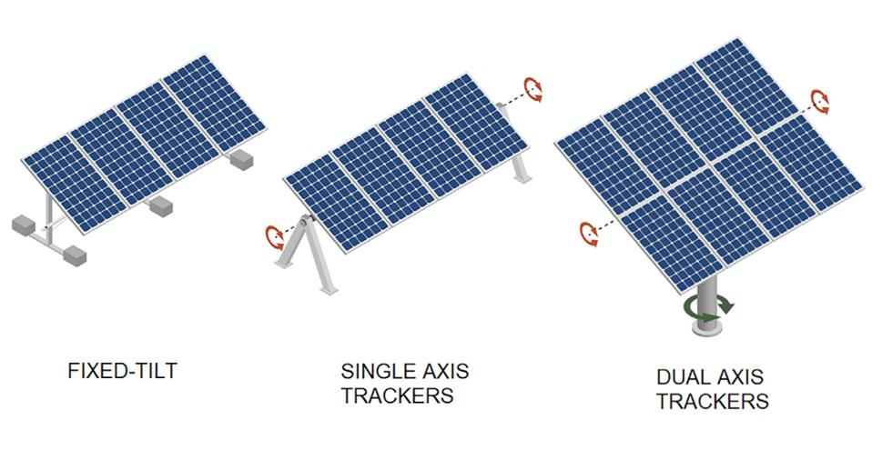
Thesis_Typst/chapters/ch04/Figures/PV-04-23.jpg
