MAQattan/My-Graduation-Project/Thesis_Typst/chapters/ch04/Figures/PV-04-26.jpg

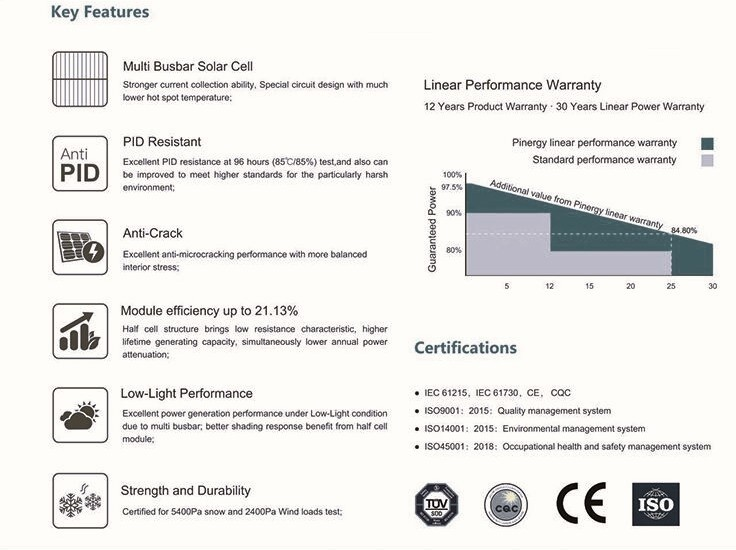
Thesis_Typst/chapters/ch04/Figures/PV-04-26.jpg
