MAQattan/My-Graduation-Project/Thesis_Typst/chapters/ch04/Figures/PV-05-02.png

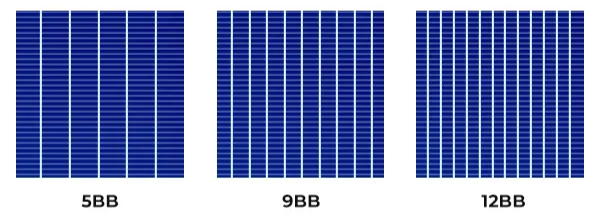
Thesis_Typst/chapters/ch04/Figures/PV-05-02.png
