MAQattan/My-Graduation-Project/Thesis_Typst/chapters/ch04/Figures/PV-05-06.png

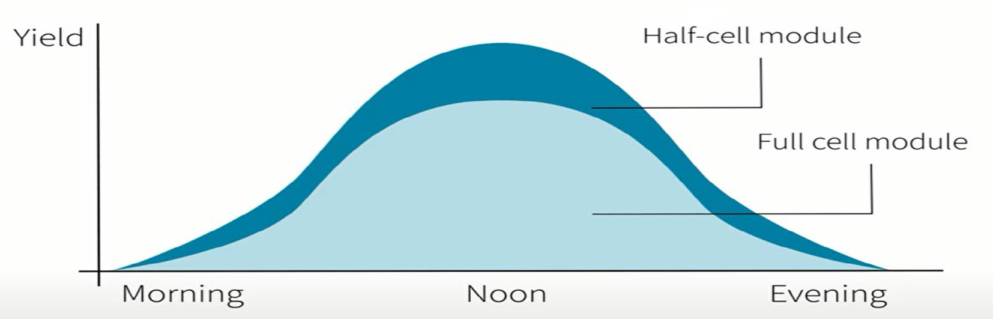
Thesis_Typst/chapters/ch04/Figures/PV-05-06.png
