MAQattan/My-Graduation-Project/Thesis_Typst/chapters/ch06/Figures/PV-06-01.png

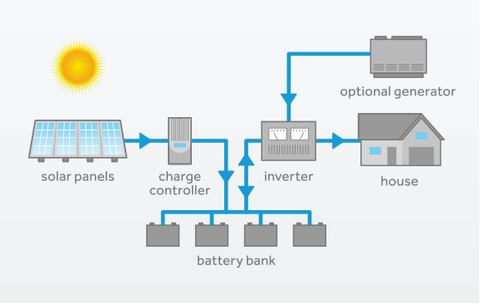
Thesis_Typst/chapters/ch06/Figures/PV-06-01.png
