MAQattan/My-Graduation-Project/Thesis_Typst/chapters/ch06/Figures/PV-06-02.jpg

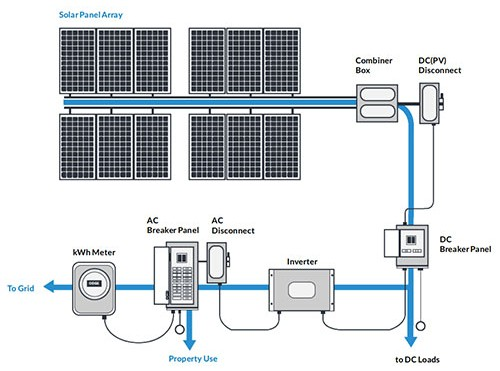
Thesis_Typst/chapters/ch06/Figures/PV-06-02.jpg
