MAQattan/My-Graduation-Project/Thesis_Typst/chapters/ch07/Figures/PV-07-02.jpg

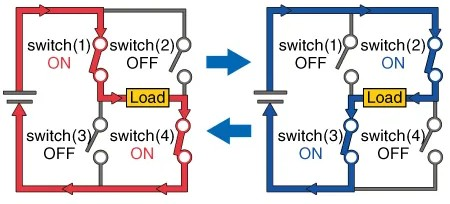
Thesis_Typst/chapters/ch07/Figures/PV-07-02.jpg
