MAQattan/My-Graduation-Project/Thesis_Typst/chapters/ch07/Figures/PV-07-04.png

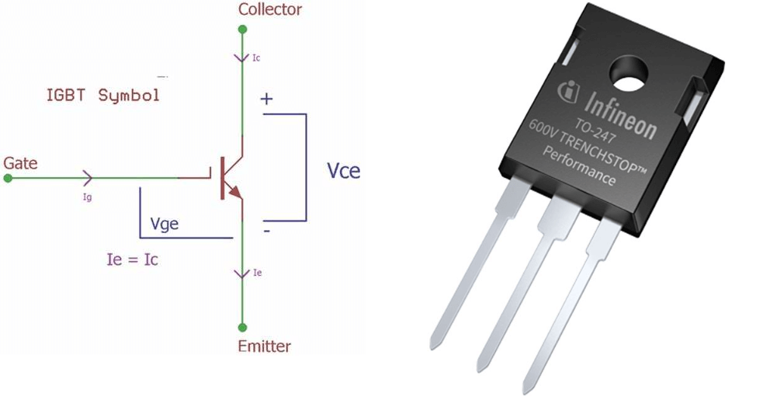
Thesis_Typst/chapters/ch07/Figures/PV-07-04.png
