MAQattan/My-Graduation-Project/Thesis_Typst/chapters/ch07/Figures/PV-07-06.jpg

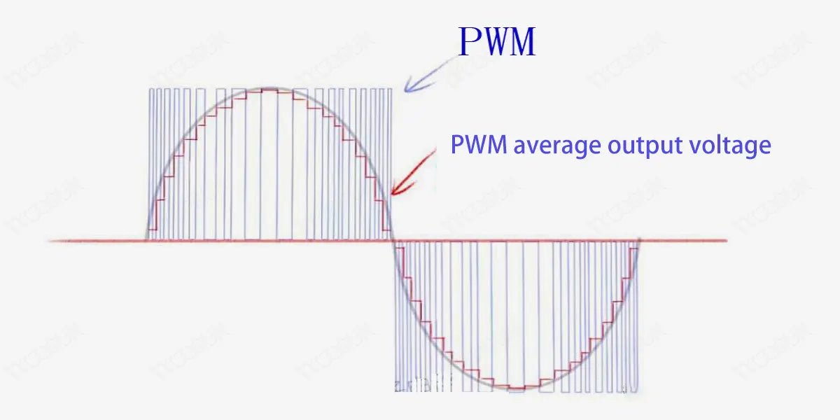
Thesis_Typst/chapters/ch07/Figures/PV-07-06.jpg
