MAQattan/My-Graduation-Project/Thesis_Typst/chapters/ch07/Figures/PV-07-10.webp

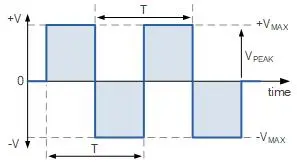
Thesis_Typst/chapters/ch07/Figures/PV-07-10.webp
