MAQattan/My-Graduation-Project/Thesis_Typst/chapters/ch07/Figures/PV-07-12.png

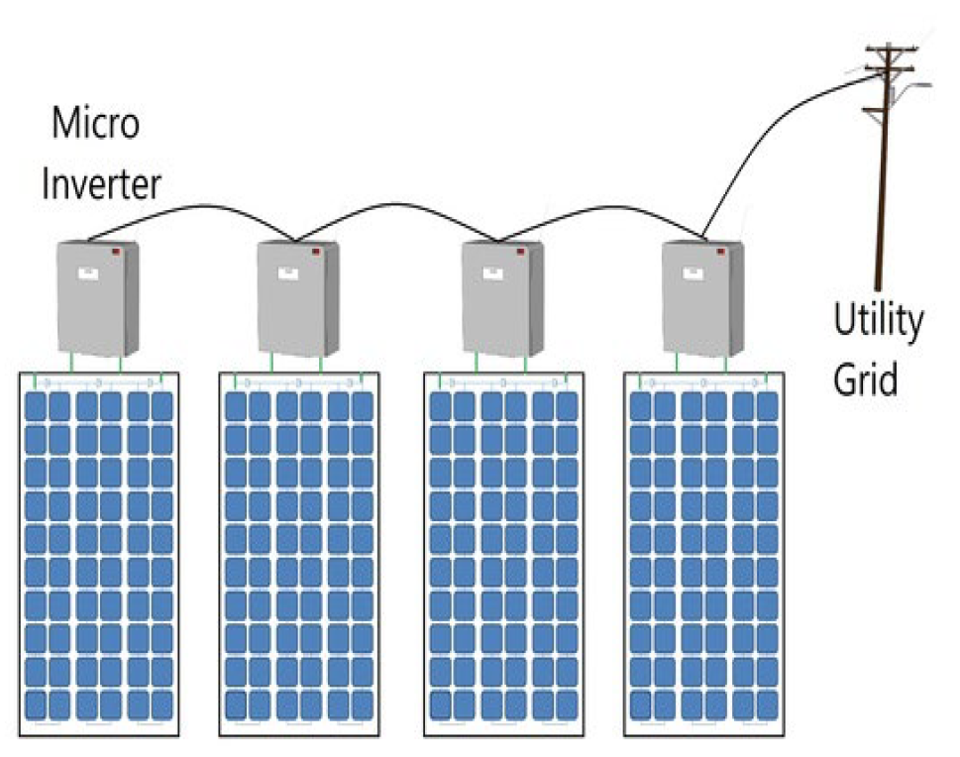
Thesis_Typst/chapters/ch07/Figures/PV-07-12.png
