MAQattan/My-Graduation-Project/Thesis_Typst/chapters/ch07/Figures/PV-07-13.png

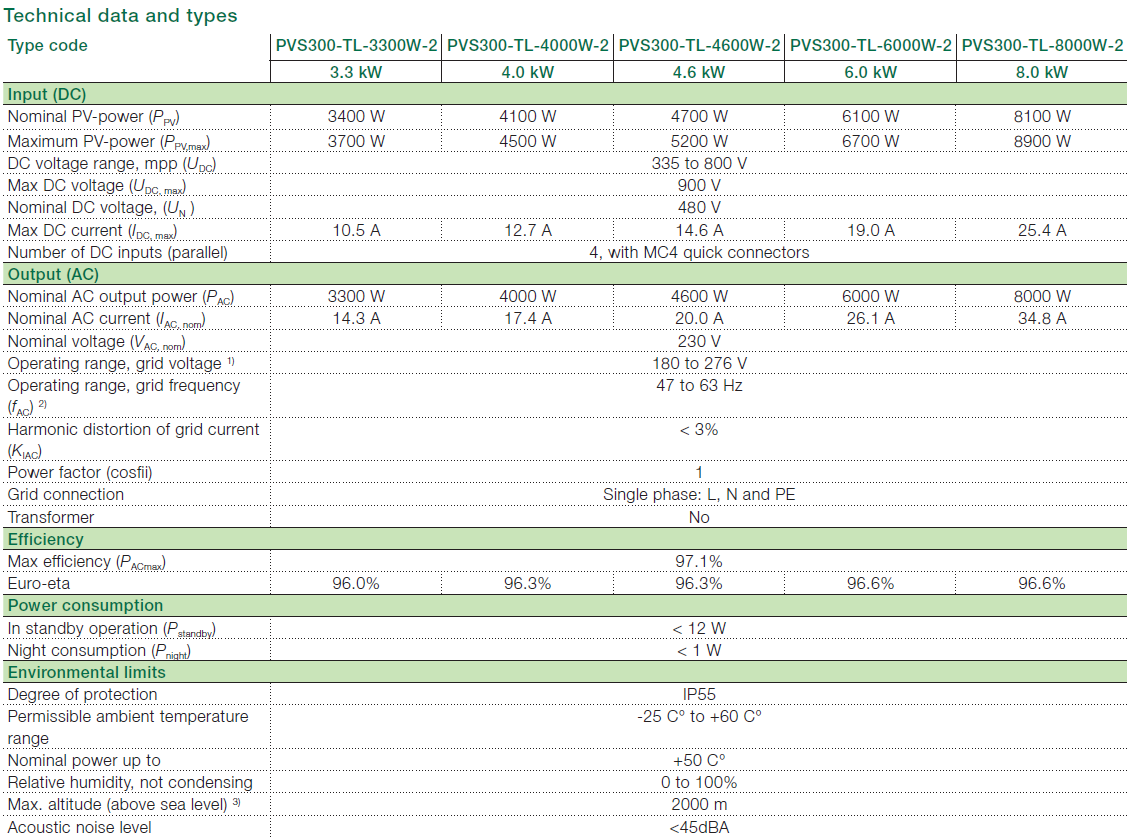
Thesis_Typst/chapters/ch07/Figures/PV-07-13.png
