MAQattan/My-Graduation-Project/Thesis_Typst/chapters/ch07/Figures/PV-07-17.png

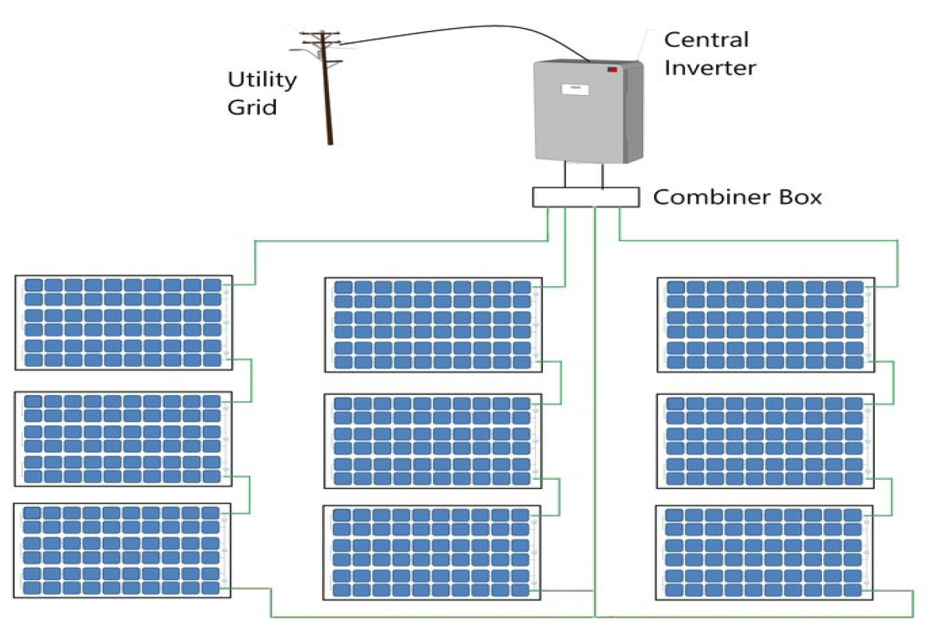
Thesis_Typst/chapters/ch07/Figures/PV-07-17.png
