MAQattan/My-Graduation-Project/Thesis_Typst/chapters/ch08/Figures/PV-08-01.png

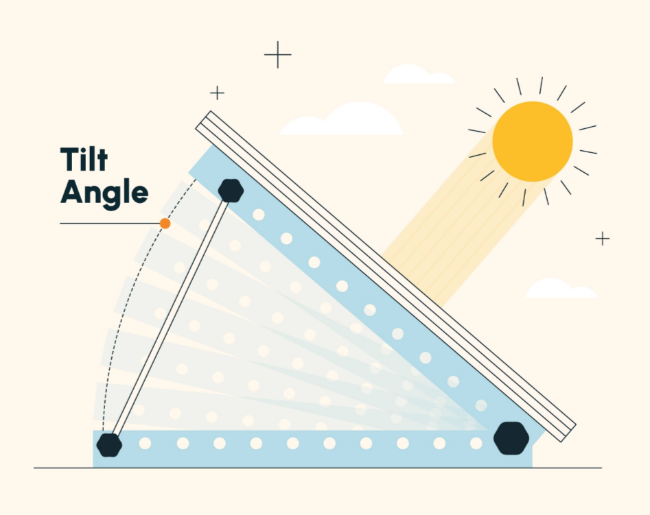
Thesis_Typst/chapters/ch08/Figures/PV-08-01.png
