MAQattan/My-Graduation-Project/Thesis_Typst/chapters/ch08/Figures/PV-08-05.jpg

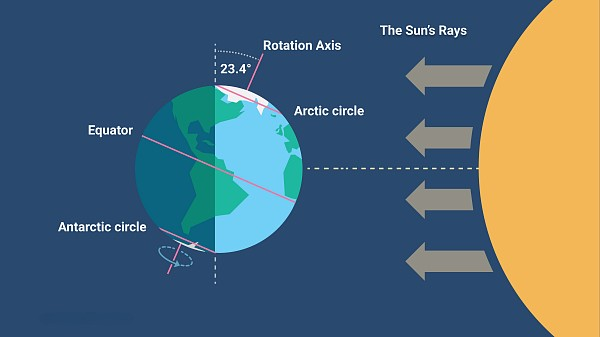
Thesis_Typst/chapters/ch08/Figures/PV-08-05.jpg
