MAQattan/My-Graduation-Project/Thesis_Typst/chapters/ch08/Figures/PV-08-07.jpg

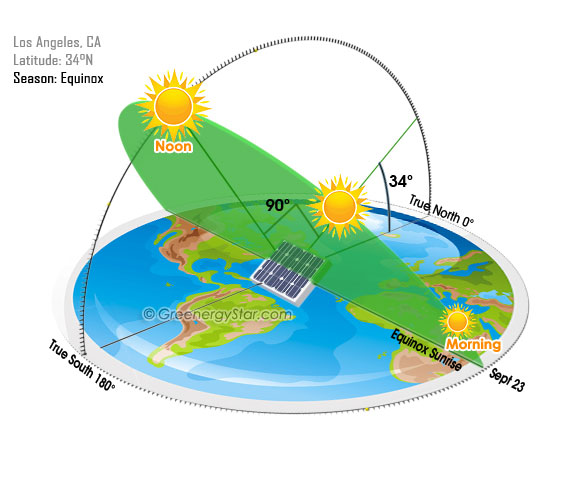
Thesis_Typst/chapters/ch08/Figures/PV-08-07.jpg
