MAQattan/My-Graduation-Project/Thesis_Typst/chapters/ch09/Figures/193.jpg

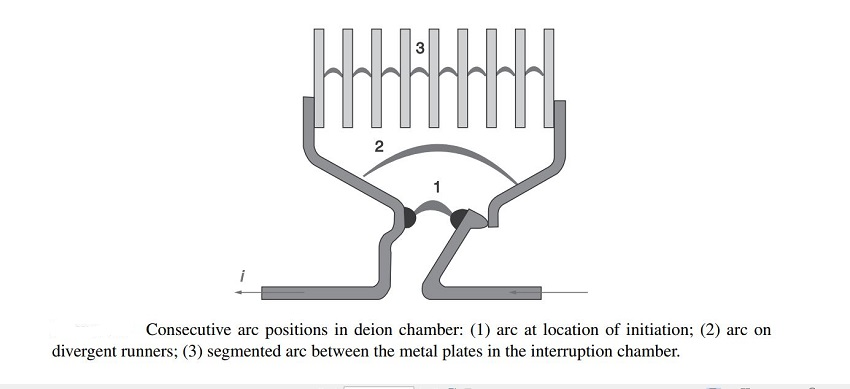
Thesis_Typst/chapters/ch09/Figures/193.jpg
