MAQattan/My-Graduation-Project/Thesis_Typst/chapters/ch09/Figures/7703e50aa5be4e3a8756facce1c4e32e.jpg

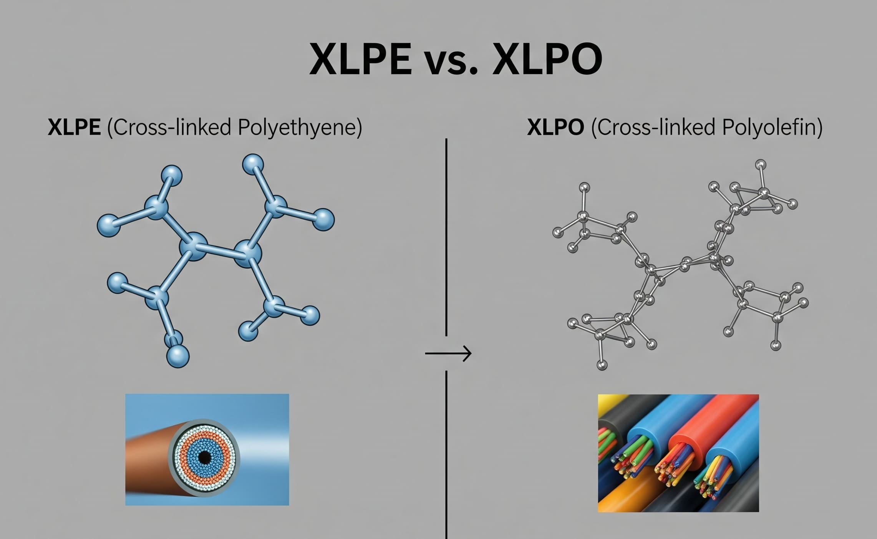
Thesis_Typst/chapters/ch09/Figures/7703e50aa5be4e3a8756facce1c4e32e.jpg
