MAQattan/My-Graduation-Project/Thesis_Typst/chapters/ch09/Figures/1729953673276.jpg

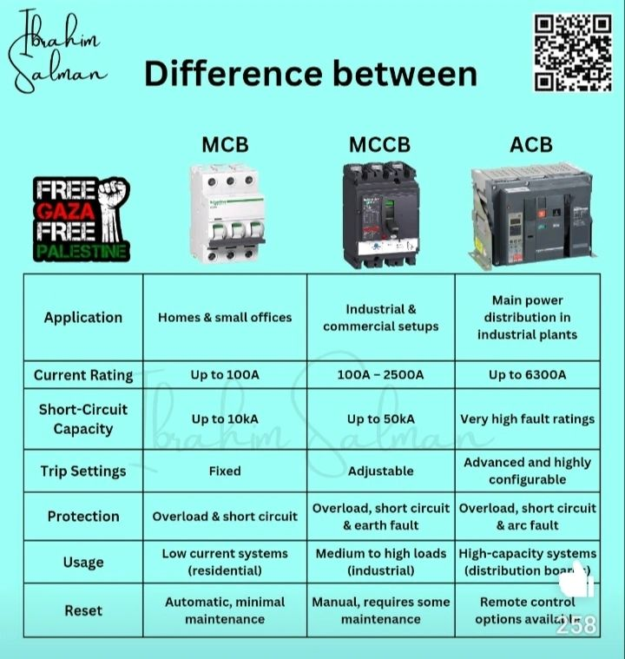
Thesis_Typst/chapters/ch09/Figures/1729953673276.jpg
