MAQattan/My-Graduation-Project/Thesis_Typst/chapters/ch09/Figures/1761010792405.jpg

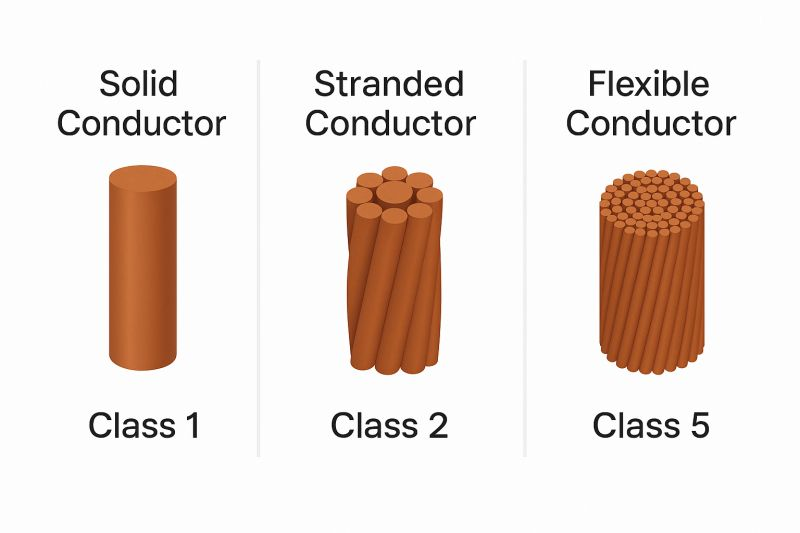
Thesis_Typst/chapters/ch09/Figures/1761010792405.jpg
