MAQattan/My-Graduation-Project/Thesis_Typst/chapters/ch09/Figures/1762951919946.jpg

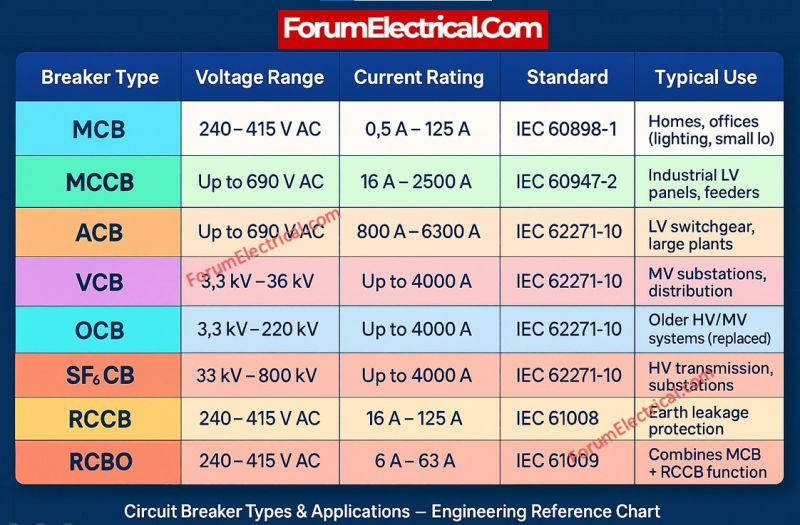
Thesis_Typst/chapters/ch09/Figures/1762951919946.jpg
