MAQattan/My-Graduation-Project/Thesis_Typst/chapters/ch09/Figures/AC-MCB-63A-Circuit-Breaker-1p-2p-3p-4p-AC-Breaker-for-Solar-System.webp

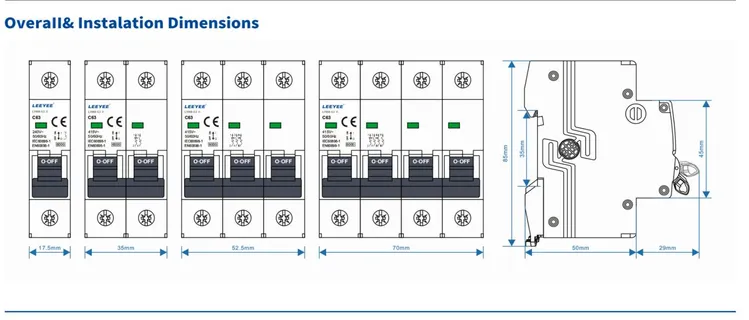
Thesis_Typst/chapters/ch09/Figures/AC-MCB-63A-Circuit-Breaker-1p-2p-3p-4p-AC-Breaker-for-Solar-System.webp
