MAQattan/My-Graduation-Project/Thesis_Typst/chapters/ch09/Figures/ACB-vs-MCCB-vs-MCB-Key-Differences-1024x536.jpg

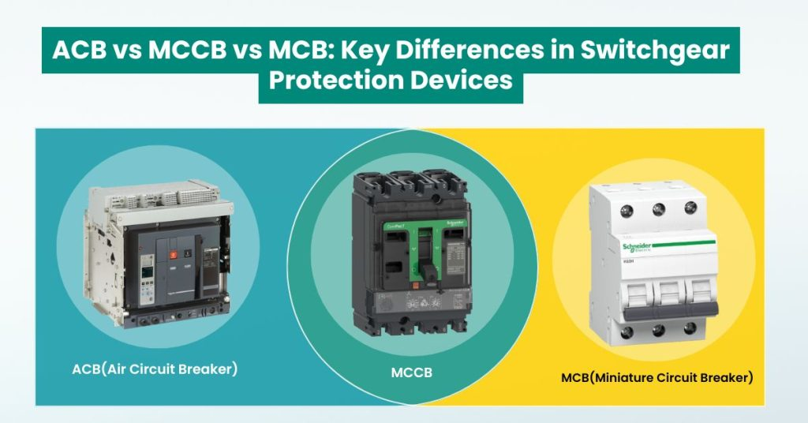
Thesis_Typst/chapters/ch09/Figures/ACB-vs-MCCB-vs-MCB-Key-Differences-1024x536.jpg
