MAQattan/My-Graduation-Project/Thesis_Typst/chapters/ch09/Figures/Air-Break-Circuit-Breaker-Diagram-2.webp

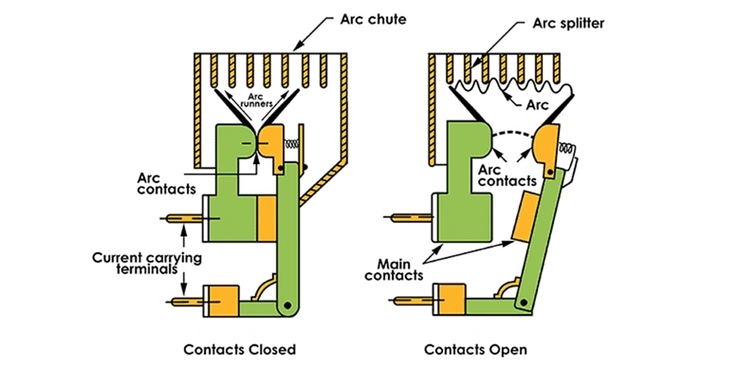
Thesis_Typst/chapters/ch09/Figures/Air-Break-Circuit-Breaker-Diagram-2.webp
