MAQattan/My-Graduation-Project/Thesis_Typst/chapters/ch09/Figures/Bimetal_Strip.gif

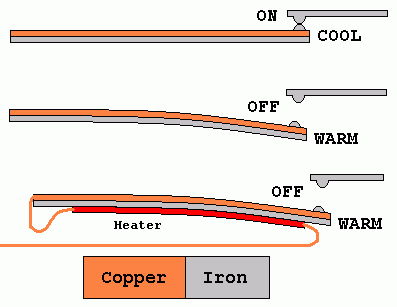
Thesis_Typst/chapters/ch09/Figures/Bimetal_Strip.gif
