MAQattan/My-Graduation-Project/Thesis_Typst/chapters/ch09/Figures/Comparison-Chart-of-Differences-between-MCB-MCCB-ELCB-RCD_2.webp

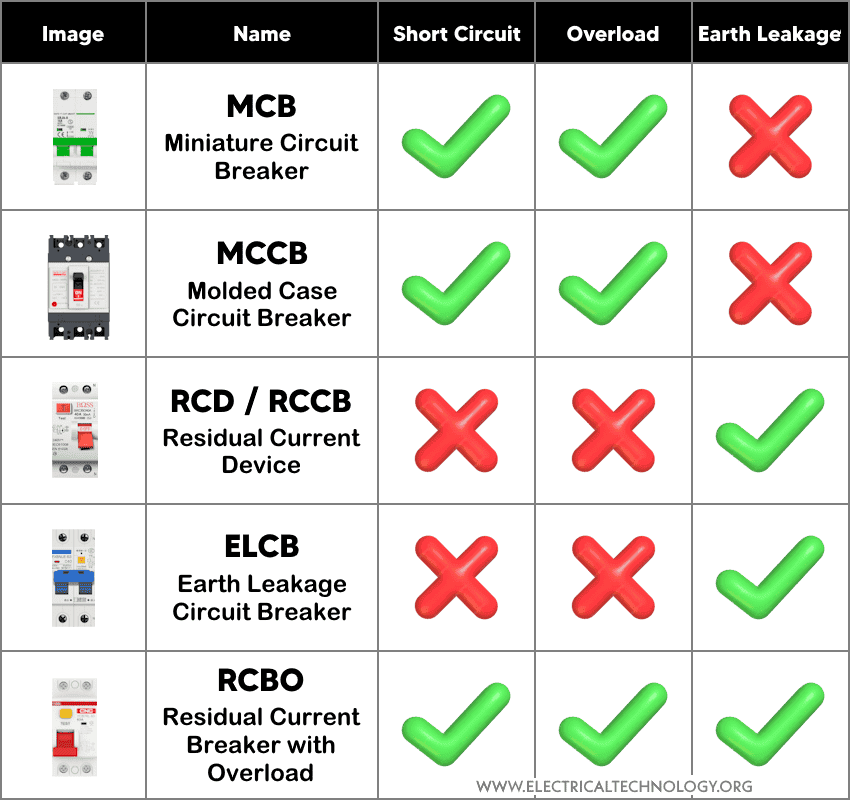
Thesis_Typst/chapters/ch09/Figures/Comparison-Chart-of-Differences-between-MCB-MCCB-ELCB-RCD_2.webp
