MAQattan/My-Graduation-Project/Thesis_Typst/chapters/ch09/Figures/dc-fuse-srd-30-1100v-01.webp

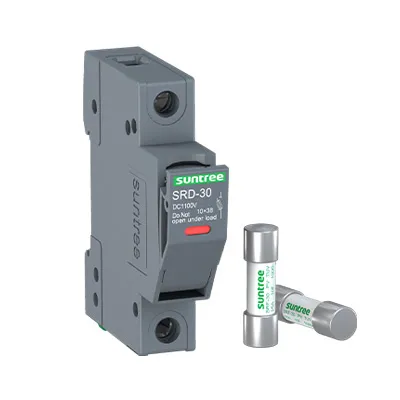
Thesis_Typst/chapters/ch09/Figures/dc-fuse-srd-30-1100v-01.webp
