MAQattan/My-Graduation-Project/Thesis_Typst/chapters/ch09/Figures/EKM2-63S.jpg

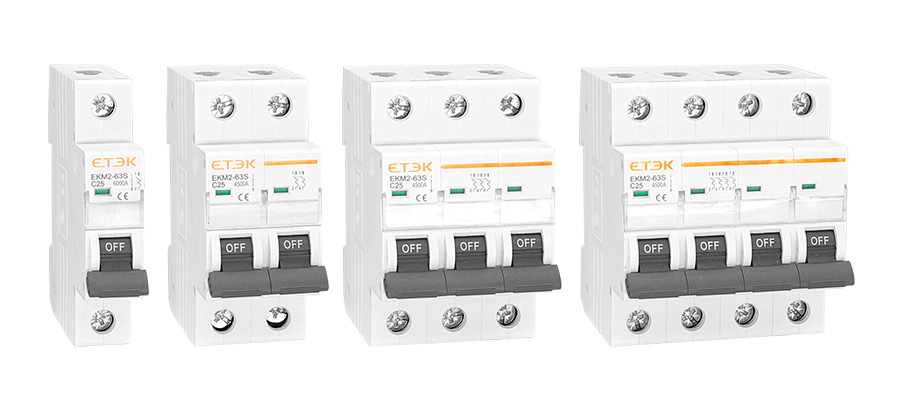
Thesis_Typst/chapters/ch09/Figures/EKM2-63S.jpg
