MAQattan/My-Graduation-Project/Thesis_Typst/chapters/ch09/Figures/el-current-flowing.png

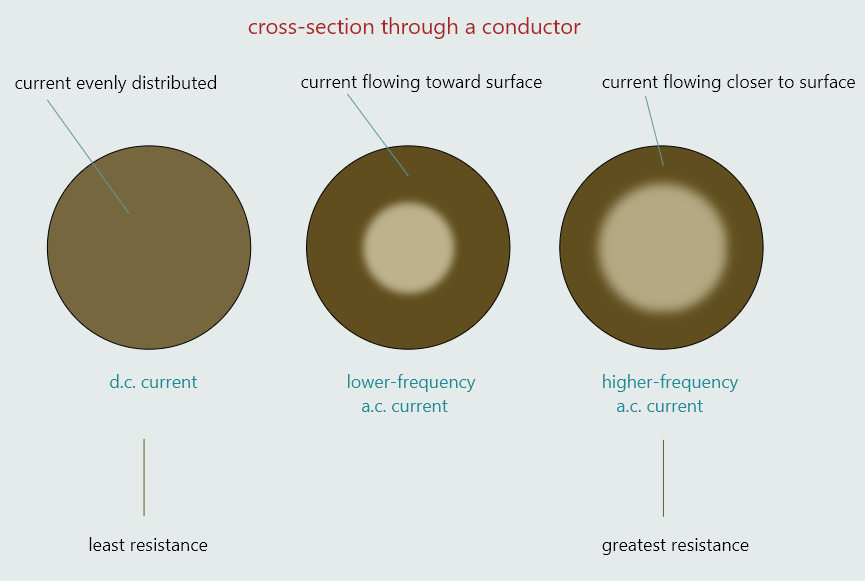
Thesis_Typst/chapters/ch09/Figures/el-current-flowing.png
