MAQattan/My-Graduation-Project/Thesis_Typst/chapters/ch09/Figures/fig1.png

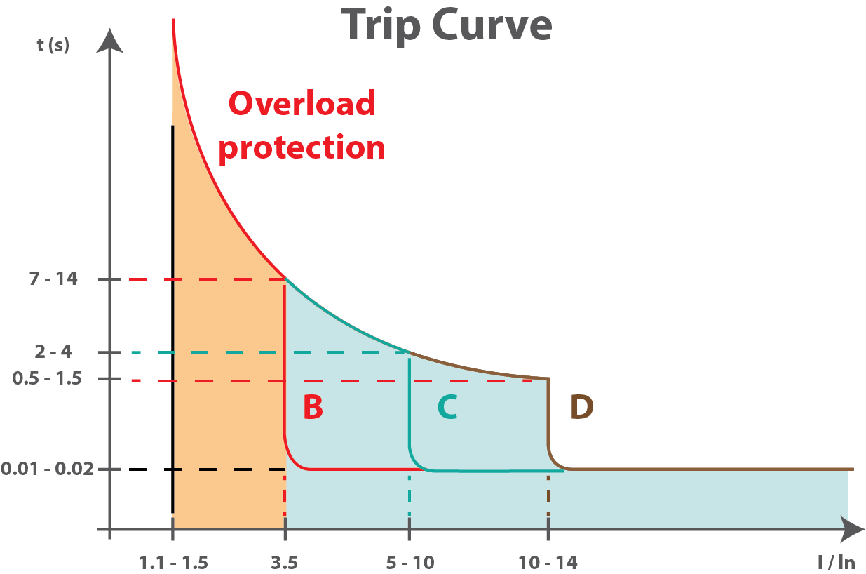
Thesis_Typst/chapters/ch09/Figures/fig1.png
