MAQattan/My-Graduation-Project/Thesis_Typst/chapters/ch09/Figures/High-Quality-Compact-MCCB-Circuit-Breaker-KNM5-2.png

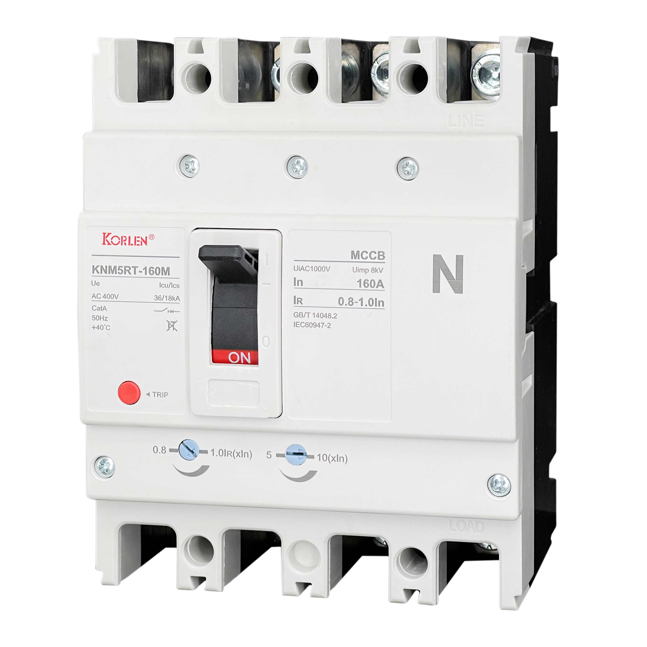
Thesis_Typst/chapters/ch09/Figures/High-Quality-Compact-MCCB-Circuit-Breaker-KNM5-2.png
