MAQattan/My-Graduation-Project/Thesis_Typst/chapters/ch09/Figures/maxresdefault.jpg

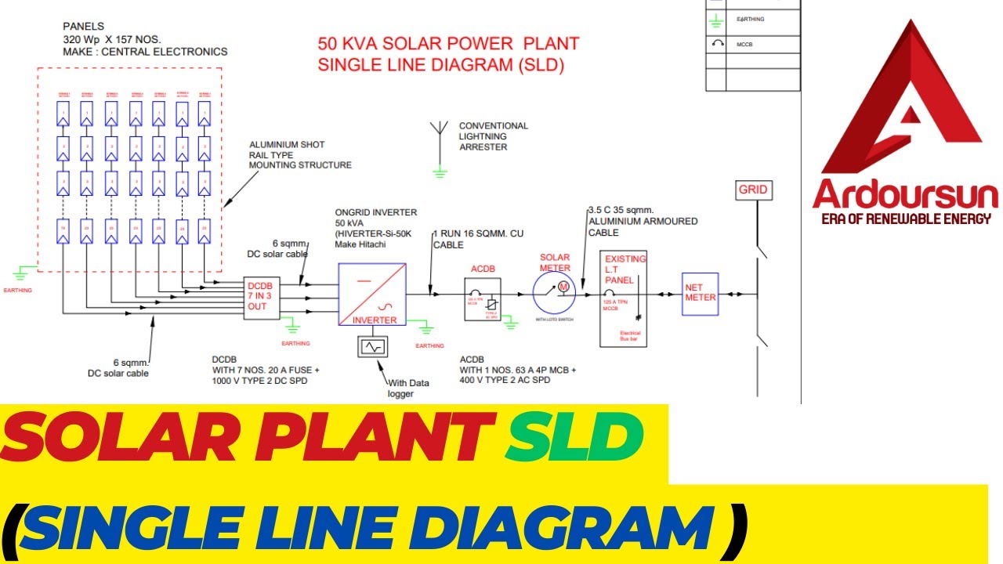
Thesis_Typst/chapters/ch09/Figures/maxresdefault.jpg
