MAQattan/My-Graduation-Project/Thesis_Typst/chapters/ch09/Figures/MCB.jpg

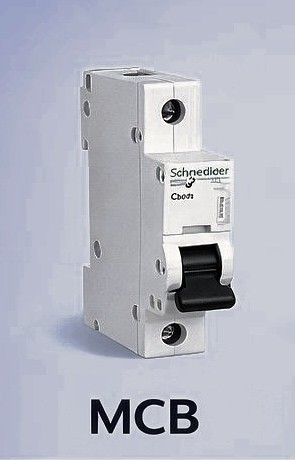
Thesis_Typst/chapters/ch09/Figures/MCB.jpg
