MAQattan/My-Graduation-Project/Thesis_Typst/chapters/ch09/Figures/MOREDAY-MCB-MDB1Z-63-Series-Miniature-Circuit-Breaker-1P-2P-3P-and-4P-models-1280.jpg

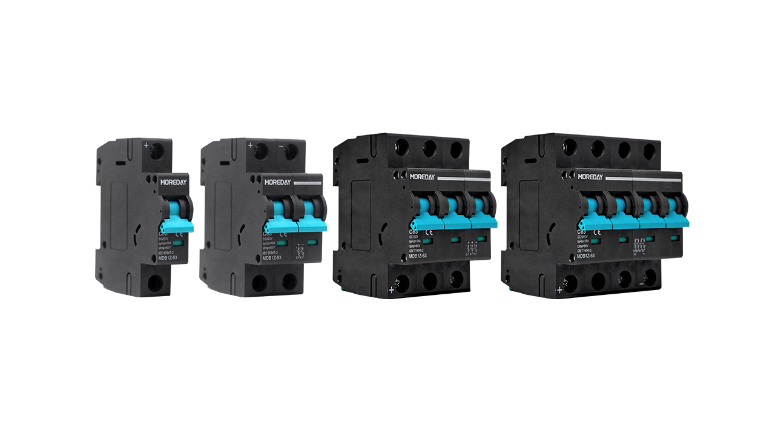
Thesis_Typst/chapters/ch09/Figures/MOREDAY-MCB-MDB1Z-63-Series-Miniature-Circuit-Breaker-1P-2P-3P-and-4P-models-1280.jpg
