MAQattan/My-Graduation-Project/Thesis_Typst/chapters/ch09/Figures/photo_2026-05-23_11-20-18.jpg

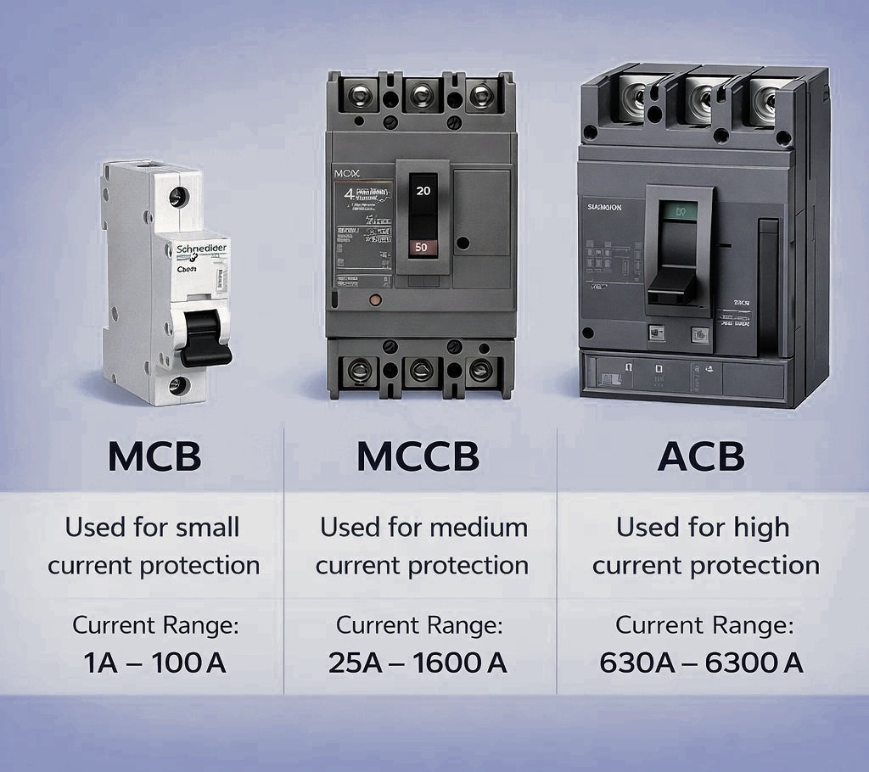
Thesis_Typst/chapters/ch09/Figures/photo_2026-05-23_11-20-18.jpg
