MAQattan/My-Graduation-Project/Thesis_Typst/chapters/ch09/Figures/PV-09-02.png

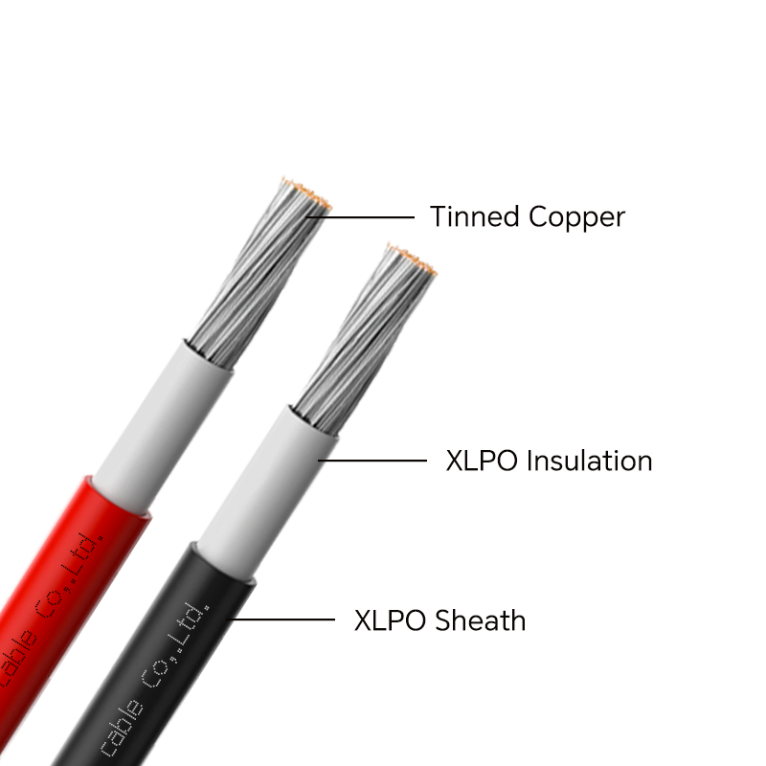
Thesis_Typst/chapters/ch09/Figures/PV-09-02.png
