MAQattan/My-Graduation-Project/Thesis_Typst/chapters/ch09/Figures/PV-09-04.jpg

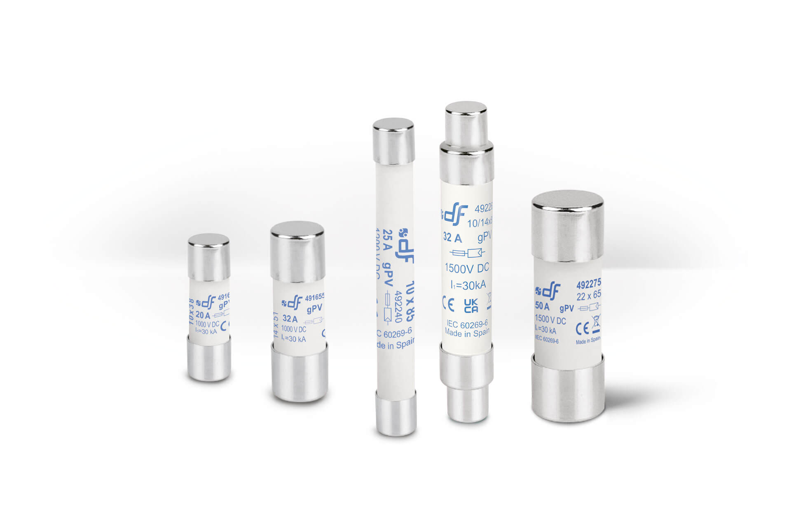
Thesis_Typst/chapters/ch09/Figures/PV-09-04.jpg
