MAQattan/My-Graduation-Project/Thesis_Typst/chapters/ch09/Figures/PV-09-05.png

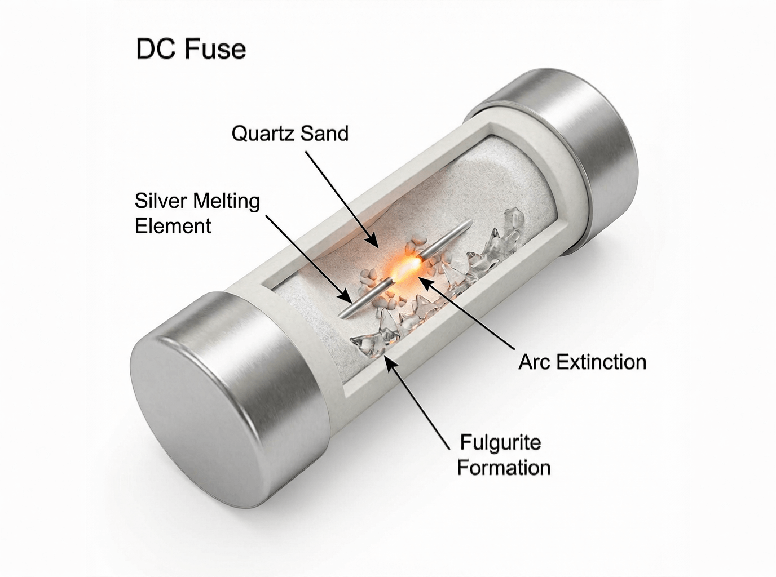
Thesis_Typst/chapters/ch09/Figures/PV-09-05.png
