MAQattan/My-Graduation-Project/Thesis_Typst/chapters/ch09/Figures/PV-09-10.png

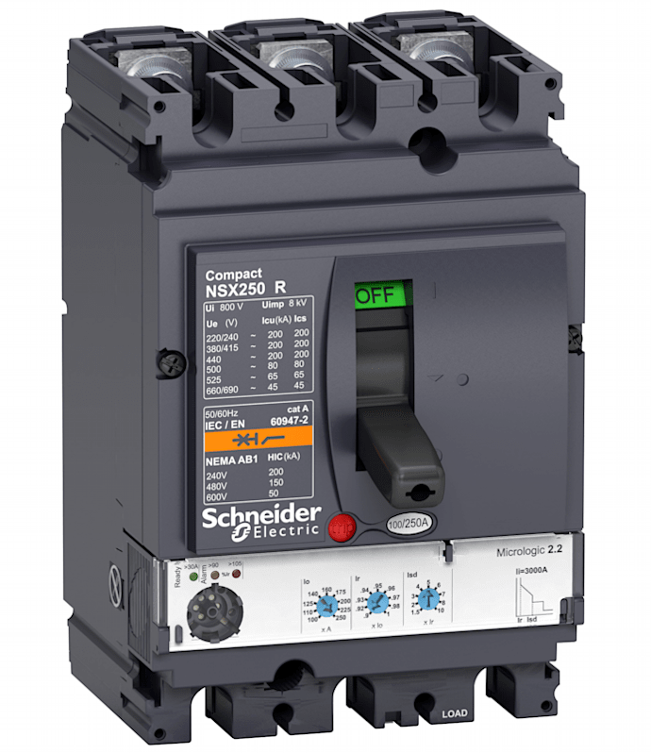
Thesis_Typst/chapters/ch09/Figures/PV-09-10.png
