MAQattan/My-Graduation-Project/Thesis_Typst/chapters/ch09/Figures/PV-09-12.webp

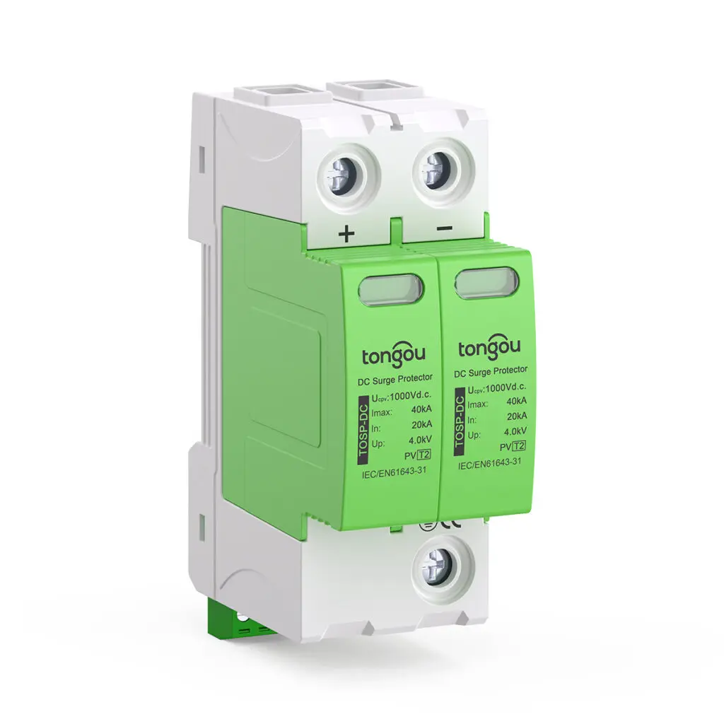
Thesis_Typst/chapters/ch09/Figures/PV-09-12.webp
