MAQattan/My-Graduation-Project/Thesis_Typst/chapters/ch09/Figures/Solar-cable4.webp

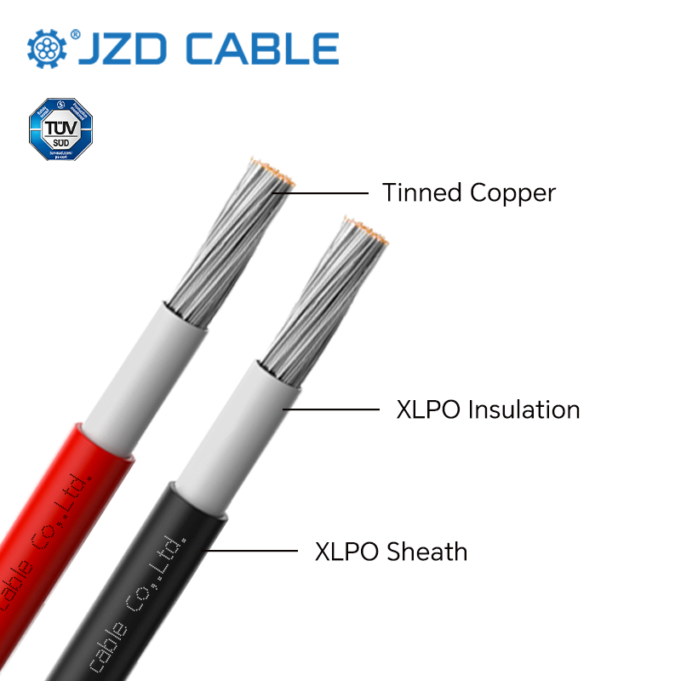
Thesis_Typst/chapters/ch09/Figures/Solar-cable4.webp
