MAQattan/My-Graduation-Project/Thesis_Typst/chapters/ch09/Figures/SPD-type-1-2-3-comparison-1-scaled-1.jpg

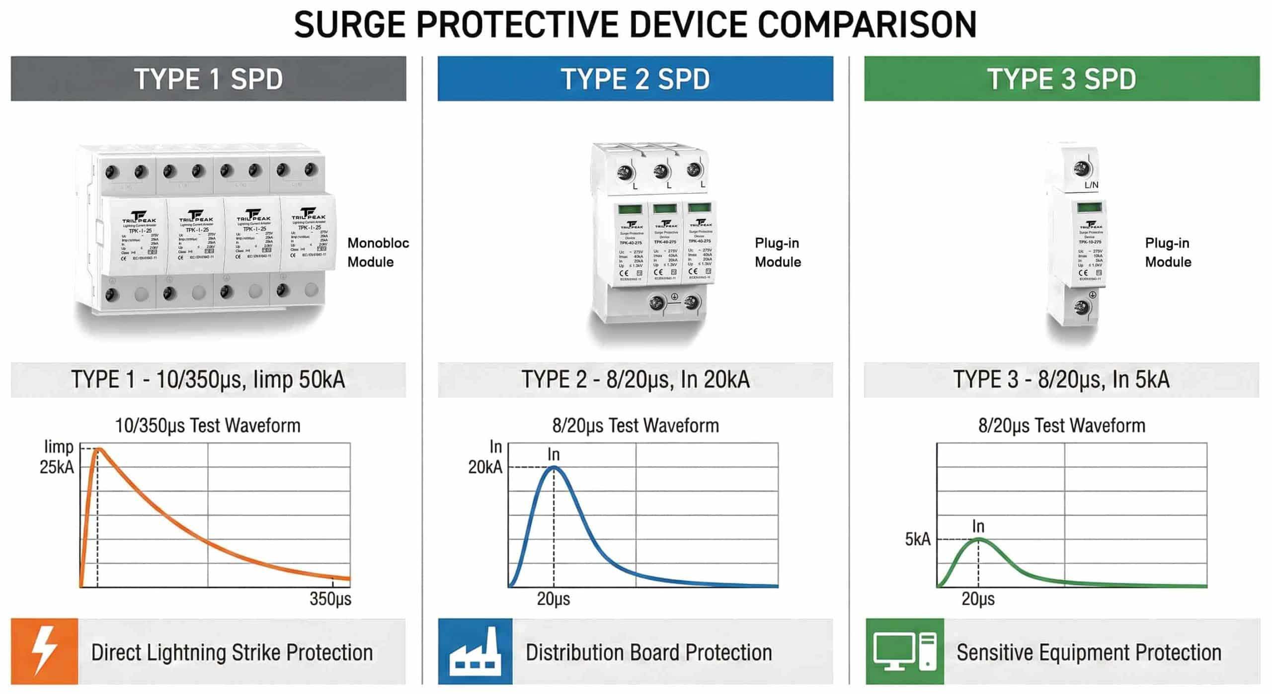
Thesis_Typst/chapters/ch09/Figures/SPD-type-1-2-3-comparison-1-scaled-1.jpg
