MAQattan/My-Graduation-Project/Thesis_Typst/chapters/ch09/Figures/Surge-Protection-Device-SPD-Types-Classes-and-Categories-.webp

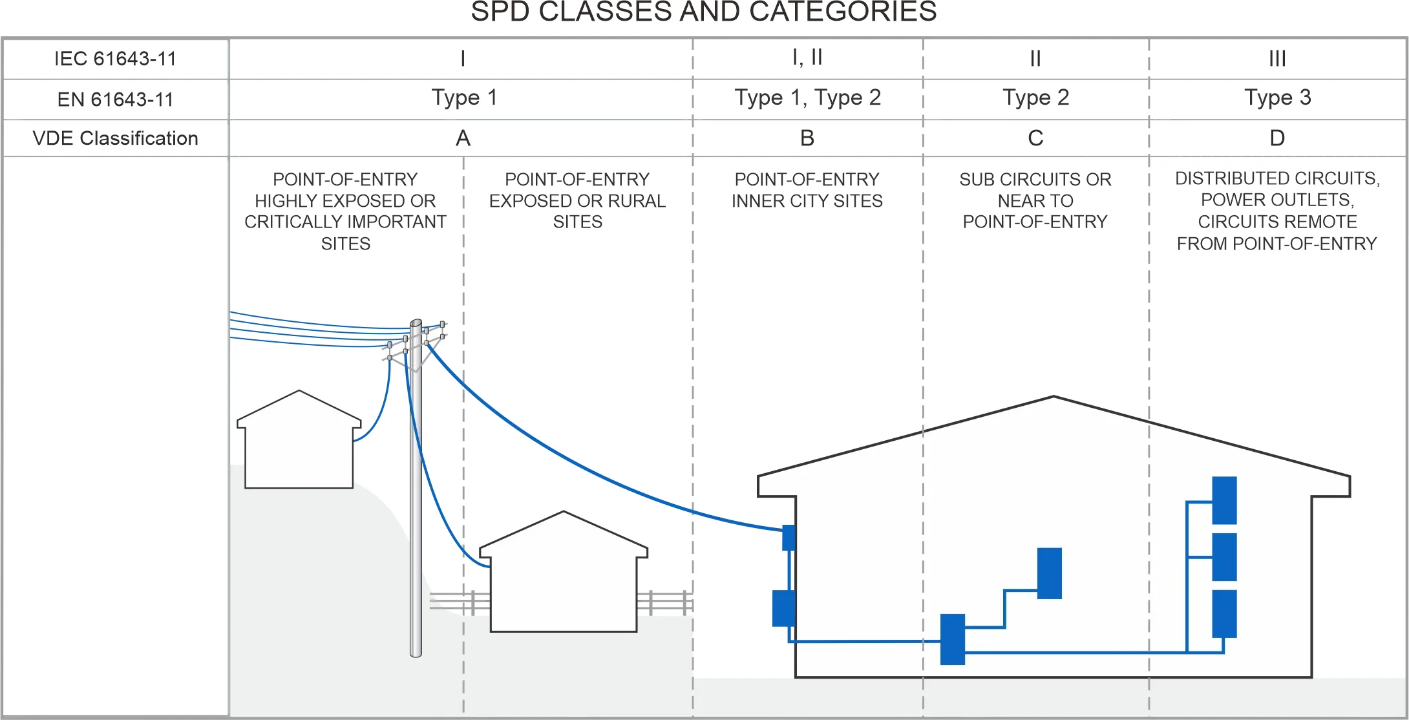
Thesis_Typst/chapters/ch09/Figures/Surge-Protection-Device-SPD-Types-Classes-and-Categories-.webp
