MAQattan/My-Graduation-Project/Thesis_Typst/chapters/ch09/Figures/Thermobimetals_Materiability_1024x1024.jpg

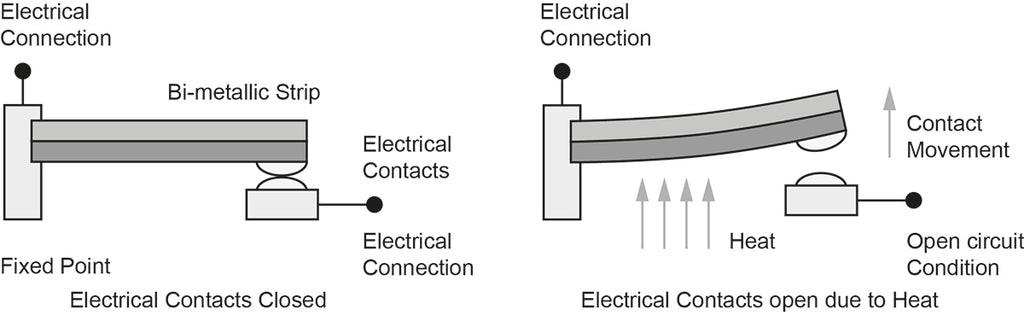
Thesis_Typst/chapters/ch09/Figures/Thermobimetals_Materiability_1024x1024.jpg
