MAQattan/My-Graduation-Project/Thesis_Typst/chapters/ch09/Figures/type1-2-3-surge-protection-device.jpg

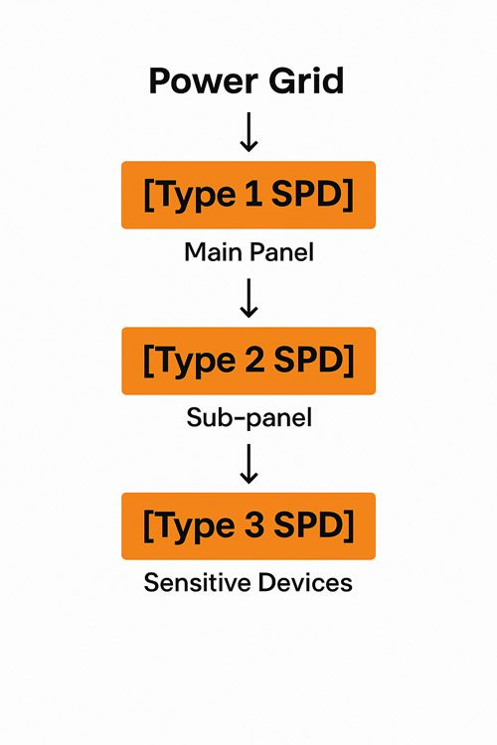
Thesis_Typst/chapters/ch09/Figures/type1-2-3-surge-protection-device.jpg
