MAQattan/My-Graduation-Project/Thesis_Typst/chapters/ch09/Figures/YCB8s-63PVn-DC-MCB-Photovoltaic-Miniature-Circuit-Breaker-dimension-3.png

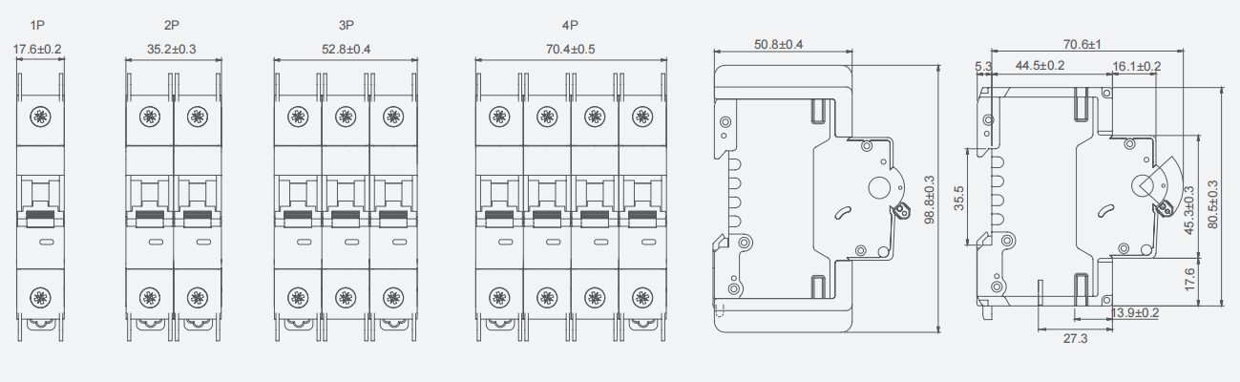
Thesis_Typst/chapters/ch09/Figures/YCB8s-63PVn-DC-MCB-Photovoltaic-Miniature-Circuit-Breaker-dimension-3.png
