MAQattan/My-Graduation-Project/Illustrations/3-tracking-v-static-v-household-usage_orig.png

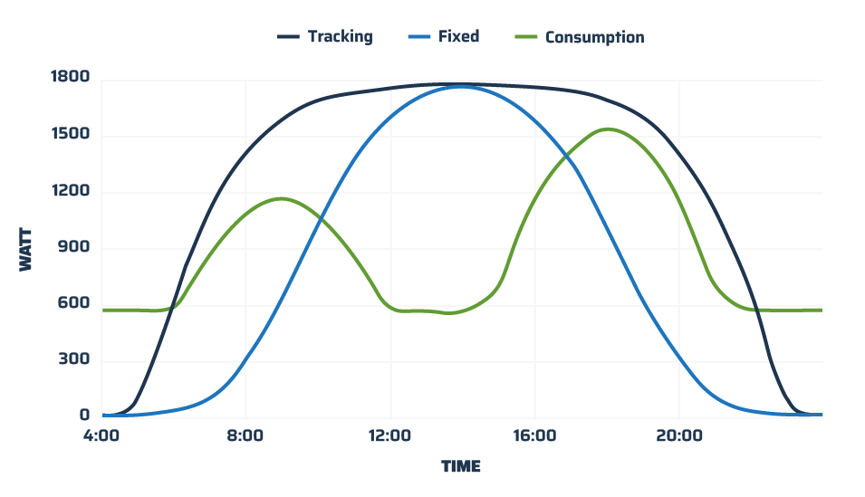
Illustrations/3-tracking-v-static-v-household-usage_orig.png
