MAQattan/My-Graduation-Project/Illustrations/series-parallel-solar-panel-wiring-diagram_480x480.jpg

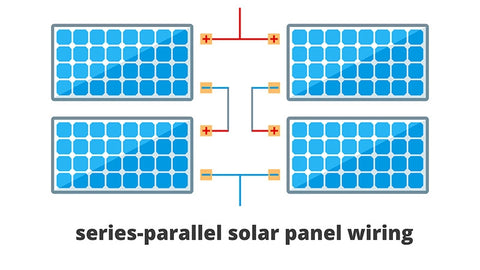
Illustrations/series-parallel-solar-panel-wiring-diagram_480x480.jpg
