MAQattan/My-Graduation-Project/Thesis_Typst/chapters/ch09/Figures/Figure-1-Normal-Operation.jpg

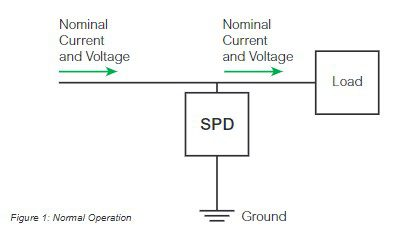
Thesis_Typst/chapters/ch09/Figures/Figure-1-Normal-Operation.jpg
