MAQattan/My-Graduation-Project/Thesis_Typst/chapters/ch09/Figures/Figure-2-Shunting-Operation.jpg

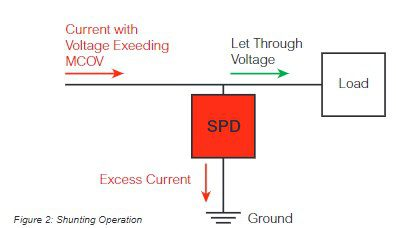
Thesis_Typst/chapters/ch09/Figures/Figure-2-Shunting-Operation.jpg
