MAQattan/My-Graduation-Project/images/SLD.pdf

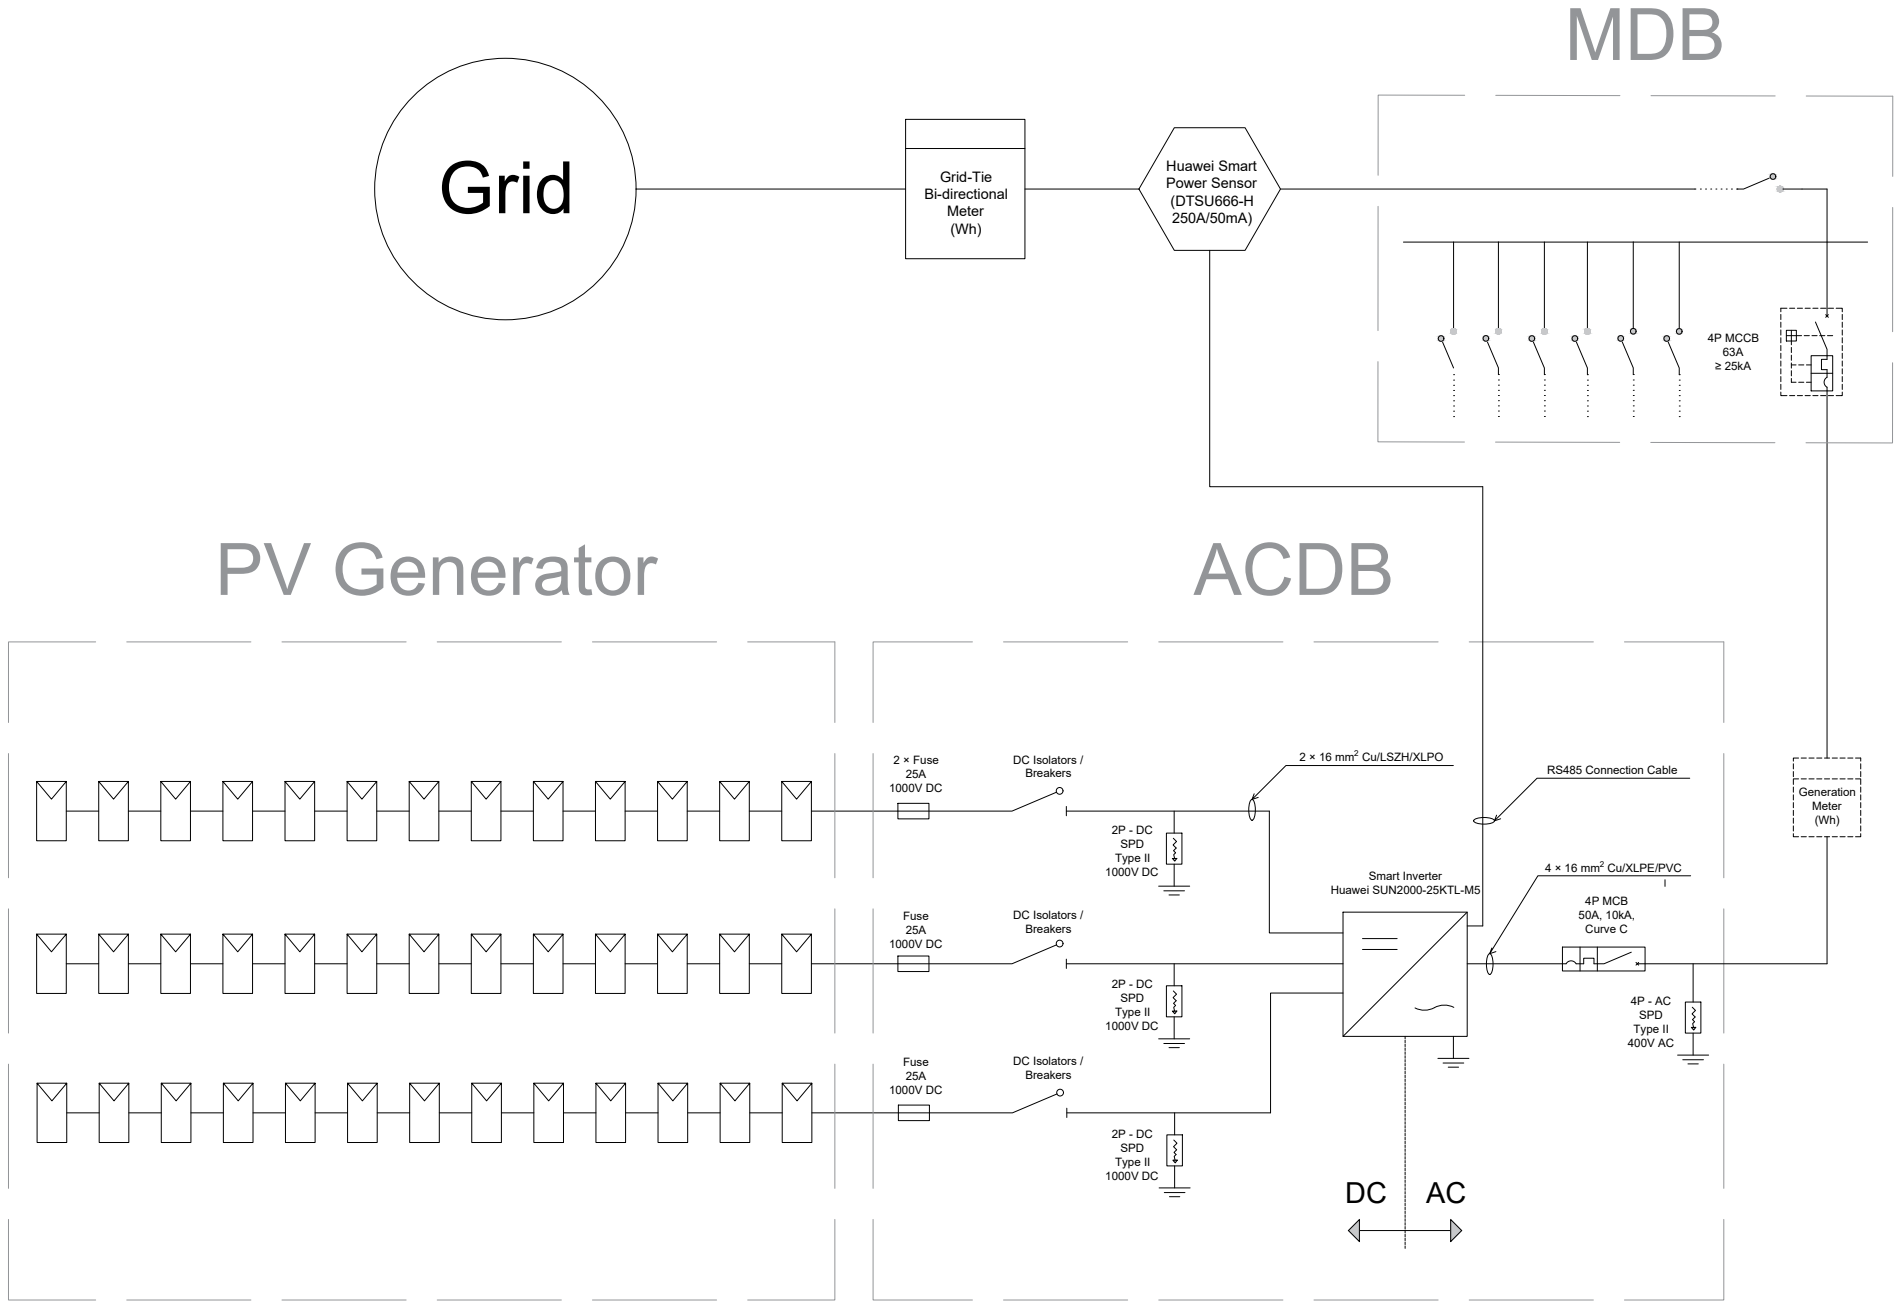
[picture p211: page 1]
Huawei Smart Power Sensor; 4P MCB 50A, 10kA, Curve C; 2 × Fuse; PV Generator; 4P MCCB; RS485 Connection Cable; 2 DC Isolators /; Type II 1000V DC; DC Isolators /; Smart Inverter Huawei SUN2000-25KTL-M5; Type II 400V AC

Cu/LSZH/XLPO

Cu/XLPE/PVC
