MAQattan/My-Graduation-Project/Data about the project site/New folder/Illustration of Correction Angle 1.pdf

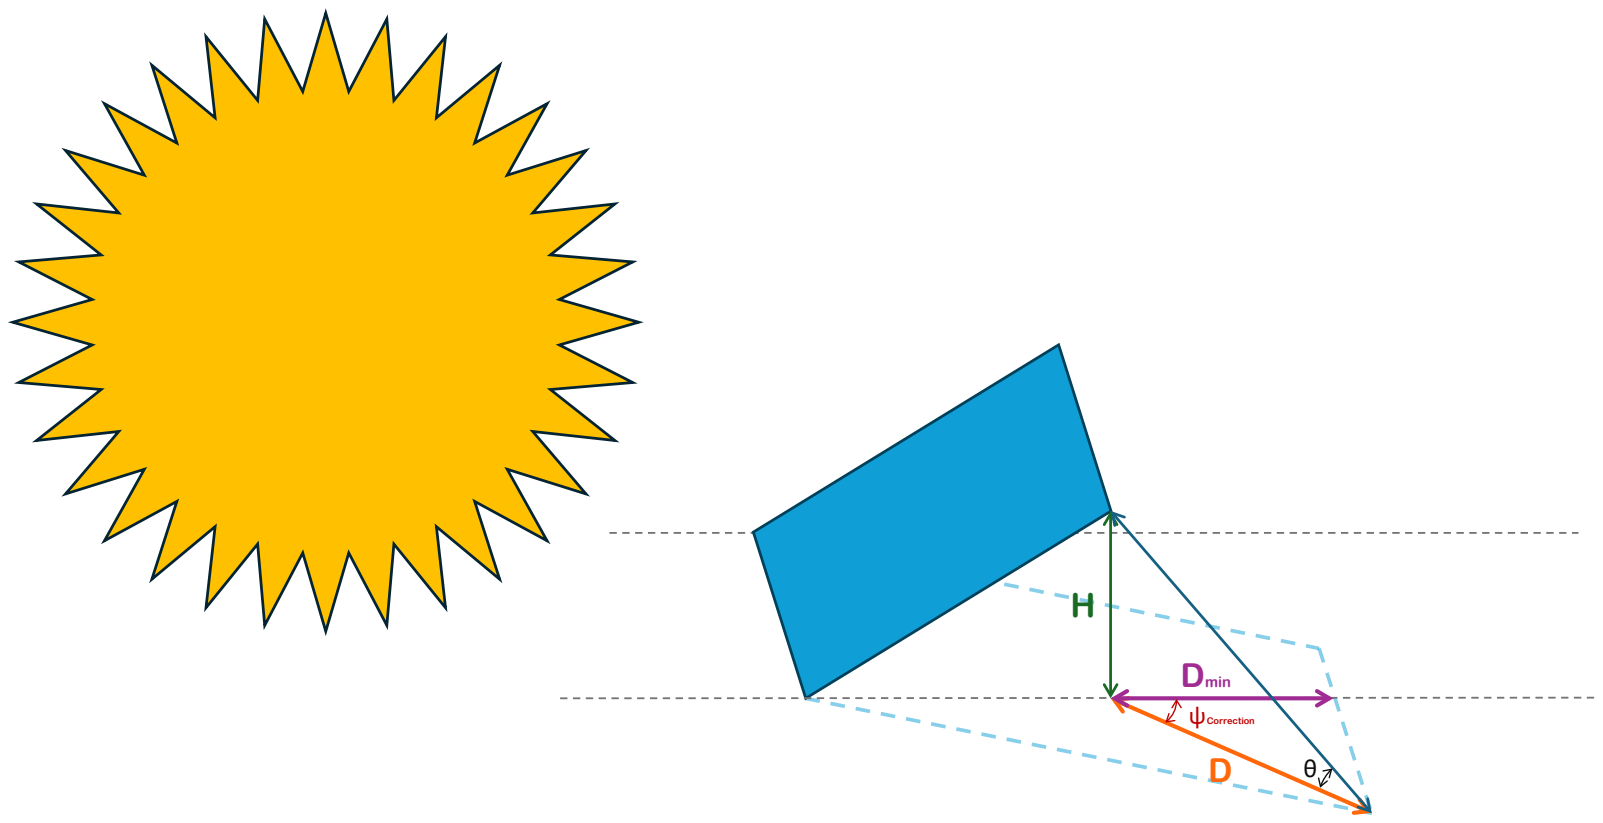
[picture p214: page 1]
Dmin ψCorrection
