MAQattan/My-Graduation-Project/Data about the project site/New folder/Illustration of Correction Angle.pdf

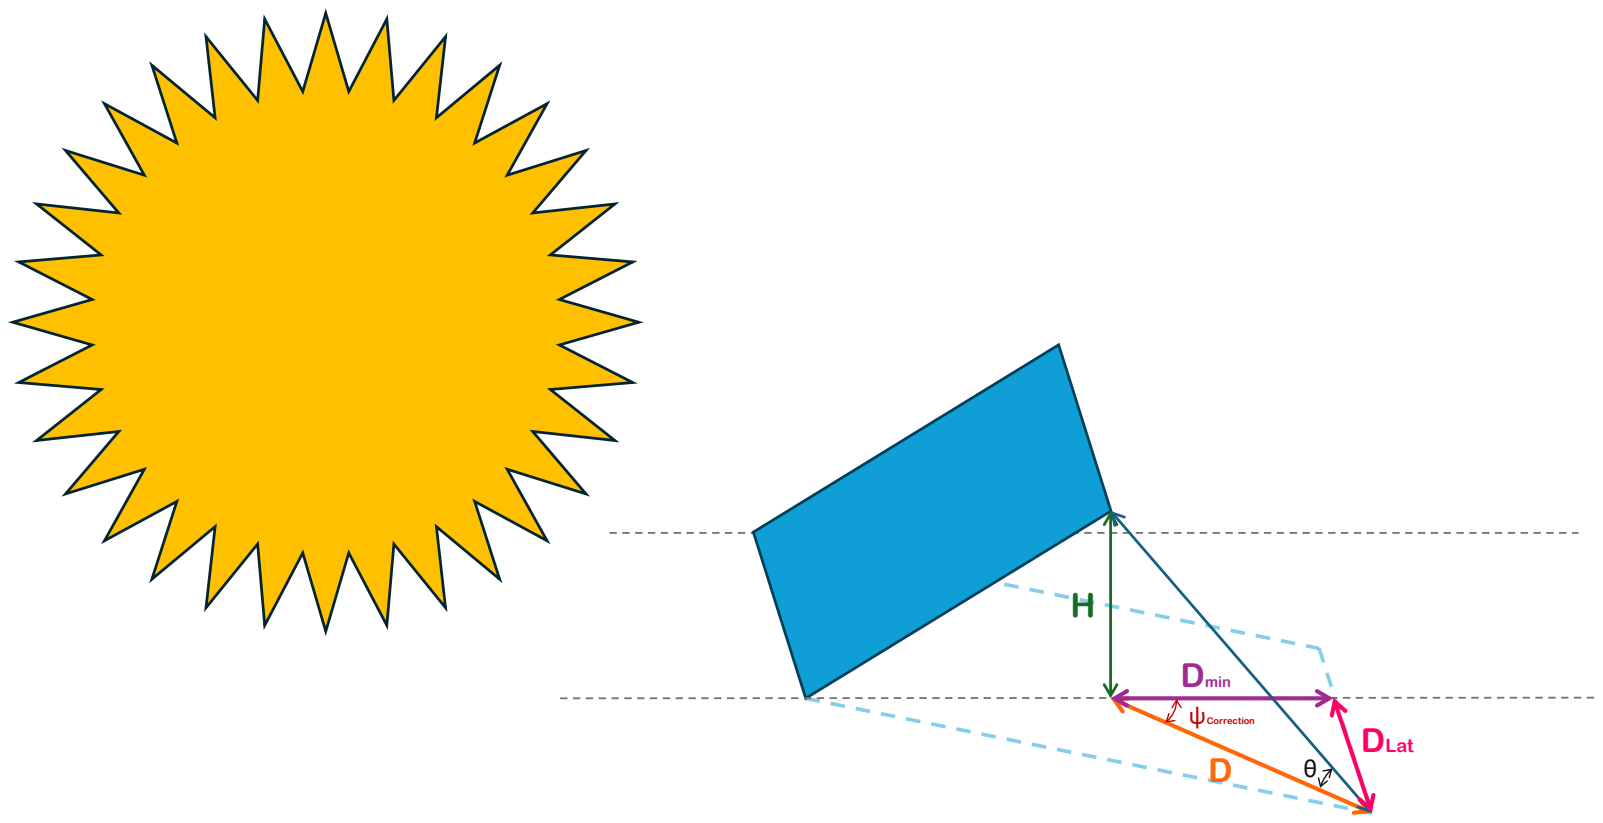
[picture p215: page 1]
Dmin ψCorrection; DLat
